jrsteensen/OpenHornet/release/OHM_Modifications/README.md

# Mods Folder

All parts inside the "mods" folder are modifications of the original OpenHornet parts. All parts inside this folder do not belong to the OpenHornet release baseline and are therefore not officially supported by the OpenHornet team.

## Documentation
All modifications made to the parts inside the "mods" folder are documented in the `README.md` file inside every folder.

### README.md Template
```
# <TITLE OF MODIFICATION>
- **Author:** <Name and discord username i.e. John Steensen (Noctum)>
- **Contributed on:** <date>
- **Derived from:** v<release number, i.e. 0.2.0)
- **Original Assembly:** <List OH part number of the original assembly.>

## Summary
<Describe the change and why>

### Parts List <This section is only required if there are changes to the parts list>
1. <List the new parts/hardware/components, and describe them well enough that they can be sourced. Links are good.>
2. ...
3. ...
```
