jrsteensen/OpenHornet/release/OHM_Modifications/DXF_files_v0.2.0/README.md

# DXF File Export of v0.2.0 release
- **Author:** Jose (5JsAs)
- **Contributed on:** Apr 10, 2024
- **Derived from:** v0.2.0
- **Original Assembly:** All SVG Structure Parts

## Summary
Contains the DXF files that correspond to the parts in SVG format of the different OH structures. The parts are compiled into 5 files according to the main structures of the project: UIP, LIP, Center Tub, LC, RC. For each structure there are two files in mm and inches.

The parts have been exported from the Fusion model in mm and compiled in AUTOCAD. The inch version is obtained after a units conversion in AUTOCAD.
