jrsteensen/OpenHornet/artwork/Left Console/OH4A1-9001 - DECAL, GROUND POWER.png

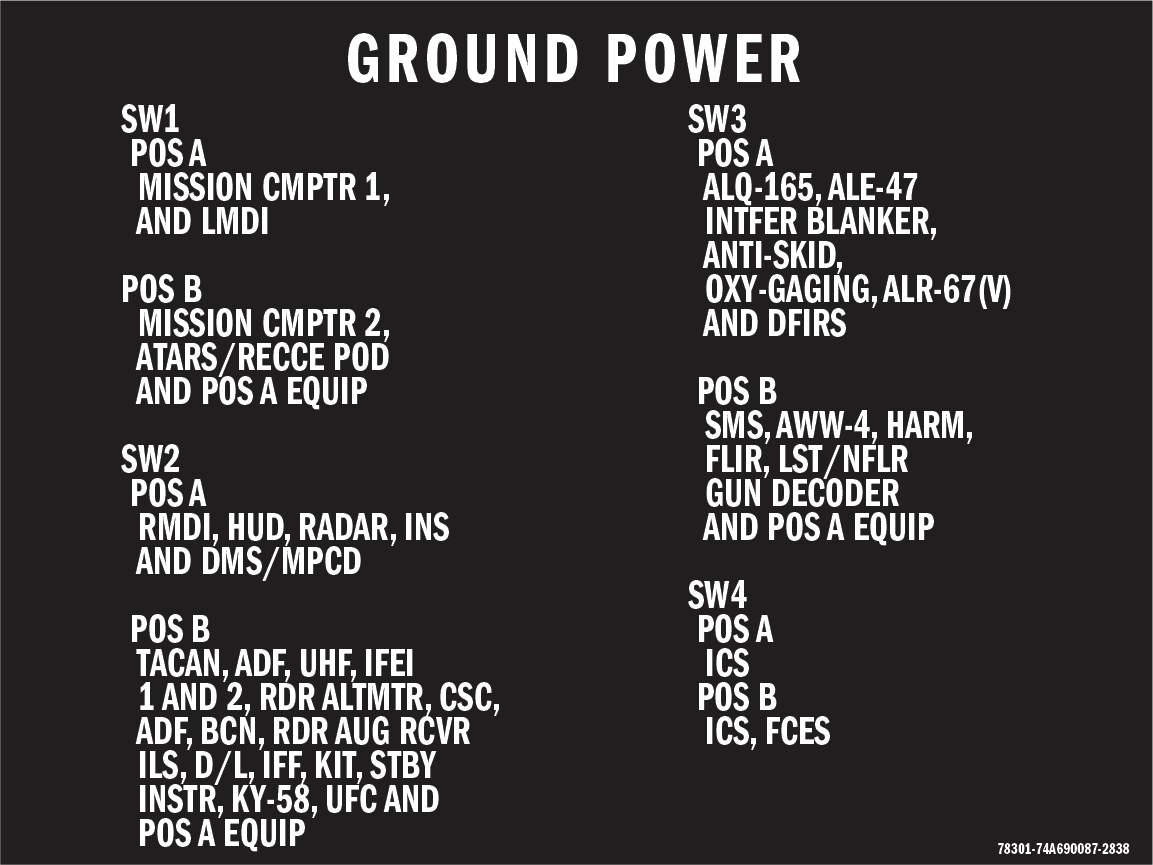
artwork/Left Console/OH4A1-9001 - DECAL, GROUND POWER.png
