jrsteensen/OpenHornet/artwork/Left Console/OH4A9-9001 - DECAL, RH GRIP ASSY.png

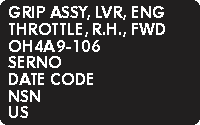
artwork/Left Console/OH4A9-9001 - DECAL, RH GRIP ASSY.png
