jrsteensen/OpenHornet/artwork/Right Console/OH5A1-9001 - DECAL, CANOPY.png

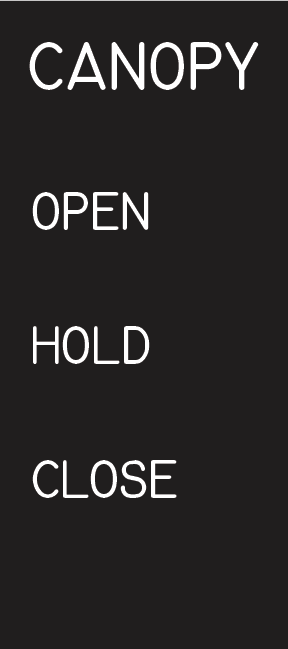
artwork/Right Console/OH5A1-9001 - DECAL, CANOPY.png
