jrsteensen/OpenHornet/artwork/seat/OH3A2A-9002 - DECAL, BRIDLE AND BOX.png

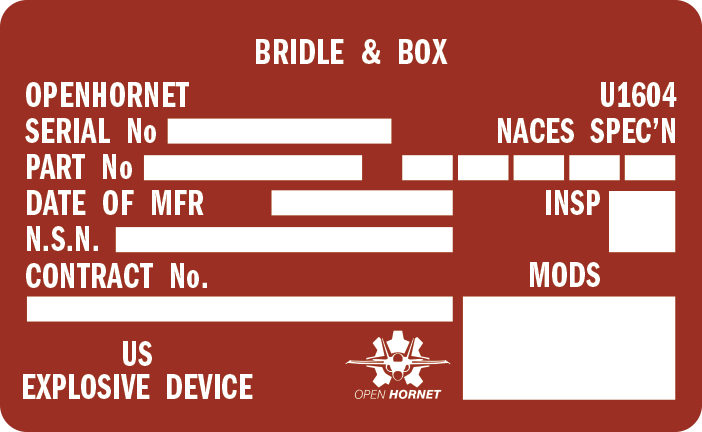
artwork/seat/OH3A2A-9002 - DECAL, BRIDLE AND BOX.png
