jrsteensen/OpenHornet/artwork/seat/OH3A2A-9004 - DECAL, DANGER DO NOT PULL.png

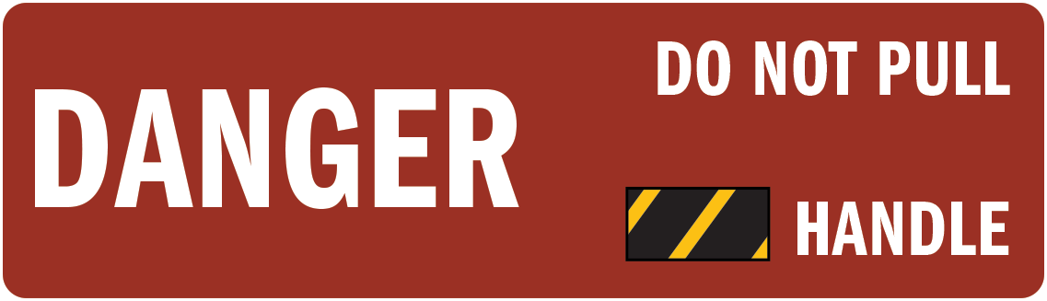
artwork/seat/OH3A2A-9004 - DECAL, DANGER DO NOT PULL.png
