jrsteensen/OpenHornet/artwork/seat/OH3A2A-9005 - DECAL, DO NOT HOLD.png

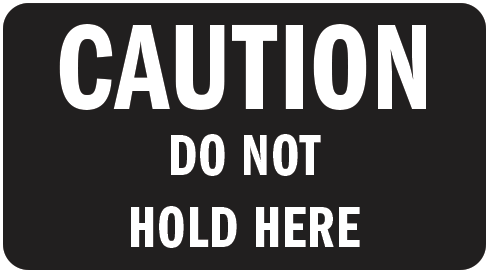
artwork/seat/OH3A2A-9005 - DECAL, DO NOT HOLD.png
