jrsteensen/OpenHornet/artwork/seat/OH3A2A-9006 - DECAL, NACES PFCL.png

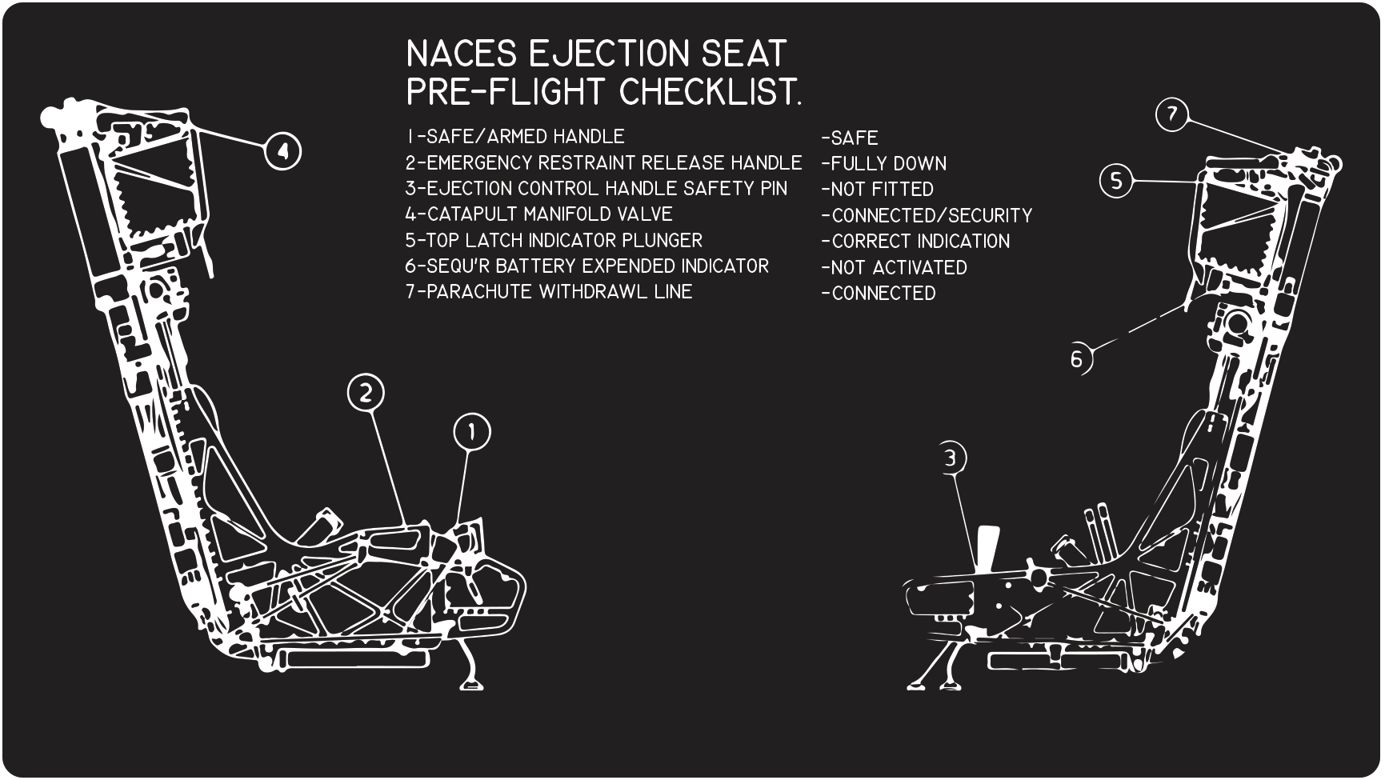
artwork/seat/OH3A2A-9006 - DECAL, NACES PFCL.png
