jrsteensen/OpenHornet/artwork/seat/OH3A2A-9008 - DECAL, SEAT BUCKET MECH.png

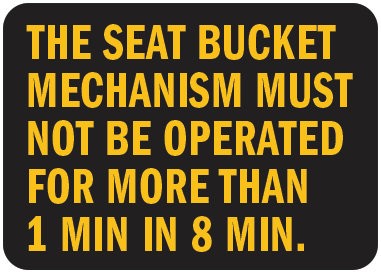
artwork/seat/OH3A2A-9008 - DECAL, SEAT BUCKET MECH.png
