jrsteensen/OpenHornet/artwork/seat/OH3A2A-9010 - DECAL, SEAT, AIRCRAFT EJECTION.png

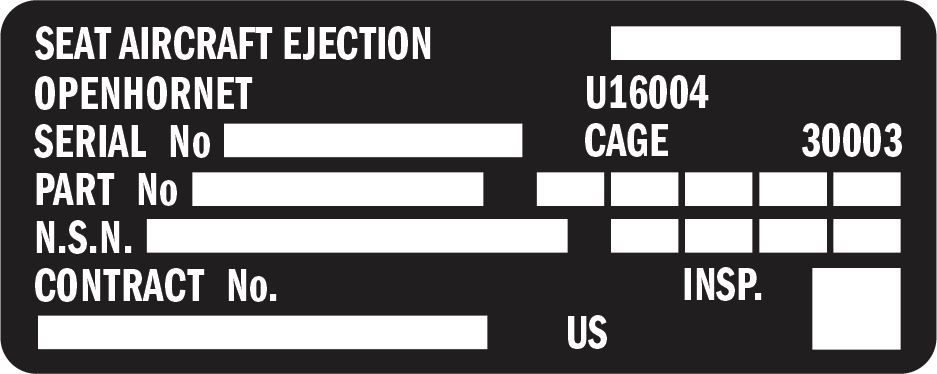
artwork/seat/OH3A2A-9010 - DECAL, SEAT, AIRCRAFT EJECTION.png
