jrsteensen/OpenHornet/artwork/seat/OH3A2A-9011 - DECAL, SEAT APPLICATION.png

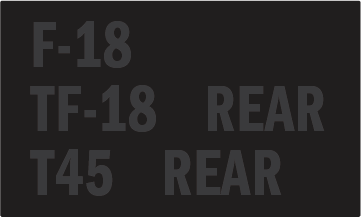
artwork/seat/OH3A2A-9011 - DECAL, SEAT APPLICATION.png
