jrsteensen/OpenHornet/artwork/seat/OH3A2A-9014 - DECAL, SURVIVAL KIT, OXYGEN, AIRCRAFT SEAT.png

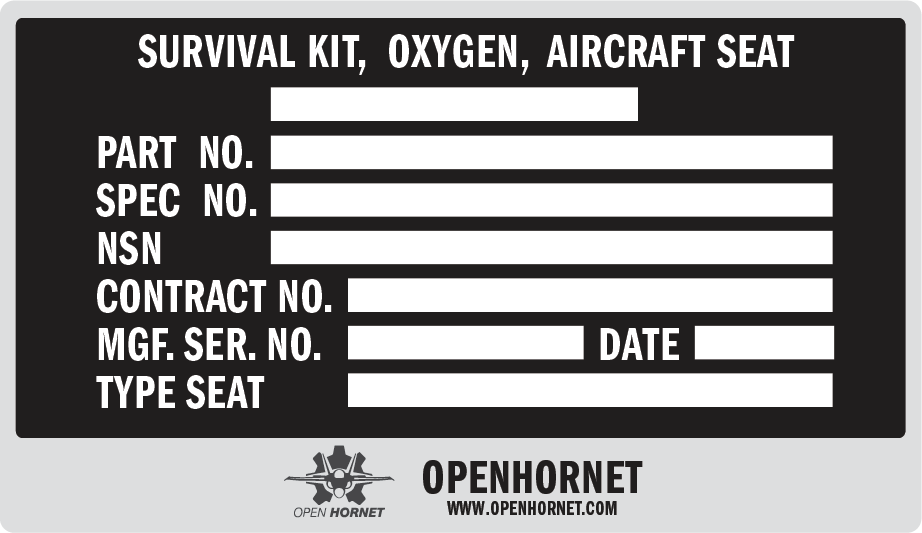
artwork/seat/OH3A2A-9014 - DECAL, SURVIVAL KIT, OXYGEN, AIRCRAFT SEAT.png
