jrsteensen/OpenHornet/artwork/seat/OH3A2A-9016 - DECAL, DROGUE ASSY.pdf.png

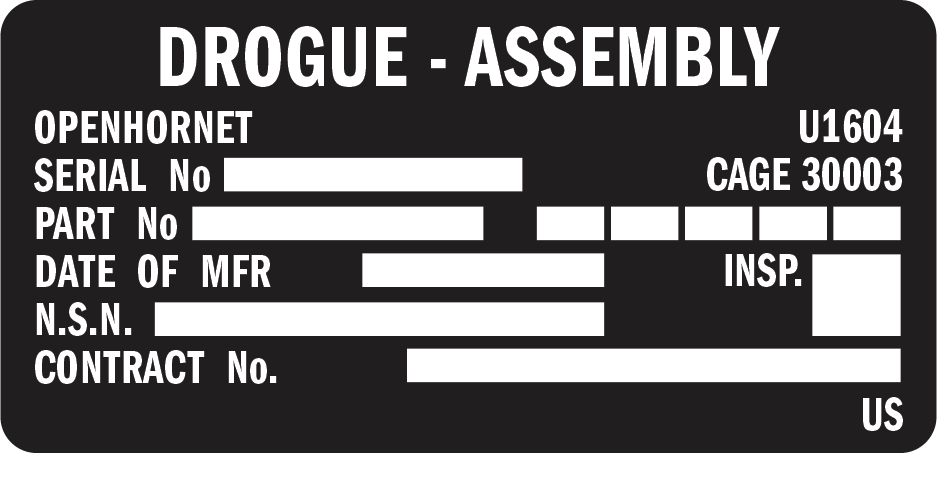
artwork/seat/OH3A2A-9016 - DECAL, DROGUE ASSY.pdf.png
