jrsteensen/OpenHornet/artwork/Stick/OH3A3-9001 - DECAL, GRIP ASSY.png

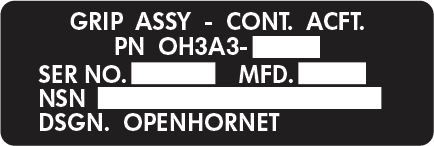
artwork/Stick/OH3A3-9001 - DECAL, GRIP ASSY.png
