jrsteensen/OpenHornet/artwork/Upper Instrument Panel/OH1A8-9001 - DECAL, TV LENS.png

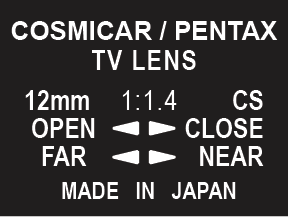
artwork/Upper Instrument Panel/OH1A8-9001 - DECAL, TV LENS.png
