jrsteensen/OpenHornet/ECAD/PCBs/ABSIS/ABSIS_ALE Relay Module/Assets/ABSIS_ALE Relay Module-BOT.png

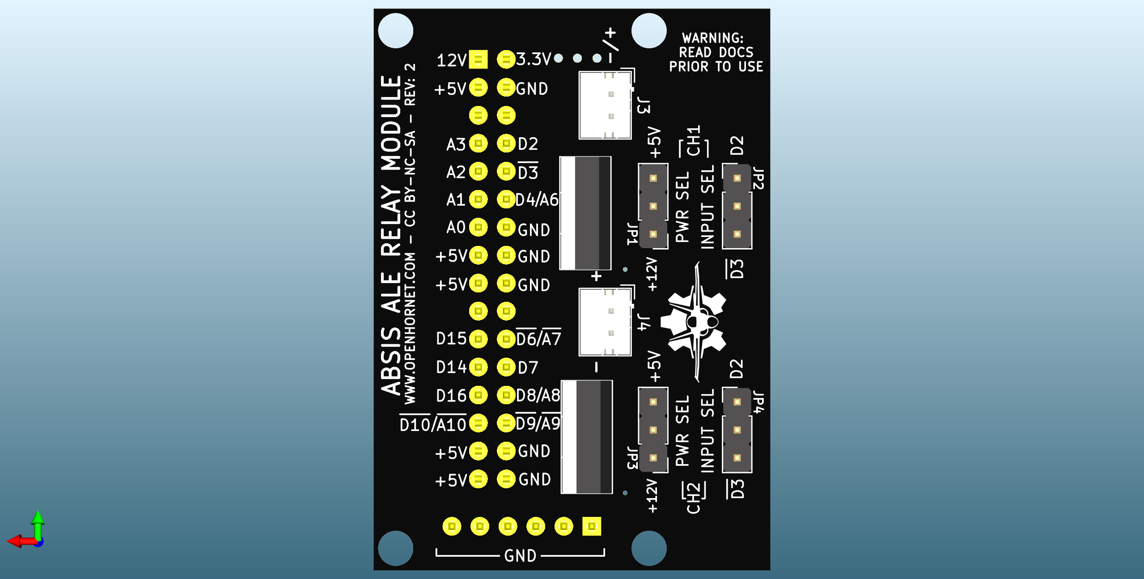
ECAD/PCBs/ABSIS/ABSIS_ALE Relay Module/Assets/ABSIS_ALE Relay Module-BOT.png
