jrsteensen/OpenHornet/ECAD/PCBs/ABSIS/ABSIS_ALE Relay Module/Assets/ABSIS_ALE Relay Module-TOP.png

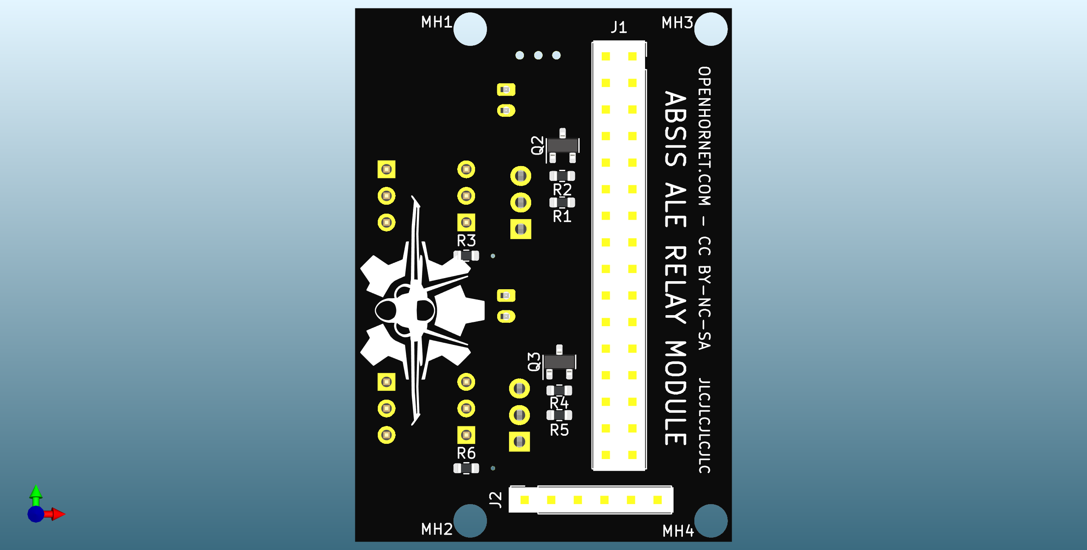
ECAD/PCBs/ABSIS/ABSIS_ALE Relay Module/Assets/ABSIS_ALE Relay Module-TOP.png
