jrsteensen/OpenHornet/ECAD/PCBs/ABSIS/ABSIS_ALE+/ASSETS/11.PNG

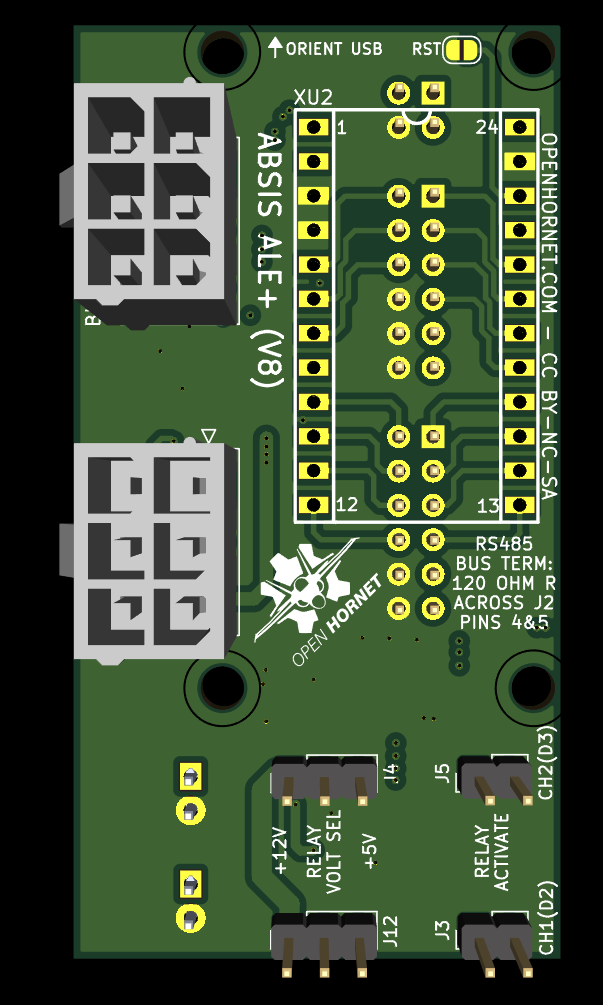
ECAD/PCBs/ABSIS/ABSIS_ALE+/ASSETS/11.PNG
