jrsteensen/OpenHornet/ECAD/PCBs/ABSIS/ABSIS_ALE+/ASSETS/12.PNG

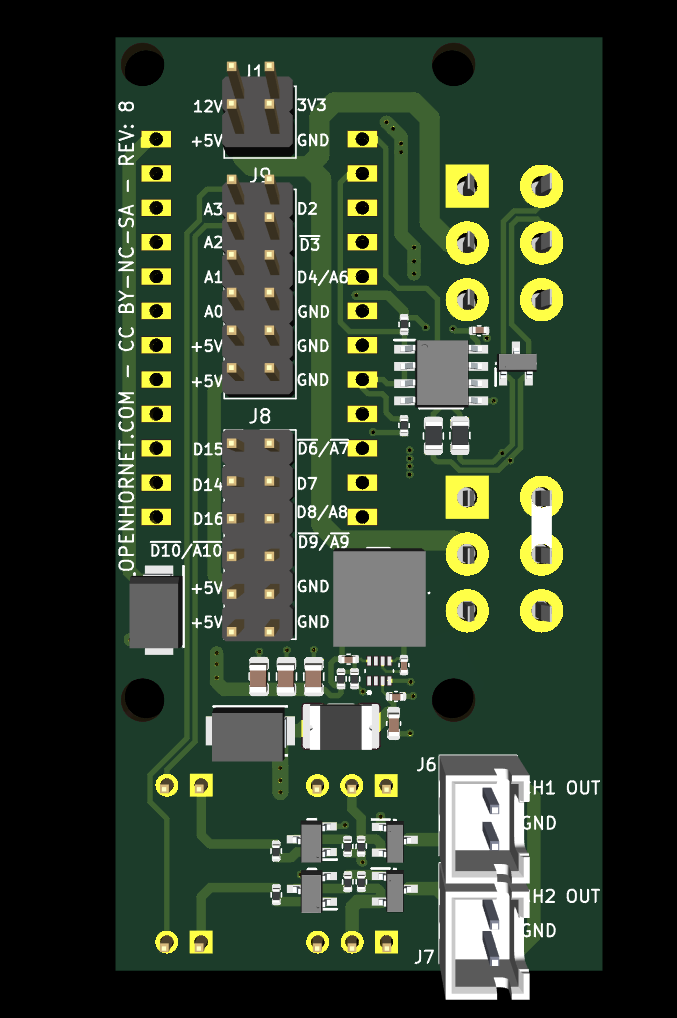
ECAD/PCBs/ABSIS/ABSIS_ALE+/ASSETS/12.PNG
