jrsteensen/OpenHornet/ECAD/PCBs/ABSIS/ABSIS_ALE+/ASSETS/13.PNG

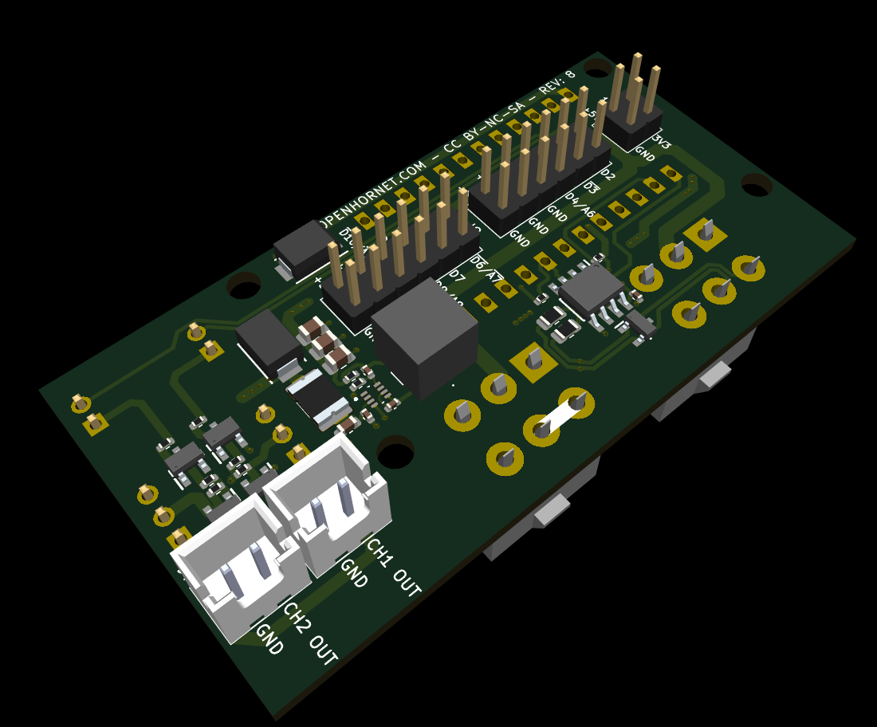
ECAD/PCBs/ABSIS/ABSIS_ALE+/ASSETS/13.PNG
