jrsteensen/OpenHornet/ECAD/PCBs/ABSIS/ABSIS_ALE+/ASSETS/14.PNG

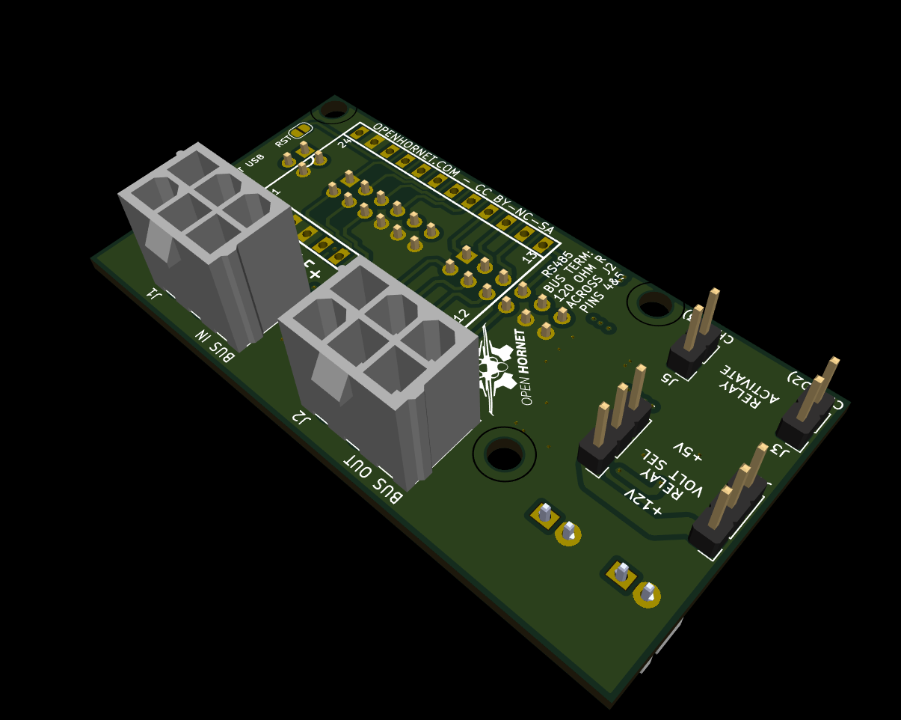
ECAD/PCBs/ABSIS/ABSIS_ALE+/ASSETS/14.PNG
