jrsteensen/OpenHornet/ECAD/PCBs/ABSIS/ABSIS_ALE+/ASSETS/15.PNG

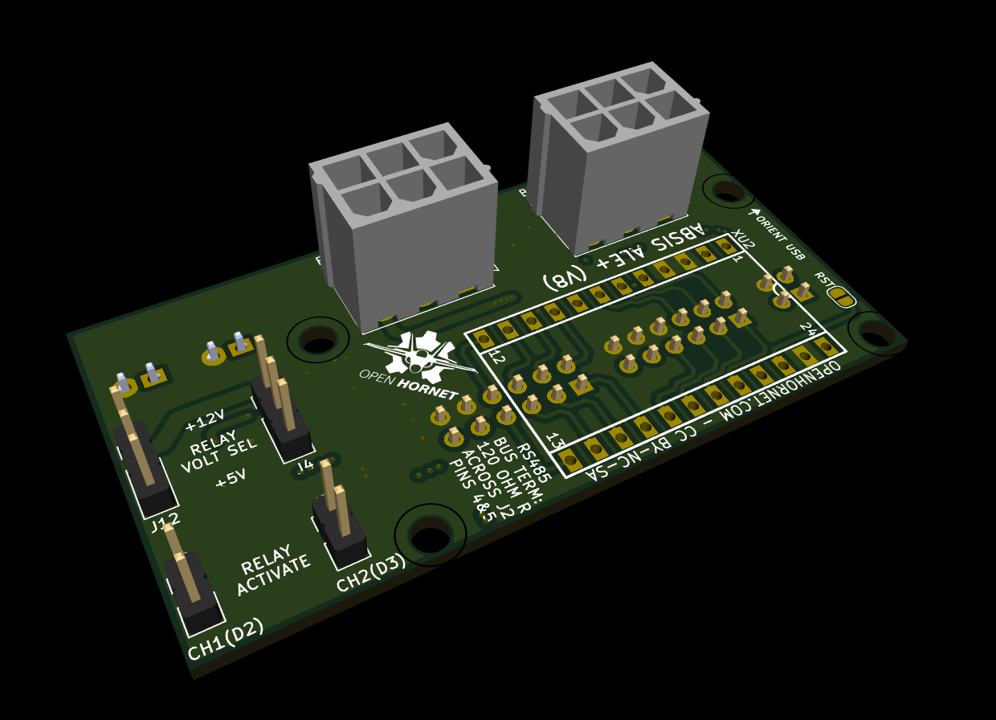
ECAD/PCBs/ABSIS/ABSIS_ALE+/ASSETS/15.PNG
