jrsteensen/OpenHornet/ECAD/PCBs/ABSIS/ABSIS_ALE+/ASSETS/16.PNG

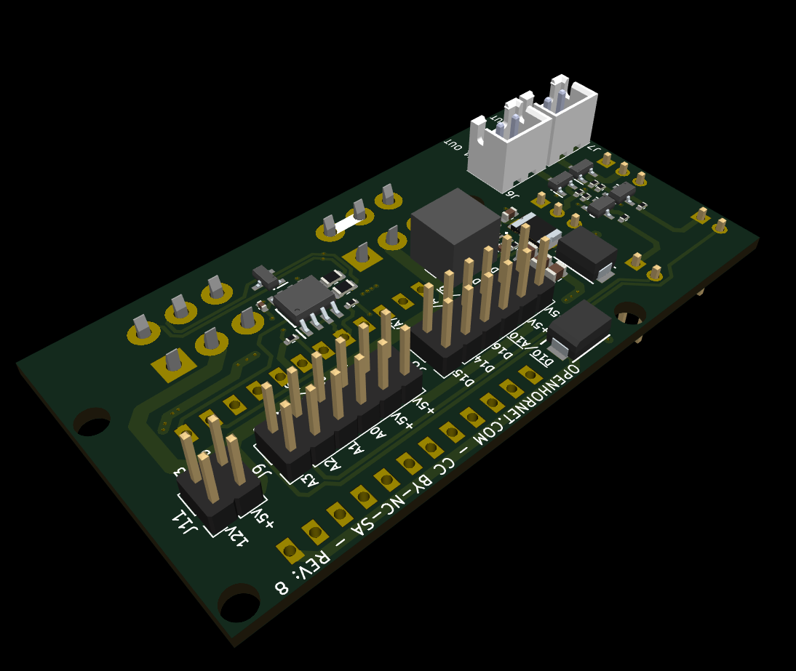
ECAD/PCBs/ABSIS/ABSIS_ALE+/ASSETS/16.PNG
