jrsteensen/OpenHornet/ECAD/PCBs/ABSIS/ABSIS_ALE/Assets/ABSIS_ALE-BOT_ISO.png

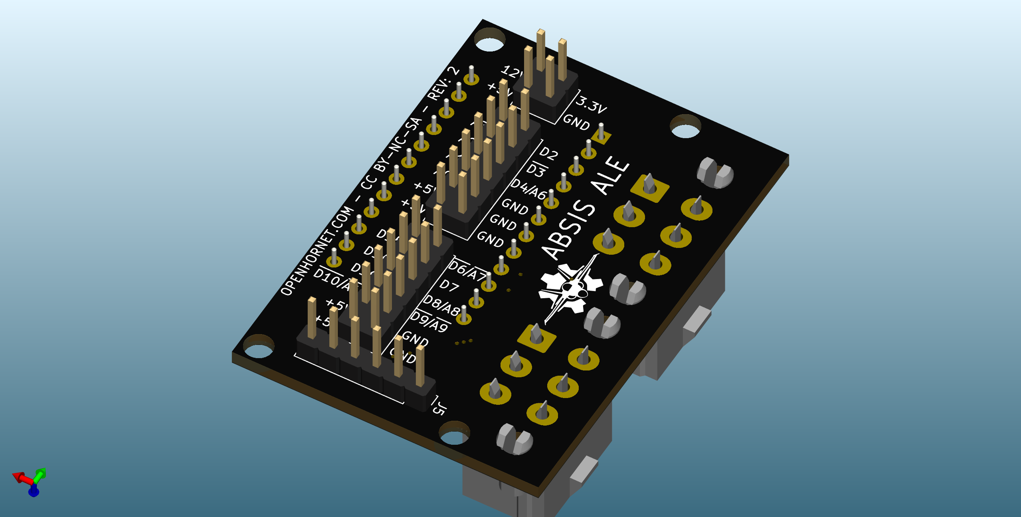
ECAD/PCBs/ABSIS/ABSIS_ALE/Assets/ABSIS_ALE-BOT_ISO.png
