jrsteensen/OpenHornet/ECAD/PCBs/ABSIS/ABSIS_ALE/Assets/ABSIS_ALE-TOP.png

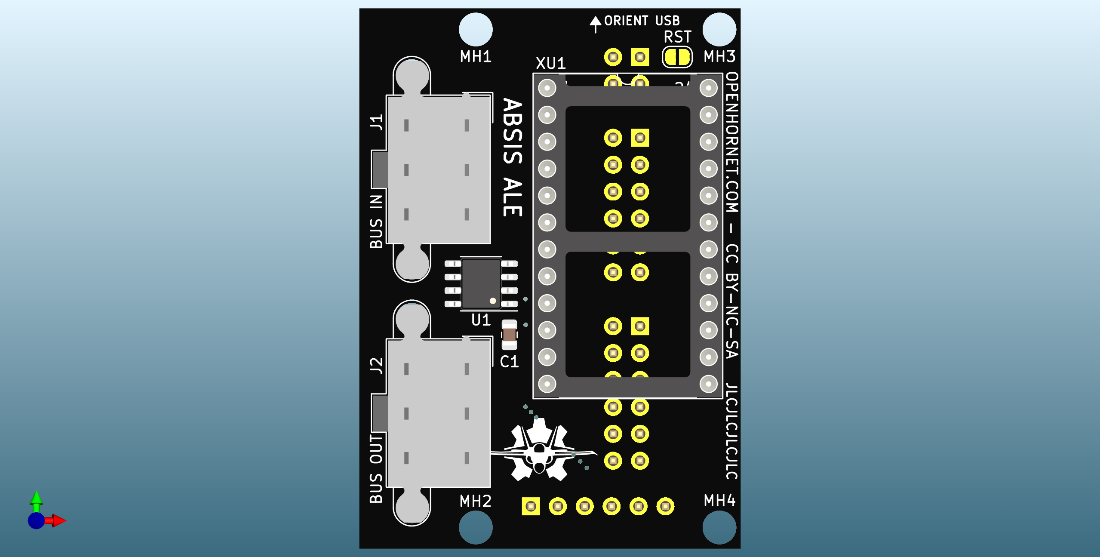
ECAD/PCBs/ABSIS/ABSIS_ALE/Assets/ABSIS_ALE-TOP.png
