jrsteensen/OpenHornet/ECAD/PCBs/ABSIS/ABSIS_ATX Power Supply Unit/Assets/ABSIS_ATX Power Supply Unit-BOT.png

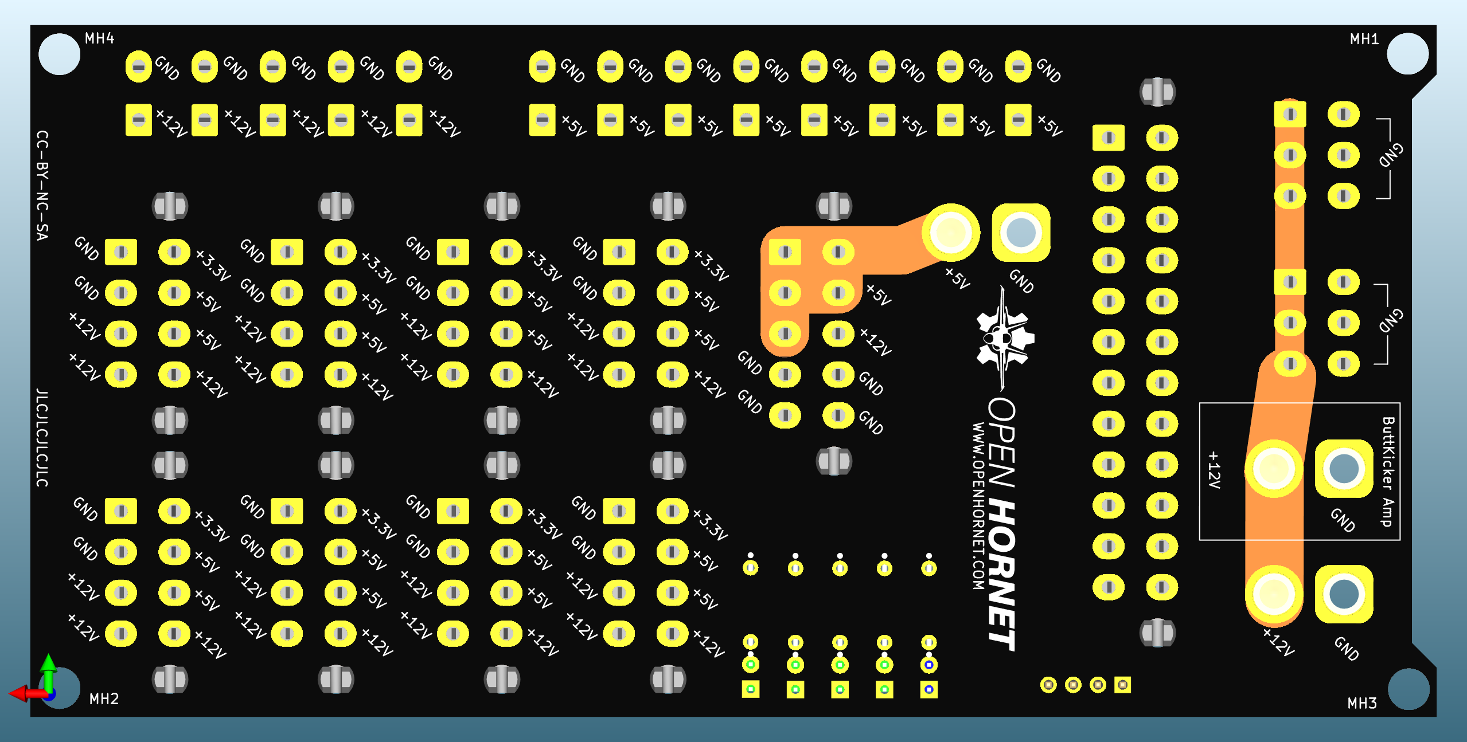
ECAD/PCBs/ABSIS/ABSIS_ATX Power Supply Unit/Assets/ABSIS_ATX Power Supply Unit-BOT.png
