jrsteensen/OpenHornet/ECAD/PCBs/ABSIS/ABSIS_ATX Power Supply Unit/Assets/ABSIS_ATX Power Supply Unit-TOP.png

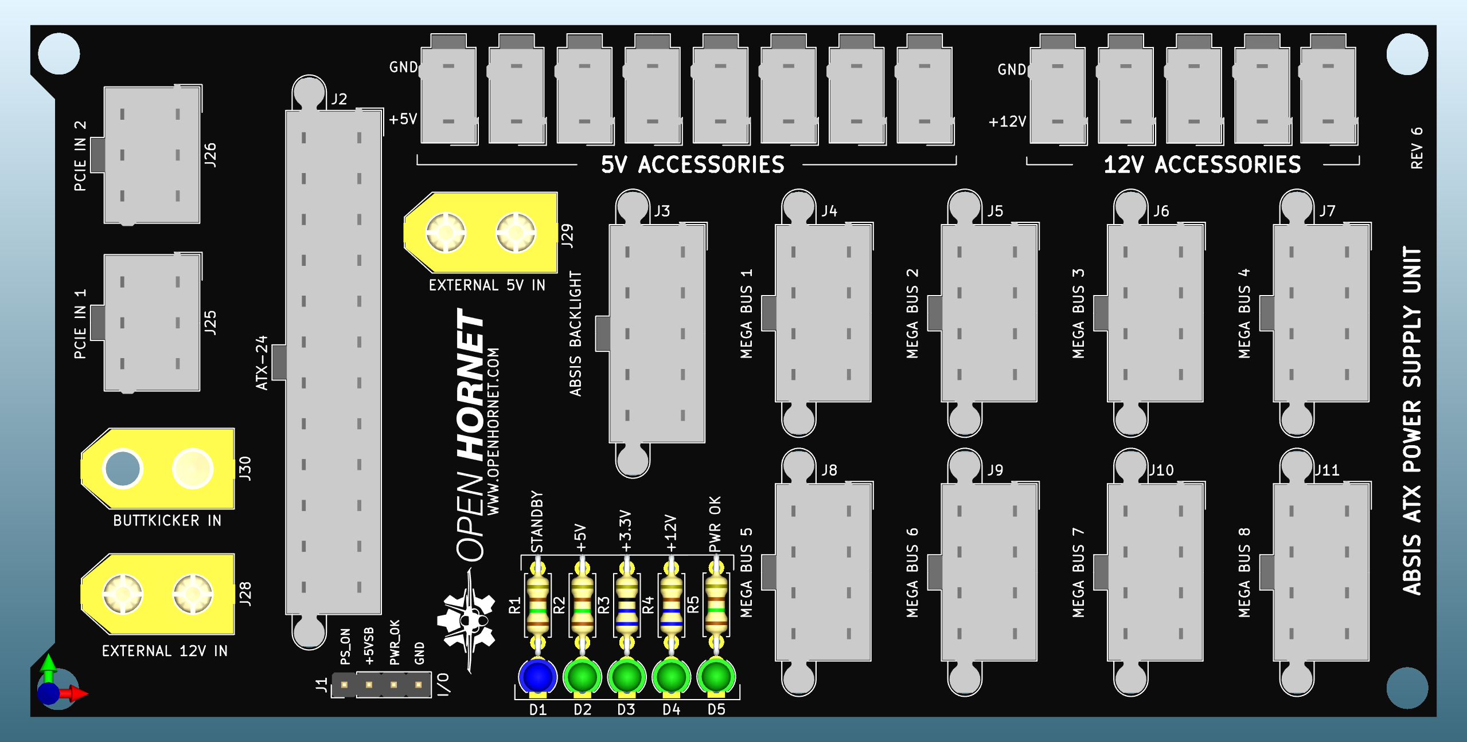
ECAD/PCBs/ABSIS/ABSIS_ATX Power Supply Unit/Assets/ABSIS_ATX Power Supply Unit-TOP.png
