jrsteensen/OpenHornet/ECAD/PCBs/ABSIS/ABSIS_ATX Power Supply Unit/Assets/ABSIS_ATX Power Supply Unit-TOP_ISO.png

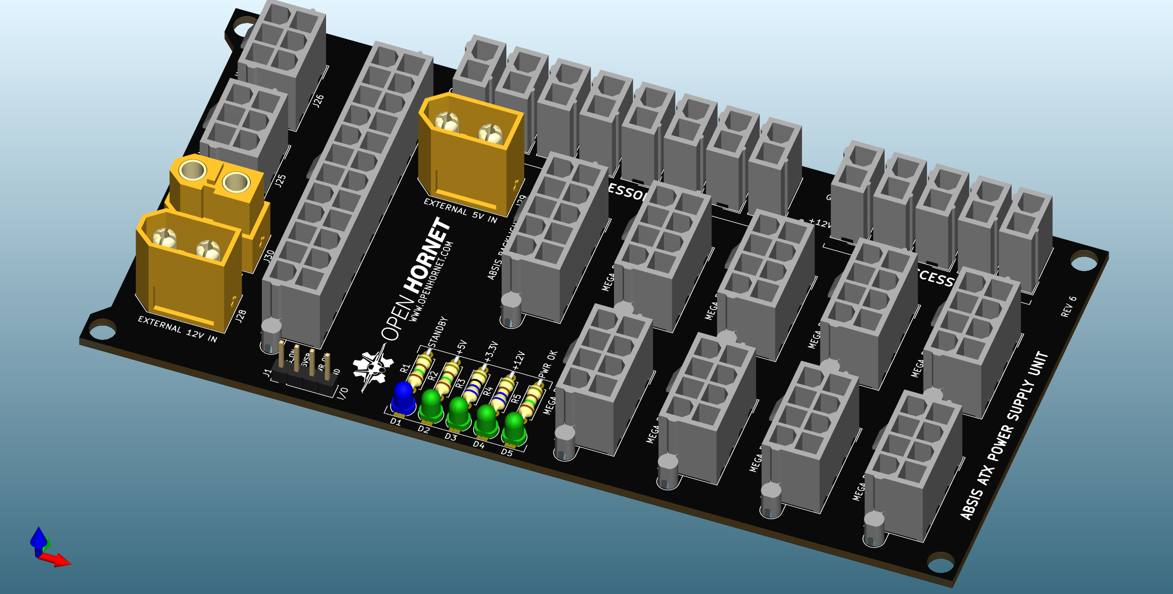
ECAD/PCBs/ABSIS/ABSIS_ATX Power Supply Unit/Assets/ABSIS_ATX Power Supply Unit-TOP_ISO.png
