jrsteensen/OpenHornet/ECAD/PCBs/ABSIS/ABSIS_Backlight Controller/Assets/ABSIS_Backlight Controller-BOT.png

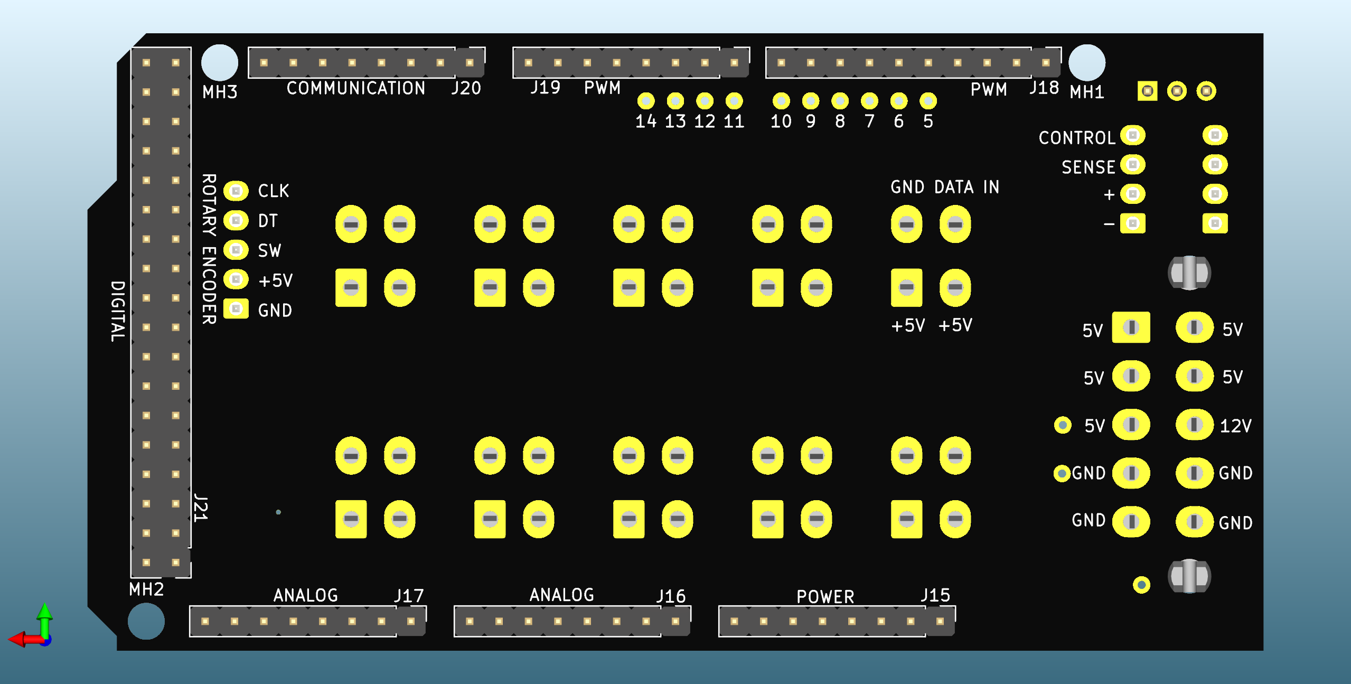
ECAD/PCBs/ABSIS/ABSIS_Backlight Controller/Assets/ABSIS_Backlight Controller-BOT.png
