jrsteensen/OpenHornet/ECAD/PCBs/ABSIS/ABSIS_Backlight Controller/Assets/ABSIS_Backlight Controller-TOP.png

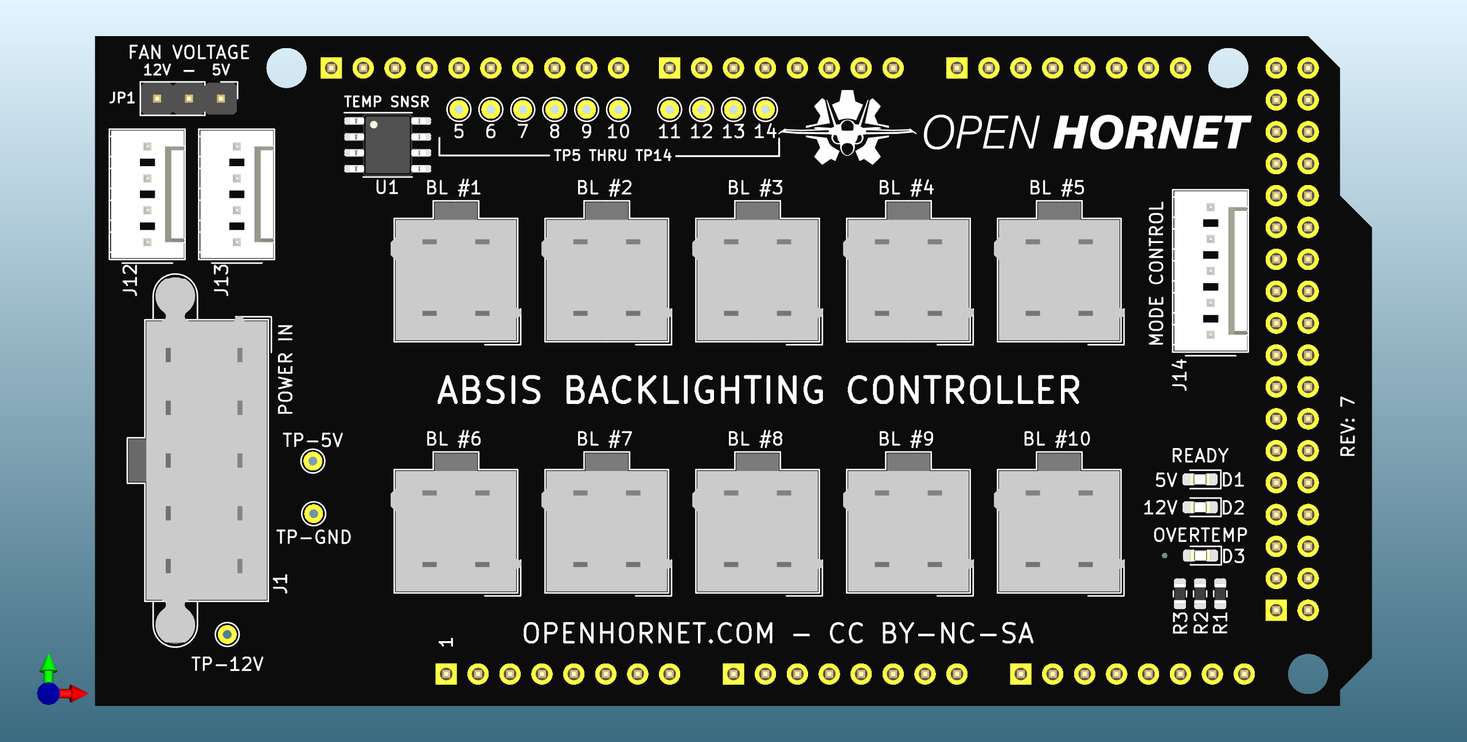
ECAD/PCBs/ABSIS/ABSIS_Backlight Controller/Assets/ABSIS_Backlight Controller-TOP.png
