jrsteensen/OpenHornet/ECAD/PCBs/ABSIS/ABSIS_Backlight Controller/Assets/ABSIS_Backlight Controller-TOP_ISO.png

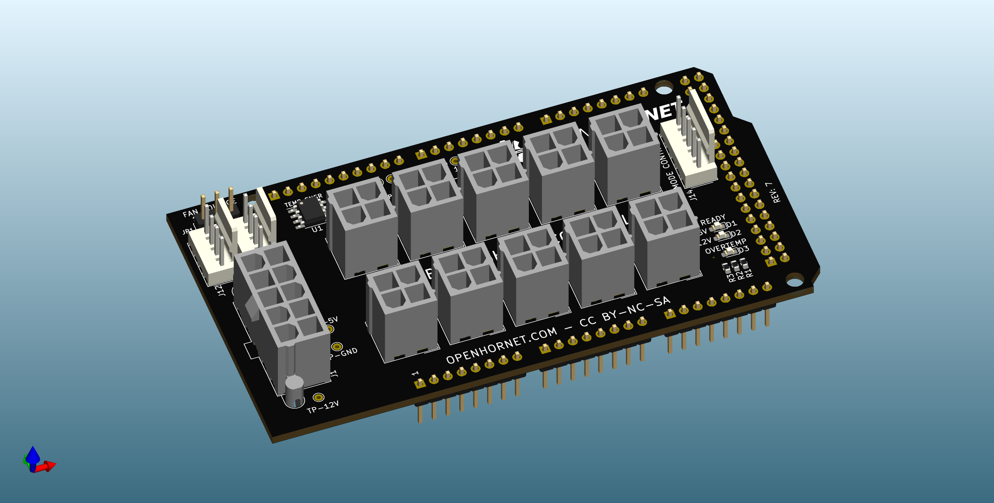
ECAD/PCBs/ABSIS/ABSIS_Backlight Controller/Assets/ABSIS_Backlight Controller-TOP_ISO.png
