jrsteensen/OpenHornet/ECAD/PCBs/ABSIS/ABSIS_Bus_Master/assets/11.PNG

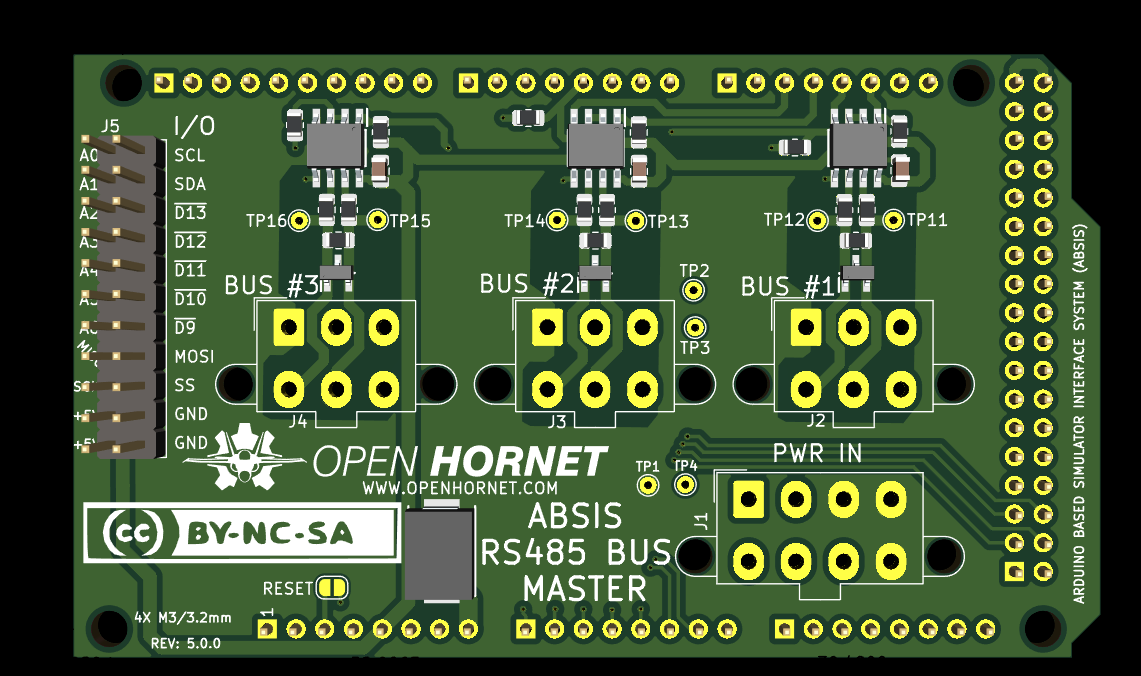
ECAD/PCBs/ABSIS/ABSIS_Bus_Master/assets/11.PNG
