jrsteensen/OpenHornet/ECAD/PCBs/ABSIS/ABSIS_Bus_Master/assets/12.PNG

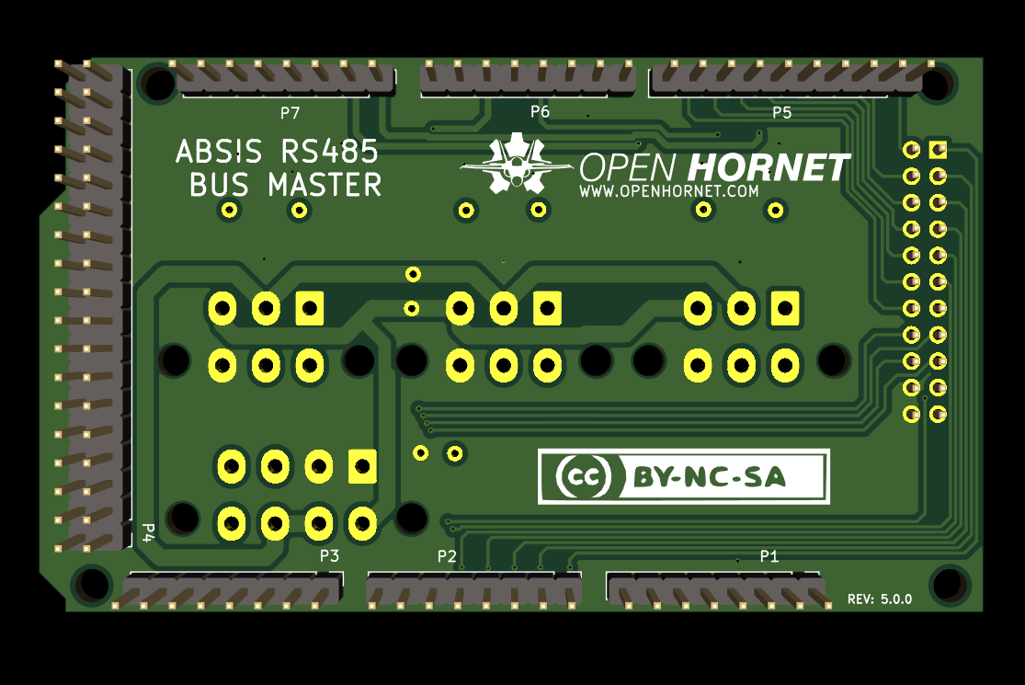
ECAD/PCBs/ABSIS/ABSIS_Bus_Master/assets/12.PNG
