jrsteensen/OpenHornet/ECAD/PCBs/ABSIS/ABSIS_Bus_Master/assets/13.PNG

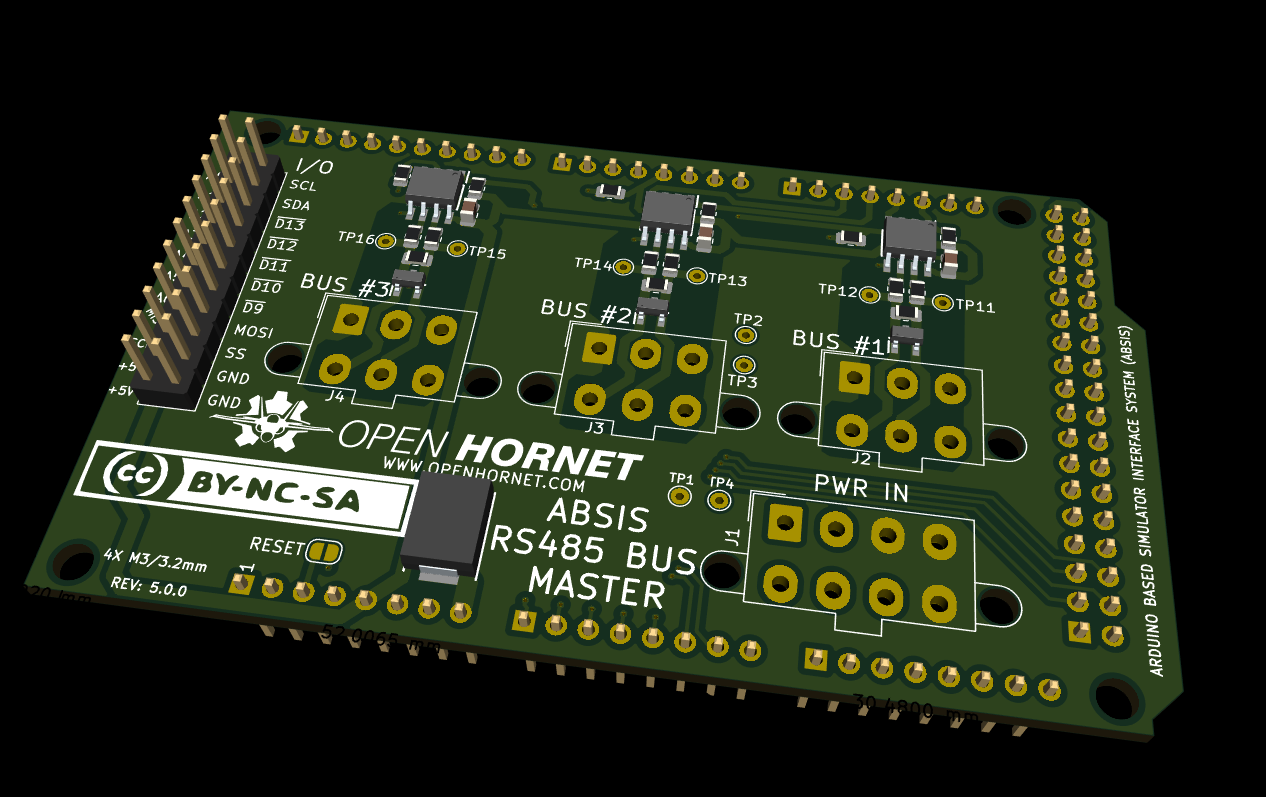
ECAD/PCBs/ABSIS/ABSIS_Bus_Master/assets/13.PNG
