jrsteensen/OpenHornet/ECAD/PCBs/ABSIS/ABSIS_Bus_Master/assets/14.PNG

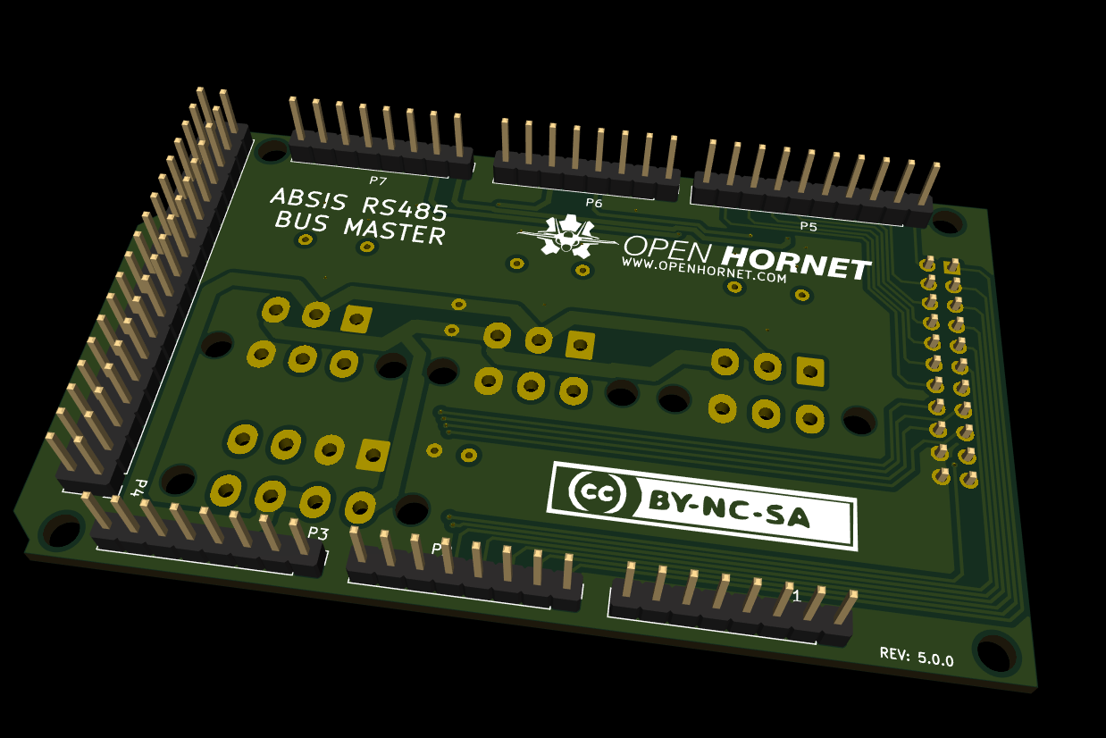
ECAD/PCBs/ABSIS/ABSIS_Bus_Master/assets/14.PNG
