jrsteensen/OpenHornet/ECAD/PCBs/ABSIS/ABSIS_Hall Sensor/Assets/ABSIS_Hall Sensor-BOT.png

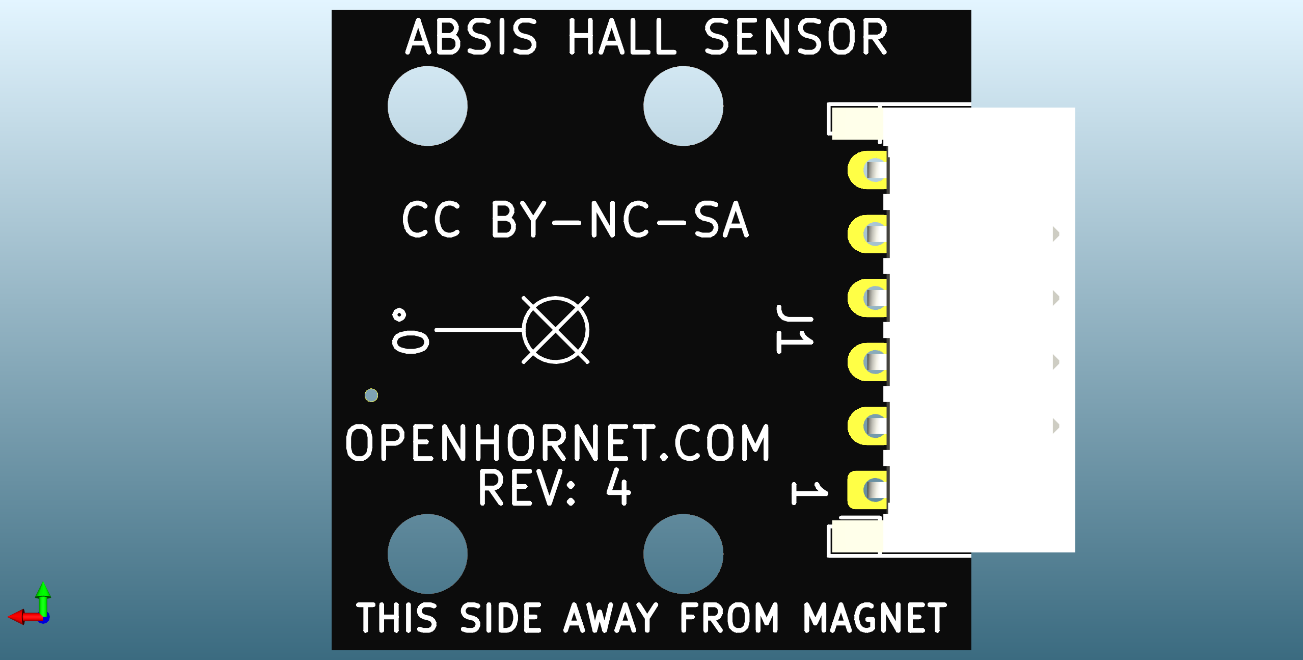
ECAD/PCBs/ABSIS/ABSIS_Hall Sensor/Assets/ABSIS_Hall Sensor-BOT.png
