jrsteensen/OpenHornet/ECAD/PCBs/ABSIS/ABSIS_Hall Sensor/Assets/ABSIS_Hall Sensor-BOT_ISO.png

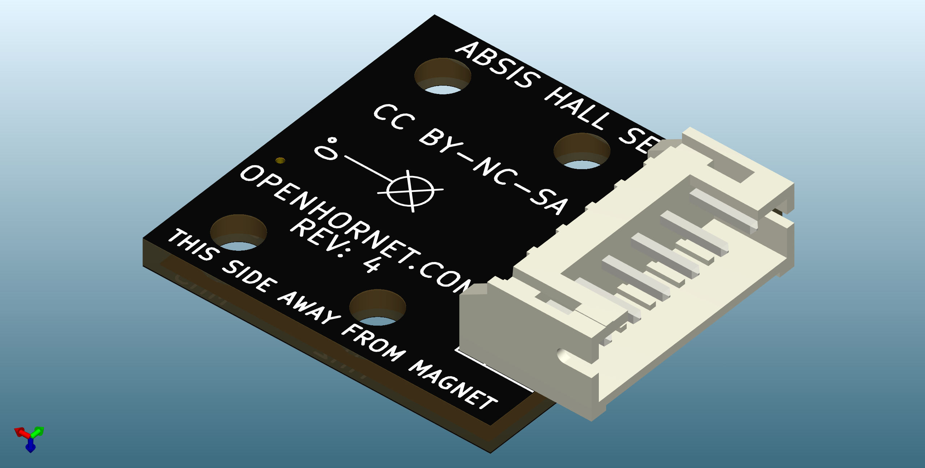
ECAD/PCBs/ABSIS/ABSIS_Hall Sensor/Assets/ABSIS_Hall Sensor-BOT_ISO.png
