jrsteensen/OpenHornet/ECAD/PCBs/ABSIS/ABSIS_Hall Sensor/Assets/ABSIS_Hall Sensor-TOP_ISO.png

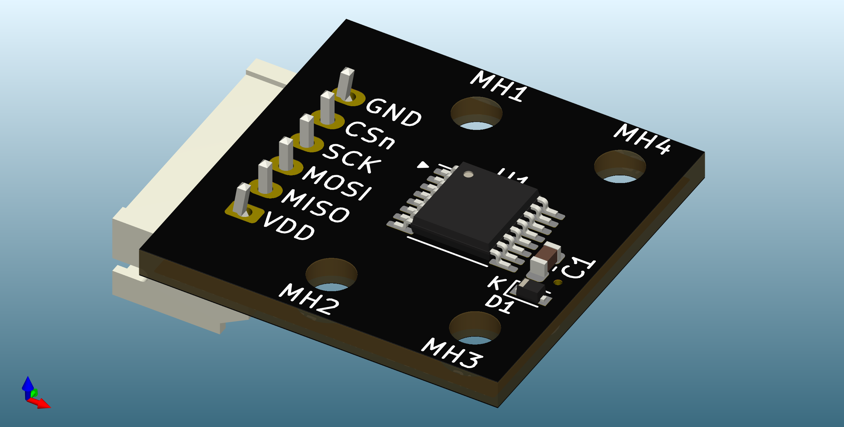
ECAD/PCBs/ABSIS/ABSIS_Hall Sensor/Assets/ABSIS_Hall Sensor-TOP_ISO.png
