jrsteensen/OpenHornet/ECAD/PCBs/ABSIS/ABSIS_HID Bus Master/Assets/ABSIS_HID Bus Master-BOT.png

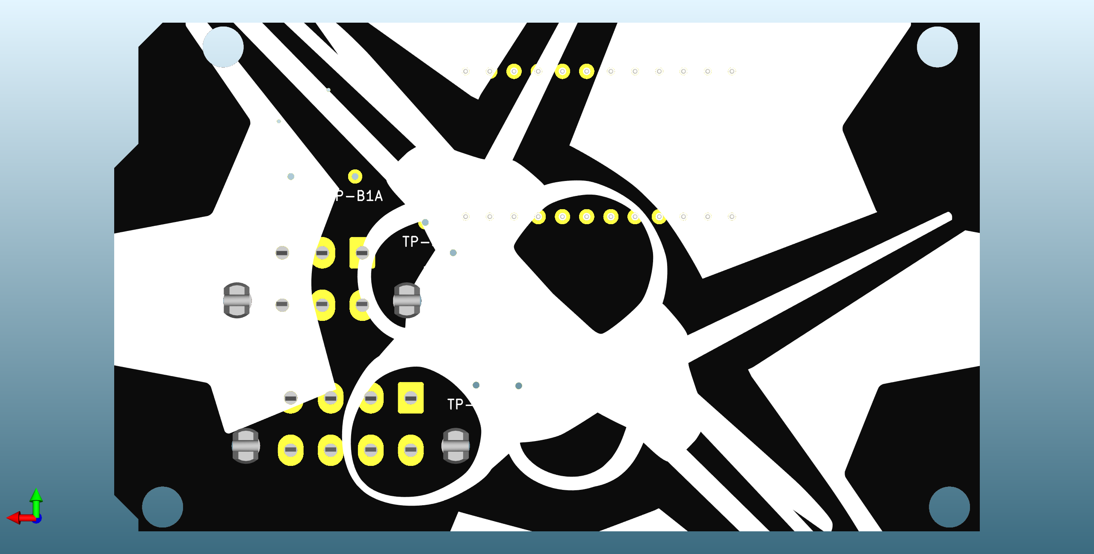
ECAD/PCBs/ABSIS/ABSIS_HID Bus Master/Assets/ABSIS_HID Bus Master-BOT.png
