jrsteensen/OpenHornet/ECAD/PCBs/ABSIS/ABSIS_HID Bus Master/Assets/ABSIS_HID Bus Master-TOP.png

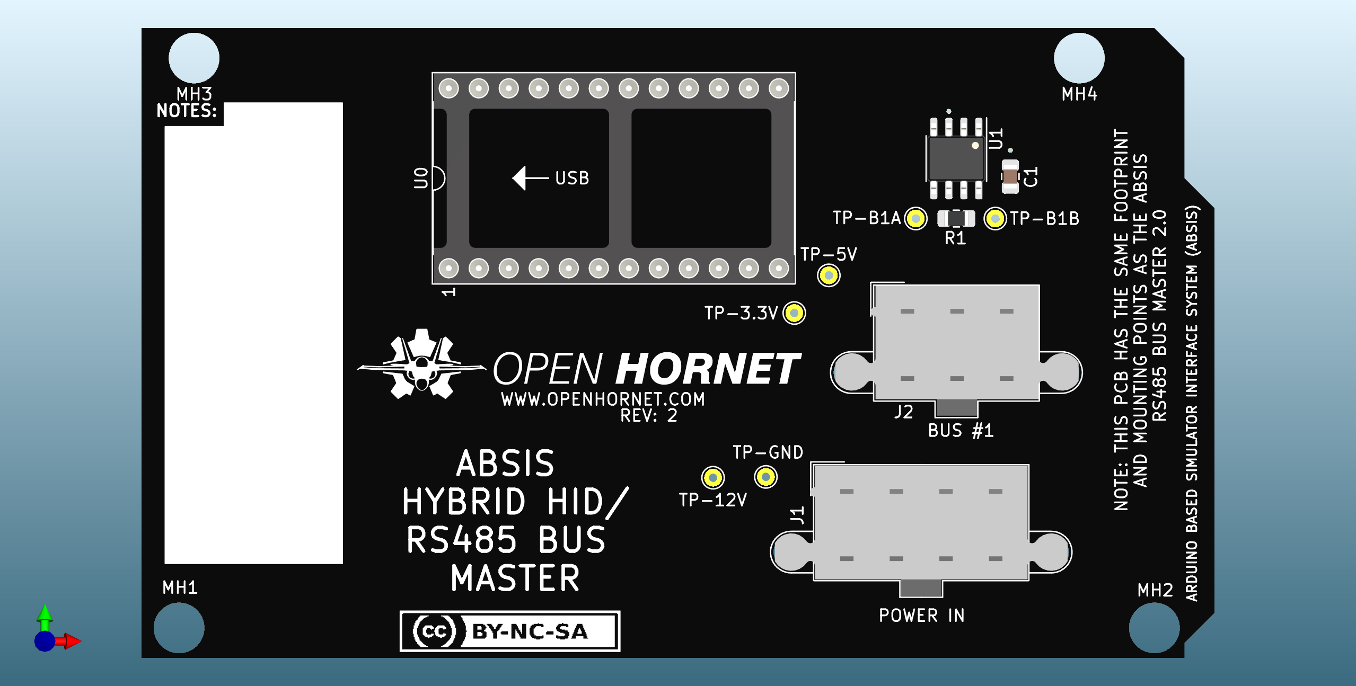
ECAD/PCBs/ABSIS/ABSIS_HID Bus Master/Assets/ABSIS_HID Bus Master-TOP.png
