jrsteensen/OpenHornet/ECAD/PCBs/ABSIS/ABSIS_HID Bus Master/Assets/ABSIS_HID Bus Master-TOP_ISO.png

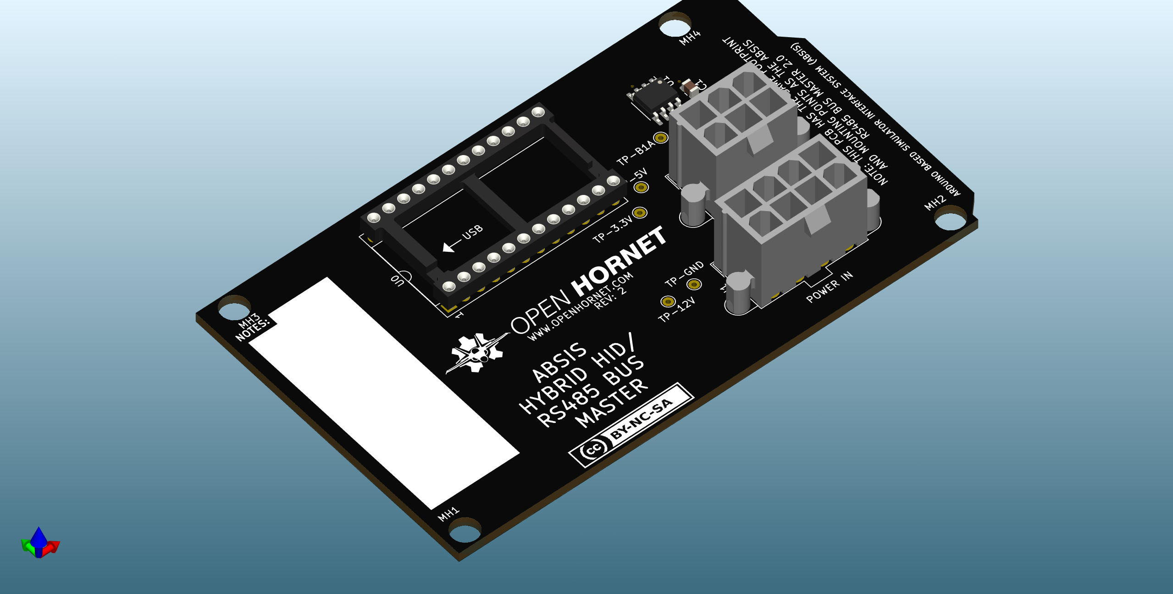
ECAD/PCBs/ABSIS/ABSIS_HID Bus Master/Assets/ABSIS_HID Bus Master-TOP_ISO.png
