jrsteensen/OpenHornet/ECAD/PCBs/ABSIS/ABSIS_Mega/assets/11.PNG

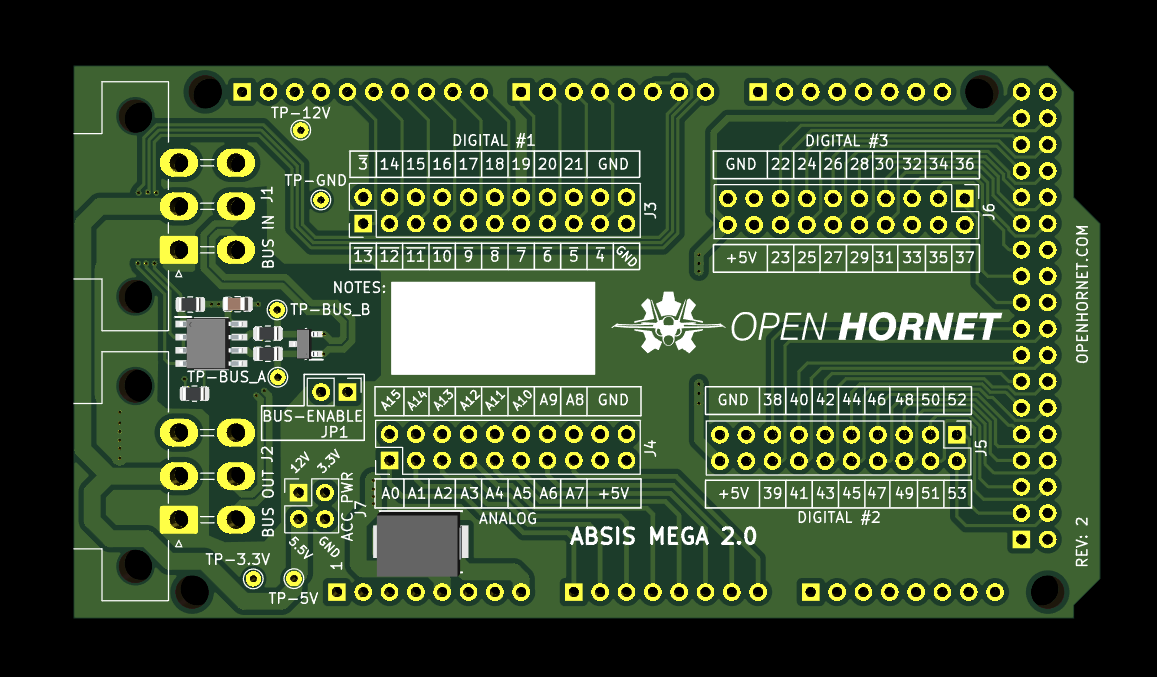
ECAD/PCBs/ABSIS/ABSIS_Mega/assets/11.PNG
