jrsteensen/OpenHornet/ECAD/PCBs/ABSIS/ABSIS_Mega/assets/12.PNG

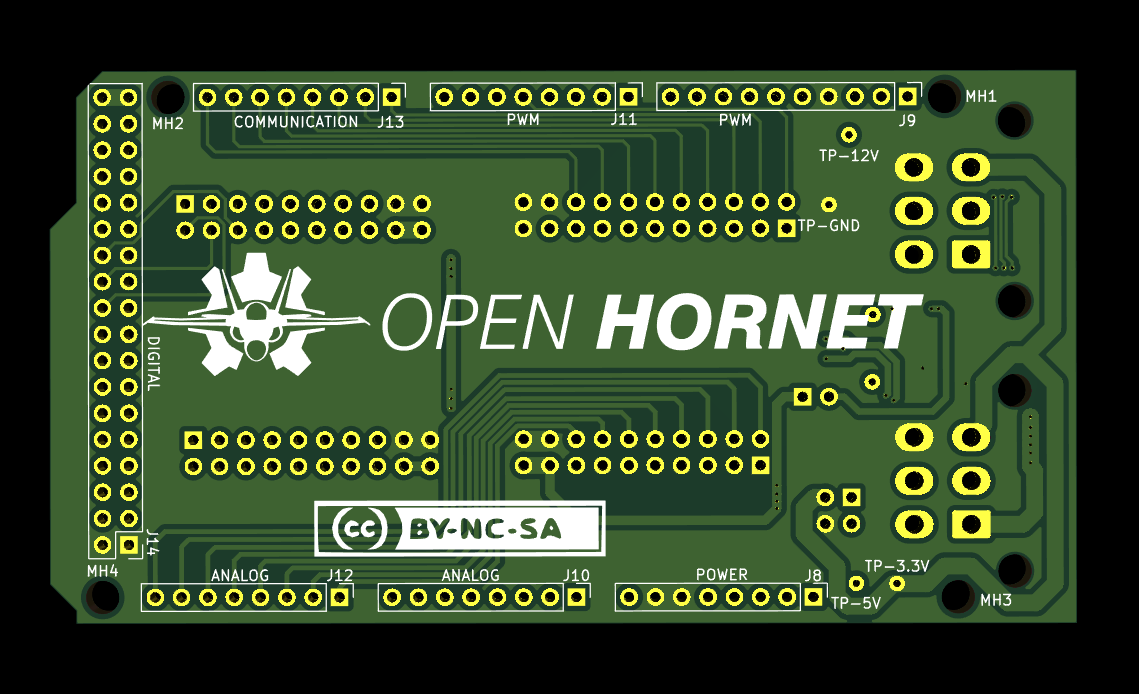
ECAD/PCBs/ABSIS/ABSIS_Mega/assets/12.PNG
