jrsteensen/OpenHornet/ECAD/PCBs/ABSIS/ABSIS_Mega/assets/13.PNG

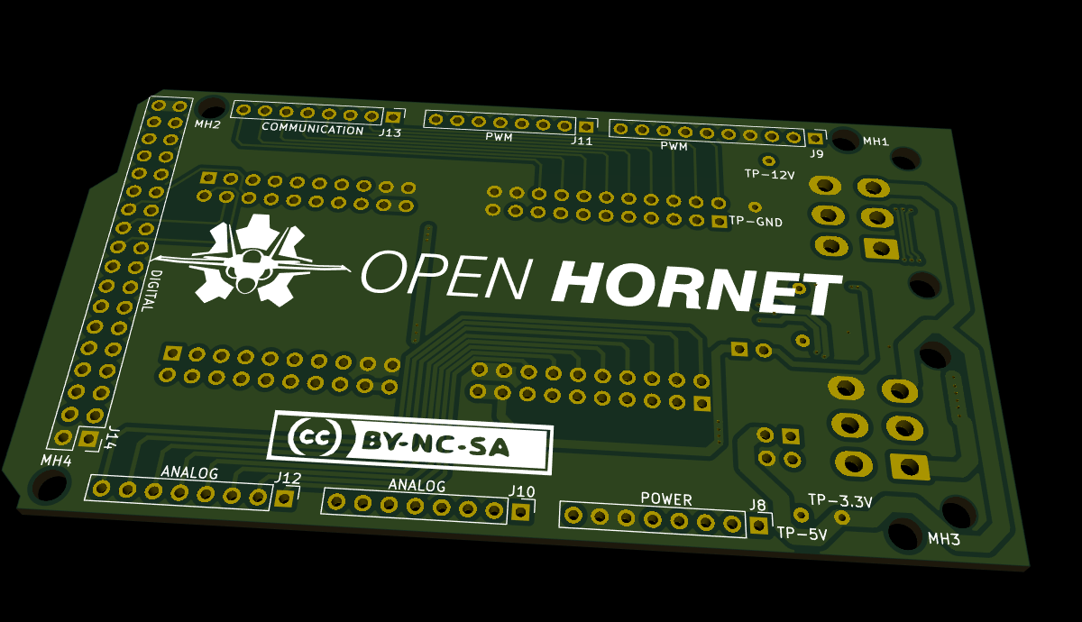
ECAD/PCBs/ABSIS/ABSIS_Mega/assets/13.PNG
