jrsteensen/OpenHornet/ECAD/PCBs/ABSIS/ABSIS_Mega/assets/14.PNG

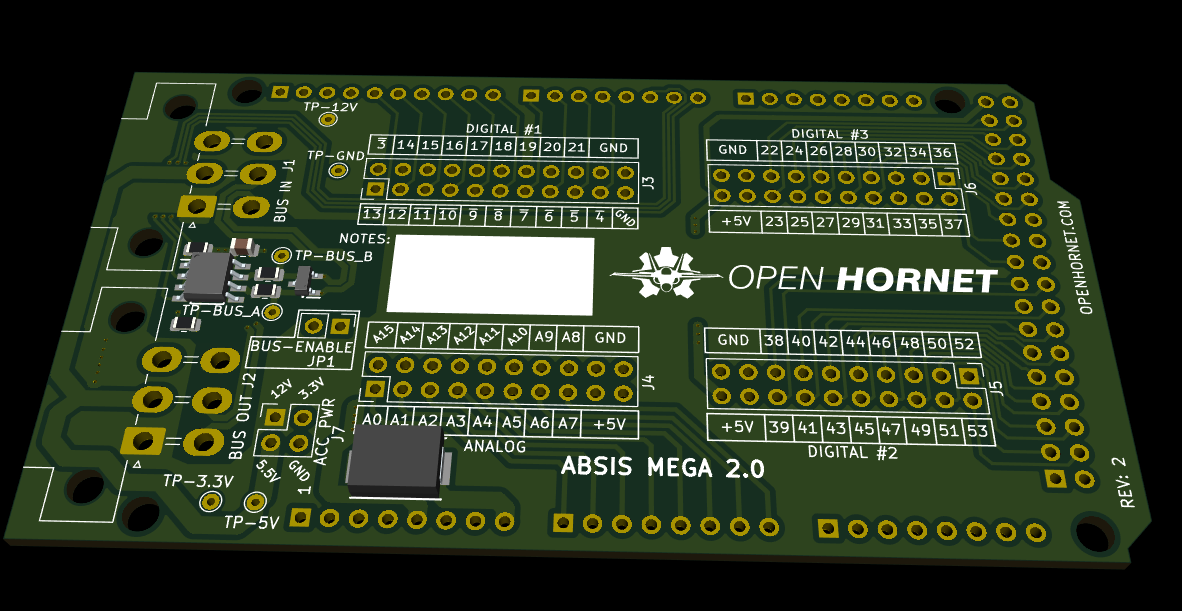
ECAD/PCBs/ABSIS/ABSIS_Mega/assets/14.PNG
