jrsteensen/OpenHornet/ECAD/PCBs/ABSIS/ABSIS_Mega/Assets/ABSIS_Mega-BOT.png

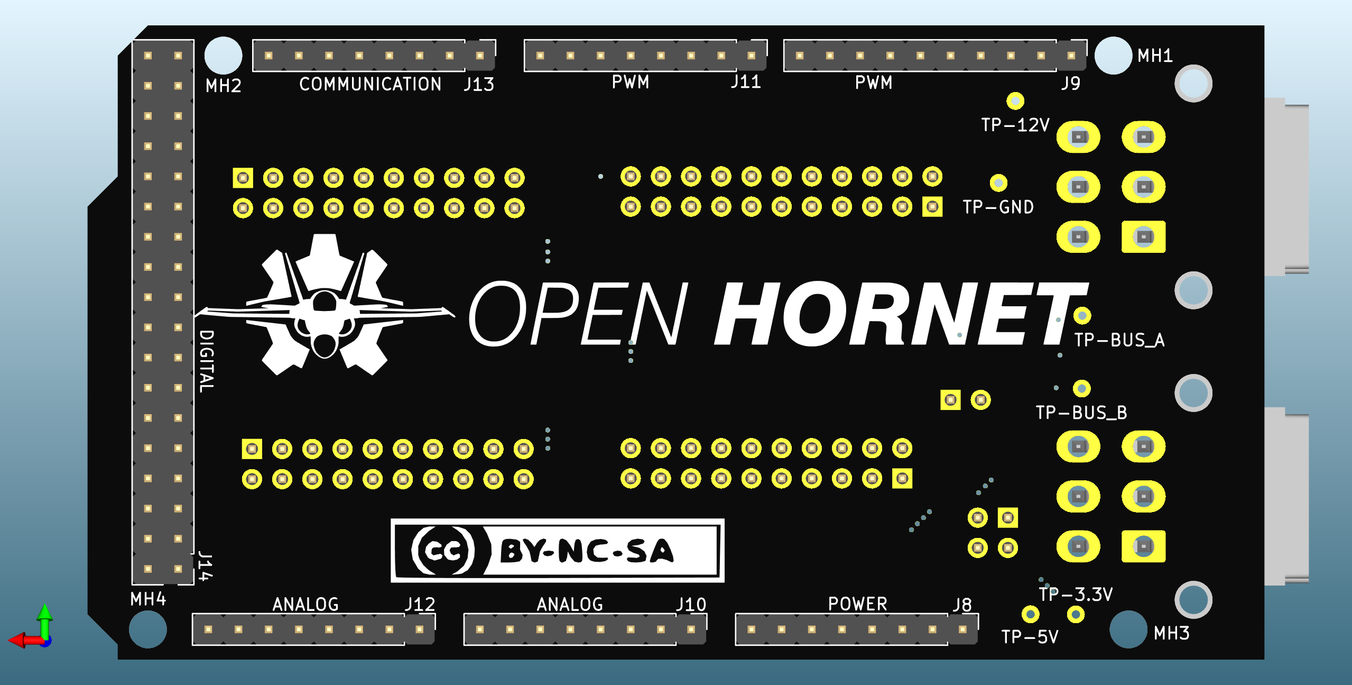
ECAD/PCBs/ABSIS/ABSIS_Mega/Assets/ABSIS_Mega-BOT.png
