jrsteensen/OpenHornet/ECAD/PCBs/ABSIS/ABSIS_Mega/Assets/ABSIS_Mega-BOT_ISO.png

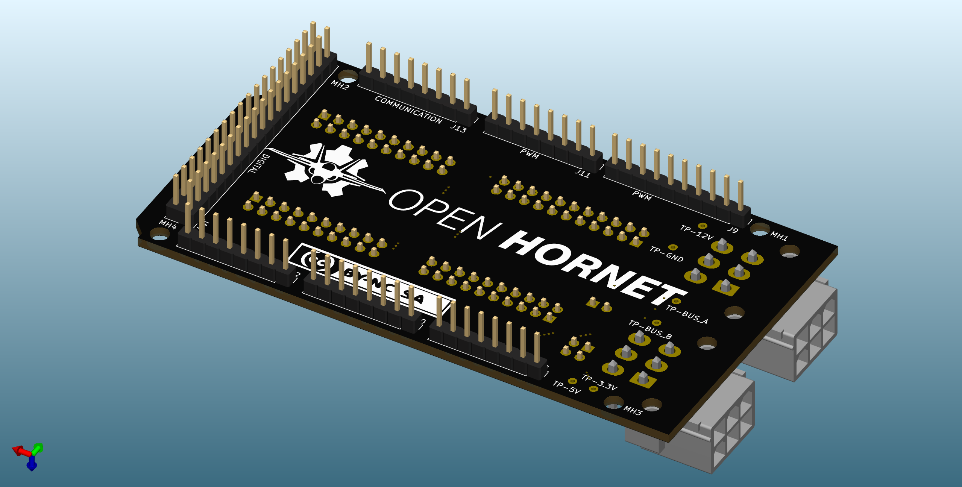
ECAD/PCBs/ABSIS/ABSIS_Mega/Assets/ABSIS_Mega-BOT_ISO.png
