jrsteensen/OpenHornet/ECAD/PCBs/ABSIS/ABSIS_Mega/Assets/ABSIS_Mega-TOP.png

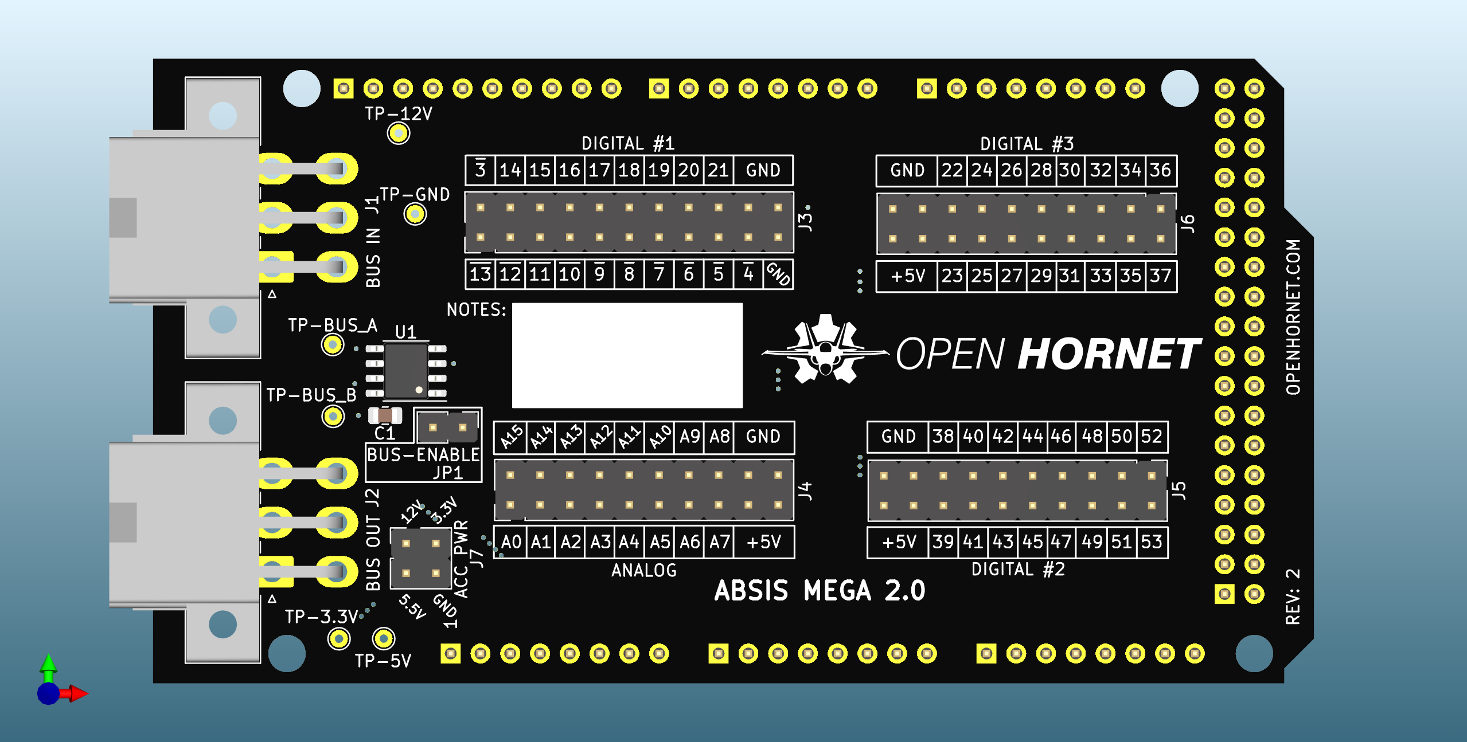
ECAD/PCBs/ABSIS/ABSIS_Mega/Assets/ABSIS_Mega-TOP.png
