jrsteensen/OpenHornet/ECAD/PCBs/ABSIS/xx_IN_DEV_ABSIS_Pro Micro/Assets/ABSIS_Pro_Micro_TOP_ISO.png

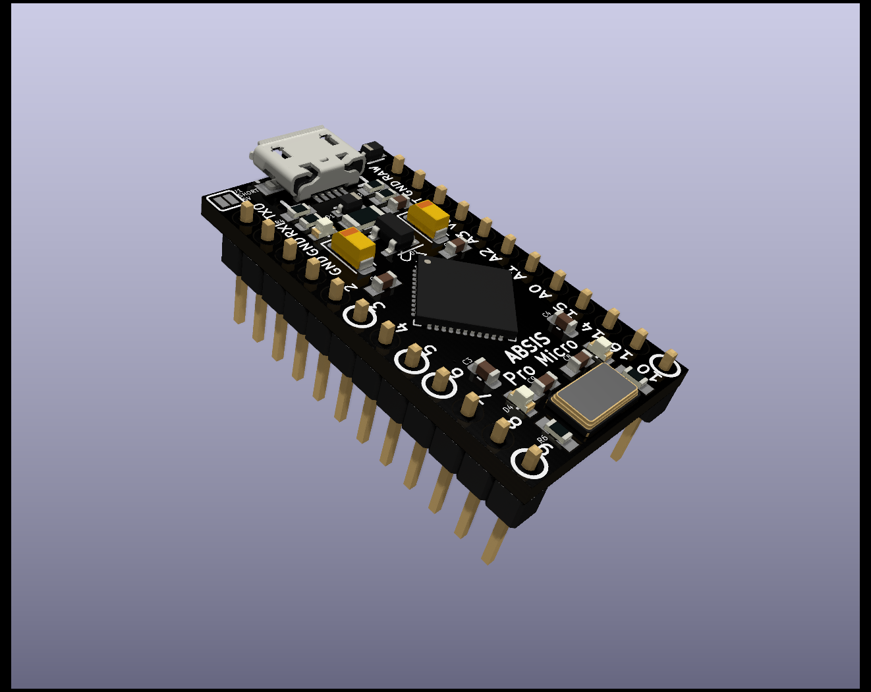
ECAD/PCBs/ABSIS/xx_IN_DEV_ABSIS_Pro Micro/Assets/ABSIS_Pro_Micro_TOP_ISO.png
