jrsteensen/OpenHornet/ECAD/PCBs/ABSIS/xx_IN_DEV_ABSIS_Pro Micro/Documentation/IMG_5492.jpg

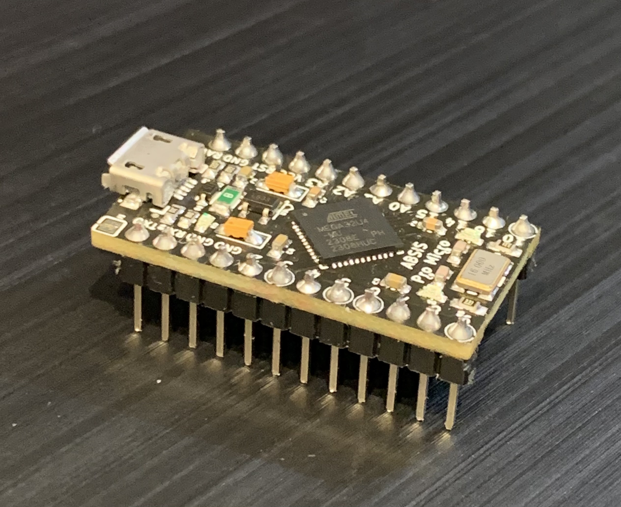
ECAD/PCBs/ABSIS/xx_IN_DEV_ABSIS_Pro Micro/Documentation/IMG_5492.jpg
