jrsteensen/OpenHornet/ECAD/PCBs/Backlight PCBs/Backlighting_Type A/ANT SEL PANEL/Assets/ANT SEL PANEL-BOT.png

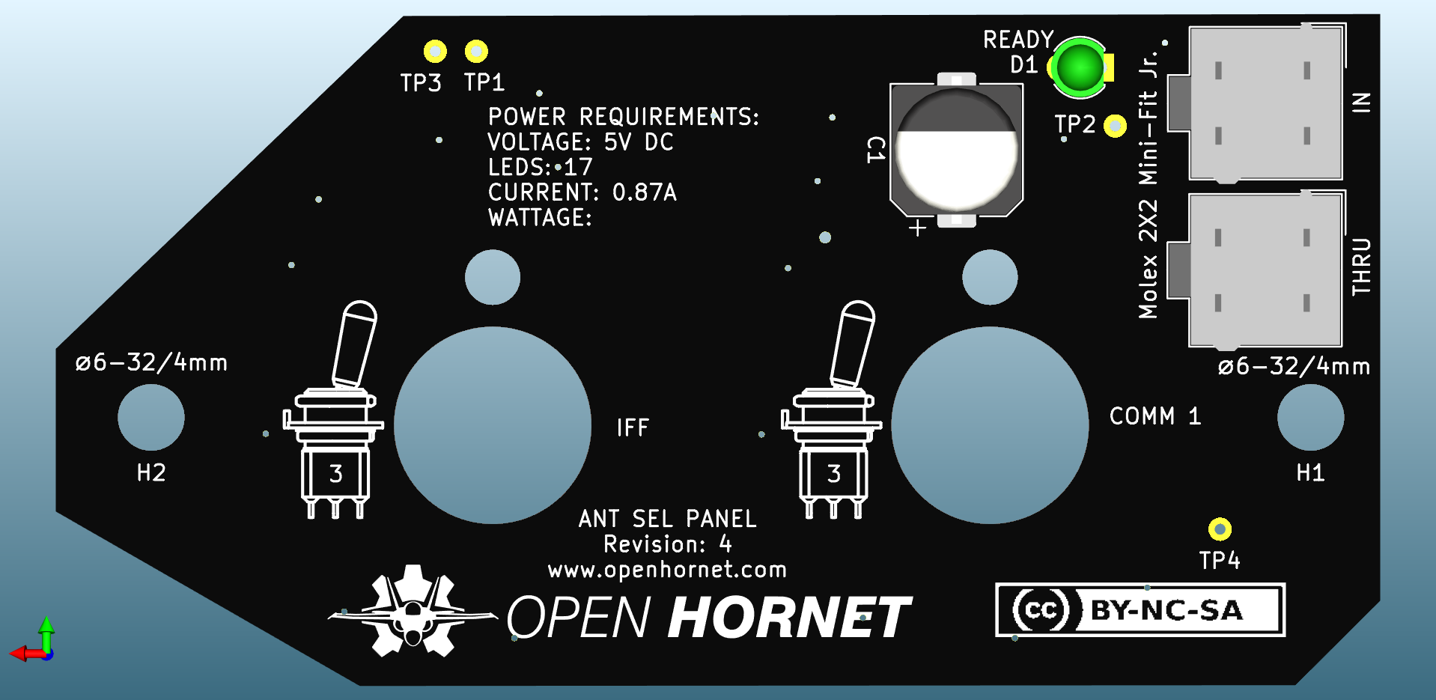
ECAD/PCBs/Backlight PCBs/Backlighting_Type A/ANT SEL PANEL/Assets/ANT SEL PANEL-BOT.png
