jrsteensen/OpenHornet/ECAD/PCBs/Backlight PCBs/Backlighting_Type A/APU ENG CRANK PANEL/Assets/APU ENG CRANK PANEL-BOT_ISO.png

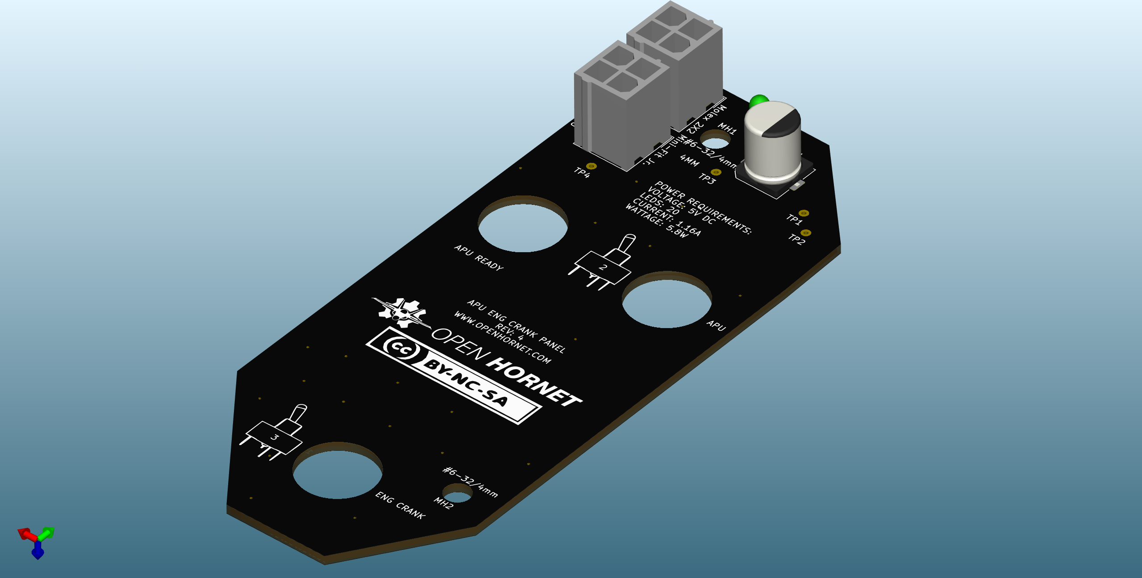
ECAD/PCBs/Backlight PCBs/Backlighting_Type A/APU ENG CRANK PANEL/Assets/APU ENG CRANK PANEL-BOT_ISO.png
