jrsteensen/OpenHornet/ECAD/PCBs/Backlight PCBs/Backlighting_Type A/AV COOL PANEL/Assets/AV COOL PANEL-BOT_ISO.png

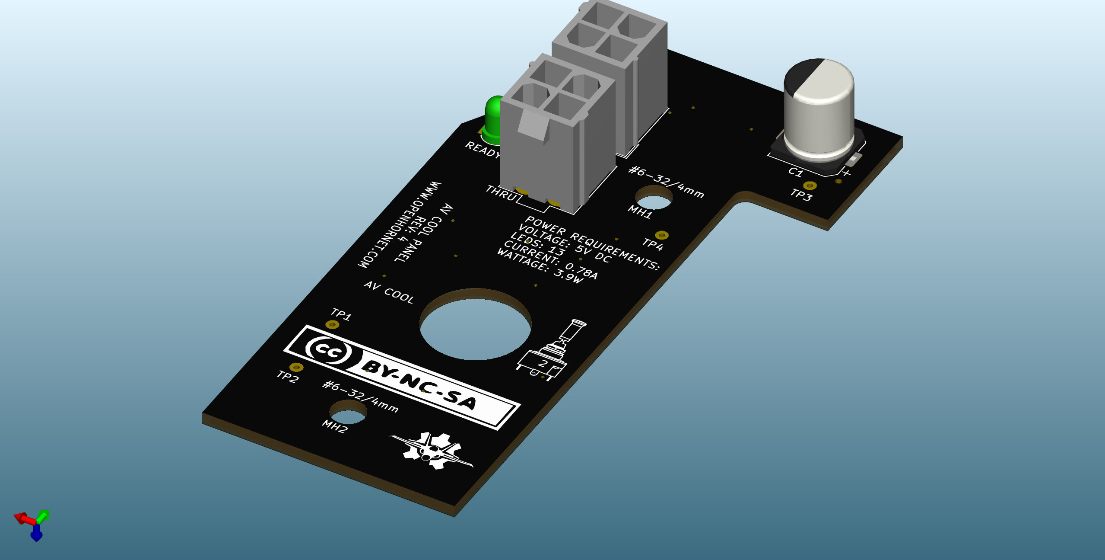
ECAD/PCBs/Backlight PCBs/Backlighting_Type A/AV COOL PANEL/Assets/AV COOL PANEL-BOT_ISO.png
