jrsteensen/OpenHornet/ECAD/PCBs/Backlight PCBs/Backlighting_Type A/AV COOL PANEL/Assets/AV COOL PANEL-TOP_ISO.png

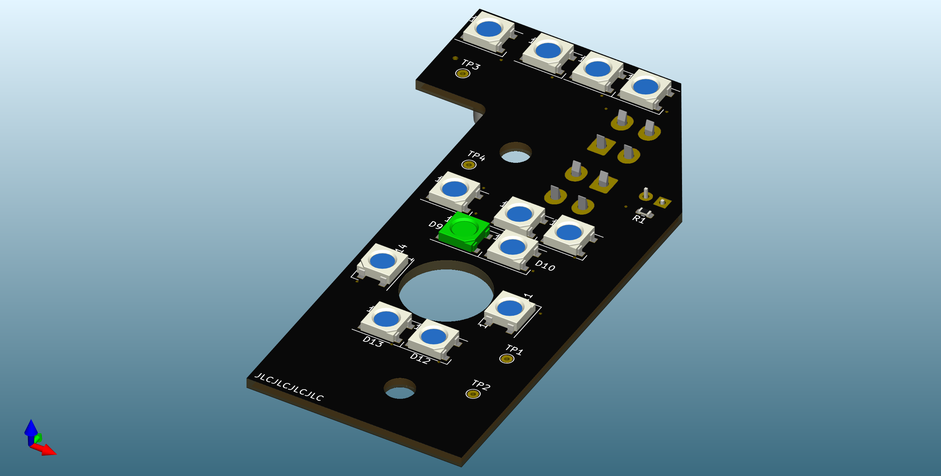
ECAD/PCBs/Backlight PCBs/Backlighting_Type A/AV COOL PANEL/Assets/AV COOL PANEL-TOP_ISO.png
