jrsteensen/OpenHornet/ECAD/PCBs/Backlight PCBs/Backlighting_Type A/CAUTION LIGHTS PANEL/Assets/CAUTION LIGHTS PANEL-BOT.png

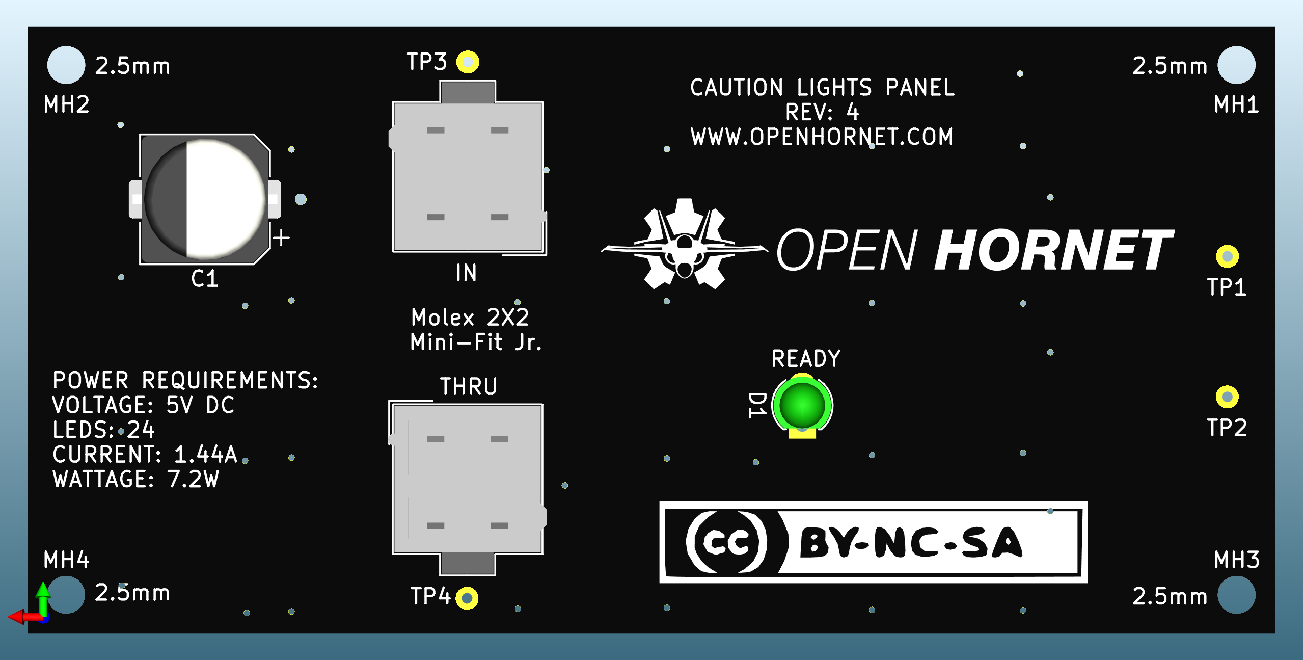
ECAD/PCBs/Backlight PCBs/Backlighting_Type A/CAUTION LIGHTS PANEL/Assets/CAUTION LIGHTS PANEL-BOT.png
