jrsteensen/OpenHornet/ECAD/PCBs/Backlight PCBs/Backlighting_Type A/DEFOG PANEL/Assets/DEFOG PANEL-BOT.png

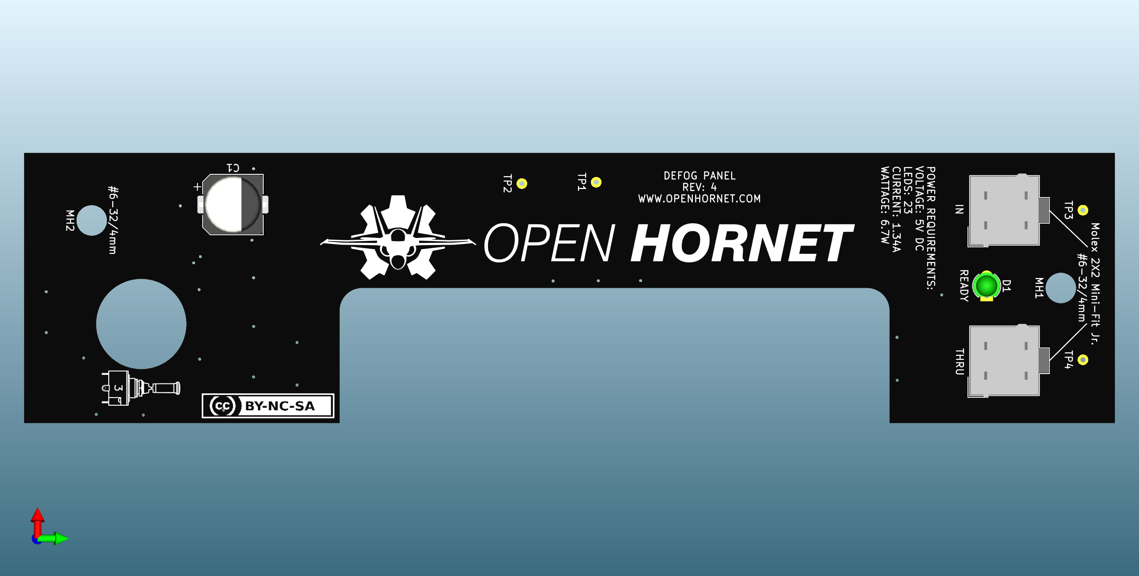
ECAD/PCBs/Backlight PCBs/Backlighting_Type A/DEFOG PANEL/Assets/DEFOG PANEL-BOT.png
