jrsteensen/OpenHornet/ECAD/PCBs/Backlight PCBs/Backlighting_Type A/ECM DISP PANEL/Assets/ECM DISP PANEL-BOT_ISO.png

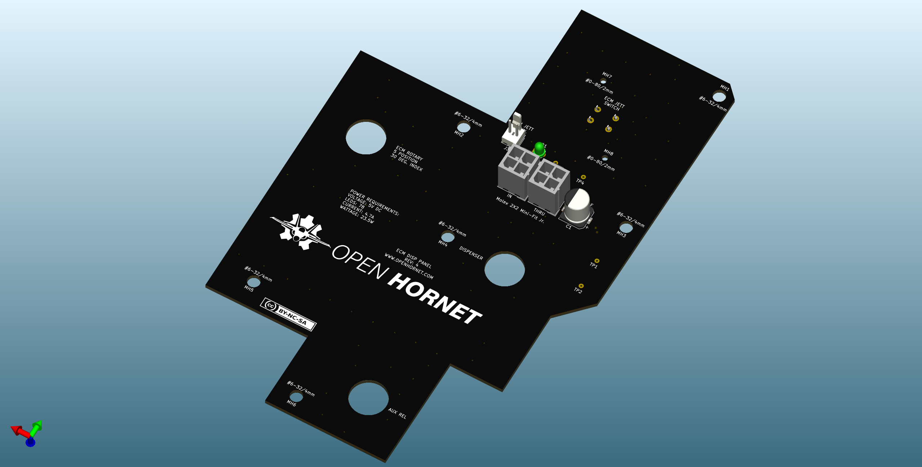
ECAD/PCBs/Backlight PCBs/Backlighting_Type A/ECM DISP PANEL/Assets/ECM DISP PANEL-BOT_ISO.png
