jrsteensen/OpenHornet/ECAD/PCBs/Backlight PCBs/Backlighting_Type A/ECS PANEL/Assets/ECS PANEL-BOT.png

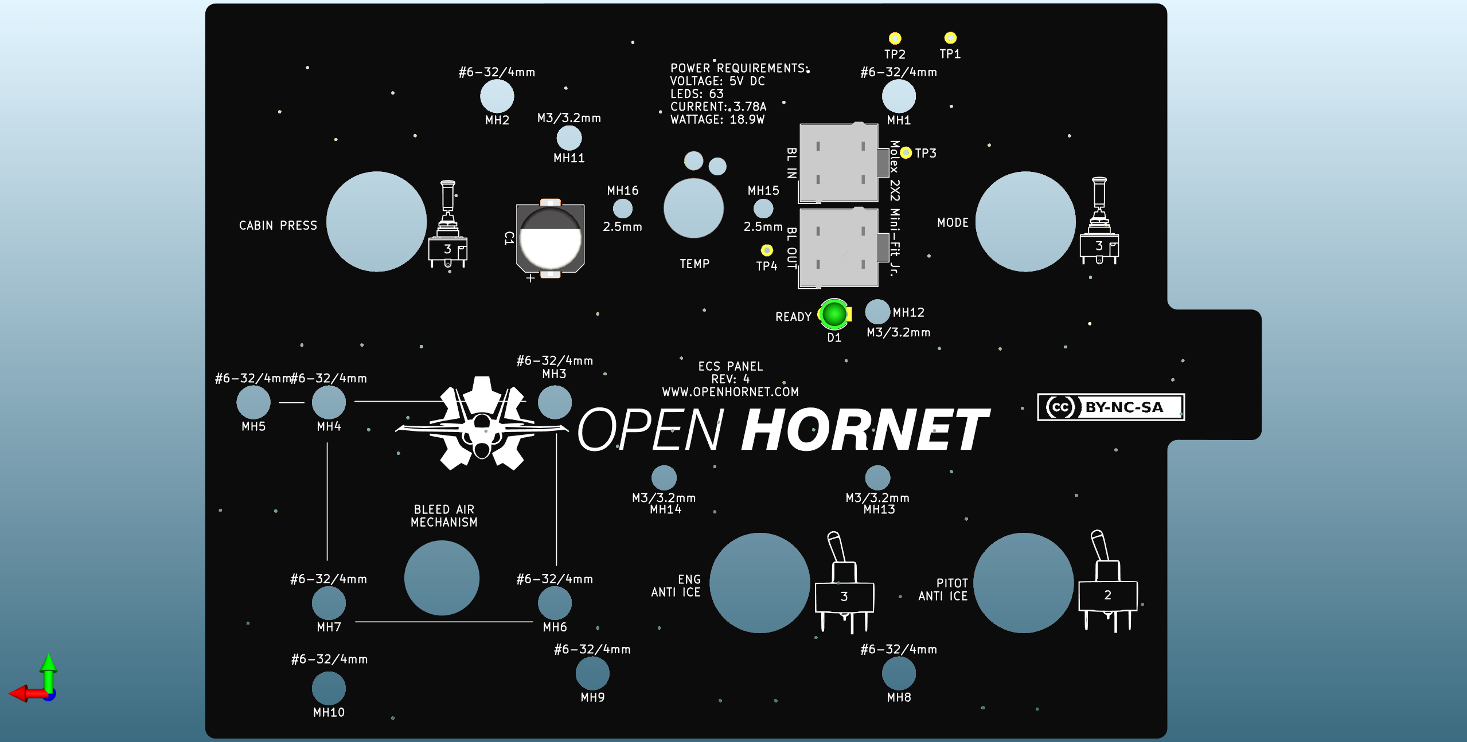
ECAD/PCBs/Backlight PCBs/Backlighting_Type A/ECS PANEL/Assets/ECS PANEL-BOT.png
