jrsteensen/OpenHornet/ECAD/PCBs/Backlight PCBs/Backlighting_Type A/ELEC PANEL/Assets/ELEC PANEL-BOT.png

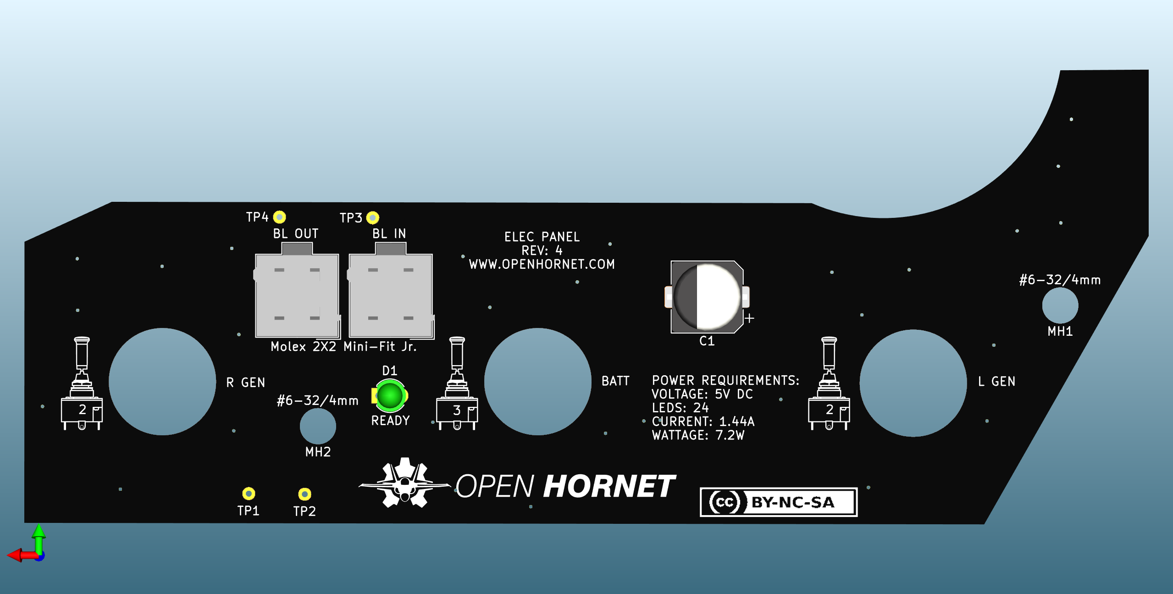
ECAD/PCBs/Backlight PCBs/Backlighting_Type A/ELEC PANEL/Assets/ELEC PANEL-BOT.png
