jrsteensen/OpenHornet/ECAD/PCBs/Backlight PCBs/Backlighting_Type A/EXT LT PANEL/Assets/EXT LT PANEL-BOT_ISO.png

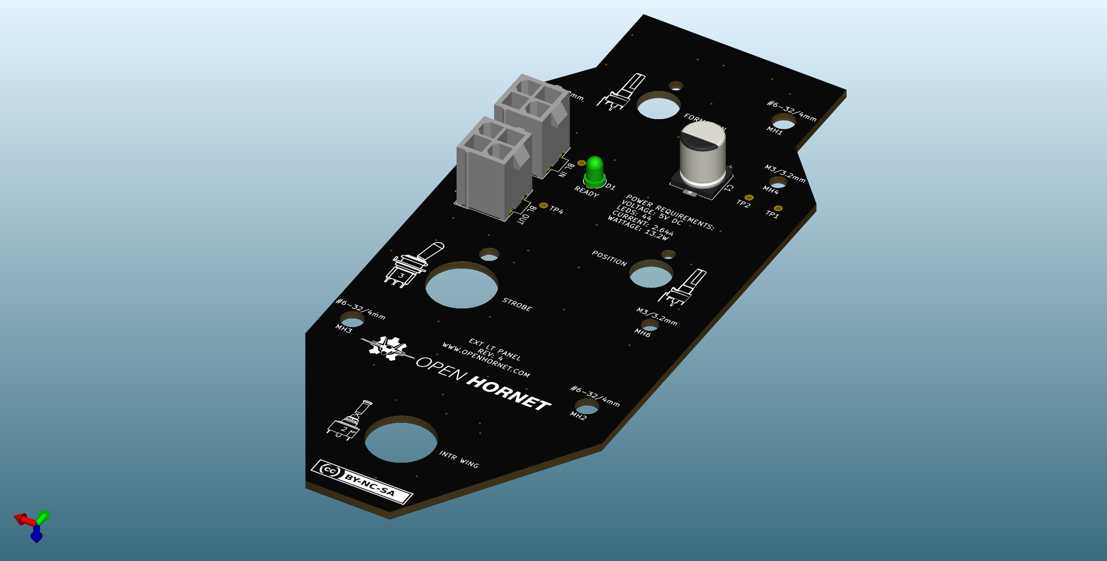
ECAD/PCBs/Backlight PCBs/Backlighting_Type A/EXT LT PANEL/Assets/EXT LT PANEL-BOT_ISO.png
