jrsteensen/OpenHornet/ECAD/PCBs/Backlight PCBs/Backlighting_Type A/FCS PANEL/Assets/FCS PANEL-BOT.png

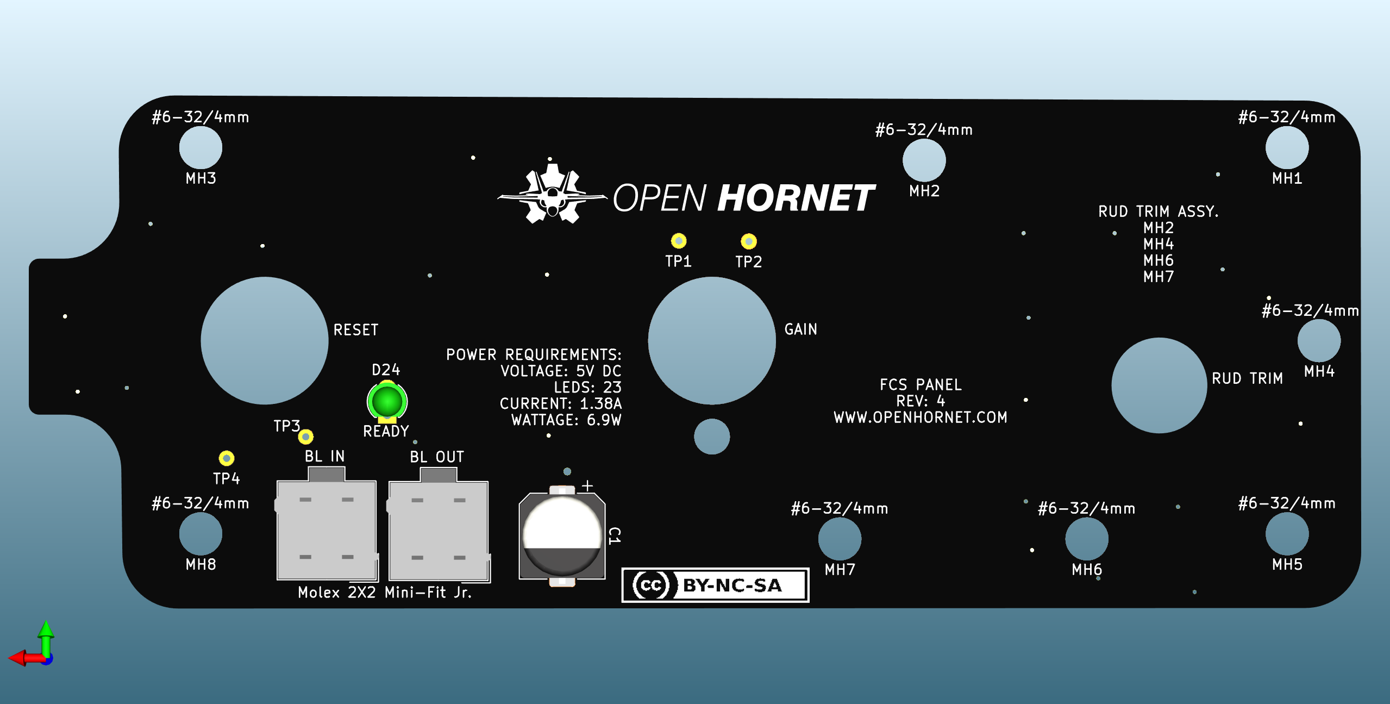
ECAD/PCBs/Backlight PCBs/Backlighting_Type A/FCS PANEL/Assets/FCS PANEL-BOT.png
