jrsteensen/OpenHornet/ECAD/PCBs/Backlight PCBs/Backlighting_Type A/FUEL PANEL/Assets/FUEL PANEL-BOT.png

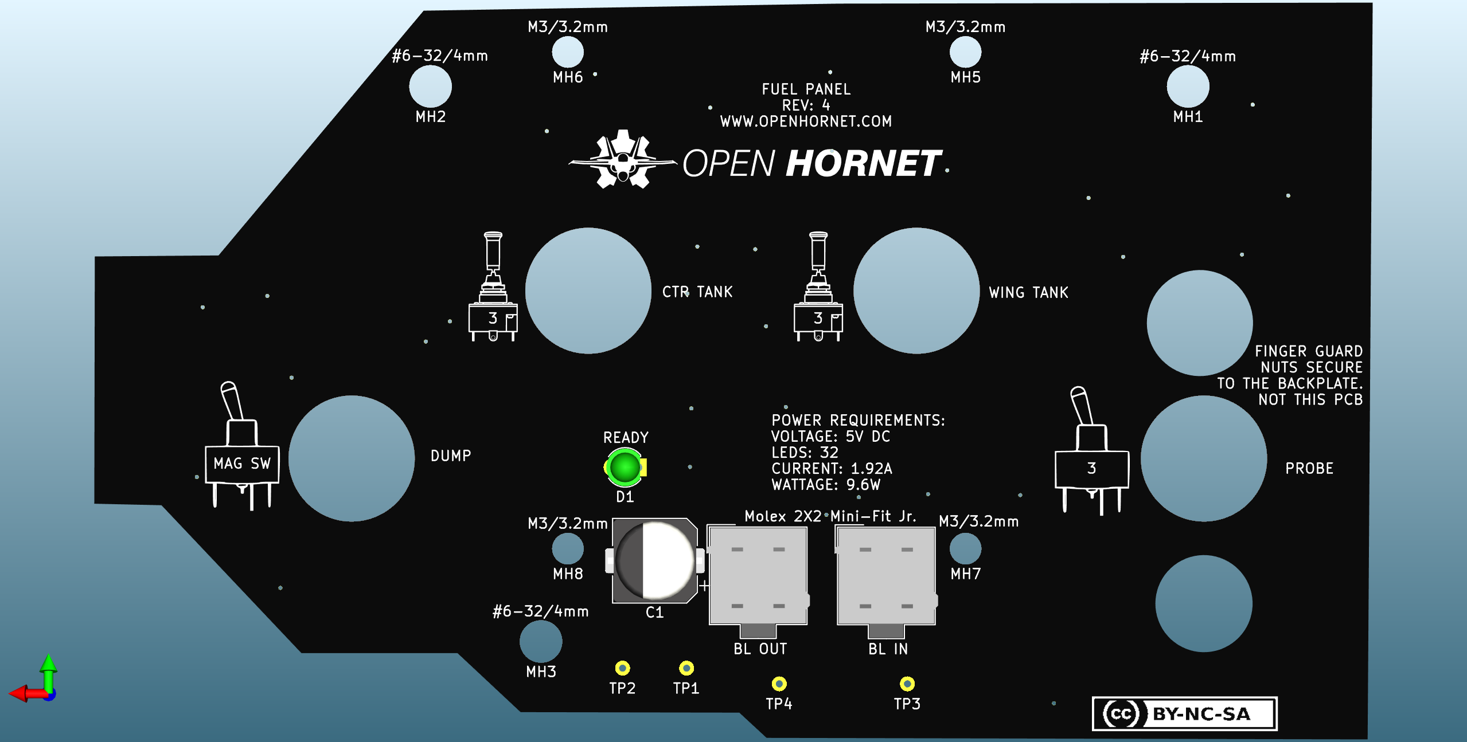
ECAD/PCBs/Backlight PCBs/Backlighting_Type A/FUEL PANEL/Assets/FUEL PANEL-BOT.png
