jrsteensen/OpenHornet/ECAD/PCBs/Backlight PCBs/Backlighting_Type A/GEN TIE PANEL/Assets/GEN TIE PANEL-BOT_ISO.png

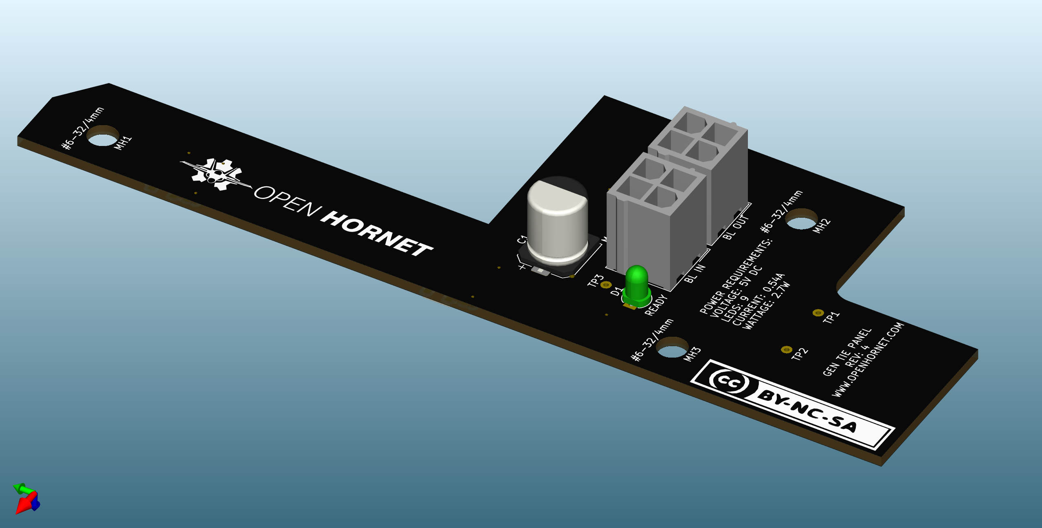
ECAD/PCBs/Backlight PCBs/Backlighting_Type A/GEN TIE PANEL/Assets/GEN TIE PANEL-BOT_ISO.png
