jrsteensen/OpenHornet/ECAD/PCBs/Backlight PCBs/Backlighting_Type A/HUD PANEL/Assets/HUD PANEL-BOT.png

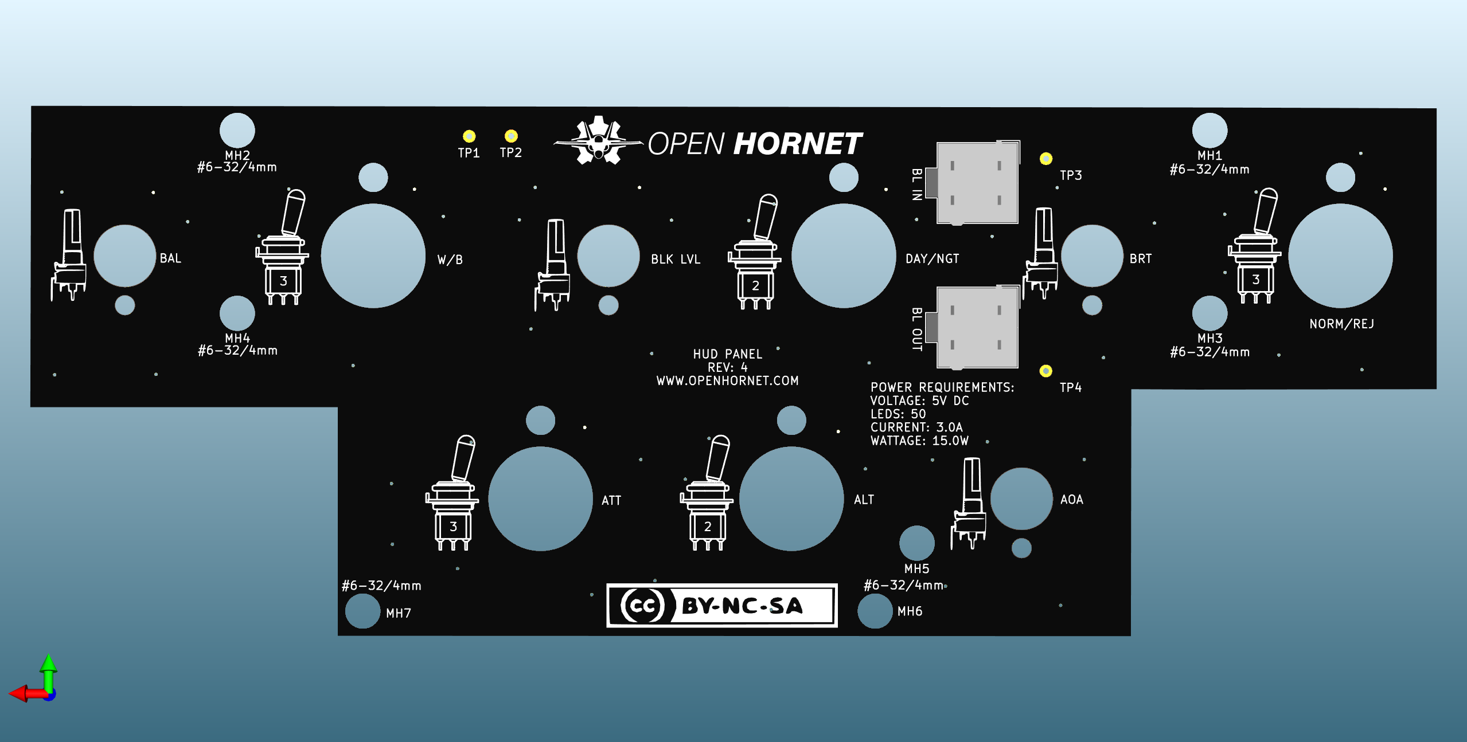
ECAD/PCBs/Backlight PCBs/Backlighting_Type A/HUD PANEL/Assets/HUD PANEL-BOT.png
