jrsteensen/OpenHornet/ECAD/PCBs/Backlight PCBs/Backlighting_Type A/HUD VID RCD PANEL/Assets/HUD VID RCD PANEL-BOT.png

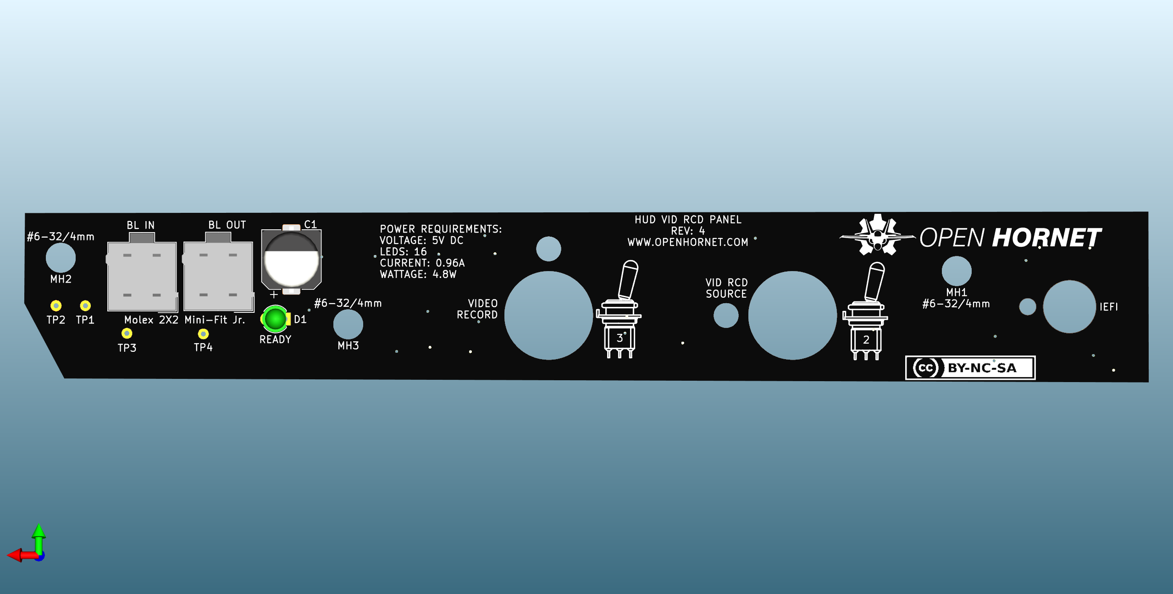
ECAD/PCBs/Backlight PCBs/Backlighting_Type A/HUD VID RCD PANEL/Assets/HUD VID RCD PANEL-BOT.png
