jrsteensen/OpenHornet/ECAD/PCBs/Backlight PCBs/Backlighting_Type A/HYD ISO PANEL/Assets/HYD ISO PANEL-BOT.png

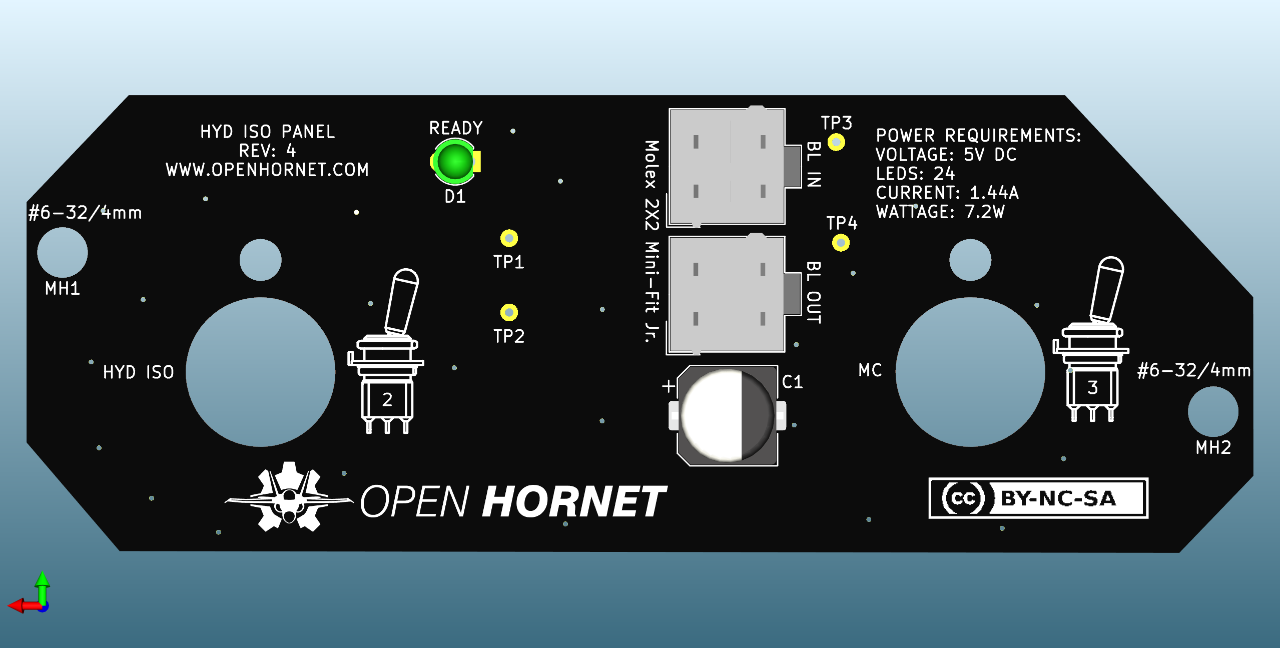
ECAD/PCBs/Backlight PCBs/Backlighting_Type A/HYD ISO PANEL/Assets/HYD ISO PANEL-BOT.png
