jrsteensen/OpenHornet/ECAD/PCBs/Backlight PCBs/Backlighting_Type A/INTR LT PANEL/Assets/INTR LT PANEL-BOT.png

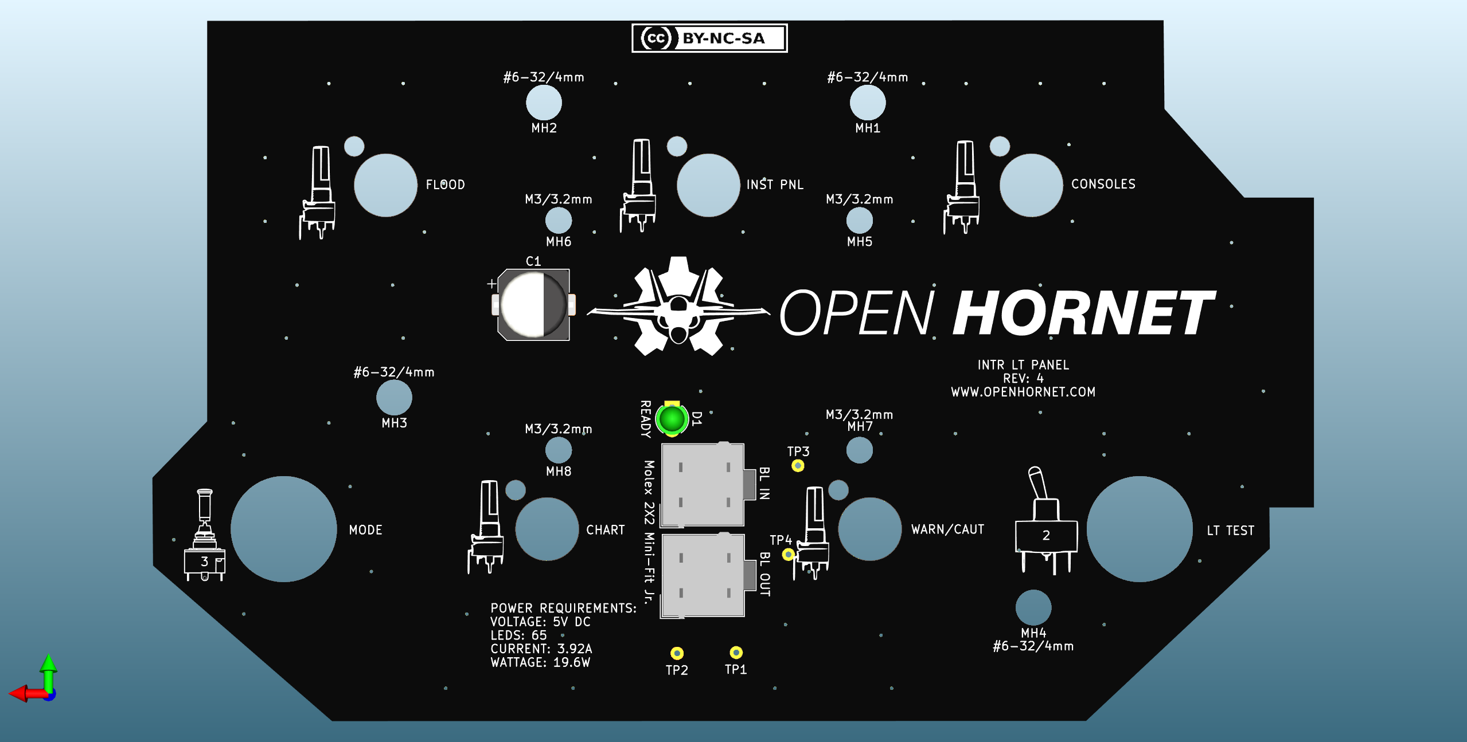
ECAD/PCBs/Backlight PCBs/Backlighting_Type A/INTR LT PANEL/Assets/INTR LT PANEL-BOT.png
