jrsteensen/OpenHornet/ECAD/PCBs/Backlight PCBs/Backlighting_Type A/JETT STATION SELECT PLACARD/Assets/JETT STATION SELECT PLACARD-BOT.png

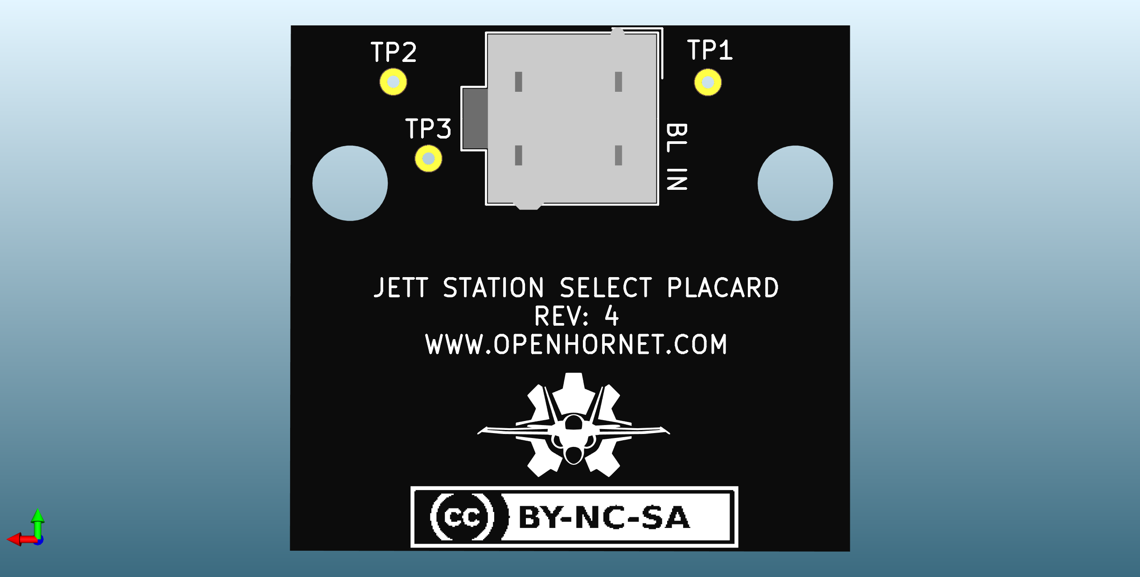
ECAD/PCBs/Backlight PCBs/Backlighting_Type A/JETT STATION SELECT PLACARD/Assets/JETT STATION SELECT PLACARD-BOT.png
