jrsteensen/OpenHornet/ECAD/PCBs/Backlight PCBs/Backlighting_Type A/KY-58 PANEL/Assets/KY-58 PANEL-BOT.png

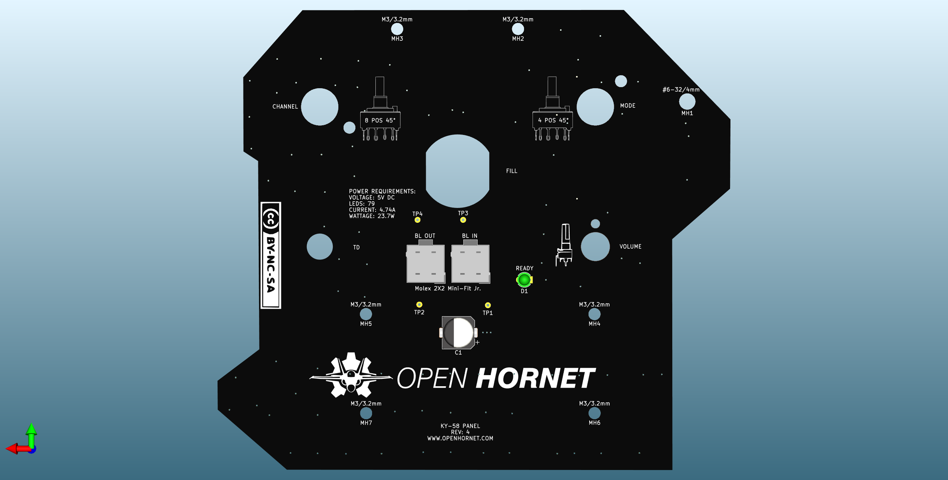
ECAD/PCBs/Backlight PCBs/Backlighting_Type A/KY-58 PANEL/Assets/KY-58 PANEL-BOT.png
