jrsteensen/OpenHornet/ECAD/PCBs/Backlight PCBs/Backlighting_Type A/LANDING GEAR PANEL/Assets/LANDING GEAR PANEL-BOT.png

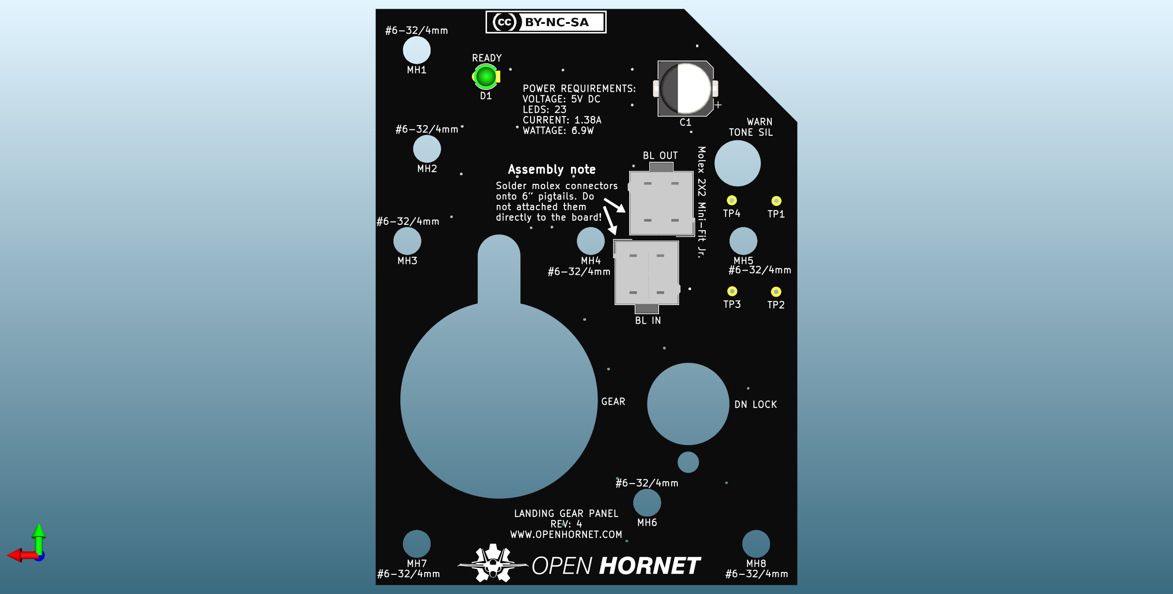
ECAD/PCBs/Backlight PCBs/Backlighting_Type A/LANDING GEAR PANEL/Assets/LANDING GEAR PANEL-BOT.png
