jrsteensen/OpenHornet/ECAD/PCBs/Backlight PCBs/Backlighting_Type A/LDG WING FOLD PLACARD/Assets/LDG WING FOLD PLACARD-BOT_ISO.png

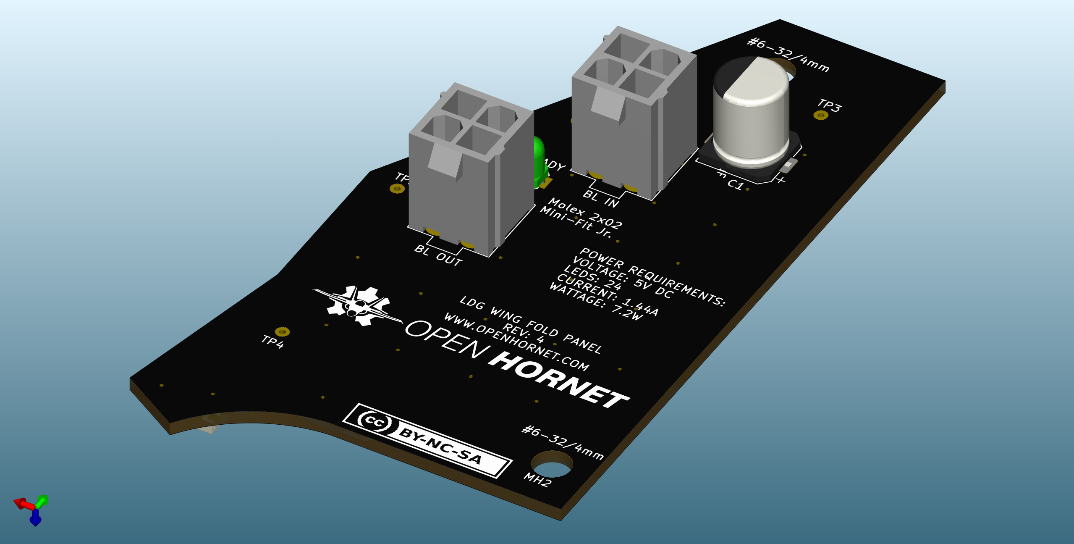
ECAD/PCBs/Backlight PCBs/Backlighting_Type A/LDG WING FOLD PLACARD/Assets/LDG WING FOLD PLACARD-BOT_ISO.png
