jrsteensen/OpenHornet/ECAD/PCBs/Backlight PCBs/Backlighting_Type A/LEFT CIRCUIT BREAKER/Assets/LEFT CIRCUIT BREAKER-BOT.png

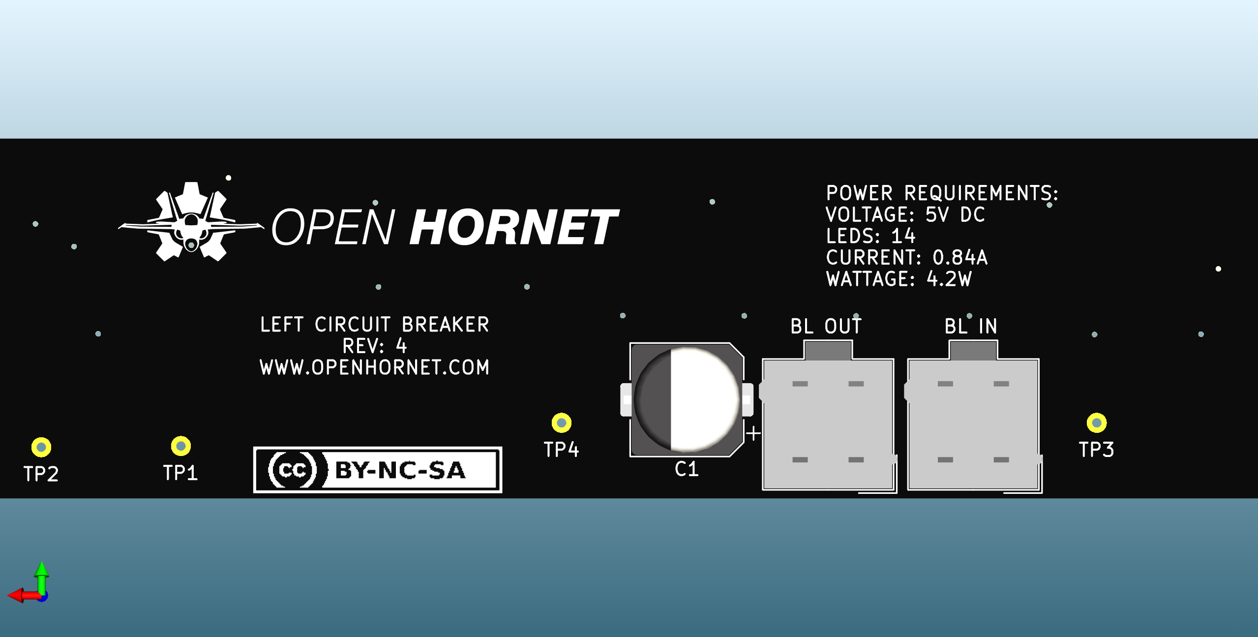
ECAD/PCBs/Backlight PCBs/Backlighting_Type A/LEFT CIRCUIT BREAKER/Assets/LEFT CIRCUIT BREAKER-BOT.png
