jrsteensen/OpenHornet/ECAD/PCBs/Backlight PCBs/Backlighting_Type A/MASTER ARM PANEL/Assets/MASTER ARM PANEL-TOP_ISO.png

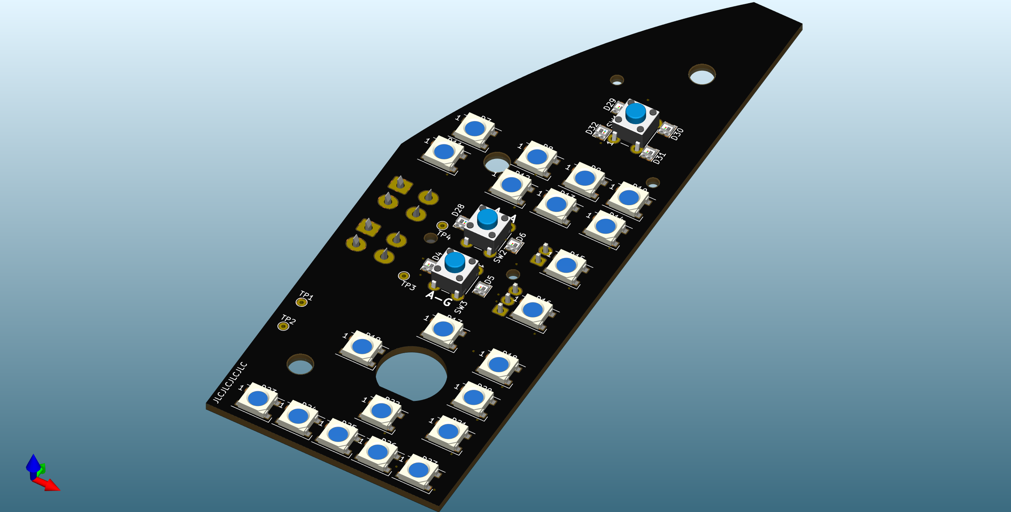
ECAD/PCBs/Backlight PCBs/Backlighting_Type A/MASTER ARM PANEL/Assets/MASTER ARM PANEL-TOP_ISO.png
