jrsteensen/OpenHornet/ECAD/PCBs/Backlight PCBs/Backlighting_Type A/OBOGS PANEL/Assets/OBOGS PANEL-BOT_ISO.png

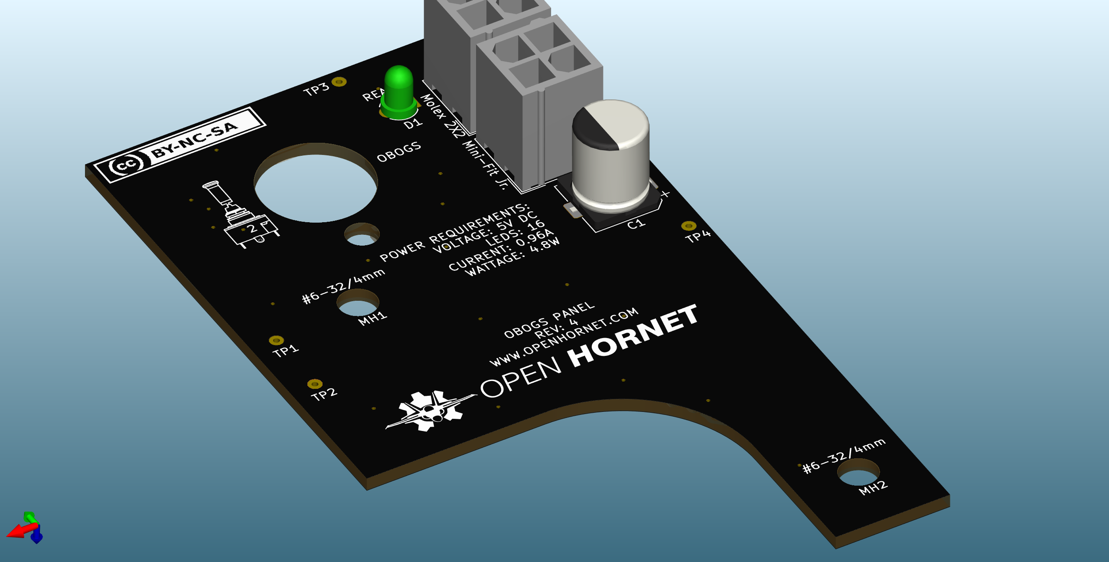
ECAD/PCBs/Backlight PCBs/Backlighting_Type A/OBOGS PANEL/Assets/OBOGS PANEL-BOT_ISO.png
