jrsteensen/OpenHornet/ECAD/PCBs/Backlight PCBs/Backlighting_Type A/SELECT JETT PANEL/Assets/SELECT JETT PANEL-BOT.png

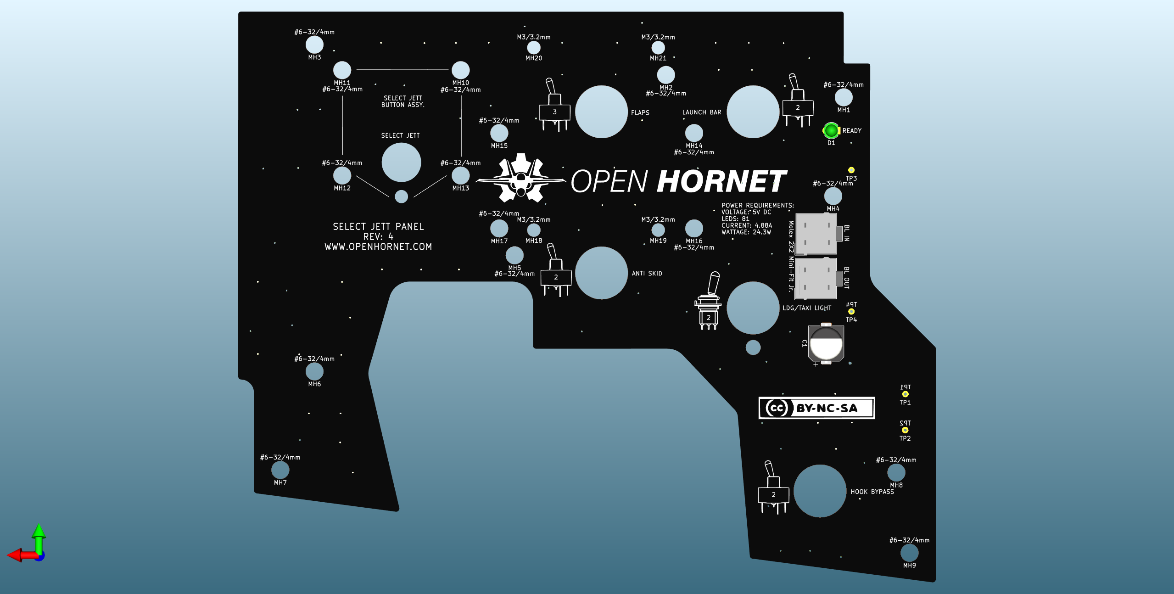
ECAD/PCBs/Backlight PCBs/Backlighting_Type A/SELECT JETT PANEL/Assets/SELECT JETT PANEL-BOT.png
