jrsteensen/OpenHornet/ECAD/PCBs/Backlight PCBs/Backlighting_Type A/SIM CONTROL PANEL/Assets/SIM CONTROL PANEL-BOT.png

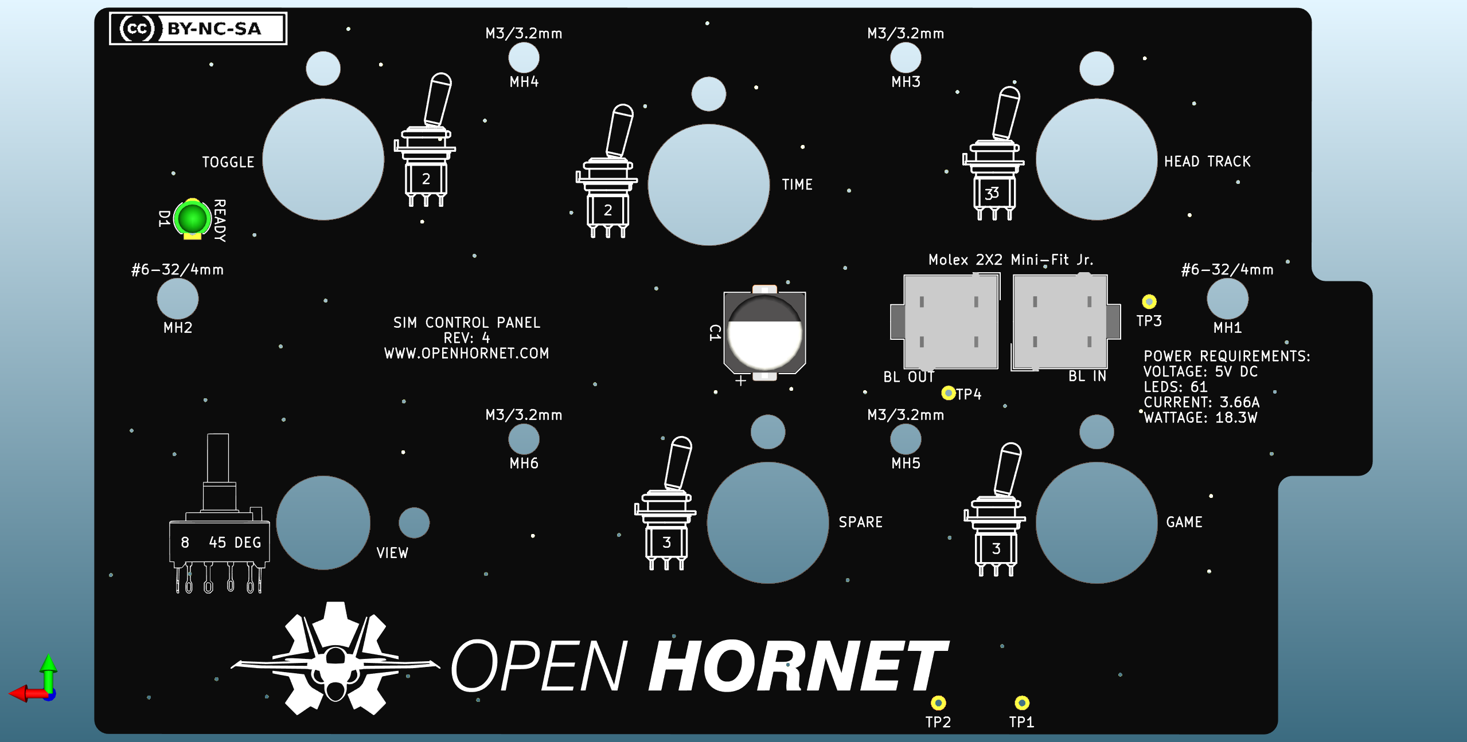
ECAD/PCBs/Backlight PCBs/Backlighting_Type A/SIM CONTROL PANEL/Assets/SIM CONTROL PANEL-BOT.png
