jrsteensen/OpenHornet/ECAD/PCBs/Backlight PCBs/Backlighting_Type A/SIM POWER PANEL/Assets/SIM POWER PANEL-BOT_ISO.png

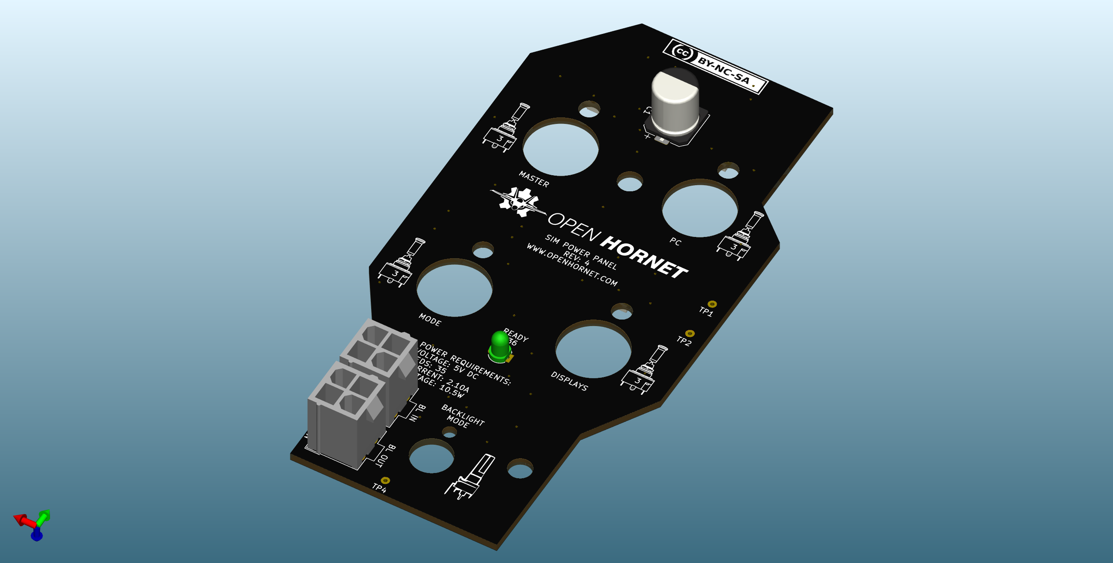
ECAD/PCBs/Backlight PCBs/Backlighting_Type A/SIM POWER PANEL/Assets/SIM POWER PANEL-BOT_ISO.png
