jrsteensen/OpenHornet/ECAD/PCBs/Backlight PCBs/Backlighting_Type A/SIM POWER PANEL/Assets/SIM POWER PANEL-TOP_ISO.png

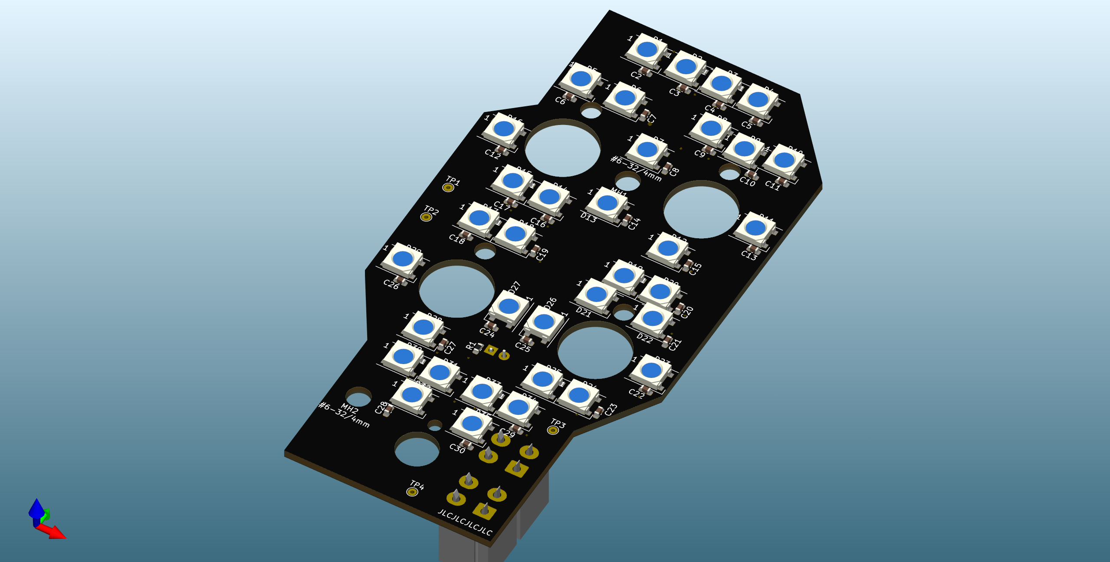
ECAD/PCBs/Backlight PCBs/Backlighting_Type A/SIM POWER PANEL/Assets/SIM POWER PANEL-TOP_ISO.png
