jrsteensen/OpenHornet/ECAD/PCBs/Backlight PCBs/Backlighting_Type A/SNSR PANEL/Assets/SNSR PANEL-BOT.png

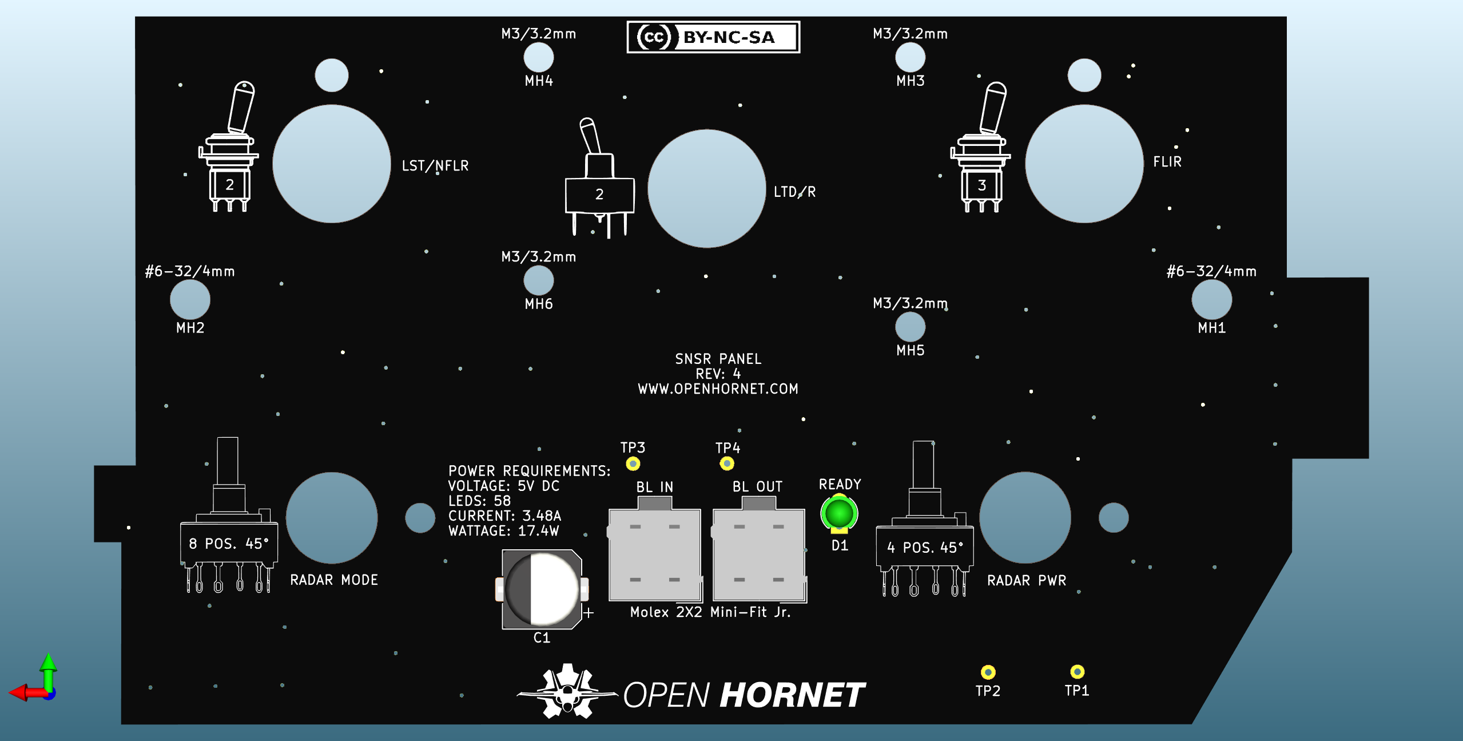
ECAD/PCBs/Backlight PCBs/Backlighting_Type A/SNSR PANEL/Assets/SNSR PANEL-BOT.png
