jrsteensen/OpenHornet/ECAD/PCBs/Backlight PCBs/Backlighting_Type A/SPIN RCV PANEL/Assets/SPIN RCV PANEL-BOT_ISO.png

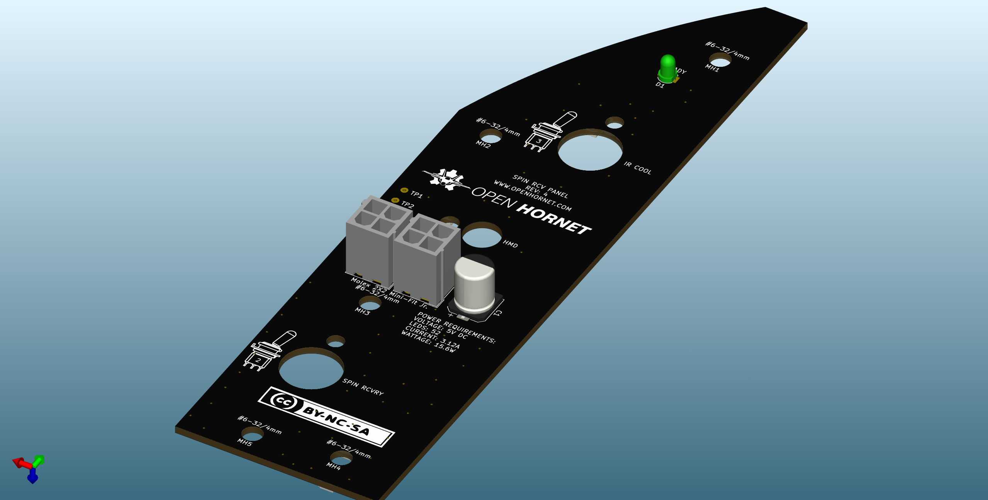
ECAD/PCBs/Backlight PCBs/Backlighting_Type A/SPIN RCV PANEL/Assets/SPIN RCV PANEL-BOT_ISO.png
