jrsteensen/OpenHornet/ECAD/PCBs/Functional PCBs/AMPCD/Assets/AMPCD-BOT.png

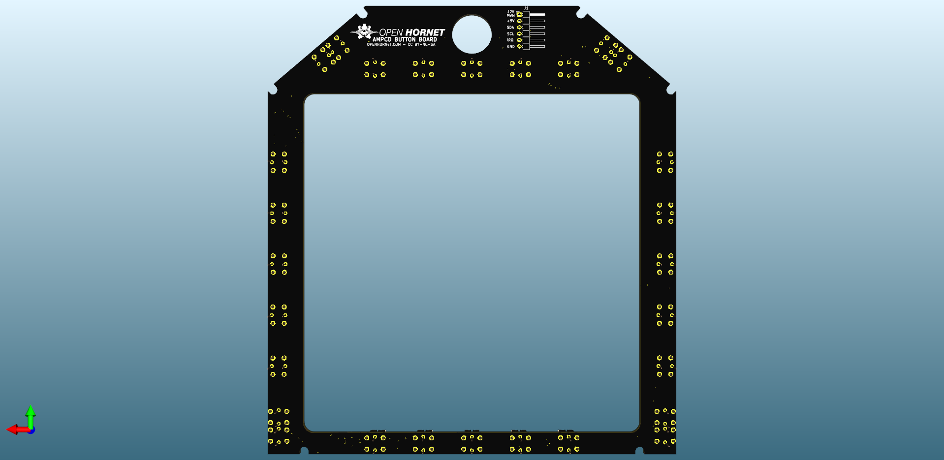
ECAD/PCBs/Functional PCBs/AMPCD/Assets/AMPCD-BOT.png
