jrsteensen/OpenHornet/ECAD/PCBs/Functional PCBs/AMPCD/Assets/AMPCD-BOT_ISO.png

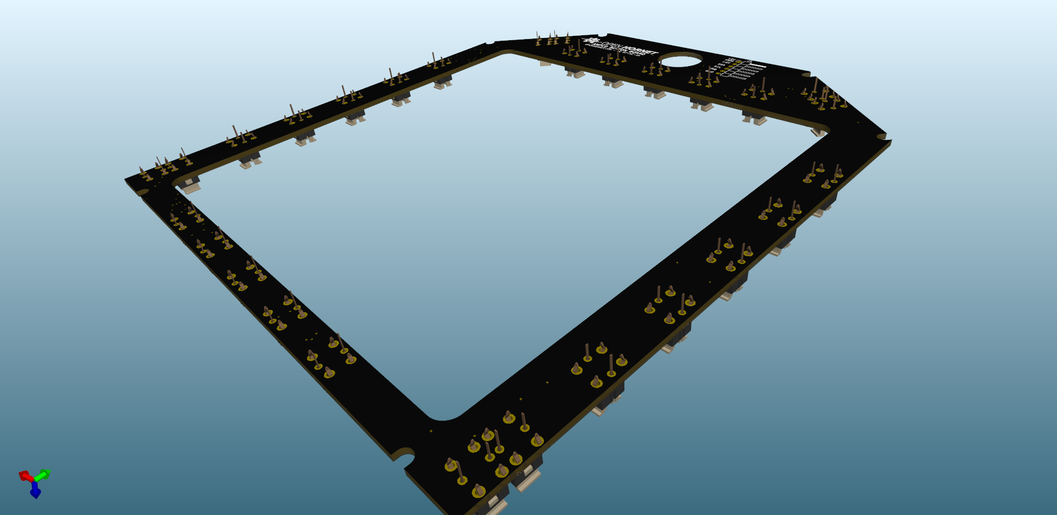
ECAD/PCBs/Functional PCBs/AMPCD/Assets/AMPCD-BOT_ISO.png
