jrsteensen/OpenHornet/ECAD/PCBs/Functional PCBs/AMPCD/Assets/AMPCD-TOP_ISO.png

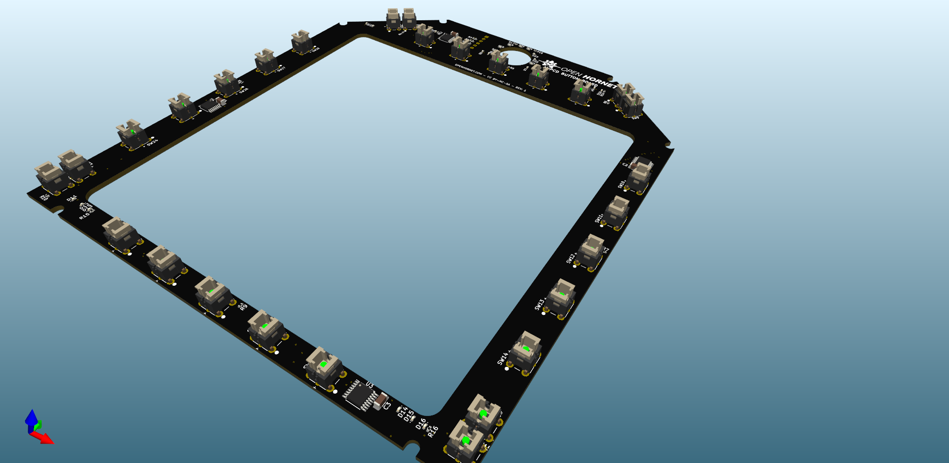
ECAD/PCBs/Functional PCBs/AMPCD/Assets/AMPCD-TOP_ISO.png
