jrsteensen/OpenHornet/ECAD/PCBs/Functional PCBs/CONTROLLER_AMPCD DDI/Assets/CONTROLLER_AMPCD DDI-BOT.png

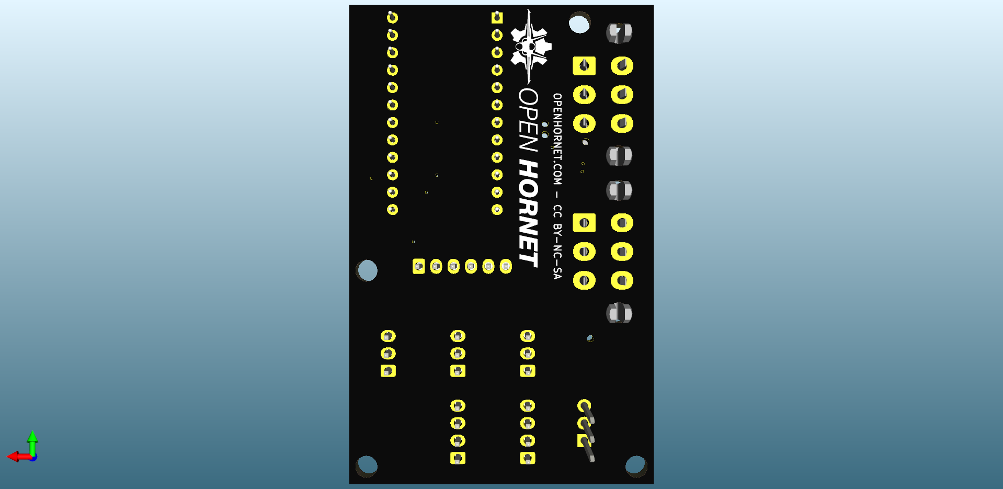
ECAD/PCBs/Functional PCBs/CONTROLLER_AMPCD DDI/Assets/CONTROLLER_AMPCD DDI-BOT.png
