jrsteensen/OpenHornet/ECAD/PCBs/Functional PCBs/CONTROLLER_Stick/Assets/CONTROLLER_Stick-BOT.png

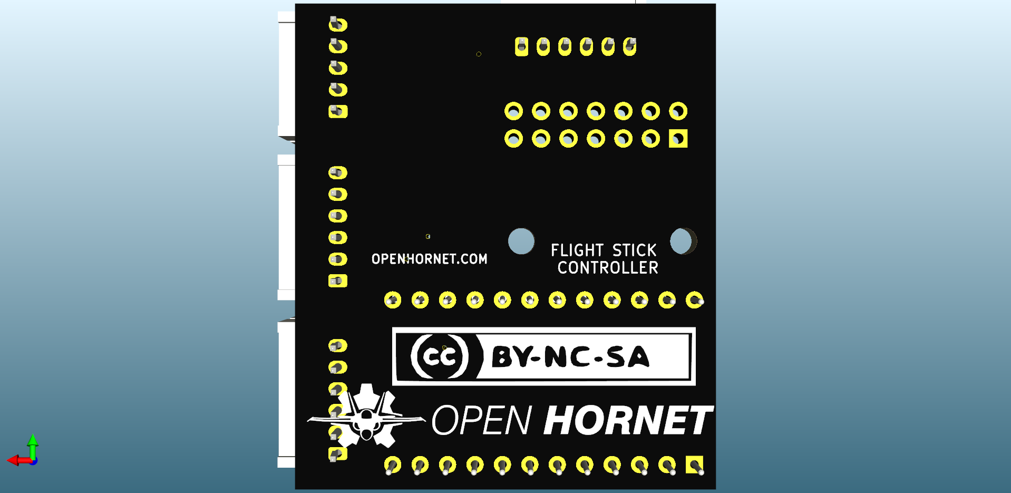
ECAD/PCBs/Functional PCBs/CONTROLLER_Stick/Assets/CONTROLLER_Stick-BOT.png
