jrsteensen/OpenHornet/ECAD/PCBs/Functional PCBs/CONTROLLER_Throttle/Assets/CONTROLLER_Throttle-BOT.png

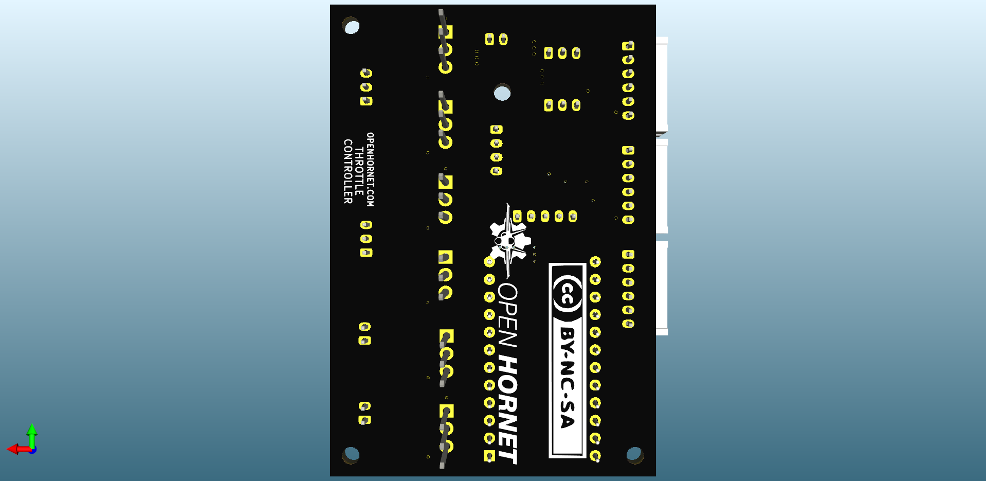
ECAD/PCBs/Functional PCBs/CONTROLLER_Throttle/Assets/CONTROLLER_Throttle-BOT.png
