jrsteensen/OpenHornet/ECAD/PCBs/Functional PCBs/DDI/Assets/DDI-BOT_ISO.png

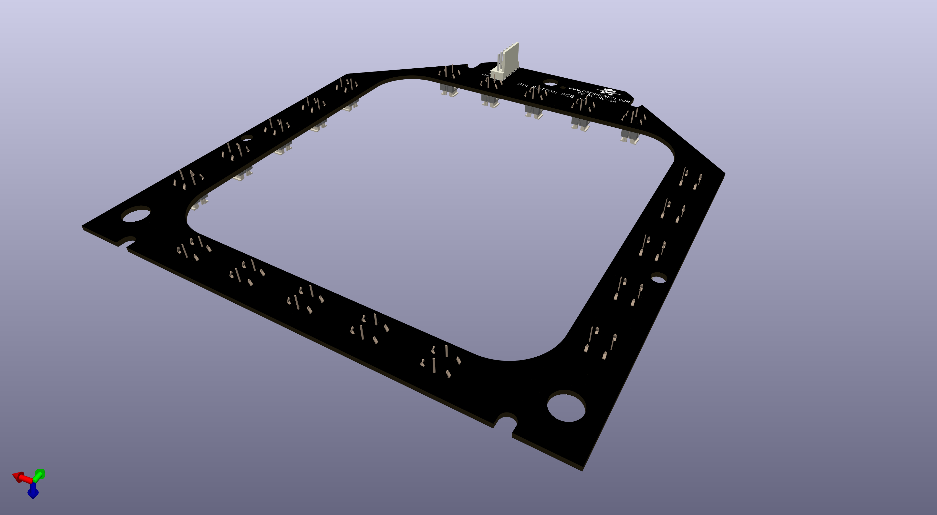
ECAD/PCBs/Functional PCBs/DDI/Assets/DDI-BOT_ISO.png
