jrsteensen/OpenHornet/ECAD/PCBs/Functional PCBs/DDI/Assets/DDI-TOP.png

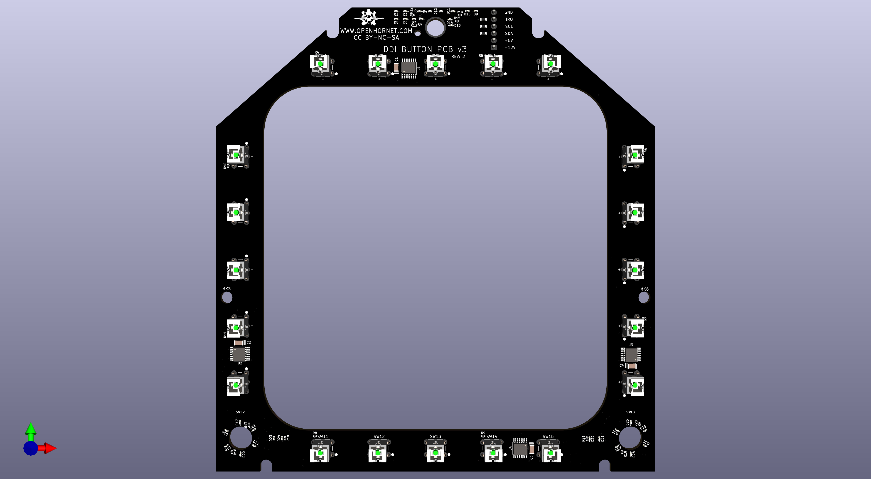
ECAD/PCBs/Functional PCBs/DDI/Assets/DDI-TOP.png
