jrsteensen/OpenHornet/ECAD/PCBs/Functional PCBs/DDI/Assets/DDI-TOP_ISO.png

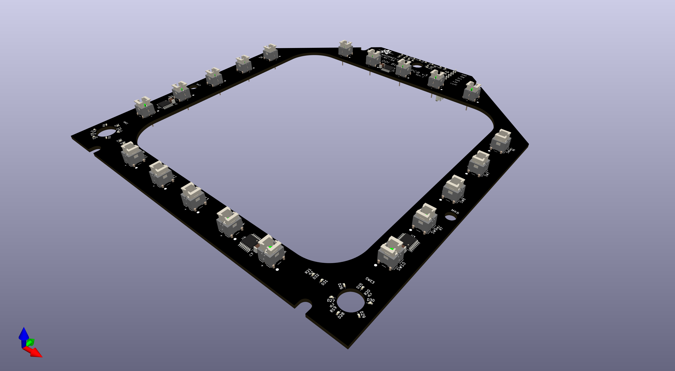
ECAD/PCBs/Functional PCBs/DDI/Assets/DDI-TOP_ISO.png
