jrsteensen/OpenHornet/ECAD/PCBs/Functional PCBs/EYEBROW WARNING INDICATOR_LEFT/Assets/EYEBROW WARNING INDICATOR_LEFT-BOT.png

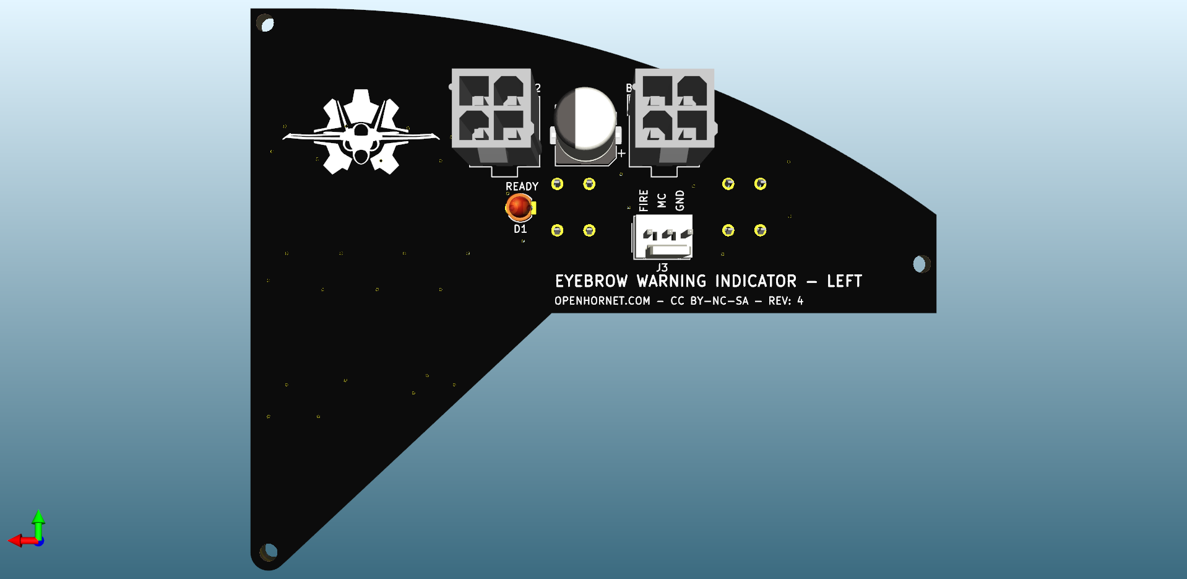
ECAD/PCBs/Functional PCBs/EYEBROW WARNING INDICATOR_LEFT/Assets/EYEBROW WARNING INDICATOR_LEFT-BOT.png
