jrsteensen/OpenHornet/ECAD/PCBs/Functional PCBs/EYEBROW WARNING INDICATOR_RIGHT/Assets/EYEBROW WARNING INDICATOR_RIGHT-BOT.png

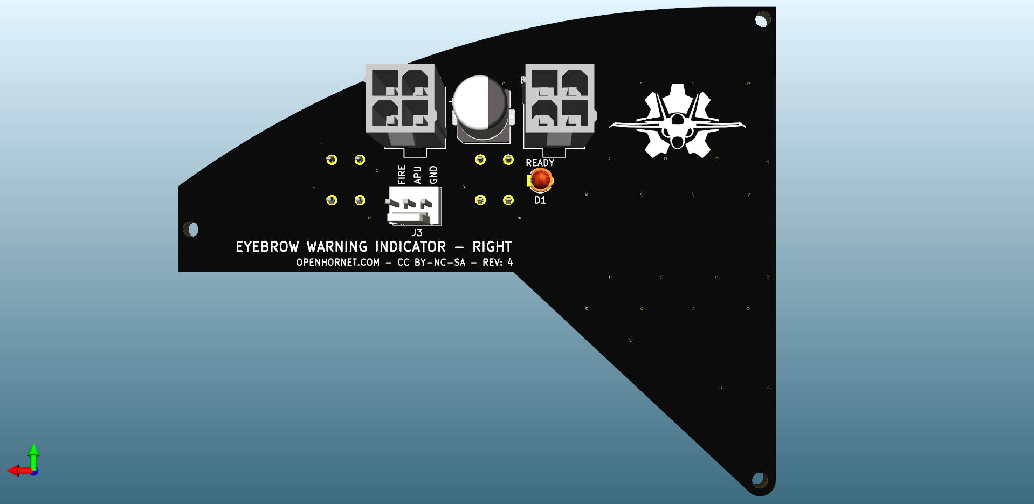
ECAD/PCBs/Functional PCBs/EYEBROW WARNING INDICATOR_RIGHT/Assets/EYEBROW WARNING INDICATOR_RIGHT-BOT.png
