jrsteensen/OpenHornet/ECAD/PCBs/Functional PCBs/GAUGE_Analog Instruments/Assets/GAUGE_Analog Instruments-TOP_ISO.png

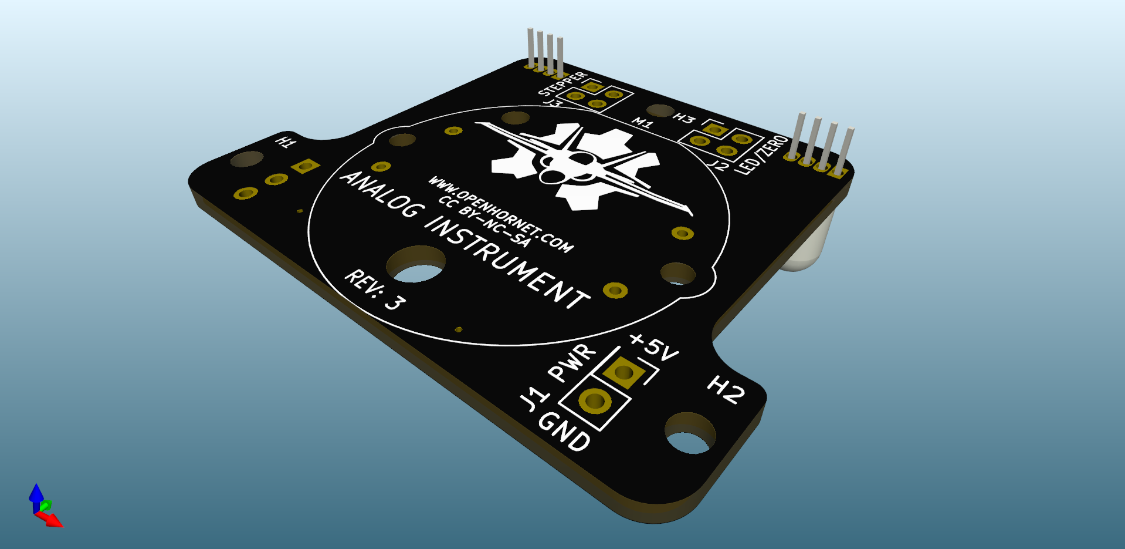
ECAD/PCBs/Functional PCBs/GAUGE_Analog Instruments/Assets/GAUGE_Analog Instruments-TOP_ISO.png
