jrsteensen/OpenHornet/ECAD/PCBs/Functional PCBs/IFEI/Assets/IFEI-BOT.png

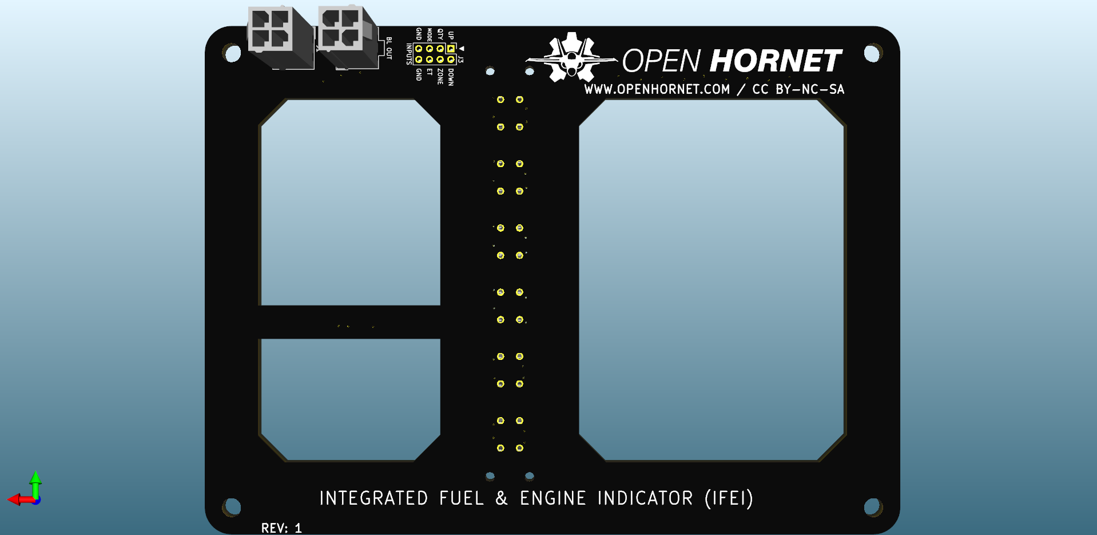
ECAD/PCBs/Functional PCBs/IFEI/Assets/IFEI-BOT.png
