jrsteensen/OpenHornet/ECAD/PCBs/Functional PCBs/IFEI/Assets/IFEI-BOT_ISO.png

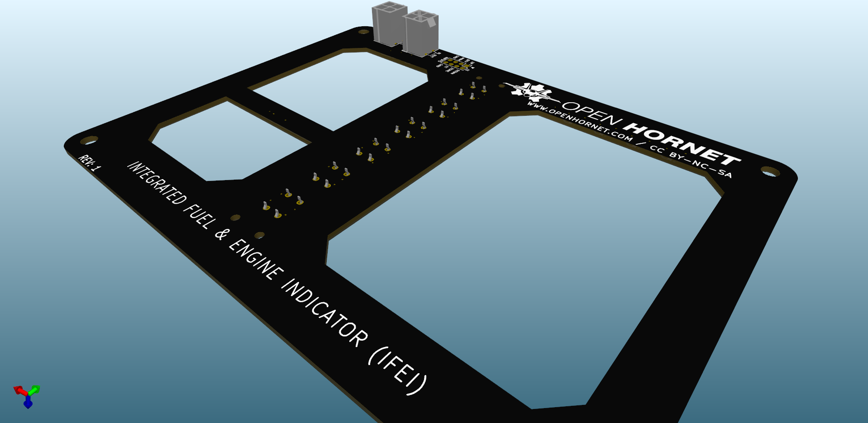
ECAD/PCBs/Functional PCBs/IFEI/Assets/IFEI-BOT_ISO.png
