jrsteensen/OpenHornet/ECAD/PCBs/Functional PCBs/IFEI/Assets/IFEI-TOP.png

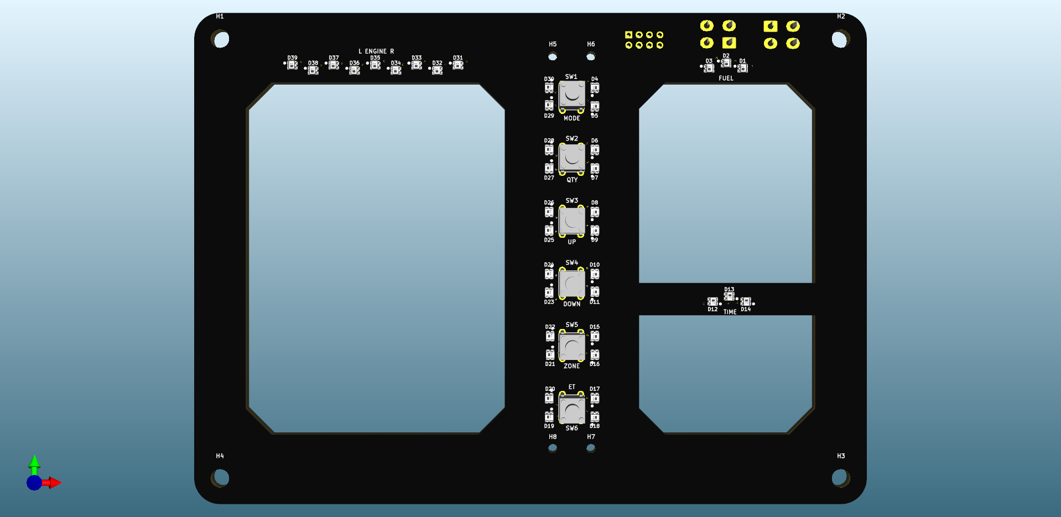
ECAD/PCBs/Functional PCBs/IFEI/Assets/IFEI-TOP.png
