jrsteensen/OpenHornet/ECAD/PCBs/Functional PCBs/IFEI/Assets/IFEI-TOP_ISO.png

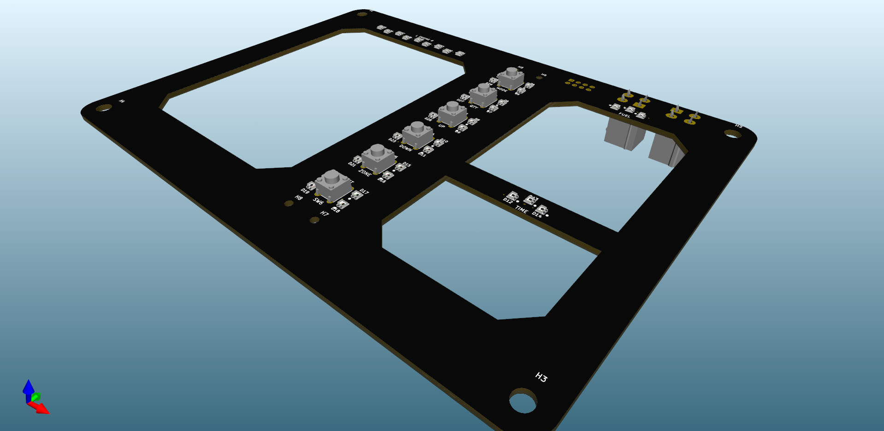
ECAD/PCBs/Functional PCBs/IFEI/Assets/IFEI-TOP_ISO.png
