jrsteensen/OpenHornet/ECAD/PCBs/Functional PCBs/JETT STATION SELECT/Assets/JETT STATION SELECT-BOT_ISO.png

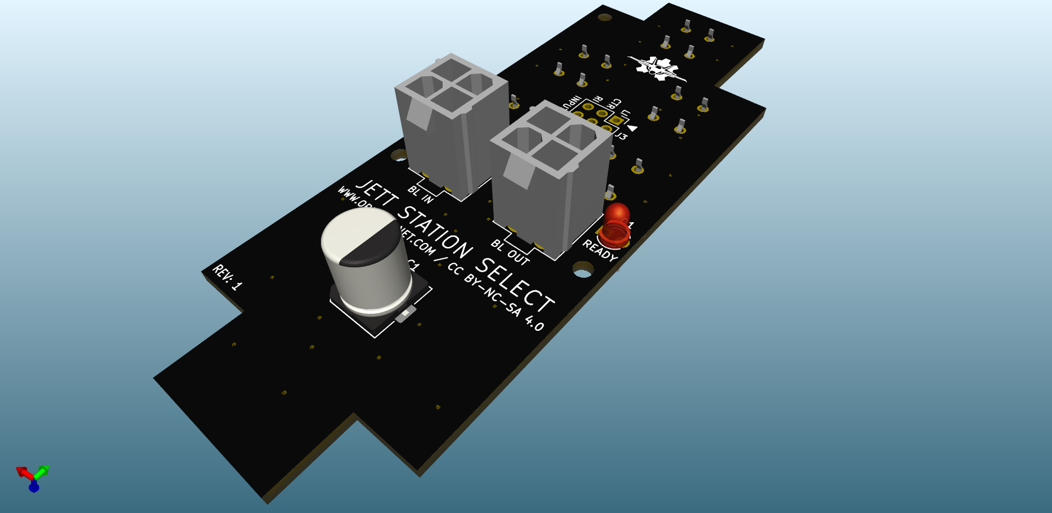
ECAD/PCBs/Functional PCBs/JETT STATION SELECT/Assets/JETT STATION SELECT-BOT_ISO.png
