jrsteensen/OpenHornet/ECAD/PCBs/Functional PCBs/JETT STATION SELECT/Assets/JETT STATION SELECT-TOP_ISO.png

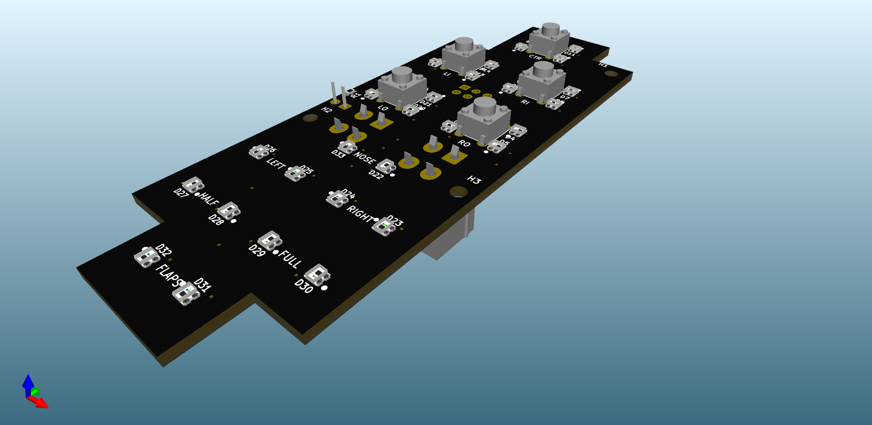
ECAD/PCBs/Functional PCBs/JETT STATION SELECT/Assets/JETT STATION SELECT-TOP_ISO.png
