jrsteensen/OpenHornet/ECAD/PCBs/Functional PCBs/RWR CONTROL PANEL/Assets/RWR CONTROL PANEL-BOT.png

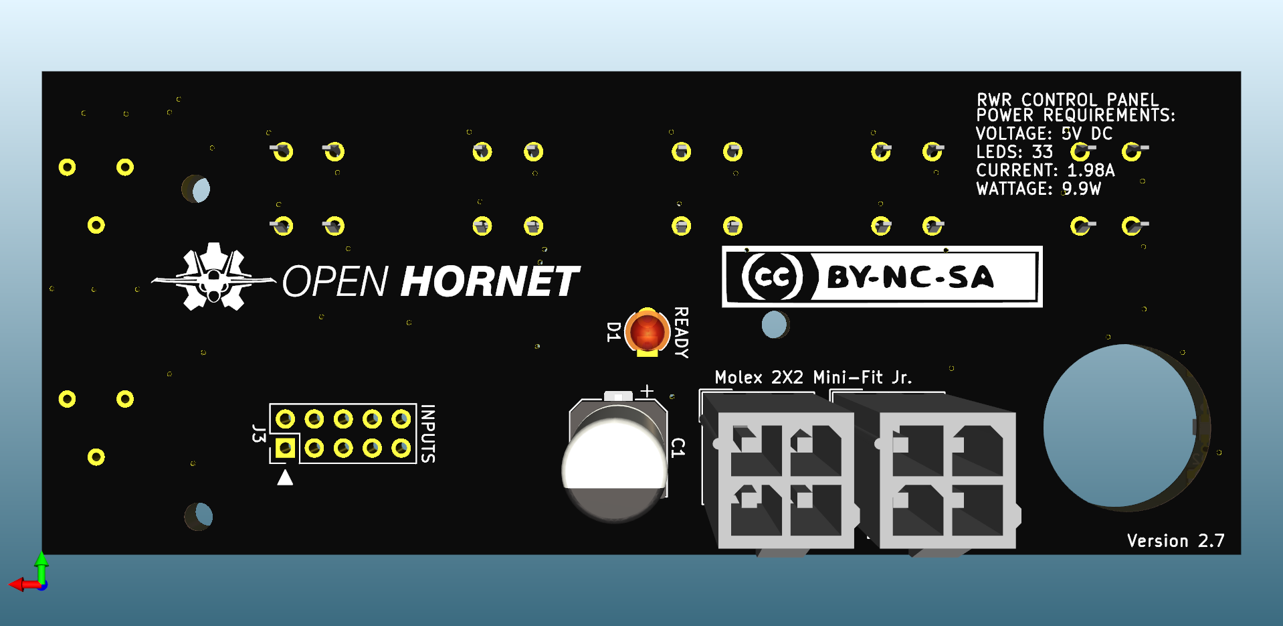
ECAD/PCBs/Functional PCBs/RWR CONTROL PANEL/Assets/RWR CONTROL PANEL-BOT.png
