jrsteensen/OpenHornet/ECAD/PCBs/OH_Specific/Backlighting/Landing_Gear_Panel_PCB_V2/Landing Gear Panel PCB V2-2 Back.png

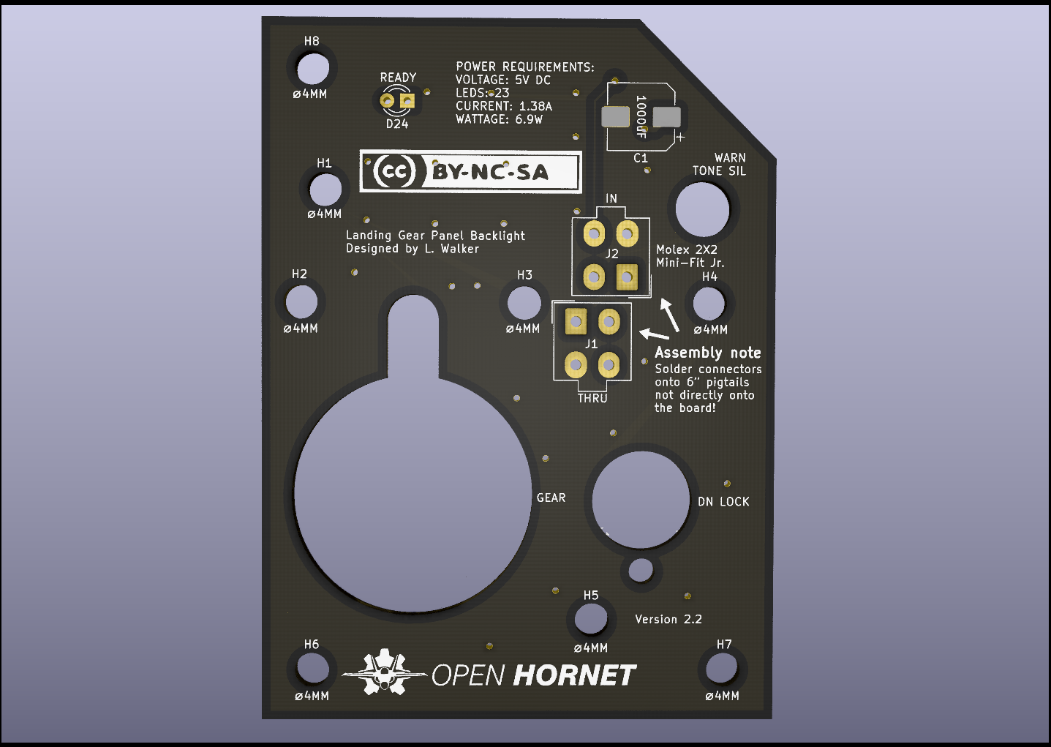
ECAD/PCBs/OH_Specific/Backlighting/Landing_Gear_Panel_PCB_V2/Landing Gear Panel PCB V2-2 Back.png
