jrsteensen/OpenHornet/ECAD/PCBs/OH_Specific/Functional/ewi_v3/ewi_v3 Left Front.png

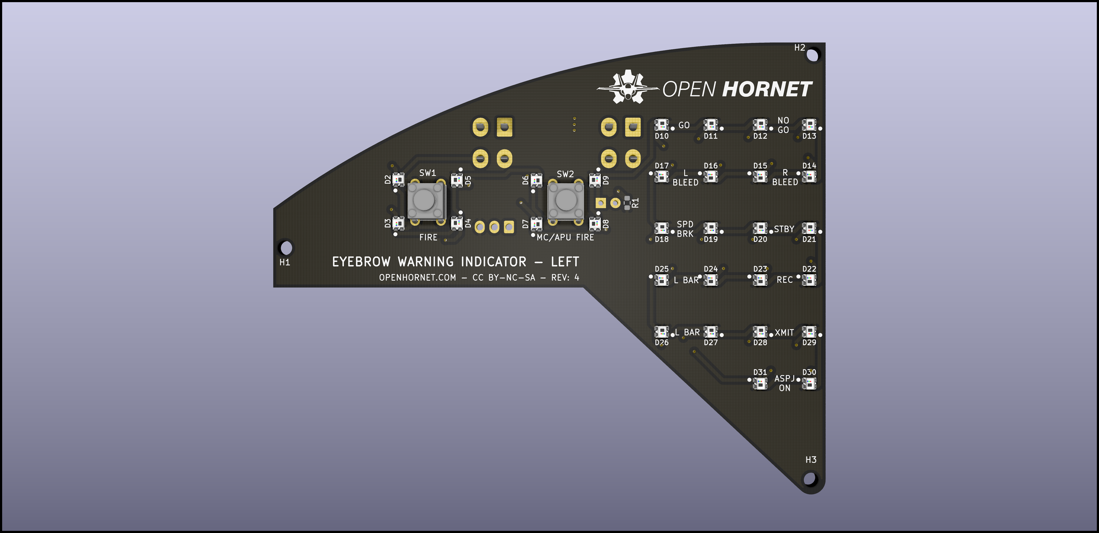
ECAD/PCBs/OH_Specific/Functional/ewi_v3/ewi_v3 Left Front.png
