jrsteensen/OpenHornet/ECAD/PCBs/Specialty/UFC3/ref/69504649-035c4d80-0ee2-11ea-87ad-109d5551093c.png

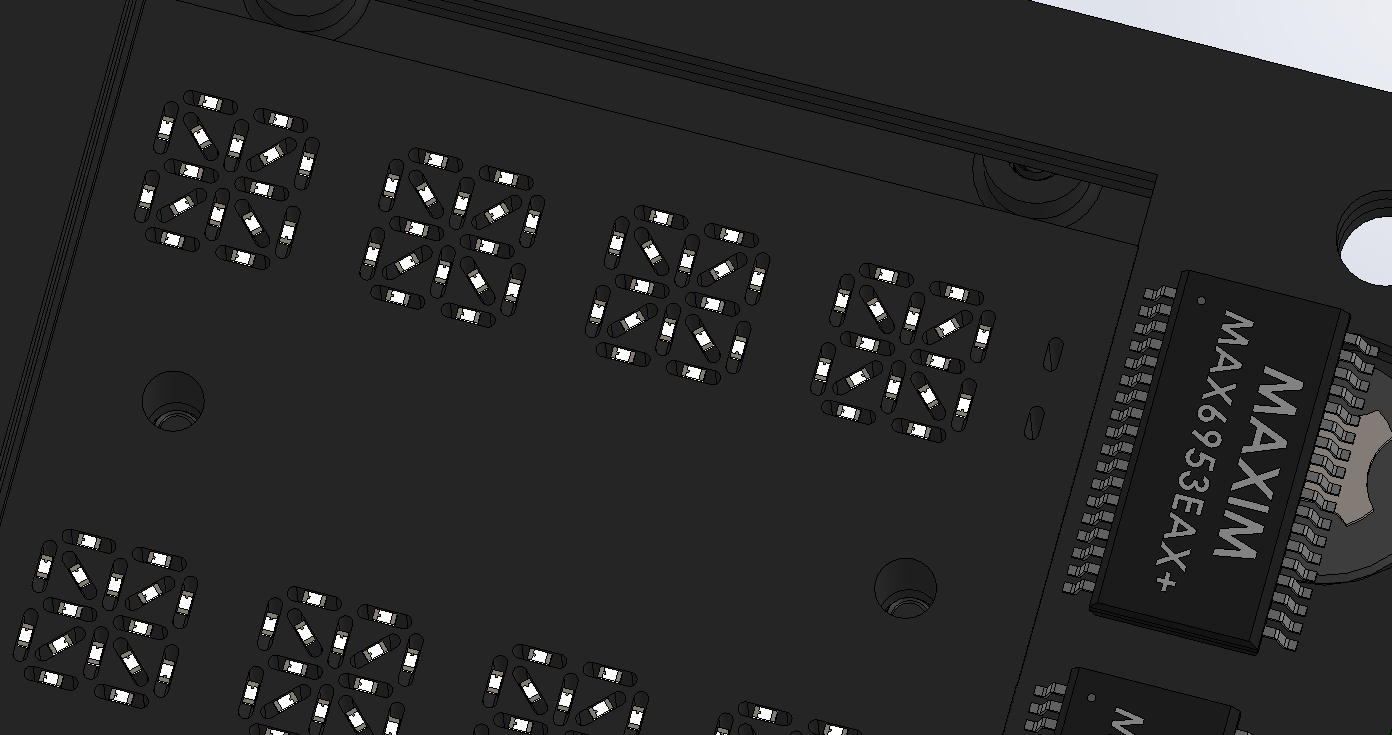
ECAD/PCBs/Specialty/UFC3/ref/69504649-035c4d80-0ee2-11ea-87ad-109d5551093c.png
