jrsteensen/OpenHornet/images/GerberDrillFilesGenerationSettings.png

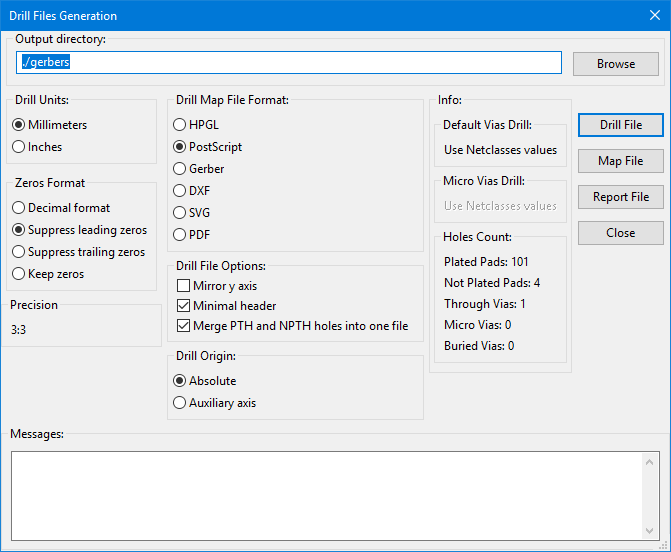
images/GerberDrillFilesGenerationSettings.png
