jrsteensen/OpenHornet/images/GerberPlotDialogSettings.png

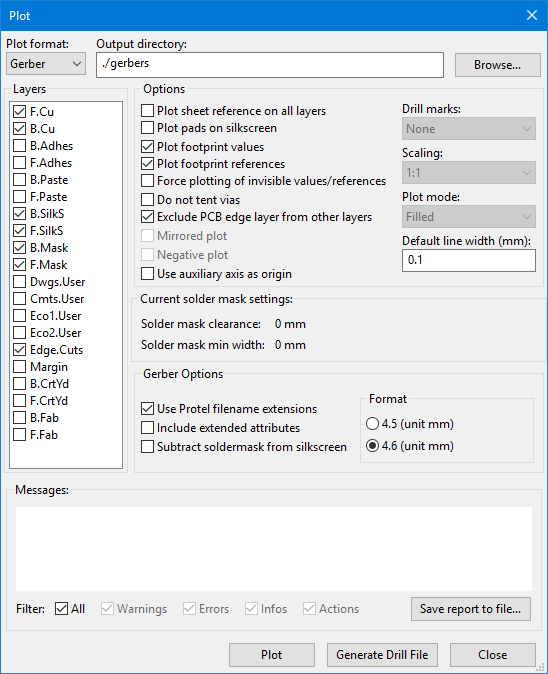
images/GerberPlotDialogSettings.png
