jrsteensen/OpenHornet/images/OHSysArch_SHT1.png

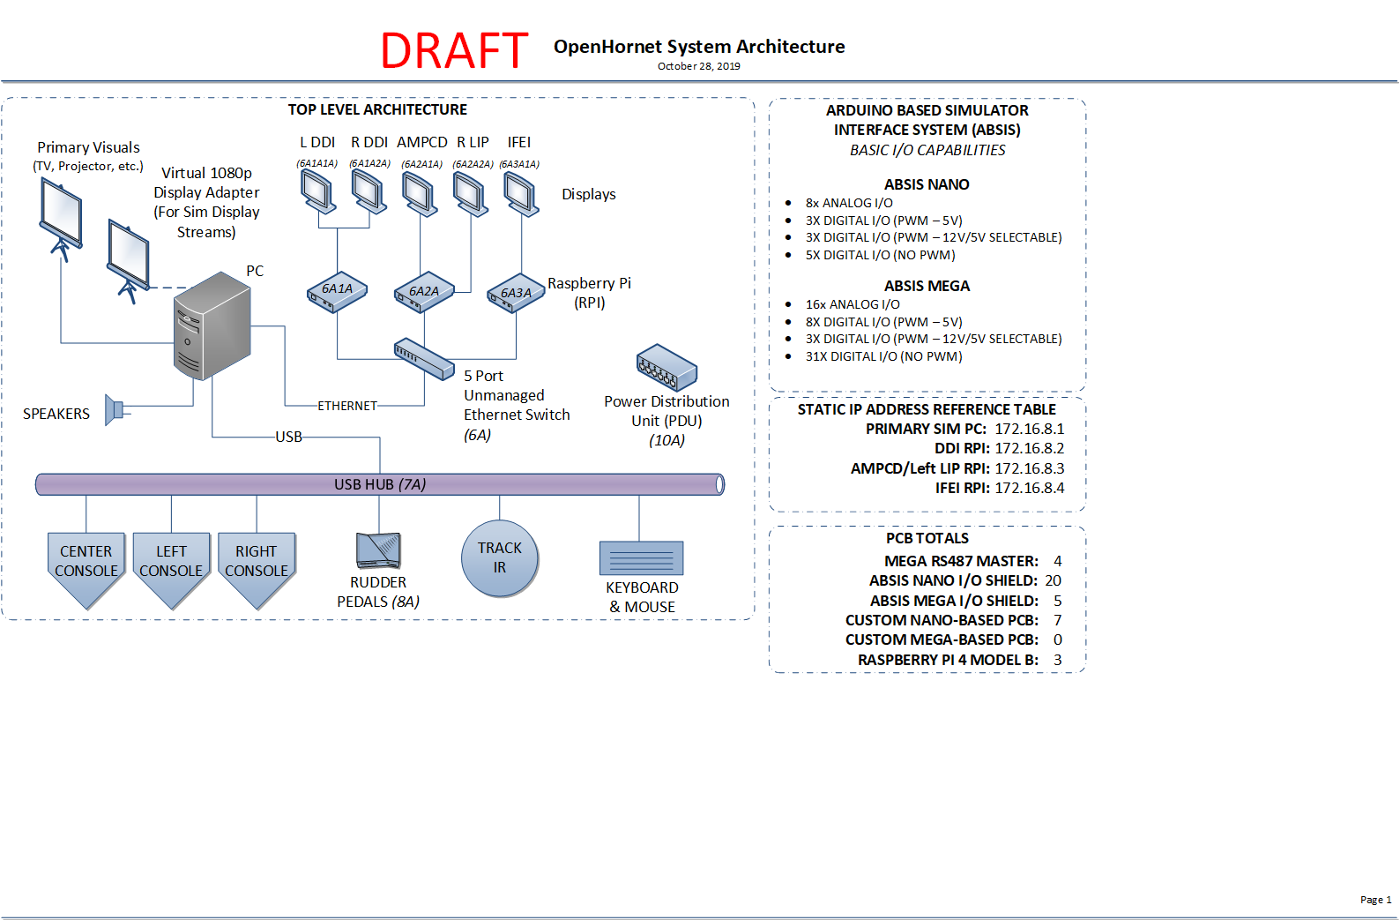
images/OHSysArch_SHT1.png
