jrsteensen/OpenHornet/images/OHSysArch_SHT2.png

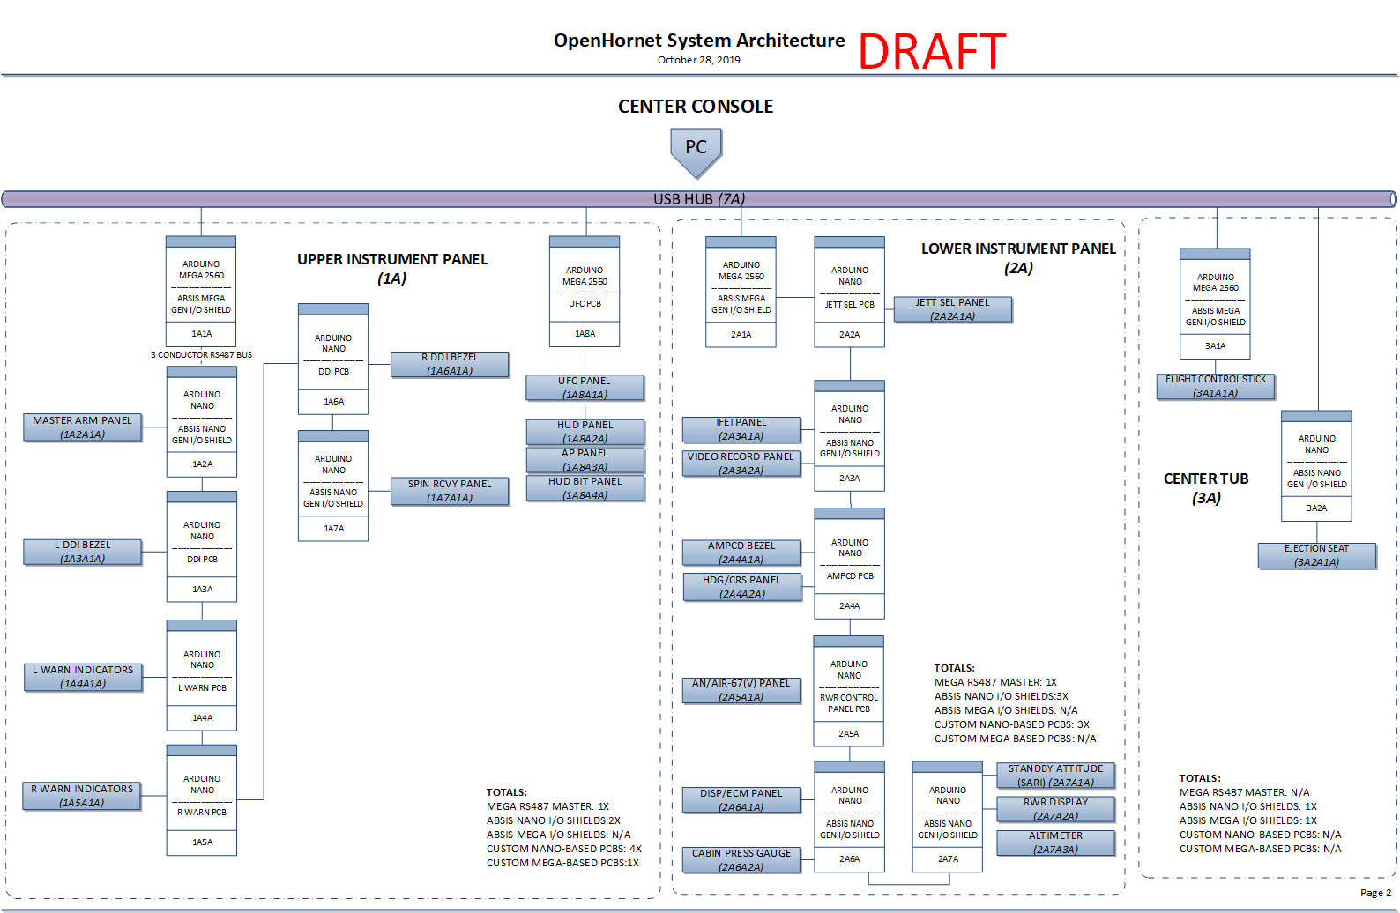
images/OHSysArch_SHT2.png
