jrsteensen/OpenHornet/images/OHSysArch_SHT3.png

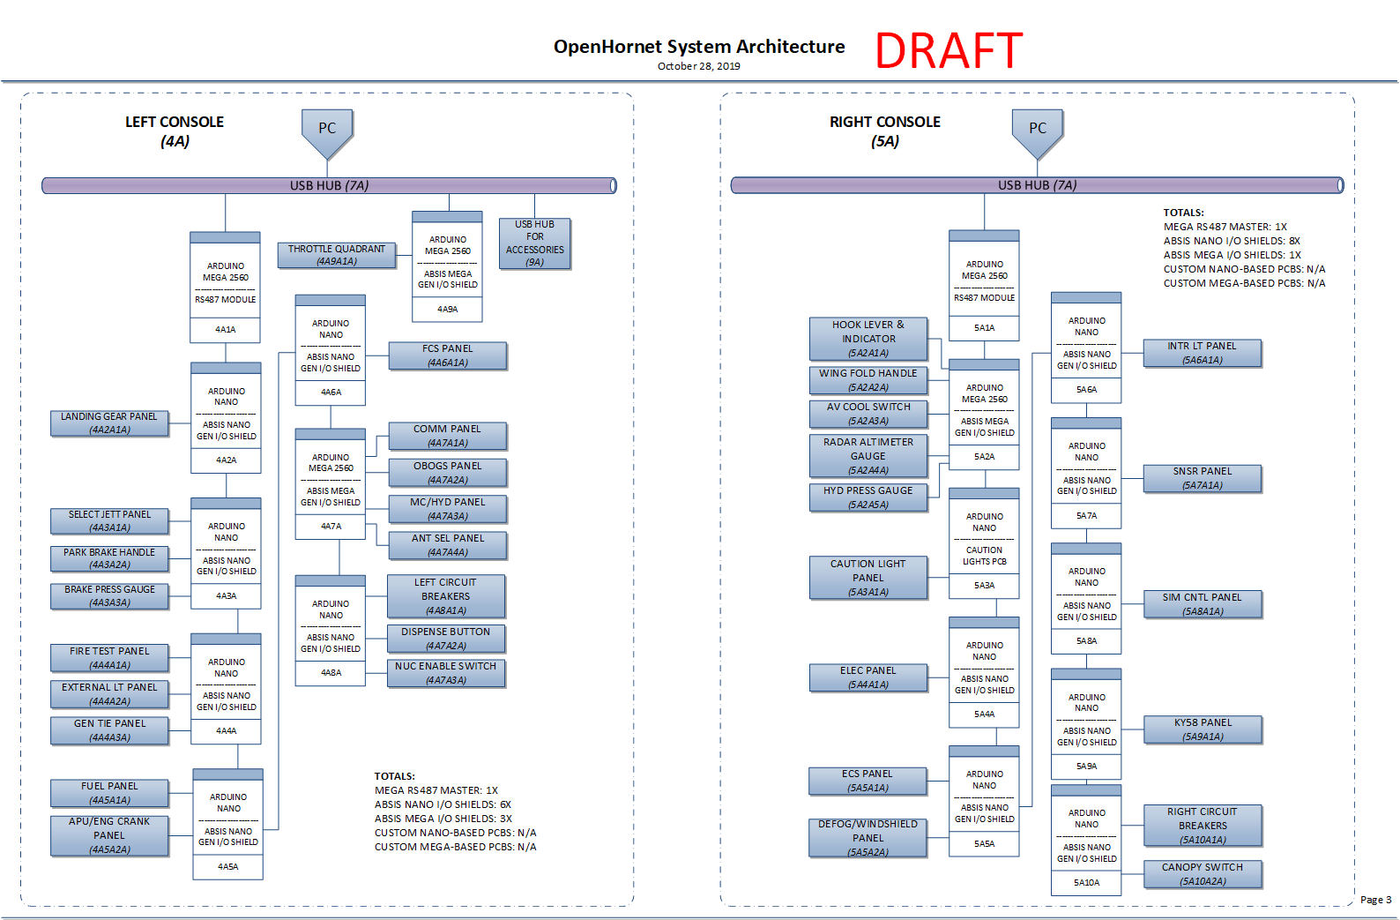
images/OHSysArch_SHT3.png
