jrsteensen/OpenHornet/utils/tools/MetricConversion/no_adaptation.png

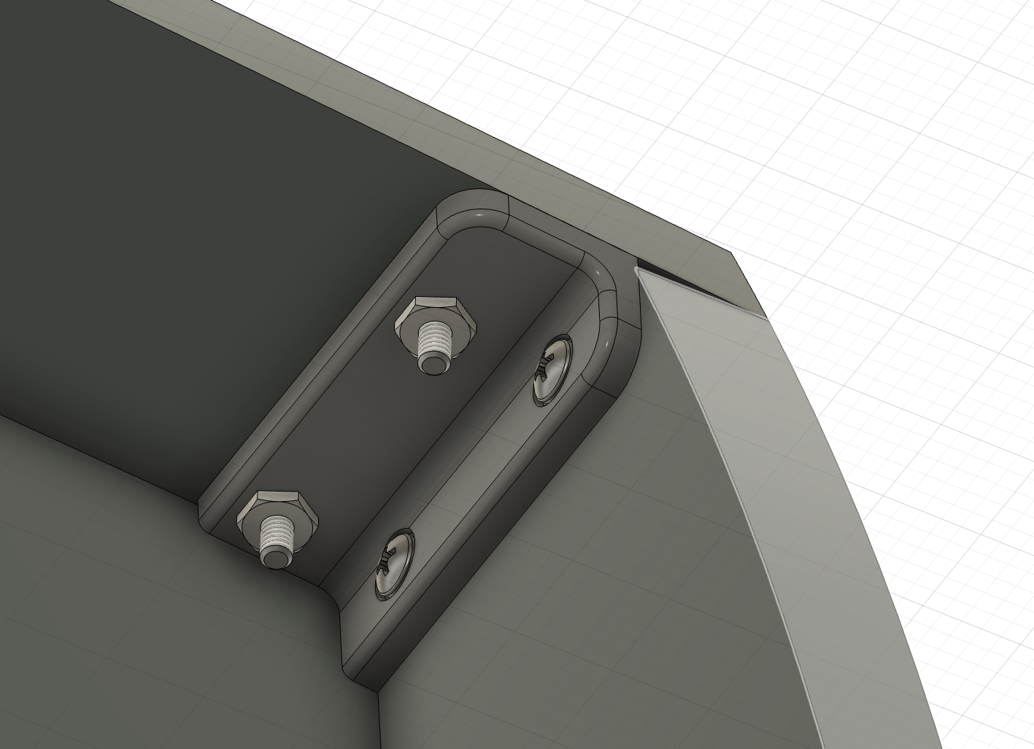
utils/tools/MetricConversion/no_adaptation.png
