jrsteensen/OpenHornet/ECAD/docs/requirements/ARCHITECTURE_INVENTORY.md

# Architecture evidence and findings

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

## Scope and method

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

No PCB, schematic, project, library, manufacturing output or workbook is changed by this PR.

## Pending successor supplement

The [ALE+ supplement](ALE_PLUS_SUPPLEMENT.md) reviews PR #1233 at its pinned head and records owner confirmation on 2026-09-11: ALE+ replaces ALE and the separate relay module; 7.5 V nominal / 7.3 V actual buck output; SS34 D2; planned 8.0.1 formatting/silkscreen revision. The master counts below remain a historical baseline, not a complete description of pending architecture.

## Issue-backed migration intent

[ABSIS_MIGRATION.md](ABSIS_MIGRATION.md) maps issue #1220 and related failure reports to affected boards. The older power/RS-485 circuits listed there are pending intentional migration, not equally preferred design alternatives. Master/Mega implementation has merged; ALE+ is pending; tracker checkboxes and qualification status are separate.

## Evidence map

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

| Evidence | Findings and relevance |
| --- | --- |
| [ECAD/README.md](../../README.md), [ECAD/MANUFACTURING.md](../../MANUFACTURING.md), [ECAD/REVIEW.md](../../REVIEW.md) | KiCad source, JLCPCB output structure and supplier preference, 1.6 mm default thickness, usually two layers/top SMD; board-specific exceptions; preview tooling has dependency limitations. KiCad 7.0.2 setup text is historical, not the intended new KiCad 10 baseline. |
| [PR template](../../../PULL_REQUEST_TEMPLATE.md) | Existing expectation of schematic requirements notes, review, version changes, constrained mechanics, BOM/Gerbers/MCAD and release copies. These support, but do not already implement, the new qualification gates. |
| [Cable specification A v2](../../../release/OH-SPEC_Specifications/OH-SPEC-002%20-%20ABSIS%20CABLES_A_v2.pdf) | Explicit 2025-11-02 revision changes Type A/E data conductors to 24–16 AWG twisted stranded pair; four power/return conductors remain 16 AWG. Exact cable/housing/contact families. Text and rendered sheet reviewed. |
| [Interconnect root](../../interconnects/OH_Interconnect.kicad_sch) and its five child sheets | Assembly/cable references, connector variants and mates, voltage/signal naming, subsystem topology and termination notes. Older generic-wire notes conflict with the later cable specification. |
| [Bus Master/Mega refresh PR #1228](https://github.com/jrsteensen/OpenHornet/pull/1228) | Explicit reliability/ESD rationale for THVD1410 refresh, master four-layer conversion, shield drain and power-path diodes. Current files show implementation differences from prose; see findings below. |
| [Custom Pro Micro PR #1213](https://github.com/jrsteensen/OpenHornet/pull/1213) | Explicitly an initial, unrouted and untested development design. Intended to address RAW/USB power coexistence using a priority mux. |
| [PowerDistribution.xlsx](../PowerDistribution.xlsx), [PDUPowerRequirements.xlsx](../PDUPowerRequirements.xlsx) | Incomplete older load estimates. `Summary` has mostly empty loads; PDU sheet has missing entries and Nano-era names. No complete approved current/drop/thermal budget inferred. |
| [OpenHornet IO Requirements.xlsx](../OpenHornet%20IO%20Requirements.xlsx), [ABSIS 2.0 Part Numbers.xlsx](../ABSIS%202.0%20Part%20Numbers.xlsx) | Useful functional intent; planning-era Nano assignments, proposed functions and old part-number mapping are not current interface authority. |
| [PCB Master BOM](../../PCBs/OpenHornet%20PCB%20Master%20BOM.xlsx), [ABSIS BOM](../../PCBs/ABSIS/ABSIS_BOM.xlsx), [UFC connections](../../PCBs/Functional%20PCBs/UFCconnections.xlsx) | Parts/MPN/supplier and interface evidence; not automatically synchronized with latest source. Master BOM, `MASTER`, `Top Components` and `Bottom Components` sheets retain historical metadata and must be reconciled with the latest source. |
| [Interconnect parts list](../../interconnects/reference/OH-PL-INTERCONNECT_A_v5.xlsx), [metadata quick reference](../../interconnects/reference/Interconnect%20Metadata%20Quick%20Ref.xlsx), [CSV combiner](../../interconnects/utilities/oh-interconnect-csv2bom.py) | Connector/housing/contact metadata and reference/quantity conventions. Combiner groups semicolon input by PN and sums Qty; it does not verify pinouts, missing metadata or mixed descriptions. |
| [Generation guide](../Generating_ECAD_Manufacturing_Files-V0.1.docx), [relative path guide](../relative_kicad_paths.docx), [2021 block diagram](../OpenHornet%20Block%20Diagram.pdf) | Refill/regenerate advice and portable library intent; older software steps and Nano topology require revision-specific interpretation. Block-diagram first page visually reviewed. |

## Architecture and generations

| Area | Recurring implementation | Classification |
| --- | --- | --- |
| Distributed power | ATX breakout supplies +12 V, +5 V, +3.3 V plus standby/control; Mini-Fit Jr. distribution, separate backlight feeds and auxiliary XT60 interfaces | Repeated intentional architecture; allowable rail currents/source combinations remain unresolved |
| ABSIS I/O | ALE and Mega modules with power + A/B on six-pin connectors; incoming/outgoing bus through nodes; local headers connect controls | Repeated interface mapping, not a guarantee that all named modules are compatible |
| Refreshed RS-485 | Master v6.0.0 and Mega v3.0.0: THVD1410DR, CDSOT23-SM712, two 10 Ω line resistors, 0.1 µF bypass, 10 kΩ logic pulls; master 120 Ω terminators | Intentional 2026 refresh. Candidate basis for new work; physical qualification and mixed-generation limits need records |
| ALE+ successor (pending) | Integrated I/O and two output channels; THVD1410/SM712 refresh; buck supply and four-layer PCB | Owner-confirmed replacement for ALE plus relay; see [ALE+ supplement](ALE_PLUS_SUPPLEMENT.md) for source and test-evidence scope |
| Older RS-485 | ALE, HID Master and several instrument controllers use MAX487EESA+T and a local 0.1 µF capacitor | Still present in current directories; not automatically the preferred new design |
| USB | Purchased Pro Micro/Mega modules and hubs; direct USB controllers alongside RS-485; UFC source selection; custom Pro Micro USB-C development | Multiple power generations and board-specific programming restrictions |
| Backlighting | WS2812B, WS2812B-Mini and WS2812B-2020; usually Mini-Fit Jr. DIN/DOUT chain with parallel +5 V/GND pass-through | Repeated architecture, package-specific electrical/optical behavior. Not RS-485 or analog PWM wiring merely because MCU pins are PWM-capable |
| DDI/AMPCD | Local I2C expander/button interface, shared IRQ, dedicated controller and separate lighting functions | Board-specific local bus. Legacy modular DDI text does not supersede current full boards |
| Instruments/HOTAS/UFC | Steppers/servos, optical zero sensors, magnetic SPI sensors, I2C muxes/ADCs/expanders, display controllers and keyboard scanning | Several distinct functional families; their ratings and local-bus rules are not global ABSIS specifications |
| Templates and placeholders | Nano and Mega shield templates, Type B ECS alternative, footprint-empty MPC PCB, partly placed custom Pro Micro | Historical/development candidates; active support and validation unknown |

Older `.sch/.pro` formats and KiCad 6/7-era modern files coexist with later 8/9/10-era formats. File-format recency and title-block dates do not alone establish architectural authority. In particular the refreshed Master PCB retains a 2024 title date while the schematic has a 2026 date. The update history and component topology are stronger evidence of intent.

## Interconnect hierarchy and topology evidence

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

## Connector and pinout conventions

See the exact observed bus maps in [INTERFACES.md](INTERFACES.md). Recurring families include Mini-Fit Jr. 4.20 mm power/bus connectors, 2.54 mm headers/sockets and Harwin M20 harness housings, JST PH local sensor/accessory connectors, JST SM panel-to-panel cable pairs, Molex KK-254 controls and USB/module connectors. XT60, Hirose, DIN and audio/load connectors appear in specific assemblies and are not generic replacements.

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

## Repeated parts, protection and power-integrity evidence

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

## Library, geometry and manufacturing evidence

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

## Findings requiring disposition

| Finding | Evidence | Interpretation / action |
| --- | --- | --- |
| F-01: ALE Relay layer conflict | Schematic note specifies four layers; PCB layer table and released Gerber ZIP have only top/bottom copper | Legacy maintenance/fabrication disposition only; ALE+ successor is four-layer. See Q-01 and [ALE+ supplement](ALE_PLUS_SUPPLEMENT.md) |
| F-02: Mega release instruction conflicts with CAD/CAM | `release/OHE_Electronics/ABSIS002-10 - PCB, ABSIS_MEGA/Important Manufacturing Instructions.txt` says four layers; current Mega PCB and released ZIP have two | Potential misplaced instruction; do not infer intent without owner disposition, Q-01 |
| F-03: Master manufacturing note absent | Refresh PR says note added; current Master production directory and release package have no such note. PCB and checked ZIP have four copper layers | Resolve exact manufacturing profile/document placement, Q-01 |
| F-04: Refresh incomplete across families | Master/Mega and pending ALE+ use THVD1410; master still contains older ALE/HID/selected MAX487 controllers | ALE+ is the intended ALE/relay successor; issue #1220 establishes migration scope for derivative controllers. See ABSIS_MIGRATION.md; tested limits and qualification remain Q-02/Q-09 |
| F-05: RS-485 note error and bias terminology | Master/Mega note gives low threshold as `.8VCC`; TI datasheet section 7.4 states 0.8 V. Logic pull networks differ from PR's external-bias description | Correct notes in a separately scoped hardware/docs follow-up; do not encode wrong threshold or presumed bias, Q-02 |
| F-06: Divergent USB restrictions | ALE/DDI controller module-fuse/jumper instructions, Standby Mega removal, Mega note mentions programming “Pro Micro,” UFC source-selection modes | Module-specific power analysis and corrected instructions needed, Q-04 |
| F-07: Cable text lags released specification | Interconnect Type A/E generic 16 AWG text versus OH-SPEC-002 A twisted pair | Newer explicit cable specification wins; synchronize later, Q-03 |
| F-08: Development design in current tree | Custom Pro Micro only partly placed, no routed tracks; PR explicitly untested. MPC PCB has no footprints | Do not treat as validated references, Q-09 |
| F-09: Case-split companions | `Functional PCBs/IFEI/IFEI.kicad_pro` and schematic versus `ifei/ifei.kicad_pcb`; same pattern for `UTIL_PHOTOSWITCH`/`util_photoswitch` | Exact-path/project pairing must be fixed or explicitly resolved before parity/export, Q-10 |
| F-10: Incomplete/stale requirements and parts metadata | Blank power budgets, Nano-era planning sheets, `1) XXXX` schematic notes, old BOM sensor naming and library paths | Do not derive approved ratings/parts from placeholders, Q-05/Q-09/Q-10 |
| F-11: Inconsistent constraints and exceptions | Varied copper-edge minima, existing exclusions and ignored rules, nonmatching Pro Micro custom-rule filename | No universal numeric fabrication rule or approved exception list inferred, Q-01/Q-10 |

Authoritative external checks: [TI THVD14xx datasheet revision E](https://www.ti.com/lit/gpn/THVD1410) for pin functions/thresholds; [Bourns CDSOT23-SM712 datasheet](https://www.bourns.com/docs/product-datasheets/cdsot23-sm712.pdf) for the protection-device/package reference; [KiCad IPC API](https://dev-docs.kicad.org/en/apis-and-binding/ipc-api/) and [KiCad 10 CLI](https://docs.kicad.org/10.0/en/cli/cli.html) for the proposed workflow. No full per-part qualification is claimed.

## Proposed policy versus discovered standards

Discovered standards worth preserving within scope are the recurring connector pin maps, released twisted-pair cable requirement, separate RS-485/backlight topology, explicit board-specific manufacturing instructions, and the intentional THVD1410 refresh direction. Newly proposed policy comprises semantic editing preference, stable requirement IDs, reproducible validation/evidence, exact part/pad verification, controlled deviations, source/CAM traceability and separate physical/release gates. Numerical budgets, environmental limits and unresolved architecture choices remain in [OPEN_QUESTIONS.md](OPEN_QUESTIONS.md).
