jrsteensen/OpenHornet/ECAD/docs/requirements/BOARD_INVENTORY.md

# Board and project inventory

**Informative baseline evidence, not requirements or validation results.** Snapshot: `c259a65a1759801a2affea817fd99f6a14f1e1fe`.

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

## Pending successor outside the master snapshot

**B69: ABSIS_ALE+** is an additional branch-specific PCB/project candidate in PR #1233, not part of the 68-file master count. See the [ALE+ supplement](ALE_PLUS_SUPPLEMENT.md) for pinned schematic/PCB/project paths, observed four-layer construction, parts and confirmed 7.5 V nominal / 7.3 V actual supply, SS34 selection and planned 8.0.1 revision. Its intended function replaces B01 and B02. Reported v8 prototype testing and the pending cosmetic revision are tracked separately from release qualification.

See [ABSIS_MIGRATION.md](ABSIS_MIGRATION.md) for the issue-backed power/RS-485 update scope and implementation status of affected boards. The baseline entries below retain historical observations; they do not override that migration direction.

## PCB sources

### B01: ABSIS_ALE

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

- Function: General Pro Micro I/O node with RS-485 in/out.
- Sources: [PCB](../../PCBs/ABSIS/ABSIS_ALE/ABSIS_ALE.kicad_pcb); [schematic](../../PCBs/ABSIS/ABSIS_ALE/ABSIS_ALE.kicad_sch); [project](../../PCBs/ABSIS/ABSIS_ALE/ABSIS_ALE.kicad_pro).
- Observed PCB revision: `3`; copper layers: F.Cu, B.Cu; thickness: 1.6; 17 embedded footprints.
- Repeated/functional parts: Mini-Fit Jr. 2x03 ×2; PinHeader_2x06 ×2; 0.1uF ×1; MAX487EESA+T ×1; ProMicro_5V/16Hz ×1; RST ×1; 1N5819WS ×1; PinHeader_1x06 ×1; PinHeader_2x02 ×1.
- Connector footprint families: Molex_Mini-Fit_Jr_5566-06A2_2x03_P4.20mm_Vertical ×2; PinHeader_2x06_P2.54mm_Vertical ×2; PinHeader_1x06_P2.54mm_Vertical ×1; PinHeader_2x02_P2.54mm_Vertical ×1.
- Selected rails: +5V, /+12V_SUPPLY, /+3.3V_SUPPLY, /+5V_SUPPLY, GND.
- Net classes (clearance/track/via diameter/drill): Default: 0.2/0.25/0.6/0.4.
- Project minima: min_clearance=0; min_track_width=0.2; min_copper_edge_clearance=0.05; min_through_hole_diameter=0.3; DRC exclusion records: 0.
- Actual routed widths: 0.3048, 0.4572, 0.635, 0.9144, 1.6256; via diameter/drill forms: 0.6/0.4.
- Mechanical footprint evidence: MountingHole_3.2mm_M3_DIN965 ×4.

### B02: ABSIS_ALE Relay Module

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

- Function: ALE accessory with two selectable-voltage MOSFET output channels.
- Sources: [PCB](../../PCBs/ABSIS/ABSIS_ALE%20Relay%20Module/ABSIS_ALE%20Relay%20Module.kicad_pcb); [schematic](../../PCBs/ABSIS/ABSIS_ALE%20Relay%20Module/ABSIS_ALE%20Relay%20Module.kicad_sch); [project](../../PCBs/ABSIS/ABSIS_ALE%20Relay%20Module/ABSIS_ALE%20Relay%20Module.kicad_pro).
- Observed PCB revision: `2`; copper layers: F.Cu, B.Cu; thickness: 1.6; 24 embedded footprints.
- Repeated/functional parts: 10k ×6; PinHeader_1x03 ×4; IRLML6402TRPBF ×2; JST_PH_01x02 ×2; IRFB3206PBF ×2; PinSocket_Long_1x06 ×1; PinSocket_Long_2x16 ×1.
- Connector footprint families: PinSocket_1x06_P2.54mm_Vertical ×1; PinSocket_2x16_P2.54mm_Vertical ×1; JST_PH_B2B-PH-K_1x02_P2.00mm_Vertical ×2; PinHeader_1x03_P2.54mm_Vertical ×4.
- Selected rails: /+12V_SUPPLY, /+3.3V_SUPPLY, /+5V_SUPPLY, GND.
- Net classes (clearance/track/via diameter/drill): Default: 0.2/0.25/0.6/0.4.
- Project minima: min_clearance=0; min_track_width=0.2; min_copper_edge_clearance=0.05; min_through_hole_diameter=0.3; DRC exclusion records: 1.
- Actual routed widths: 0.3048, 0.9144, 1.6256; via diameter/drill forms: 1.5/0.8; 0.6/0.4.
- Mechanical footprint evidence: MountingHole_3.2mm_M3_DIN965 ×4.

### B03: ABSIS_ATX Power Supply Unit

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

### B04: ABSIS_Backlight Controller

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

### B05: ABSIS_Bus_Master

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

### B06: ABSIS_Bus_Master (legacy)

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

### B07: ABSIS_HID Bus Master

- Function: Pro Micro USB/HID to one terminated RS-485 channel.
- Sources: [PCB](../../PCBs/ABSIS/ABSIS_HID%20Bus%20Master/ABSIS_HID%20Bus%20Master.kicad_pcb); [schematic](../../PCBs/ABSIS/ABSIS_HID%20Bus%20Master/ABSIS_HID%20Bus%20Master.kicad_sch); [project](../../PCBs/ABSIS/ABSIS_HID%20Bus%20Master/ABSIS_HID%20Bus%20Master.kicad_pro).
- Observed PCB revision: `4`; copper layers: F.Cu, B.Cu; thickness: 1.6; 20 embedded footprints.
- Repeated/functional parts: TestPoint ×6; MAX487EESA+T ×1; 120 ×1; 0.1uF ×1; Molex_Mini-Fit_Jr._2x04 ×1; Mini-Fit Jr. 2x03 ×1; ProMicro_5V/16Hz ×1; 1N5819WS ×1.
- Connector footprint families: Molex_Mini-Fit_Jr_5566-08A2_2x04_P4.20mm_Vertical ×1; Molex_Mini-Fit_Jr_5566-06A2_2x03_P4.20mm_Vertical ×1.
- Selected rails: +5V, /+12V_SUPPLY, /+3.3V_SUPPLY, /+5V_SUPPLY, GND.
- Net classes (clearance/track/via diameter/drill): Default: 0.2/0.25/0.6/0.4.
- Project minima: min_clearance=0; min_track_width=0.2; min_copper_edge_clearance=0.075; min_through_hole_diameter=0.3; DRC exclusion records: 0.
- Actual routed widths: 0.4572, 0.635, 0.9144, 1.2192, 1.6256; via diameter/drill forms: 0.6/0.4.
- Mechanical footprint evidence: MountingHole_3.2mm_M3_DIN965 ×4.

### B08: ABSIS_Hall Sensor

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

### B09: ABSIS_MPC

- Function: Incomplete project; intended function not established from empty PCB.
- Sources: [PCB](../../PCBs/ABSIS/ABSIS_MPC/ABSIS_MPC.kicad_pcb); [schematic](../../PCBs/ABSIS/ABSIS_MPC/ABSIS_MPC.kicad_sch); [project](../../PCBs/ABSIS/ABSIS_MPC/ABSIS_MPC.kicad_pro).
- Observed PCB revision: `not stated`; copper layers: F.Cu, B.Cu; thickness: 1.6; 0 embedded footprints.
- Repeated/functional parts: .
- Connector footprint families: none placed.
- Selected rails: none resolved from placed pads.
- Net classes (clearance/track/via diameter/drill): Default: 0.2/0.305/0.6/0.4; +5V: 0.2/0.457/0.6/0.4.
- Project minima: min_clearance=0.127; min_track_width=0.127; min_copper_edge_clearance=0.75; min_through_hole_diameter=0.3; DRC exclusion records: 0.
- Actual routed widths: none; via diameter/drill forms: none.
- Mechanical footprint evidence: inspect outline and assembly; no named mounting/keepout footprint.

### B10: ABSIS_Mega

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

### B11: ABSIS_Mega (legacy)

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

### B12: ABSIS_Pit Management System

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

### B13: ABSIS_Pro_Micro

- Function: Development ATmega32U4 replacement module with USB-C and RAW-priority power mux.
- Sources: [PCB](../../PCBs/ABSIS/ABSIS_Pro%20Micro/ABSIS_Pro_Micro.kicad_pcb); [schematic](../../PCBs/ABSIS/ABSIS_Pro%20Micro/ABSIS_Pro_Micro.kicad_sch); [project](../../PCBs/ABSIS/ABSIS_Pro%20Micro/ABSIS_Pro_Micro.kicad_pro).
- Observed PCB revision: `not stated`; copper layers: F.Cu, In1.Cu, In2.Cu, B.Cu; thickness: 1.6; 7 embedded footprints.
- Repeated/functional parts: FIDUCIALUFIDUCIAL ×2; M12PTH ×2; 2171790001 ×1; ~ ×1.
- Connector footprint families: PinHeader_1x06_P2.00mm_Vertical ×1; PinHeader_1x12_P2.54mm_Vertical ×2.
- Selected rails: +5V, /RAW, /vBUS, GND.
- Net classes (clearance/track/via diameter/drill): Default: 0.1778/0.25/0.8/0.4; +5v: 0.1778/0.25/0.8/0.4; 12V: 0.1778/0.25/0.8/0.4; AREF_4096: 0.1778/0.25/0.8/0.4; Diff: 0.1778/0.25/0.8/0.4; GND: 0.1778/0.25/0.8/0.4; vBUS: 0.1778/0.25/0.8/0.4; vIN1: 0.1778/0.25/0.8/0.4; vIN2: 0.1778/0.25/0.8/0.4.
- Project minima: min_clearance=0; min_track_width=0.2; min_copper_edge_clearance=0.1016; min_through_hole_diameter=0.254; DRC exclusion records: 0.
- Actual routed widths: none; via diameter/drill forms: none.
- Mechanical footprint evidence: inspect outline and assembly; no named mounting/keepout footprint.

### B14: ANT SEL PANEL

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

### B15: APU ENG CRANK PANEL

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

### B16: AV COOL PANEL

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

### B17: CAUTION LIGHTS PANEL

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

### B18: COMM PANEL

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

### B19: DEFOG PANEL

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

### B20: ECM DISP PANEL

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

### B21: ECS PANEL

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

### B22: ELEC PANEL

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

### B23: EXT LT PANEL

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

### B24: FCS PANEL

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

### B25: FIRE TEST PANEL

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

### B26: FUEL PANEL

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

### B27: GEN TIE PANEL

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

### B28: HUD PANEL

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

### B29: HUD VID RCD PANEL

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

### B30: HYD ISO PANEL

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

### B31: INTR LT PANEL

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

### B32: JETT STATION SELECT PLACARD

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

### B33: KY-58 PANEL

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

### B34: LANDING GEAR PANEL

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

### B35: LDG WING FOLD PLACARD

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

### B36: LEFT CIRCUIT BREAKER

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

### B37: MASTER ARM PANEL

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

### B38: OBOGS PANEL

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

### B39: SELECT JETT PANEL

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

### B40: SIM CONTROL PANEL

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

### B41: SIM PWR PCB V2 (legacy)

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

### B42: SIM POWER PANEL

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

### B43: SNSR PANEL

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

### B44: SPIN RCV PANEL

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

### B45: ECS PANEL

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

### B46: AMPCD

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

### B47: CONTROLLER_AMPCD DDI

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

### B48: CONTROLLER_Radar Altimeter

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

### B49: CONTROLLER_Standby Instrument

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

### B50: CONTROLLER_Stick

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

### B51: CONTROLLER_Throttle

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

### B52: DDI

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

### B53: EYEBROW WARNING INDICATOR_LEFT

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

### B54: EYEBROW WARNING INDICATOR_RIGHT

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

### B55: GAUGE_Analog Instruments

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

### B56: GAUGE_Dual Needle Instruments

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

### B57: GAUGE_Standby Altimeter

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

### B58: HOTAS_Analog Stick Breakout

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

### B59: HOTAS_Hat Switch Breakout

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

### B60: HOTAS_Throttle Inner Grip

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

### B61: JETT STATION SELECT

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

### B62: RWR CONTROL PANEL

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

### B63: UFC_Function Select

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

### B64: UFC_Main

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

### B65: ifei

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

### B66: util_photoswitch

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

### B67: ABSIS_Nano_2.0_Template (template)

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

### B68: Mega_shield_template (template)

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

## Modern projects without a corresponding PCB path

- [ewi_v3.kicad_pro](../../PCBs/Functional%20PCBs/EYEBROW%20WARNING%20INDICATOR_RIGHT/Legacy/ewi_v3.kicad_pro).
- [OH_Interconnect.kicad_pro](../../interconnects/OH_Interconnect.kicad_pro).

## Complete modern schematic index

This includes the six-sheet interconnect hierarchy, current board schematics and the two modern legacy snapshots.

| Schematic | Revision | Direct symbol instances / child sheets |
| --- | --- | --- |
| [PCBs/ABSIS/ABSIS_ALE/ABSIS_ALE.kicad_sch](../../PCBs/ABSIS/ABSIS_ALE/ABSIS_ALE.kicad_sch) | 3 | 40 / 0 |
| [PCBs/ABSIS/ABSIS_ALE Relay Module/ABSIS_ALE Relay Module.kicad_sch](../../PCBs/ABSIS/ABSIS_ALE%20Relay%20Module/ABSIS_ALE%20Relay%20Module.kicad_sch) | 2 | 38 / 0 |
| [PCBs/ABSIS/ABSIS_ATX Power Supply Unit/ABSIS_ATX Power Supply Unit.kicad_sch](../../PCBs/ABSIS/ABSIS_ATX%20Power%20Supply%20Unit/ABSIS_ATX%20Power%20Supply%20Unit.kicad_sch) | 6 | 86 / 0 |
| [PCBs/ABSIS/ABSIS_Backlight Controller/ABSIS_Backlight Controller.kicad_sch](../../PCBs/ABSIS/ABSIS_Backlight%20Controller/ABSIS_Backlight%20Controller.kicad_sch) | 7 | 82 / 0 |
| [PCBs/ABSIS/ABSIS_Bus_Master/ABSIS_Bus_Master.kicad_sch](../../PCBs/ABSIS/ABSIS_Bus_Master/ABSIS_Bus_Master.kicad_sch) | 6.0.0 | 96 / 0 |
| [PCBs/ABSIS/ABSIS_Bus_Master/legacy/ABSIS_Bus_Master.kicad_sch](../../PCBs/ABSIS/ABSIS_Bus_Master/legacy/ABSIS_Bus_Master.kicad_sch) | 5.0.0 | 72 / 0 |
| [PCBs/ABSIS/ABSIS_HID Bus Master/ABSIS_HID Bus Master.kicad_sch](../../PCBs/ABSIS/ABSIS_HID%20Bus%20Master/ABSIS_HID%20Bus%20Master.kicad_sch) | 4 | 38 / 0 |
| [PCBs/ABSIS/ABSIS_Hall Sensor/ABSIS_Hall Sensor.kicad_sch](../../PCBs/ABSIS/ABSIS_Hall%20Sensor/ABSIS_Hall%20Sensor.kicad_sch) | 4 | 18 / 0 |
| [PCBs/ABSIS/ABSIS_MPC/ABSIS_MPC.kicad_sch](../../PCBs/ABSIS/ABSIS_MPC/ABSIS_MPC.kicad_sch) | 1 | 321 / 0 |
| [PCBs/ABSIS/ABSIS_Mega/ABSIS_Mega.kicad_sch](../../PCBs/ABSIS/ABSIS_Mega/ABSIS_Mega.kicad_sch) | 3.0.0 | 68 / 0 |
| [PCBs/ABSIS/ABSIS_Mega/legacy/ABSIS_Mega.kicad_sch](../../PCBs/ABSIS/ABSIS_Mega/legacy/ABSIS_Mega.kicad_sch) | 2 | 59 / 0 |
| [PCBs/ABSIS/ABSIS_Pit Management System/ABSIS_Pit Management System.kicad_sch](../../PCBs/ABSIS/ABSIS_Pit%20Management%20System/ABSIS_Pit%20Management%20System.kicad_sch) | 1 | 32 / 0 |
| [PCBs/ABSIS/ABSIS_Pro Micro/ABSIS_Pro_Micro.kicad_sch](../../PCBs/ABSIS/ABSIS_Pro%20Micro/ABSIS_Pro_Micro.kicad_sch) | not stated | 68 / 0 |
| [PCBs/Backlight PCBs/Backlighting_Type A/ANT SEL PANEL/ANT SEL PANEL.kicad_sch](../../PCBs/Backlight%20PCBs/Backlighting_Type%20A/ANT%20SEL%20PANEL/ANT%20SEL%20PANEL.kicad_sch) | 4 | 61 / 0 |
| [PCBs/Backlight PCBs/Backlighting_Type A/APU ENG CRANK PANEL/APU ENG CRANK PANEL.kicad_sch](../../PCBs/Backlight%20PCBs/Backlighting_Type%20A/APU%20ENG%20CRANK%20PANEL/APU%20ENG%20CRANK%20PANEL.kicad_sch) | 4 | 68 / 0 |
| [PCBs/Backlight PCBs/Backlighting_Type A/AV COOL PANEL/AV COOL PANEL.kicad_sch](../../PCBs/Backlight%20PCBs/Backlighting_Type%20A/AV%20COOL%20PANEL/AV%20COOL%20PANEL.kicad_sch) | 4 | 45 / 0 |
| [PCBs/Backlight PCBs/Backlighting_Type A/CAUTION LIGHTS PANEL/CAUTION LIGHTS PANEL.kicad_sch](../../PCBs/Backlight%20PCBs/Backlighting_Type%20A/CAUTION%20LIGHTS%20PANEL/CAUTION%20LIGHTS%20PANEL.kicad_sch) | 4 | 85 / 0 |
| [PCBs/Backlight PCBs/Backlighting_Type A/COMM PANEL/COMM PANEL.kicad_sch](../../PCBs/Backlight%20PCBs/Backlighting_Type%20A/COMM%20PANEL/COMM%20PANEL.kicad_sch) | 4 | 287 / 0 |
| [PCBs/Backlight PCBs/Backlighting_Type A/DEFOG PANEL/DEFOG PANEL.kicad_sch](../../PCBs/Backlight%20PCBs/Backlighting_Type%20A/DEFOG%20PANEL/DEFOG%20PANEL.kicad_sch) | 4 | 58 / 0 |
| [PCBs/Backlight PCBs/Backlighting_Type A/ECM DISP PANEL/ECM DISP PANEL.kicad_sch](../../PCBs/Backlight%20PCBs/Backlighting_Type%20A/ECM%20DISP%20PANEL/ECM%20DISP%20PANEL.kicad_sch) | 4 | 131 / 0 |
| [PCBs/Backlight PCBs/Backlighting_Type A/ECS PANEL/ECS PANEL.kicad_sch](../../PCBs/Backlight%20PCBs/Backlighting_Type%20A/ECS%20PANEL/ECS%20PANEL.kicad_sch) | 4 | 184 / 0 |
| [PCBs/Backlight PCBs/Backlighting_Type A/ELEC PANEL/ELEC PANEL.kicad_sch](../../PCBs/Backlight%20PCBs/Backlighting_Type%20A/ELEC%20PANEL/ELEC%20PANEL.kicad_sch) | 4 | 86 / 0 |
| [PCBs/Backlight PCBs/Backlighting_Type A/EXT LT PANEL/EXT LT PANEL.kicad_sch](../../PCBs/Backlight%20PCBs/Backlighting_Type%20A/EXT%20LT%20PANEL/EXT%20LT%20PANEL.kicad_sch) | 4 | 109 / 0 |
| [PCBs/Backlight PCBs/Backlighting_Type A/FCS PANEL/FCS PANEL.kicad_sch](../../PCBs/Backlight%20PCBs/Backlighting_Type%20A/FCS%20PANEL/FCS%20PANEL.kicad_sch) | 4 | 81 / 0 |
| [PCBs/Backlight PCBs/Backlighting_Type A/FIRE TEST PANEL/FIRE TEST PANEL.kicad_sch](../../PCBs/Backlight%20PCBs/Backlighting_Type%20A/FIRE%20TEST%20PANEL/FIRE%20TEST%20PANEL.kicad_sch) | 4 | 49 / 0 |
| [PCBs/Backlight PCBs/Backlighting_Type A/FUEL PANEL/FUEL PANEL.kicad_sch](../../PCBs/Backlight%20PCBs/Backlighting_Type%20A/FUEL%20PANEL/FUEL%20PANEL.kicad_sch) | 4 | 93 / 0 |
| [PCBs/Backlight PCBs/Backlighting_Type A/GEN TIE PANEL/GEN TIE PANEL.kicad_sch](../../PCBs/Backlight%20PCBs/Backlighting_Type%20A/GEN%20TIE%20PANEL/GEN%20TIE%20PANEL.kicad_sch) | 4 | 50 / 0 |
| [PCBs/Backlight PCBs/Backlighting_Type A/HUD PANEL/HUD PANEL.kicad_sch](../../PCBs/Backlight%20PCBs/Backlighting_Type%20A/HUD%20PANEL/HUD%20PANEL.kicad_sch) | 4 | 94 / 0 |
| [PCBs/Backlight PCBs/Backlighting_Type A/HUD VID RCD PANEL/HUD VID RCD PANEL.kicad_sch](../../PCBs/Backlight%20PCBs/Backlighting_Type%20A/HUD%20VID%20RCD%20PANEL/HUD%20VID%20RCD%20PANEL.kicad_sch) | 4 | 51 / 0 |
| [PCBs/Backlight PCBs/Backlighting_Type A/HYD ISO PANEL/HYD ISO PANEL.kicad_sch](../../PCBs/Backlight%20PCBs/Backlighting_Type%20A/HYD%20ISO%20PANEL/HYD%20ISO%20PANEL.kicad_sch) | 4 | 74 / 0 |
| [PCBs/Backlight PCBs/Backlighting_Type A/INTR LT PANEL/INTR LT PANEL.kicad_sch](../../PCBs/Backlight%20PCBs/Backlighting_Type%20A/INTR%20LT%20PANEL/INTR%20LT%20PANEL.kicad_sch) | 4 | 115 / 0 |
| [PCBs/Backlight PCBs/Backlighting_Type A/JETT STATION SELECT PLACARD/JETT STATION SELECT PLACARD.kicad_sch](../../PCBs/Backlight%20PCBs/Backlighting_Type%20A/JETT%20STATION%20SELECT%20PLACARD/JETT%20STATION%20SELECT%20PLACARD.kicad_sch) | 4 | 24 / 0 |
| [PCBs/Backlight PCBs/Backlighting_Type A/KY-58 PANEL/KY-58 PANEL.kicad_sch](../../PCBs/Backlight%20PCBs/Backlighting_Type%20A/KY-58%20PANEL/KY-58%20PANEL.kicad_sch) | 4 | 162 / 0 |
| [PCBs/Backlight PCBs/Backlighting_Type A/LANDING GEAR PANEL/LANDING GEAR PANEL.kicad_sch](../../PCBs/Backlight%20PCBs/Backlighting_Type%20A/LANDING%20GEAR%20PANEL/LANDING%20GEAR%20PANEL.kicad_sch) | 4 | 84 / 0 |
| [PCBs/Backlight PCBs/Backlighting_Type A/LDG WING FOLD PLACARD/LDG WING FOLD PLACARD.kicad_sch](../../PCBs/Backlight%20PCBs/Backlighting_Type%20A/LDG%20WING%20FOLD%20PLACARD/LDG%20WING%20FOLD%20PLACARD.kicad_sch) | 4 | 67 / 0 |
| [PCBs/Backlight PCBs/Backlighting_Type A/LEFT CIRCUIT BREAKER/LEFT CIRCUIT BREAKER.kicad_sch](../../PCBs/Backlight%20PCBs/Backlighting_Type%20A/LEFT%20CIRCUIT%20BREAKER/LEFT%20CIRCUIT%20BREAKER.kicad_sch) | 4 | 55 / 0 |
| [PCBs/Backlight PCBs/Backlighting_Type A/MASTER ARM PANEL/MASTER ARM PANEL.kicad_sch](../../PCBs/Backlight%20PCBs/Backlighting_Type%20A/MASTER%20ARM%20PANEL/MASTER%20ARM%20PANEL.kicad_sch) | 4 | 76 / 0 |
| [PCBs/Backlight PCBs/Backlighting_Type A/OBOGS PANEL/OBOGS PANEL.kicad_sch](../../PCBs/Backlight%20PCBs/Backlighting_Type%20A/OBOGS%20PANEL/OBOGS%20PANEL.kicad_sch) | 4 | 61 / 0 |
| [PCBs/Backlight PCBs/Backlighting_Type A/SELECT JETT PANEL/SELECT JETT PANEL.kicad_sch](../../PCBs/Backlight%20PCBs/Backlighting_Type%20A/SELECT%20JETT%20PANEL/SELECT%20JETT%20PANEL.kicad_sch) | 4 | 183 / 0 |
| [PCBs/Backlight PCBs/Backlighting_Type A/SIM CONTROL PANEL/SIM CONTROL PANEL.kicad_sch](../../PCBs/Backlight%20PCBs/Backlighting_Type%20A/SIM%20CONTROL%20PANEL/SIM%20CONTROL%20PANEL.kicad_sch) | 4 | 145 / 0 |
| [PCBs/Backlight PCBs/Backlighting_Type A/SIM POWER PANEL/SIM POWER PANEL.kicad_sch](../../PCBs/Backlight%20PCBs/Backlighting_Type%20A/SIM%20POWER%20PANEL/SIM%20POWER%20PANEL.kicad_sch) | 4 | 104 / 0 |
| [PCBs/Backlight PCBs/Backlighting_Type A/SNSR PANEL/SNSR PANEL.kicad_sch](../../PCBs/Backlight%20PCBs/Backlighting_Type%20A/SNSR%20PANEL/SNSR%20PANEL.kicad_sch) | 4 | 158 / 0 |
| [PCBs/Backlight PCBs/Backlighting_Type A/SPIN RCV PANEL/SPIN RCV PANEL.kicad_sch](../../PCBs/Backlight%20PCBs/Backlighting_Type%20A/SPIN%20RCV%20PANEL/SPIN%20RCV%20PANEL.kicad_sch) | 4 | 96 / 0 |
| [PCBs/Backlight PCBs/Backlighting_Type B/ECS PANEL/ECS PANEL.kicad_sch](../../PCBs/Backlight%20PCBs/Backlighting_Type%20B/ECS%20PANEL/ECS%20PANEL.kicad_sch) | 1 | 15 / 0 |
| [PCBs/Functional PCBs/AMPCD/AMPCD.kicad_sch](../../PCBs/Functional%20PCBs/AMPCD/AMPCD.kicad_sch) | 1 | 147 / 0 |
| [PCBs/Functional PCBs/CONTROLLER_AMPCD DDI/CONTROLLER_AMPCD DDI.kicad_sch](../../PCBs/Functional%20PCBs/CONTROLLER_AMPCD%20DDI/CONTROLLER_AMPCD%20DDI.kicad_sch) | 4 | 56 / 0 |
| [PCBs/Functional PCBs/CONTROLLER_Radar Altimeter/CONTROLLER_Radar Altimeter.kicad_sch](../../PCBs/Functional%20PCBs/CONTROLLER_Radar%20Altimeter/CONTROLLER_Radar%20Altimeter.kicad_sch) | 3 | 50 / 0 |
| [PCBs/Functional PCBs/CONTROLLER_Standby Instrument/CONTROLLER_Standby Instrument.kicad_sch](../../PCBs/Functional%20PCBs/CONTROLLER_Standby%20Instrument/CONTROLLER_Standby%20Instrument.kicad_sch) | 1 | 63 / 0 |
| [PCBs/Functional PCBs/CONTROLLER_Stick/CONTROLLER_Stick.kicad_sch](../../PCBs/Functional%20PCBs/CONTROLLER_Stick/CONTROLLER_Stick.kicad_sch) | 1 | 37 / 0 |
| [PCBs/Functional PCBs/CONTROLLER_Throttle/CONTROLLER_Throttle.kicad_sch](../../PCBs/Functional%20PCBs/CONTROLLER_Throttle/CONTROLLER_Throttle.kicad_sch) | 2 | 84 / 0 |
| [PCBs/Functional PCBs/DDI/DDI.kicad_sch](../../PCBs/Functional%20PCBs/DDI/DDI.kicad_sch) | 1 | 144 / 0 |
| [PCBs/Functional PCBs/EYEBROW WARNING INDICATOR_LEFT/EYEBROW WARNING INDICATOR_LEFT.kicad_sch](../../PCBs/Functional%20PCBs/EYEBROW%20WARNING%20INDICATOR_LEFT/EYEBROW%20WARNING%20INDICATOR_LEFT.kicad_sch) | 4.0.1 | 72 / 0 |
| [PCBs/Functional PCBs/EYEBROW WARNING INDICATOR_RIGHT/EYEBROW WARNING INDICATOR_RIGHT.kicad_sch](../../PCBs/Functional%20PCBs/EYEBROW%20WARNING%20INDICATOR_RIGHT/EYEBROW%20WARNING%20INDICATOR_RIGHT.kicad_sch) | not stated | 72 / 0 |
| [PCBs/Functional PCBs/GAUGE_Analog Instruments/GAUGE_Analog Instruments.kicad_sch](../../PCBs/Functional%20PCBs/GAUGE_Analog%20Instruments/GAUGE_Analog%20Instruments.kicad_sch) | 2 | 20 / 0 |
| [PCBs/Functional PCBs/GAUGE_Dual Needle Instruments/GAUGE_Dual Needle Instruments.kicad_sch](../../PCBs/Functional%20PCBs/GAUGE_Dual%20Needle%20Instruments/GAUGE_Dual%20Needle%20Instruments.kicad_sch) | 1 | 51 / 0 |
| [PCBs/Functional PCBs/GAUGE_Standby Altimeter/GAUGE_Standby Altimeter.kicad_sch](../../PCBs/Functional%20PCBs/GAUGE_Standby%20Altimeter/GAUGE_Standby%20Altimeter.kicad_sch) | 2 | 39 / 0 |
| [PCBs/Functional PCBs/HOTAS_Analog Stick Breakout/HOTAS_Analog Stick Breakout.kicad_sch](../../PCBs/Functional%20PCBs/HOTAS_Analog%20Stick%20Breakout/HOTAS_Analog%20Stick%20Breakout.kicad_sch) | not stated | 20 / 0 |
| [PCBs/Functional PCBs/HOTAS_Hat Switch Breakout/HOTAS_Hat Switch Breakout.kicad_sch](../../PCBs/Functional%20PCBs/HOTAS_Hat%20Switch%20Breakout/HOTAS_Hat%20Switch%20Breakout.kicad_sch) | not stated | 10 / 0 |
| [PCBs/Functional PCBs/HOTAS_Throttle Inner Grip/HOTAS_Throttle Inner Grip.kicad_sch](../../PCBs/Functional%20PCBs/HOTAS_Throttle%20Inner%20Grip/HOTAS_Throttle%20Inner%20Grip.kicad_sch) | 1.1.0 | 30 / 0 |
| [PCBs/Functional PCBs/IFEI/IFEI.kicad_sch](../../PCBs/Functional%20PCBs/IFEI/IFEI.kicad_sch) | 1 | 71 / 0 |
| [PCBs/Functional PCBs/JETT STATION SELECT/JETT STATION SELECT.kicad_sch](../../PCBs/Functional%20PCBs/JETT%20STATION%20SELECT/JETT%20STATION%20SELECT.kicad_sch) | 1 | 61 / 0 |
| [PCBs/Functional PCBs/RWR CONTROL PANEL/RWR CONTROL PANEL.kicad_sch](../../PCBs/Functional%20PCBs/RWR%20CONTROL%20PANEL/RWR%20CONTROL%20PANEL.kicad_sch) | A | 70 / 0 |
| [PCBs/Functional PCBs/UFC_Function Select/UFC_Function Select.kicad_sch](../../PCBs/Functional%20PCBs/UFC_Function%20Select/UFC_Function%20Select.kicad_sch) | 3 | 72 / 0 |
| [PCBs/Functional PCBs/UFC_Main/UFC_Main.kicad_sch](../../PCBs/Functional%20PCBs/UFC_Main/UFC_Main.kicad_sch) | 6.3.1 | 382 / 0 |
| [PCBs/Functional PCBs/UTIL_PHOTOSWITCH/UTIL_PHOTOSWITCH.kicad_sch](../../PCBs/Functional%20PCBs/UTIL_PHOTOSWITCH/UTIL_PHOTOSWITCH.kicad_sch) | not stated | 10 / 0 |
| [interconnects/OH_Center_Tub.kicad_sch](../../interconnects/OH_Center_Tub.kicad_sch) | A | 46 / 0 |
| [interconnects/OH_Interconnect.kicad_sch](../../interconnects/OH_Interconnect.kicad_sch) | A | 25 / 5 |
| [interconnects/OH_Left_Console.kicad_sch](../../interconnects/OH_Left_Console.kicad_sch) | A | 359 / 0 |
| [interconnects/OH_Lower_Instrument_Panel.kicad_sch](../../interconnects/OH_Lower_Instrument_Panel.kicad_sch) | A | 353 / 0 |
| [interconnects/OH_Right_Console.kicad_sch](../../interconnects/OH_Right_Console.kicad_sch) | A | 255 / 0 |
| [interconnects/OH_Upper_Instrument_Panel.kicad_sch](../../interconnects/OH_Upper_Instrument_Panel.kicad_sch) | A | 194 / 0 |

## Legacy schematic index

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

| Source | Components | Title / revision |
| --- | --- | --- |
| [PCBs/ABSIS/ABSIS_ALE/Legacy/ABSIS_ALE.sch](../../PCBs/ABSIS/ABSIS_ALE/Legacy/ABSIS_ALE.sch) | 38 | Title "ABSIS ALE (ALmost Everything)"; Rev "1" |
| [PCBs/ABSIS/ABSIS_ALE Relay Module/Legacy/ABSIS_ALE Relay Module.sch](../../PCBs/ABSIS/ABSIS_ALE%20Relay%20Module/Legacy/ABSIS_ALE%20Relay%20Module.sch) | 36 | Title "ABSIS Nano 2.5 Relay Module"; Rev "1" |
| [PCBs/ABSIS/ABSIS_ATX Power Supply Unit/Legacy/ABSIS_ATX Power Supply Unit.sch](../../PCBs/ABSIS/ABSIS_ATX%20Power%20Supply%20Unit/Legacy/ABSIS_ATX%20Power%20Supply%20Unit.sch) | 84 | Title "ABSIS ATX Power Board"; Rev "2" |
| [PCBs/ABSIS/ABSIS_Backlight Controller/Legacy/ABSIS_Backlight Controller.sch](../../PCBs/ABSIS/ABSIS_Backlight%20Controller/Legacy/ABSIS_Backlight%20Controller.sch) | 81 | Title "ABSIS Backlighting Controller"; Rev "2" |
| [PCBs/ABSIS/ABSIS_HID Bus Master/Legacy/ABSIS_HID Bus Master.sch](../../PCBs/ABSIS/ABSIS_HID%20Bus%20Master/Legacy/ABSIS_HID%20Bus%20Master.sch) | 37 | Title "ABSIS RS485 Bus Master"; Rev "2" |
| [PCBs/ABSIS/ABSIS_Hall Sensor/Legacy/ABSIS_Hall Sensor.sch](../../PCBs/ABSIS/ABSIS_Hall%20Sensor/Legacy/ABSIS_Hall%20Sensor.sch) | 18 | Title "ABSIS HALL SENSOR"; Rev "2" |
| [PCBs/ABSIS/ABSIS_Pit Management System/Legacy/ABSIS_Pit Management System.sch](../../PCBs/ABSIS/ABSIS_Pit%20Management%20System/Legacy/ABSIS_Pit%20Management%20System.sch) | 32 | Title "ABSIS PIT MANAGEMENT SYSTEM"; Rev "1" |
| [PCBs/Backlight PCBs/Backlighting_Type A/ANT SEL PANEL/Legacy/ANT SEL PANEL.sch](../../PCBs/Backlight%20PCBs/Backlighting_Type%20A/ANT%20SEL%20PANEL/Legacy/ANT%20SEL%20PANEL.sch) | 23 | Title ""; Rev "" |
| [PCBs/Backlight PCBs/Backlighting_Type A/APU ENG CRANK PANEL/Legacy/APU ENG CRANK PANEL.sch](../../PCBs/Backlight%20PCBs/Backlighting_Type%20A/APU%20ENG%20CRANK%20PANEL/Legacy/APU%20ENG%20CRANK%20PANEL.sch) | 37 | Title ""; Rev "" |
| [PCBs/Backlight PCBs/Backlighting_Type A/AV COOL PANEL/Legacy/AV COOL PANEL.sch](../../PCBs/Backlight%20PCBs/Backlighting_Type%20A/AV%20COOL%20PANEL/Legacy/AV%20COOL%20PANEL.sch) | 26 | Title ""; Rev "" |
| [PCBs/Backlight PCBs/Backlighting_Type A/CAUTION LIGHTS PANEL/Legacy/CAUTION LIGHTS PANEL.sch](../../PCBs/Backlight%20PCBs/Backlighting_Type%20A/CAUTION%20LIGHTS%20PANEL/Legacy/CAUTION%20LIGHTS%20PANEL.sch) | 53 | Title ""; Rev "" |
| [PCBs/Backlight PCBs/Backlighting_Type A/COMM PANEL/Legacy/COMM PANEL.sch](../../PCBs/Backlight%20PCBs/Backlighting_Type%20A/COMM%20PANEL/Legacy/COMM%20PANEL.sch) | 224 | Title ""; Rev "" |
| [PCBs/Backlight PCBs/Backlighting_Type A/DEFOG PANEL/Legacy/DEFOG PANEL.sch](../../PCBs/Backlight%20PCBs/Backlighting_Type%20A/DEFOG%20PANEL/Legacy/DEFOG%20PANEL.sch) | 27 | Title ""; Rev "" |
| [PCBs/Backlight PCBs/Backlighting_Type A/ECM DISP PANEL/Legacy/ECM DISP PANEL.sch](../../PCBs/Backlight%20PCBs/Backlighting_Type%20A/ECM%20DISP%20PANEL/Legacy/ECM%20DISP%20PANEL.sch) | 89 | Title ""; Rev "" |
| [PCBs/Backlight PCBs/Backlighting_Type A/ECS PANEL/Legacy/ECS PANEL.sch](../../PCBs/Backlight%20PCBs/Backlighting_Type%20A/ECS%20PANEL/Legacy/ECS%20PANEL.sch) | 131 | Title ""; Rev "" |
| [PCBs/Backlight PCBs/Backlighting_Type A/ELEC PANEL/Legacy/ELEC PANEL.sch](../../PCBs/Backlight%20PCBs/Backlighting_Type%20A/ELEC%20PANEL/Legacy/ELEC%20PANEL.sch) | 53 | Title ""; Rev "" |
| [PCBs/Backlight PCBs/Backlighting_Type A/EXT LT PANEL/Legacy/EXT LT PANEL.sch](../../PCBs/Backlight%20PCBs/Backlighting_Type%20A/EXT%20LT%20PANEL/Legacy/EXT%20LT%20PANEL.sch) | 69 | Title ""; Rev "" |
| [PCBs/Backlight PCBs/Backlighting_Type A/FCS PANEL/Legacy/FCS PANEL.sch](../../PCBs/Backlight%20PCBs/Backlighting_Type%20A/FCS%20PANEL/Legacy/FCS%20PANEL.sch) | 44 | Title ""; Rev "" |
| [PCBs/Backlight PCBs/Backlighting_Type A/FIRE TEST PANEL/Legacy/FIRE TEST PANEL.sch](../../PCBs/Backlight%20PCBs/Backlighting_Type%20A/FIRE%20TEST%20PANEL/Legacy/FIRE%20TEST%20PANEL.sch) | 29 | Title ""; Rev "" |
| [PCBs/Backlight PCBs/Backlighting_Type A/FUEL PANEL/Legacy/FUEL PANEL.sch](../../PCBs/Backlight%20PCBs/Backlighting_Type%20A/FUEL%20PANEL/Legacy/FUEL%20PANEL.sch) | 52 | Title ""; Rev "" |
| [PCBs/Backlight PCBs/Backlighting_Type A/GEN TIE PANEL/Legacy/GEN TIE PANEL.sch](../../PCBs/Backlight%20PCBs/Backlighting_Type%20A/GEN%20TIE%20PANEL/Legacy/GEN%20TIE%20PANEL.sch) | 23 | Title ""; Rev "" |
| [PCBs/Backlight PCBs/Backlighting_Type A/HUD PANEL/Legacy/HUD PANEL.sch](../../PCBs/Backlight%20PCBs/Backlighting_Type%20A/HUD%20PANEL/Legacy/HUD%20PANEL.sch) | 64 | Title ""; Rev "" |
| [PCBs/Backlight PCBs/Backlighting_Type A/HUD VID RCD PANEL/Legacy/HUD VID RCD PANEL.sch](../../PCBs/Backlight%20PCBs/Backlighting_Type%20A/HUD%20VID%20RCD%20PANEL/Legacy/HUD%20VID%20RCD%20PANEL.sch) | 21 | Title ""; Rev "" |
| [PCBs/Backlight PCBs/Backlighting_Type A/HYD ISO PANEL/Legacy/HYD ISO PANEL.sch](../../PCBs/Backlight%20PCBs/Backlighting_Type%20A/HYD%20ISO%20PANEL/Legacy/HYD%20ISO%20PANEL.sch) | 42 | Title ""; Rev "" |
| [PCBs/Backlight PCBs/Backlighting_Type A/INTR LT PANEL/Legacy/INTR LT PANEL.sch](../../PCBs/Backlight%20PCBs/Backlighting_Type%20A/INTR%20LT%20PANEL/Legacy/INTR%20LT%20PANEL.sch) | 70 | Title ""; Rev "" |
| [PCBs/Backlight PCBs/Backlighting_Type A/JETT STATION SELECT PLACARD/Legacy/JETT STATION SELECT PLACARD.sch](../../PCBs/Backlight%20PCBs/Backlighting_Type%20A/JETT%20STATION%20SELECT%20PLACARD/Legacy/JETT%20STATION%20SELECT%20PLACARD.sch) | 9 | Title ""; Rev "" |
| [PCBs/Backlight PCBs/Backlighting_Type A/KY-58 PANEL/Legacy/KY-58 PANEL.sch](../../PCBs/Backlight%20PCBs/Backlighting_Type%20A/KY-58%20PANEL/Legacy/KY-58%20PANEL.sch) | 118 | Title ""; Rev "" |
| [PCBs/Backlight PCBs/Backlighting_Type A/LANDING GEAR PANEL/Legacy/LANDING GEAR PANEL.sch](../../PCBs/Backlight%20PCBs/Backlighting_Type%20A/LANDING%20GEAR%20PANEL/Legacy/LANDING%20GEAR%20PANEL.sch) | 48 | Title ""; Rev "" |
| [PCBs/Backlight PCBs/Backlighting_Type A/LDG WING FOLD PLACARD/Legacy/LDG WING FOLD PLACARD.sch](../../PCBs/Backlight%20PCBs/Backlighting_Type%20A/LDG%20WING%20FOLD%20PLACARD/Legacy/LDG%20WING%20FOLD%20PLACARD.sch) | 37 | Title ""; Rev "" |
| [PCBs/Backlight PCBs/Backlighting_Type A/LEFT CIRCUIT BREAKER/Legacy/LEFT CIRCUIT BREAKER.sch](../../PCBs/Backlight%20PCBs/Backlighting_Type%20A/LEFT%20CIRCUIT%20BREAKER/Legacy/LEFT%20CIRCUIT%20BREAKER.sch) | 31 | Title ""; Rev "" |
| [PCBs/Backlight PCBs/Backlighting_Type A/MASTER ARM PANEL/Legacy/MASTER ARM PANEL.sch](../../PCBs/Backlight%20PCBs/Backlighting_Type%20A/MASTER%20ARM%20PANEL/Legacy/MASTER%20ARM%20PANEL.sch) | 48 | Title ""; Rev "" |
| [PCBs/Backlight PCBs/Backlighting_Type A/OBOGS PANEL/Legacy/OBOGS PANEL.sch](../../PCBs/Backlight%20PCBs/Backlighting_Type%20A/OBOGS%20PANEL/Legacy/OBOGS%20PANEL.sch) | 38 | Title ""; Rev "" |
| [PCBs/Backlight PCBs/Backlighting_Type A/SELECT JETT PANEL/Legacy/SELECT JETT PANEL.sch](../../PCBs/Backlight%20PCBs/Backlighting_Type%20A/SELECT%20JETT%20PANEL/Legacy/SELECT%20JETT%20PANEL.sch) | 122 | Title ""; Rev "" |
| [PCBs/Backlight PCBs/Backlighting_Type A/SIM CONTROL PANEL/Legacy/SIM CONTROL PANEL.sch](../../PCBs/Backlight%20PCBs/Backlighting_Type%20A/SIM%20CONTROL%20PANEL/Legacy/SIM%20CONTROL%20PANEL.sch) | 102 | Title ""; Rev "" |
| [PCBs/Backlight PCBs/Backlighting_Type A/SIM POWER PANEL/Legacy/SIM POWER PANEL.sch](../../PCBs/Backlight%20PCBs/Backlighting_Type%20A/SIM%20POWER%20PANEL/Legacy/SIM%20POWER%20PANEL.sch) | 77 | Title ""; Rev "" |
| [PCBs/Backlight PCBs/Backlighting_Type A/SIM POWER PANEL/Legacy/SIM_PWR_PCB_V2/SIM PWR PCB V2.sch](../../PCBs/Backlight%20PCBs/Backlighting_Type%20A/SIM%20POWER%20PANEL/Legacy/SIM_PWR_PCB_V2/SIM%20PWR%20PCB%20V2.sch) | 54 | Title ""; Rev "" |
| [PCBs/Backlight PCBs/Backlighting_Type A/SNSR PANEL/Legacy/SNSR PANEL.sch](../../PCBs/Backlight%20PCBs/Backlighting_Type%20A/SNSR%20PANEL/Legacy/SNSR%20PANEL.sch) | 120 | Title ""; Rev "" |
| [PCBs/Backlight PCBs/Backlighting_Type A/SPIN RCV PANEL/Legacy/SPIN RCV PANEL.sch](../../PCBs/Backlight%20PCBs/Backlighting_Type%20A/SPIN%20RCV%20PANEL/Legacy/SPIN%20RCV%20PANEL.sch) | 86 | Title ""; Rev "" |
| [PCBs/Backlight PCBs/Backlighting_Type B/ECS PANEL/Legacy/ECS PANEL.sch](../../PCBs/Backlight%20PCBs/Backlighting_Type%20B/ECS%20PANEL/Legacy/ECS%20PANEL.sch) | 15 | Title ""; Rev "" |
| [PCBs/Functional PCBs/AMPCD/Legacy/AMPCD.sch](../../PCBs/Functional%20PCBs/AMPCD/Legacy/AMPCD.sch) | 147 | Title "AMPCD BUTTON BOARD"; Rev "1" |
| [PCBs/Functional PCBs/CONTROLLER_AMPCD DDI/Legacy/CONTROLLER_AMPCD DDI.sch](../../PCBs/Functional%20PCBs/CONTROLLER_AMPCD%20DDI/Legacy/CONTROLLER_AMPCD%20DDI.sch) | 55 | Title "DDI/AMPCD CONTROLLER"; Rev "2" |
| [PCBs/Functional PCBs/CONTROLLER_Radar Altimeter/Legacy/CONTROLLER_Radar Altimeter.sch](../../PCBs/Functional%20PCBs/CONTROLLER_Radar%20Altimeter/Legacy/CONTROLLER_Radar%20Altimeter.sch) | 44 | Title "Radar Altimeter Controller"; Rev "1" |
| [PCBs/Functional PCBs/CONTROLLER_Standby Instrument/Legacy/CONTROLLER_Standby Instrument.sch](../../PCBs/Functional%20PCBs/CONTROLLER_Standby%20Instrument/Legacy/CONTROLLER_Standby%20Instrument.sch) | 63 | Title "ABSIS MEGA 2.0"; Rev "1" |
| [PCBs/Functional PCBs/CONTROLLER_Stick/Legacy/CONTROLLER_Stick.sch](../../PCBs/Functional%20PCBs/CONTROLLER_Stick/Legacy/CONTROLLER_Stick.sch) | 37 | Title "OH Flight Stick Controller"; Rev "1" |
| [PCBs/Functional PCBs/CONTROLLER_Throttle/Legacy/CONTROLLER_Throttle.sch](../../PCBs/Functional%20PCBs/CONTROLLER_Throttle/Legacy/CONTROLLER_Throttle.sch) | 105 | Title "OH Flight Stick Controller"; Rev "1" |
| [PCBs/Functional PCBs/DDI/Legacy/DDI.sch](../../PCBs/Functional%20PCBs/DDI/Legacy/DDI.sch) | 144 | Title "DDI Button Board"; Rev "1" |
| [PCBs/Functional PCBs/EYEBROW WARNING INDICATOR_RIGHT/Legacy/ewi_v3.sch](../../PCBs/Functional%20PCBs/EYEBROW%20WARNING%20INDICATOR_RIGHT/Legacy/ewi_v3.sch) | 72 | Title ""; Rev "" |
| [PCBs/Functional PCBs/GAUGE_Analog Instruments/Legacy/GAUGE_Analog Instruments.sch](../../PCBs/Functional%20PCBs/GAUGE_Analog%20Instruments/Legacy/GAUGE_Analog%20Instruments.sch) | 20 | Title ""; Rev "2" |
| [PCBs/Functional PCBs/GAUGE_Dual Needle Instruments/Legacy/GAUGE_Dual Needle Instruments.sch](../../PCBs/Functional%20PCBs/GAUGE_Dual%20Needle%20Instruments/Legacy/GAUGE_Dual%20Needle%20Instruments.sch) | 51 | Title "DUAL NEEDLE GAUGE"; Rev "1" |
| [PCBs/Functional PCBs/GAUGE_Standby Altimeter/Legacy/GAUGE_Standby Altimeter.sch](../../PCBs/Functional%20PCBs/GAUGE_Standby%20Altimeter/Legacy/GAUGE_Standby%20Altimeter.sch) | 39 | Title ""; Rev "2" |
| [PCBs/Functional PCBs/HOTAS_Analog Stick Breakout/Legacy/HOTAS_Analog Stick Breakout.sch](../../PCBs/Functional%20PCBs/HOTAS_Analog%20Stick%20Breakout/Legacy/HOTAS_Analog%20Stick%20Breakout.sch) | 20 | Title ""; Rev "" |
| [PCBs/Functional PCBs/HOTAS_Hat Switch Breakout/Legacy/HOTAS_Hat Switch Breakout.sch](../../PCBs/Functional%20PCBs/HOTAS_Hat%20Switch%20Breakout/Legacy/HOTAS_Hat%20Switch%20Breakout.sch) | 10 | Title ""; Rev "" |
| [PCBs/Functional PCBs/HOTAS_Throttle Inner Grip/Legacy/HOTAS_Throttle Inner Grip.sch](../../PCBs/Functional%20PCBs/HOTAS_Throttle%20Inner%20Grip/Legacy/HOTAS_Throttle%20Inner%20Grip.sch) | 30 | Title ""; Rev "" |
| [PCBs/Functional PCBs/IFEI/Legacy/IFEI.sch](../../PCBs/Functional%20PCBs/IFEI/Legacy/IFEI.sch) | 71 | Title "Integrated Fuel & Engine Indicator (IFEI)"; Rev "1" |
| [PCBs/Functional PCBs/JETT STATION SELECT/Legacy/JETT STATION SELECT.sch](../../PCBs/Functional%20PCBs/JETT%20STATION%20SELECT/Legacy/JETT%20STATION%20SELECT.sch) | 61 | Title "JETT STATION SELECT"; Rev "1" |
| [PCBs/Functional PCBs/RWR CONTROL PANEL/Legacy/RWR CONTROL PANEL.sch](../../PCBs/Functional%20PCBs/RWR%20CONTROL%20PANEL/Legacy/RWR%20CONTROL%20PANEL.sch) | 70 | Title "RWR CONTROL PANEL"; Rev "A" |
| [PCBs/Functional PCBs/UFC_Function Select/Legacy/UFC_Function Select.sch](../../PCBs/Functional%20PCBs/UFC_Function%20Select/Legacy/UFC_Function%20Select.sch) | 35 | Title "Autopilot Button PCB"; Rev "2" |
| [PCBs/Functional PCBs/UTIL_PHOTOSWITCH/Legacy/UTIL_PHOTOSWITCH.sch](../../PCBs/Functional%20PCBs/UTIL_PHOTOSWITCH/Legacy/UTIL_PHOTOSWITCH.sch) | 10 | Title ""; Rev "" |
| [lib/OH_Templates/ABSIS_Nano_2.0_Template/ABSIS_Nano_2.0_Template.sch](../../lib/OH_Templates/ABSIS_Nano_2.0_Template/ABSIS_Nano_2.0_Template.sch) | 34 | Title "ABSIS Nano 2.0"; Rev "1" |
| [lib/OH_Templates/Mega_shield_template/Mega_shield_template.sch](../../lib/OH_Templates/Mega_shield_template/Mega_shield_template.sch) | 35 | Title ""; Rev "1" |
