jrsteensen/OpenHornet/release/OHC_Common_Parts/OHC0001 - ASSY, SWITCH, LOCKING TOGGLES/OHC0001 - ASSY, SWITCH, LOCKING TOGGLES_-_v5.pdf

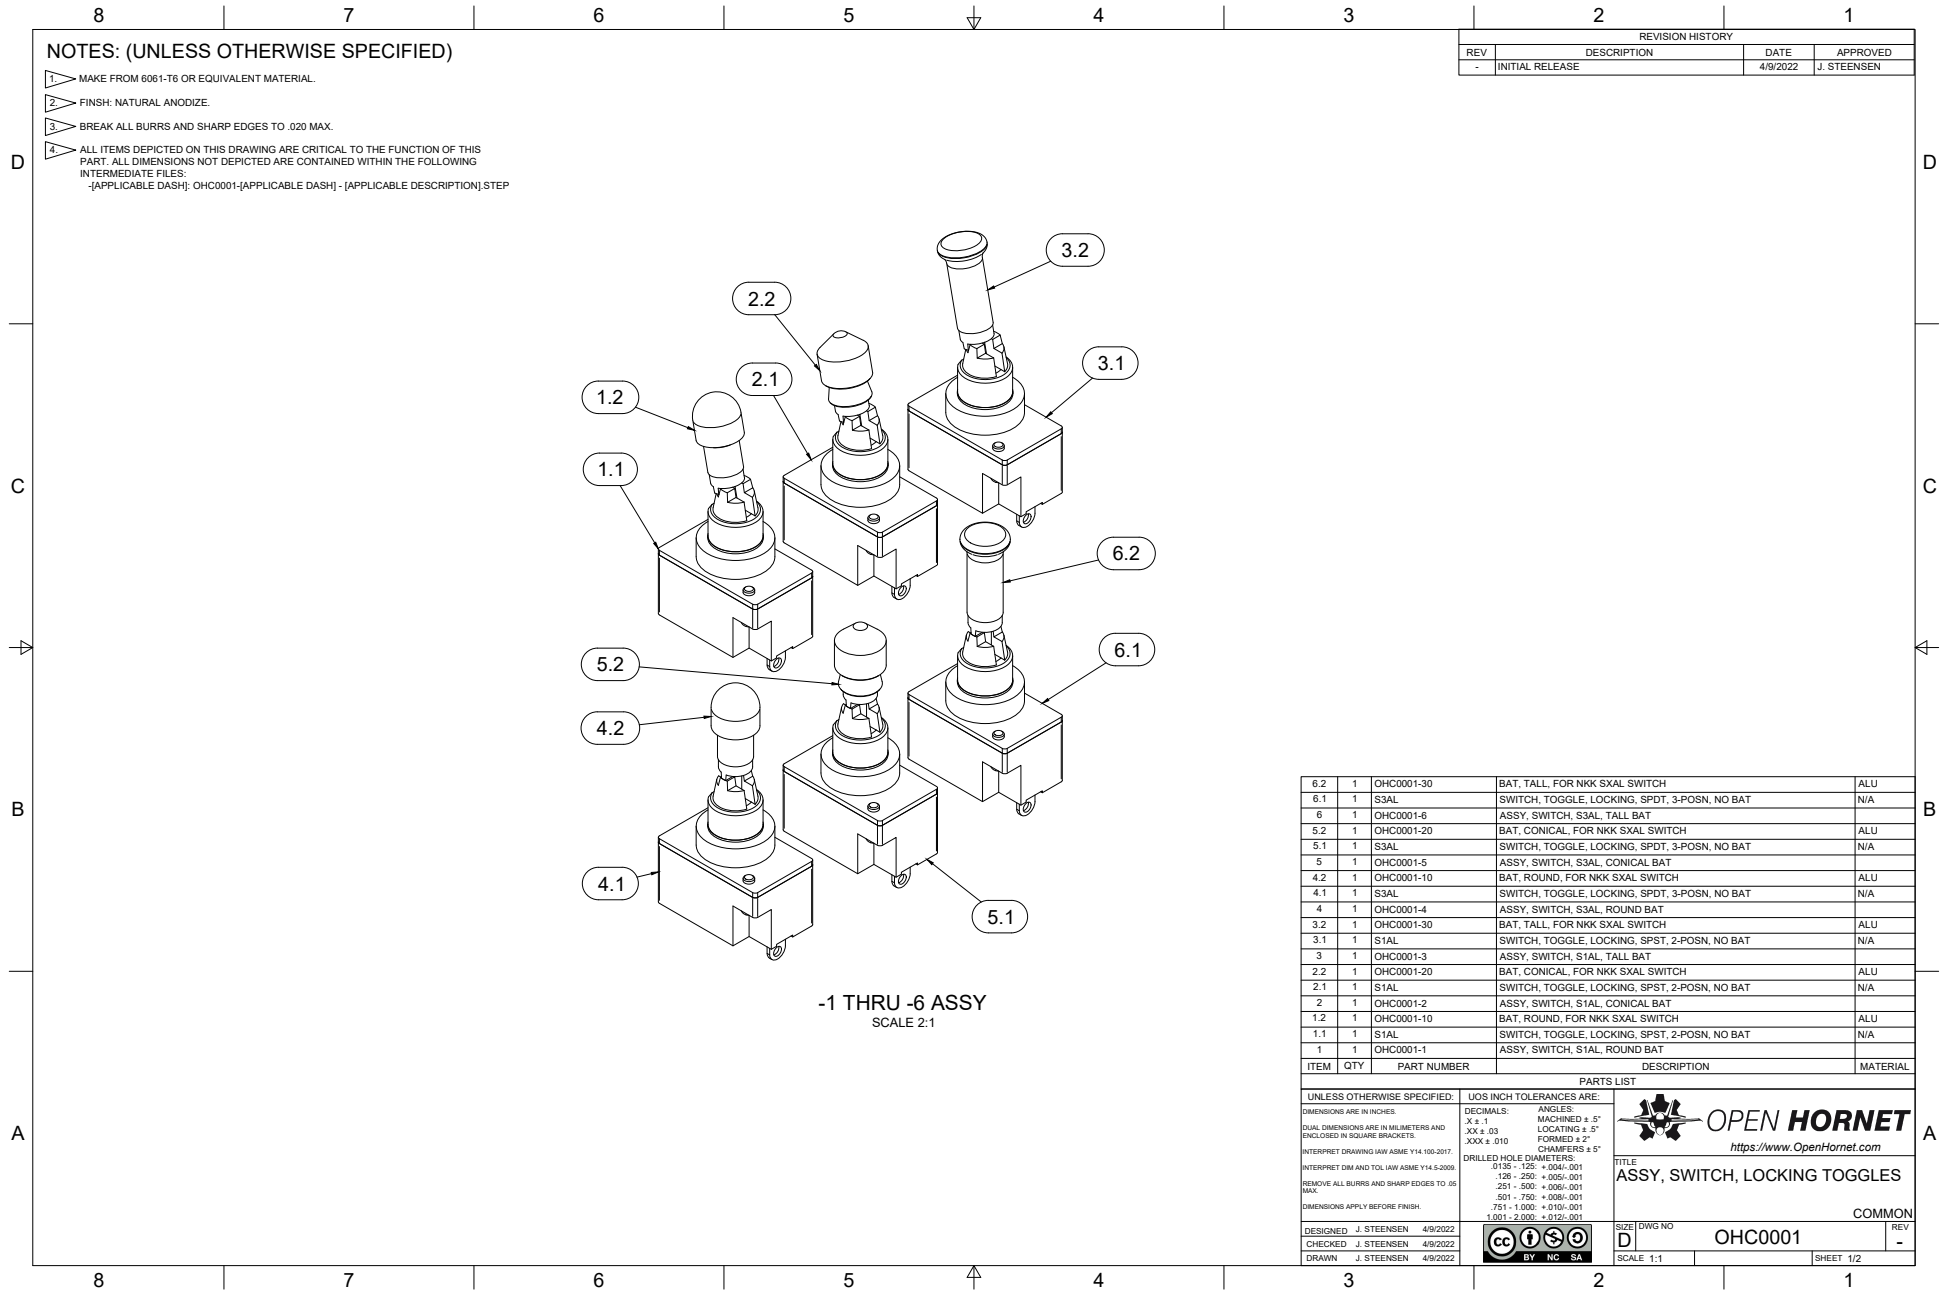
[picture p324: page 1]
SIZE; DWG NO; REV; J. STEENSEN; OHC0001; PARTS LIST; REVISION HISTORY; -1 THRU -6 ASSY; SCALE 2:1

NOTES: (UNLESS OTHERWISE SPECIFIED)

REV | DESCRIPTION | DATE | APPROVED
- | INITIAL RELEASE | 4/9/2022 | J. STEENSEN

1. MAKE FROM 6061-T6 OR EQUIVALENT MATERIAL.

2. FINSH: NATURAL ANODIZE.

3. BREAK ALL BURRS AND SHARP EDGES TO .020 MAX.

4. ALL ITEMS DEPICTED ON THIS DRAWING ARE CRITICAL TO THE FUNCTION OF THIS

PART. ALL DIMENSIONS NOT DEPICTED ARE CONTAINED WITHIN THE FOLLOWING
INTERMEDIATE FILES:
-[APPLICABLE DASH]: OHC0001-[APPLICABLE DASH] - [APPLICABLE DESCRIPTION].STEP

6.2 | 1 | OHC0001-30 | BAT, TALL, FOR NKK SXAL SWITCH | ALU
6.1 | 1 | S3AL | SWITCH, TOGGLE, LOCKING, SPDT, 3-POSN, NO BAT | N/A
6 | 1 | OHC0001-6 | ASSY, SWITCH, S3AL, TALL BAT
5.2 | 1 | OHC0001-20 | BAT, CONICAL, FOR NKK SXAL SWITCH | ALU
5.1 | 1 | S3AL | SWITCH, TOGGLE, LOCKING, SPDT, 3-POSN, NO BAT | N/A
5 | 1 | OHC0001-5 | ASSY, SWITCH, S3AL, CONICAL BAT
4.2 | 1 | OHC0001-10 | BAT, ROUND, FOR NKK SXAL SWITCH | ALU
4.1 | 1 | S3AL | SWITCH, TOGGLE, LOCKING, SPDT, 3-POSN, NO BAT | N/A
4 | 1 | OHC0001-4 | ASSY, SWITCH, S3AL, ROUND BAT
3.2 | 1 | OHC0001-30 | BAT, TALL, FOR NKK SXAL SWITCH | ALU
3.1 | 1 | S1AL | SWITCH, TOGGLE, LOCKING, SPST, 2-POSN, NO BAT | N/A
3 | 1 | OHC0001-3 | ASSY, SWITCH, S1AL, TALL BAT
2.2 | 1 | OHC0001-20 | BAT, CONICAL, FOR NKK SXAL SWITCH | ALU
2.1 | 1 | S1AL | SWITCH, TOGGLE, LOCKING, SPST, 2-POSN, NO BAT | N/A
2 | 1 | OHC0001-2 | ASSY, SWITCH, S1AL, CONICAL BAT
1.2 | 1 | OHC0001-10 | BAT, ROUND, FOR NKK SXAL SWITCH | ALU
1.1 | 1 | S1AL | SWITCH, TOGGLE, LOCKING, SPST, 2-POSN, NO BAT | N/A
1 | 1 | OHC0001-1 | ASSY, SWITCH, S1AL, ROUND BAT
ITEM | QTY | PART NUMBER | DESCRIPTION | MATERIAL

UNLESS OTHERWISE SPECIFIED: | UOS INCH TOLERANCES ARE: | https://www.OpenHornet.com
DIMENSIONS ARE IN INCHES. DUAL DIMENSIONS ARE IN MILIMETERS AND ENCLOSED IN SQUARE BRACKETS. INTERPRET DRAWING IAW ASME Y14.100-2017. INTERPRET DIM AND TOL IAW ASME Y14.5-2009. REMOVE ALL BURRS AND SHARP EDGES TO .05 MAX. DIMENSIONS APPLY BEFORE FINISH. | ANGLES: DECIMALS: MACHINED ± .5° .X ± .1 LOCATING ± .5° .XX ± .03 FORMED ± 2° .XXX ± .010 CHAMFERS ± 5° DRILLED HOLE DIAMETERS: .0135 - .125: +.004/-.001 .126 - .250: +.005/-.001 .251 - .500: +.006/-.001 .501 - .750: +.008/-.001 .751 - 1.000: +.010/-.001 1.001 - 2.000: +.012/-.001

TITLE
ASSY, SWITCH, LOCKING TOGGLES

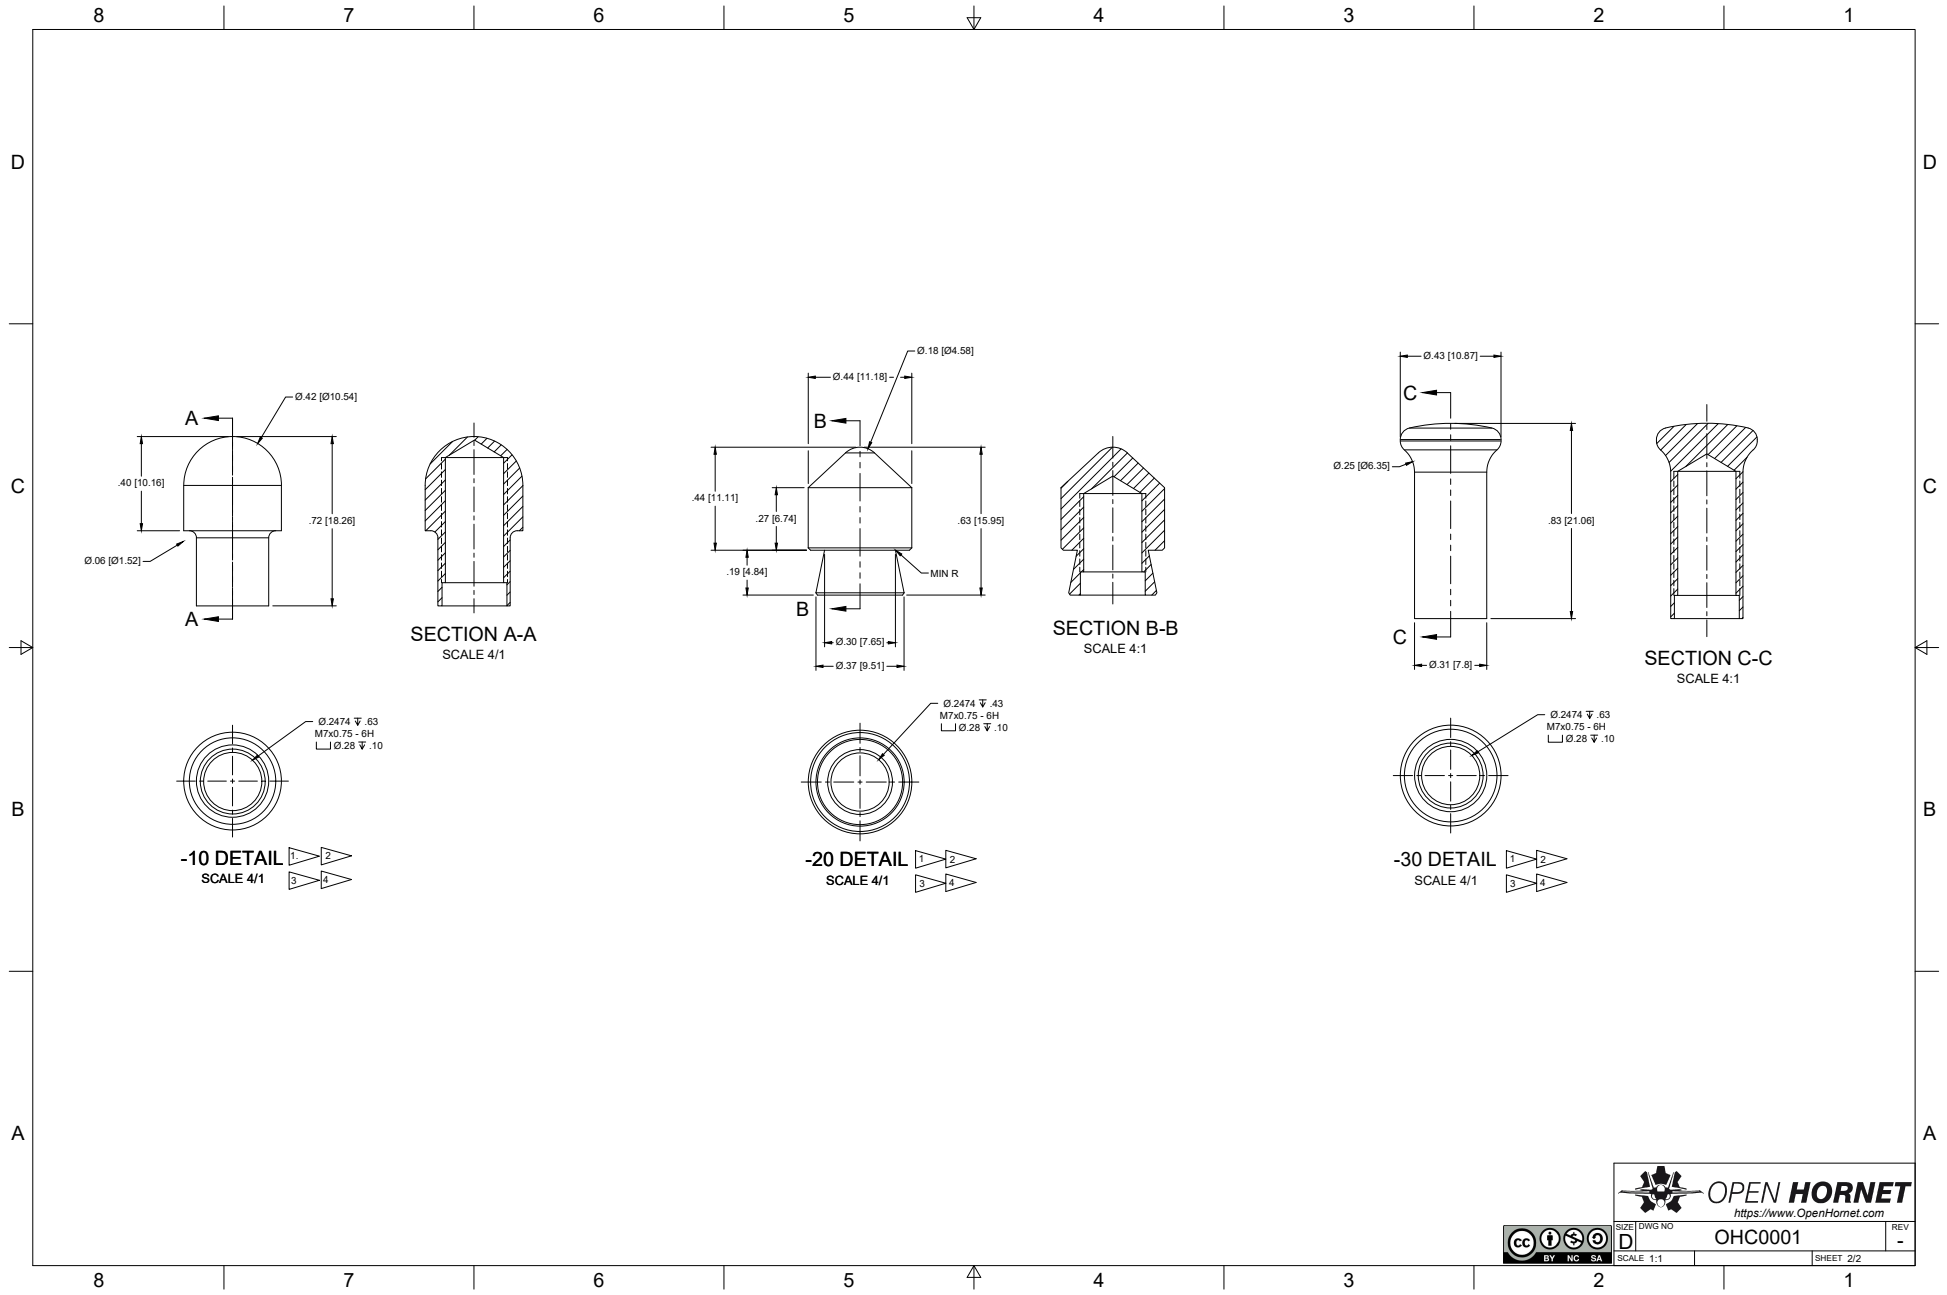
[picture p325: page 2]
-10 DETAIL; SCALE 4/1; SECTION A-A; -20 DETAIL; SECTION B-B; SCALE 4:1; MIN R; SECTION C-C; -30 DETAIL

https://www.OpenHornet.com

SIZE D | DWG NO OHC0001 | REV -

1:1 SCALE | | 2/2 SHEET
