jrsteensen/OpenHornet/release/OHC_Common_Parts/OHC0007 - INSTRUMENT COMPONENTS/OHC0007 - INSTRUMENT COMPONENTS_-_v5.pdf

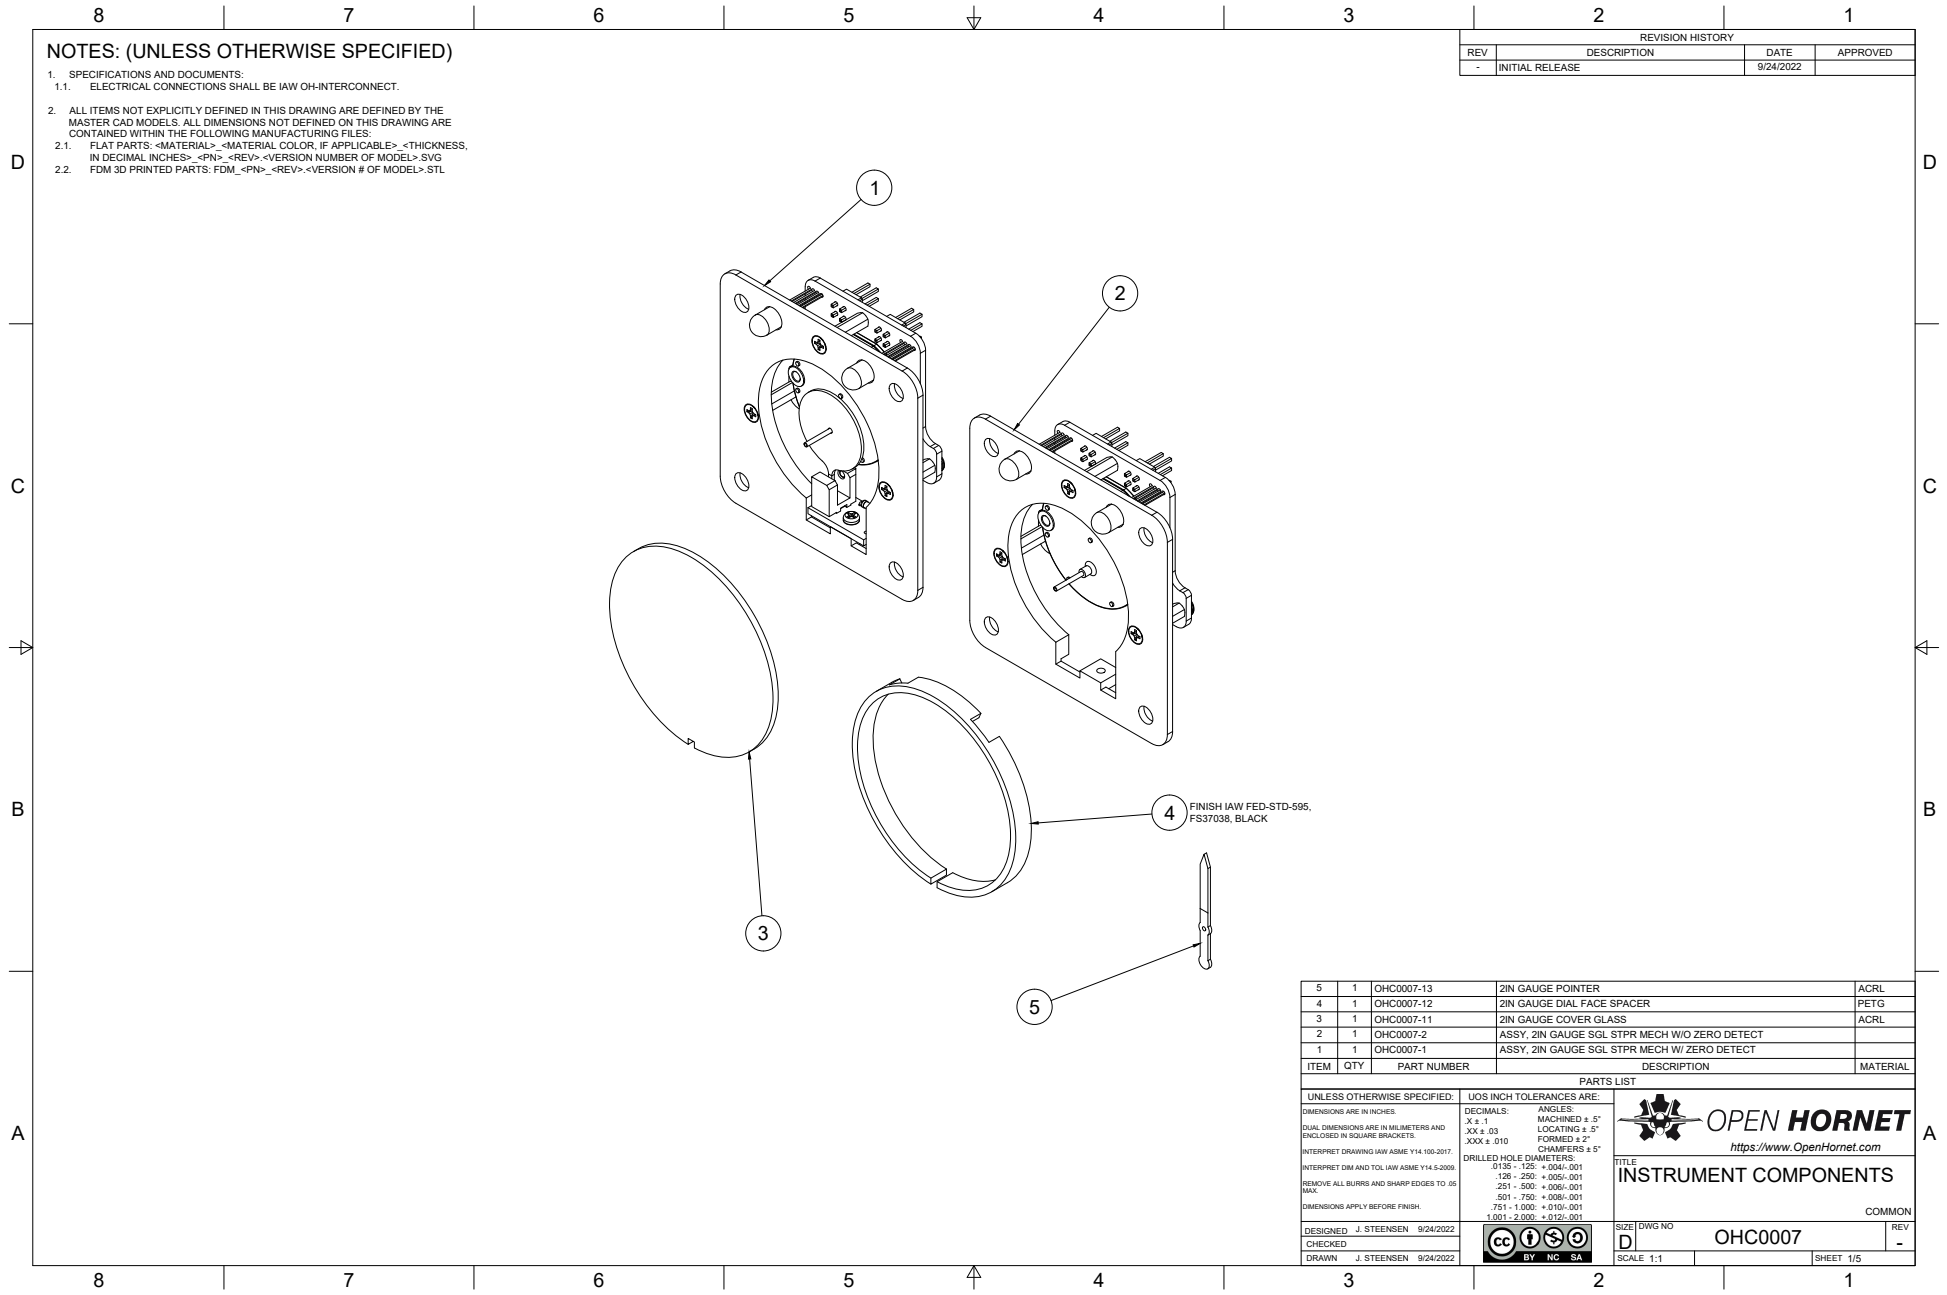
[picture p331: page 1]
J. STEENSEN; INSTRUMENT COMPONENTS; PARTS LIST; REVISION HISTORY

NOTES: (UNLESS OTHERWISE SPECIFIED)

REV | DESCRIPTION | DATE | APPROVED
- | INITIAL RELEASE | 9/24/2022

1. SPECIFICATIONS AND DOCUMENTS:
1.1. ELECTRICAL CONNECTIONS SHALL BE IAW OH-INTERCONNECT.

2. ALL ITEMS NOT EXPLICITLY DEFINED IN THIS DRAWING ARE DEFINED BY THE
MASTER CAD MODELS. ALL DIMENSIONS NOT DEFINED ON THIS DRAWING ARE
CONTAINED WITHIN THE FOLLOWING MANUFACTURING FILES:
2.1. FLAT PARTS: <MATERIAL>_<MATERIAL COLOR, IF APPLICABLE>_<THICKNESS,

IN DECIMAL INCHES>_<PN>_<REV>.<VERSION NUMBER OF MODEL>.SVG

2.2. FDM 3D PRINTED PARTS: FDM_<PN>_<REV>.<VERSION # OF MODEL>.STL

FINISH IAW FED-STD-595,
FS37038, BLACK

5 | 1 | OHC0007-13 | 2IN GAUGE POINTER | ACRL
4 | 1 | OHC0007-12 | 2IN GAUGE DIAL FACE SPACER | PETG
3 | 1 | OHC0007-11 | 2IN GAUGE COVER GLASS | ACRL
2 | 1 | OHC0007-2 | ASSY, 2IN GAUGE SGL STPR MECH W/O ZERO DETECT
1 | 1 | OHC0007-1 | ASSY, 2IN GAUGE SGL STPR MECH W/ ZERO DETECT
ITEM | QTY | PART NUMBER | DESCRIPTION | MATERIAL

UNLESS OTHERWISE SPECIFIED: | UOS INCH TOLERANCES ARE: | https://www.OpenHornet.com
DIMENSIONS ARE IN INCHES. DUAL DIMENSIONS ARE IN MILIMETERS AND ENCLOSED IN SQUARE BRACKETS. INTERPRET DRAWING IAW ASME Y14.100-2017. INTERPRET DIM AND TOL IAW ASME Y14.5-2009. REMOVE ALL BURRS AND SHARP EDGES TO .05 MAX. DIMENSIONS APPLY BEFORE FINISH. | ANGLES: DECIMALS: MACHINED ± .5° .X ± .1 LOCATING ± .5° .XX ± .03 FORMED ± 2° .XXX ± .010 CHAMFERS ± 5° DRILLED HOLE DIAMETERS: .0135 - .125: +.004/-.001 .126 - .250: +.005/-.001 .251 - .500: +.006/-.001 .501 - .750: +.008/-.001 .751 - 1.000: +.010/-.001 1.001 - 2.000: +.012/-.001

J. STEENSEN 9/24/2022 DESIGNED | | SIZE D | DWG NO OHC0007 | REV -

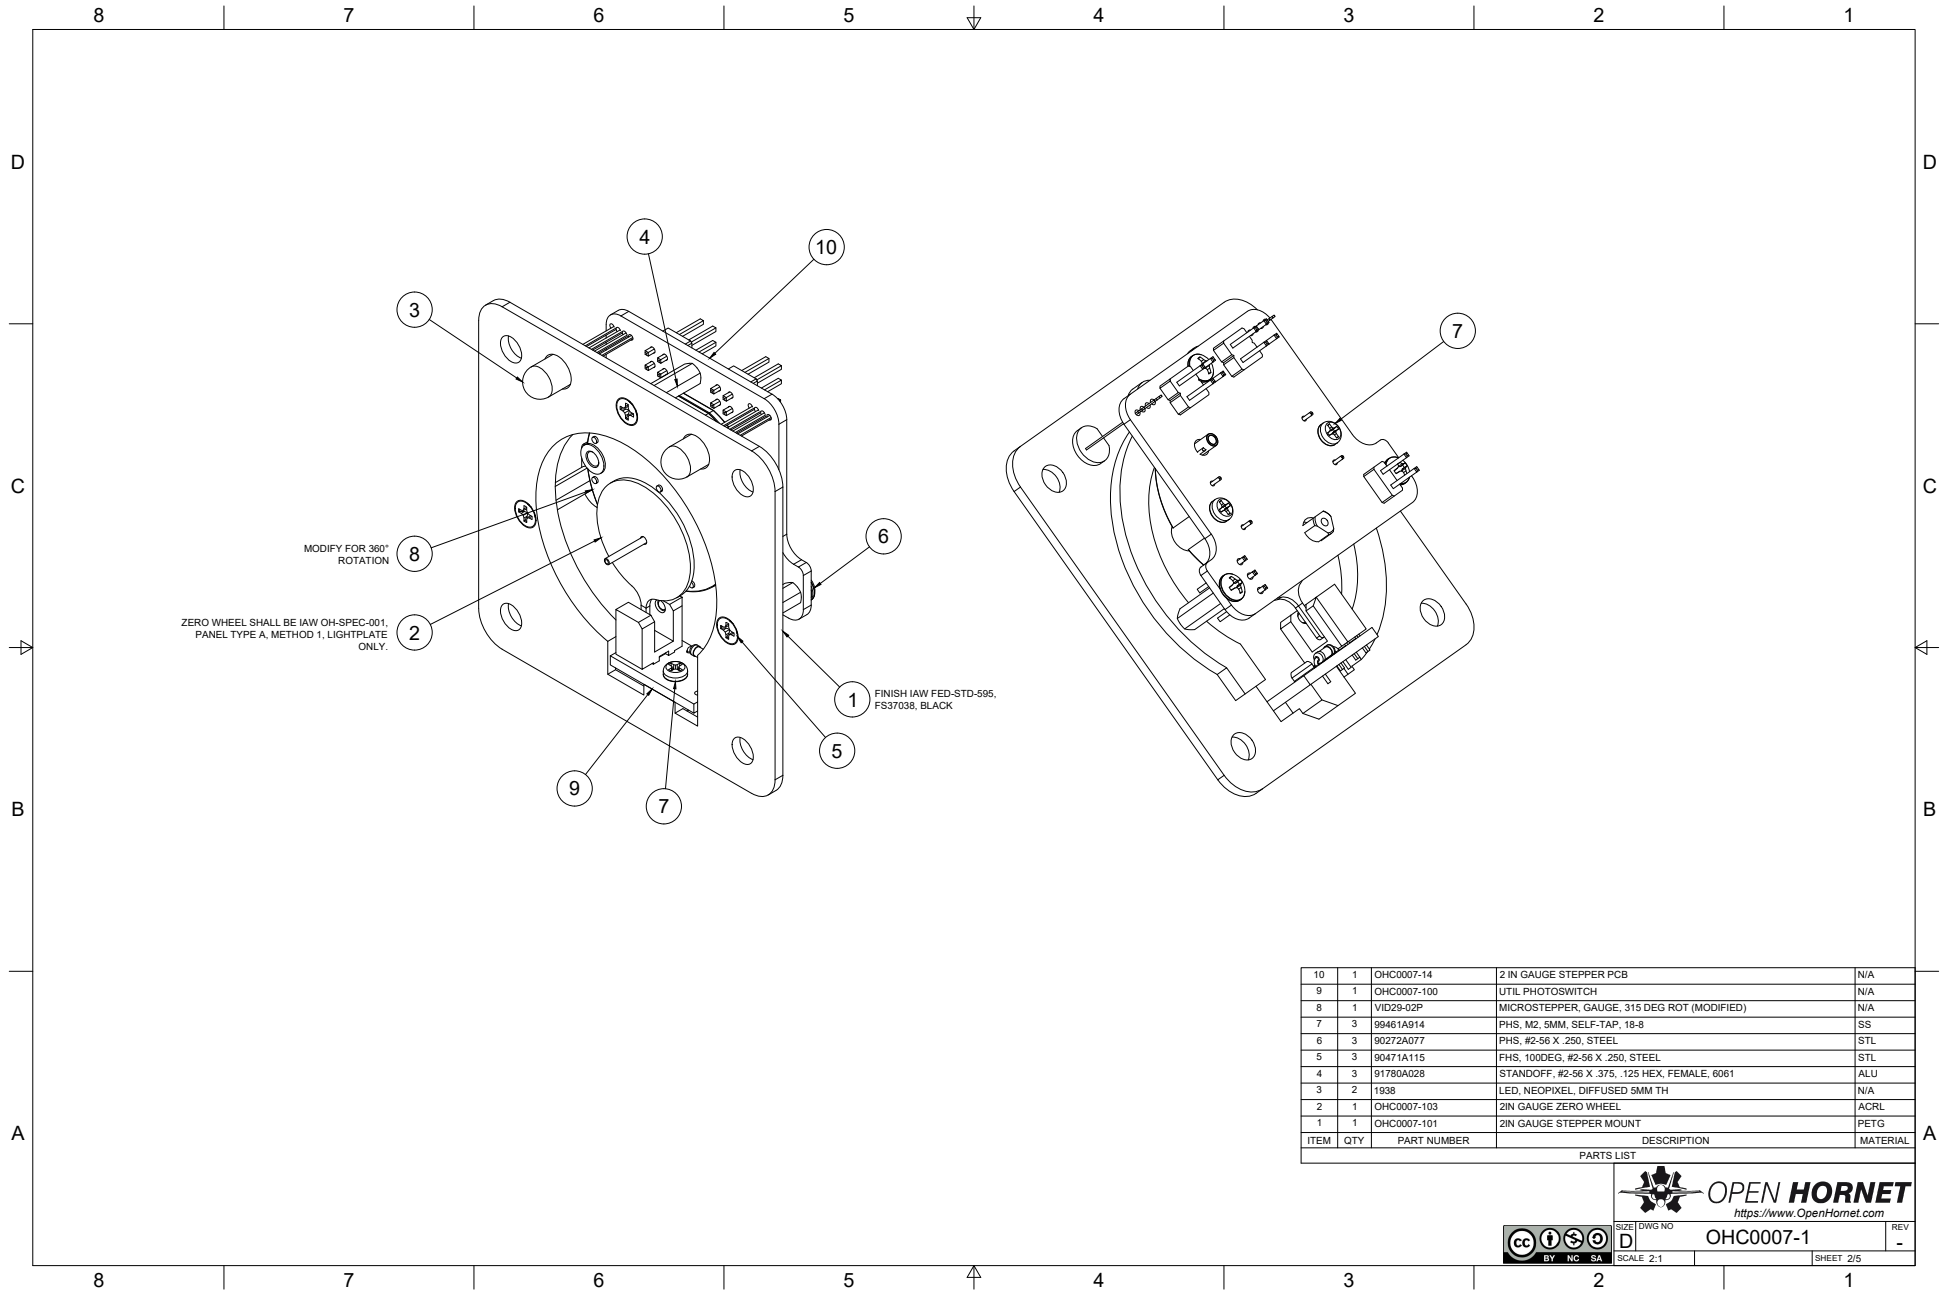
[picture p332: page 2]
PARTS LIST; MODIFY FOR 360°

ZERO WHEEL SHALL BE IAW OH-SPEC-001,
PANEL TYPE A, METHOD 1, LIGHTPLATE

FINISH IAW FED-STD-595,
FS37038, BLACK

10 | 1 | OHC0007-14 | 2 IN GAUGE STEPPER PCB | N/A
9 | 1 | OHC0007-100 | UTIL PHOTOSWITCH | N/A
8 | 1 | VID29-02P | MICROSTEPPER, GAUGE, 315 DEG ROT (MODIFIED) | N/A
7 | 3 | 99461A914 | PHS, M2, 5MM, SELF-TAP, 18-8 | SS
6 | 3 | 90272A077 | PHS, #2-56 X .250, STEEL | STL
5 | 3 | 90471A115 | FHS, 100DEG, #2-56 X .250, STEEL | STL
4 | 3 | 91780A028 | STANDOFF, #2-56 X .375, .125 HEX, FEMALE, 6061 | ALU
3 | 2 | 1938 | LED, NEOPIXEL, DIFFUSED 5MM TH | N/A
2 | 1 | OHC0007-103 | 2IN GAUGE ZERO WHEEL | ACRL
1 | 1 | OHC0007-101 | 2IN GAUGE STEPPER MOUNT | PETG
ITEM | QTY | PART NUMBER | DESCRIPTION | MATERIAL

https://www.OpenHornet.com

D | OHC0007-1 | -

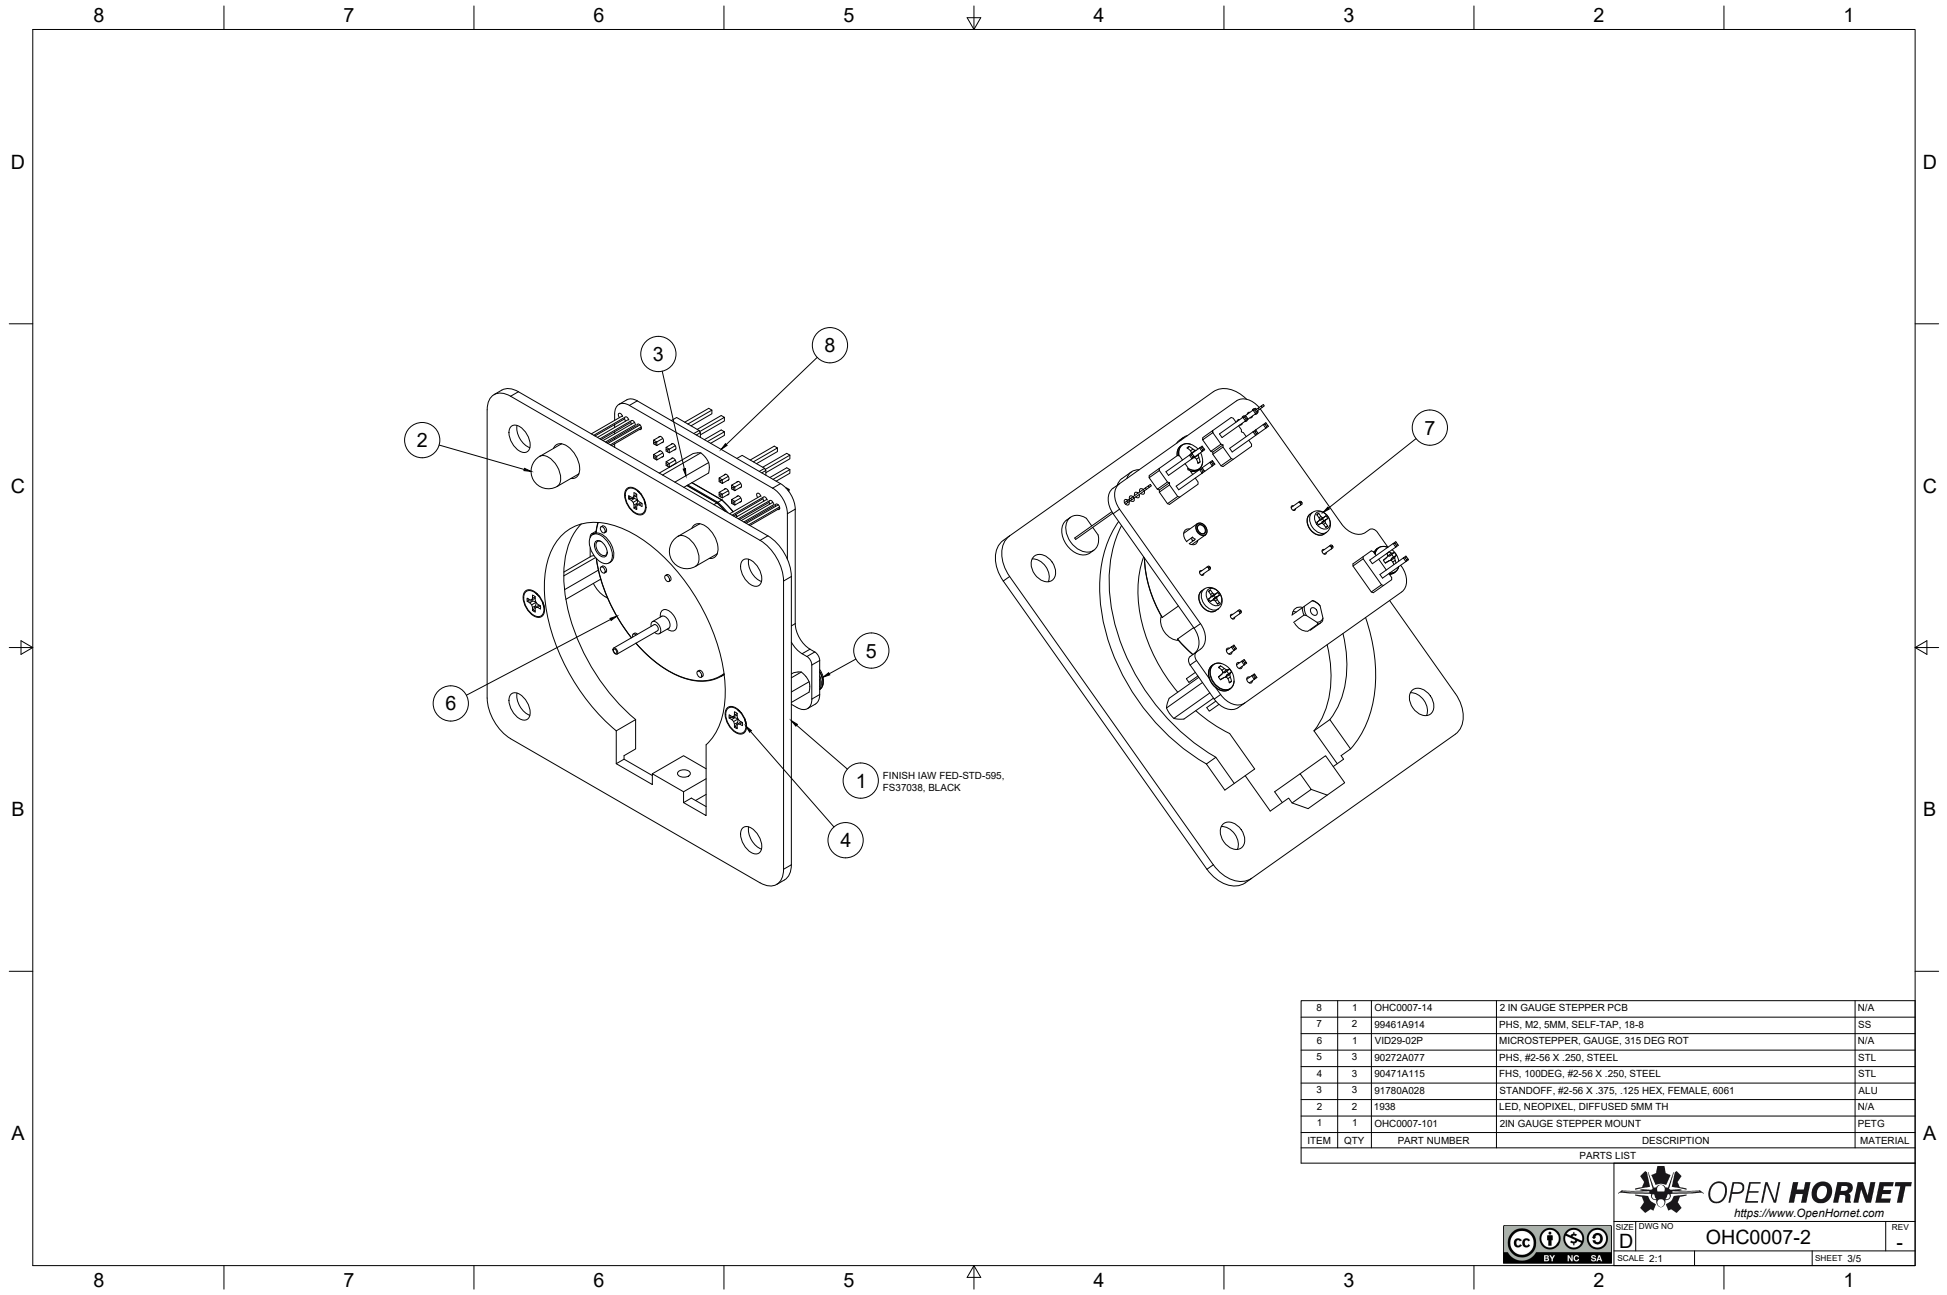
[picture p333: page 3]
PARTS LIST

FINISH IAW FED-STD-595,
FS37038, BLACK

8 | 1 | OHC0007-14 | 2 IN GAUGE STEPPER PCB | N/A
7 | 2 | 99461A914 | PHS, M2, 5MM, SELF-TAP, 18-8 | SS
6 | 1 | VID29-02P | MICROSTEPPER, GAUGE, 315 DEG ROT | N/A
5 | 3 | 90272A077 | PHS, #2-56 X .250, STEEL | STL
4 | 3 | 90471A115 | FHS, 100DEG, #2-56 X .250, STEEL | STL
3 | 3 | 91780A028 | STANDOFF, #2-56 X .375, .125 HEX, FEMALE, 6061 | ALU
2 | 2 | 1938 | LED, NEOPIXEL, DIFFUSED 5MM TH | N/A
1 | 1 | OHC0007-101 | 2IN GAUGE STEPPER MOUNT | PETG
ITEM | QTY | PART NUMBER | DESCRIPTION | MATERIAL

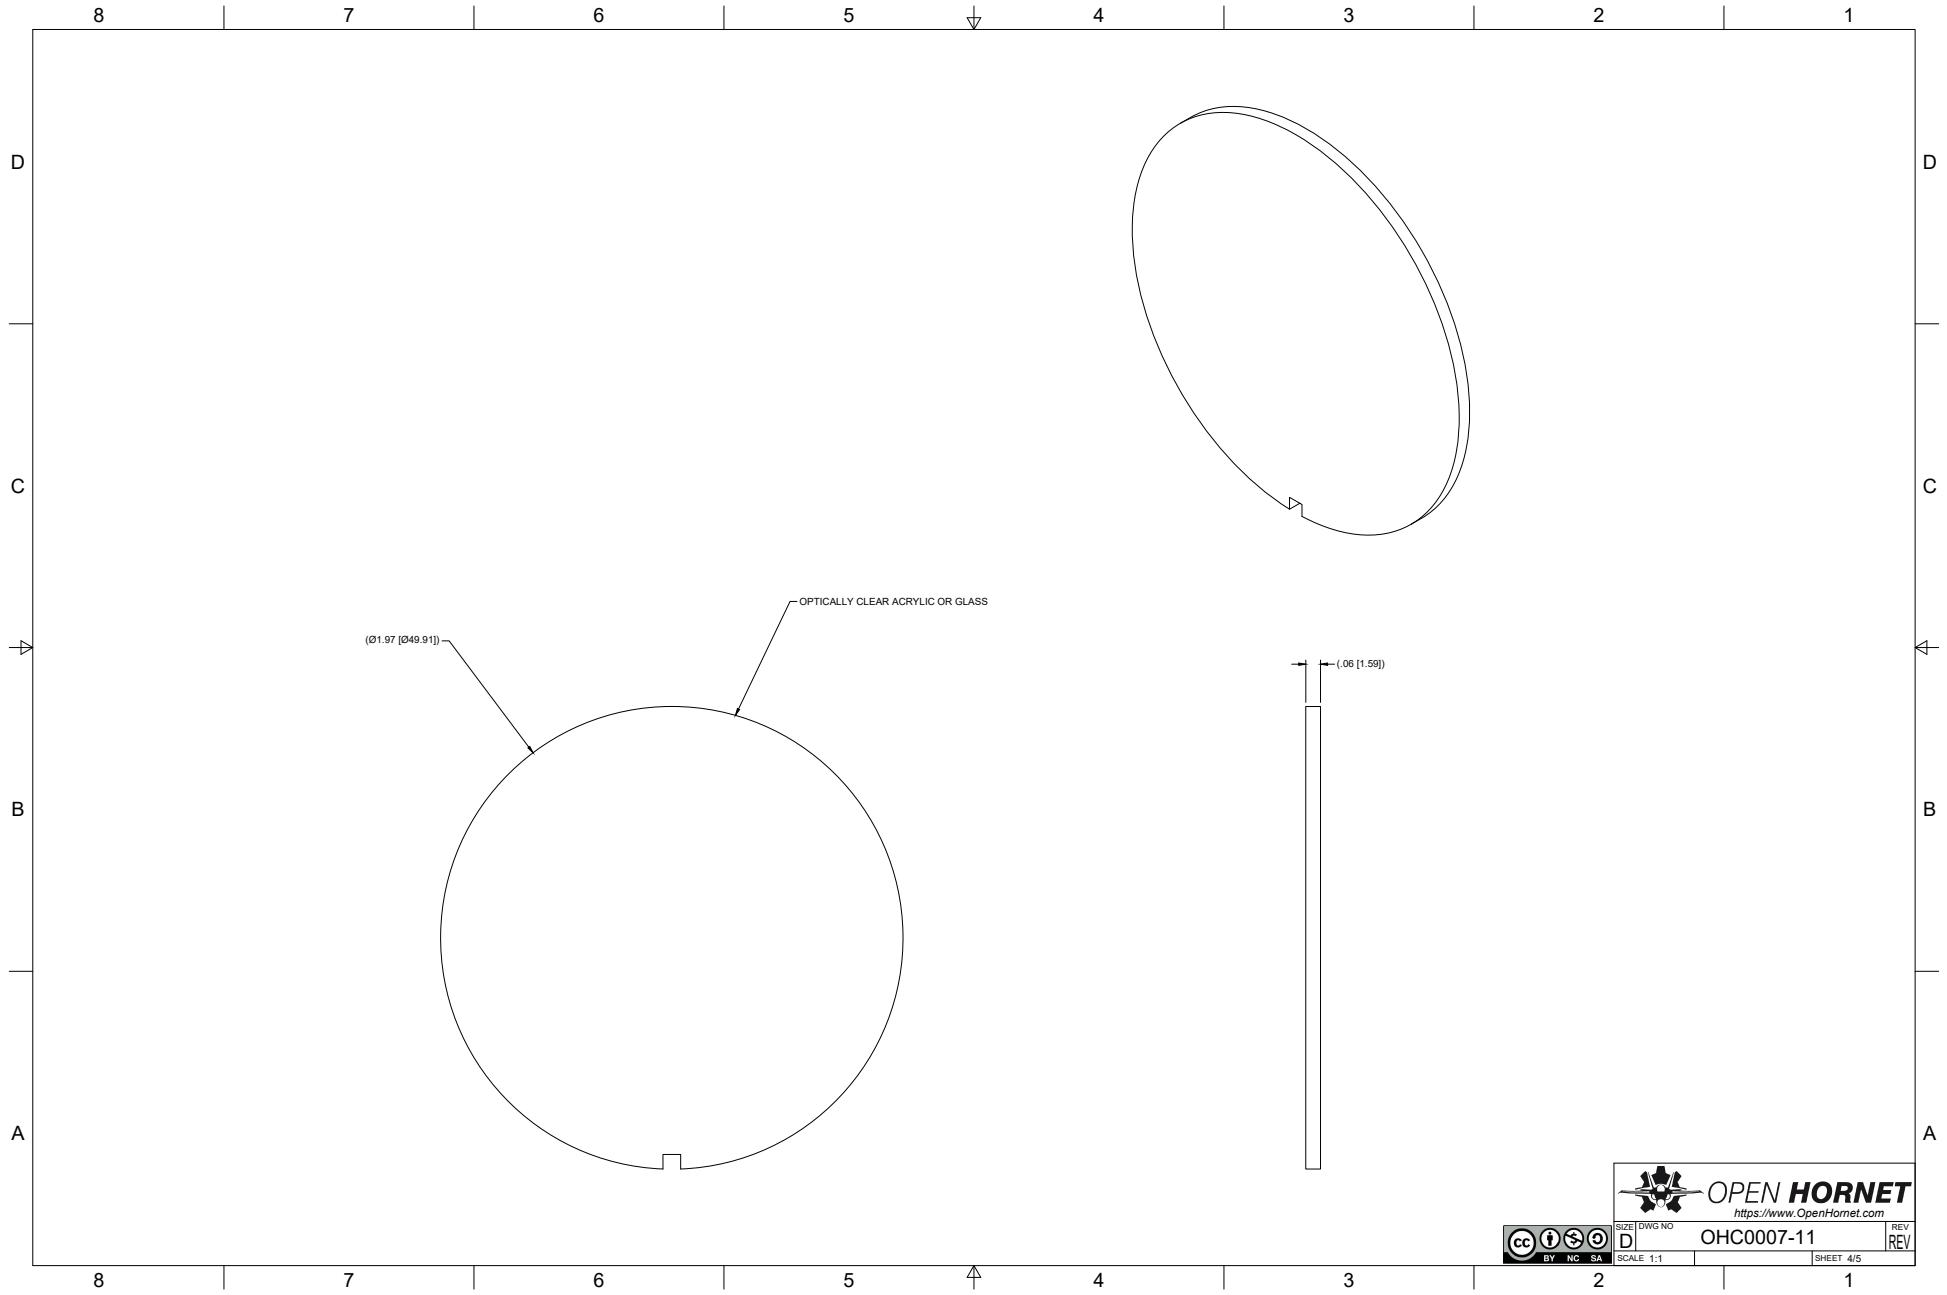
[picture p334: page 4]

OPTICALLY CLEAR ACRYLIC OR GLASS

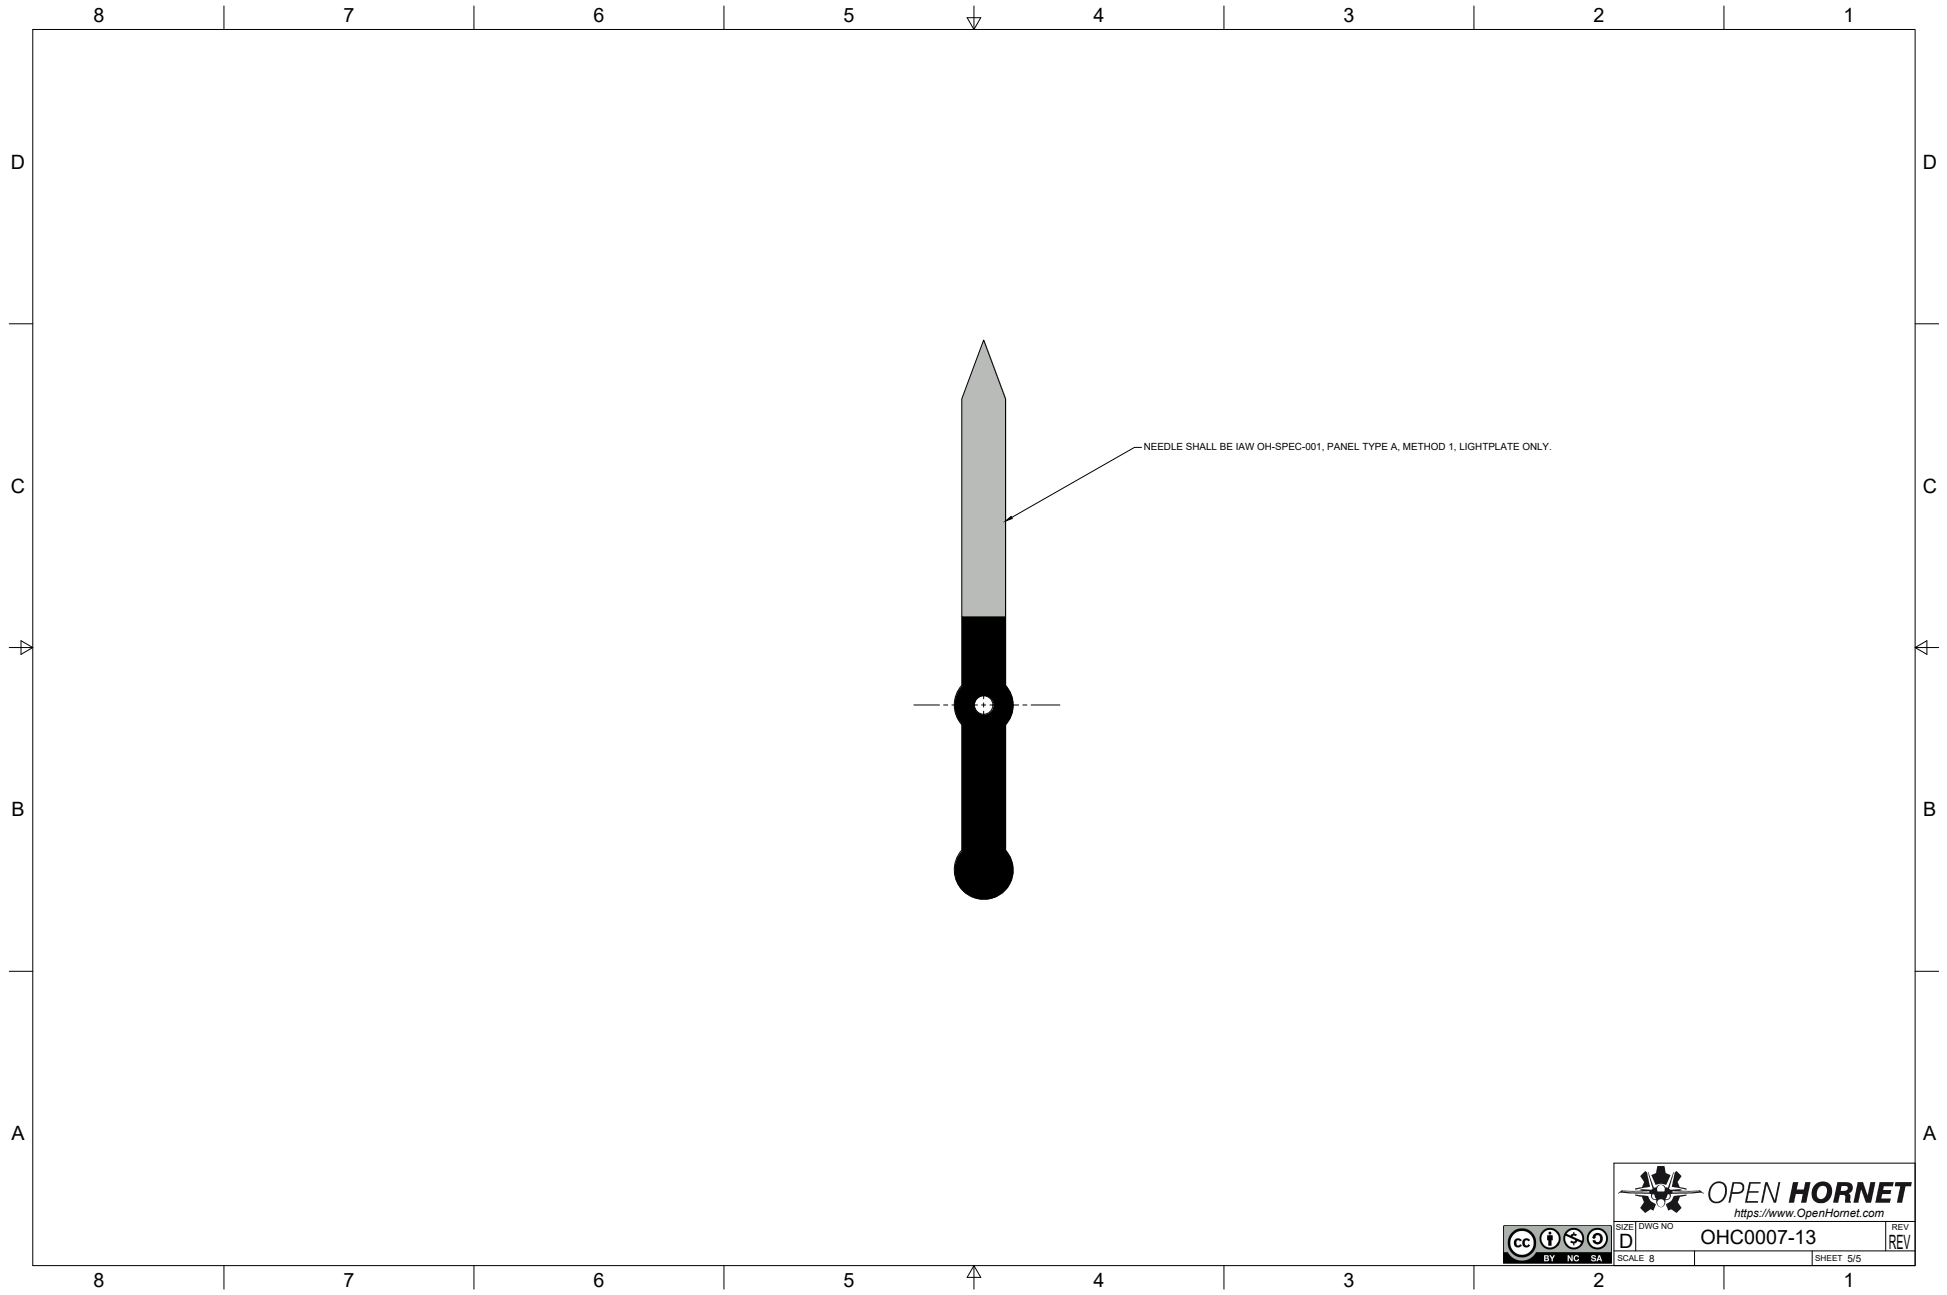
[picture p335: page 5]

NEEDLE SHALL BE IAW OH-SPEC-001, PANEL TYPE A, METHOD 1, LIGHTPLATE ONLY.

D | OHC0007-13 | REV
