jrsteensen/OpenHornet/release/OHC_Common_Parts/OHC0013 - BULKHEAD INTERCONNECT PANELS/OHC0013 - BULKHEAD INTERCONNECT PANELS_-_v4.pdf

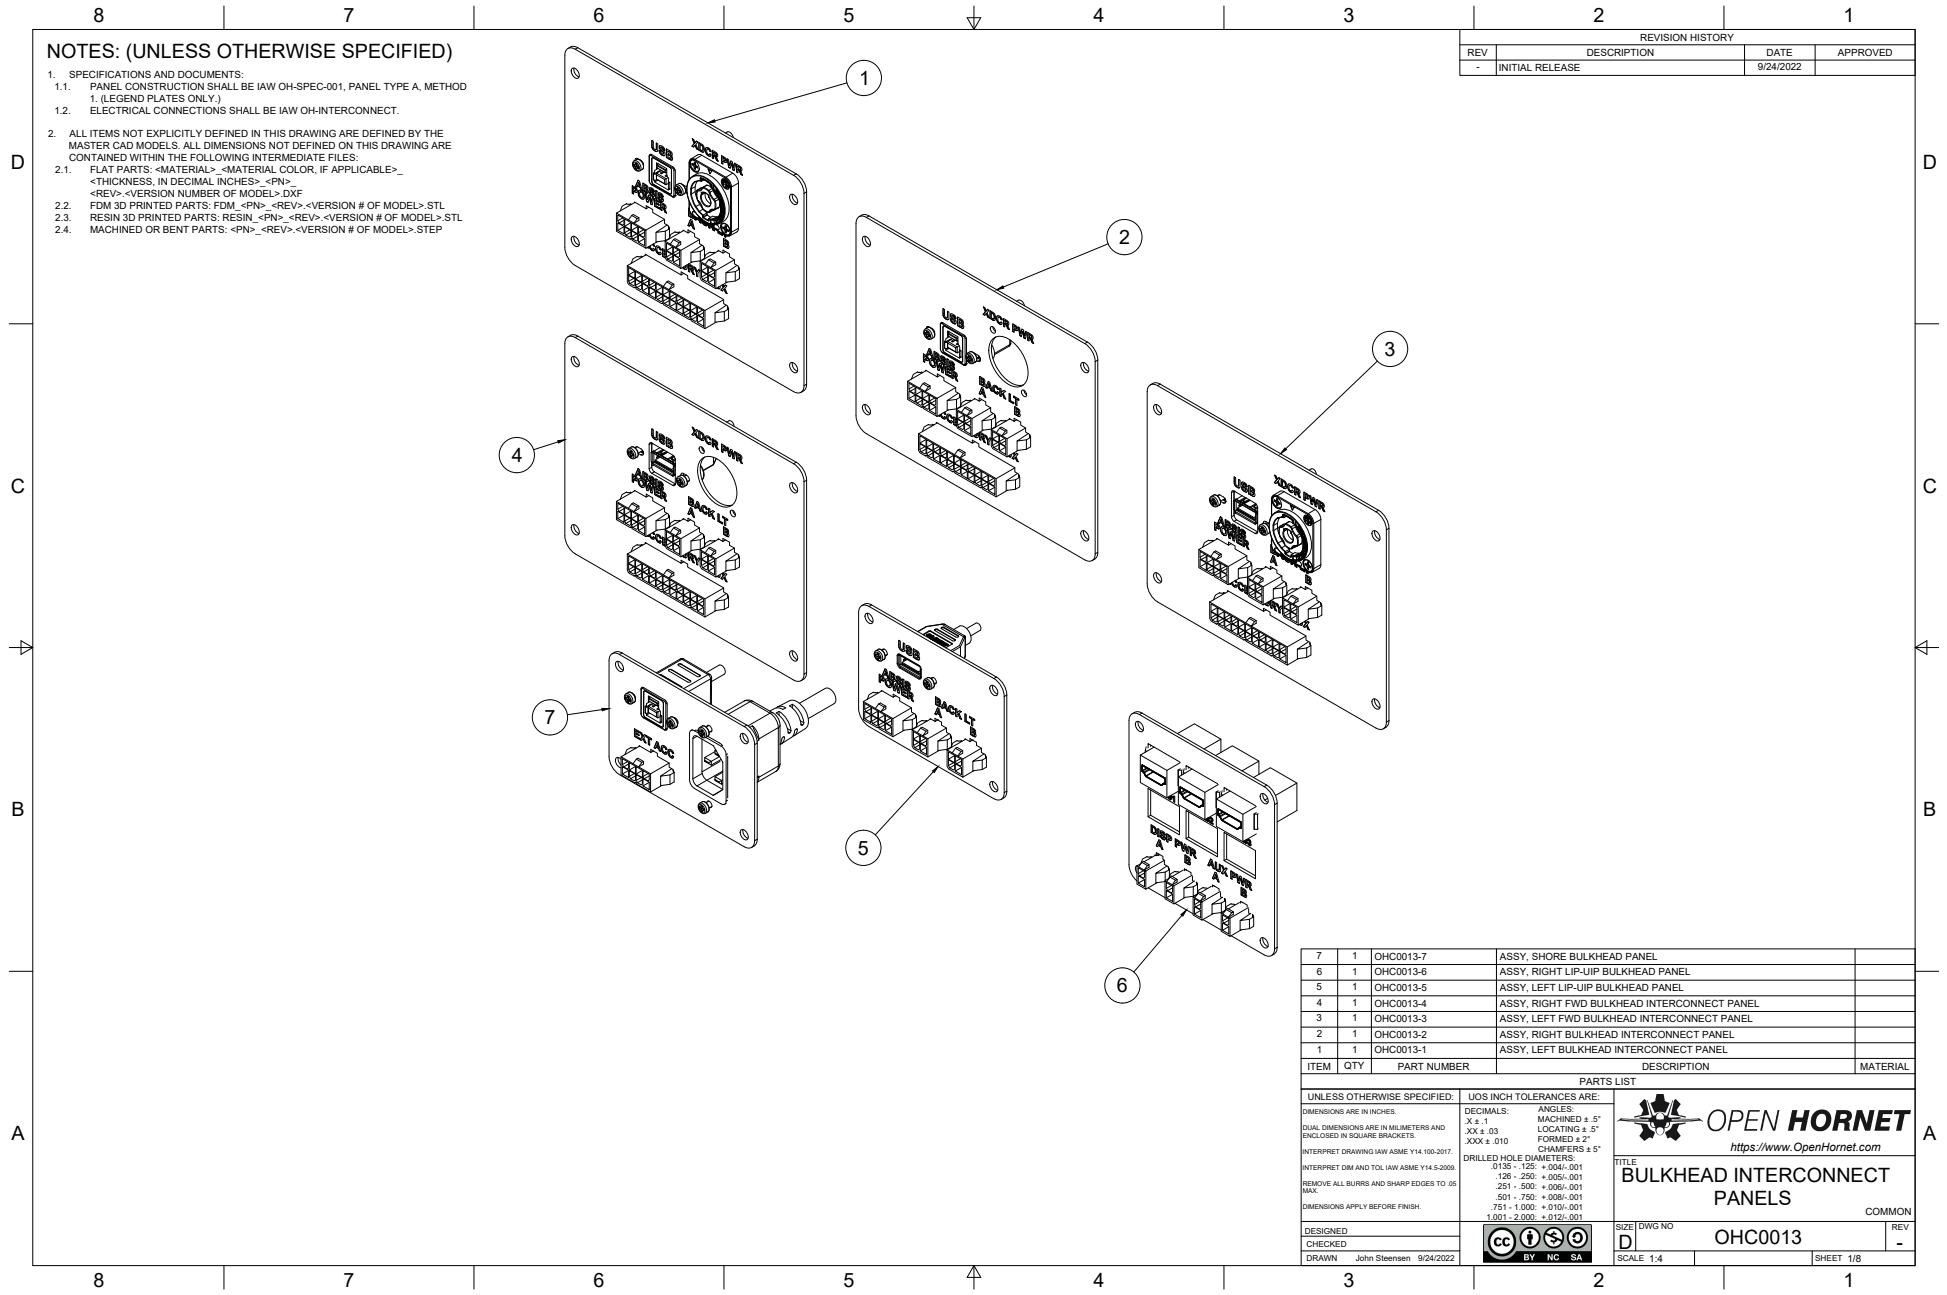
[picture p336: page 1]
SIZE DWG NO; REV; .X ± .1 .XX ± .03 .XXX ± .010; MACHINED ± .5° LOCATING ± .5° FORMED ± 2° CHAMFERS ± 5°; UNLESS OTHERWISE SPECIFIED:; UOS INCH TOLERANCES ARE:; John Steensen 9/24/2022; OHC0013; - COMMON; BULKHEAD INTERCONNECT; PARTS LIST; ITEM; QTY; PART NUMBER; DESCRIPTION; MATERIAL; OHC0013-1; ASSY, LEFT BULKHEAD INTERCONNECT PANEL; OHC0013-2; ASSY, RIGHT BULKHEAD INTERCONNECT PANEL; OHC0013-3; ASSY, LEFT FWD BULKHEAD INTERCONNECT PANEL; OHC0013-4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

NOTES: (UNLESS OTHERWISE SPECIFIED)

1. SPECIFICATIONS AND DOCUMENTS:
1.1. PANEL CONSTRUCTION SHALL BE IAW OH-SPEC-001, PANEL TYPE A, METHOD

1. (LEGEND PLATES ONLY.)

1.2. ELECTRICAL CONNECTIONS SHALL BE IAW OH-INTERCONNECT.

2. ALL ITEMS NOT EXPLICITLY DEFINED IN THIS DRAWING ARE DEFINED BY THE
MASTER CAD MODELS. ALL DIMENSIONS NOT DEFINED ON THIS DRAWING ARE
CONTAINED WITHIN THE FOLLOWING INTERMEDIATE FILES:
2.1. FLAT PARTS: <MATERIAL>_<MATERIAL COLOR, IF APPLICABLE>_

<THICKNESS, IN DECIMAL INCHES>_<PN>_
<REV>.<VERSION NUMBER OF MODEL>.DXF

2.2. FDM 3D PRINTED PARTS: FDM_<PN>_<REV>.<VERSION # OF MODEL>.STL
2.3. RESIN 3D PRINTED PARTS: RESIN_<PN>_<REV>.<VERSION # OF MODEL>.STL
2.4. MACHINED OR BENT PARTS: <PN>_<REV>.<VERSION # OF MODEL>.STEP

DIMENSIONS ARE IN INCHES.

DUAL DIMENSIONS ARE IN MILIMETERS AND
ENCLOSED IN SQUARE BRACKETS.

https://www.OpenHornet.com

INTERPRET DRAWING IAW ASME Y14.100-2017.

DRILLED HOLE DIAMETERS:

INTERPRET DIM AND TOL IAW ASME Y14.5-2009.

REMOVE ALL BURRS AND SHARP EDGES TO .05
MAX.

DIMENSIONS APPLY BEFORE FINISH.

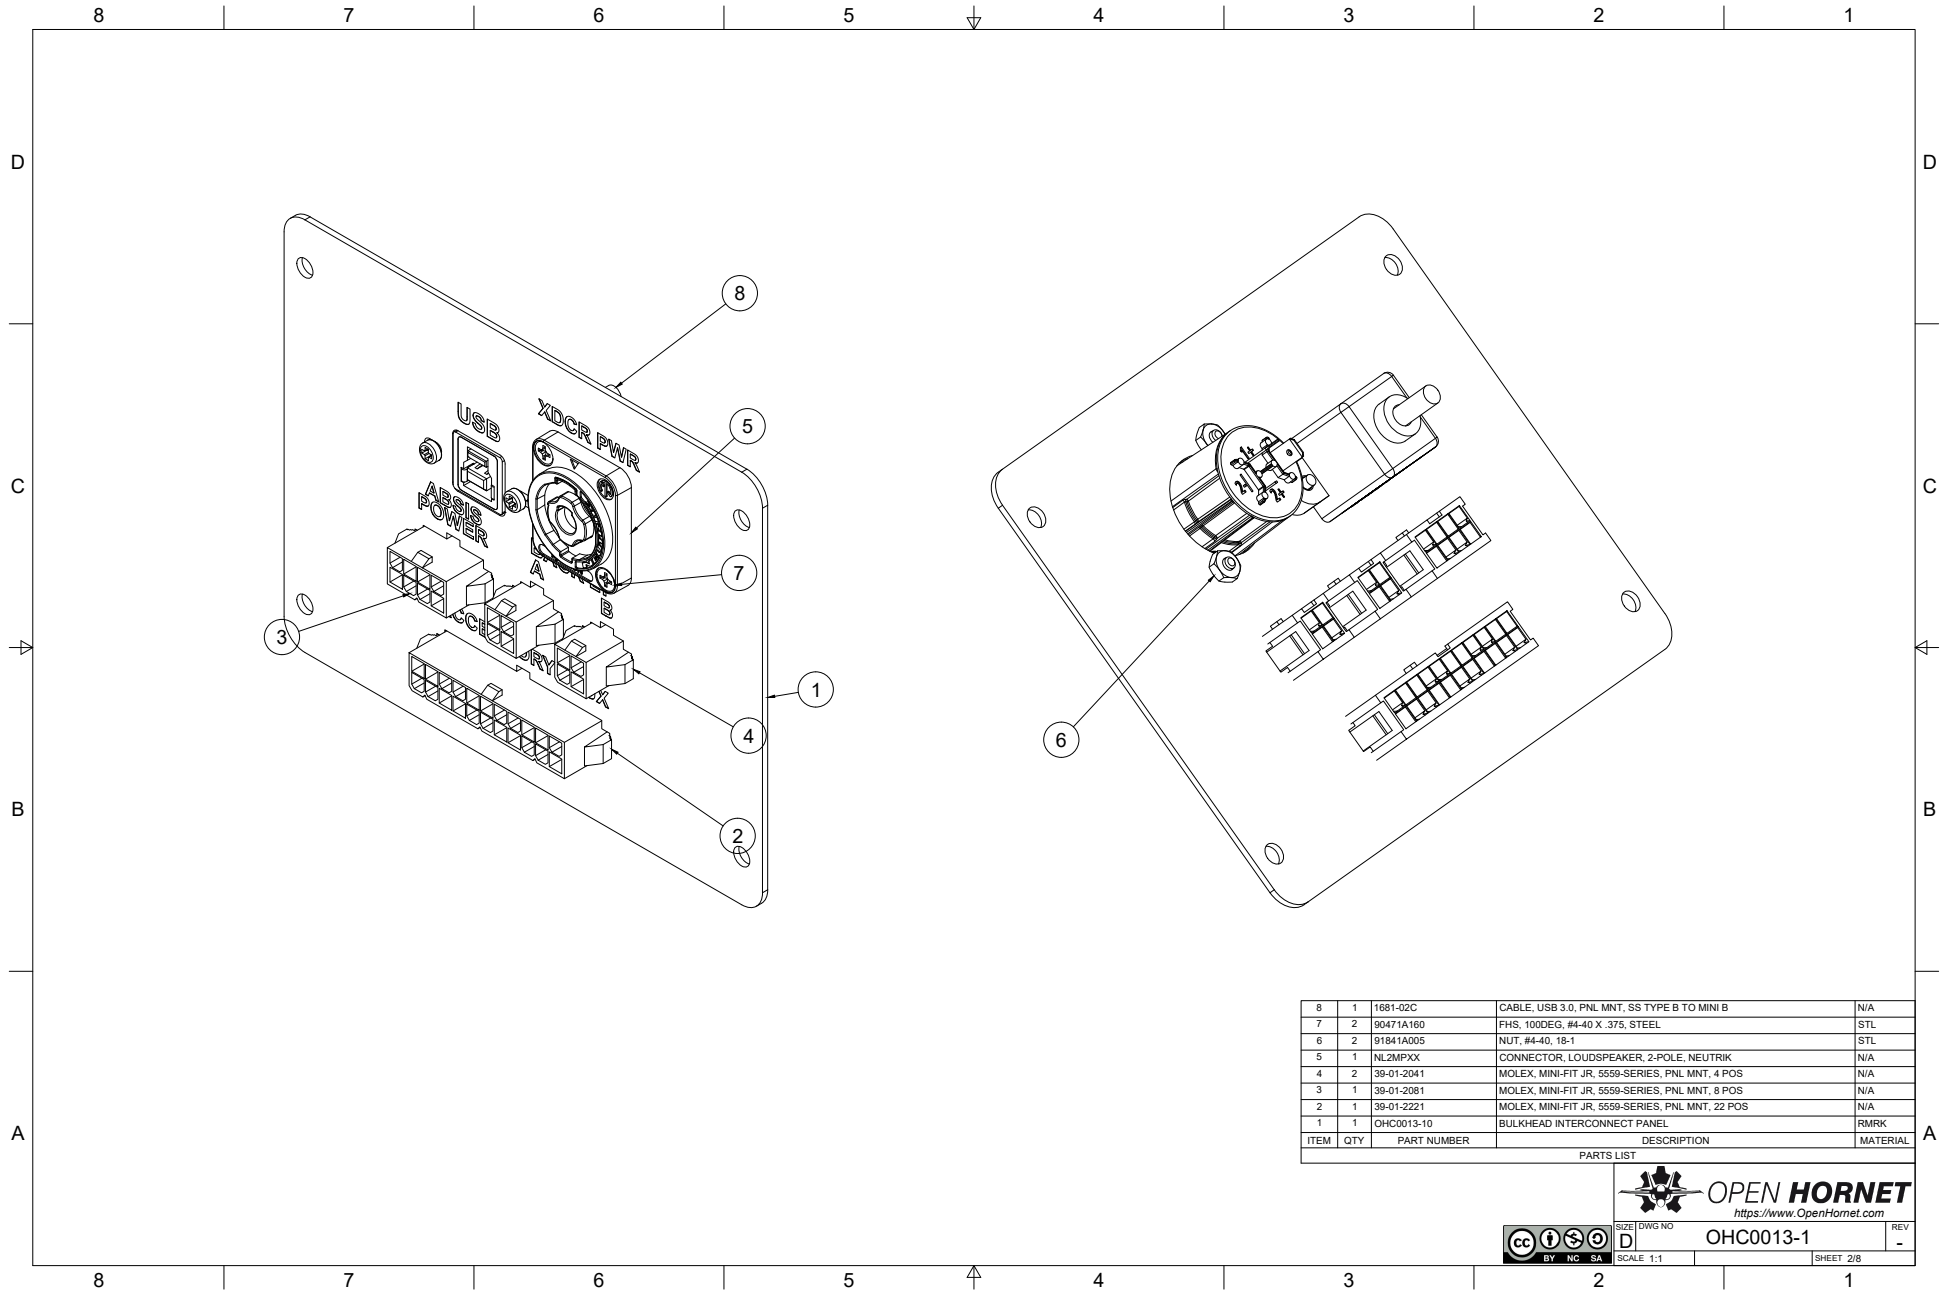
[picture p337: page 2]
PARTS LIST

8 | 1 | 1681-02C | CABLE, USB 3.0, PNL MNT, SS TYPE B TO MINI B | N/A
7 | 2 | 90471A160 | FHS, 100DEG, #4-40 X .375, STEEL | STL
6 | 2 | 91841A005 | NUT, #4-40, 18-1 | STL
5 | 1 | NL2MPXX | CONNECTOR, LOUDSPEAKER, 2-POLE, NEUTRIK | N/A
4 | 2 | 39-01-2041 | MOLEX, MINI-FIT JR, 5559-SERIES, PNL MNT, 4 POS | N/A
3 | 1 | 39-01-2081 | MOLEX, MINI-FIT JR, 5559-SERIES, PNL MNT, 8 POS | N/A
2 | 1 | 39-01-2221 | MOLEX, MINI-FIT JR, 5559-SERIES, PNL MNT, 22 POS | N/A
1 | 1 | OHC0013-10 | BULKHEAD INTERCONNECT PANEL | RMRK
ITEM | QTY | PART NUMBER | DESCRIPTION | MATERIAL

https://www.OpenHornet.com

D | OHC0013-1 | -

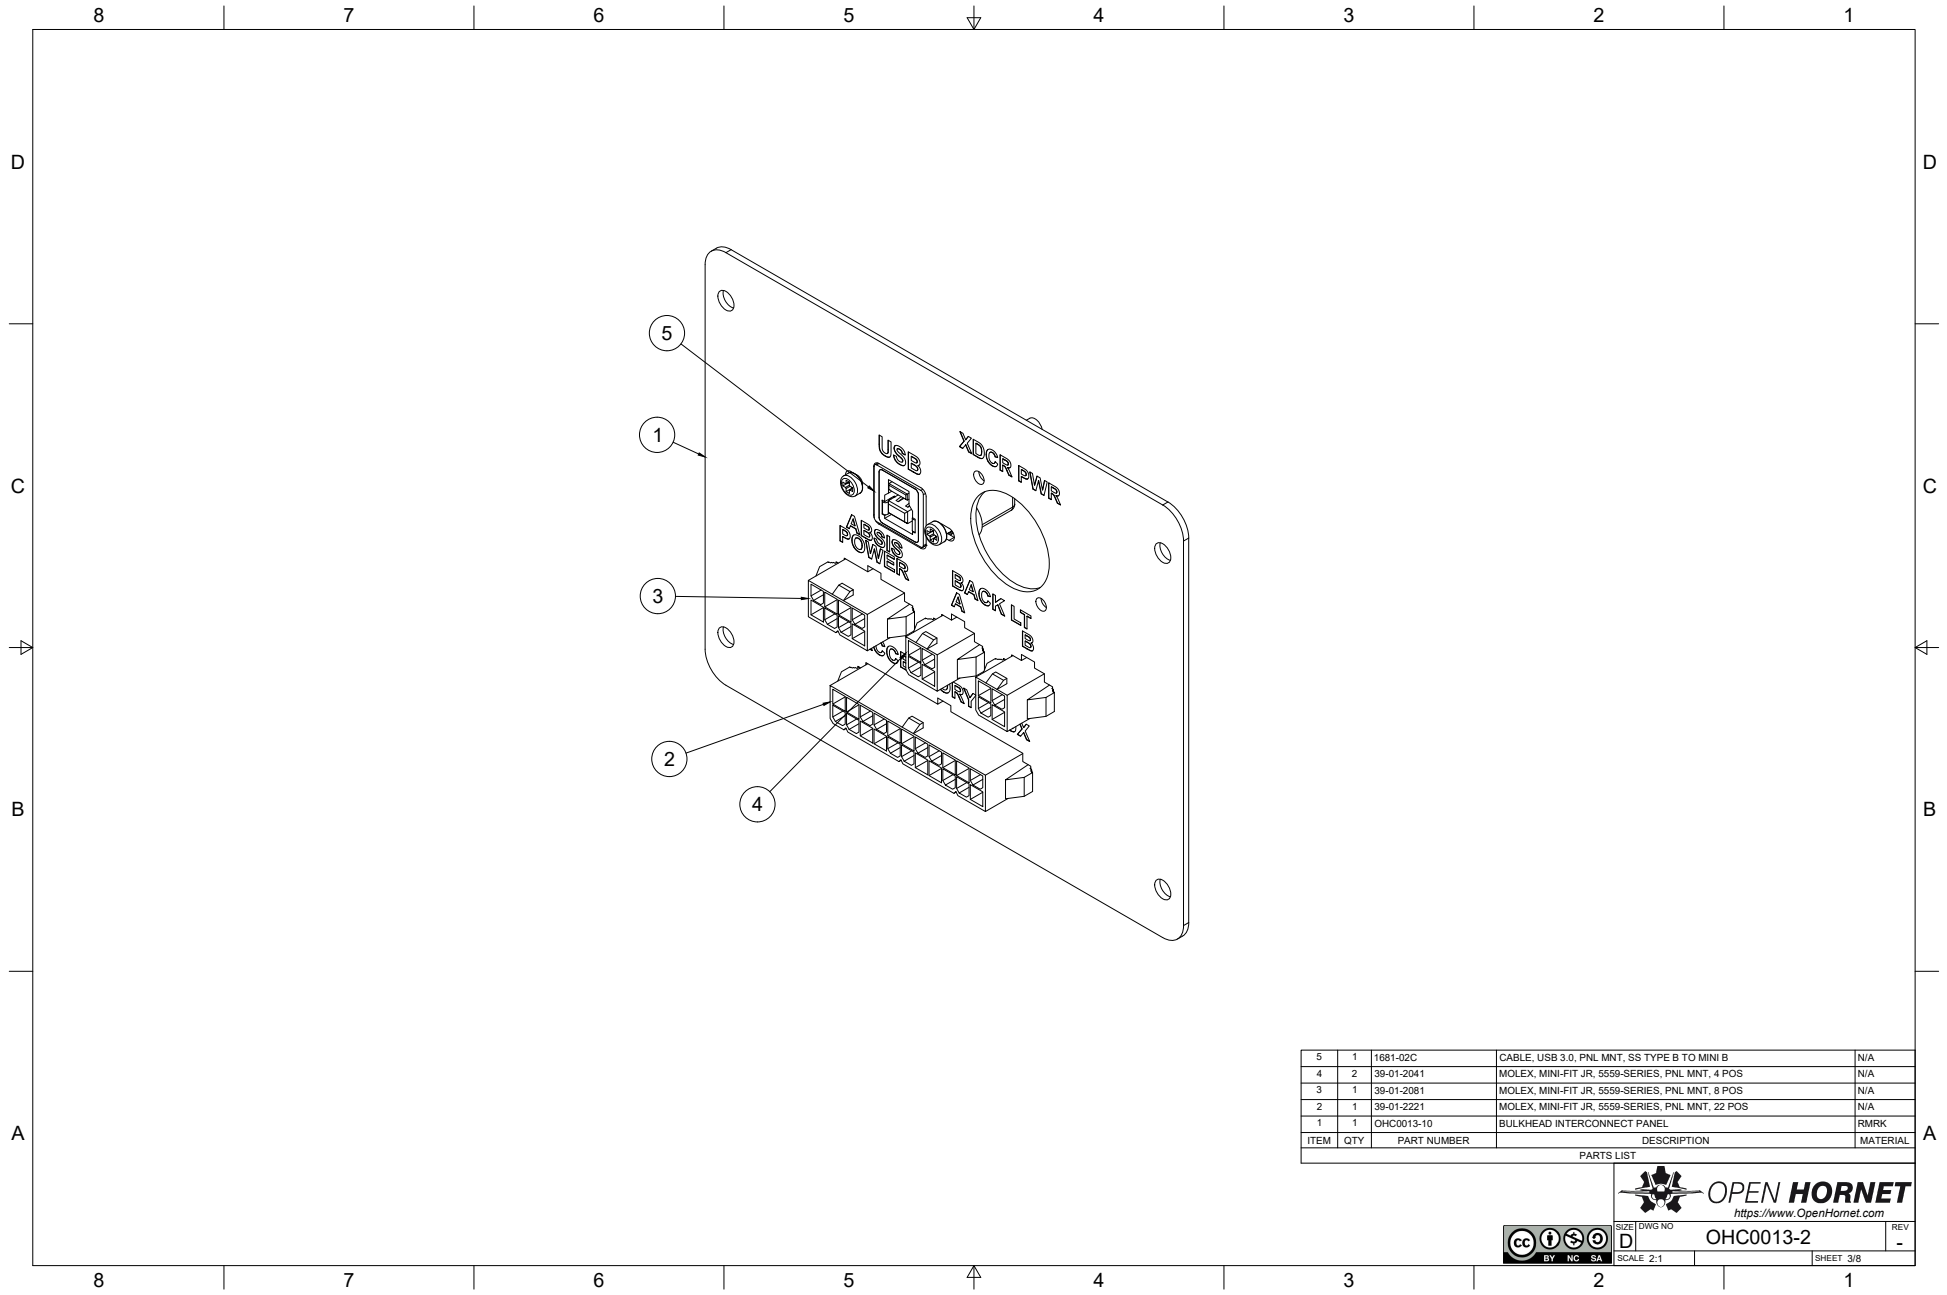
[picture p338: page 3]
PARTS LIST

5 | 1 | 1681-02C | CABLE, USB 3.0, PNL MNT, SS TYPE B TO MINI B | N/A
4 | 2 | 39-01-2041 | MOLEX, MINI-FIT JR, 5559-SERIES, PNL MNT, 4 POS | N/A
3 | 1 | 39-01-2081 | MOLEX, MINI-FIT JR, 5559-SERIES, PNL MNT, 8 POS | N/A
2 | 1 | 39-01-2221 | MOLEX, MINI-FIT JR, 5559-SERIES, PNL MNT, 22 POS | N/A
1 | 1 | OHC0013-10 | BULKHEAD INTERCONNECT PANEL | RMRK
ITEM | QTY | PART NUMBER | DESCRIPTION | MATERIAL

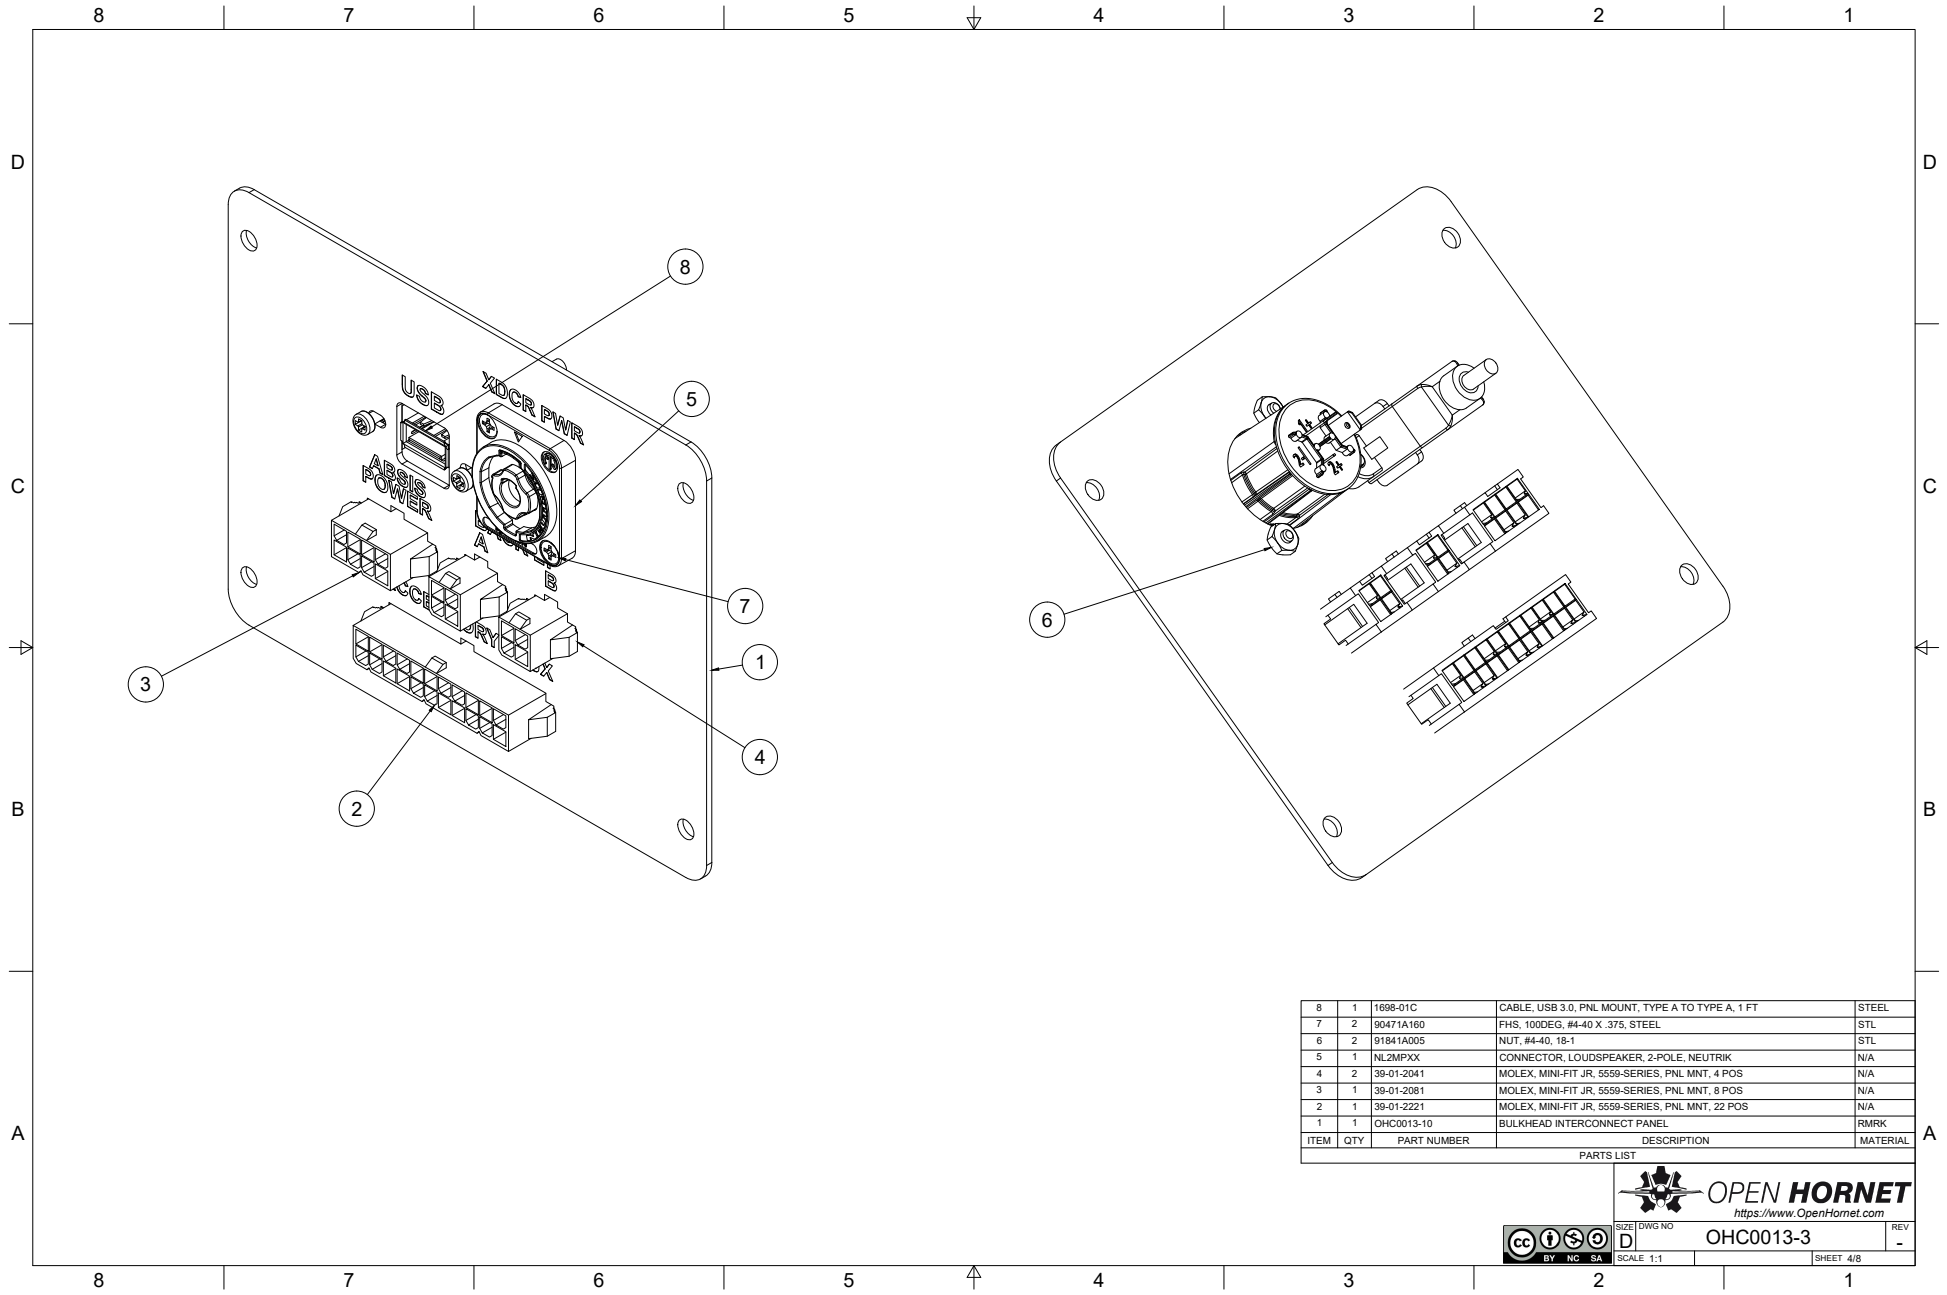
[picture p339: page 4]
PARTS LIST

8 | 1 | 1698-01C | CABLE, USB 3.0, PNL MOUNT, TYPE A TO TYPE A, 1 FT | STEEL
7 | 2 | 90471A160 | FHS, 100DEG, #4-40 X .375, STEEL | STL
6 | 2 | 91841A005 | NUT, #4-40, 18-1 | STL
5 | 1 | NL2MPXX | CONNECTOR, LOUDSPEAKER, 2-POLE, NEUTRIK | N/A
4 | 2 | 39-01-2041 | MOLEX, MINI-FIT JR, 5559-SERIES, PNL MNT, 4 POS | N/A
3 | 1 | 39-01-2081 | MOLEX, MINI-FIT JR, 5559-SERIES, PNL MNT, 8 POS | N/A
2 | 1 | 39-01-2221 | MOLEX, MINI-FIT JR, 5559-SERIES, PNL MNT, 22 POS | N/A
1 | 1 | OHC0013-10 | BULKHEAD INTERCONNECT PANEL | RMRK
ITEM | QTY | PART NUMBER | DESCRIPTION | MATERIAL

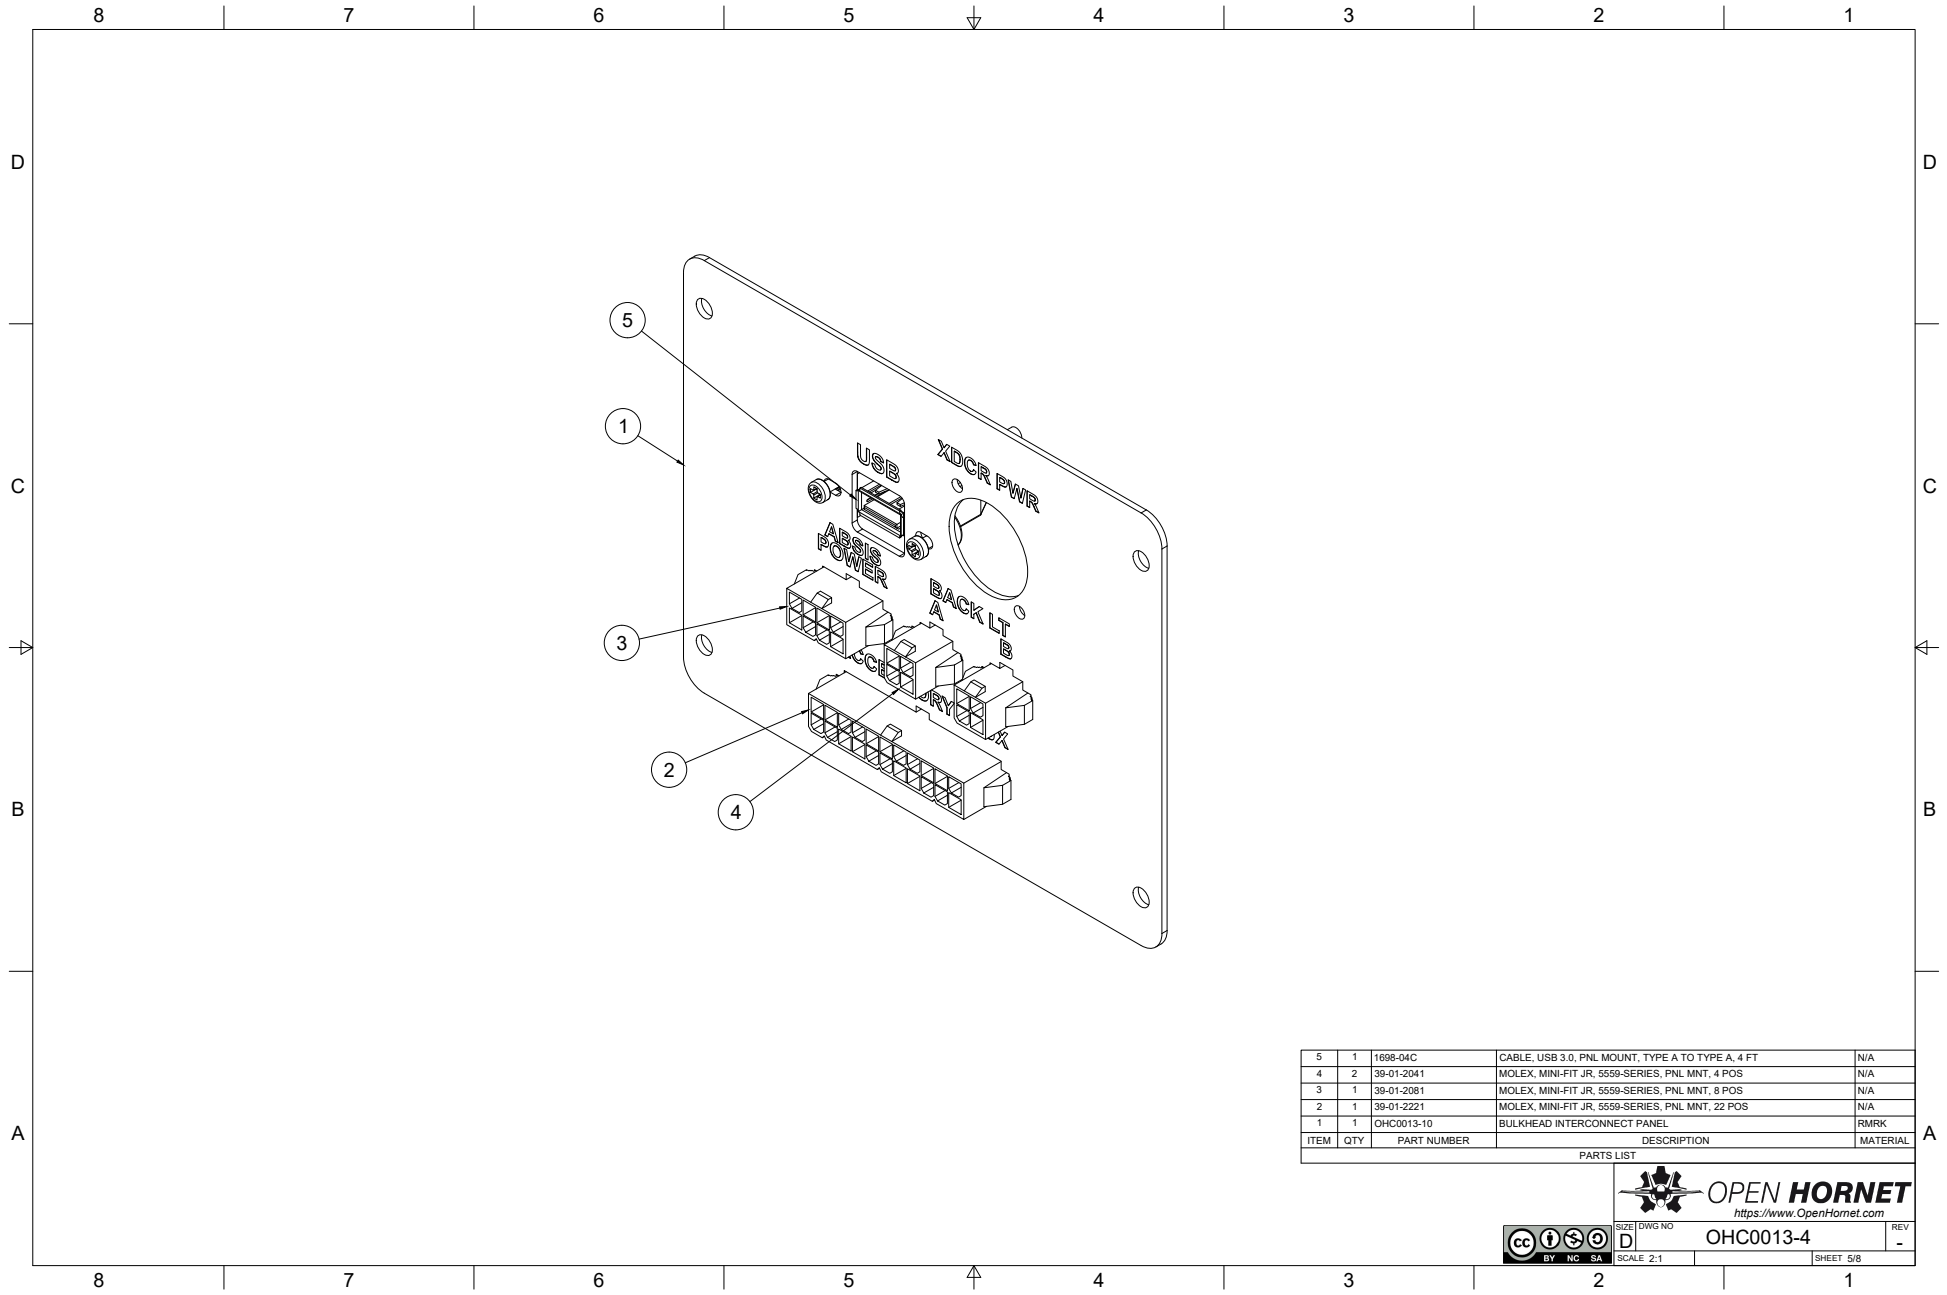
[picture p340: page 5]
PARTS LIST

5 | 1 | 1698-04C | CABLE, USB 3.0, PNL MOUNT, TYPE A TO TYPE A, 4 FT | N/A
4 | 2 | 39-01-2041 | MOLEX, MINI-FIT JR, 5559-SERIES, PNL MNT, 4 POS | N/A
3 | 1 | 39-01-2081 | MOLEX, MINI-FIT JR, 5559-SERIES, PNL MNT, 8 POS | N/A
2 | 1 | 39-01-2221 | MOLEX, MINI-FIT JR, 5559-SERIES, PNL MNT, 22 POS | N/A
1 | 1 | OHC0013-10 | BULKHEAD INTERCONNECT PANEL | RMRK
ITEM | QTY | PART NUMBER | DESCRIPTION | MATERIAL

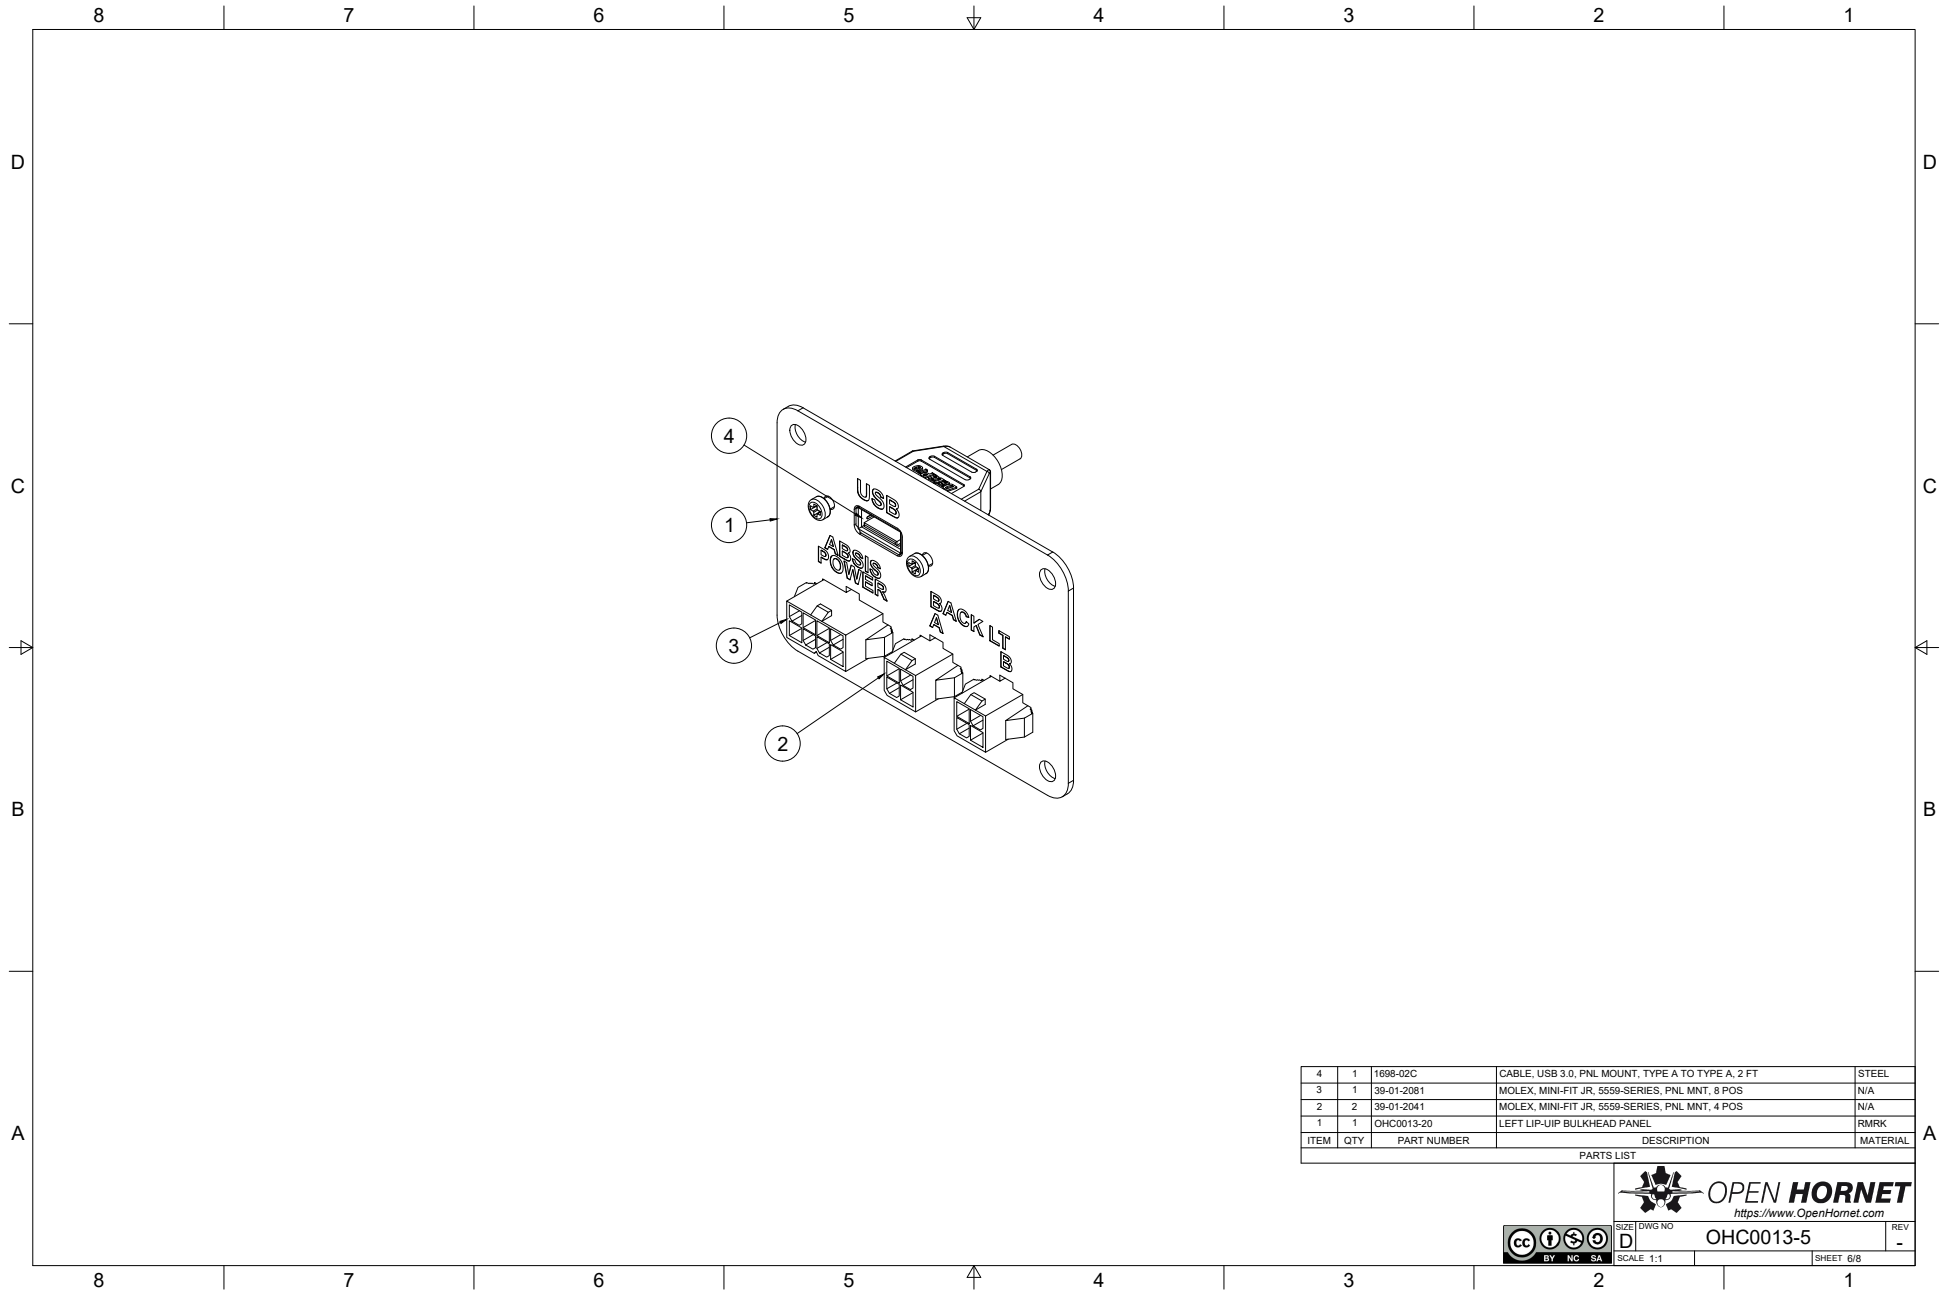
[picture p341: page 6]
PARTS LIST

4 | 1 | 1698-02C | CABLE, USB 3.0, PNL MOUNT, TYPE A TO TYPE A, 2 FT | STEEL
3 | 1 | 39-01-2081 | MOLEX, MINI-FIT JR, 5559-SERIES, PNL MNT, 8 POS | N/A
2 | 2 | 39-01-2041 | MOLEX, MINI-FIT JR, 5559-SERIES, PNL MNT, 4 POS | N/A
1 | 1 | OHC0013-20 | LEFT LIP-UIP BULKHEAD PANEL | RMRK
ITEM | QTY | PART NUMBER | DESCRIPTION | MATERIAL

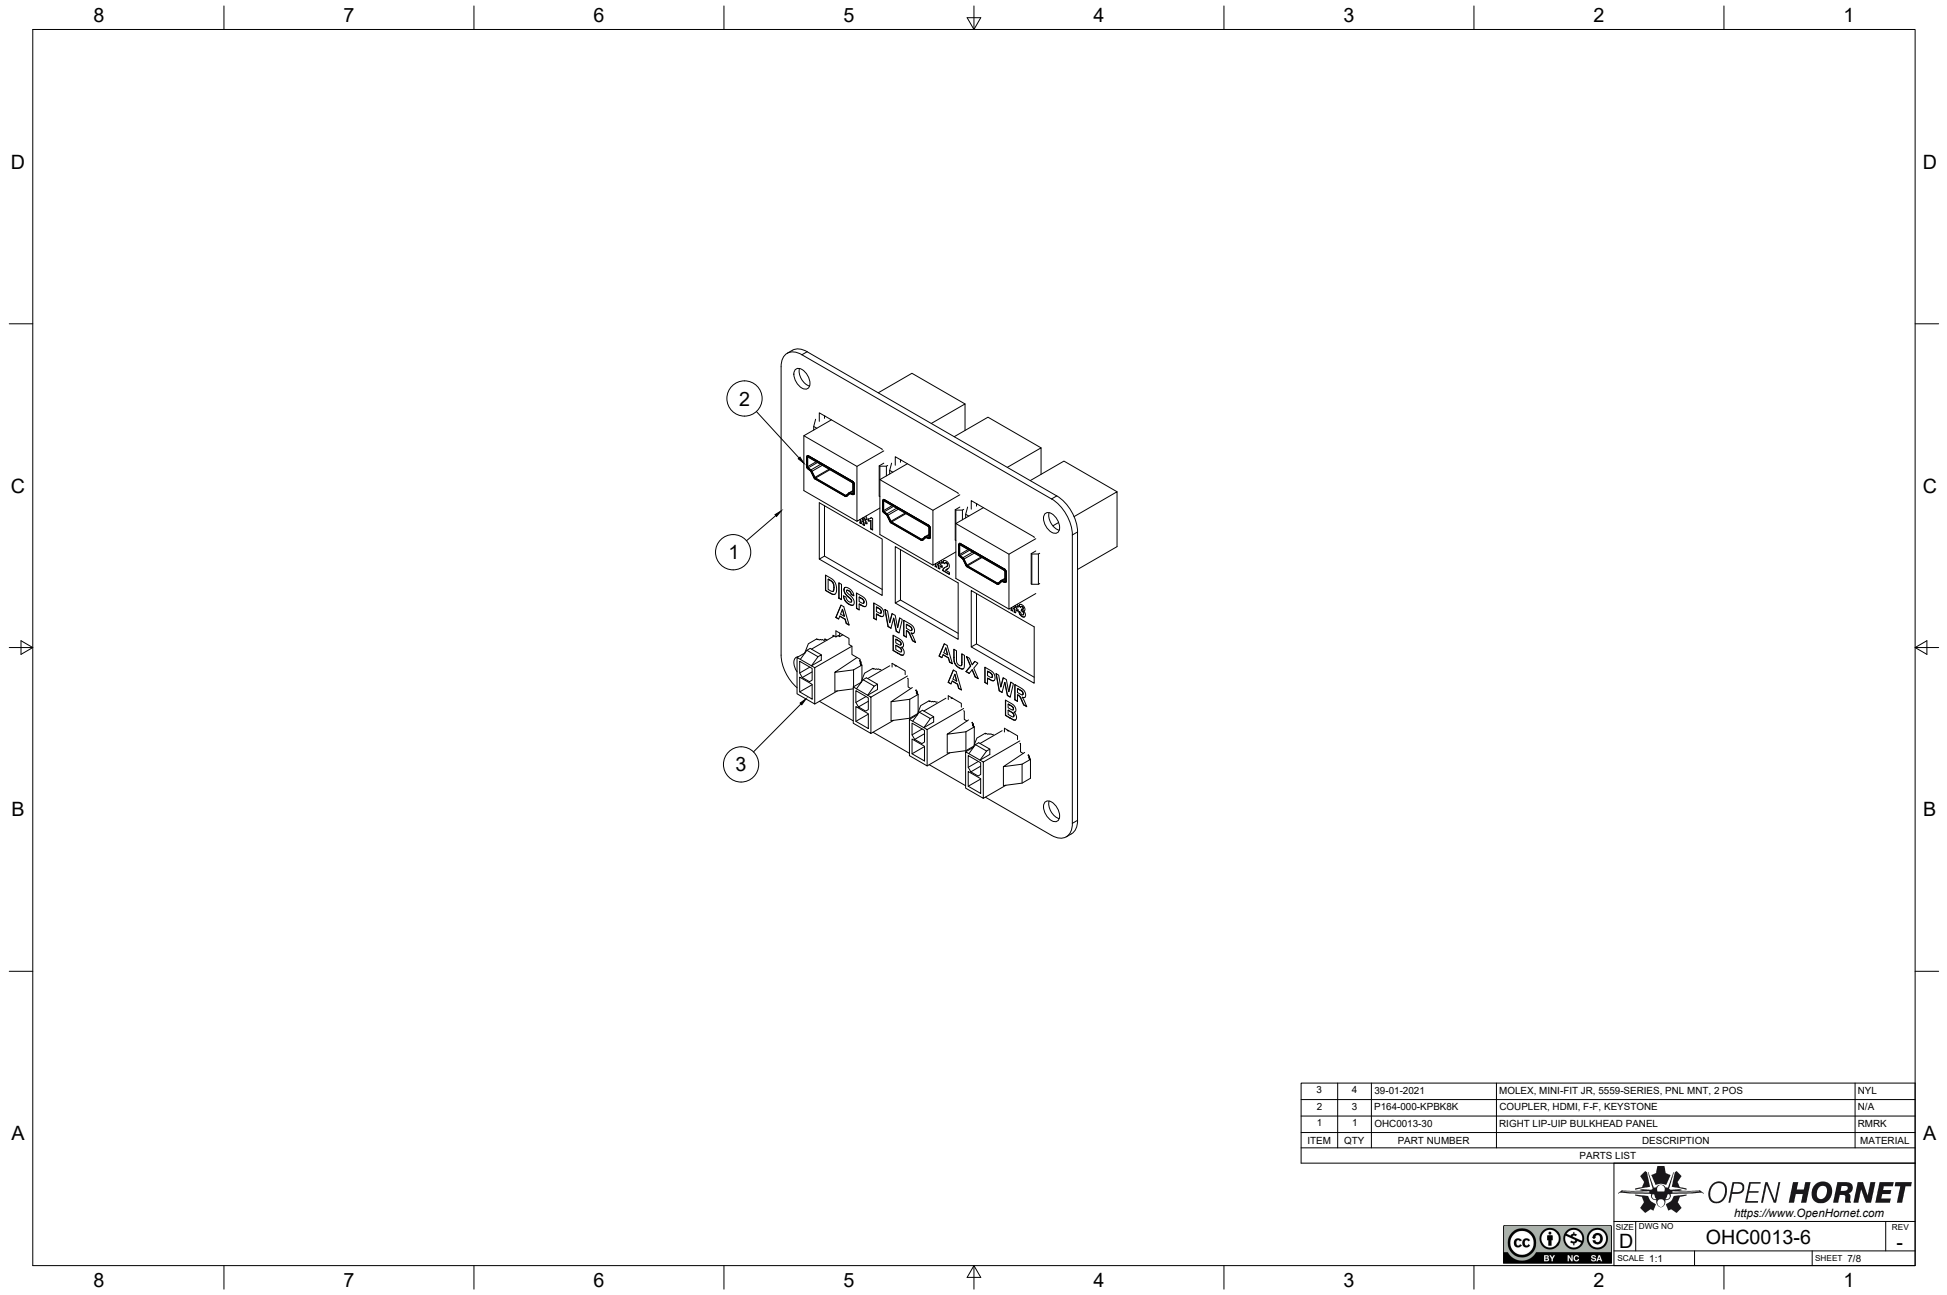
[picture p342: page 7]
PARTS LIST

3 | 4 | 39-01-2021 | MOLEX, MINI-FIT JR, 5559-SERIES, PNL MNT, 2 POS | NYL
2 | 3 | P164-000-KPBK8K | COUPLER, HDMI, F-F, KEYSTONE | N/A
1 | 1 | OHC0013-30 | RIGHT LIP-UIP BULKHEAD PANEL | RMRK
ITEM | QTY | PART NUMBER | DESCRIPTION | MATERIAL

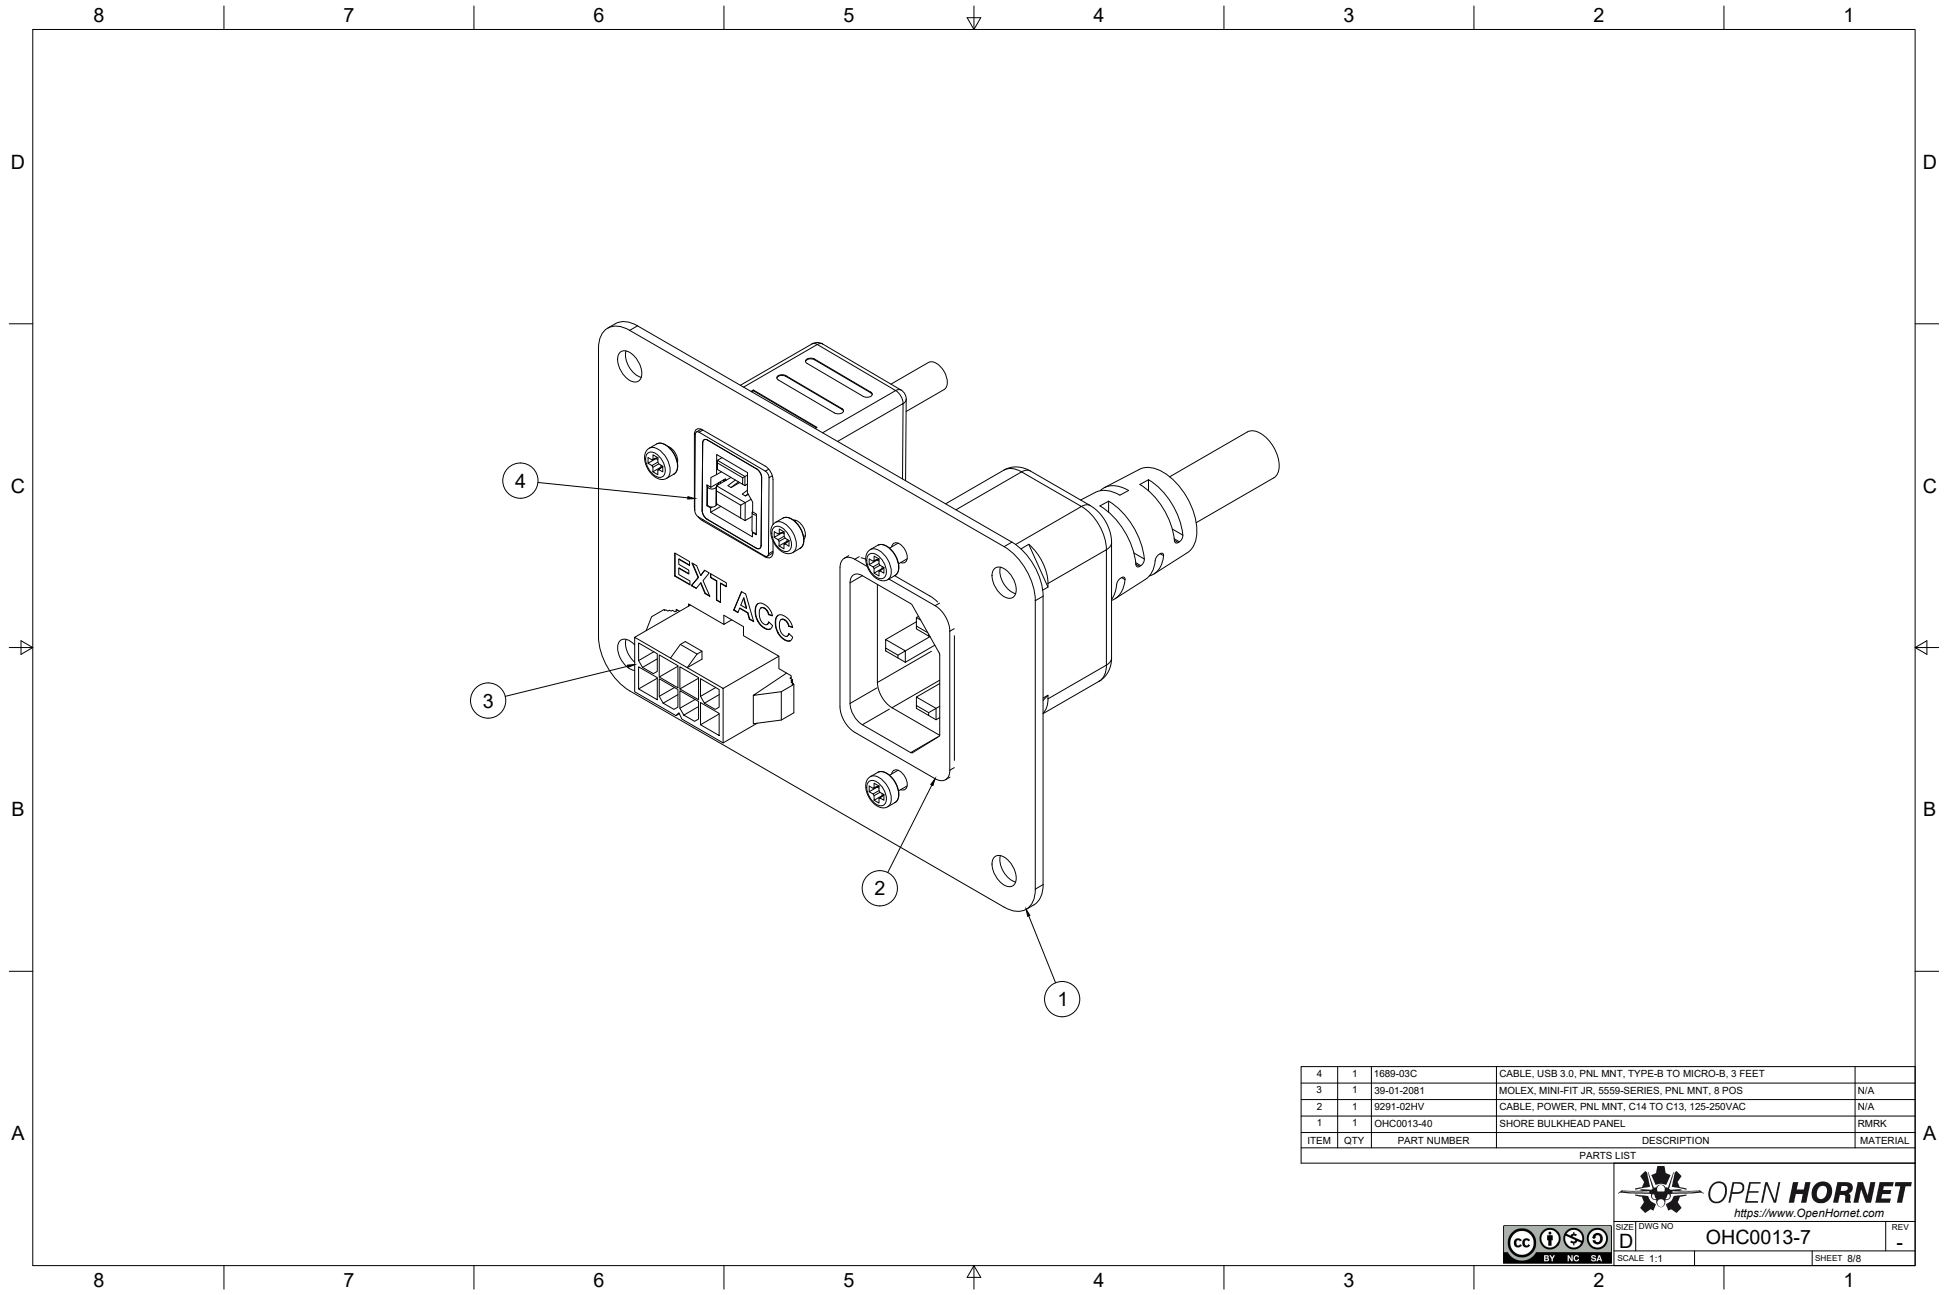
[picture p343: page 8]
PARTS LIST

4 | 1 | 1689-03C | CABLE, USB 3.0, PNL MNT, TYPE-B TO MICRO-B, 3 FEET
3 | 1 | 39-01-2081 | MOLEX, MINI-FIT JR, 5559-SERIES, PNL MNT, 8 POS | N/A
2 | 1 | 9291-02HV | CABLE, POWER, PNL MNT, C14 TO C13, 125-250VAC | N/A
1 | 1 | OHC0013-40 | SHORE BULKHEAD PANEL | RMRK
ITEM | QTY | PART NUMBER | DESCRIPTION | MATERIAL
