jrsteensen/OpenHornet/release/OH-MPL - MASTER PARTS LIST, OPENHORNET (FOR REFERENCE ONLY)_B_v19.xlsx

Sheet: Master Parts List
Part Type | (All) | SEE SHEET 1 FOR ADMIN INFORMATION AND LICENSING MARKING.
Part Name | (All)
MATERIAL | (All)
COTS Category | (All)
COTS Subcategory | (All)
Sum of QTY
Console | OH ASSY PN | SUB ASSEMBLIES | PART NUMBER | DESCRIPTION | Total
CENTER | OH3A1-1 - ASSY, CENTER TUB | (blank) | 90126A029 | WASHER, .25 X .625, STEEL, ZINC | 13
 |  |  | 91309A542 | HHCS, .25-20 X 1.00, STEEL, ZINC | 13
 |  |  | OH3A1-1 | ASSY, CENTER TUB | 1
 | OH3A1A1 - ASSY, MAIN CENTER TUB | (blank) | 3225T24 | VIBRATION-DAMPING LOOP CLAMP | 2
 |  |  | 90252A115 | FHWS, 82DEG, #8 X 1.50, STEEL, BLK, FOR MDF | 26
 |  |  | 90252A118 | FHWS, 82DEG, #8 X 2.00, STEEL, BLK, FOR MDF | 26
 |  |  | 90471A435 | FHS, 100DEG, #8-32 X .625, STEEL | 16
 |  |  | 90471A436 | FHS, 100DEG, #8-32 X 1.25, STEEL | 8
 |  |  | 91249A197 | PHS, #8-32 X .750, 18-8, BLK | 2
 |  |  | 92105A660 | INSERT, 8-32, SELF TAPPING, FOR SOFTWOOD | 28
 |  |  | 92105A675 | INSERT, .25-20, SELF TAPPING, FOR SOFTWOOD | 13
 |  |  | 98023A113 | WASHER, #8, STEEL, ZINC | 2
 |  |  | J15BF.1.15N | DRAG CHAIN, 15 X 15MM, ABS | 1
 |  |  | OH3A1-101 | CENTER TUB FLOOR | 1
 |  |  | OH3A1-102 | CENTER TUB KEYSTONE | 1
 |  |  | OH3A1-103 | CENTER TUB AFT BULKHEAD | 1
 |  |  | OH3A1-104 | CENTER TUB LEFT WALL | 1
 |  |  | OH3A1-105 | CENTER TUB RIGHT WALL | 1
 |  |  | OH3A1-106 | CENTER TUB FWD BULKHEAD | 1
 |  |  | OH3A1-107 | REAR HUMP OUTBOARD INTERNAL SUPPORT | 2
 |  |  | OH3A1-108 | REAR HUMP LATERAL STRINGER | 3
 |  |  | OH3A1-109 | SEAT MOUNT ANGLE A, .125 X 2.0 X 2.0, 6063-T52 | 2
 |  |  | OH3A1-110 | STRIP A, .50 X 2.0, 60A DUROMETER, RUBBER, ADHESIVE BACKED | 2
 |  |  | OH3A1-111 | SEAT MOUNT ANGLE B, .125 X 2.0 X 2.0, 6063-T52 | 2
 |  |  | OH3A1-112 | STRIP B, .50 X 2.0, 60A DUROMETER, RUBBER, ADHESIVE BACKED | 2
 |  |  | OH3A1A1 | ASSY, MAIN CENTER TUB | 1
 | OH3A2-1 - ASSY, EJECTION SEAT, SJU-17 | ASSY, BRIDLE CONTAINER COVER | 90252A115 | FHWS, 82DEG, #8 X 1.50, STEEL, BLK, FOR MDF | 4
 |  |  | OH3A2-20 | DROGUE BRIDLE CONTAINER | 2
 |  |  | OH3A2-23 | AFT RAIL CAP | 1
 |  |  | OH3A2-400 | ASSY, BRIDLE CONTAINER COVER | 1
 |  | ASSY, PARACHUTE CONTAINER, SJU-17 | 4280-BLACK | BRACKET, SLOTTED, INSIDE CORNER | 2
 |  |  | 60645K131 | ROD END, BALL JOINT, .3125-24 X 1.25 SHANK X .875 OAW, STEEL | 2
 |  |  | 90252A112 | FHWS, 82DEG, #8 X 1.00, STEEL, BLK, FOR MDF | 19
 |  |  | 90252A115 | FHWS, 82DEG, #8 X 1.50, STEEL, BLK, FOR MDF | 3
 |  |  | 90272A201 | PHS, #8-32 X 1.250, STEEL | 4
 |  |  | 90275A196 | FHS, 82DEG, #8-32 X .625, STEEL | 14
 |  |  | 90471A435 | FHS, 100DEG, #8-32 X .625, STEEL | 4
 |  |  | 91249A197 | PHS, #8-32 X .750, 18-8, BLK | 20
 |  |  | 91309A587 | HHCS, .3125-18 X 1.5, STEEL | 4
 |  |  | 91654A144 | SCREW NAIL, DOMED, .14 X .25 SHANK X .25 HD DIA, 18-8 | 30
 |  |  | 91841A009 | NUT, #8-32, 18-8 | 22
 |  |  | 92105A660 | INSERT, 8-32, SELF TAPPING, FOR SOFTWOOD | 6
 |  |  | 92673A119 | NUT, .3125-18, 18-8 | 4
 |  |  | 93365A140 | INSERT, 8-32, BRASS, FOR PLASTICS | 22
 |  |  | 96765A145 | WASHER, .3125 X .750 X .05 THK, 18-8, BLK | 4
 |  |  | 98023A113 | WASHER, #8, STEEL, ZINC | 28
 |  |  | OH3A2A-200 | ASSY, PARACHUTE CONTAINER, SJU-17 | 1
 |  |  | OH3A2A-201 | LOWER PARACHUTE CONTAINER BASE | 1
 |  |  | OH3A2A-202 | FWD PARACHUTE CONTAINER SUPPORT | 1
 |  |  | OH3A2A-203 | TOP PARACHUTE CONTAINER BASE | 1
 |  |  | OH3A2A-204 | LEFT SIDE PARACHUTE CONTAINER SUPPORT | 1
 |  |  | OH3A2A-205 | AFT PARACHUTE CONTAINER SUPPORT | 1
 |  |  | OH3A2A-206 | RIGHT SIDE PARACHUTE CONTAINER SUPPORT | 1
 |  |  | OH3A2A-207 | LH CANOPY BREAKER | 1
 |  |  | OH3A2A-208 | RH CANOPY BREAKER | 1
 |  |  | OH3A2A-209 | LH PARACHUTE CONTAINER LID | 1
 |  |  | 146 | RH PARACHUTE CONTAINER LID | 1
 |  |  | OH3A2A-211 | SJU-17 HEADREST A | 1
 |  |  | OH3A2A-212 | SJU-17 HEADREST D | 1
 |  |  | OH3A2A-213 | SJU-17 HEADREST C | 1
 |  |  | OH3A2A-214 | SJU-17 HEADREST B | 1
 |  |  | OH3A2A-215 | OUTSIDE PARACHUTE CONTAINER SKIN | 1
 |  |  | OH3A2A-216 | LOWER PARACHUTE CONTAINER SKIN TRIM | 1
 |  |  | OH3A2A-217 | RIGHT OUTSIDE PARACHUTE CONTAINER SKIN | 1
 |  |  | OH3A2A-218 | RIGHT LOWER PARACHUTE CONTAINER SKIN TRIM | 1
 |  |  | OH3A2A-221 | PCM PARACHUTE CONTAINER INTERFACE PLATE | 1
 |  |  | OH3A2A-222 | PCM UPPER RAIL INTERFACE PLATE | 1
 |  |  | OH3A2A-223 | PCM SUPPORT | 1
 |  | ASSY, SEAT BASE & RAILS | 90252A112 | FHWS, 82DEG, #8 X 1.00, STEEL, BLK, FOR MDF | 2
 |  |  | 90252A115 | FHWS, 82DEG, #8 X 1.50, STEEL, BLK, FOR MDF | 66
 |  |  | 90252A118 | FHWS, 82DEG, #8 X 2.00, STEEL, BLK, FOR MDF | 4
 |  |  | 90272A201 | PHS, #8-32 X 1.250, STEEL | 24
 |  |  | 90272A203 | PHS, #8-32 X 1.50, STEEL | 1
 |  |  | 90471A435 | FHS, 100DEG, #8-32 X .625, STEEL | 6
 |  |  | 91249A197 | PHS, #8-32 X .750, 18-8, BLK | 14
 |  |  | 91841A009 | NUT, #8-32, 18-8 | 1
 |  |  | 92105A660 | INSERT, 8-32, SELF TAPPING, FOR SOFTWOOD | 12
 |  |  | 92105A675 | INSERT, .25-20, SELF TAPPING, FOR SOFTWOOD | 4
 |  |  | 93365A140 | INSERT, 8-32, BRASS, FOR PLASTICS | 32
 |  |  | 96765A120 | WASHER, #8 X .375 OD, 18-8, BLACK | 6
 |  |  | 98023A113 | WASHER, #8, STEEL, ZINC | 33
 |  |  | 98381A474 | PIN, DOWEL, .125 OD X .875L, ALLOY STEEL | 2
 |  |  | 9994T91 | CASTER, FIXED, EDGE-MOUNT, 2.0 OD RBR WHEEL | 2
 |  |  | OH3A2-10 | FWD SEAT MOUNT CROSSMEMBER | 1
 |  |  | OH3A2-11 | SEAT CATAPULT | 1
 |  |  | OH3A2-12 | SEAT CATAPULT MOUNT | 1
 |  |  | OH3A2-13 | SEAT CATAPULT DETAIL RING | 2
 |  |  | OH3A2-14 | BUTTKICKER MOUNTING PLATE | 1
 |  |  | OH3A2-15 | OUTBOARD SEAT MOUNT | 1
 |  |  | OH3A2-16 | INBOARD SEAT MOUNT | 1
 |  |  | OH3A2-17 | VERTICAL MOUNTING RAIL | 1
 |  |  | OH3A2-18 | VERTICAL MOUNTING RAIL, OUTER | 1
 |  |  | OH3A2-19 | UPPER HORIZONTAL MOUNTING RAIL | 1
 |  |  | OH3A2-21 | LOWER HORIZONTAL MOUNTING RAIL | 1
 |  |  | OH3A2-22 | UPPER RAIL CAP | 1
 |  |  | OH3A2-24 | SEAT CATAPULT HORIZONTAL SUPPORT | 1
 |  |  | OH3A2-25 | SEAT REAR RAIL PLATE | 1
 |  |  | OH3A2-26 | DROGUE DEPLOYMENT MOUNT A | 2
 |  |  | OH3A2-28 | LOWER PARACHUTE DEPLOYMENT ROCKET MOUNT | 1
 |  |  | OH3A2-29 | RH OUTBOARD SEAT MOUNT | 1
 |  |  | OH3A2-30 | RH VERTICAL MOUNTING RAIL INNER | 1
 |  |  | OH3A2-300 | ASSY, SEAT BASE & RAILS | 1
 |  |  | OH3A2-31 | RH VERTICAL MOUNTING RAIL OUTER | 1
 |  |  | OH3A2-32 | RH INBOARD SEAT MOUNT | 1
 |  |  | OH3A2-35 | LH IGNITION BLOCK | 1
 |  |  | OH3A2-36 | RH IGNITION BLOCK | 1
 |  |  | OH3A2-37 | LOWER HEADREST BLOCK B | 1
 |  |  | OH3A2-38 | LOWER HEADREST BLOCK D | 1
 |  |  | OH3A2-39 | LOWER HEADREST BLOCK A | 1
 |  |  | OH3A2-40 | LOWER HEADREST BLOCK A (1) | 1
 |  |  | OH3A2-41 | SEAT HARNESS REEL | 1
 |  |  | OH3A2-42 | SEAT SEAWARS PROBE | 1
 |  |  | OH3A2-43 | LOWER HEADREST SKIN | 1
 |  | ASSY, SEAT BUCKET, SJU-17 | 91249A148 | PHS, #6-32 X .50, 18-8, BLK | 4
 |  |  | 91249A197 | PHS, #8-32 X .750, 18-8, BLK | 13
 |  |  | 96765A115 | WASHER, #6 X .375 OD, 18-8, BLACK-OXIDE | 4
 |  |  | 96765A120 | WASHER, #8 X .375 OD, 18-8, BLACK | 13
 |  |  | OH3A2A-100 | ASSY, SEAT BUCKET, SJU-17 | 1
 |  | ASSY, SEAT BUCKET, SJU-17 -> ASSY, CENTER SEAT BUCKET | 4280-BLACK | BRACKET, SLOTTED, INSIDE CORNER | 4
 |  |  | 90252A115 | FHWS, 82DEG, #8 X 1.50, STEEL, BLK, FOR MDF | 29
 |  |  | 90252A118 | FHWS, 82DEG, #8 X 2.00, STEEL, BLK, FOR MDF | 22
 |  |  | 90377A165 | WASHER, .3125 X 1.50 OD, 18-8, BLK | 4
 |  |  | 91249A060 | PHS, #2-56 X .625, 18-8, BLK | 4
 |  |  | 91249A197 | PHS, #8-32 X .750, 18-8, BLK | 8
 |  |  | 91780A035 | STANDOFF, #2-56 X 1.50, .1875 HEX, FEMALE, 6061 | 4
 |  |  | 92105A660 | INSERT, 8-32, SELF TAPPING, FOR SOFTWOOD | 17
 |  |  | 92198A692 | HHCS, .3125-18 X 2.25, PART THD, 18-8 | 4
 |  |  | 92673A119 | NUT, .3125-18, 18-8 | 4
 |  |  | 93365A130 | INSERT, 6-32, BRASS, FOR PLASTIC | 4
 |  |  | 93365A140 | INSERT, 8-32, BRASS, FOR PLASTICS | 4
 |  |  | 94070A076 | PHS, #2-56 X .1875, BRASS | 4
 |  |  | 96765A145 | WASHER, .3125 X .750 X .05 THK, 18-8, BLK | 4
 |  |  | 98023A113 | WASHER, #8, STEEL, ZINC | 8
 |  |  | OH3A2A-1000 | ASSY, CENTER SEAT BUCKET | 1
 |  |  | OH3A2A-101 | SEAT BASE | 1
 |  |  | OH3A2A-102 | UPPER SEAT BASE | 1
 |  |  | OH3A2A-103 | RIGHT OUTBOARD UPPER SEAT PAN LONGERON | 1
 |  |  | OH3A2A-105 | UPPER SEAT PAN DETAIL B | 1
 |  |  | OH3A2A-106 | UPPER SEAT PAN DETAIL C | 1
 |  |  | OH3A2A-107 | LEFT INBOARD UPPER SEAT PAN LONGERON | 1
 |  |  |  | RIGHT INBOARD UPPER SEAT PAN LONGERON | 1
 |  |  | OH3A2A-108 | LEFT THIGH SUPPORT | 1
 |  |  |  | RIGHT THIGH SUPPORT | 1
 |  |  | OH3A2A-109 | FWD UPPER SEAT PAN TRIM | 1
 |  |  | OH3A2A-110 | LEFT OUTBOARD UPPER SEAT PAN LONGERON | 1
 |  |  | OH3A2A-112 | UPPER SEAT PAN DETAIL E | 1
 |  |  | OH3A2A-115 | REAR UPPER SEAT PAN SUPPORT | 1
 |  |  | OH3A2A-116 | FWD SEAT PAN TOP SUPPORT | 1
 |  |  | OH3A2A-117 | SEAT PAN TOP | 1
 |  |  | OH3A2A-119 | SEAT BACK BASE | 1
 |  |  | OH3A2A-120 | SEAT BACK RIB A | 2
 |  |  | OH3A2A-121 | SEAT BACK RIB B | 2
 |  |  | OH3A2A-122 | RIGHT SEAT BACK DOUBLER PLATE | 1
 |  |  | OH3A2A-123 | LEFT SEAT BACK DOUBLER PLATE | 1
 |  |  | OH3A2A-124 | SEAT BACK SKIN | 1
 |  |  | OH3A2A-138 | ACCESS PANEL, SEAT PAN | 1
 |  |  | OH3A2A-140 | RIGHT KNEE GUARD SUPPORT | 1
 |  |  | OH3A2A-141 | KNEE GUARD SUPPORT BRACKET | 2
 |  |  | OH3A2A-147 | LEFT KNEE GUARD SUPPORT | 1
 |  | ASSY, SEAT BUCKET, SJU-17 -> ASSY, CENTER SEAT BUCKET -> ASSY, ABSIS ALE | ABSIS001 | ASSY, ABSIS ALE | 1
 |  |  | ABSIS001-10 | PCB, ABSIS ALE | 1
 |  |  | DEV-12640 | ARDUINO PRO MICRO, 5V, 16 MHZ, SPARKFUN | 1
 |  | ASSY, SEAT BUCKET, SJU-17 -> ASSY, EJECTION HANDLE | 3914T5 | STOP, WIRE ROPE, .1875 WIRE DIA | 4
 |  |  | 5648K33 | TUBING, .500OD X .3281 ID, 95A DUROMETER, POLYURETHANE, YELLOW | 1
 |  |  | 7658K17 | SWITCH, LIMIT, SUBMINIATURE, SNAP-ACTING, SPST | 1
 |  |  | 7856K18 | HEAT-SHRINK, .75ID SHRINK TO .375ID, POLYOLEFIN, YELLOW | 2
 |  |  | 8912T54 | ROPE, WIRE, COATED, .1875 ROPE DIA, .3125 COATING DIAMETER, BLACK | 1
 |  |  | 90126A029 | WASHER, .25 X .625, STEEL, ZINC | 6
 |  |  | 90272A079 | PHS, #2-56 X .375, STEEL | 2
 |  |  | 90272A203 | PHS, #8-32 X 1.50, STEEL | 2
 |  |  | 91078A029 | NUT, THIN, .25-20, STEEL | 2
 |  |  | 93365A110 | INSERT, 2-56, BRASS, FOR PLASTIC | 2
 |  |  | 93365A140 | INSERT, 8-32, BRASS, FOR PLASTICS | 2
 |  |  | 93365A160 | INSERT, .25-20, BRASS, FOR PLASTICS | 4
 |  |  | 95412A560 | ROD, .25-20 X 4.500, 18-8 | 2
 |  |  | 9657K332 | SPRING, COMPRESSION, 0.296 ID X 0.36 OD X 1.25 OAL X 0.27 CL, STEEL, 6.7 LBF MAX | 2
 |  |  | 98023A113 | WASHER, #8, STEEL, ZINC | 2
 |  |  | OH3A2A-1300 | ASSY, EJECTION HANDLE | 1
 |  |  | OH3A2A-142 | EJECTION HANDLE CAP SUPPORT | 1
 |  |  | OH3A2A-143 | EJECTION HANDLE CAP | 1
 |  |  | OH3A2A-144 | EJECTION HANDLE SWITCH ACTUATOR | 1
 |  |  | OH3A2A-145 | LOWER EJECTION HANDLE BASE | 1
 |  |  | OH3A2A-146 | UPPER EJECTION HANDLE BASE | 1
 |  |  | PTN0.50SS | SLEEVING, BRAIDED, SAFETY STRIPE (YELLOW-BLACK), .500 DIA, PET | 1
 |  | ASSY, SEAT BUCKET, SJU-17 -> ASSY, LEFT SEAT BUCKET | 100SP4T8B13M1QEH | SWITCH, TOGGLE, (ON)-OFF-(ON), SPDT, 18MM BAT | 1
 |  |  | 5901A122 | SPRING PLUNGER, BALL-NOSE, 8-32 HEX DRIVE | 1
 |  |  | 7658K17 | SWITCH, LIMIT, SUBMINIATURE, SNAP-ACTING, SPST | 2
 |  |  | 90471A436 | FHS, 100DEG, #8-32 X 1.25, STEEL | 7
 |  |  | 91654A144 | SCREW NAIL, DOMED, .14 X .25 SHANK X .25 HD DIA, 18-8 | 42
 |  |  | 91772A064 | PHS, #0-80 X 0.4375, 18-8 | 4
 |  |  | 91841A009 | NUT, #8-32, 18-8 | 1
 |  |  | 93365A102 | INSERT, 0-80, BRASS, FOR PLASTICS | 4
 |  |  | 93365A140 | INSERT, 8-32, BRASS, FOR PLASTICS | 8
 |  |  | HDW12 | LOCK WASHER FOR SWITCH, B13 | 1
 |  |  | HDW17 | LOCKING RING FOR SWITCH, B13 | 1
 |  |  | HDW4 | HEX NUT FOR SWITCH, 15/32-32NS | 2
 |  |  | OH3A2A-1200 | ASSY, LEFT SEAT BUCKET | 1
 |  |  | OH3A2A-126 | LEFT SEAT BUCKET SKIN | 1
 |  |  | OH3A2A-127 | SEAT HEIGHT ACTUATOR SWITCH HOUSING | 1
 |  |  | OH3A2A-128 | OUTER SHOULDER HARNESS CONTROL LEVER HOUSING | 1
 |  |  | OH3A2A-129 | INNER SHOULDER HARNESS CONTROL LEVER HOUSING | 1
 |  |  | OH3A2A-130 | SHOULDER HARNESS CONTROL LEVER | 1
 |  |  | OH3A2A-131 | SHOULDER HARNESS CONTROL LEVER HANDLE | 1
 |  | ASSY, SEAT BUCKET, SJU-17 -> ASSY, RIGHT SEAT BUCKET | 1394A230 | BRACKET, FLAT, 1.5 X 0.5 X .06, 2X #5 HOLE, STEEL | 1
 |  |  | 60645K111 (LH) | ROD END, BALL JOINT, 10-32 X .750 X .3125 ID, STEEL | 1
 |  |  | 60645K111 (RH) | ROD END, BALL JOINT, 10-32 X .750 X .3125 ID, RH, STEEL | 1
 |  |  | 60645K311 | ROD END, BALL JOINT, 10-32 FEMALE X .3125 ID, STEEL, ZINC | 2
 |  |  | 6294K432 | BEARING, SLEEVE, .3125 OD X .25 L X .375 FLANGE, NYLON | 2
 |  |  | 6516K120 | ROD, CONNECTING, 10-32 X 1.1875, 12 OAL, STEEL | 1
 |  |  | 6627K412 | BEARING, SLEEVE, .4698 OD X .25 L X .6875 FLANGE OD X .375 SHFT, PEEK | 1
 |  |  | 7658K17 | SWITCH, LIMIT, SUBMINIATURE, SNAP-ACTING, SPST | 2
 |  |  | 84835A23 | SPRING PLUNGER, BALL-NOSE, PRESS-FIT, 0.25 IN DIA, 6-13 LB FORCE | 2
 |  |  | 90272A832 | PHS, #10-32 X .875, STEEL | 1
 |  |  | 90322A639 | ROD, THREADED, 10-32 X 1.0, STEEL | 1
 |  |  | 90480A195 | NUT, #10-32, THIN, STEEL | 2
 |  |  | 90618A200 | WASHER, #4 X .250, 18-8, BLACK OXIDE, MS15795-803B | 6
 |  |  | 90969A310 | SCREW, ULTRA LOW PROFILE SHOULDER, .375 X .50 L X .3125-18 X .50 | 1
 |  |  | 91249A111 | PHS, #4-40 X .50, 18-8, BLK | 6
 |  |  | 91654A144 | SCREW NAIL, DOMED, .14 X .25 SHANK X .25 HD DIA, 18-8 | 40
 |  |  | 91771A140 | FHS, 82DEG, #2-56 X 1.00, 18-8 | 2
 |  |  | 91772A060 | PHS, #0-80 X 0.625, 18-8 | 2
 |  |  | 91772A064 | PHS, #0-80 X 0.4375, 18-8 | 2
 |  |  | 92141A011 | WASHER, #10 X .438 OD, 18-8 | 4
 |  |  | 92671A115 | NUT, #0-80, BRASS | 2
 |  |  | 92673A119 | NUT, .3125-18, 18-8 | 1
 |  |  | 92735A605 | GROOVED CLEVIS PIN, .3125 OD X .625 UL X .75 OAL, STEEL | 4
 |  |  | 92735A610 | GROOVED CLEVIS PIN, .3125 OD X .875 UL X 1.0 OAL, STEEL | 1
 |  |  | 93330A554 | STANDOFF, #10-32 X 3.50, .25 OD, FEMALE, ALUMINUM | 1
 |  |  | 93330A564 | STANDOFF, #10-32 X 4.00, .25 OD, FEMALE, ALUMINUM | 1
 |  |  | 93365A102 | INSERT, 0-80, BRASS, FOR PLASTICS | 2
 |  |  | 93365A110 | INSERT, 2-56, BRASS, FOR PLASTIC | 2
 |  |  | 93365A120 | INSERT, 4-40, BRASS, FOR PLASTICS | 6
 |  |  | 9657K328 | SPRING, COMPRESSION, .198 ID X .25 OD X 1.25OAL X .32 CL, STEEL, 5.7LBS-IN FORCE | 1
 |  |  | OH3A2A-1100 | ASSY, RIGHT SEAT BUCKET | 1
 |  |  | OH3A2A-125 | RIGHT SEAT BUCKET SKIN | 1
 |  |  | OH3A2A-132 | MANUAL OVERRIDE HANDLE | 1
 |  |  | OH3A2A-133 | SEAT ARMING LEVER | 1
 |  |  | OH3A2A-134 | MANUAL OVERRIDE HANDLE SWITCH MOUNT | 1
 |  |  | OH3A2A-135 | MANUAL OVERRIDE HANDLE MECHANISM GUARD | 1
 |  |  | OH3A2A-137 | CRANK ARM, SEAT ARMING LEVER | 1
 |  | DROGUE DEPLOYMENT CATAPULT | OH3A2-100 | DROGUE DEPLOYMENT CATAPULT | 1
 |  |  | OH3A2-101 | DROGUE DEPLOYMENT CATAPULT UPPER CAP | 1
 |  |  | OH3A2-102 | DROGUE DEPLOYMENT CATAPULT LOWER CAP | 1
 |  |  | OH3A2-103 | DROGUE DEPLOYMENT CATAPULT BODY | 1
 |  |  | OH3A2-104 | DROGUE DEPLOYMENT CATAPULT MOUNT | 2
 |  |  | OH3A2-105 | DROGUE DEPLOYMENT CASTLE NUT | 1
 |  | PARACHUTE DEPLOYMENT ROCKET | OH3A2-200 | PARACHUTE DEPLOYMENT ROCKET | 1
 |  |  | OH3A2-201 | PARACHUTE DEPLOYMENT ROCKET BODY | 1
 |  |  | OH3A2-202 | PARACHUTE DEPLOYMENT ROCKET LOWER BODY | 1
 |  |  | OH3A2-203 | PARACHUTE DEPLOYMENT ROCKET UPPER CAP | 1
 |  | (blank) | 57715K26 | KNOB, THREE-ARM, .3125-18, THRU-HOLE, PLASTIC | 4
 |  |  | 90126A029 | WASHER, .25 X .625, STEEL, ZINC | 4
 |  |  | 90377A165 | WASHER, .3125 X 1.50 OD, 18-8, BLK | 8
 |  |  | 91309A542 | HHCS, .25-20 X 1.00, STEEL, ZINC | 4
 |  |  | 91841A009 | NUT, #8-32, 18-8 | 2
 |  |  | 92198A692 | HHCS, .3125-18 X 2.25, PART THD, 18-8 | 9
 |  |  | 92673A119 | NUT, .3125-18, 18-8 | 9
 |  |  | 93085A854 | FHS, 100DEG, #8-32 X 2.00, 18-8 | 2
 |  |  | 96765A120 | WASHER, #8 X .375 OD, 18-8, BLACK | 2
 |  |  | 96765A145 | WASHER, .3125 X .750 X .05 THK, 18-8, BLK | 12
 |  |  | 98060A580 | BOLT, CARRIAGE, KNURLED-NECK, .3125-18 X 1.75L, GR5 | 4
 |  |  | BK4-4 | XDCR, BUTTKICKER ADVANCE | 1
 |  |  | OH3A2-1 | ASSY, EJECTION SEAT, SJU-17 | 1
 |  |  | OH3A2-27 | UPPER PARACHUTE DEPLOYMENT ROCKET ARM | 2
 |  |  | OH3A2-33 | SEAT PAN CUSHION | 1
 |  |  | OH3A2-34 | SEAT BACK CUSHION | 1
 |  |  | OH3A2A-9002 | DECAL, BRIDLE AND BOX | 1
 |  |  | OH3A2A-9003 | DECAL, BUCKET-SEAT ASSY | 1
 |  |  | OH3A2A-9004 | DECAL, DANGER DO NOT PULL | 1
 |  |  | OH3A2A-9005 | DECAL, DO NOT HOLD | 1
 |  |  | OH3A2A-9006 | DECAL, NACES PFCL | 1
 |  |  | OH3A2A-9007 | DECAL, PARACHUTE ASSY | 1
 |  |  | OH3A2A-9008 | DECAL, SEAT BUCKET MECH | 1
 |  |  | OH3A2A-9010 | DECAL, SEAT, AIRCRAFT EJECTION | 1
 |  |  | OH3A2A-9011 | DECAL, SEAT APPLICATION | 2
 |  |  | OH3A2A-9014 | DECAL, SURVIVAL KIT, OXYGEN, AIRCRAFT SEAT | 1
 |  |  | OH3A2A-9016 | DECAL, DROGUE ASSY | 1
 | OH3A3-1 - ASSY, FLIGHT CONTROL STICK | ASSY, SSDCT | 57445K24 | 8MM CLAMPING SHAFT COLLAR | 3
 |  |  | 90131A103 | WASHER, CUSHIONING, 0.375 ID, ABRASION-RESISTANT | 3
 |  |  | 9657K438 | 3 IN COMPRESSION SPRING | 1
 |  |  | OH3A3-20 | ASSY, SSDCT | 2
 |  | ASSY, SSDCT -> ASSY, FIXED END, SSDCT | 59935K73 | M8 8MM BALL JOINT ROD END | 1
 |  |  | 91116A160 | OVERSIZED FLAT WASHER, M8, 8.4MM ID 24MM OD | 1
 |  |  | 91828A410 | HEX NUT, M8 X 1.25 | 1
 |  |  | 92125A141 | FHCS, M3 X 0.5 MM, 35 MM LONG | 10
 |  |  | 93475A270 | 93475A270 - FLAT WASHER, M8 | 1
 |  |  | 93625A100 | NYLOC HEX NUT, M3 X 0.5 MM | 10
 |  |  | 93625A300 | NYLOC HEX NUT, M8 X 1.25MM | 1
 |  |  | 93650A155 | Cushioning Washer, 0.3125", Moisture-Resistant | 2
 |  |  | OH3A3-203 | FIXED END BASE A | 1
 |  |  | OH3A3-204 | FIXED END BASE B | 1
 |  |  | OH3A3-22 | ASSY, FIXED END, SSDCT | 1
 |  | ASSY, SSDCT -> ASSY, FIXED END, SSDCT -> ASSY, GUIDE ROD | 57485K67 | 8MM SET SCREW SHAFT COLLAR | 1
 |  |  | OH3A3-205 | ASSY, GUIDE ROD | 2
 |  |  | OH3A3-206 | ROD, 8MM X 180MM, ALU | 1
 |  | ASSY, SSDCT -> ASSY, FIXED END, SSDCT -> ASSY, THREADED STUD | 91116A160 | OVERSIZED FLAT WASHER, M8, 8.4MM ID 24MM OD | 1
 |  |  | 91828A410 | HEX NUT, M8 X 1.25 | 2
 |  |  | OH3A3-207 | ASSY, THREADED STUD | 1
 |  |  | OH3A3-208 | ROD, M8 X 75MM | 1
 |  | ASSY, SSDCT -> ASSY, PUSHROD, SMOOTH, SSDCT | 57445K24 | 8MM CLAMPING SHAFT COLLAR | 1
 |  |  | 90131A103 | WASHER, CUSHIONING, 0.375 ID, ABRASION-RESISTANT | 1
 |  |  | OH3A3-209 | ROD, 8MM X 140MM | 1
 |  |  | OH3A3-23 | ASSY, PUSHROD, SMOOTH, SSDCT | 1
 |  | ASSY, SSDCT -> ASSY, PUSHROD, THREADED, SSDCT | 5395T211 | 8MM SET SCREW SHAFT COUPLING | 1
 |  |  | 59935K73 | M8 8MM BALL JOINT ROD END | 1
 |  |  | 91828A410 | HEX NUT, M8 X 1.25 | 2
 |  |  | 93475A270 | 93475A270 - FLAT WASHER, M8 | 2
 |  |  | OH3A3-210 | ROD, M8 X 1.25 X 117.5MM, FLATTED END | 1
 |  |  | OH3A3-24 | ASSY, PUSHROD, THREADED, SSDCT | 1
 |  | ASSY, SSDCT -> ASSY, SPRING END, SSDCT | 6659K677 | 8MM OIL-EMBEDDED FLANGED SLEEVE BEARING | 1
 |  |  | 92125A132 | FHCS, M3 X 0.5 MM, 12 MM LONG | 4
 |  |  | 94180A333 | HEAT-SET INSERT, M3 X 0.50 MM | 4
 |  |  | LM8SUU | LINEAR BEARING 8MM | 2
 |  |  | OH3A3-201 | SPRING END BASE | 1
 |  |  | OH3A3-202 | SPRING END PLATE | 1
 |  |  | OH3A3-21 | ASSY, SPRING END, SSDCT | 2
 |  | ASSY, STATIC SSDCT ANCHOR | 92125A216 | FHCS, M5 X 0.8 MM, 25 MM LONG | 10
 |  |  | 93475A240 | FLAT WASHER, M5 | 10
 |  |  | 93625A200 | NYLOC HEX NUT, M5 X 0.8 MM | 10
 |  |  | OH3A3-30 | ASSY, STATIC SSDCT ANCHOR | 1
 |  |  | OH3A3-31 | BASE PLATE, SSA | 1
 |  |  | OH3A3-32 | RISER, SSA | 2
 |  |  | OH3A3-33 | TOP PLATE, SSA | 1
 |  | ASSY, STICK EXTENSION | 2960812 | F/A-18C HORNET™ HOTAS ADD-ON GRIP | 1
 |  |  | 90471A210 | FHS, 100DEG, #6-32 X .3125, STEEL | 4
 |  |  | 92095A194 | BHCS, M4 X 0.70 MM THREAD, 16 MM LONG | 2
 |  |  | 93365A130 | INSERT, 6-32, BRASS, FOR PLASTIC | 4
 |  |  | 93475A230 | FLAT WASHER, M4 | 2
 |  |  | 93625A150 | NYLOC HEX NUT, M4 X 0.7 MM | 2
 |  |  | HR10A-7P-5P | CONNECTOR, PLUG, MALE, 5P | 1
 |  |  | HR10A-7R-5S | CONNECTOR, RECEPTACLE, FEMALE, 5P | 1
 |  |  | MD-50PL100 | CONNECTOR, 5P MINI DIN RCPT, PNL MNT, 10CM LEADS | 1
 |  |  | OH3A3-40 | ASSY, STICK EXTENSION | 1
 |  |  | OH3A3-41 | STICK RISER | 1
 |  |  | OH3A3-42 | PADDLE BOX | 1
 |  |  | OH3A3-43 | PADDLE BOX COVER | 1
 |  |  | OH3A3-44 | RECEPTACLE MOUNTING CUP | 1
 |  |  | OH3A3-45 | RISER CUP MOUNT | 1
 |  | ASSY, STICK PITCH AXIS | 5862K205 | MAGNET, .50 OD X .125 THK, NEODYMIUM | 1
 |  |  | 91287A155 | HHS, M8 X 1.25 MM, 35 MM LONG | 2
 |  |  | 92095A454 | BHCS, M2 X 0.4MM, 8 MM LONG | 6
 |  |  | 92125A216 | FHCS, M5 X 0.8 MM, 25 MM LONG | 16
 |  |  | 92125A222 | FHCS, M5 X 0.8 MM, 35 MM LONG | 6
 |  |  | 92125A250 | FHCS, M6 X 1 MM, 45 MM LONG | 12
 |  |  | 93187A110 | HEX NUT, M2 X 0.4 MM, BRASS | 4
 |  |  | 93475A240 | FLAT WASHER, M5 | 10
 |  |  | 93475A250 | FLAT WASHER, M6 | 12
 |  |  | 93475A280 | FLAT WASHER, M10 | 4
 |  |  | 93625A200 | NYLOC HEX NUT, M5 X 0.8 MM | 10
 |  |  | 93625A250 | NYLOC HEX NUT, M6 X 1 MM | 12
 |  |  | 93625A300 | NYLOC HEX NUT, M8 X 1.25MM | 2
 |  |  | 95130A105 | NUT, #2-56, NARROW, BRASS | 2
 |  |  | ABSIS004-1 | PCB, HALL SENSOR, ABSIS | 1
 |  |  | KP000-10MM | 10MM PILLOW BLOCK RADIAL BALL BEARING | 2
 |  |  | OH3A3-10 | ASSY, STICK PITCH AXIS | 1
 |  |  | OH3A3-13 | BASE PLATE, SPA | 1
 |  |  | OH3A3-14 | PITCH BEARING RISER BLOCK, SPA | 2
 |  |  | OH3A3-142 | PITCH SENSOR MAGNET SPACER | 1
 |  |  | OH3A3-143 | STICK CONTROLLER MOUNT | 1
 |  | ASSY, STICK PITCH AXIS -> ASSY, LEFT PITCH DAMPER | 92095A238 | BHCS, M6 X 1MM, 16MM LONG | 1
 |  |  | 93475A270 | 93475A270 - FLAT WASHER, M8 | 6
 |  |  | KX-ZNQ-024 | MOTORCYCLE STEERING DAMPER | 1
 |  |  | KX-ZNQ-024 (PO) | DAMPER CLAMP | 1
 |  |  | OH3A3-19L | ASSY, LEFT PITCH DAMPER | 1
 |  | ASSY, STICK PITCH AXIS -> ASSY, LEFT PITCH DAMPER ANCHOR, SPA | 93475A270 | 93475A270 - FLAT WASHER, M8 | 1
 |  |  | 93625A200 | NYLOC HEX NUT, M5 X 0.8 MM | 3
 |  |  | 93625A300 | NYLOC HEX NUT, M8 X 1.25MM | 1
 |  |  | OH3A3-11 | ASSY, LEFT PITCH DAMPER ANCHOR, SPA | 1
 |  |  | OH3A3-136 | BLOCK, LEFT PITCH DAMPER ANCHOR | 1
 |  | ASSY, STICK PITCH AXIS -> ASSY, RIGHT PITCH DAMPER | 92095A238 | BHCS, M6 X 1MM, 16MM LONG | 1
 |  |  | KX-ZNQ-024 | MOTORCYCLE STEERING DAMPER | 1
 |  |  | KX-ZNQ-024 (PO) | DAMPER CLAMP | 1
 |  |  | OH3A3-19R | ASSY, RIGHT PITCH DAMPER | 1
 |  | ASSY, STICK PITCH AXIS -> ASSY, RIGHT PITCH DAMPER ANCHOR, SPA | 93475A270 | 93475A270 - FLAT WASHER, M8 | 1
 |  |  | 93625A200 | NYLOC HEX NUT, M5 X 0.8 MM | 3
 |  |  | 93625A300 | NYLOC HEX NUT, M8 X 1.25MM | 1
 |  |  | OH3A3-12 | ASSY, RIGHT PITCH DAMPER ANCHOR, SPA | 1
 |  |  | OH3A3-137 | BLOCK, RIGHT PITCH DAMPER ANCHOR | 1
 |  | ASSY, STICK PITCH AXIS -> ASSY, STICK CONTROLLER PCB | DEV-12640 | ARDUINO PRO MICRO, 5V, 16 MHZ, SPARKFUN | 1
 |  |  | OH3A3A1-1 | ASSY, STICK CONTROLLER PCB | 1
 |  |  | OH3A3A1-10 | PCB, STICK CONTROLLER | 1
 |  | ASSY, STICK PITCH AXIS -> ASSY, STICK YOKE | 6658K734 | 8MM ID, 12MM OD, 6MM LG, OIL-EMBEDDED BRONZE SLEEVE BEARING | 2
 |  |  | 91287A254 | HHS, M6 X 1 MM, 80 MM LONG | 1
 |  |  | 91292A318 | SHCS, M4 X 0.7 MM, 75 MM LONG | 14
 |  |  | 92125A130 | FHCS, M3 X 0.5 MM, 10 MM LONG | 2
 |  |  | 92125A203 | FHCS - M4 X 0.7 MM THREAD, 30 MM LONG | 6
 |  |  | 92125A373 | FHCS, M4 X 0.7 MM THREAD, 55 MM LONG | 2
 |  |  | 92981A230 | SHOULDER SCREW, M6 X 1MM, 8MM SHOULDER DIA, 80MM SHOULDER LEN | 1
 |  |  | 93475A230 | FLAT WASHER, M4 | 28
 |  |  | 93475A250 | FLAT WASHER, M6 | 2
 |  |  | 93475A270 | 93475A270 - FLAT WASHER, M8 | 2
 |  |  | 93625A150 | NYLOC HEX NUT, M4 X 0.7 MM | 14
 |  |  | 93625A250 | NYLOC HEX NUT, M6 X 1 MM | 2
 |  |  | OH3A3-100 | ASSY, STICK YOKE | 1
 |  |  | OH3A3-124 | SCISSOR STOP | 1
 |  | ASSY, STICK PITCH AXIS -> ASSY, STICK YOKE -> ASSY, AFT MAIN PLATE | 92095A194 | BHCS, M4 X 0.70 MM THREAD, 16 MM LONG | 2
 |  |  | 93475A230 | FLAT WASHER, M4 | 2
 |  |  | 93625A150 | NYLOC HEX NUT, M4 X 0.7 MM | 2
 |  |  | FRT-D2-152 | ROTARY DAMPER | 1
 |  |  | FRT-D2-152-G1 | ROTARY DAMPER WITH 12-TOOTH M1 GEAR | 1
 |  |  | OH3A3-122 | ASSY, AFT MAIN PLATE | 1
 |  | ASSY, STICK PITCH AXIS -> ASSY, STICK YOKE -> ASSY, AFT MAIN PLATE -> ASSY, FWD MAIN PLATE | 608-2RS | 8X22X7 SEALED RADIAL BALL BEARING | 1
 |  |  | 92125A192 | FHCS, M4 X 0.7 MM, 12 MM LONG | 3
 |  |  | OH3A3-119 | ASSY, FWD MAIN PLATE | 1
 |  |  | OH3A3-120 | MAIN PLATE | 1
 |  |  | OH3A3-121 | BEARING PLATE | 1
 |  | ASSY, STICK PITCH AXIS -> ASSY, STICK YOKE -> ASSY, FWD PLATE | 5862K205 | MAGNET, .50 OD X .125 THK, NEODYMIUM | 1
 |  |  | 92095A194 | BHCS, M4 X 0.70 MM THREAD, 16 MM LONG | 2
 |  |  | FRT-D2-152 | ROTARY DAMPER | 1
 |  |  | FRT-D2-152-G1 | ROTARY DAMPER WITH 12-TOOTH M1 GEAR | 1
 |  |  | OH3A3-118 | ASSY, FWD PLATE | 1
 |  |  | OH3A3-152 | ROLL AXIS DAMPER EXTENDED GEAR | 1
 |  |  | OH3A3-153 | ROLL AXIS MAGNET CUP | 1
 |  | ASSY, STICK PITCH AXIS -> ASSY, STICK YOKE -> ASSY, FWD PLATE -> ASSY, FWD MAIN PLATE | 608-2RS | 8X22X7 SEALED RADIAL BALL BEARING | 1
 |  |  | 92125A192 | FHCS, M4 X 0.7 MM, 12 MM LONG | 3
 |  |  | OH3A3-119 | ASSY, FWD MAIN PLATE | 1
 |  |  | OH3A3-120 | MAIN PLATE | 1
 |  |  | OH3A3-121 | BEARING PLATE | 1
 |  | ASSY, STICK PITCH AXIS -> ASSY, STICK YOKE -> ASSY, FWD PLATE -> ASSY, ROLL SENSOR | 92095A454 | BHCS, M2 X 0.4MM, 8 MM LONG | 4
 |  |  | 93187A110 | HEX NUT, M2 X 0.4 MM, BRASS | 4
 |  |  | 94180A351 | SCREW-TO-EXPAND INSERT, M2 X 0.4MM | 2
 |  |  | ABSIS004-1 | PCB, HALL SENSOR, ABSIS | 1
 |  |  | OH3A3-123 | ASSY, ROLL SENSOR | 1
 |  |  | OH3A3-150 | ROLL SENSOR MOUNT | 1
 |  | ASSY, STICK PITCH AXIS -> ASSY, STICK YOKE -> ASSY, MAIN CASING | 57485K68 | 10 MM CARBON STEEL SET SCREW SHAFT COLLAR | 3
 |  |  | 92015A121 | SET SCREW, M5 X 0.8 MM, 10 MM LONG | 3
 |  |  | 92125A205 | FHCS, M4 X 0.7 MM THREAD, 40 MM LONG | 2
 |  |  | OH3A3-101 | ASSY, MAIN CASING | 1
 |  |  | OH3A3-106 | ROD, PITCH AXIS | 1
 |  | ASSY, STICK PITCH AXIS -> ASSY, STICK YOKE -> ASSY, MAIN CASING -> ASSY, MAIN CASING A | 93625A150 | NYLOC HEX NUT, M4 X 0.7 MM | 2
 |  |  | OH3A3-102 | ASSY, MAIN CASING A | 1
 |  |  | OH3A3-103 | MAIN CASING A | 1
 |  | ASSY, STICK PITCH AXIS -> ASSY, STICK YOKE -> ASSY, MAIN CASING -> ASSY, MAIN CASING B | 93625A150 | NYLOC HEX NUT, M4 X 0.7 MM | 4
 |  |  | OH3A3-104 | ASSY, MAIN CASING B | 1
 |  |  | OH3A3-105 | MAIN CASING B | 1
 |  | ASSY, STICK PITCH AXIS -> ASSY, STICK YOKE -> ASSY, MAIN CASING -> STUD, SPRING DAMPER | 91116A160 | OVERSIZED FLAT WASHER, M8, 8.4MM ID 24MM OD | 1
 |  |  | 91287A307 | HHS, M8 X 1.25 MM THREAD, 45 MM LONG | 1
 |  |  | OH3A3-107 | STUD, SPRING DAMPER | 4
 |  | ASSY, STICK PITCH AXIS -> ASSY, STICK YOKE -> ASSY, PIVOTING STICK RISER MOUNT | 6658K736 | 8MM ID, 12MM OD, 16MM LG, OIL-EMBEDDED SAE 841 BRONZE SLEEVE BEARING | 1
 |  |  | 92125A130 | FHCS, M3 X 0.5 MM, 10 MM LONG | 4
 |  |  | 92125A204 | FHCS, M4 X 0.7 MM THREAD, 35 MM LONG | 2
 |  |  | OH3A3-108 | ASSY, PIVOTING STICK RISER MOUNT | 1
 |  |  | OH3A3-109 | MID PLATE | 1
 |  |  | OH3A3-114 | PIVOT TOP PLATE | 1
 |  | ASSY, STICK PITCH AXIS -> ASSY, STICK YOKE -> ASSY, PIVOTING STICK RISER MOUNT -> ASSY, PIVOT BLOCK A | 93625A150 | NYLOC HEX NUT, M4 X 0.7 MM | 1
 |  |  | 94180A331 | HEAT-SET INSERT, M3 X 0.50 MM | 2
 |  |  | 94180A351 | SCREW-TO-EXPAND INSERT, M2 X 0.4MM | 1
 |  |  | OH3A3-110 | ASSY, PIVOT BLOCK A | 1
 |  |  | OH3A3-111 | PIVOT BLOCK A | 1
 |  | ASSY, STICK PITCH AXIS -> ASSY, STICK YOKE -> ASSY, PIVOTING STICK RISER MOUNT -> ASSY, PIVOT BLOCK B | 93625A150 | NYLOC HEX NUT, M4 X 0.7 MM | 3
 |  |  | 94180A331 | HEAT-SET INSERT, M3 X 0.50 MM | 2
 |  |  | 94180A351 | SCREW-TO-EXPAND INSERT, M2 X 0.4MM | 1
 |  |  | OH3A3-112 | ASSY, PIVOT BLOCK B | 1
 |  |  | OH3A3-113 | PIVOT BLOCK B | 1
 |  | ASSY, STICK PITCH AXIS -> ASSY, STICK YOKE -> ASSY, ROLL DAMPER ARM A | 94180A331 | HEAT-SET INSERT, M3 X 0.50 MM | 1
 |  |  | OH3A3-115 | ASSY, ROLL DAMPER ARM A | 1
 |  |  | OH3A3-116 | ROLL DAMPER ARM A | 1
 |  | ASSY, STICK PITCH AXIS -> ASSY, STICK YOKE -> ASSY, ROLL DAMPER ARM B | 94180A331 | HEAT-SET INSERT, M3 X 0.50 MM | 1
 |  |  | OH3A3-117 | ASSY, ROLL DAMPER B | 1
 |  |  | OH3A3-118 | ROLL DAMPER ARM B | 1
 |  | ASSY, STICK PITCH AXIS -> ASSY, STICK YOKE -> ASSY, SCISSORS | 92095A223 | BHCS M5 X 0.80 MM THREAD, 45 MM LONG | 2
 |  |  | 93475A240 | FLAT WASHER, M5 | 6
 |  |  | 93625A200 | NYLOC HEX NUT, M5 X 0.8 MM | 2
 |  |  | 9654K421 | 1.75" Long, 0.5" OD, 0.055" WD Steel Extension Spring with Loop Ends | 3
 |  |  | OH3A3-125 | ASSY, SCISSORS | 1
 |  |  | OH3A3-135 | SCISSOR SPRING SPACER | 4
 |  | ASSY, STICK PITCH AXIS -> ASSY, STICK YOKE -> ASSY, SCISSORS -> ASSY, SCISSOR ARM A | 6659K115 | 8MM ID, 12MM OD, 6MM LG, OIL-EMBEDDED FLANGED SLEEVE BEARING | 2
 |  |  | 92095A205 | BHCS, M4 X 0.7 MM THREAD, 45MM LONG | 2
 |  |  | 93475A230 | FLAT WASHER, M4 | 6
 |  |  | 93625A150 | NYLOC HEX NUT, M4 X 0.7 MM | 2
 |  |  | OH3A3-131 | SCISSOR CUSHION (1374N12) | 1
 |  |  | OH3A3-132 | ASSY, SCISSOR ARM A | 1
 |  |  | OH3A3-133 | SCISSOR ARM A LINK | 2
 |  |  | OH3A3-134 | SCISSOR ARM A BLOCK | 1
 |  | ASSY, STICK PITCH AXIS -> ASSY, STICK YOKE -> ASSY, SCISSORS -> ASSY, SCISSOR ARM B | 6659K115 | 8MM ID, 12MM OD, 6MM LG, OIL-EMBEDDED FLANGED SLEEVE BEARING | 2
 |  |  | 92095A205 | BHCS, M4 X 0.7 MM THREAD, 45MM LONG | 2
 |  |  | 93475A230 | FLAT WASHER, M4 | 6
 |  |  | 93625A150 | NYLOC HEX NUT, M4 X 0.7 MM | 2
 |  |  | OH3A3-126 | ASSY, SCISSOR ARM B | 1
 |  |  | OH3A3-127 | SCISSOR ARM B LINK UPPER | 2
 |  |  | OH3A3-128 | SCISSOR ARM B LINK SPACER | 2
 |  |  | OH3A3-129 | SCISSOR ARM B LINK LOWER | 2
 |  |  | OH3A3-130 | SCISSOR ARM B BLOCK | 1
 |  |  | OH3A3-131 | SCISSOR CUSHION (1374N12) | 1
 |  | ASSY, STICK PITCH AXIS -> ASSY, TRAVEL STOP, AFT LEFT | 91292A129 | SHCS, M5X0.8, 25MM, 18-8 | 1
 |  |  | 91828A241 | HEX NUT, M5 X 0.8 MM | 2
 |  |  | 93625A200 | NYLOC HEX NUT, M5 X 0.8 MM | 1
 |  |  | 9540K922 | UNTHREADED BUMPER M5 | 1
 |  |  | OH3A3-138 | TRAVEL STOP, AFT LEFT | 1
 |  |  | OH3A3-15 | ASSY, TRAVEL STOP, AFT LEFT | 1
 |  | ASSY, STICK PITCH AXIS -> ASSY, TRAVEL STOP, AFT RIGHT | 91292A129 | SHCS, M5X0.8, 25MM, 18-8 | 1
 |  |  | 91828A241 | HEX NUT, M5 X 0.8 MM | 2
 |  |  | 93625A200 | NYLOC HEX NUT, M5 X 0.8 MM | 1
 |  |  | 9540K922 | UNTHREADED BUMPER M5 | 1
 |  |  | OH3A3-139 | TRAVEL STOP, AFT RIGHT | 1
 |  |  | OH3A3-16 | ASSY, TRAVEL STOP, AFT RIGHT | 1
 |  | ASSY, STICK PITCH AXIS -> ASSY, TRAVEL STOP, FWD LEFT | 91292A126 | SHCS, M5X0.8, 16MM, 18-8 | 1
 |  |  | 91828A241 | HEX NUT, M5 X 0.8 MM | 1
 |  |  | 93625A200 | NYLOC HEX NUT, M5 X 0.8 MM | 1
 |  |  | 9540K922 | UNTHREADED BUMPER M5 | 1
 |  |  | OH3A3-140 | TRAVEL STOP, FWD LEFT | 1
 |  |  | OH3A3-17 | ASSY, TRAVEL STOP, FWD LEFT | 1
 |  | ASSY, STICK PITCH AXIS -> ASSY, TRAVEL STOP, FWD RIGHT | 91292A126 | SHCS, M5X0.8, 16MM, 18-8 | 1
 |  |  | 91828A241 | HEX NUT, M5 X 0.8 MM | 1
 |  |  | 93625A200 | NYLOC HEX NUT, M5 X 0.8 MM | 1
 |  |  | 9540K922 | UNTHREADED BUMPER M5 | 1
 |  |  | OH3A3-141 | TRAVEL STOP, FWD RIGHT | 1
 |  |  | OH3A3-18 | ASSY, TRAVEL STOP, FWD RIGHT | 1
 |  | (blank) | 91287A307 | HHS, M8 X 1.25 MM THREAD, 45 MM LONG | 2
 |  |  | 92095A205 | BHCS, M4 X 0.7 MM THREAD, 45MM LONG | 2
 |  |  | 93475A230 | FLAT WASHER, M4 | 4
 |  |  | 93475A270 | 93475A270 - FLAT WASHER, M8 | 10
 |  |  | 93625A150 | NYLOC HEX NUT, M4 X 0.7 MM | 2
 |  |  | 93625A300 | NYLOC HEX NUT, M8 X 1.25MM | 4
 |  |  | OH3A3-1 | ASSY, FLIGHT CONTROL STICK | 1
 |  |  | OH3A3-9001 | DECAL, GRIP ASSY | 1
CENTER Total |  |  |  |  | 1700
LEFT | OH10A1A1-1 - ASSY, SIM PWR PANEL | ASSY, SWITCH, S1AL, ROUND BAT | OHC0001-1 | ASSY, SWITCH, S1AL, ROUND BAT | 1
 |  |  | OHC0001-10 | BAT, ROUND, FOR NKK SXAL SWITCH | 1
 |  |  | S1AL | SWITCH, TOGGLE, LOCKING, SPST, 2-POSN, NO BAT | 1
 |  | ASSY, SWITCH, S3AL, CONICAL BAT | OHC0001-20 | BAT, CONICAL, FOR NKK SXAL SWITCH | 1
 |  |  | OHC0001-5 | ASSY, SWITCH, S3AL, CONICAL BAT | 1
 |  |  | S3AL | SWITCH, TOGGLE, LOCKING, SPDT, 3-POSN, NO BAT | 1
 |  | ASSY, SWITCH, S3AL, TALL BAT | OHC0001-30 | BAT, TALL, FOR NKK SXAL SWITCH | 1
 |  |  | OHC0001-6 | ASSY, SWITCH, S3AL, TALL BAT | 1
 |  |  | S3AL | SWITCH, TOGGLE, LOCKING, SPDT, 3-POSN, NO BAT | 1
 |  | OHC0003-A-18FLGN4 - ASSY, KNOB, GREY, .25 D-SHAFT | 92311A188 | SET SCREW, 8-32 X .1875, CUP POINT, 18-8 | 2
 |  |  | OHC0003-18FLGN4 | KNOB, GREY, .25 D-SHAFT | 1
 |  |  | OHC0003-A-18FLGN4 | ASSY, KNOB, GREY, .25 D-SHAFT | 1
 |  | S1AL - SWITCH, TOGGLE, LOCKING, SPST, 2-POSN, STD BAT | S1AL | SWITCH, TOGGLE, LOCKING, SPST, 2-POSN, NO BAT | 1
 |  |  |  | SWITCH, TOGGLE, LOCKING, SPST, 2-POSN, STD BAT | 1
 |  |  | SXAL-BAT | STANDARD BAT FOR S-SERIES LOCKING SWITCHES | 1
 |  | (blank) | 90760A007 | NUT, JAM, #6-32, STEEL | 2
 |  |  | 91249A151 | PHS, #6-32 X .625, 18-8, BLK | 2
 |  |  | AT503M | HEX NUT FOR SWITCH, M12-1 | 4
 |  |  | AT508 | LOCK WASHER FOR SWITCH, M12 | 4
 |  |  | AT537 | O-RING FOR SWITCH, 12 MM ID | 4
 |  |  | EN11-HSM1BF20 | ROTARY ENCODER | 1
 |  |  | OH10A1A1-1 | ASSY, SIM PWR PANEL | 1
 |  |  | OH10A1A1-10 | SIM PWR PCB V | 1
 |  |  | OH10A1A1-11 | SIM PWR BACKPLATE | 1
 |  |  | OH10A1A1-12 | SIM PWR LIGHTPLATE | 1
 |  |  | OH10A1A1-13 | SIM PWR LEGEND PLATE | 1
 |  |  | PEC11R NUT | HEX NUT FOR SWITCH, M7 X .75 | 1
 | OH4A1-1 - ASSY, LEFT CONSOLE | ASSY, ABSIS ALE | ABSIS001 | ASSY, ABSIS ALE | 1
 |  |  | ABSIS001-10 | PCB, ABSIS ALE | 1
 |  |  | DEV-12640 | ARDUINO PRO MICRO, 5V, 16 MHZ, SPARKFUN | 1
 |  | ASSY, ABSIS HID BUS MASTER | (GENERIC) | HEADER, PIN, .1 SPACING | 2
 |  |  | DEV-12640 | ARDUINO PRO MICRO, 5V, 16 MHZ, SPARKFUN | 1
 |  | ASSY, LC TO CT BULKHEAD INTERCONNECT PANEL | 1589-01C | CABLE, USB 2.0, PNL MNT, TYPE B FEMALE TO TYPE A MALE, 1 FT | 1
 |  |  | 39-01-2061 | MOLEX, MINI-FIT JR, 5559-SERIES, PNL MNT, 6 POS | 2
 |  |  | 90471A160 | FHS, 100DEG, #4-40 X .375, STEEL | 2
 |  |  | 91841A005 | NUT, #4-40, 18-1 | 2
 |  |  | NL2MPXX | CONNECTOR, LOUDSPEAKER, 2-POLE, NEUTRIK | 1
 |  |  | OH4A14A1-1 | ASSY, LC TO CT BULKHEAD INTERCONNECT PANEL | 1
 |  |  | OH4A14A1-10 | LC TO CT BULKHEAD INTERCONNECT PANEL | 1
 |  | ASSY, LEFT BULKHEAD INTERCONNECT PANEL | 1681-02C | CABLE, USB 3.0, PNL MNT, SS TYPE B TO MINI B | 1
 |  |  | 39-01-2041 | MOLEX, MINI-FIT JR, 5559-SERIES, PNL MNT, 4 POS | 2
 |  |  | 39-01-2081 | MOLEX, MINI-FIT JR, 5559-SERIES, PNL MNT, 8 POS | 1
 |  |  | 39-01-2221 | MOLEX, MINI-FIT JR, 5559-SERIES, PNL MNT, 22 POS | 1
 |  |  | 90471A160 | FHS, 100DEG, #4-40 X .375, STEEL | 2
 |  |  | 91841A005 | NUT, #4-40, 18-1 | 2
 |  |  | NL2MPXX | CONNECTOR, LOUDSPEAKER, 2-POLE, NEUTRIK | 1
 |  |  | OHC0013-1 | ASSY, LEFT BULKHEAD INTERCONNECT PANEL | 1
 |  |  | OHC0013-10 | BULKHEAD INTERCONNECT PANEL | 1
 |  | ASSY, TRANSDUCER GAIN REMOTE | OH4A10-1 | ASSY, TRANSDUCER GAIN REMOTE | 1
 |  |  | OH4A10-10 | TRANSDUCER GAIN REMOTE PLATE | 1
 |  |  | P0915N-FC20BR10K | POTENTIOMETER, 9MM ROTARY, PANEL MOUNT | 1
 |  |  | P09X NUT | HEX NUT FOR POTENTIOMETER, M7X0.75 | 1
 |  |  | P09X WASHER | WASHER FOR POTENTIOMETER, M7 | 1
 |  | ASSY, TRANSDUCER GAIN REMOTE -> OHC0003-A-18FLGN4 - ASSY, KNOB, GREY, .25 D-SHAFT | 92311A188 | SET SCREW, 8-32 X .1875, CUP POINT, 18-8 | 2
 |  |  | OHC0003-18FLGN4 | KNOB, GREY, .25 D-SHAFT | 1
 |  |  | OHC0003-A-18FLGN4 | ASSY, KNOB, GREY, .25 D-SHAFT | 1
 |  | OHC0009-1 - FAUX DZUS STUD | 90275A196 | FHS, 82DEG, #8-32 X .625, STEEL | 1
 |  |  | OHC0009-1 | FAUX DZUS STUD | 43
 |  |  | OHC0009-10 | FAUX DZUS STUD HEAD | 1
 |  | THROTTLE QUADRANT COVER PLATE | 7900T707 | STRIP BRUSH, EASY-CUT, .125 WIDTH X .0975 THICK, NYLON | 3
 |  |  | 90618A200 | WASHER, #4 X .250, 18-8, BLACK OXIDE, MS15795-803B | 6
 |  |  | 91249A111 | PHS, #4-40 X .50, 18-8, BLK | 6
 |  |  | 93365A120 | INSERT, 4-40, BRASS, FOR PLASTICS | 6
 |  |  | OH4A1-11 | USB COVER PLATE | 1
 |  |  | OH4A9A4-1 | THROTTLE QUADRANT COVER PLATE | 1
 |  |  | OH4A9A4-10 | INBOARD THROTTLE QUADRANT CONSOLE COVER PLATE | 1
 |  |  | OH4A9A4-11 | OUTBOARD THROTTLE QUADRANT LEGEND PLATE | 1
 |  |  | OH4A9A4-12 | OUTBOARD THROTTLE QUADRANT BRUSH HOLDER | 1
 |  |  | OH4A9A4-13 | INBOARD THROTTLE QUADRANT LEGEND PLATE | 1
 |  |  | OH4A9A4-14 | AFT OUTBOARD THROTTLE QUADRANT RAIL SUPPORT | 1
 |  |  | OH4A9A4-15 | FWD OUTBOARD THROTTLE QUADRANT RAIL SUPPORT | 1
 |  | (blank) | 4PMINIH | 4 PORT USB 3.0 HUB | 1
 |  |  | 90272A079 | PHS, #2-56 X .375, STEEL | 4
 |  |  | 90272A106 | PHS, #4-40 X .250, STEEL | 4
 |  |  | 90272A201 | PHS, #8-32 X 1.250, STEEL | 12
 |  |  | 90272A203 | PHS, #8-32 X 1.50, STEEL | 4
 |  |  | 90471A220 | FHS, 100DEG, #6-32 X .500, STEEL | 2
 |  |  | 90471A435 | FHS, 100DEG, #8-32 X .625, STEEL | 4
 |  |  | 90618A200 | WASHER, #4 X .250, 18-8, BLACK OXIDE, MS15795-803B | 4
 |  |  | 90760A007 | NUT, JAM, #6-32, STEEL | 2
 |  |  | 91249A066 | PHS, #2-56 X 1.0, 18-8, BLK | 2
 |  |  | 91249A111 | PHS, #4-40 X .50, 18-8, BLK | 2
 |  |  | 91249A120 | PHS, #4-40 X .875, 18-8, BLK | 2
 |  |  | 91249A146 | PHS, #6-32 X .375, 18-8, BLK | 1
 |  |  | 91249A148 | PHS, #6-32 X .50, 18-8, BLK | 11
 |  |  | 91249A161 | PHS, #6-32 X 1.50, 18-8, BLK | 2
 |  |  | 91249A192 | PHS, #8-32 X .375, 18-8, BLK | 6
 |  |  | 91780A105 | STANDOFF, #2-56 X .375, .1875 HEX, FEMALE, ALUMINUM | 4
 |  |  | 91841A005 | NUT, #4-40, 18-1 | 4
 |  |  | 91841A007 | NUT, #6-32, 18-8 | 2
 |  |  | 91841A009 | NUT, #8-32, 18-8 | 8
 |  |  | 92105A660 | INSERT, 8-32, SELF TAPPING, FOR SOFTWOOD | 2
 |  |  | 93505A456 | STANDOFF, #8-32 X 1.00, .250 HEX, MALE-FEMALE, ALUMINUM | 4
 |  |  | 94070A076 | PHS, #2-56 X .1875, BRASS | 4
 |  |  | 94639A187 | SPACER, #2 X 0.25 OD X 0.125 L, NYLON | 4
 |  |  | 95130A105 | NUT, #2-56, NARROW, BRASS | 2
 |  |  | 98023A113 | WASHER, #8, STEEL, ZINC | 6
 |  |  | ABSIS001A1 | PCB, ABSIS ALE RELAY MODULE | 1
 |  |  | B09V6WY1SD | HUB, USB 3.0, 7-PORT, 5VDC | 3
 |  |  | OH4A1-1 | ASSY, LEFT CONSOLE | 1
 |  |  | OH4A1-10 | LEFT CONSOLE EXT SKIN | 1
 |  |  | OH4A1-12 | APU ABSIS ADAPTER PLATE | 1
 |  | ASSY, ABSIS BUS MASTER | ABSIS011 | ASSY, ABSIS BUS MASTER | 1
 |  |  | ABSIS011-10 | PCB, ABSIS BUS MASTER | 1
 | OH4A1A1-1 - ASSY, LEFT CONSOLE STRUCTURE | (blank) | 3225T24 | VIBRATION-DAMPING LOOP CLAMP | 1
 |  |  | 90252A115 | FHWS, 82DEG, #8 X 1.50, STEEL, BLK, FOR MDF | 75
 |  |  | 90272A190 | PHS, #8-32 X 0.250, STEEL | 1
 |  |  | 90272A203 | PHS, #8-32 X 1.50, STEEL | 48
 |  |  | 90471A435 | FHS, 100DEG, #8-32 X .625, STEEL | 29
 |  |  | 90471A436 | FHS, 100DEG, #8-32 X 1.25, STEEL | 32
 |  |  | 91249A151 | PHS, #6-32 X .625, 18-8, BLK | 3
 |  |  | 91249A192 | PHS, #8-32 X .375, 18-8, BLK | 5
 |  |  | 91841A009 | NUT, #8-32, 18-8 | 79
 |  |  | 92105A660 | INSERT, 8-32, SELF TAPPING, FOR SOFTWOOD | 36
 |  |  | 93365A120 | INSERT, 4-40, BRASS, FOR PLASTICS | 4
 |  |  | 93365A130 | INSERT, 6-32, BRASS, FOR PLASTIC | 13
 |  |  | 93365A140 | INSERT, 8-32, BRASS, FOR PLASTICS | 66
 |  |  | 98023A113 | WASHER, #8, STEEL, ZINC | 70
 |  |  | OH4A1A1-1 | ASSY, LEFT CONSOLE STRUCTURE | 1
 |  |  | OH4A1A1-10 | PRIMARY RIB E | 1
 |  |  | OH4A1A1-11 | PRIMARY RIB A | 1
 |  |  | OH4A1A1-12 | PRIMARY RIB B | 1
 |  |  | OH4A1A1-13 | PRIMARY RIB C | 1
 |  |  | OH4A1A1-14 | PRIMARY RIB D | 1
 |  |  | OH4A1A1-15 | D-C LEFT INBOARD SPACER | 1
 |  |  | OH4A1A1-16 | E-D LEFT INBOARD SPACER | 1
 |  |  | OH4A1A1-17 | E-AFT LEFT INBOARD SPACER | 1
 |  |  | OH4A1A1-18 | LEFT CONSOLE - LEFT AUX SPACER | 1
 |  |  | OH4A1A1-19 | A-B LEFT OUTBOARD SPACER | 1
 |  |  | OH4A1A1-20 | LEFT SUB-CONSOLE RAIL | 1
 |  |  | OH4A1A1-21 | B-C LEFT OUTBOARD SPACER | 1
 |  |  | OH4A1A1-22 | C-D LEFT OUTBOARD SPACER | 1
 |  |  | OH4A1A1-23 | D-E LEFT OUTBOARD SPACER | 1
 |  |  | OH4A1A1-24 | E-AFT LEFT OUTBOARD SPACER | 1
 |  |  | OH4A1A1-25 | FWD LEFT CONSOLE CANOPY RAIL BRACKET | 1
 |  |  | OH4A1A1-26 | CANOPY RAIL TRIM | 1
 |  |  | OH4A1A1-27 | AFT LEFT CONSOLE CANOPY RAIL BRACKET | 1
 |  |  | OH4A1A1-28 | CANOPY RAIL | 1
 |  |  | OH4A1A1-29 | CONSOLE SILL BRACKET A-L | 4
 |  |  | OH4A1A1-30 | CONSOLE SILL BRACKET B-L | 3
 |  |  | OH4A1A1-31 | AFT LEFT UPPER BULKHEAD BRACKET | 1
 |  |  | OH4A1A1-32 | INBOARD LEFT CONSOLE WALL | 1
 |  |  | OH4A1A1-33 | LEFT CONSOLE FLOOR | 1
 |  |  | OH4A1A1-34 | LEFT AFT INTERNAL BULKHEAD | 1
 |  |  | OH4A1A1-35 | LEFT AFT BULKHEAD | 1
 |  |  | OH4A1A1-36 | LEFT CONSOLE INBOARD WALL | 1
 |  |  | OH4A1A1-37 | INBOARD WALL SUPPORT | 1
 |  |  | OH4A1A1-38 | A-B LOWER STRINGER | 1
 |  |  | OH4A1A1-39 | B-C LOWER STRINGER | 1
 |  |  | OH4A1A1-40 | C-D LOWER STRINGER | 2
 |  |  | OH4A1A1-41 | E-F LOWER STRINGER | 2
 |  |  | OH4A1A1-42 | AFT BULKHEAD STRINGER | 2
 |  |  | OH4A1A1-43 | INBOARD FWD LEFT CONSOLE TRIM | 1
 |  |  | OH4A1A1-44 | LEFT AUX VENT PLUG | 1
 |  |  | OH4A1A1-45 | LEFT AUX PANEL | 1
 |  |  | OH4A1A1-46 | LEFT AUX UPPER BRACKET | 1
 |  |  | OH4A1A1-47 | LEFT AUX SUPPORT BRACKET, FWD, OUTBOARD | 1
 |  |  | OH4A1A1-48 | LEFT AUX SUPPORT BRACKET, LOWER, OUTBOARD | 1
 |  |  | OH4A1A1-49 | LEFT AUX SUPPORT BRACKET, LOWER, INBOARD | 1
 | OH4A2A1-1 - ASSY, LANDING GEAR LEVER PANEL | ASSY, ABSIS ALE | ABSIS001 | ASSY, ABSIS ALE | 1
 |  |  | ABSIS001-10 | PCB, ABSIS ALE | 1
 |  |  | DEV-12640 | ARDUINO PRO MICRO, 5V, 16 MHZ, SPARKFUN | 1
 |  | ASSY, LDG GEAR HANDLE | 92671A115 | NUT, #0-80, BRASS | 1
 |  |  | OH4A2A1-100 | OH4A2A1-100 - ASSY, LDG GEAR HANDLE | 1
 |  |  | OH4A2A1-101 | LDG GEAR HANDLE LOLLIPOP | 1
 |  |  | OH4A2A1-102 | LDG GEAR HANDLE LOLLIPOP COVER | 1
 |  | ASSY, LDG GEAR LVR MECH | 7658K16 | SWITCH, LIMIT, SUBMINIATURE, ROLLER LEVER, SPDT | 2
 |  |  | 84835A14 | SPRING PLUNGER, BALL-NOSE, PRESS-FIT, 0.5 IN DIA | 1
 |  |  | 90272A079 | PHS, #2-56 X .375, STEEL | 2
 |  |  | 90618A200 | WASHER, #4 X .250, 18-8, BLACK OXIDE, MS15795-803B | 4
 |  |  | 91249A058 | PHS, #2-56 X .500, 18-8, BLK | 2
 |  |  | 91249A115 | PHS, #4-40 X .625, 18-8, BLK | 4
 |  |  | 92141A003 | WASHER, #2 X .250 OD, 18-8 | 6
 |  |  | 93085A851 | FHS, 100DEG, #4-40 X 1.25, 18-8 | 4
 |  |  | 95649A232 | WASHER, .25 X .50 OD, .031 THK, PLASTIC UHMW | 2
 |  |  | DSTL-0418-12 | SOLENOID, CLOSED FRAME, PULL, TUBULAR | 1
 |  |  | OH4A2A1-200 | ASSY, LDG GEAR LVR MECH | 1
 |  | ASSY, LDG GEAR LVR MECH -> ASSY, LDG GEAR ELEC STANDOFF BRACKET | 91249A050 | PHS, #2-56 X .25, 18-8, BLK | 2
 |  |  | 93365A110 | INSERT, 2-56, BRASS, FOR PLASTIC | 2
 |  |  | OH4A2A1-219 | ASSY, LDG GEAR ELEC STANDOFF BRACKET | 1
 |  |  | OH4A2A1-219A | LDG GEAR ELEC STANDOFF BRACKET | 1
 |  | ASSY, LDG GEAR LVR MECH -> ASSY, LDG GEAR LEVEL MOUNT SHELL B | 6338K411 | SLEEVE BEARING FOR .250 SHAFT X .375 ID X .250 | 1
 |  |  | 93365A110 | INSERT, 2-56, BRASS, FOR PLASTIC | 2
 |  |  | 93365A120 | INSERT, 4-40, BRASS, FOR PLASTICS | 3
 |  |  | 93365A130 | INSERT, 6-32, BRASS, FOR PLASTIC | 1
 |  |  | OH4A2A1-217 | ASSY, LDG GEAR LEVEL MOUNT SHELL B | 1
 |  |  | OH4A2A1-217A | LDG GEAR LEVEL MOUNT SHELL B | 1
 |  | ASSY, LDG GEAR LVR MECH -> ASSY, LDG GEAR LEVER MOUNT A | 6338K411 | SLEEVE BEARING FOR .250 SHAFT X .375 ID X .250 | 1
 |  |  | 91831A005 | NUT, NYLOC, #4-40, 18-8 | 4
 |  |  | 93365A110 | INSERT, 2-56, BRASS, FOR PLASTIC | 6
 |  |  | 93365A120 | INSERT, 4-40, BRASS, FOR PLASTICS | 7
 |  |  | OH4A2A1-216 | ASSY, LDG GEAR LEVER MOUNT A | 1
 |  |  | OH4A2A1-216A | LDG GEAR LEVER MOUNT A | 1
 |  | ASSY, LDG GEAR LVR MECH -> ASSY, LDG GEAR LVR | 6338K312 | BEARING, SLEEVE, FLANGED, .375 ID X .50 OD, 0.50 LG | 1
 |  |  | 7658K15 | SWITCH, LIMIT, SUBMINIATURE, LEVER, SPDT | 1
 |  |  | 84835A23 | SPRING PLUNGER, BALL-NOSE, PRESS-FIT, 0.25 IN DIA, 6-13 LB FORCE | 1
 |  |  | 91249A063 | PHS, #2-56 X .750, 18-8, BLK | 2
 |  |  | 91841A003 | NUT, #2-56, 18-1 | 2
 |  |  | 92141A003 | WASHER, #2 X .250 OD, 18-8 | 4
 |  |  | 93085A116 | FHS, 100DEG, #4-40 X .875, 18-8 | 7
 |  |  | OH4A2A1-210 | ASSY, LDG GEAR LVR | 1
 |  |  | OH4A2A1-211 | LDG GEAR LVR PIVOT PIN 0.25 IN | 2
 |  |  | OH4A2A1-214 | LDG GEAR LVR DETENTS | 1
 |  | ASSY, LDG GEAR LVR MECH -> ASSY, LDG GEAR LVR -> ASSY, LDG GEAR LVR LOLLIPOP SHAFT | 92196A108 | SHCS, #4-40 X .375, 18-8 | 1
 |  |  | OH4A2A1-216 | ASSY, LDG GEAR LVR LOLLIPOP SHAFT | 1
 |  |  | OH4A2A1-216A | LDG GEAR LVR LOLLIPOP SHAFT | 1
 |  | ASSY, LDG GEAR LVR MECH -> ASSY, LDG GEAR LVR -> PRE-ASSY, LDG GEAR LVR SHELL A | 93365A120 | INSERT, 4-40, BRASS, FOR PLASTICS | 7
 |  |  | OH4A2A1-212 | PRE-ASSY, LDG GEAR LVR SHELL A | 1
 |  |  | OH4A2A1-212A | LDG GEAR LVR SHELL A | 1
 |  | ASSY, LDG GEAR LVR MECH -> ASSY, LDG GEAR LVR -> PRE-ASSY, LDG GEAR LVR SHELL B | 93365A110 | INSERT, 2-56, BRASS, FOR PLASTIC | 2
 |  |  | OH4A2A1-215 | PRE-ASSY, LDG GEAR LVR SHELL B | 1
 |  |  | OH4A2A1-215A | LDG GEAR LVR SHELL B | 1
 |  | ASSY, LDG GEAR LVR MECH -> ASSY, LDG GEAR LVR -> PRE-ASSY, LDG GEAR LVR UPPER TUBE | 6338K312 | BEARING, SLEEVE, FLANGED, .375 ID X .50 OD, 0.50 LG | 1
 |  |  | OH4A2A1-213 | PRE-ASSY, LDG GEAR LVR UPPER TUBE | 1
 |  |  | OH4A2A1-213A | LDG GEAR LVR UPPER TUBE | 1
 |  | ASSY, LDG GEAR LVR MECH -> ASSY, LDG GEAR SOLENOID CLAMP | 91251A115 | SHCS, #4-40 X 1.00, STEEL, BLK | 1
 |  |  | 91831A005 | NUT, NYLOC, #4-40, 18-8 | 1
 |  |  | OH4A2A1-218 | ASSY, LDG GEAR SOLENOID CLAMP | 1
 |  |  | OH4A2A1-218A | SOLENOID CLAMP LINER | 1
 |  |  | OH4A2A1-218B | LDG GEAR SOLENOID CLAMP | 1
 |  | ASSY, LDG GEAR LWR OUTBD MOUNTING BRACKET | 93365A130 | INSERT, 6-32, BRASS, FOR PLASTIC | 1
 |  |  | OH4A2A1-20 | ASSY, LDG GEAR LWR OUTBD MOUNTING BRACKET | 1
 |  |  | OH4A2A1-20A | LDG GEAR LWR OUTBD MOUNTING BRACKET | 1
 |  | (blank) | 462071004 | MOLEX MINI-FIT JR HEADER, 4-CIRCUITS DUAL-ROW | 2
 |  |  | 90272A079 | PHS, #2-56 X .375, STEEL | 1
 |  |  | 90471A160 | FHS, 100DEG, #4-40 X .375, STEEL | 2
 |  |  | 91249A151 | PHS, #6-32 X .625, 18-8, BLK | 2
 |  |  | 91771A071 | FHS, 82DEG, #0-80 X .75, 18-8 | 1
 |  |  | 93505A217 | STANDOFF, #2-56 X 1.00, .1875 HEX, MALE-FEMALE, ALUMINUM | 8
 |  |  | 94070A076 | PHS, #2-56 X .1875, BRASS | 4
 |  |  | 96640A295 | FHS, 100DEG, #2-56 X .250, 18-8, BLK | 1
 |  |  | ABSIS001A1 | PCB, ABSIS ALE RELAY MODULE | 1
 |  |  | AT513M | HEX NUT FOR SWITCH, M6 X .75 | 1
 |  |  | C90 | CAP, PUSHBUTTON, BLACK, .354 OD | 1
 |  |  | KM1101RR02QE | PUSHBUTTON, SPST, SUBMINIATURE, PANEL MOUNT | 1
 |  |  | MPG206R | SWITCH, PUSHBUTTON, MOMENTARY, NO CAP | 1
 |  |  | OH4A2A1-1 | ASSY, LANDING GEAR LEVER PANEL | 1
 |  |  | OH4A2A1-10 | LANDING GEAR PANEL PCB V2 | 1
 |  |  | OH4A2A1-11 | LANDING GEAR PANEL BACKPLATE | 1
 |  |  | OH4A2A1-12 | LANDING GEAR PANEL LIGHTPLATE | 1
 |  |  | OH4A2A1-13 | LANDING GEAR PANEL LEGEND PLATE | 1
 |  |  | OH4A2A1-16 | WARN TONE SILENCE SWITCH CAP | 1
 |  |  | OH4A2A1-21 | LANDING GEAR HANDLE LED MOUNT | 1
 |  |  | HLMP-1321 | 3MM BACKLIGHTING LED, RED | 1
 | OH4A3A1-1 - ASSY, SELECT JETT PANEL | ASSY, SELECT JETT BUTTON | 92311A144 | SET SCREW, #6-32 X 0.25, CUP POINT, 18-8 | 1
 |  |  | 9414T3 | SHAFT COLLAR, .125 ID X 0.375 OD X .25 THK | 1
 |  |  | OH4A3A1-19 | SELECT JETT BUTTON | 1
 |  |  | OH4A3A1-19A | ASSY, SELECT JETT BUTTON | 1
 |  | ASSY, SELECT JETT ELECTRONICS TRAY | 94070A076 | PHS, #2-56 X .1875, BRASS | 16
 |  |  | ABSIS001A1 | PCB, ABSIS ALE RELAY MODULE | 1
 |  |  | OH4A3A1-20 | SELECT JETT ABSIS ADAPTER PLATE | 1
 |  |  | OH4A3A1-200 | ASSY, SELECT JETT ELECTRONICS TRAY | 1
 |  |  | 91780A115 | STANDOFF, #2-56 X .875, .1875 HEX, FEMALE, ALUMINUM | 8
 |  | ASSY, SELECT JETT ELECTRONICS TRAY -> ASSY, ABSIS ALE | ABSIS001 | ASSY, ABSIS ALE | 2
 |  |  | ABSIS001-10 | PCB, ABSIS ALE | 1
 |  |  | DEV-12640 | ARDUINO PRO MICRO, 5V, 16 MHZ, SPARKFUN | 1
 |  | ASSY, SELECT JETT KNOB | 92311A425 | SET SCREW, 10-32 X .250, CUP POINT, 18-8 | 1
 |  |  | 9414T6 | COLLAR, SHAFT, .25 ID X .50 OD X .2813 T, STEEL, BLK | 1
 |  |  | OH4A3A1-18 | SELECT JETT KNOB | 1
 |  |  | OH4A3A1-18A | ASSY, SELECT JETT KNOB | 1
 |  | ASSY, SELECT JETT SWITCH MECH | 2303-0250-0024 | GEAR, PINION, .250 BORE, 24T, MOD 0.8, STL, SERVOCITY | 2
 |  |  | 50K NUT | HEX NUT FOR SWITCH, .375-32 UNEF | 1
 |  |  | 50KS45-01-1-05N | SWITCH, ROTARY, 45 DEG, 5 POS, .25 FLAT SHAFT | 1
 |  |  | 7779K61 | SWITCH, LIMIT, MINIATURE, SNAP-ACTION | 1
 |  |  | 90471A210 | FHS, 100DEG, #6-32 X .3125, STEEL | 2
 |  |  | 90471A220 | FHS, 100DEG, #6-32 X .500, STEEL | 2
 |  |  | 90618A200 | WASHER, #4 X .250, 18-8, BLACK OXIDE, MS15795-803B | 4
 |  |  | 91249A120 | PHS, #4-40 X .875, 18-8, BLK | 2
 |  |  | 91831A005 | NUT, NYLOC, #4-40, 18-8 | 2
 |  |  | 92141A011 | WASHER, #10 X .438 OD, 18-8 | 2
 |  |  | 92311A144 | SET SCREW, #6-32 X 0.25, CUP POINT, 18-8 | 1
 |  |  | 9414T3 | SHAFT COLLAR, .125 ID X 0.375 OD X .25 THK | 1
 |  |  | 9657K247 | SPRING, COMPRESSION, 0.30 OD X 0.440 L | 1
 |  |  | 96640A298 | FHS, 100DEG, #2-56 X .4375, 18-8, BLK | 4
 |  |  | OH4A3A1-100 | ASSY, SELECT JETT SWITCH MECH | 1
 |  |  | OH4A3A1-105 | ROTATING SHAFT, 0.25 OD, 0.15 ID | 1
 |  |  | OH4A3A1-106 | PUSH SHAFT, 0.125 OD | 1
 |  |  | OH4A3A1-107 | ALIGNING SHAFT, 0.25 OD, 0.375 LG | 1
 |  |  | OH4A3A1-108 | SPRING CENTERING SLEEVE | 1
 |  | ASSY, SELECT JETT SWITCH MECH -> PRE-ASSY, SELECT JETT LOWER MOUNT PLATE | 6338K561 | BEARING, SLEEVE, FLANGED, .125 ID X .25OD, .25 LG, BRONZE | 1
 |  |  | 6389K231 | BEARING, SLEEVED, FLANGED, .375 OD X .25 ID X .3125 H, .50 X .0625 FLANGE, NYLON | 1
 |  |  | OH4A3A1-102 | SELECT JETT LOWER MOUNT PLATE 3DP | 1
 |  |  | OH4A3A1-102A | PRE-ASSY, SELECT JETT LOWER MOUNT PLATE | 1
 |  | ASSY, SELECT JETT SWITCH MECH -> PRE-ASSY, SELECT JETT SWITCH BRACKET | 93365A110 | INSERT, 2-56, BRASS, FOR PLASTIC | 4
 |  |  | OH4A3A1-103 | SELECT JETT SWITCH BRACKET | 1
 |  |  | OH4A3A1-103A | PRE-ASSY, SELECT JETT SWITCH BRACKET | 1
 |  | ASSY, SELECT JETT SWITCH MECH -> PRE-ASSY, SELECT JETT UPPER BRACKET | 6389K231 | BEARING, SLEEVED, FLANGED, .375 OD X .25 ID X .3125 H, .50 X .0625 FLANGE, NYLON | 1
 |  |  | 93365A130 | INSERT, 6-32, BRASS, FOR PLASTIC | 8
 |  |  | OH4A3A1-101 | SELECT JETT UPPER BRACKET 3DP | 1
 |  |  | OH4A3A1-101A | PRE-ASSY, SELECT JETT UPPER BRACKET | 1
 |  | ASSY, SWITCH, MAGNETICALLY HELD, (ON)-ON | 645H/2 MOD | SWITCH, TOGGLE, MOM-ON, STD BAT (MODIFIED) | 1
 |  |  | 91100A120 | WASHER, M3 X 9 OD, STL, ZINC | 1
 |  |  | 91920A579 | STANDOFF, M3 X 0.5 - 6.4 X 4.5 HEX X 50L, STL | 1
 |  |  | 92095A179 | BHCS, M3 X 0.5-6, 18-8 | 1
 |  |  | OHC0005-1 | ASSY, SWITCH, MAGNETICALLY HELD, (ON)-ON | 2
 |  |  | OHC0005-10 | BRACKET, MAG SWITCH | 1
 |  |  | P20/15 | ELECTROMAGNET, Ø20 X 15, 12V DC, 25N | 1
 |  | ASSY, SWITCH, S1AL, ROUND BAT | OHC0001-1 | ASSY, SWITCH, S1AL, ROUND BAT | 1
 |  |  | OHC0001-10 | BAT, ROUND, FOR NKK SXAL SWITCH | 1
 |  |  | S1AL | SWITCH, TOGGLE, LOCKING, SPST, 2-POSN, NO BAT | 1
 |  | (blank) | 100SP1T8B13M1QEH | SWITCH, TOGGLE, ON-ON, SPDT, 2-POSN, 18MM BAT | 1
 |  |  | 639H/2 | SWITCH, TOGGLE, ON-OFF-ON, STD BAT | 1
 |  |  | 90272A106 | PHS, #4-40 X .250, STEEL | 1
 |  |  | 90272A144 | PHS, #6-32 X 0.250, STEEL | 2
 |  |  | 90471A150 | FHS, 100DEG, #4-40 X .1875, STEEL | 1
 |  |  | 90471A220 | FHS, 100DEG, #6-32 X .500, STEEL | 4
 |  |  | 90760A007 | NUT, JAM, #6-32, STEEL | 3
 |  |  | 91249A151 | PHS, #6-32 X .625, 18-8, BLK | 5
 |  |  | 91251A108 | SHCS, #4-40 X .375, STEEL, BLK | 1
 |  |  | 91780A045 | STANDOFF, #4-40 X 2.50, HEX, FEMALE, ALU | 1
 |  |  | 91780A337 | STANDOFF, #6-32 X 1.50, .25 HEX, FEMALE, ALUMINUM | 2
 |  |  | 93505A107 | STANDOFF, #4-40 X 1.00, HEX, MALE-FEMALE, ALUMINUM | 1
 |  |  | 93505A446 | STANDOFF, #6-32 X 1.00, .25 HEX, MALE-FEMALE, ALUMINUM | 4
 |  |  | AT503M | HEX NUT FOR SWITCH, M12-1 | 1
 |  |  | AT508 | LOCK WASHER FOR SWITCH, M12 | 1
 |  |  | AT537 | O-RING FOR SWITCH, 12 MM ID | 1
 |  |  | HDW12 | LOCK WASHER FOR SWITCH, B13 | 2
 |  |  | HDW17 | LOCKING RING FOR SWITCH, B13 | 1
 |  |  | HDW4 | HEX NUT FOR SWITCH, 15/32-32NS | 5
 |  |  | OH4A3A1-1 | ASSY, SELECT JETT PANEL | 1
 |  |  | OH4A3A1-10 | PCB, SELECT JETT PANEL REV 4 | 1
 |  |  | OH4A3A1-11 | SELECT JETT BACKPLATE | 1
 |  |  | OH4A3A1-12 | SELECT JETT LIGHTPLATE | 1
 |  |  | OH4A3A1-13 | SELECT JETT LEGEND PLATE | 1
 |  |  | OH4A3A1-15 | LAUNCH BAR SWITCH CAP | 1
 |  |  | OH4A3A1-16 | LANDING GEAR SWITCH CAP | 1
 |  |  | OH4A3A1-17 | FLAPS SWITCH CAP | 1
 | OH4A3A2-1 - ASSY, PARK BRAKE HANDLE | (blank) | 5901A142 | SPRING PLUNGER, BALL-NOSE, 0.25-20 HEX DRIVE | 3
 |  |  | 6338K411 | SLEEVE BEARING FOR .250 SHAFT X .375 ID X .250 | 2
 |  |  | 7658K15 | SWITCH, LIMIT, SUBMINIATURE, LEVER, SPDT | 3
 |  |  | 90176A102 | SPACER, #4 X .188 OD X .125 L, NYLON, BLK | 1
 |  |  | 91249A060 | PHS, #2-56 X .625, 18-8, BLK | 6
 |  |  | 91251A106 | SHCS, #4-40 X .250, STEEL, BLK | 2
 |  |  | 91841A003 | NUT, #2-56, 18-1 | 6
 |  |  | 92141A034 | WASHER, 0.578 X 1.062 OD, 18-8 | 1
 |  |  | 93365A112 | INSERT, 2-56, BRASS, FOR PLASTICS | 8
 |  |  | 93365A160 | INSERT, .25-20, BRASS, FOR PLASTICS | 3
 |  |  | 96640A025 | FHS, 82DEG, #2-56 X .375, 18-8, BLK | 1
 |  |  | 96640A027 | FHS, 82DEG, #2-56 X .50, 18-8, BLK | 8
 |  |  | OH4A3A2-1 | ASSY, PARK BRAKE HANDLE | 1
 |  |  | OH4A3A2-10 | PARKING BRAKE MECHANISM BODY | 1
 |  |  | OH4A3A2-11 | WING FOLD MECHANISM UPPER CAP | 1
 |  |  | OH4A3A2-12 | WING FOLD HANDLE RETAINING NUT | 1
 |  |  | OH4A3A2-13 | PARKING BRAKE MECHANISM END CAP | 1
 |  |  | OH4A3A2-14 | PARKING BRAKE HANDLE | 1
 |  |  | OH4A3A2-15 | PARKING BRAKE MECHANISM SHAFT | 1
 | OH4A3A3-1 - ASSY, BRAKE PRESSURE INDICATOR | (blank) | 1938 | LED, NEOPIXEL, DIFFUSED 5MM TH | 1
 |  |  | 91772A064 | PHS, #0-80 X 0.4375, 18-8 | 2
 |  |  | 93365A102 | INSERT, 0-80, BRASS, FOR PLASTICS | 2
 |  |  | 93365A130 | INSERT, 6-32, BRASS, FOR PLASTIC | 2
 |  |  | OH4A3A3-1 | ASSY, BRAKE PRESSURE INDICATOR | 1
 |  |  | OH4A3A3-10 | 1.5 IN CASE | 1
 |  |  | OH4A3A3-11 | 1.5 INDICATOR GLASS | 1
 |  |  | OH4A3A3-12 | BRAKE PRESSURE INDICATOR SHROUD | 1
 |  |  | OH4A3A3-13 | BRAKE PRESSURE INDICATOR SPACER | 1
 |  |  | OH4A3A3-14 | BRAKE PRESSURE INDICATOR NEEDLE | 1
 |  |  | OH4A3A3-15 | BRAKE PRESSURE INDICATOR BEZEL FACE | 1
 |  |  | OH4A3A3-16 | BRAKE PRESSURE INDICATOR REAR BEZEL SPACER | 1
 |  |  | VID29-02P | MICROSTEPPER, GAUGE, 315 DEG ROT | 1
 | OH4A4A1-1 - ASSY, FIRE TEST PANEL | (blank) | 100SP4T8B13M1QEH | SWITCH, TOGGLE, (ON)-OFF-(ON), SPDT, 18MM BAT | 1
 |  |  | 90760A007 | NUT, JAM, #6-32, STEEL | 2
 |  |  | 91249A151 | PHS, #6-32 X .625, 18-8, BLK | 2
 |  |  | HDW12 | LOCK WASHER FOR SWITCH, B13 | 1
 |  |  | HDW17 | LOCKING RING FOR SWITCH, B13 | 1
 |  |  | HDW4 | HEX NUT FOR SWITCH, 15/32-32NS | 2
 |  |  | OH4A4A1-1 | ASSY, FIRE TEST PANEL | 1
 |  |  | OH4A4A1-10 | FIRE TEST PANEL PCB V2 | 1
 |  |  | OH4A4A1-11 | FIRE TEST PANEL BACKPLATE | 1
 |  |  | OH4A4A1-12 | FIRE TEST PANEL LIGHTPLATE | 1
 |  |  | OH4A4A1-13 | FIRE TEST PANEL LEGEND PLATE | 1
 | OH4A4A2-1 - ASSY, EXTERNAL LT PANEL | ASSY, ABSIS ALE | ABSIS001 | ASSY, ABSIS ALE | 1
 |  |  | ABSIS001-10 | PCB, ABSIS ALE | 1
 |  |  | DEV-12640 | ARDUINO PRO MICRO, 5V, 16 MHZ, SPARKFUN | 1
 |  | ASSY, SWITCH, S1AL, TALL BAT | OHC0001-3 | ASSY, SWITCH, S1AL, TALL BAT | 1
 |  |  | OHC0001-30 | BAT, TALL, FOR NKK SXAL SWITCH | 1
 |  |  | S1AL | SWITCH, TOGGLE, LOCKING, SPST, 2-POSN, NO BAT | 1
 |  | OHC0003-A-385CGB4 - ASSY, KNOB, GREY, .25 D-SHAFT | 92311A188 | SET SCREW, 8-32 X .1875, CUP POINT, 18-8 | 1
 |  |  | 92311A189 | SET SCREW, 8-32 X .1875, CUP POINT, 18-8 | 1
 |  |  | OHC0003-385CGB4 | KNOB, GREY, .25 D-SHAFT | 1
 |  |  | OHC0003-A-385CGB4 | ASSY, KNOB, GREY, .25 D-SHAFT | 2
 |  | (blank) | H-37-5 | LOCKWASHER FOR POTENTIOMETER, 1/4 ID | 2
 |  |  | 100SP3T8B13M1QEH | SWITCH, TOGGLE, ON-OFF-ON, SPDT, 18MM BAT | 1
 |  |  | 90272A144 | PHS, #6-32 X 0.250, STEEL | 3
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
