jrsteensen/OpenHornet/MCAD/UFC Panel_v3.SLDASM

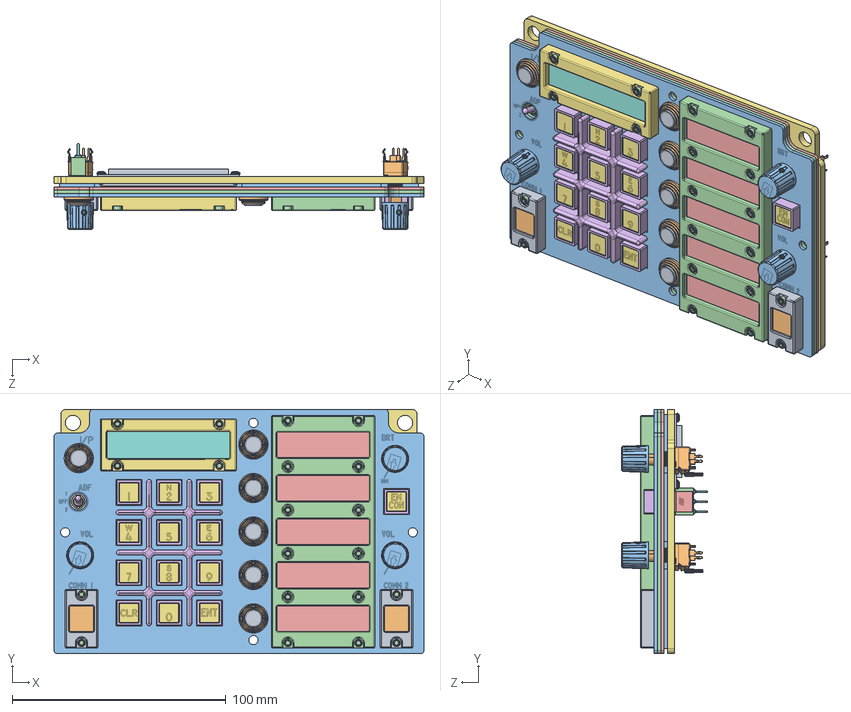
[picture p358: CAD file, 2019-12-26]
MCAD/UFC Panel_v3.SLDASM
173.0 x 114.3 x 40.1 mm
UFC COMM Bezel x 2
UFC COMM Bezel Diffuser x 2
UFC COMM Bezel Guard x 2
UFC OPT Bezel
UFC OPT Bezel Diffuser x 5
UFC OPT Bezel Guard x 5
UFC Scratchpad Bezel
UFC Scratchpad Bezel Diffuser
UFC Scratchpad Bezel Guard
UFC OPT LED Spacer Plate
UFC OPT Matrixing Plate
UFC COMM Matrixing Plate x 2
UFC COMM LED Spacer Plate x 2
UFC Square Button x 13
UFC Square Button Legend x 13
UFC Round Button x 6
UFC Round Button Legend x 6
UFC Round Button Guard x 6
UFC Legend Plate
UFC Inner Spacer Plate
UFC Outer Spacer Plate
UFC Finger Guard
UFC Backplate
16-219A-SLASH-T2D-AR2T1QY-SLASH-3T - LED, SMD, 0403, 2.95V, 10mA, White, 135 DEG VIEW ANGLE x 362
ER-OLEDM023-1W
GX06400 - SWITCH, DOME, SNAPTRON, 6.3mm DIA, 400gf x 19
UFC PCB
100 SP Housing
100 SP Top Bracket
100 T2
100 B3 Bushing
100 SP M2 Terminal
Nut^100SP3T2B3M2RE - TOGGLE, MICRO, 3 POS, .250 THD BUSHING, SHORT BAT
P0915N-FC20BR10K x 3
UFC MS21382-0XNX x 3
96006A231 - SHCS, 2-56 X .125, 18-8, BLACK OXIDE x 20
99461A505 - PHS, 0-42 X .125, SELF TAPPING, 18-8 x 19
93365A110_BRASS HEAT-SET INSERT FOR PLASTICS_2-56 x 4
94070A076 - PHS, 2-56 X .1875, BRASS x 4
92311A105 - SCREW, SET, 4-40 X .1875, CUP POINT, HEX DRIVE, 18-8 x 3
