jrsteensen/OpenHornet/MCAD/FWD UFC Assembly.sldasm

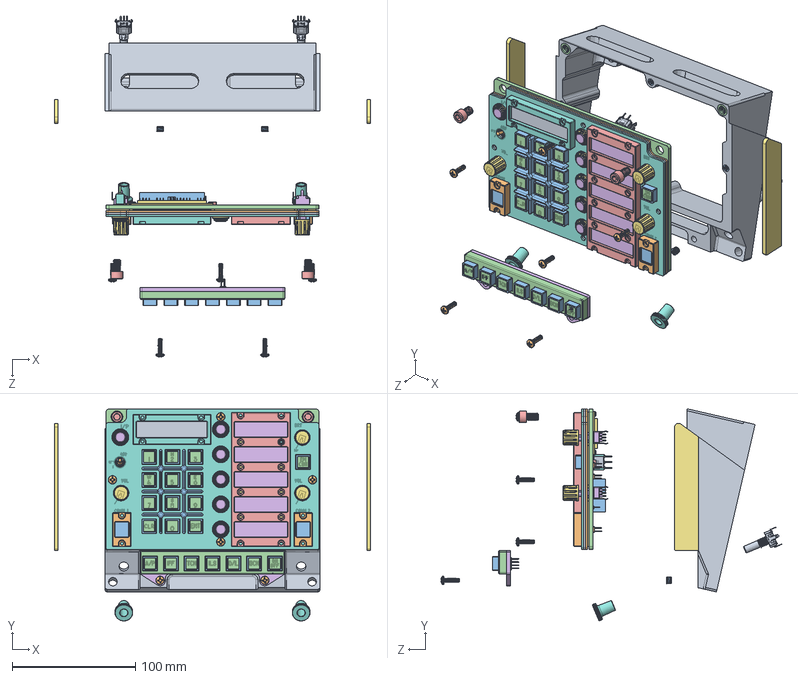
[picture p359: CAD file, 2019-11-24]
MCAD/FWD UFC Assembly.sldasm
257.2 x 172.2 x 277.1 mm
UFC Panel Support Structure
UFC COMM Bezel x 2
UFC COMM Bezel Diffuser x 2
UFC COMM Bezel Guard x 2
UFC OPT Bezel
UFC OPT Bezel Diffuser x 5
UFC OPT Bezel Guard x 5
UFC Scratchpad Bezel
UFC Scratchpad Bezel Diffuser
UFC Scratchpad Bezel Guard
UFC Square Button x 20
UFC Square Button Legend x 20
UFC Round Button x 6
UFC Round Button Legend x 6
UFC Round Button Guard x 6
UFC Legend Plate
UFC Inner Spacer Plate
UFC Outer Spacer Plate
UFC Finger Guard
UFC Backplate
LTP-305G - LED, 5x7 Matrix, Green, .300 Char Height, Common Cathode Row, Common Anode Column x 22
LTST-C150KGKT - LED, GREEN, SMD, 1206, 3.2x1.6mm x 10
ER-OLEDM023-1W
header SMD 2,54mm x 25
Single pin x 44
Single plastic support x 22
71349-2016 - Header, 2.54mm pitch, 2x18 (36), shrouded x 2
MAX5953EAX+ x 6
EEE-0JA221WP - CAP, 220uF, 6.3V, Polarized, SMD
GX06400 - SWITCH, DOME, SNAPTRON, 6.3mm DIA, 400gf x 26
UFC PCB
100 SP Housing
100 SP Top Bracket
100 T2
100 B3 Bushing
100 SP M2 Terminal
Nut^100SP3T2B3M2RE - TOGGLE, MICRO, 3 POS, .250 THD BUSHING, SHORT BAT
EVU-F2MFL3B14 - Pot, 10k Linear, PTH, M9 x 0.75 bushing, No Switch x 3
UFC MS21382-0XNX x 3
96006A231 - SHCS, 2-56 X .125, 18-8, BLACK OXIDE
99461A505 - PHS, 0-42 X .125, SELF TAPPING, 18-8 x 26
93365A110_BRASS HEAT-SET INSERT FOR PLASTICS_2-56 x 4
94070A076 - PHS, 2-56 X .1875, BRASS x 4
AP Module FWD Body
AP Module PCB
AP Module Mounting Plate
FWD UFC Guard x 2
UFC COMM Knob x 2
PEC11R-4220F-S0012 - ENCODER, INC, QUAD, DETENT, SWITCH, 12PPR, 6mm DIA X 20mm FLAT SHAFT x 2
91249A148 - PHS, 6-32 X .500, 18-8, BLACK-OXIDE x 6
93365A130 - INSERT, 6-32, BRASS, FOR PLASTICS x 6
93365A160 - INSERT, .25-20, BRASS, FOR PLASTICS x 2
91251A535 - SHCS, .25-20 X .375, STEEL, BLACK OXIDE x 2
