jrsteensen/OpenHornet/MCAD/DDIv2.SLDASM

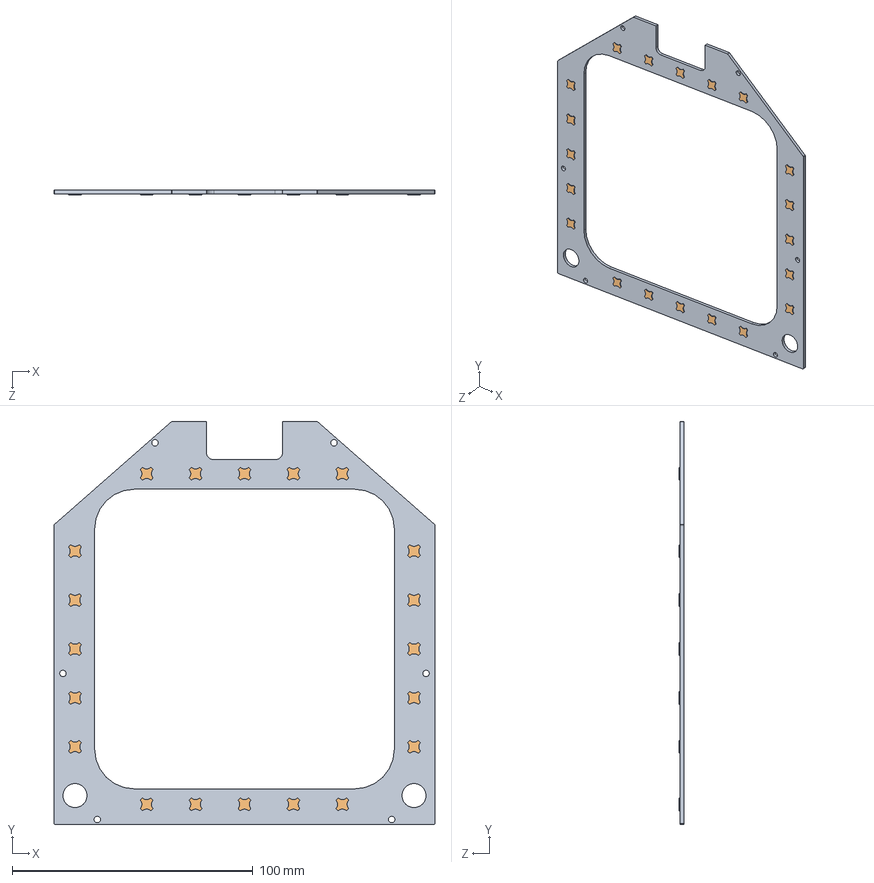
[picture p360: CAD file, 2019-11-24]
MCAD/DDIv2.SLDASM
158.2 x 167.4 x 1.96 mm
DDI PCB Mockup
GX06400 - SWITCH, DOME, SNAPTRON, 6.3mm DIA, 400gf x 20
