jrsteensen/OpenHornet/release/OH3_Center_Tub/OH3A3 - ASSY, FLIGHT CONTROL STICK/Manufacturing/OH3A3-120_MAIN PLATE_-_V50.step

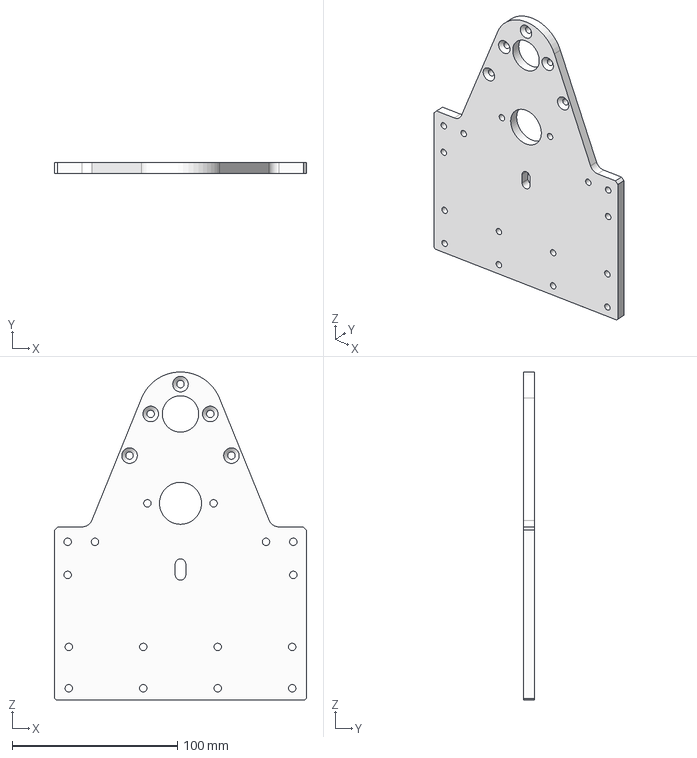
[picture p361: CAD file, 2024-02-26]
release/OH3_Center_Tub/OH3A3 - ASSY, FLIGHT CONTROL STICK/Manufacturing/OH3A3-120_MAIN PLATE_-_V50.step
152.4 x 6.35 x 198.2 mm
