jrsteensen/OpenHornet/MCAD/Spin Panel.sldasm

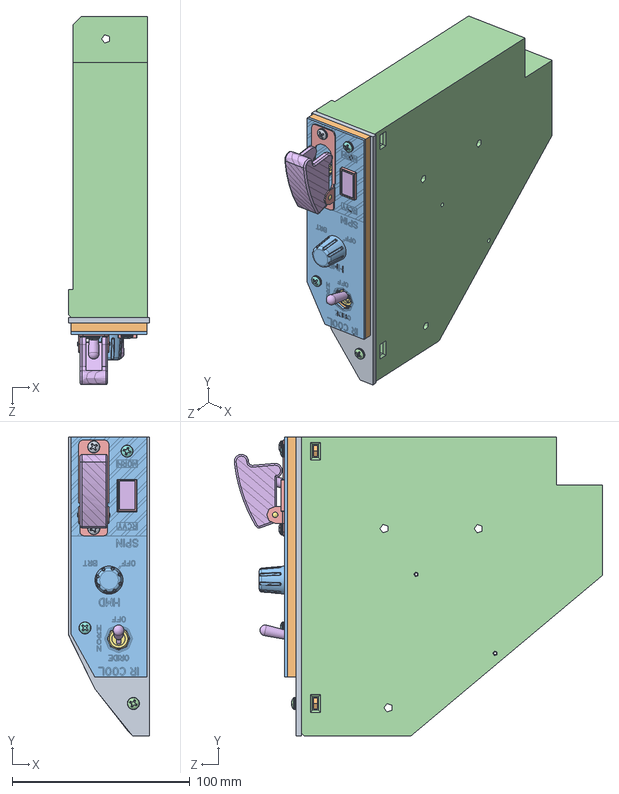
[picture p362: CAD file, 2019-10-30]
MCAD/Spin Panel.sldasm
45.7 x 168.3 x 207.3 mm
Spin Panel Backplate
Spin Panel Lightplate
Spin Panel Legend Plate
Spin Panel Module Bracket
SPN Indicator Body
SPN Indicator Cover
SPN Indicator Legend
SPN Indicator Diffuser
C-104 x 2
R-104 x 2
LTW-420D7 x 2
100-300SPXBODY x 2
100SPXBRACKET_1 x 2
100T8 x 2
100B13BUSHING x 2
100-300SPXM1 x 2
HDW17 - LOCKING RING, B13 x 2
HDW12 - LOCK WASHER, B13 x 2
HDW4 - NUT, B13 x 4
P170S-FC20BR10K - Pot, 10K, Panel Mount, Side Adjust, Lugs, ON-OFF Switch
MS25224-2 Base
MS25224_Guard
MS25224_PIN
91249A156 - PHS, 6-32 X .8750, 18-8, BLACK-OXIDE x 2
91772A162 - PHS, 6-32 X .5625, 18-8 x 2
90760A007 - NUT, 6-32, JAM, STEEL, ZINC-PLATED x 5
Korry RD239-A1G2 v4
91249A148 - PHS, 6-32 X .500, 18-8, BLACK-OXIDE
93365A110_BRASS HEAT-SET INSERT FOR PLASTICS_2-56 x 2
