jrsteensen/OpenHornet/MCAD/HUD Bit Box Assembly.sldasm

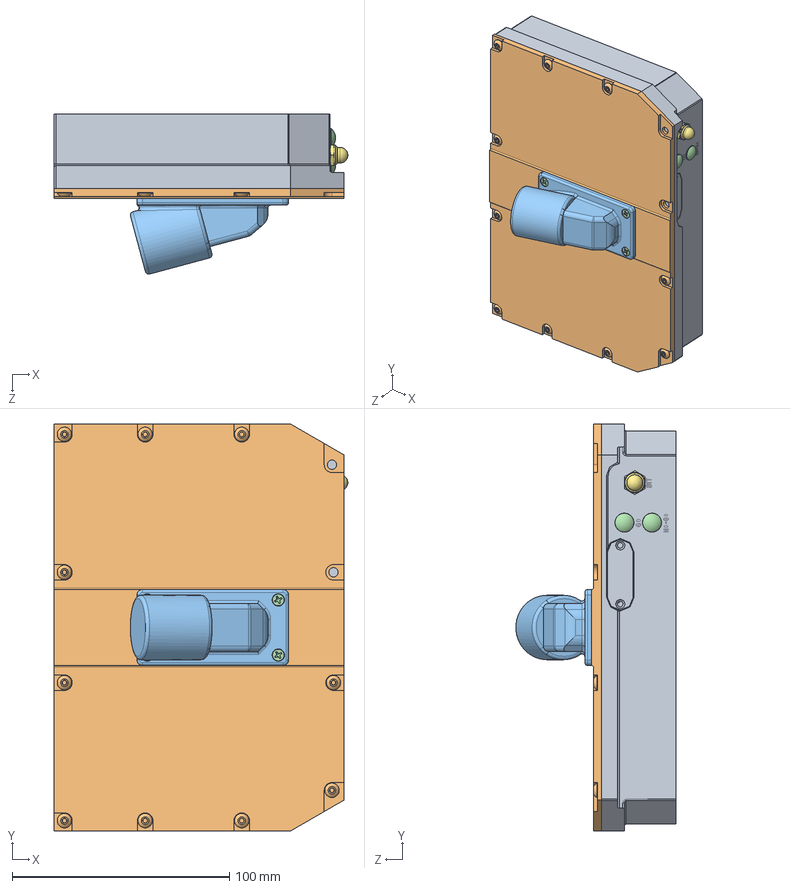
[picture p363: CAD file, 2019-10-30]
MCAD/HUD Bit Box Assembly.sldasm
135.2 x 187.3 x 73.8 mm
HUD BIT Box
HUD BIT Box Lid
HUD Camera
CMC 441 XTP x 2
334-15_SLASH_X1C5-1QSA - LED, 5mm (T1.75), WHITE, 3.2V, 20mA, PTH x 2
CF18JT68R0 - RESISTOR, 68Ohms, .125W, PTH, NO LEADS x 2
N5040G 2 - DUST BOOT, GREY, .25-32, M5423-SLASH-10-01
30-3UL
93365A130 - INSERT, 6-32, BRASS, FOR PLASTICS x 10
97763A141 - BHCS, 6-32 X .250, 18-8, BLACK-OXIDE x 10
91841A005 - NUT, 4-40, 18-8 x 4
90471A427 - FHS, 100DEG, 4-40 X .625, 18-8 x 4
