jrsteensen/OpenHornet/release/OH3_Center_Tub/OH3A3 - ASSY, FLIGHT CONTROL STICK/Manufacturing/FDM_OH3A3-105_MAIN CASING B_-_V50.3mf

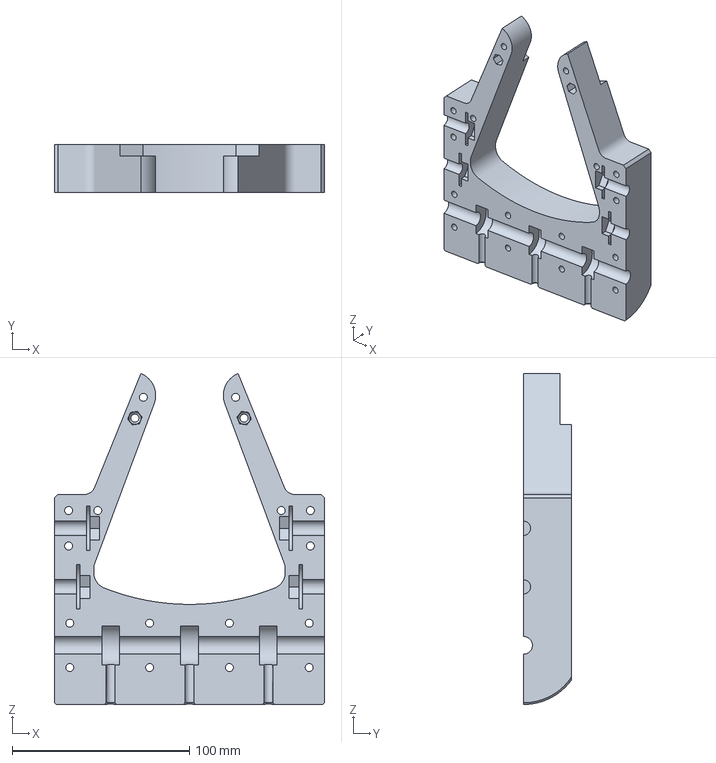
[picture p364: CAD file, 2024-02-26]
release/OH3_Center_Tub/OH3A3 - ASSY, FLIGHT CONTROL STICK/Manufacturing/FDM_OH3A3-105_MAIN CASING B_-_V50.3mf
152.4 x 27.0 x 186.7 mm
