jrsteensen/OpenHornet/ECAD/PCBs for Sim/.55 SQ Indicator/docs/.55 SQ Indicator PCB.DXF

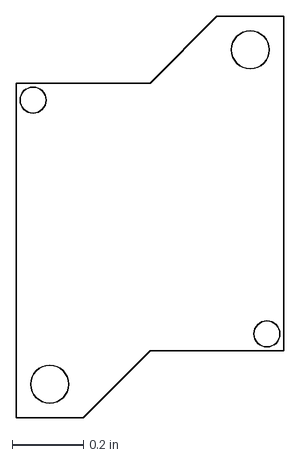
[picture p365: CAD file, 2019-10-15]
ECAD/PCBs for Sim/.55 SQ Indicator/docs/.55 SQ Indicator PCB.DXF
0.75 x 1.12 in
