jrsteensen/OpenHornet/ECAD/PCBs/ABSIS/ABSIS_ALE Relay Module/MCAD/ABSIS_ALE Relay Module.step

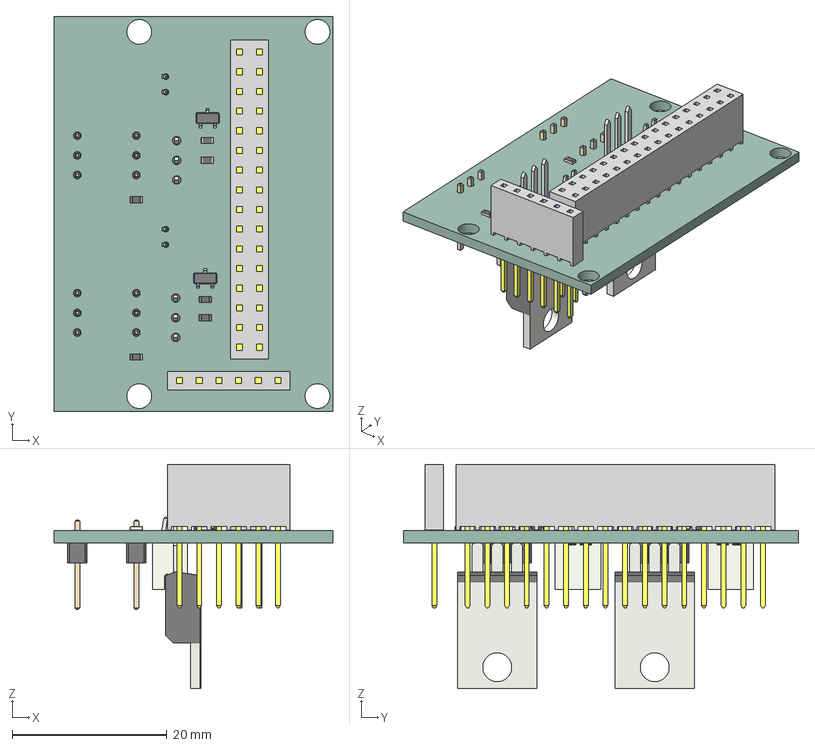
[picture p366: CAD file, 2024-02-26]
ECAD/PCBs/ABSIS/ABSIS_ALE Relay Module/MCAD/ABSIS_ALE Relay Module.step
36.0 x 51.0 x 29.0 mm
ABSIS_ALE Relay Module PCB
