jrsteensen/OpenHornet/ECAD/PCBs/ABSIS/ABSIS_ALE+/MCAD/ABSIS_ALE+.step

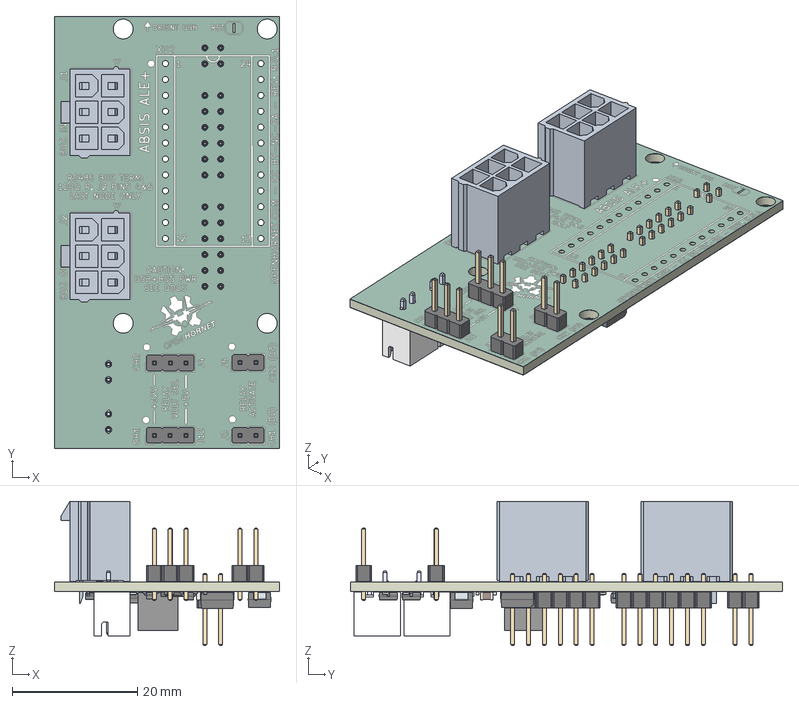
[picture p367: CAD file, 2026-09-13]
ECAD/PCBs/ABSIS/ABSIS_ALE+/MCAD/ABSIS_ALE+.step
36.0 x 69.0 x 23.0 mm
PinHeader_1x02_P254mm_Vertical x 2
PinHeader_1x03_P254mm_Vertical x 2
PinsArrayL x 5
FilletPinR x 5
R_0402_1005Metric x 10
C_0805_2012Metric x 3
PinHeader_2x02_P254mm_Vertical
PinHeader_2x06_P254mm_Vertical x 2
C_0603_1608Metric
FilletPin1 x 2
FilletPin2 x 2
Pins
R_0805_2012Metric x 2
PinsArrayLR
C_0402_1005Metric x 4
BxB-XH-A_02 x 2
Rect6
Rect7
solidBody
Terminal
ABSIS ALE+_silkscreen x 2
ABSIS ALE+_soldermask x 2
ABSIS ALE+_PCB
