jrsteensen/OpenHornet/ECAD/PCBs/ABSIS/ABSIS_Bus_Master/MCAD/ABSIS_Bus_Master.step

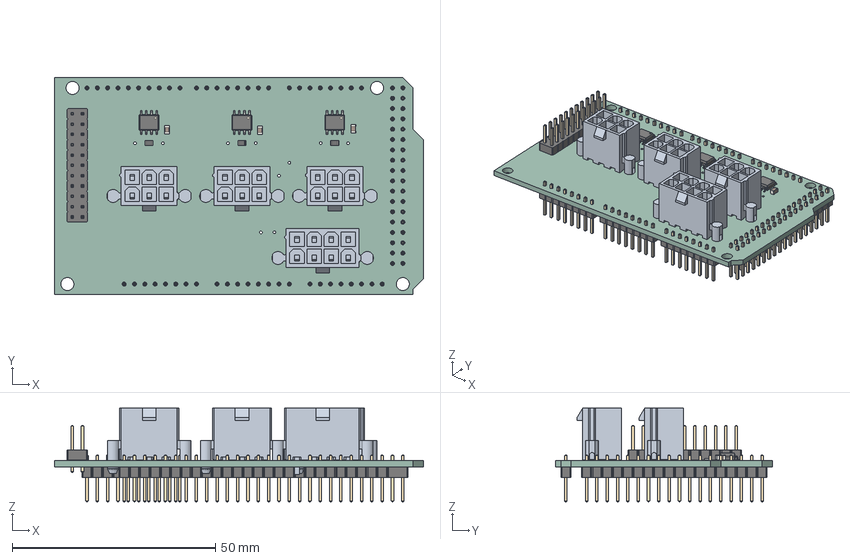
[picture p368: CAD file, 2026-04-08]
ECAD/PCBs/ABSIS/ABSIS_Bus_Master/MCAD/ABSIS_Bus_Master.step
90.8 x 53.3 x 23.0 mm
SOIC_8_39x49mm_P127mm x 3
R_0805_2012Metric x 3
C_0805_2012Metric x 3
PinHeader_2x11_P254mm_Vertical
PinHeader_2x18_P254mm_Vertical
PinHeader_1x08_P254mm_Vertical x 5
PinHeader_1x10_P254mm_Vertical
_autosave-ABSIS_Bus_Master_PCB
