jrsteensen/OpenHornet/ECAD/PCBs/ABSIS/ABSIS_Hall Sensor/MCAD/ABSIS_Hall Sensor.step

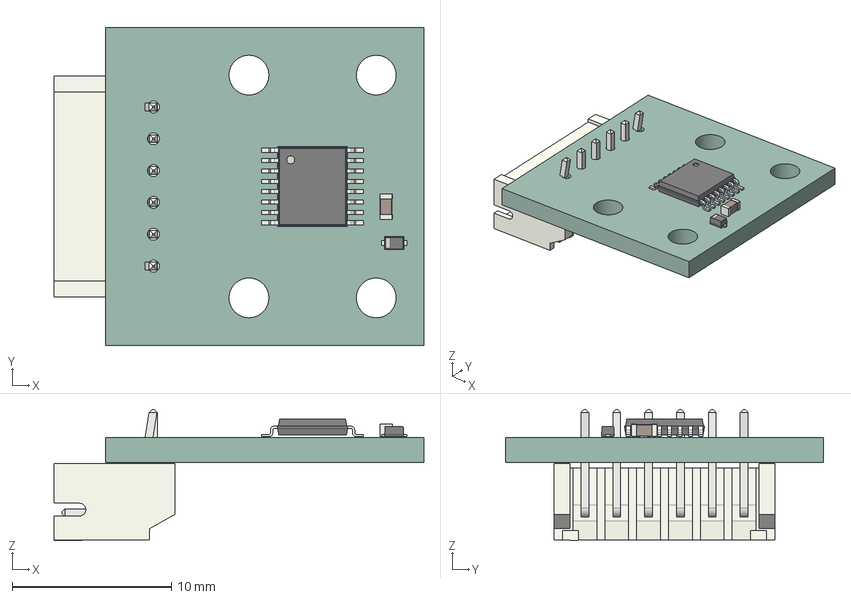
[picture p369: CAD file, 2024-02-26]
ECAD/PCBs/ABSIS/ABSIS_Hall Sensor/MCAD/ABSIS_Hall Sensor.step
23.2 x 20.0 x 8.25 mm
PCB
