jrsteensen/OpenHornet/ECAD/PCBs/ABSIS/ABSIS_Pit Management System/MCAD/ABSIS_Pit Management System.step

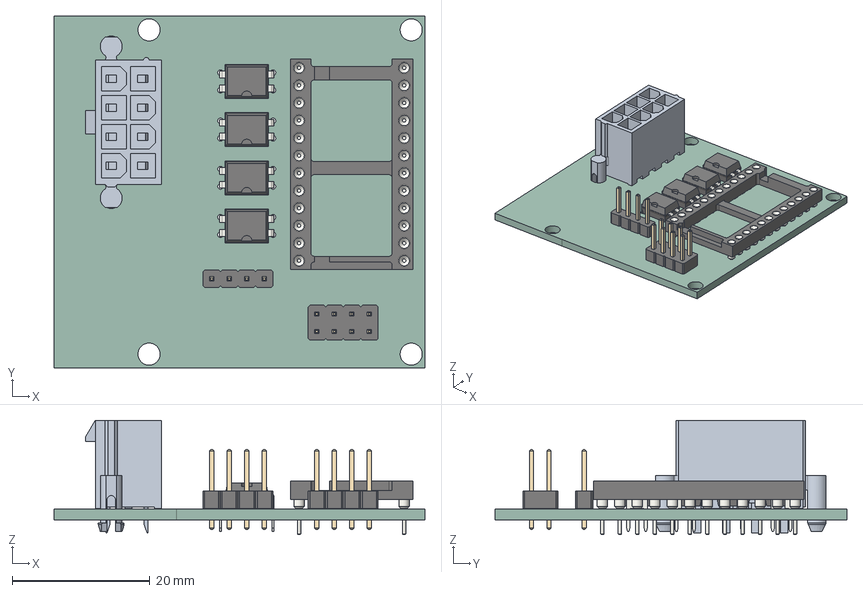
[picture p370: CAD file, 2024-02-26]
ECAD/PCBs/ABSIS/ABSIS_Pit Management System/MCAD/ABSIS_Pit Management System.step
53.8 x 51.0 x 16.6 mm
ABSIS_Pit Management System PCB
