jrsteensen/OpenHornet/ECAD/PCBs/ABSIS/NANO_IO/NANO_IO.step

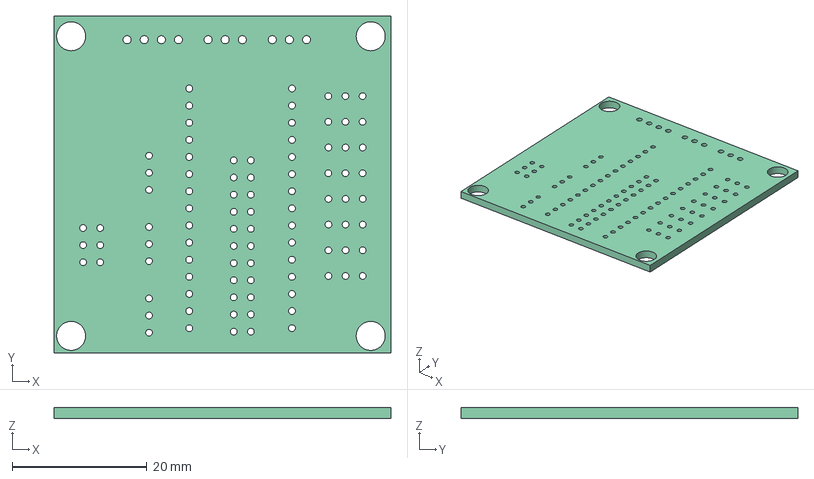
[picture p371: CAD file, 2019-11-14]
ECAD/PCBs/ABSIS/NANO_IO/NANO_IO.step
50.0 x 50.0 x 1.60 mm
Local_CS
Pcb
Step_Models
