jrsteensen/OpenHornet/ECAD/PCBs/ABSIS/NANO_IO/shapes3D/nano_io.wrl.sldprt

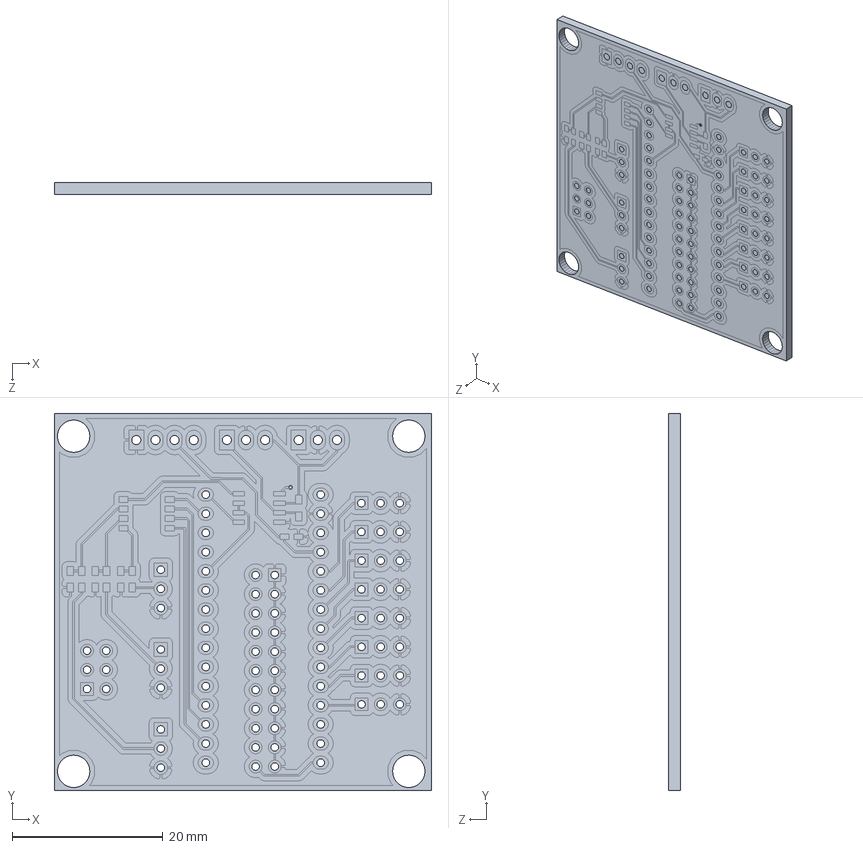
[picture p372: CAD file, 2019-10-15]
ECAD/PCBs/ABSIS/NANO_IO/shapes3D/nano_io.wrl.sldprt
50.0 x 50.0 x 1.61 mm
