jrsteensen/OpenHornet/ECAD/PCBs/ABSIS/NANO_IO_LITE/NANO_IO.step

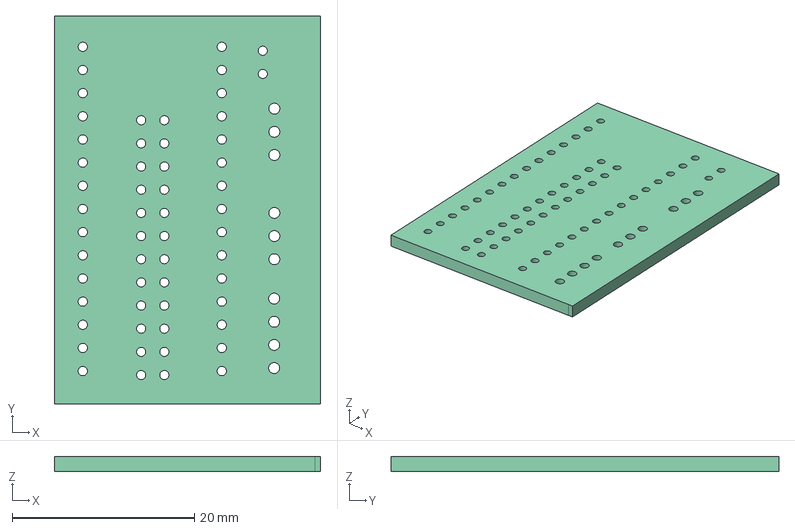
[picture p373: CAD file, 2019-11-14]
ECAD/PCBs/ABSIS/NANO_IO_LITE/NANO_IO.step
29.2 x 42.5 x 1.60 mm
Local_CS
Pcb
Step_Models
