jrsteensen/OpenHornet/ECAD/PCBs/ABSIS/xx_IN_DEV_ABSIS_Pro Micro/MCAD/ABSIS_Pro_Micro.step

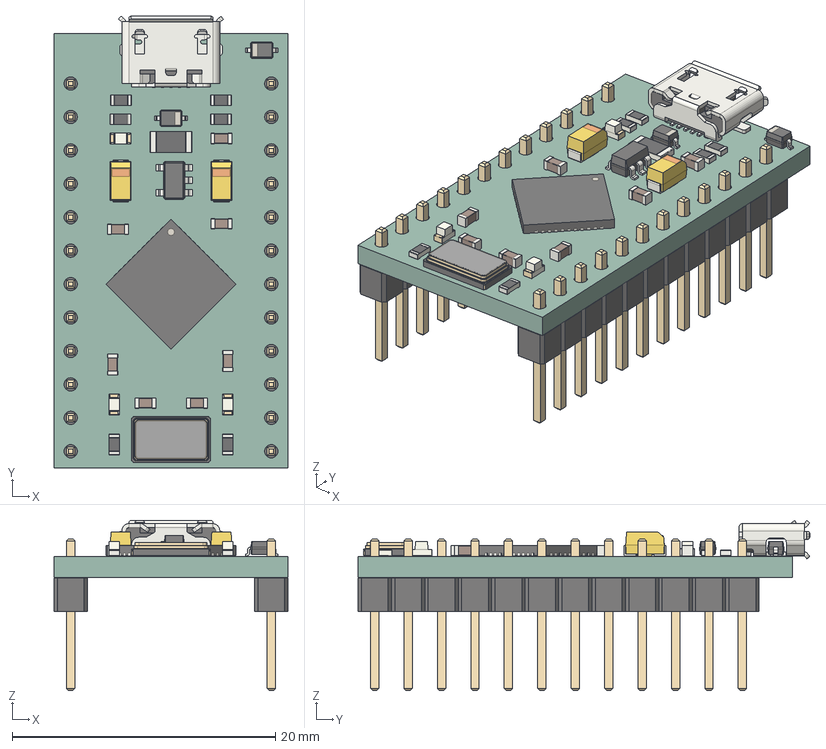
[picture p374: CAD file, 2026-05-03]
ECAD/PCBs/ABSIS/xx_IN_DEV_ABSIS_Pro Micro/MCAD/ABSIS_Pro_Micro.step
17.8 x 34.3 x 12.9 mm
C_0603_1608Metric x 7
CP_EIA_3216_18_Kemet_A x 2
R_0603_1608Metric x 6
LED_0603_1608Metric x 3
SOT_23_5
QFN-44-1EP_7x7mm_Pitch0.5mm
SMD_0603_4Pin
USB_Micro-B_Molex_47346-0001
Fuse_1206_3216Metric
D_SOD_323 x 2
PinHeader_1x12_P254mm_Vertical x 2
_autosave-ABSIS_Pro_Micro_PCB
