jrsteensen/OpenHornet/ECAD/PCBs/Backlight PCBs/Backlighting_Type A/ANT SEL PANEL/MCAD/ANT SEL PANEL.step

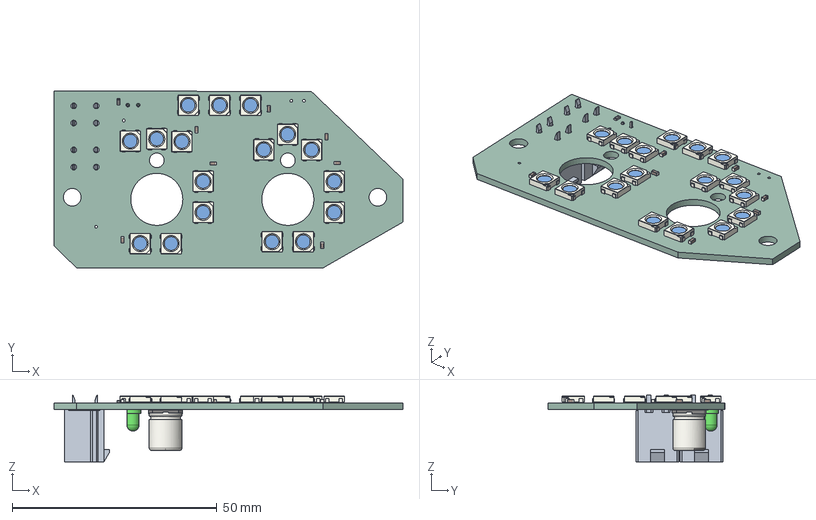
[picture p375: CAD file, 2024-02-26]
ECAD/PCBs/Backlight PCBs/Backlighting_Type A/ANT SEL PANEL/MCAD/ANT SEL PANEL.step
85.2 x 43.2 x 16.3 mm
ANT SEL PANEL PCB
