jrsteensen/OpenHornet/ECAD/PCBs/Backlight PCBs/Backlighting_Type A/APU ENG CRANK PANEL/MCAD/APU ENG CRANK PANEL.step

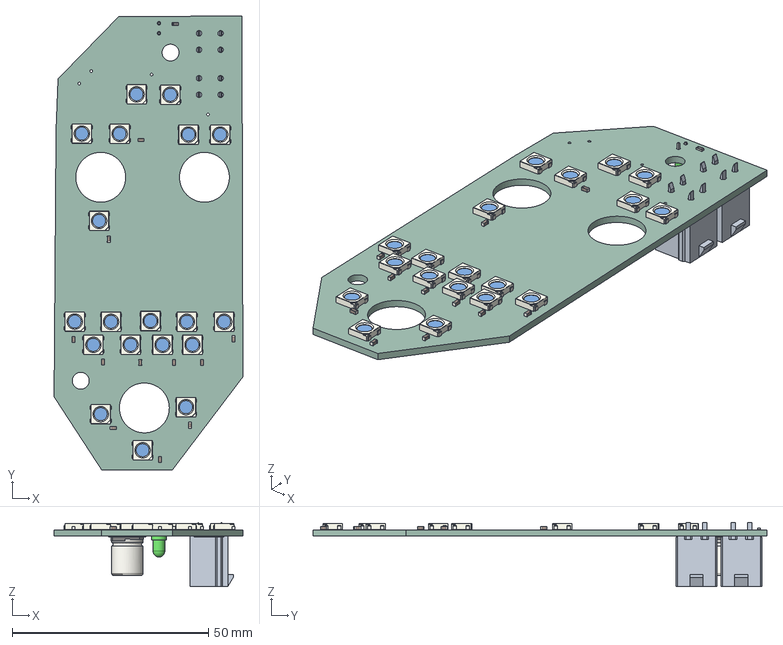
[picture p376: CAD file, 2024-02-26]
ECAD/PCBs/Backlight PCBs/Backlighting_Type A/APU ENG CRANK PANEL/MCAD/APU ENG CRANK PANEL.step
48.1 x 115.6 x 16.3 mm
_autosave-APU ENG CRANK PANEL PCB
