jrsteensen/OpenHornet/ECAD/PCBs/Backlight PCBs/Backlighting_Type A/AV COOL PANEL/MCAD/AV COOL PANEL.step

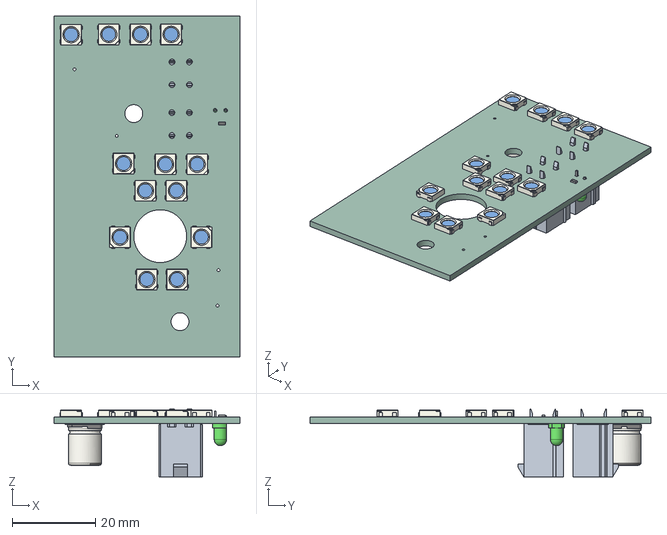
[picture p377: CAD file, 2024-02-26]
ECAD/PCBs/Backlight PCBs/Backlighting_Type A/AV COOL PANEL/MCAD/AV COOL PANEL.step
44.7 x 82.0 x 16.3 mm
AV COOL PANEL PCB
