jrsteensen/OpenHornet/ECAD/PCBs/Backlight PCBs/Backlighting_Type A/CAUTION LIGHTS PANEL/MCAD/CAUTION LIGHTS PANEL.step

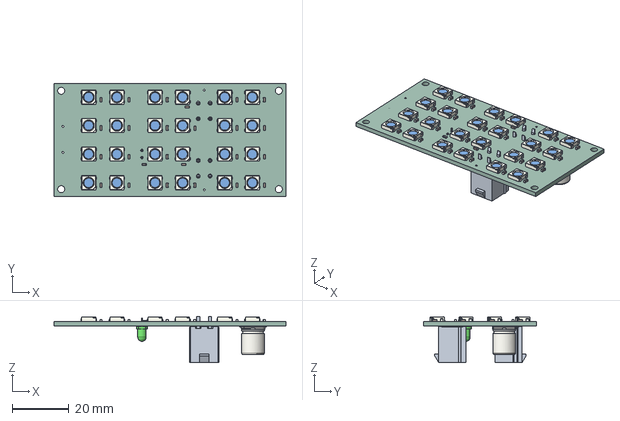
[picture p378: CAD file, 2024-02-26]
ECAD/PCBs/Backlight PCBs/Backlighting_Type A/CAUTION LIGHTS PANEL/MCAD/CAUTION LIGHTS PANEL.step
81.9 x 39.8 x 16.3 mm
CAUTION LIGHTS PANEL PCB
