jrsteensen/OpenHornet/ECAD/PCBs/Backlight PCBs/Backlighting_Type A/COMM PANEL/MCAD/COMM PANEL.step

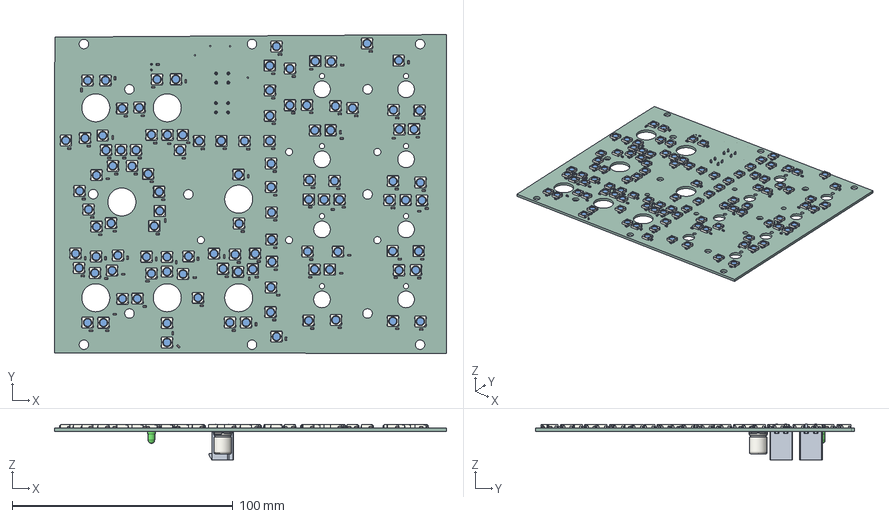
[picture p379: CAD file, 2024-02-26]
ECAD/PCBs/Backlight PCBs/Backlighting_Type A/COMM PANEL/MCAD/COMM PANEL.step
177.7 x 144.5 x 16.3 mm
COMM PANEL PCB
