jrsteensen/OpenHornet/ECAD/PCBs/Backlight PCBs/Backlighting_Type A/DEFOG PANEL/MCAD/DEFOG PANEL.step

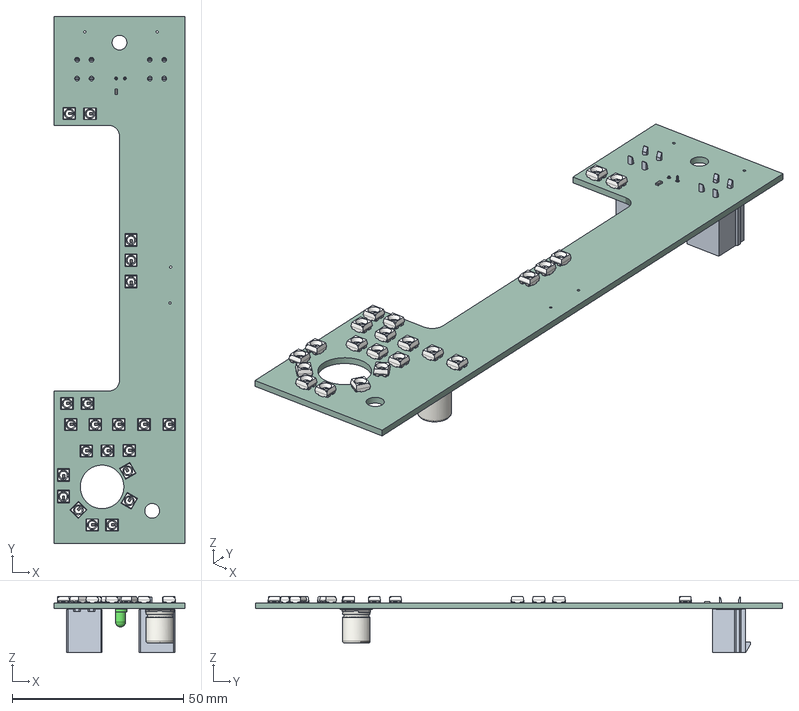
[picture p380: CAD file, 2024-02-26]
ECAD/PCBs/Backlight PCBs/Backlighting_Type A/DEFOG PANEL/MCAD/DEFOG PANEL.step
38.1 x 153.7 x 16.4 mm
DEFOG PANEL PCB
