jrsteensen/OpenHornet/ECAD/PCBs/Backlight PCBs/Backlighting_Type A/ECM DISP PANEL/MCAD/ECM DISP PANEL.step

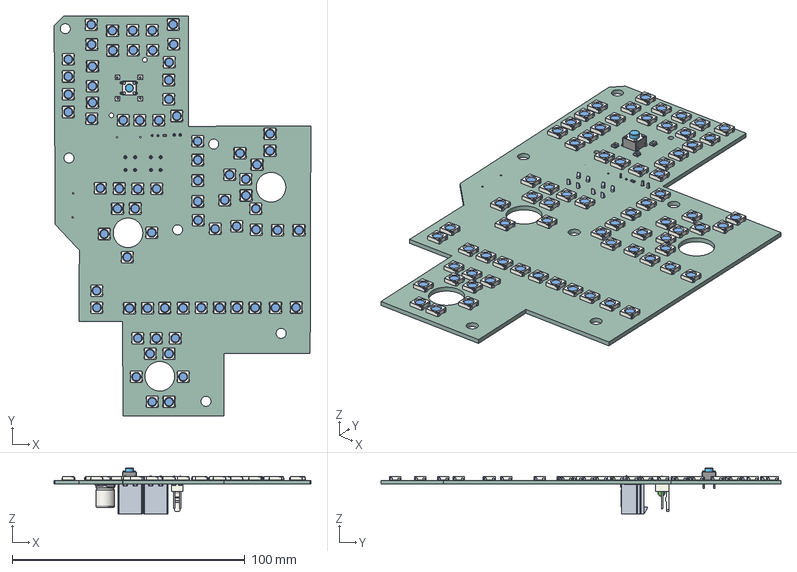
[picture p381: CAD file, 2024-02-26]
ECAD/PCBs/Backlight PCBs/Backlighting_Type A/ECM DISP PANEL/MCAD/ECM DISP PANEL.step
110.3 x 171.8 x 19.7 mm
ECM DISP PANEL PCB
