jrsteensen/OpenHornet/ECAD/PCBs/Backlight PCBs/Backlighting_Type A/ECS PANEL/MCAD/ECS PANEL.step

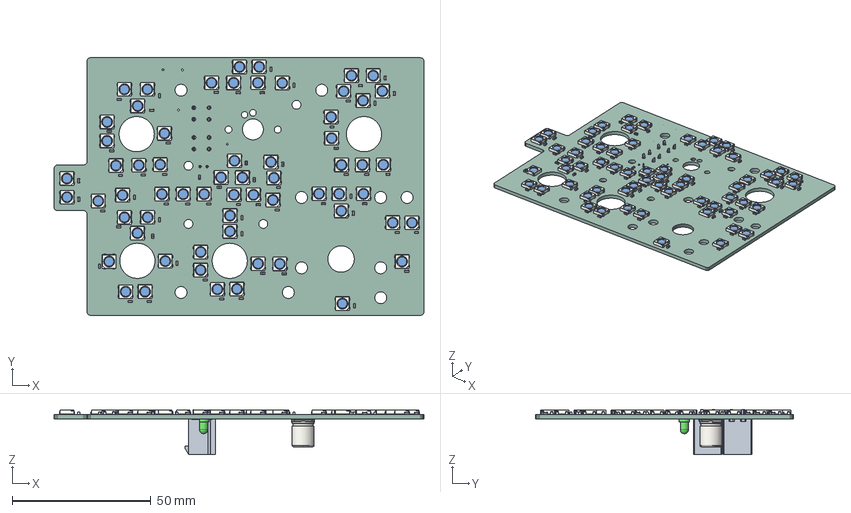
[picture p382: CAD file, 2024-02-26]
ECAD/PCBs/Backlight PCBs/Backlighting_Type A/ECS PANEL/MCAD/ECS PANEL.step
133.6 x 93.0 x 16.3 mm
ECS PANEL PCB
