jrsteensen/OpenHornet/ECAD/PCBs/Backlight PCBs/Backlighting_Type A/ELEC PANEL/MCAD/ELEC PANEL.step

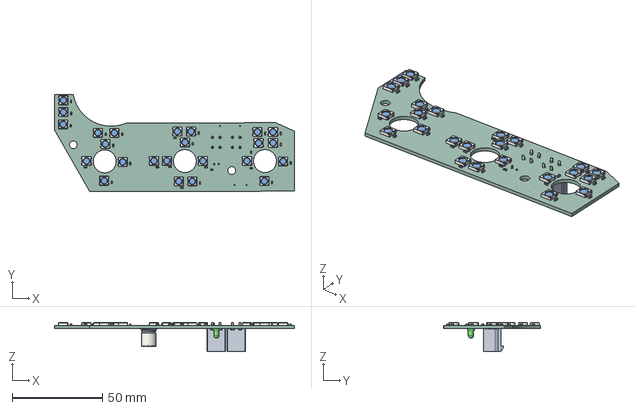
[picture p383: CAD file, 2024-02-26]
ECAD/PCBs/Backlight PCBs/Backlighting_Type A/ELEC PANEL/MCAD/ELEC PANEL.step
133.1 x 53.8 x 16.3 mm
ELEC PANEL PCB
