jrsteensen/OpenHornet/ECAD/PCBs/Backlight PCBs/Backlighting_Type A/EXT LT PANEL/MCAD/EXT LT PANEL.step

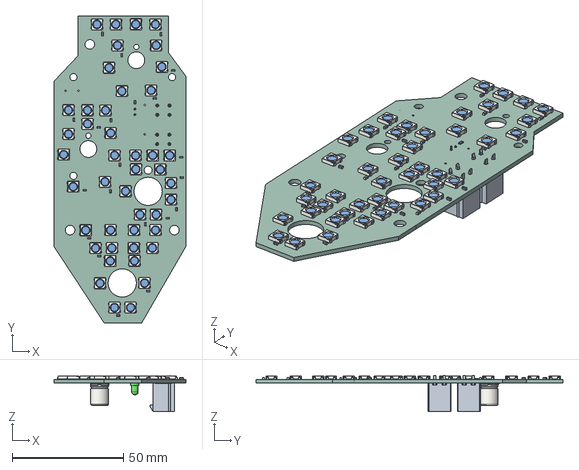
[picture p384: CAD file, 2024-02-26]
ECAD/PCBs/Backlight PCBs/Backlighting_Type A/EXT LT PANEL/MCAD/EXT LT PANEL.step
59.4 x 138.3 x 16.3 mm
EXT LT PANEL PCB
