jrsteensen/OpenHornet/ECAD/PCBs/Backlight PCBs/Backlighting_Type A/FCS PANEL/MCAD/FCS PANEL.step

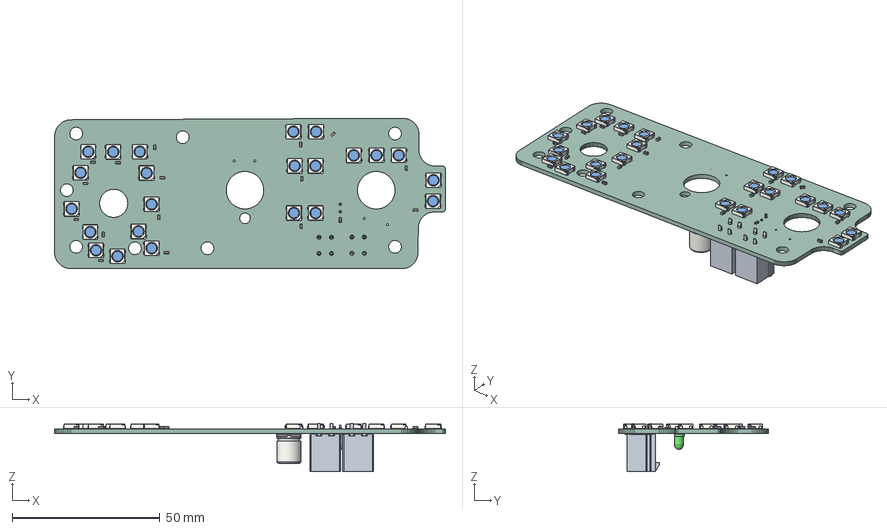
[picture p385: CAD file, 2024-02-26]
ECAD/PCBs/Backlight PCBs/Backlighting_Type A/FCS PANEL/MCAD/FCS PANEL.step
132.4 x 51.0 x 16.3 mm
FCS PANEL PCB
