jrsteensen/OpenHornet/ECAD/PCBs/Backlight PCBs/Backlighting_Type A/FIRE TEST PANEL/MCAD/FIRE TEST PANEL.step

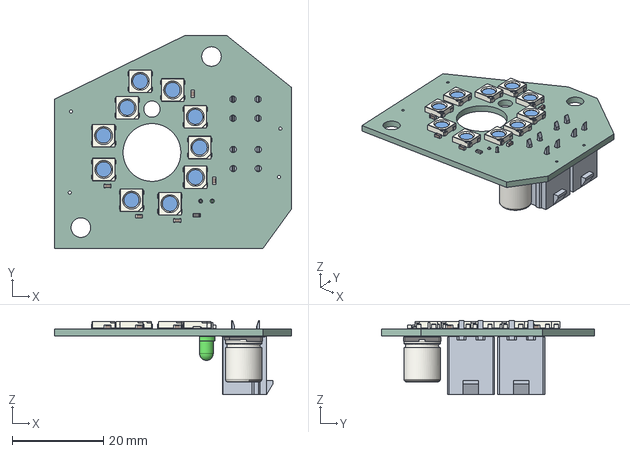
[picture p386: CAD file, 2024-02-26]
ECAD/PCBs/Backlight PCBs/Backlighting_Type A/FIRE TEST PANEL/MCAD/FIRE TEST PANEL.step
52.1 x 46.8 x 16.3 mm
FIRE TEST PANEL PCB
