jrsteensen/OpenHornet/ECAD/PCBs/Backlight PCBs/Backlighting_Type A/FUEL PANEL/MCAD/FUEL PANEL.step

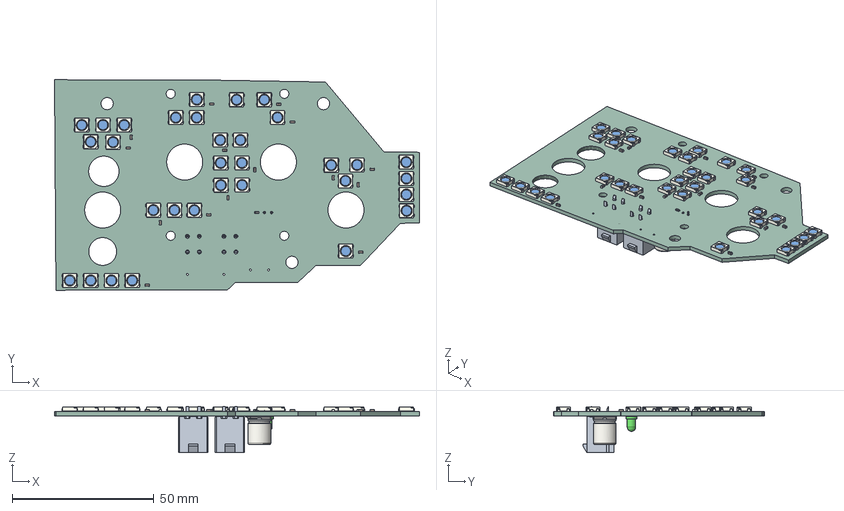
[picture p387: CAD file, 2024-02-26]
ECAD/PCBs/Backlight PCBs/Backlighting_Type A/FUEL PANEL/MCAD/FUEL PANEL.step
128.6 x 74.2 x 16.3 mm
FUEL PANEL PCB
