jrsteensen/OpenHornet/ECAD/PCBs/Backlight PCBs/Backlighting_Type A/GEN TIE PANEL/MCAD/GEN TIE PANEL.step

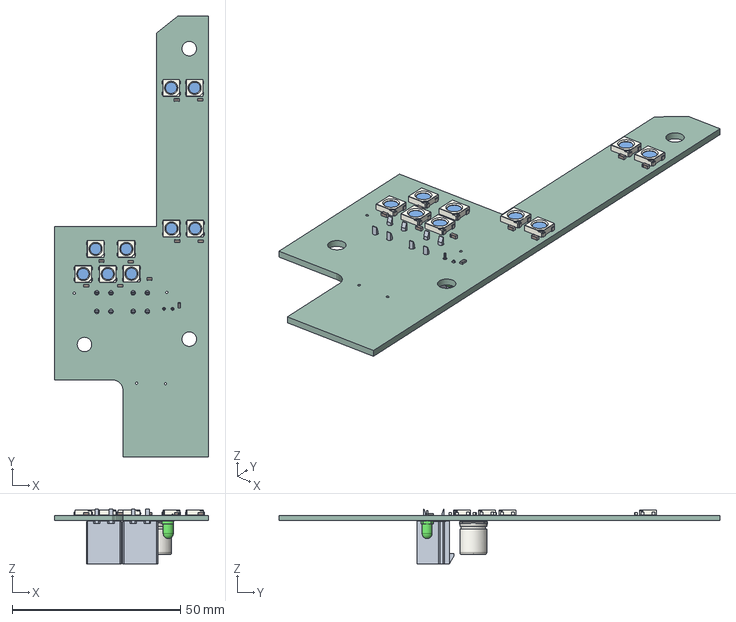
[picture p388: CAD file, 2024-02-26]
ECAD/PCBs/Backlight PCBs/Backlighting_Type A/GEN TIE PANEL/MCAD/GEN TIE PANEL.step
45.7 x 130.8 x 16.3 mm
GEN TIE PANEL PCB
