jrsteensen/OpenHornet/ECAD/PCBs/Backlight PCBs/Backlighting_Type A/HUD PANEL/MCAD/HUD PANEL.step

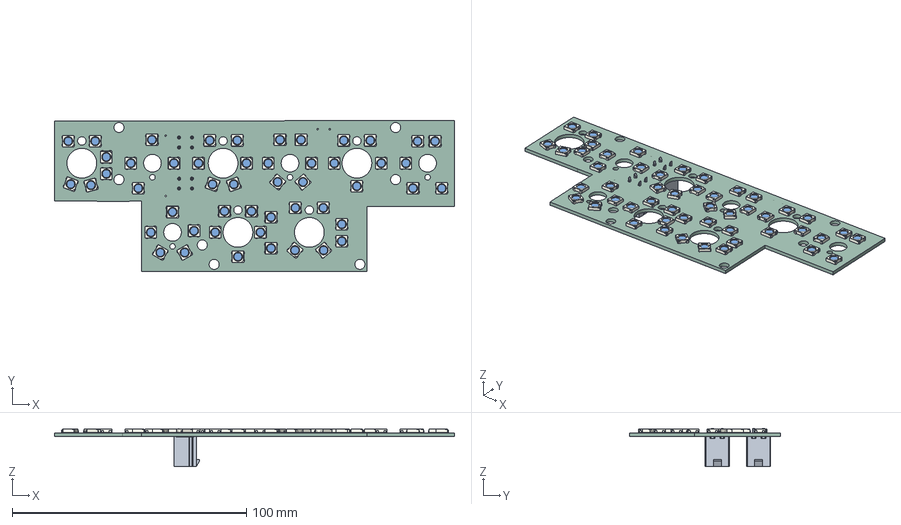
[picture p389: CAD file, 2024-02-26]
ECAD/PCBs/Backlight PCBs/Backlighting_Type A/HUD PANEL/MCAD/HUD PANEL.step
170.8 x 64.5 x 16.3 mm
_autosave-HUD PANEL PCB
