jrsteensen/OpenHornet/ECAD/PCBs/Backlight PCBs/Backlighting_Type A/HUD VID RCD PANEL/MCAD/HUD VID RCD PANEL.step

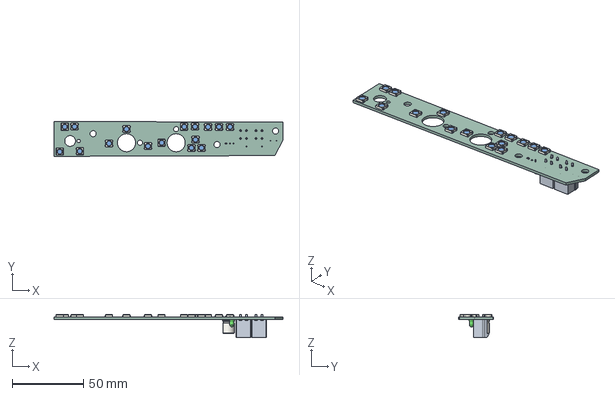
[picture p390: CAD file, 2024-02-26]
ECAD/PCBs/Backlight PCBs/Backlighting_Type A/HUD VID RCD PANEL/MCAD/HUD VID RCD PANEL.step
161.0 x 24.4 x 16.3 mm
_autosave-HUD VID RCD PANEL PCB
