jrsteensen/OpenHornet/ECAD/PCBs/Backlight PCBs/Backlighting_Type A/HYD ISO PANEL/MCAD/HYD ISO PANEL.step

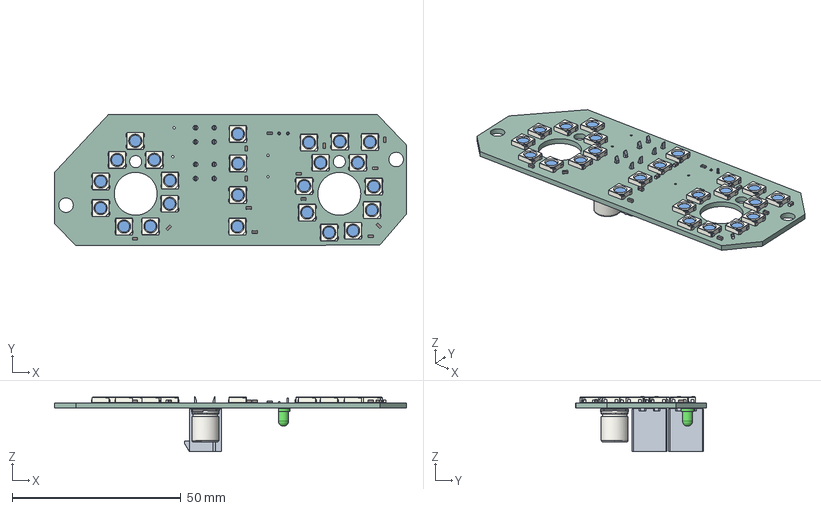
[picture p391: CAD file, 2024-02-26]
ECAD/PCBs/Backlight PCBs/Backlighting_Type A/HYD ISO PANEL/MCAD/HYD ISO PANEL.step
104.3 x 38.9 x 16.3 mm
_autosave-HYD ISO PANEL PCB
