jrsteensen/OpenHornet/ECAD/PCBs/Backlight PCBs/Backlighting_Type A/INTR LT PANEL/MCAD/INTR LT PANEL.step

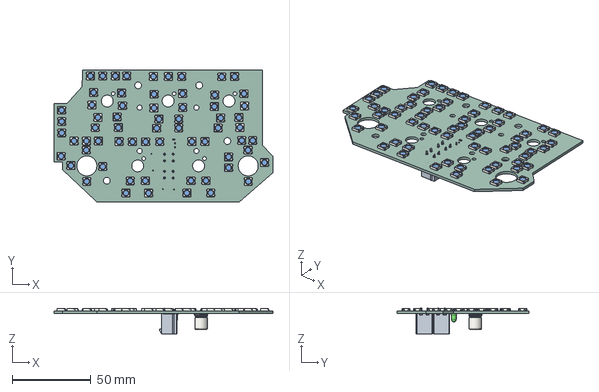
[picture p392: CAD file, 2024-02-26]
ECAD/PCBs/Backlight PCBs/Backlighting_Type A/INTR LT PANEL/MCAD/INTR LT PANEL.step
138.9 x 83.9 x 16.3 mm
INTR LT PANEL PCB
