jrsteensen/OpenHornet/ECAD/PCBs/Backlight PCBs/Backlighting_Type A/JETT STATION SELECT PLACARD/MCAD/JETT STATION SELECT PLACARD.step

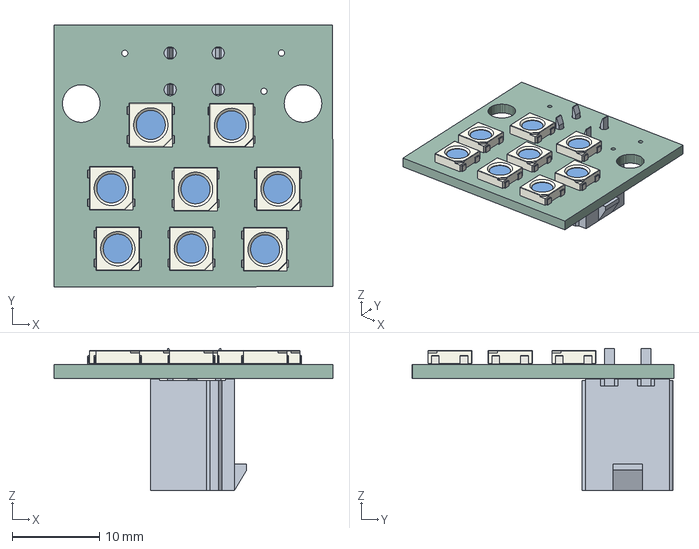
[picture p393: CAD file, 2024-02-26]
ECAD/PCBs/Backlight PCBs/Backlighting_Type A/JETT STATION SELECT PLACARD/MCAD/JETT STATION SELECT PLACARD.step
32.0 x 30.0 x 16.3 mm
_autosave-JETT STATION SELECT PLACARD PCB
