jrsteensen/OpenHornet/ECAD/PCBs/Backlight PCBs/Backlighting_Type A/KY-58 PANEL/MCAD/KY-58 PANEL.step

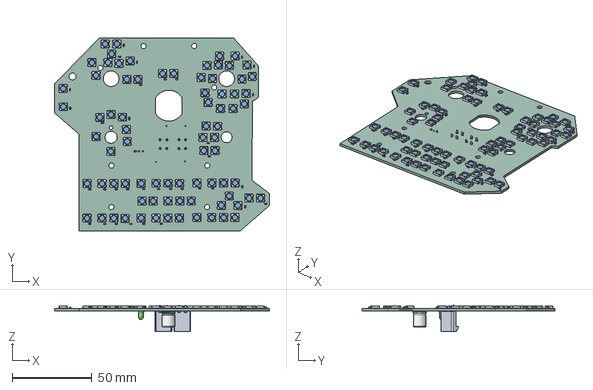
[picture p394: CAD file, 2024-02-26]
ECAD/PCBs/Backlight PCBs/Backlighting_Type A/KY-58 PANEL/MCAD/KY-58 PANEL.step
134.7 x 120.8 x 16.3 mm
KY-58 PANEL PCB
