jrsteensen/OpenHornet/ECAD/PCBs/Backlight PCBs/Backlighting_Type A/LDG WING FOLD PLACARD/MCAD/LDG WING FOLD PLACARD.step

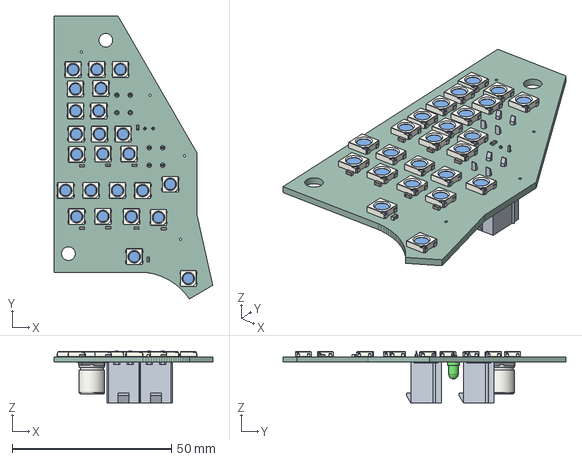
[picture p396: CAD file, 2024-02-26]
ECAD/PCBs/Backlight PCBs/Backlighting_Type A/LDG WING FOLD PLACARD/MCAD/LDG WING FOLD PLACARD.step
49.8 x 88.9 x 16.3 mm
LDG WING FOLD PLACARD PCB
