jrsteensen/OpenHornet/ECAD/PCBs/Backlight PCBs/Backlighting_Type A/LEFT CIRCUIT BREAKER/MCAD/LEFT CIRCUIT BREAKER.step

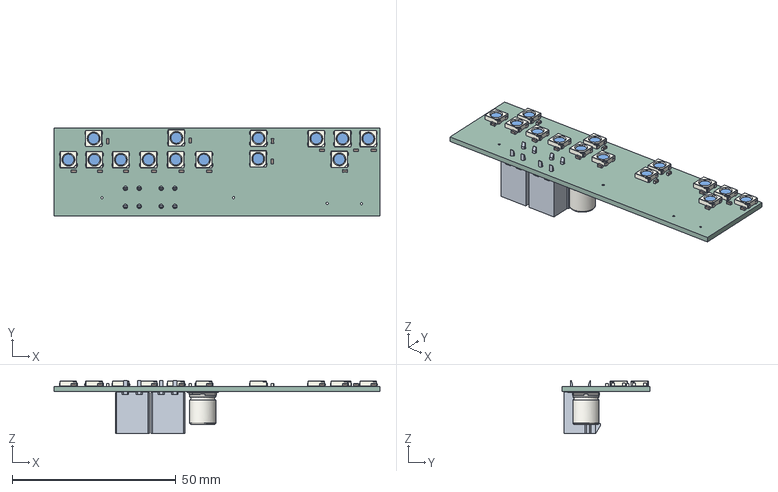
[picture p397: CAD file, 2024-02-26]
ECAD/PCBs/Backlight PCBs/Backlighting_Type A/LEFT CIRCUIT BREAKER/MCAD/LEFT CIRCUIT BREAKER.step
99.5 x 27.0 x 16.3 mm
LEFT CIRCUIT BREAKER PCB
