jrsteensen/OpenHornet/ECAD/PCBs/Backlight PCBs/Backlighting_Type A/MASTER ARM PANEL/MCAD/MASTER ARM PANEL.step

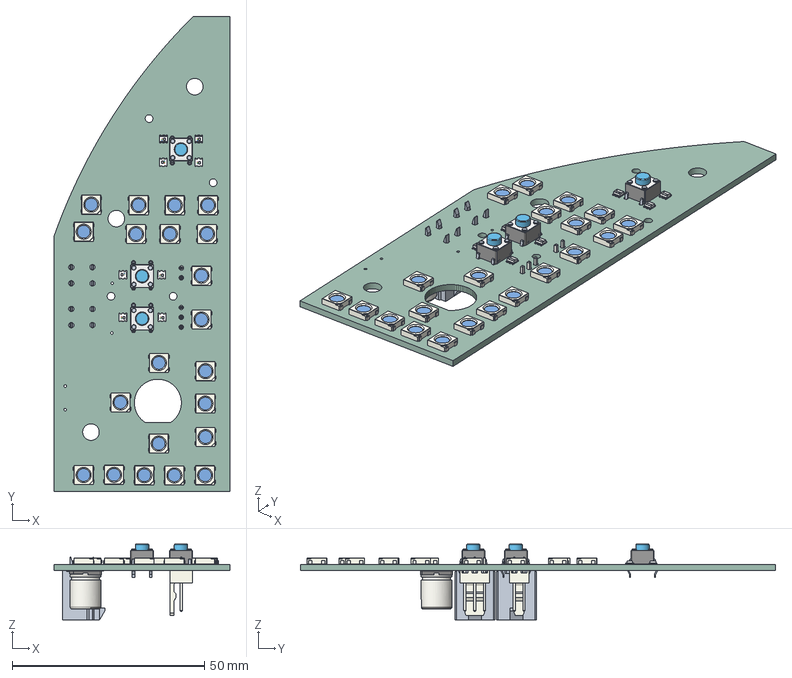
[picture p398: CAD file, 2024-02-26]
ECAD/PCBs/Backlight PCBs/Backlighting_Type A/MASTER ARM PANEL/MCAD/MASTER ARM PANEL.step
45.7 x 123.5 x 19.7 mm
MASTER ARM PANEL PCB
