jrsteensen/OpenHornet/ECAD/PCBs/Backlight PCBs/Backlighting_Type A/OBOGS PANEL/MCAD/OBOGS PANEL.step

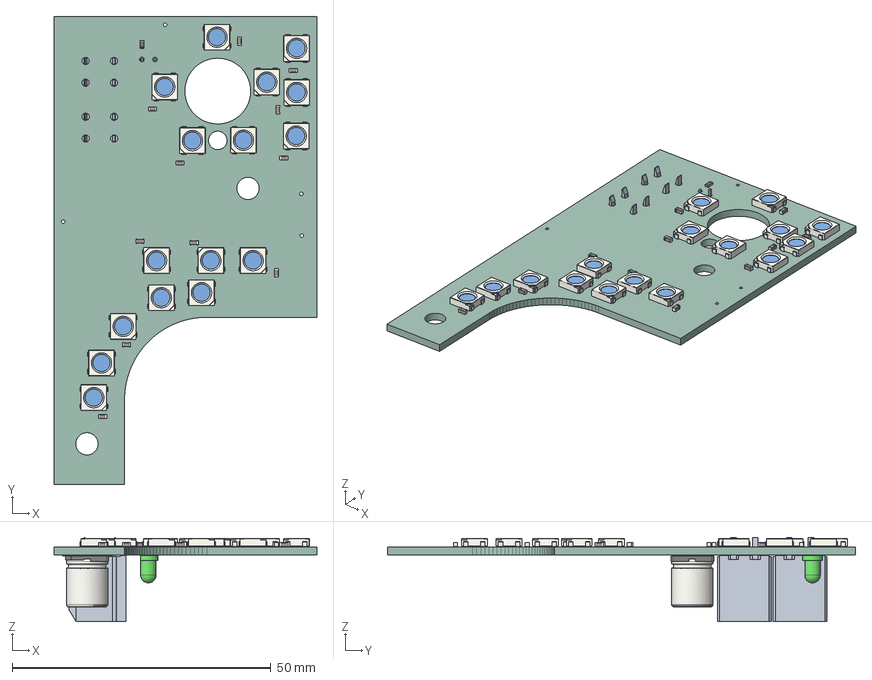
[picture p399: CAD file, 2024-02-26]
ECAD/PCBs/Backlight PCBs/Backlighting_Type A/OBOGS PANEL/MCAD/OBOGS PANEL.step
50.8 x 90.4 x 16.3 mm
OBOGS PANEL PCB
