jrsteensen/OpenHornet/ECAD/PCBs/Backlight PCBs/Backlighting_Type A/SELECT JETT PANEL/MCAD/SELECT JETT PANEL.step

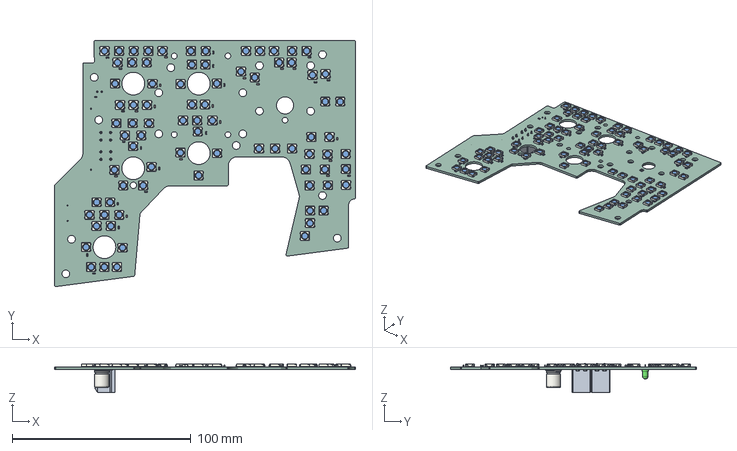
[picture p400: CAD file, 2024-02-26]
ECAD/PCBs/Backlight PCBs/Backlighting_Type A/SELECT JETT PANEL/MCAD/SELECT JETT PANEL.step
168.3 x 137.6 x 16.3 mm
PCB
