jrsteensen/OpenHornet/ECAD/PCBs/Backlight PCBs/Backlighting_Type A/SIM CONTROL PANEL/MCAD/SIM CONTROL PANEL.step

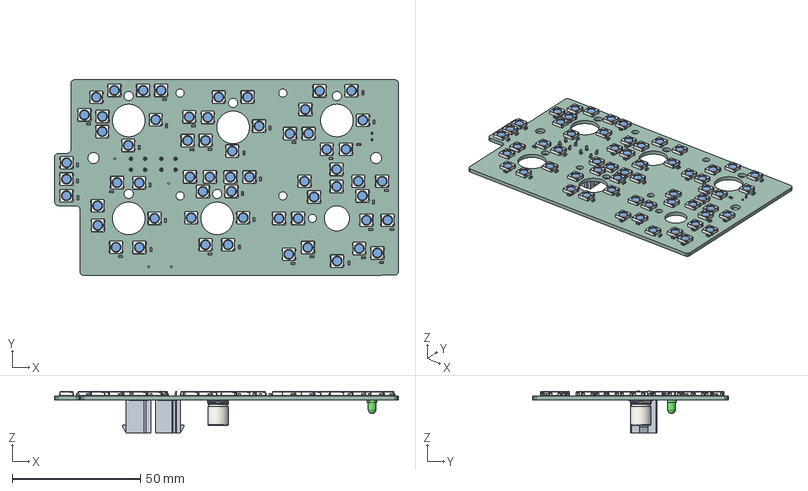
[picture p401: CAD file, 2024-02-26]
ECAD/PCBs/Backlight PCBs/Backlighting_Type A/SIM CONTROL PANEL/MCAD/SIM CONTROL PANEL.step
133.9 x 76.2 x 16.3 mm
SIM CONTROL PANEL PCB
