jrsteensen/OpenHornet/ECAD/PCBs/Backlight PCBs/Backlighting_Type A/SIM POWER PANEL/MCAD/SIM POWER PANEL.step

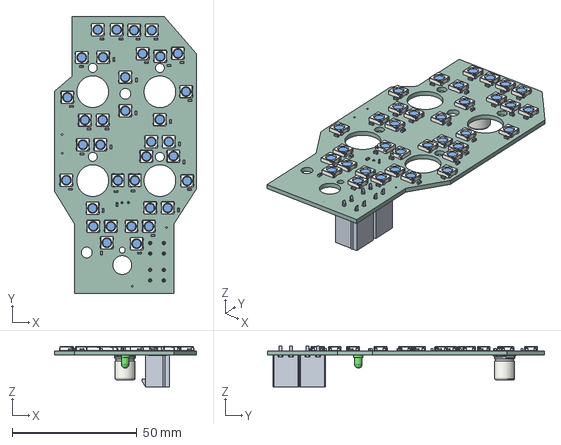
[picture p402: CAD file, 2024-02-26]
ECAD/PCBs/Backlight PCBs/Backlighting_Type A/SIM POWER PANEL/MCAD/SIM POWER PANEL.step
57.0 x 111.0 x 16.3 mm
SIM POWER PANEL PCB
