jrsteensen/OpenHornet/ECAD/PCBs/Backlight PCBs/Backlighting_Type A/SNSR PANEL/MCAD/SNSR PANEL.step

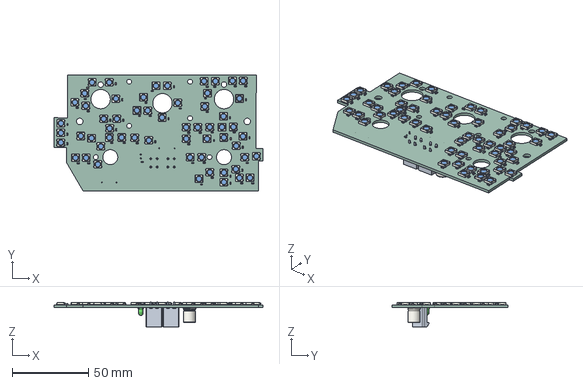
[picture p403: CAD file, 2024-02-26]
ECAD/PCBs/Backlight PCBs/Backlighting_Type A/SNSR PANEL/MCAD/SNSR PANEL.step
137.2 x 76.2 x 16.3 mm
SNSR PANEL PCB
