jrsteensen/OpenHornet/ECAD/PCBs/Backlight PCBs/Backlighting_Type A/SPIN RCV PANEL/MCAD/SPIN RCV PANEL.step

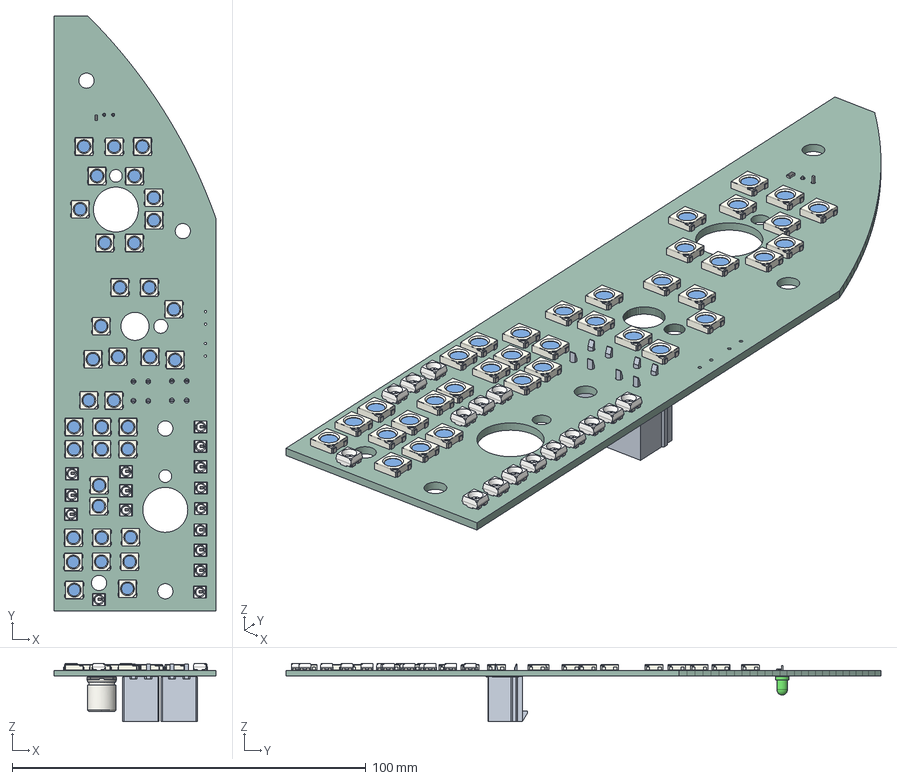
[picture p404: CAD file, 2024-02-26]
ECAD/PCBs/Backlight PCBs/Backlighting_Type A/SPIN RCV PANEL/MCAD/SPIN RCV PANEL.step
45.7 x 168.3 x 16.4 mm
_autosave-SPIN RCV PANEL PCB
