jrsteensen/OpenHornet/ECAD/PCBs/Backlight PCBs/Backlighting_Type B/ECS PANEL/Assets/ECS Panel Legend Plate.DXF

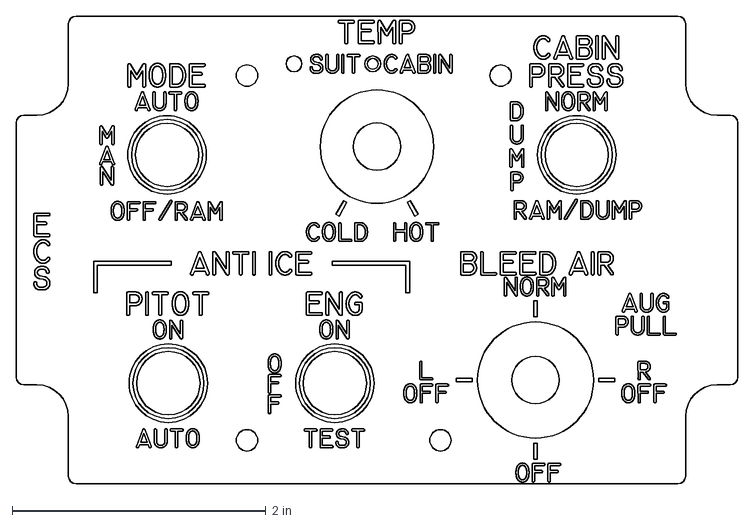
[picture p405: CAD file, 2022-09-23]
ECAD/PCBs/Backlight PCBs/Backlighting_Type B/ECS PANEL/Assets/ECS Panel Legend Plate.DXF
5.69 x 3.69 in
