jrsteensen/OpenHornet/ECAD/PCBs/Functional PCBs/AMPCD/MCAD/AMPCD.step

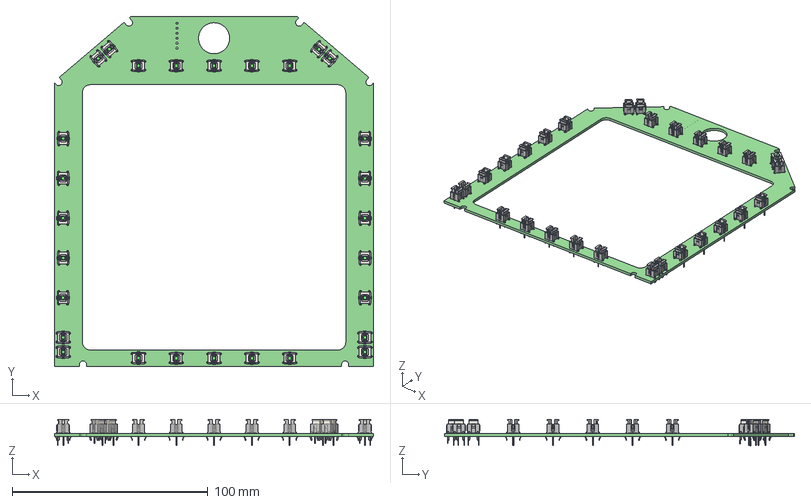
[picture p406: CAD file, 2024-02-26]
ECAD/PCBs/Functional PCBs/AMPCD/MCAD/AMPCD.step
162.9 x 178.9 x 13.4 mm
AMPCD PCB
