jrsteensen/OpenHornet/ECAD/PCBs/Functional PCBs/CONTROLLER_AMPCD DDI/MCAD/CONTROLLER_AMPCD DDI.step

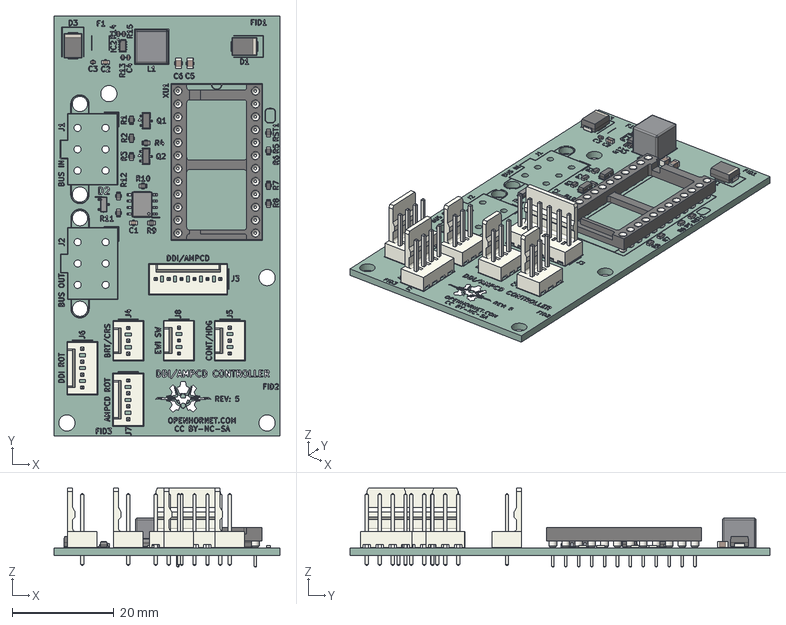
[picture p407: CAD file, 2026-10-04]
ECAD/PCBs/Functional PCBs/CONTROLLER_AMPCD DDI/MCAD/CONTROLLER_AMPCD DDI.step
44.5 x 82.5 x 15.5 mm
Molex_KK-254_AE-6410-06A_1x06_P2.54mm_Vertical
Molex_KK-254_AE-6410-03A_1x03_P2.54mm_Vertical x 3
Molex_KK-254_AE-6410-04A_1x04_P2.54mm_Vertical x 2
SOT-23 x 2
R_0603_1608Metric x 12
DIP-24_W15.24mm_Socket
SOT-583-8
C_0402_1005Metric x 2
PinsArrayLR
L_Bourns_SRP6060FA
C_0805_2012Metric x 2
PinsArrayL
FilletPinR
C_0603_1608Metric x 2
D_SMB x 2
R_0402_1005Metric x 3
CONTROLLER_AMPCD DDI_silkscreen x 2
CONTROLLER_AMPCD DDI_PCB
