jrsteensen/OpenHornet/ECAD/PCBs/Functional PCBs/CONTROLLER_Radar Altimeter/MCAD/CONTROLLER_Radar Altimeter.step

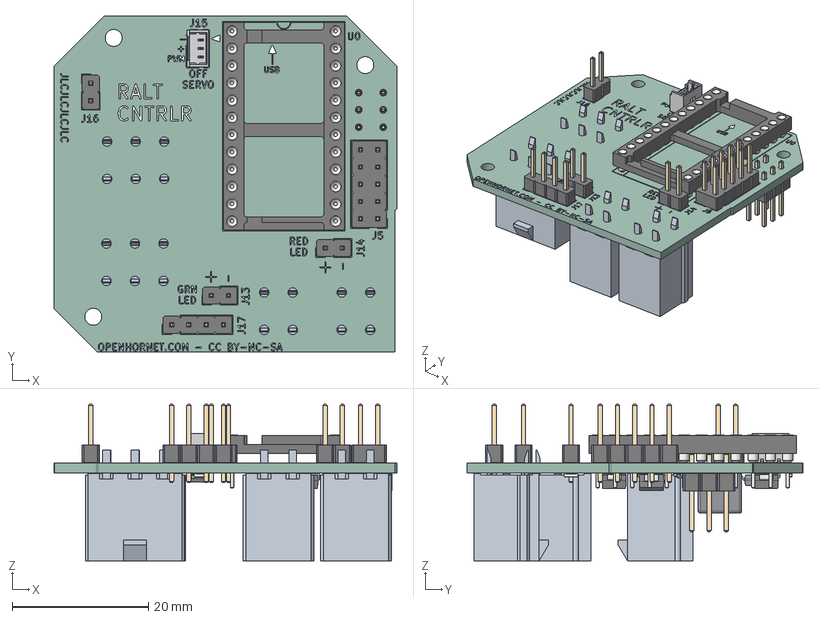
[picture p408: CAD file, 2026-10-04]
ECAD/PCBs/Functional PCBs/CONTROLLER_Radar Altimeter/MCAD/CONTROLLER_Radar Altimeter.step
50.4 x 49.4 x 23.0 mm
PinHeader_1x02_P2.54mm_Vertical x 3
125SH-B-03-TS
DIP-24_W15.24mm_Socket
PinHeader_1x04_P2.54mm_Vertical
PinHeader_2x05_P2.54mm_Vertical
R_0805_2012Metric x 2
C_0402_1005Metric x 2
Molex_Mini-Fit_Jr_5566-04A_2x02_P4.20mm_Vertical x 2
PinsArrayLR
R_0603_1608Metric x 6
C_0603_1608Metric x 2
R_0402_1005Metric x 3
SOT-583-8
C_0805_2012Metric x 2
D_SMB x 2
PinHeader_1x03_P2.54mm_Vertical x 2
SOT-23
FilletPin1
FilletPin2
PinsArrayL
FilletPinR
L_Bourns_SRP6060FA
CONTROLLER_Radar Altimeter_silkscreen x 2
CONTROLLER_Radar Altimeter_PCB
