jrsteensen/OpenHornet/ECAD/PCBs/Functional PCBs/CONTROLLER_Standby Instrument/MCAD/CONTROLLER_Standby Instrument.step

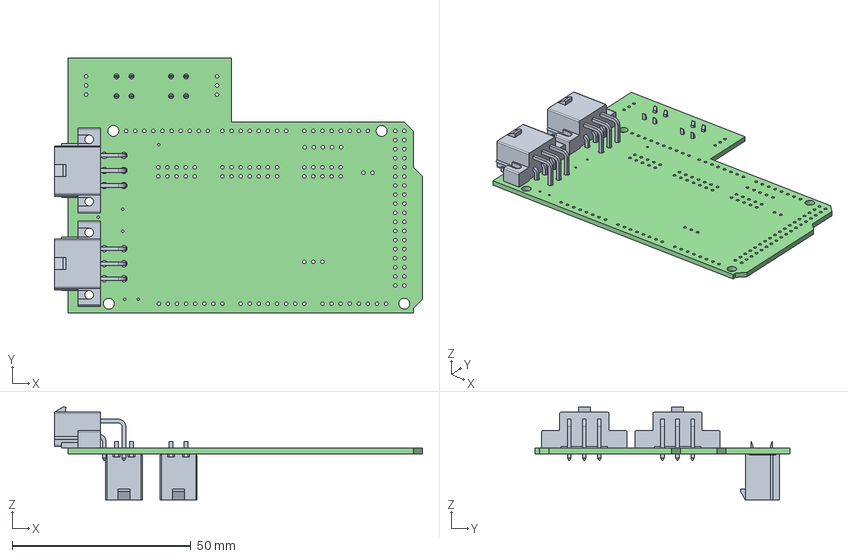
[picture p409: CAD file, 2024-02-26]
ECAD/PCBs/Functional PCBs/CONTROLLER_Standby Instrument/MCAD/CONTROLLER_Standby Instrument.step
102.8 x 71.1 x 25.9 mm
CONTROLLER_Standby Instrument PCB
