jrsteensen/OpenHornet/ECAD/PCBs/Functional PCBs/CONTROLLER_Stick/MCAD/CONTROLLER_Stick.step

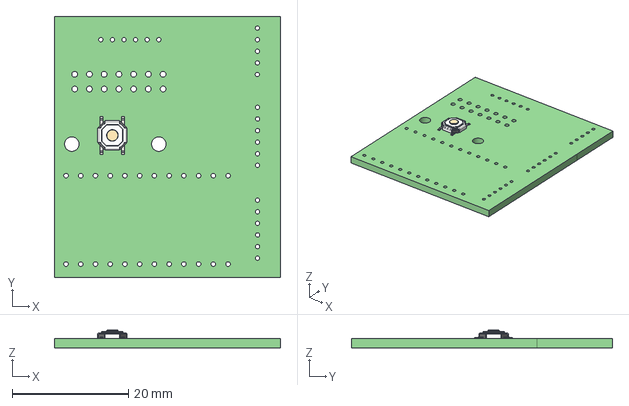
[picture p410: CAD file, 2024-02-26]
ECAD/PCBs/Functional PCBs/CONTROLLER_Stick/MCAD/CONTROLLER_Stick.step
39.0 x 45.0 x 3.05 mm
CONTROLLER_Stick PCB
