jrsteensen/OpenHornet/ECAD/PCBs/Functional PCBs/DDI/MCAD/DDI.step

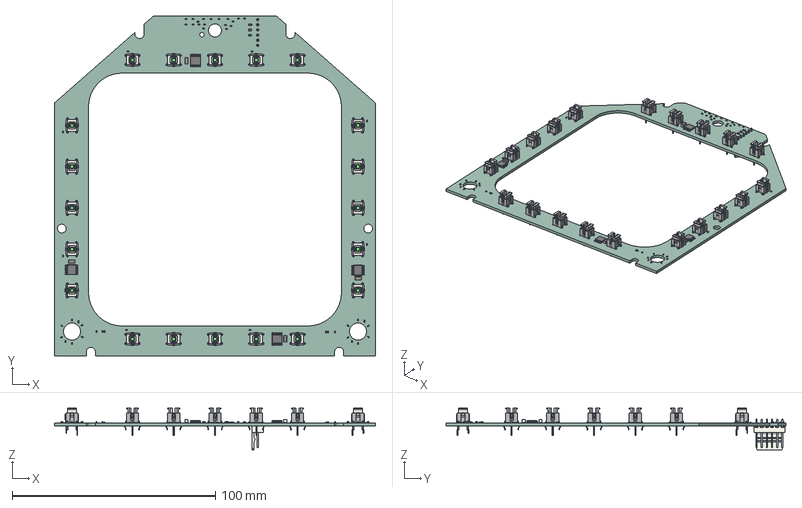
[picture p411: CAD file, 2026-04-08]
ECAD/PCBs/Functional PCBs/DDI/MCAD/DDI.step
158.2 x 167.4 x 20.6 mm
C_1206_3216Metric x 4
LED_0402_1005Metric x 30
R_0603_1608Metric x 3
R_0402_1005Metric x 18
TSSOP_16_44x5mm_P065mm x 4
TL1240GQ x 20
Molex_AE_6410_06A x 2
_autosave-DDI_PCB
