jrsteensen/OpenHornet/ECAD/PCBs/Functional PCBs/EYEBROW WARNING INDICATOR_LEFT/MCAD/EYEBROW WARNING INDICATOR_LEFT.step

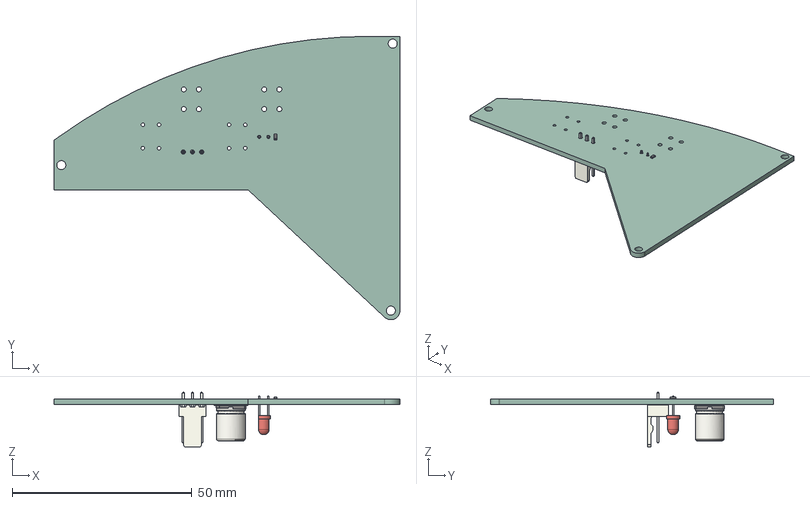
[picture p412: CAD file, 2026-04-12]
ECAD/PCBs/Functional PCBs/EYEBROW WARNING INDICATOR_LEFT/MCAD/EYEBROW WARNING INDICATOR_LEFT.step
96.1 x 78.8 x 15.3 mm
R_0603_1608Metric
CP_Elec_8x10
LED_D3.0mm
Molex_AE_6410_03A
_autosave-EYEBROW WARNING INDICATOR_LEFT_PCB
