jrsteensen/OpenHornet/ECAD/PCBs/Functional PCBs/EYEBROW WARNING INDICATOR_RIGHT/MCAD/EYEBROW WARNING INDICATOR_RIGHT.step

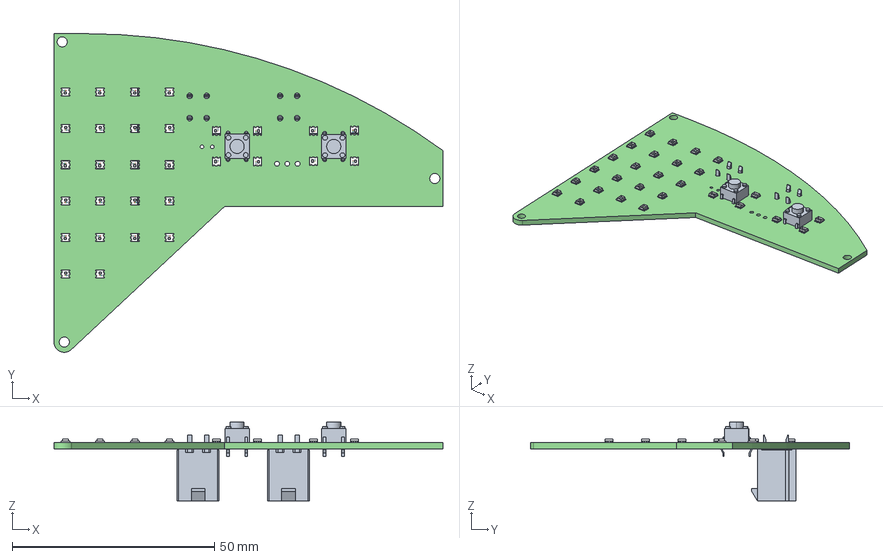
[picture p413: CAD file, 2024-02-26]
ECAD/PCBs/Functional PCBs/EYEBROW WARNING INDICATOR_RIGHT/MCAD/EYEBROW WARNING INDICATOR_RIGHT.step
96.1 x 78.8 x 19.5 mm
_autosave-EYEBROW WARNING INDICATOR_RIGHT PCB
