jrsteensen/OpenHornet/ECAD/PCBs/Functional PCBs/GAUGE_Analog Instruments/MCAD/GAUGE_Analog Instruments.step

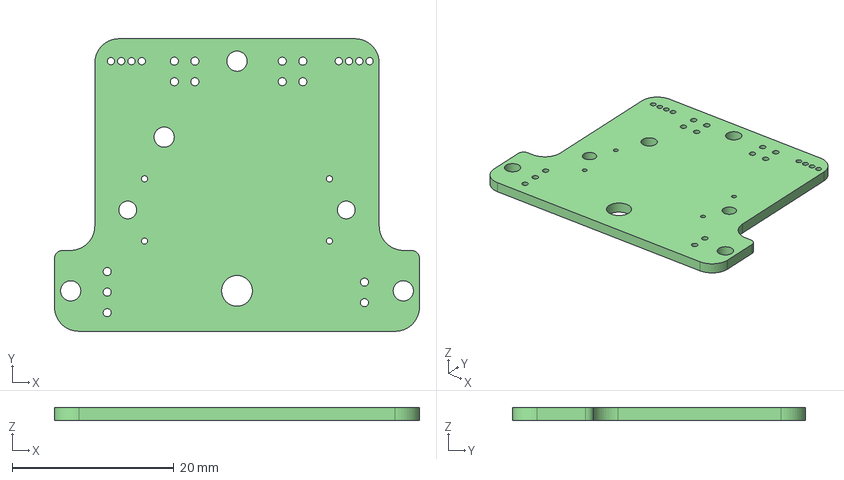
[picture p414: CAD file, 2024-02-26]
ECAD/PCBs/Functional PCBs/GAUGE_Analog Instruments/MCAD/GAUGE_Analog Instruments.step
45.1 x 36.2 x 1.60 mm
