jrsteensen/OpenHornet/ECAD/PCBs/Functional PCBs/GAUGE_Dual Needle Instruments/MCAD/GAUGE_Dual Needle Instruments.step

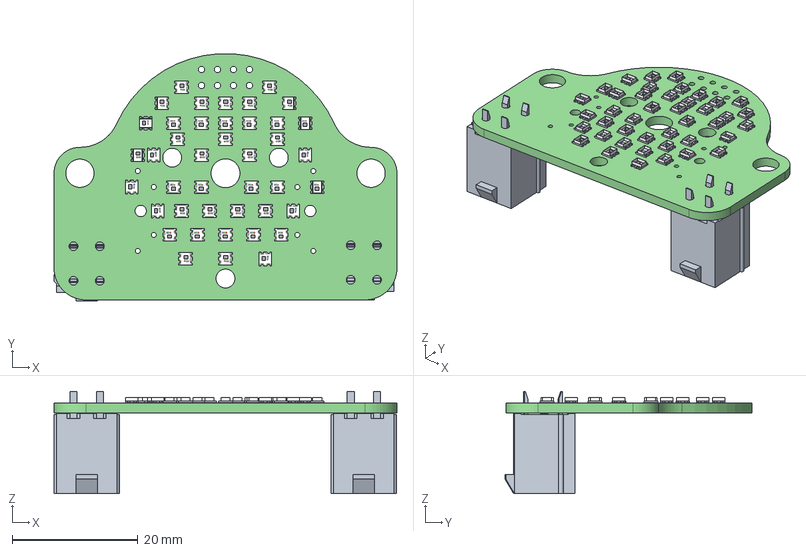
[picture p415: CAD file, 2024-02-26]
ECAD/PCBs/Functional PCBs/GAUGE_Dual Needle Instruments/MCAD/GAUGE_Dual Needle Instruments.step
54.6 x 39.4 x 16.3 mm
_autosave-GAUGE_Dual Needle Instruments PCB
