jrsteensen/OpenHornet/ECAD/PCBs/Functional PCBs/GAUGE_Standby Altimeter/MCAD/GAUGE_Standby Altimeter.step

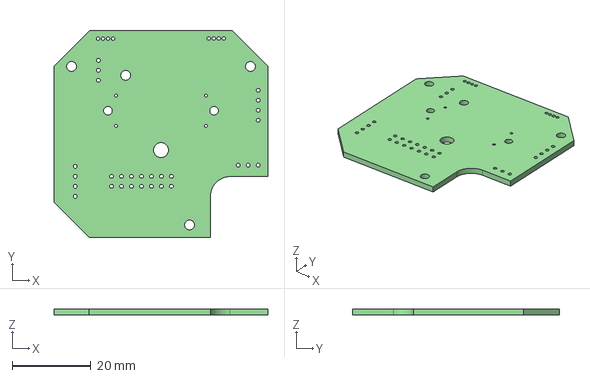
[picture p416: CAD file, 2024-02-26]
ECAD/PCBs/Functional PCBs/GAUGE_Standby Altimeter/MCAD/GAUGE_Standby Altimeter.step
54.4 x 52.6 x 1.60 mm
