jrsteensen/OpenHornet/ECAD/PCBs/Functional PCBs/HOTAS_Hat Switch Breakout/MCAD/HOTAS_Hat Switch Breakout.step

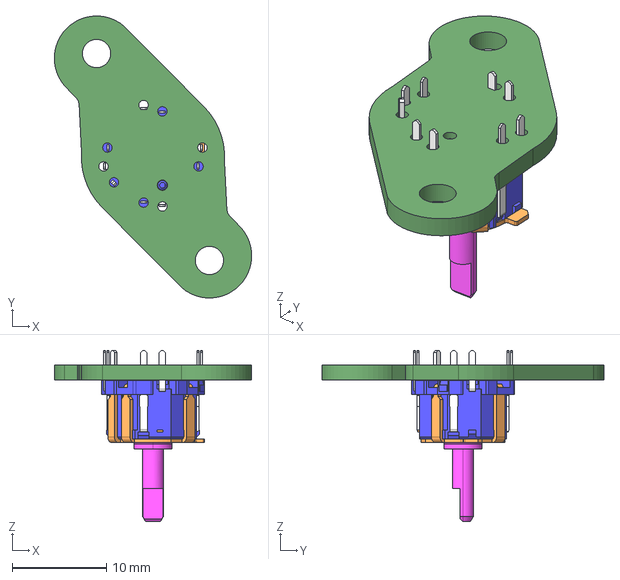
[picture p417: CAD file, 2022-09-23]
ECAD/PCBs/Functional PCBs/HOTAS_Hat Switch Breakout/MCAD/HOTAS_Hat Switch Breakout.step
21.0 x 30.0 x 18.2 mm
