jrsteensen/OpenHornet/ECAD/PCBs/Functional PCBs/IFEI/MCAD/IFEI.step

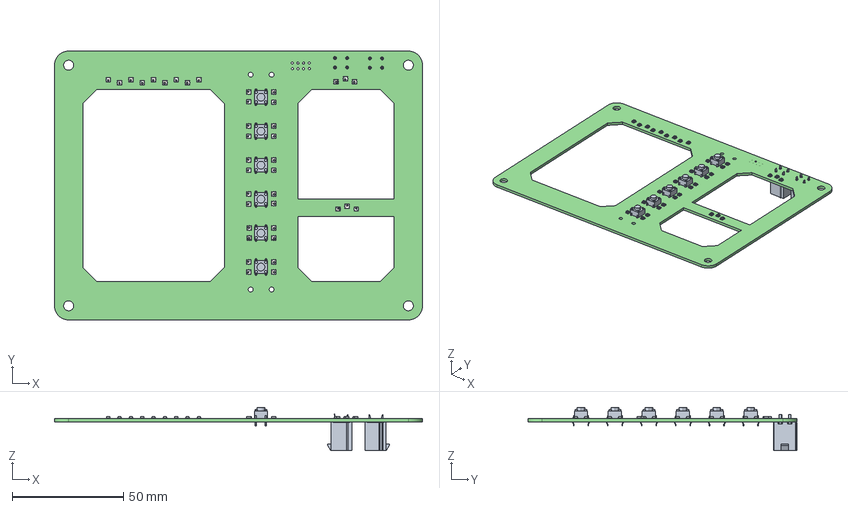
[picture p418: CAD file, 2024-02-26]
ECAD/PCBs/Functional PCBs/IFEI/MCAD/IFEI.step
165.1 x 120.7 x 19.5 mm
_autosave-IFEI PCB
