jrsteensen/OpenHornet/ECAD/PCBs/Functional PCBs/JETT STATION SELECT/MCAD/JETT STATION SELECT.step

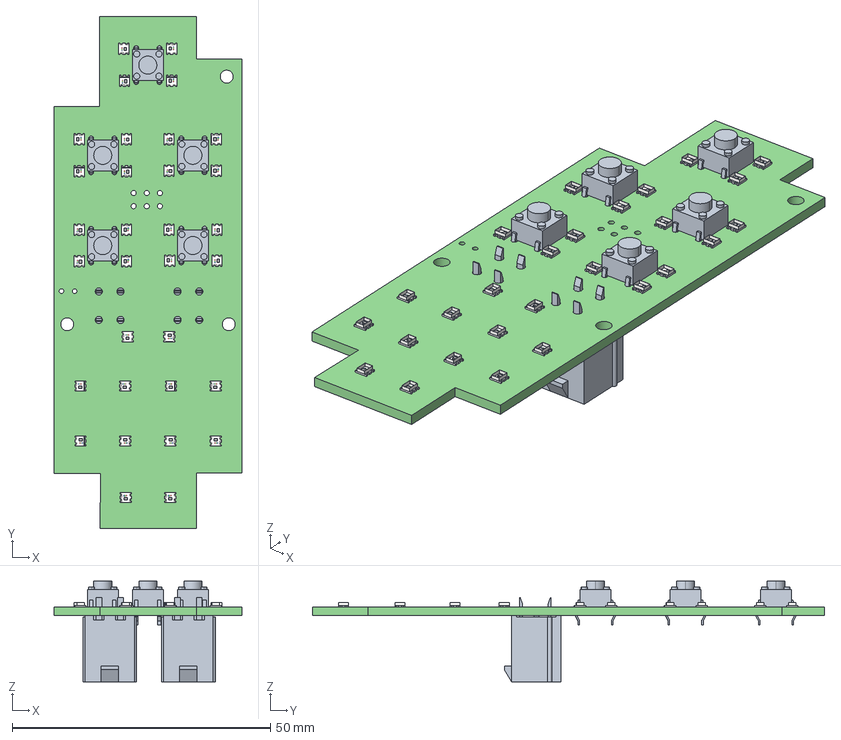
[picture p419: CAD file, 2024-02-26]
ECAD/PCBs/Functional PCBs/JETT STATION SELECT/MCAD/JETT STATION SELECT.step
36.3 x 99.1 x 19.5 mm
_autosave-JETT STATION SELECT PCB
