jrsteensen/OpenHornet/ECAD/PCBs/Functional PCBs/RWR CONTROL PANEL/MCAD/RWR CONTROL PANEL.step

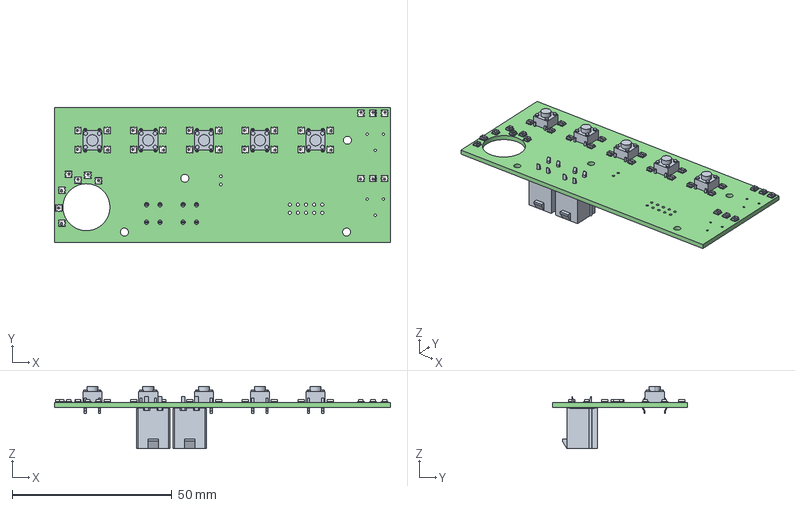
[picture p420: CAD file, 2024-02-26]
ECAD/PCBs/Functional PCBs/RWR CONTROL PANEL/MCAD/RWR CONTROL PANEL.step
105.2 x 42.4 x 19.5 mm
_autosave-RWR CONTROL PANEL PCB
