jrsteensen/OpenHornet/ECAD/PCBs/Functional PCBs/UFC_Function Select/MCAD/PCB, UFC_Function Select.step

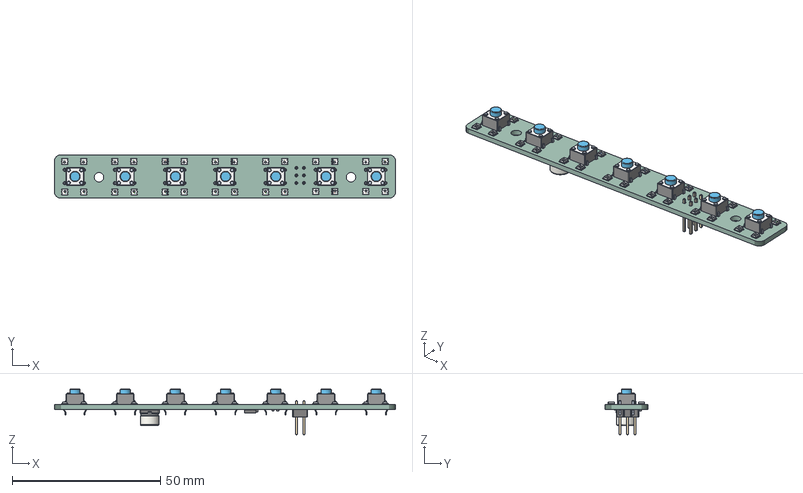
[picture p421: CAD file, 2024-02-26]
ECAD/PCBs/Functional PCBs/UFC_Function Select/MCAD/PCB, UFC_Function Select.step
115.0 x 14.5 x 15.4 mm
PCB
