jrsteensen/OpenHornet/ECAD/PCBs/Functional PCBs/UTIL_PHOTOSWITCH/MCAD/UTIL_PHOTOSWITCH.step

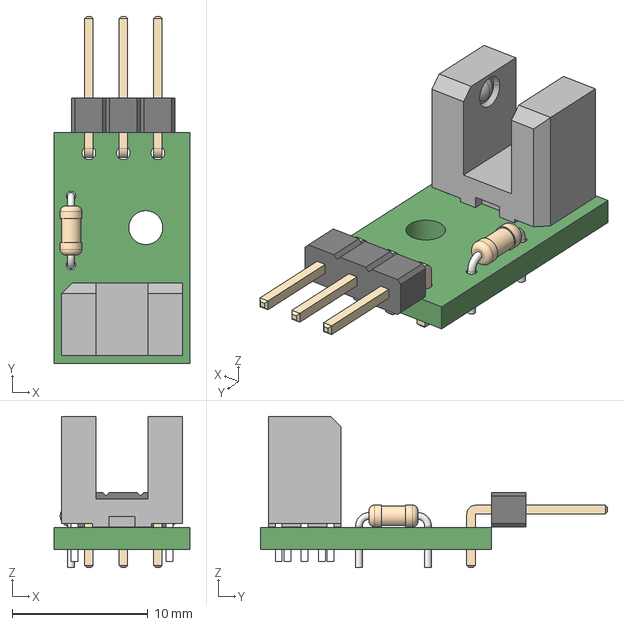
[picture p422: CAD file, 2022-09-23]
ECAD/PCBs/Functional PCBs/UTIL_PHOTOSWITCH/MCAD/UTIL_PHOTOSWITCH.step
10.0 x 25.5 x 11.1 mm
