jrsteensen/OpenHornet/ECAD/PCBs/OH_Specific/Backlighting/JETT_Station_Select_Placard_PCB_V1/JETT Station Select Placard.DXF

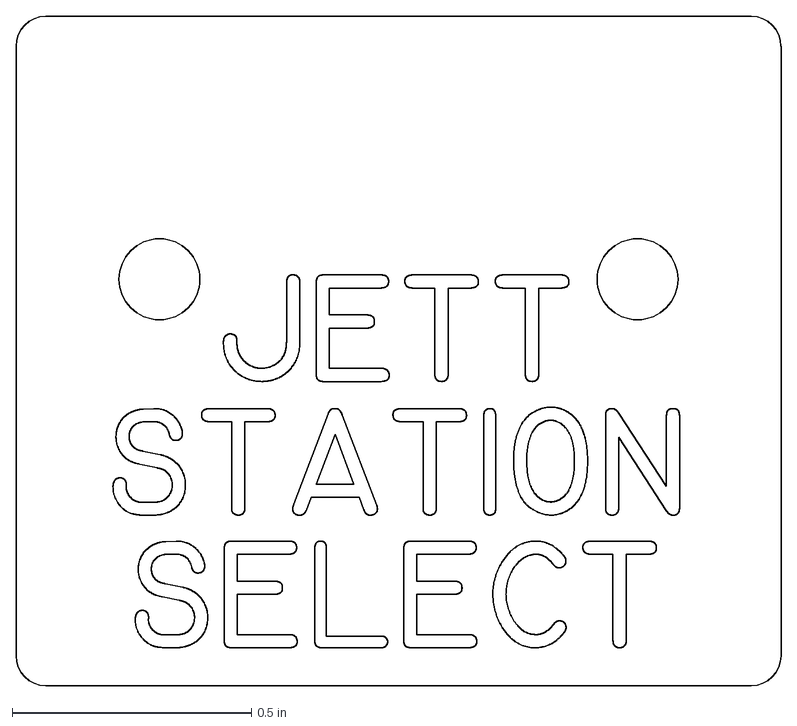
[picture p423: CAD file, 2022-09-23]
ECAD/PCBs/OH_Specific/Backlighting/JETT_Station_Select_Placard_PCB_V1/JETT Station Select Placard.DXF
1.60 x 1.40 in
