jrsteensen/OpenHornet/ECAD/PCBs/OH_Specific/Backlighting/Landing_Gear_Panel_PCB_V2/Landing Gear Panel Backplate.DXF

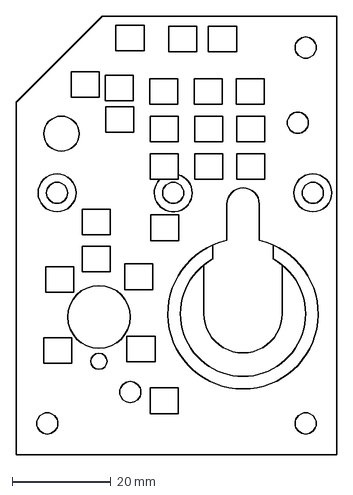
[picture p424: CAD file, 2021-02-01]
ECAD/PCBs/OH_Specific/Backlighting/Landing_Gear_Panel_PCB_V2/Landing Gear Panel Backplate.DXF
65.1 x 88.9 mm
