jrsteensen/OpenHornet/ECAD/PCBs/OH_Specific/Backlighting/LDG_Wing_Fold_PCB_V2/LDG Wing Fold PCB V2/LDG Wing Fold PCB V2_Point_1.SLDPRT

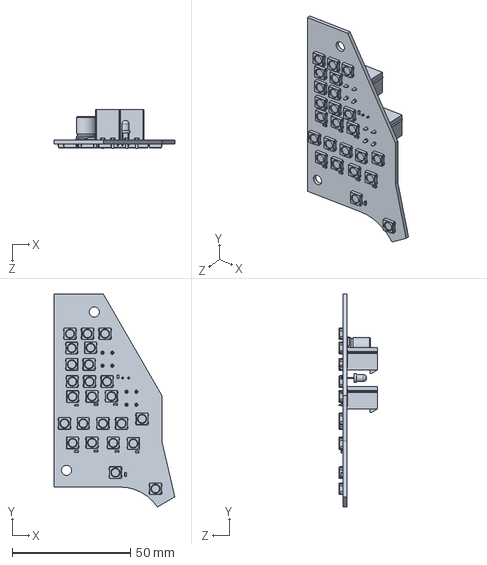
[picture p425: CAD file, 2022-09-23]
ECAD/PCBs/OH_Specific/Backlighting/LDG_Wing_Fold_PCB_V2/LDG Wing Fold PCB V2/LDG Wing Fold PCB V2_Point_1.SLDPRT
51.1 x 90.1 x 16.3 mm
