jrsteensen/OpenHornet/ECAD/PCBs/OH_Specific/Backlighting/Left_Circuit_Breaker_PCB_V1/Circuit Breaker Placard Legend Plate.DXF

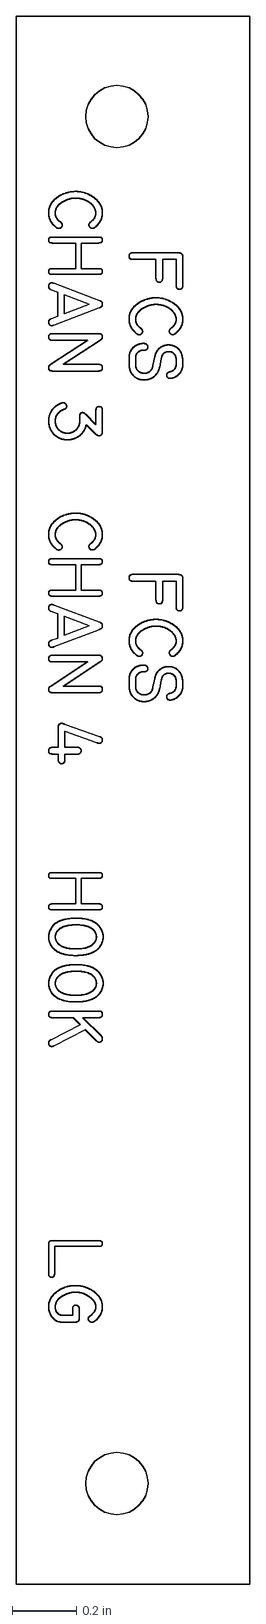
[picture p426: CAD file, 2022-09-23]
ECAD/PCBs/OH_Specific/Backlighting/Left_Circuit_Breaker_PCB_V1/Circuit Breaker Placard Legend Plate.DXF
0.725 x 4.88 in
