jrsteensen/OpenHornet/ECAD/PCBs/OH_Specific/Backlighting/Master_Arm_Panel_PCB_V2/ref/Master Arm Backplate.DXF

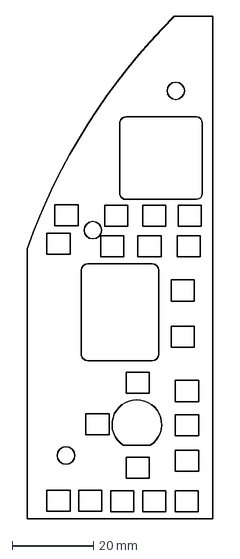
[picture p427: CAD file, 2022-09-23]
ECAD/PCBs/OH_Specific/Backlighting/Master_Arm_Panel_PCB_V2/ref/Master Arm Backplate.DXF
45.7 x 123.5 mm
