jrsteensen/OpenHornet/ECAD/PCBs/OH_Specific/Backlighting/PCB Switch Icons/Original Switch SW Export/631H_SLASH_2 - SWITCH, TOGGLE, ON-OFF, STD BAT.DXF

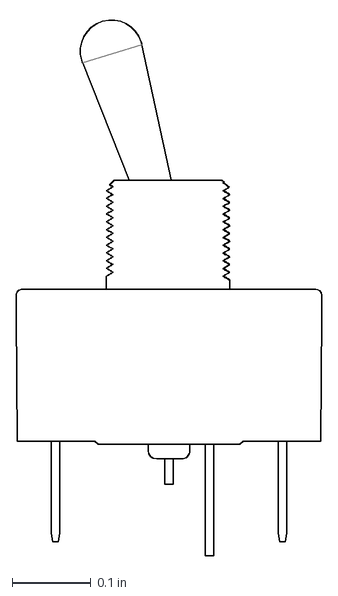
[picture p428: CAD file, 2022-09-23]
ECAD/PCBs/OH_Specific/Backlighting/PCB Switch Icons/Original Switch SW Export/631H_SLASH_2 - SWITCH, TOGGLE, ON-OFF, STD BAT.DXF
0.387 x 0.683 in
