jrsteensen/OpenHornet/ECAD/PCBs/OH_Specific/Backlighting/Select_JETT_Panel_PCB_V2/Select JETT Backplate.DXF

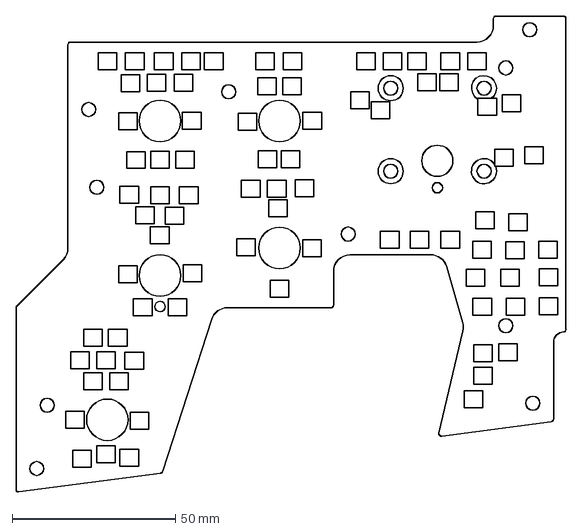
[picture p429: CAD file, 2021-02-01]
ECAD/PCBs/OH_Specific/Backlighting/Select_JETT_Panel_PCB_V2/Select JETT Backplate.DXF
168.3 x 145.6 mm
