jrsteensen/OpenHornet/ECAD/PCBs/OH_Specific/Backlighting/SIM_CNTL_Panel_PCB_V2/SIM CNTL Panel Backplate.DXF

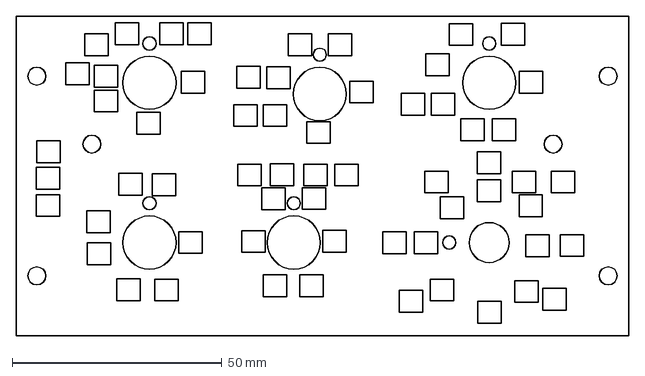
[picture p430: CAD file, 2022-09-23]
ECAD/PCBs/OH_Specific/Backlighting/SIM_CNTL_Panel_PCB_V2/SIM CNTL Panel Backplate.DXF
146.1 x 76.2 mm
