jrsteensen/OpenHornet/ECAD/PCBs/OH_Specific/Backlighting/SPIN_RCV_Panel_PCB_V2/Spin Panel Backplate.DXF

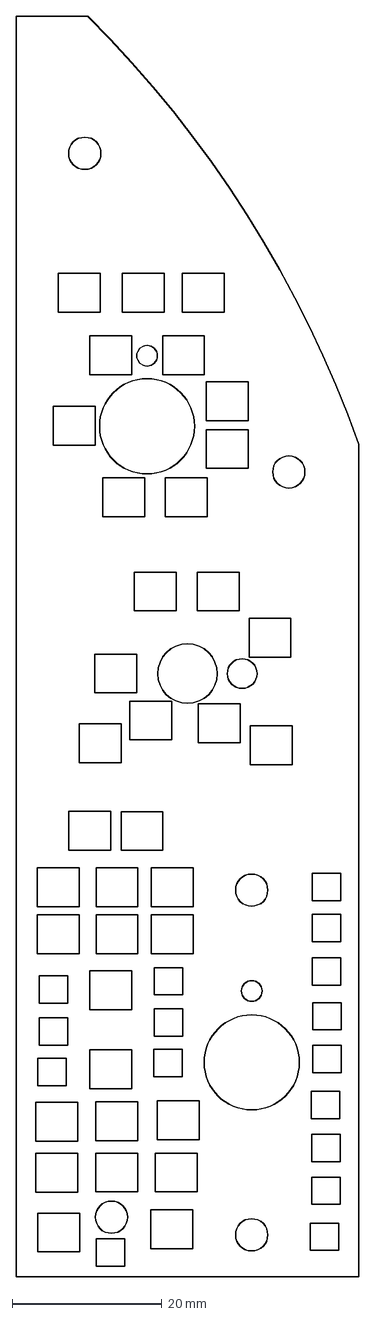
[picture p431: CAD file, 2022-09-23]
ECAD/PCBs/OH_Specific/Backlighting/SPIN_RCV_Panel_PCB_V2/Spin Panel Backplate.DXF
45.7 x 168.3 mm
