jrsteensen/OpenHornet/ECAD/PCBs/OH_Specific/Functional/ampcd_button_board/ref/AMPCD PCB2.DXF

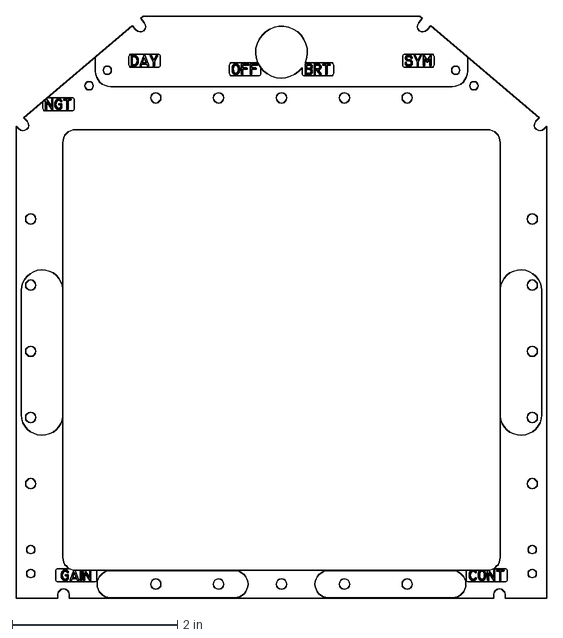
[picture p432: CAD file, 2022-09-23]
ECAD/PCBs/OH_Specific/Functional/ampcd_button_board/ref/AMPCD PCB2.DXF
6.41 x 7.04 in
