jrsteensen/OpenHornet/ECAD/PCBs/OH_Specific/Functional/ddi_button_board/docs/DDI_PCB.DXF

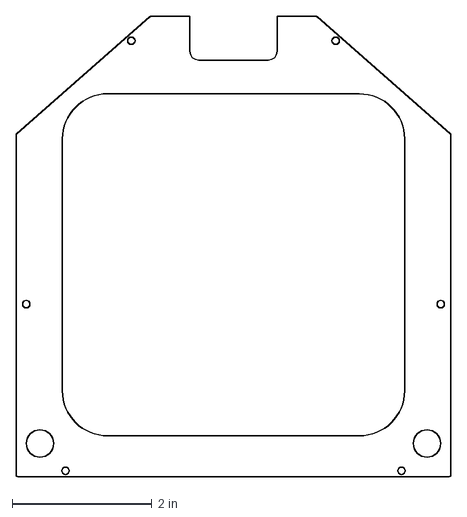
[picture p433: CAD file, 2019-10-15]
ECAD/PCBs/OH_Specific/Functional/ddi_button_board/docs/DDI_PCB.DXF
6.23 x 6.59 in
