jrsteensen/OpenHornet/ECAD/PCBs/OH_Specific/Functional/dual_needle_gauge/dual_needle_gauge.step

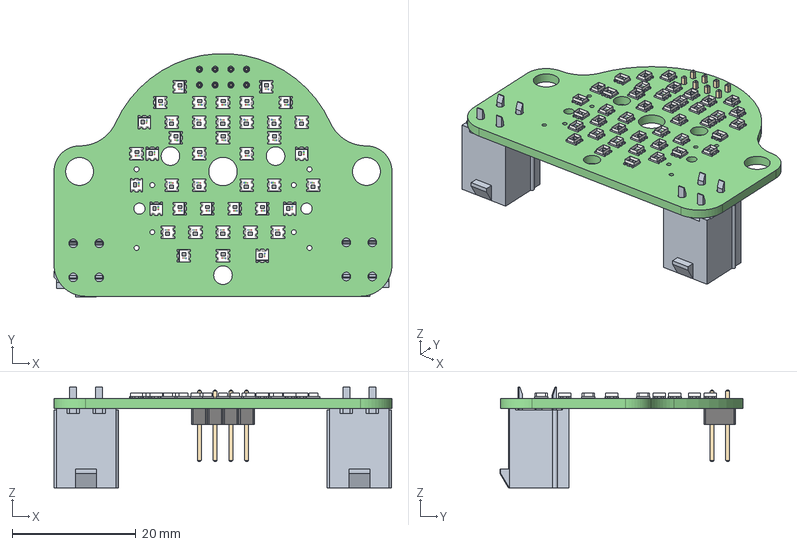
[picture p434: CAD file, 2022-09-23]
ECAD/PCBs/OH_Specific/Functional/dual_needle_gauge/dual_needle_gauge.step
54.6 x 39.3 x 16.3 mm
_autosave-dual_needle_gauge PCB
