jrsteensen/OpenHornet/ECAD/PCBs/OH_Specific/Functional/dual_needle_gauge/ref/x40_8798.DXF

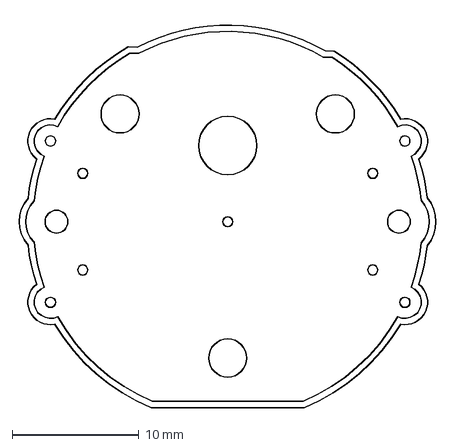
[picture p435: CAD file, 2022-09-23]
ECAD/PCBs/OH_Specific/Functional/dual_needle_gauge/ref/x40_8798.DXF
33.3 x 30.8 mm
