jrsteensen/OpenHornet/ECAD/PCBs/OH_Specific/Functional/ewi_v3/mcad/ewi_v3_right.step

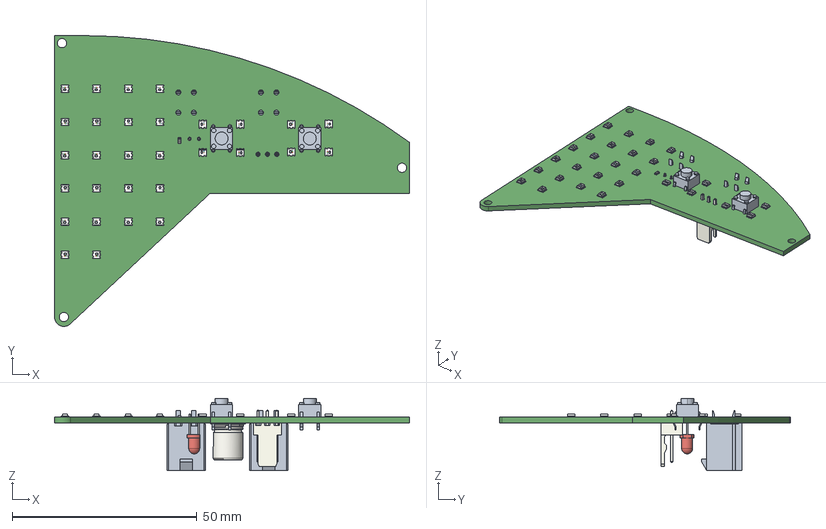
[picture p436: CAD file, 2022-09-23]
ECAD/PCBs/OH_Specific/Functional/ewi_v3/mcad/ewi_v3_right.step
96.1 x 78.8 x 19.5 mm
