jrsteensen/OpenHornet/ECAD/PCBs/OH_Specific/Functional/ewi_v3/ref/EWI PCB - Left.DXF

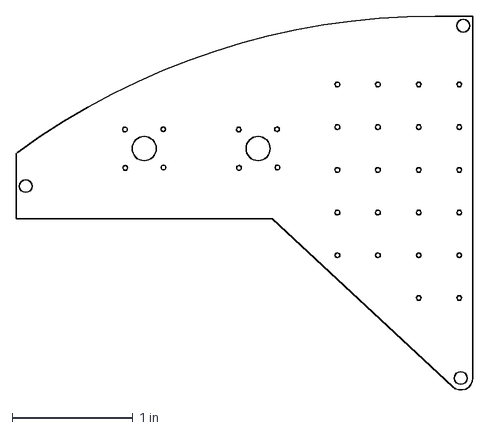
[picture p437: CAD file, 2022-09-23]
ECAD/PCBs/OH_Specific/Functional/ewi_v3/ref/EWI PCB - Left.DXF
3.79 x 3.11 in
