jrsteensen/OpenHornet/ECAD/PCBs/OH_Specific/Functional/ifei/mcad/ifei.step

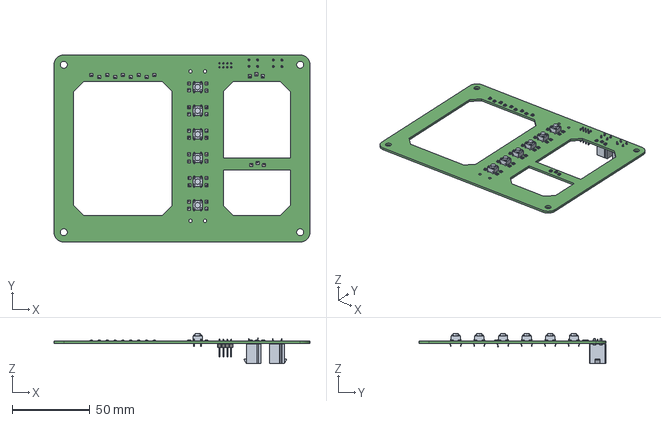
[picture p438: CAD file, 2022-09-23]
ECAD/PCBs/OH_Specific/Functional/ifei/mcad/ifei.step
165.1 x 120.6 x 19.5 mm
