jrsteensen/OpenHornet/ECAD/PCBs/OH_Specific/Functional/ifei/ref/IFEI.DXF

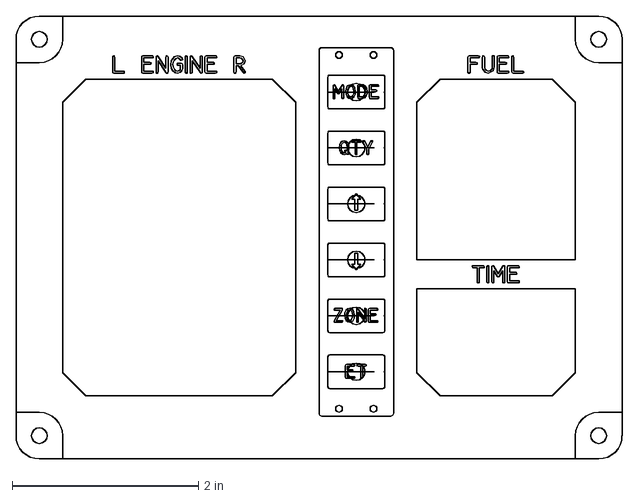
[picture p439: CAD file, 2022-09-23]
ECAD/PCBs/OH_Specific/Functional/ifei/ref/IFEI.DXF
6.50 x 4.75 in
