jrsteensen/OpenHornet/ECAD/PCBs/OH_Specific/Functional/jett_station_select/ref/JETT Select PCB.DXF

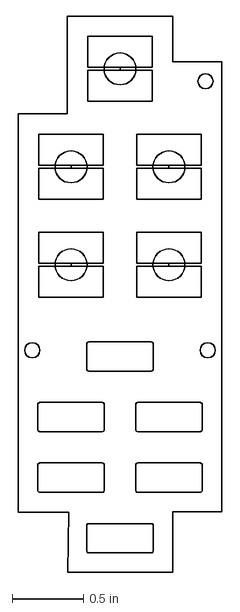
[picture p440: CAD file, 2022-09-23]
ECAD/PCBs/OH_Specific/Functional/jett_station_select/ref/JETT Select PCB.DXF
1.43 x 3.90 in
