jrsteensen/OpenHornet/ECAD/PCBs/OH_Specific/Functional/ralt_controller/Radar Altimeter Case.DXF

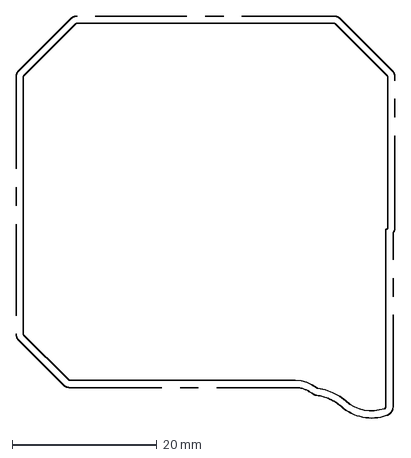
[picture p441: CAD file, 2022-09-23]
ECAD/PCBs/OH_Specific/Functional/ralt_controller/Radar Altimeter Case.DXF
52.4 x 55.6 mm
