jrsteensen/OpenHornet/ECAD/PCBs/OH_Specific/Functional/RWR_Panel_PCB_V2/mcad/RWR_Control_Panel V2.5.step

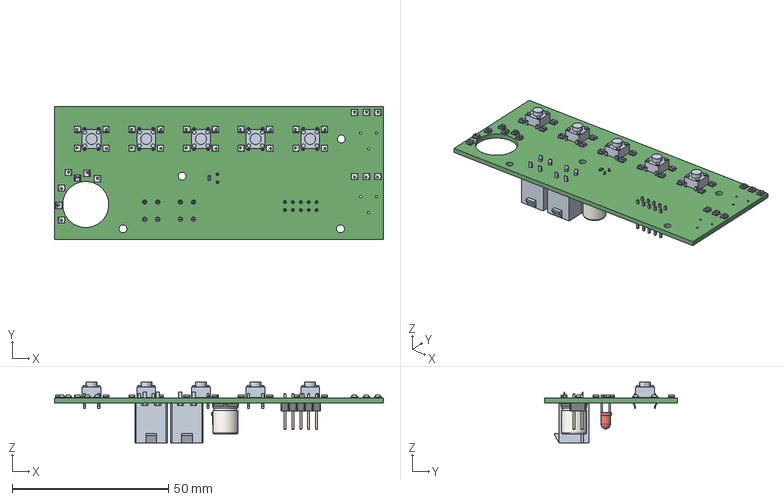
[picture p442: CAD file, 2022-09-23]
ECAD/PCBs/OH_Specific/Functional/RWR_Panel_PCB_V2/mcad/RWR_Control_Panel V2.5.step
105.2 x 42.4 x 19.5 mm
