jrsteensen/OpenHornet/ECAD/PCBs/OH_Specific/Functional/RWR_Panel_PCB_V2/ref/Part9^RWR Control Panel.DXF

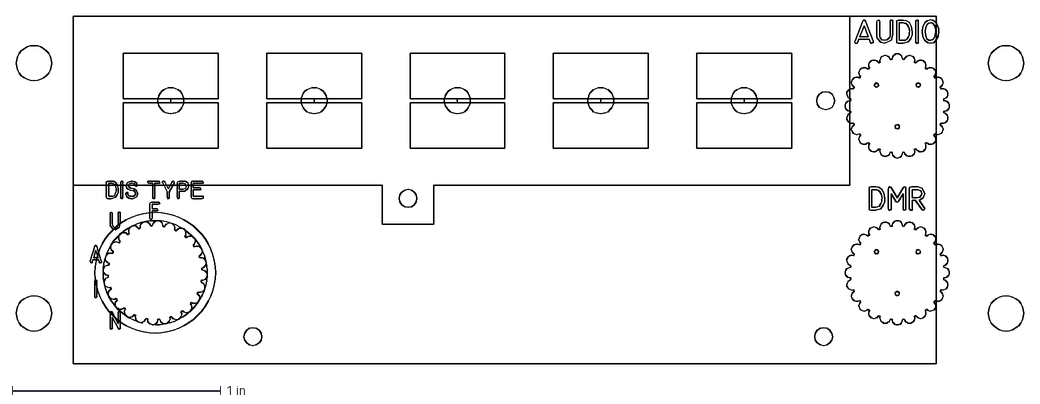
[picture p443: CAD file, 2022-09-23]
ECAD/PCBs/OH_Specific/Functional/RWR_Panel_PCB_V2/ref/Part9^RWR Control Panel.DXF
4.83 x 1.67 in
