jrsteensen/OpenHornet/ECAD/PCBs/OH_Specific/Functional/standby_airspeed_vvi/mcad/standby_airspeed_vvi.step

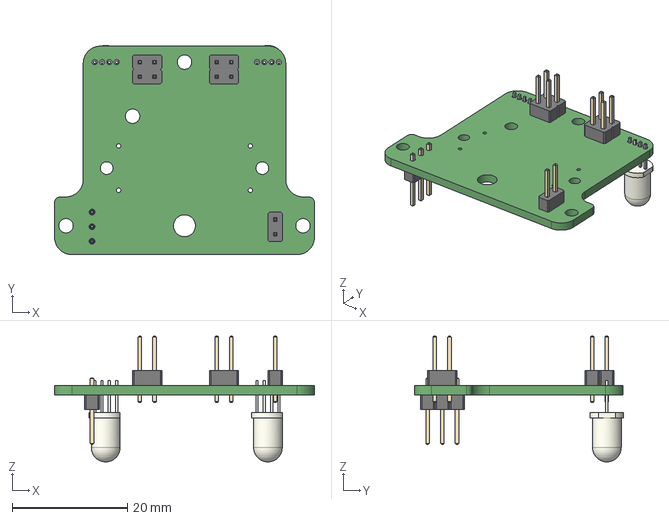
[picture p444: CAD file, 2022-09-23]
ECAD/PCBs/OH_Specific/Functional/standby_airspeed_vvi/mcad/standby_airspeed_vvi.step
45.1 x 36.3 x 21.8 mm
