jrsteensen/OpenHornet/ECAD/PCBs/OH_Specific/Functional/standby_airspeed_vvi/ref/standby_airspeed_vvi.DXF

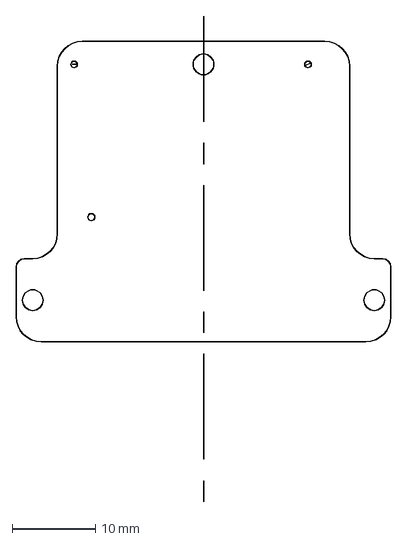
[picture p445: CAD file, 2022-09-23]
ECAD/PCBs/OH_Specific/Functional/standby_airspeed_vvi/ref/standby_airspeed_vvi.DXF
45.1 x 58.4 mm
