jrsteensen/OpenHornet/ECAD/PCBs/OH_Specific/Functional/standby_altimeter/mcad/standby_altimeter.step

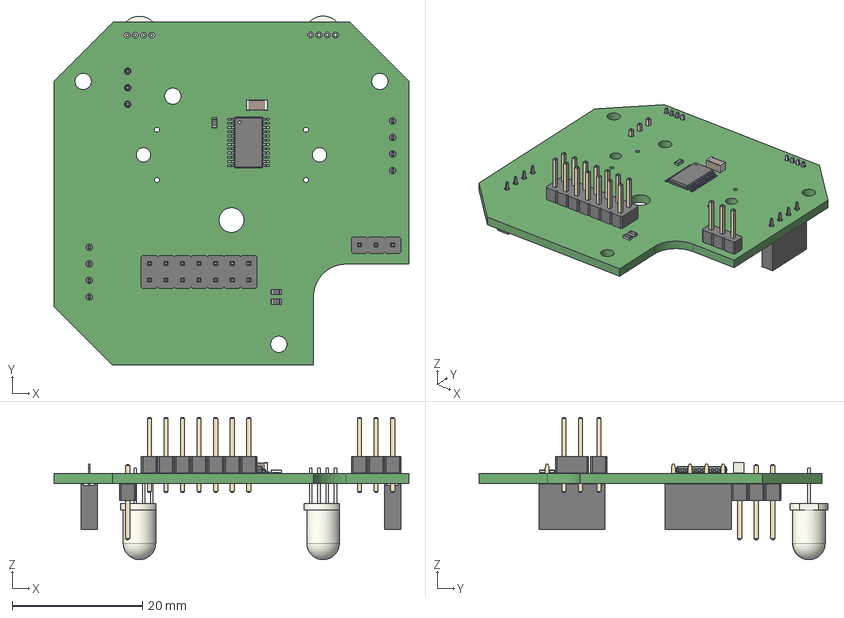
[picture p446: CAD file, 2022-09-23]
ECAD/PCBs/OH_Specific/Functional/standby_altimeter/mcad/standby_altimeter.step
54.4 x 53.5 x 21.8 mm
