jrsteensen/OpenHornet/ECAD/PCBs/OH_Specific/Functional/standby_altimeter/ref/standby_altimeter.DXF

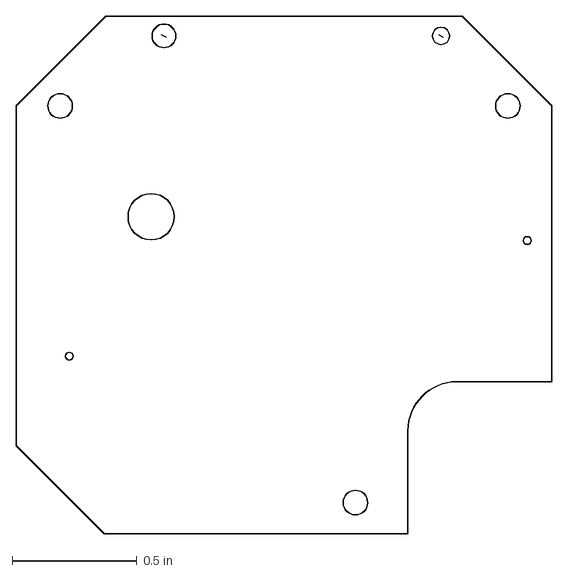
[picture p447: CAD file, 2022-09-23]
ECAD/PCBs/OH_Specific/Functional/standby_altimeter/ref/standby_altimeter.DXF
2.14 x 2.07 in
