jrsteensen/OpenHornet/ECAD/PCBs/OH_Specific/Functional/ufc_v5_ap/ref/AP Switch Module.dxf

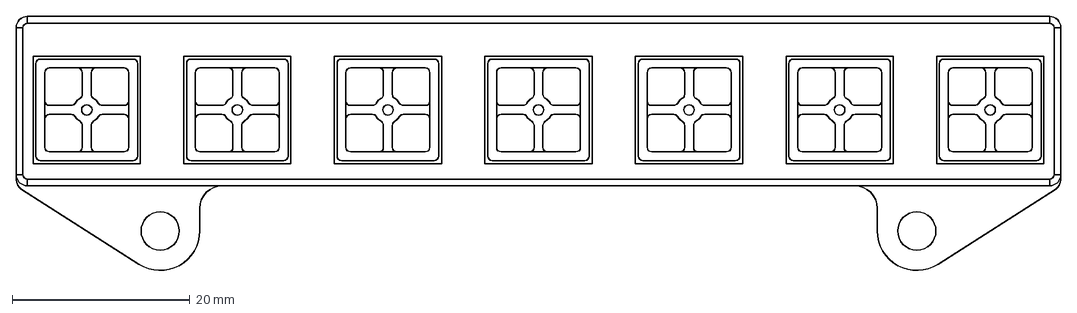
[picture p448: CAD file, 2021-02-01]
ECAD/PCBs/OH_Specific/Functional/ufc_v5_ap/ref/AP Switch Module.dxf
117.5 x 28.8 mm
