jrsteensen/OpenHornet/ECAD/PCBs/OH_Specific/Functional/ufc_v5_main/ref/UFC Panel_v4.dxf

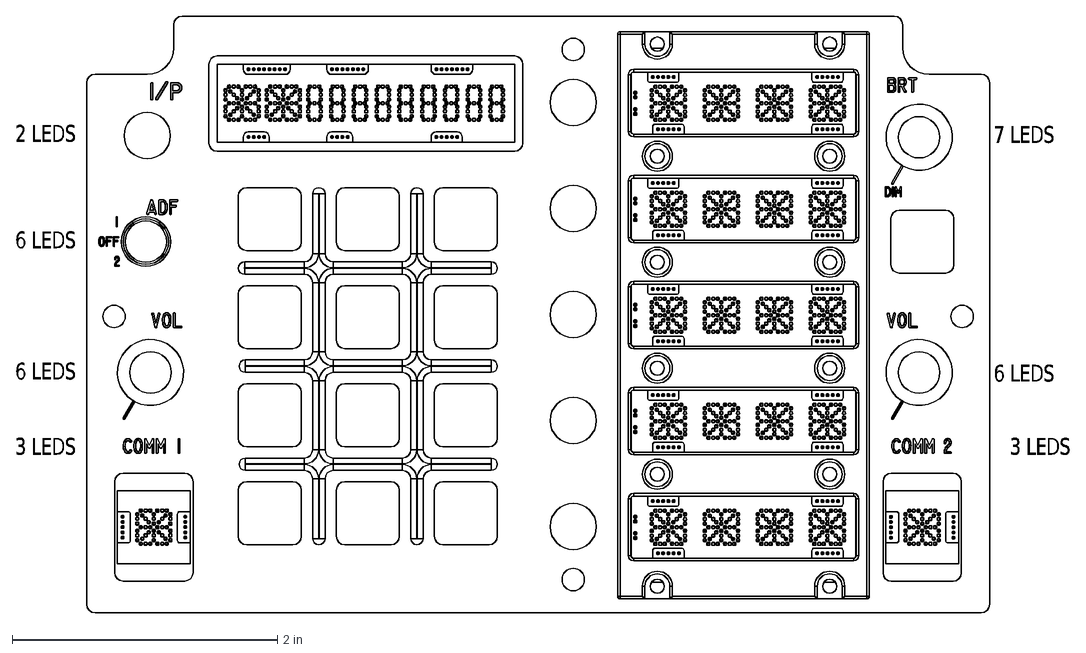
[picture p449: CAD file, 2021-02-01]
ECAD/PCBs/OH_Specific/Functional/ufc_v5_main/ref/UFC Panel_v4.dxf
7 LEDS
6 LEDS
2 LEDS
3 LEDS
