jrsteensen/OpenHornet/ECAD/PCBs/OH_Specific/Functional/util_photoswitch/opb61x.DXF

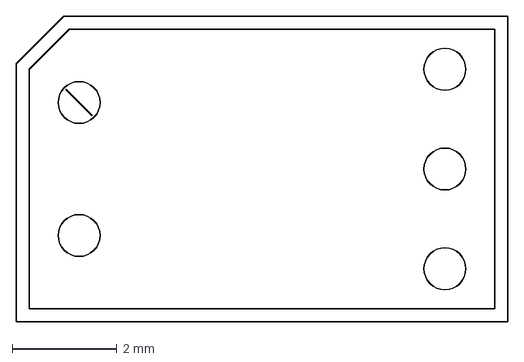
[picture p450: CAD file, 2022-09-23]
ECAD/PCBs/OH_Specific/Functional/util_photoswitch/opb61x.DXF
9.39 x 5.83 mm
