jrsteensen/OpenHornet/ECAD/PCBs/Specialty/55_SQ_Indicator/sq_indicator.step

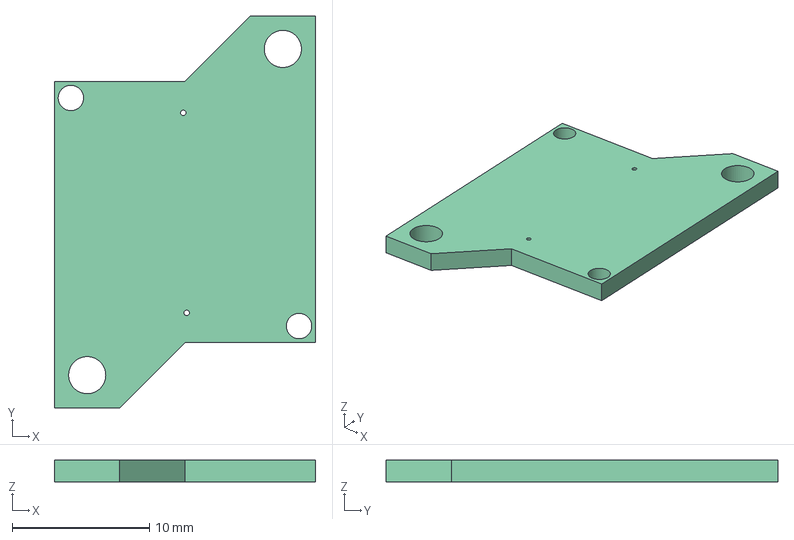
[picture p451: CAD file, 2019-11-06]
ECAD/PCBs/Specialty/55_SQ_Indicator/sq_indicator.step
19.1 x 28.6 x 1.60 mm
Local_CS
Step_Models
