jrsteensen/OpenHornet/ECAD/PCBs/Specialty/AP/AP.step

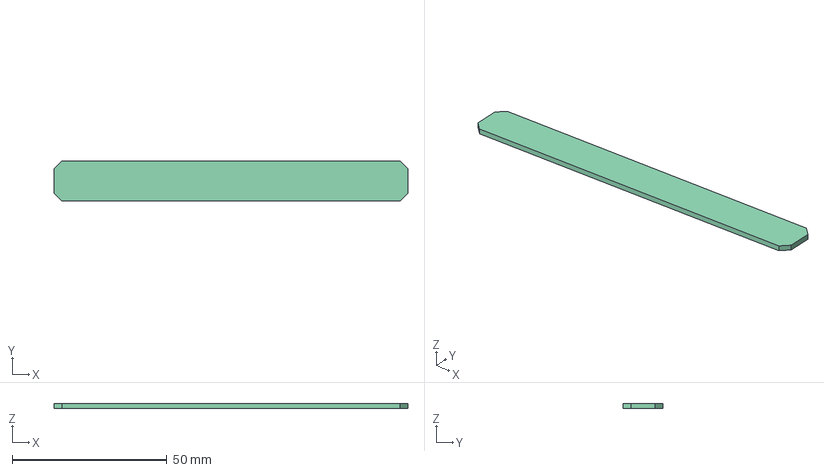
[picture p452: CAD file, 2019-11-05]
ECAD/PCBs/Specialty/AP/AP.step
114.6 x 13.0 x 1.60 mm
Local_CS
Pcb
Step_Models
