jrsteensen/OpenHornet/ECAD/PCBs/Specialty/AP/docs/AP_PCB.DXF

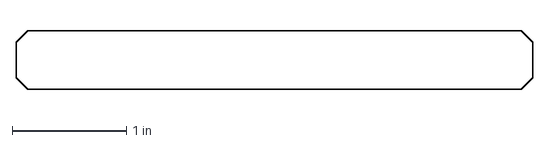
[picture p453: CAD file, 2019-10-15]
ECAD/PCBs/Specialty/AP/docs/AP_PCB.DXF
4.51 x 0.51 in
