jrsteensen/OpenHornet/ECAD/PCBs/Specialty/Caution_lights_panel/Caution_Light_Panel.step

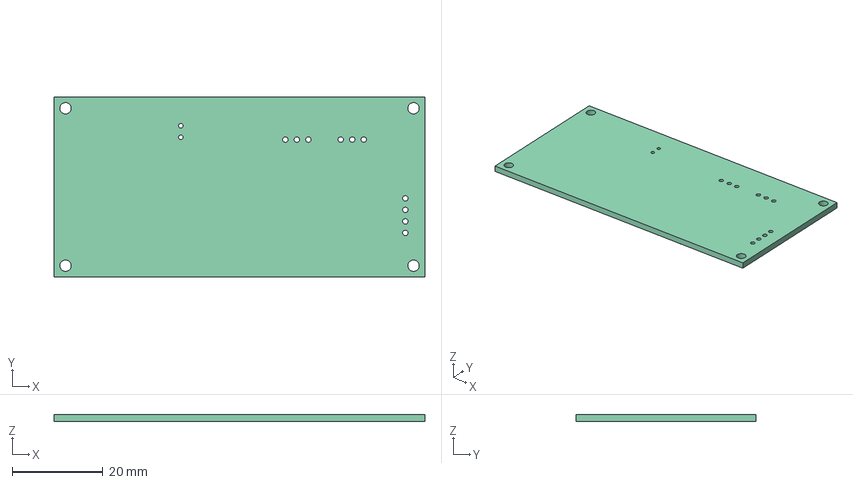
[picture p454: CAD file, 2019-11-08]
ECAD/PCBs/Specialty/Caution_lights_panel/Caution_Light_Panel.step
81.9 x 39.8 x 1.60 mm
Local_CS
Step_Models
