jrsteensen/OpenHornet/ECAD/PCBs/Specialty/DDI/AMPCD_button_board/DDI_shield.step

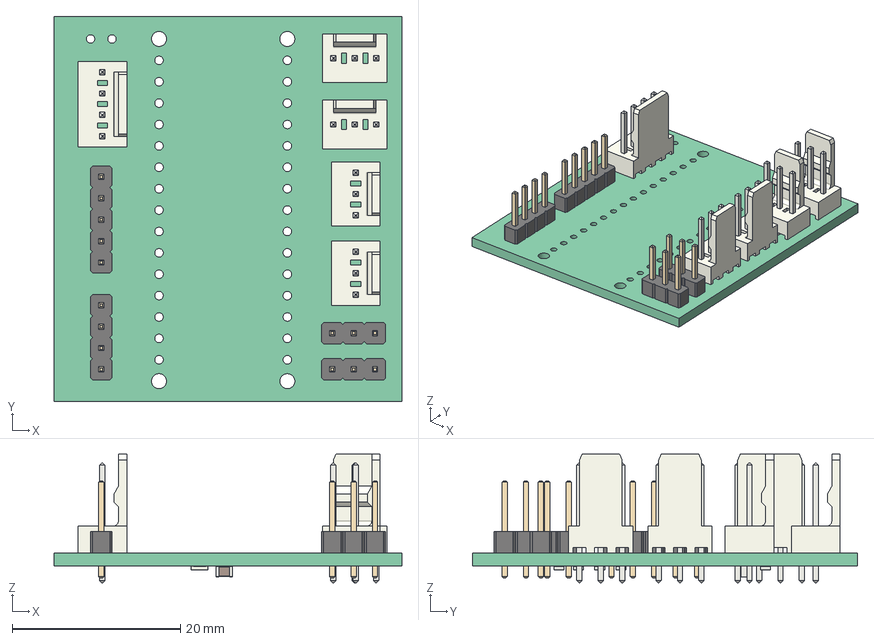
[picture p455: CAD file, 2019-10-29]
ECAD/PCBs/Specialty/DDI/AMPCD_button_board/DDI_shield.step
41.3 x 45.7 x 15.3 mm
Local_CS
J8_PinHeader_1x04_P254mm_Vertical_5DB0FFF6
J6_PinHeader_1x05_P254mm_Vertical_5BDEC227
J1_Molex_AE_6410_04A_5BDEC7D9
J2_Molex_AE_6410_03A_5BDEC804
J3_Molex_AE_6410_03A_5BDED261
J5_Molex_AE_6410_03A_5BDED08A
J7_Molex_AE_6410_03A_5BDED015
J9_PinHeader_1x03_P254mm_Vertical_5DB10023
J10_PinHeader_1x03_P254mm_Vertical_5DB102A2
R2_R_0805_2012Metric_5BDEC2A7
R3_R_0805_2012Metric_5BDEC2B8
R4_R_0805_2012Metric_5BDEC2C9
R5_R_0805_2012Metric_5BDEC2DA
C1_C_0805_2012Metric_5BDED3C8
R1_R_0805_2012Metric_5BDEC8C7
