jrsteensen/OpenHornet/ECAD/PCBs/Specialty/DDI/AMPCD_button_board/docs/AMPCD_PCB.DXF

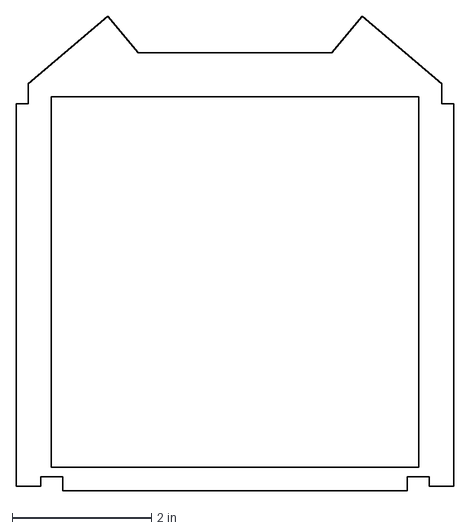
[picture p456: CAD file, 2019-10-15]
ECAD/PCBs/Specialty/DDI/AMPCD_button_board/docs/AMPCD_PCB.DXF
6.29 x 6.82 in
