jrsteensen/OpenHornet/ECAD/PCBs/Specialty/Eyebrow_warning_indicators/docs/EWI_PCB_-_Right.DXF

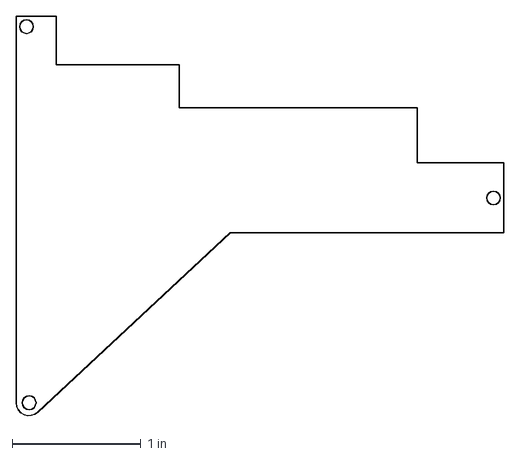
[picture p457: CAD file, 2019-10-15]
ECAD/PCBs/Specialty/Eyebrow_warning_indicators/docs/EWI_PCB_-_Right.DXF
3.79 x 3.11 in
