jrsteensen/OpenHornet/ECAD/PCBs/Specialty/Eyebrow_warning_indicators/Left/EWI_Left.step

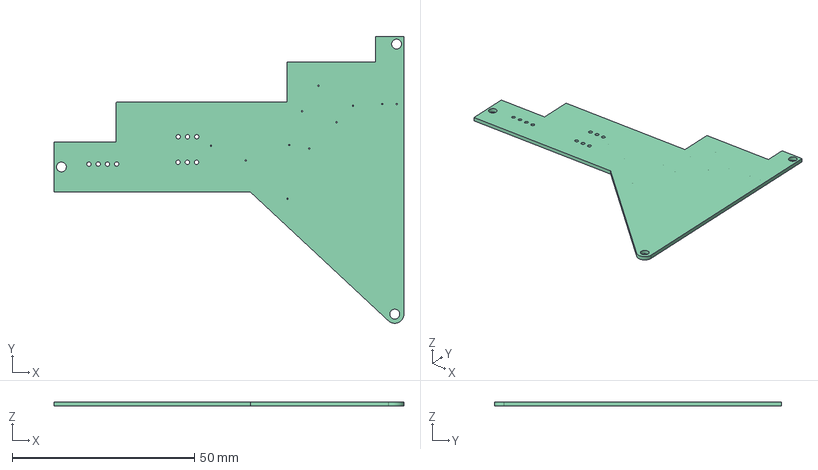
[picture p458: CAD file, 2019-11-01]
ECAD/PCBs/Specialty/Eyebrow_warning_indicators/Left/EWI_Left.step
96.1 x 78.8 x 1.20 mm
Local_CS
Step_Models
