jrsteensen/OpenHornet/ECAD/PCBs/Specialty/IFEI/docs/IFEI_PCB.DXF

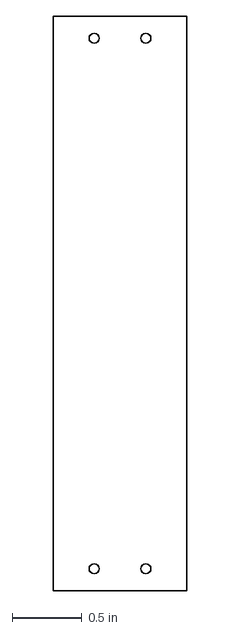
[picture p459: CAD file, 2019-10-15]
ECAD/PCBs/Specialty/IFEI/docs/IFEI_PCB.DXF
0.957 x 4.11 in
