jrsteensen/OpenHornet/ECAD/PCBs/Specialty/IFEI/IFEI.step

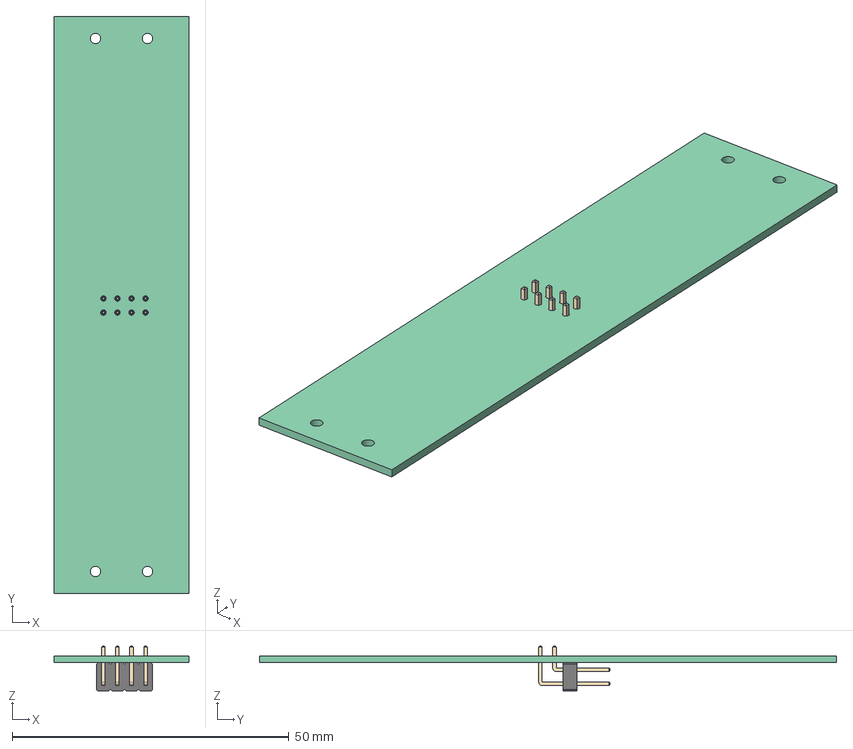
[picture p460: CAD file, 2019-11-07]
ECAD/PCBs/Specialty/IFEI/IFEI.step
24.3 x 104.3 x 8.08 mm
Local_CS
J1_PinHeader_2x04_P254mm_Horizontal_5DBCFCC3
