jrsteensen/OpenHornet/ECAD/PCBs/Specialty/JETT_SELECT_Panel/docs/JETT_Select_PCB.DXF

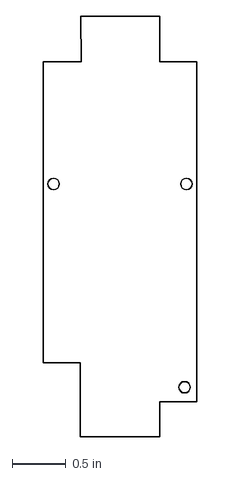
[picture p461: CAD file, 2019-10-15]
ECAD/PCBs/Specialty/JETT_SELECT_Panel/docs/JETT_Select_PCB.DXF
1.43 x 3.90 in
