jrsteensen/OpenHornet/ECAD/PCBs/Specialty/Master_Mode_Pushbutton/docs/Master_Mode_Pushbutton_PCB.DXF

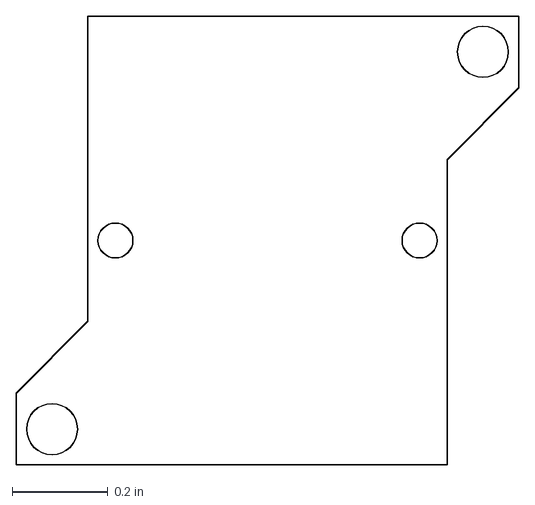
[picture p462: CAD file, 2019-10-15]
ECAD/PCBs/Specialty/Master_Mode_Pushbutton/docs/Master_Mode_Pushbutton_PCB.DXF
1.05 x 0.938 in
