jrsteensen/OpenHornet/ECAD/PCBs/Specialty/Master_Mode_Pushbutton/MasterModePushbutton.step

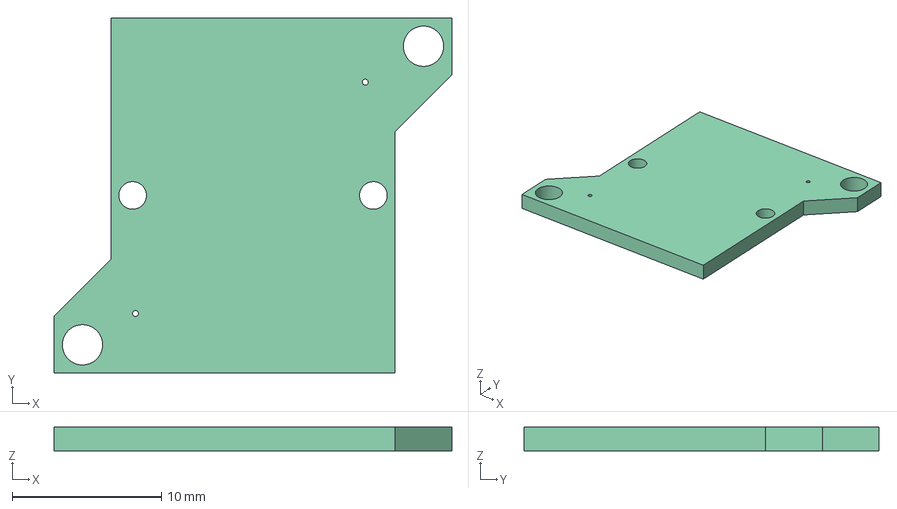
[picture p463: CAD file, 2019-11-01]
ECAD/PCBs/Specialty/Master_Mode_Pushbutton/MasterModePushbutton.step
26.7 x 23.8 x 1.60 mm
Local_CS
Step_Models
