jrsteensen/OpenHornet/ECAD/PCBs/Specialty/RWR_Control_Panel/docs/RWR_Control_Panel_PCB.DXF

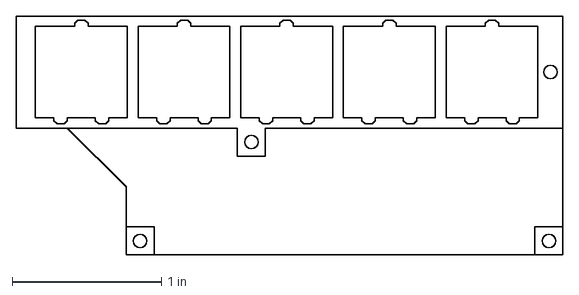
[picture p464: CAD file, 2019-10-15]
ECAD/PCBs/Specialty/RWR_Control_Panel/docs/RWR_Control_Panel_PCB.DXF
3.66 x 1.60 in
