jrsteensen/OpenHornet/ECAD/PCBs/Specialty/RWR_Control_Panel/RWR_Control_Panel.step

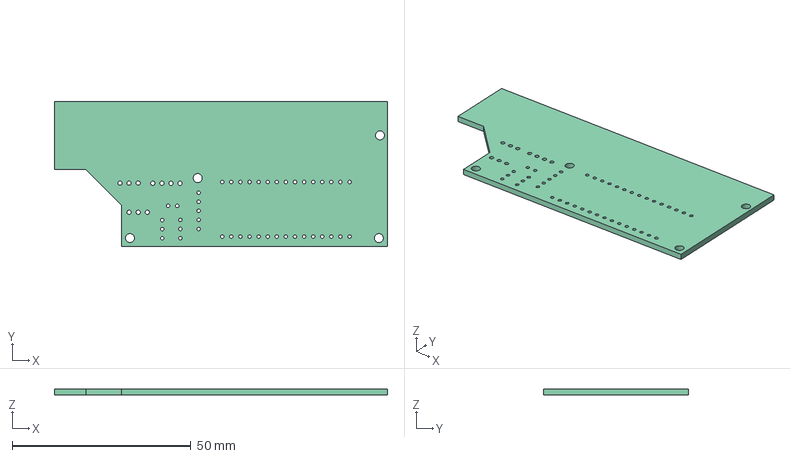
[picture p465: CAD file, 2019-11-16]
ECAD/PCBs/Specialty/RWR_Control_Panel/RWR_Control_Panel.step
93.0 x 40.6 x 1.60 mm
Local_CS
Pcb
Step_Models
