jrsteensen/OpenHornet/ECAD/PCBs/Specialty/UFC_Mega_Shield/UFC_Controller_Interface.step

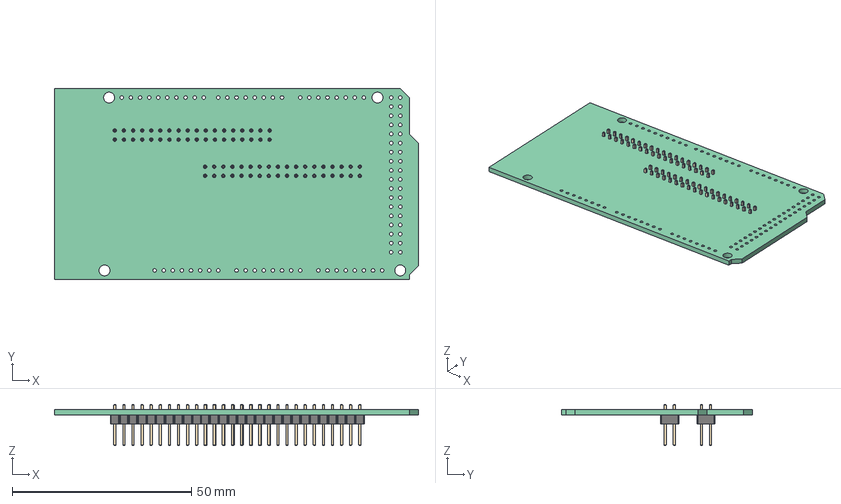
[picture p466: CAD file, 2019-11-06]
ECAD/PCBs/Specialty/UFC_Mega_Shield/UFC_Controller_Interface.step
101.6 x 53.3 x 11.5 mm
Local_CS
P14_PinHeader_2x18_P254mm_Vertical_5DBBCDBC
P15_PinHeader_2x18_P254mm_Vertical_5DBBD61E
