jrsteensen/OpenHornet/reference/hornet_stick_grip_basemesh.obj

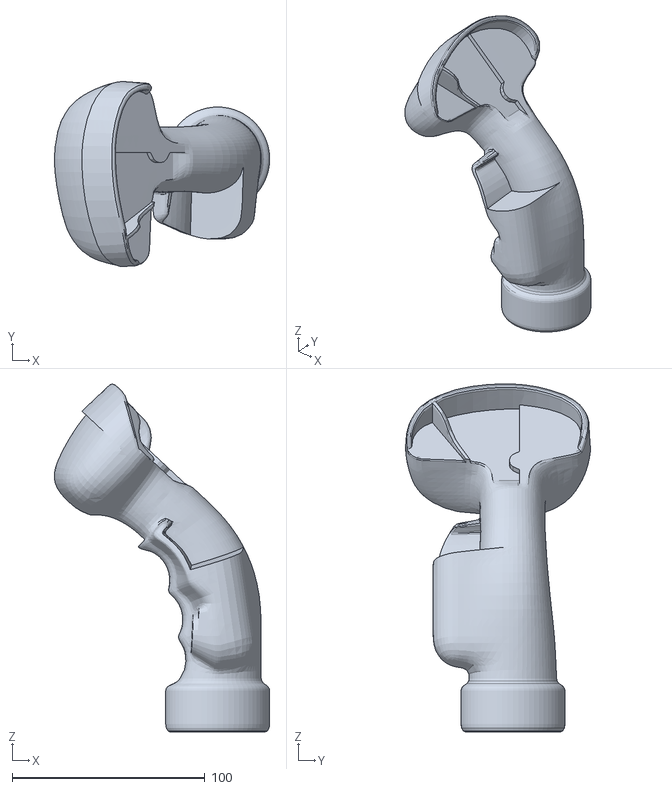
[picture p467: CAD file, 2020-04-17]
reference/hornet_stick_grip_basemesh.obj
111.8 x 96.1 x 180.7
