jrsteensen/OpenHornet/release/OH1_Upper_Instrument_Panel/Manufacturing/FDM_OH1A1-18_UPPER UIP FACE MOUNT, LEFT_-_V105.3mf

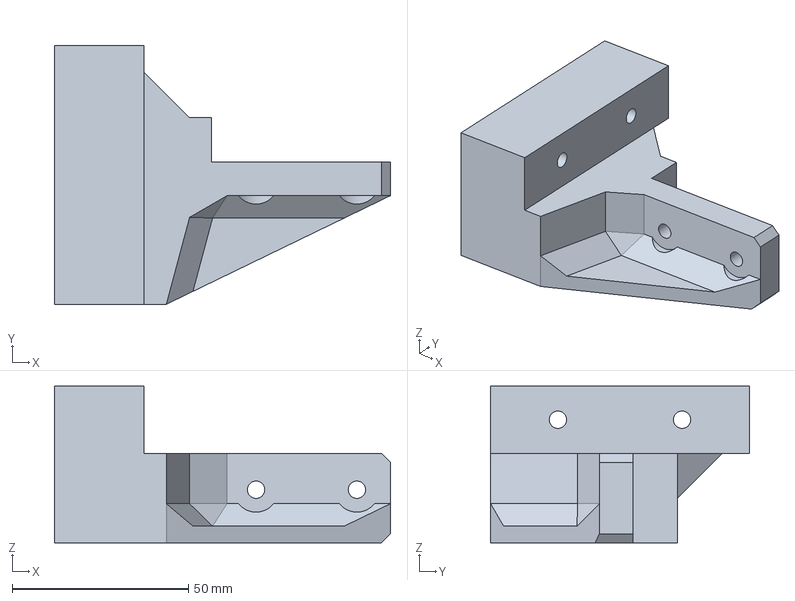
[picture p468: CAD file, 2024-02-26]
release/OH1_Upper_Instrument_Panel/Manufacturing/FDM_OH1A1-18_UPPER UIP FACE MOUNT, LEFT_-_V105.3mf
95.2 x 73.3 x 44.4 mm
