jrsteensen/OpenHornet/release/OH1_Upper_Instrument_Panel/OH1A2 - ASSY, PANEL, MASTER ARM/Manufacturing/FDM_OH1A2-15_EMERG JETT BRKT_A_V18.3mf

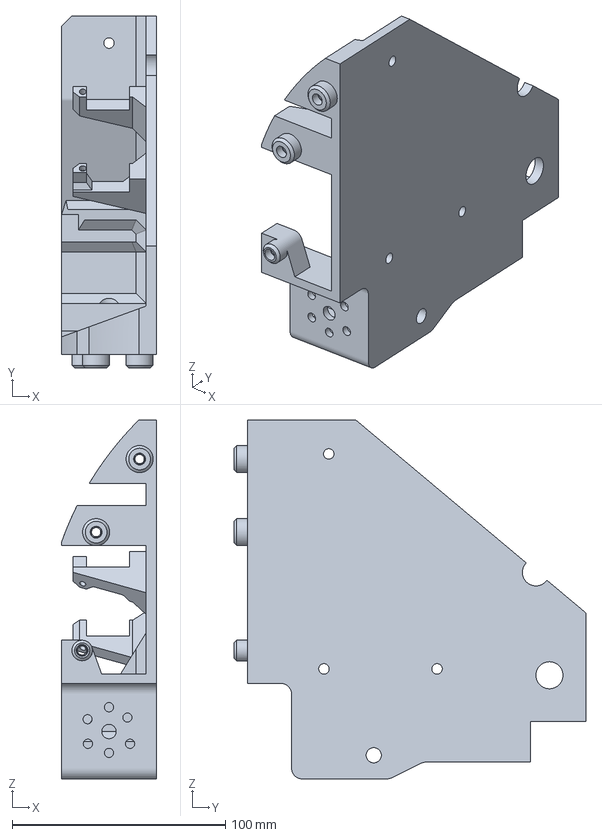
[picture p469: CAD file, 2026-09-23]
release/OH1_Upper_Instrument_Panel/OH1A2 - ASSY, PANEL, MASTER ARM/Manufacturing/FDM_OH1A2-15_EMERG JETT BRKT_A_V18.3mf
44.4 x 165.1 x 168.4 mm
