jrsteensen/OpenHornet/release/OH1_Upper_Instrument_Panel/OH1A3 - ASSY, DDIv2/Manufacturing/RESN_OH1A3-11_DDI BUTTON_-_V8.3mf

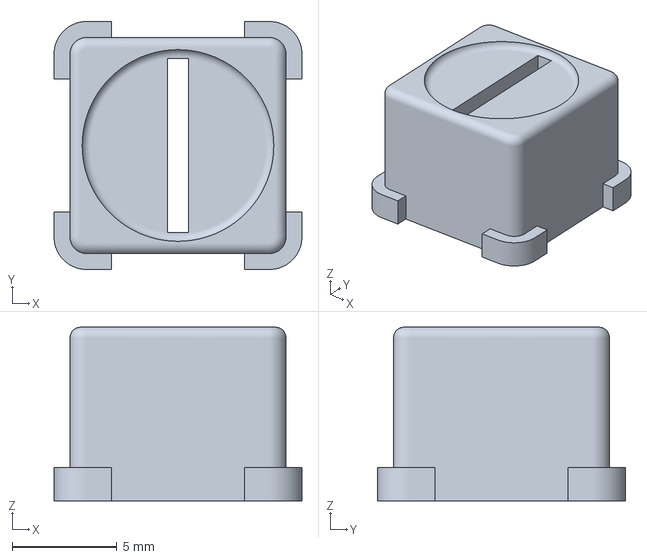
[picture p470: CAD file, 2024-02-26]
release/OH1_Upper_Instrument_Panel/OH1A3 - ASSY, DDIv2/Manufacturing/RESN_OH1A3-11_DDI BUTTON_-_V8.3mf
11.8 x 11.8 x 8.29 mm
