jrsteensen/OpenHornet/release/OH1_Upper_Instrument_Panel/OH1A4 - ASSY, EYEBROW WARNING MODULE, LEFT/Manufacturing/FDM_OH1A4-32_MIRROREWI CHASSIS - RIGHT_-_V5.3mf

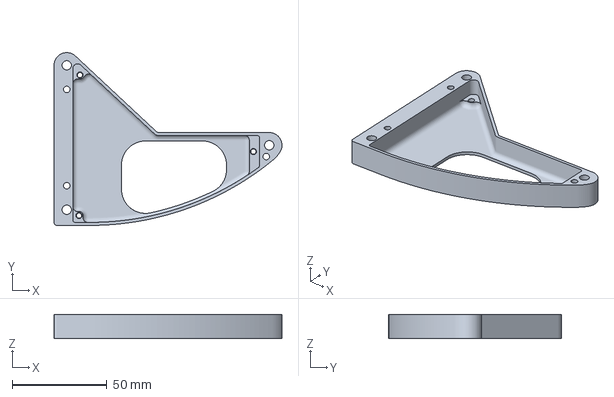
[picture p471: CAD file, 2024-02-26]
release/OH1_Upper_Instrument_Panel/OH1A4 - ASSY, EYEBROW WARNING MODULE, LEFT/Manufacturing/FDM_OH1A4-32_MIRROREWI CHASSIS - RIGHT_-_V5.3mf
120.4 x 91.3 x 12.7 mm
