jrsteensen/OpenHornet/release/OHE_Electronics/OHC0015-10 - PCB, DDI_AMPCD_CONTROLLER/Important Manufacturing Instructions.txt

1:  This PCB only has Top Layer components and will only have a "BOM_TOP-CONTROLLER_AMPCD DDI.csv"
