jrsteensen/OpenHornet/ECAD/PCBs/ABSIS/ABSIS_HID Bus Master/JLCPCB/production_files/Important Manufacturing Instructions.txt

1:  This PCB only has Top Layer components.
