jrsteensen/OpenHornet/release/OH4_Left_Console/Manufacturing/OH4A1-9001 - DECAL, GROUND POWER.pdf

# GROUND POWER

SW1
POS A
MISSION CMPTR 1,
AND LMDI
POS B
MISSION CMPTR 2,
ATARS/RECCE POD
AND POS A EQUIP
SW2
POS A
RMDI, HUD, RADAR, INS
AND DMS/MPCD
POS B
TACAN, ADF, UHF, IFEI
1 AND 2, RDR ALTMTR, CSC,
ADF, BCN, RDR AUG RCVR
ILS, D/L, IFF, KIT, STBY
INSTR, KY-58, UFC AND
POS A EQUIP

SW3
POS A
ALQ-165, ALE-47
INTFER BLANKER,
ANTI-SKID,
OXY-GAGING, ALR-67(V)
AND DFIRS
POS B
SMS, AWW-4, HARM,
FLIR, LST/NFLR
GUN DECODER
AND POS A EQUIP
SW4
POS A
ICS
POS B
ICS, FCES

78301-74A690087-2838
