jrsteensen/OpenHornet/release/OH4_Left_Console/Manufacturing/OH4A9-9001 - DECAL, RH GRIP ASSY.pdf

GRIP ASSY, LVR, ENG
THROTTLE, R.H., FWD
OH4A9-106
SERNO
DATE CODE
NSN
US
