jrsteensen/OpenHornet/release/OH4_Left_Console/Manufacturing/OH4A9-9002 - DECAL, LH GRIP ASSY.pdf

GRIP ASSY, LVR, ENG
THROTTLE, L.H., FWD
OH4A9-205
SERNO
DATE CODE
NSN
US
