jrsteensen/OpenHornet/release/OH1_Upper_Instrument_Panel/OH1A8 - ASSY, UPFRONT CONTROL PANEL/Manufacturing/OH1A8-9001 - DECAL, TV LENS_-_V2.pdf

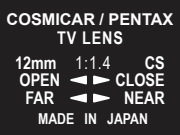
[picture p500: figure]
COSMICAR / PENTAX; 12mm OPEN FAR; CS CLOSE NEAR MADE IN JAPAN; TV LENS
