jrsteensen/OpenHornet/ECAD/PCBs/Backlight PCBs/Backlighting_Type A/FIRE TEST PANEL/Assets/FIRE TEST PANEL-BOT.png

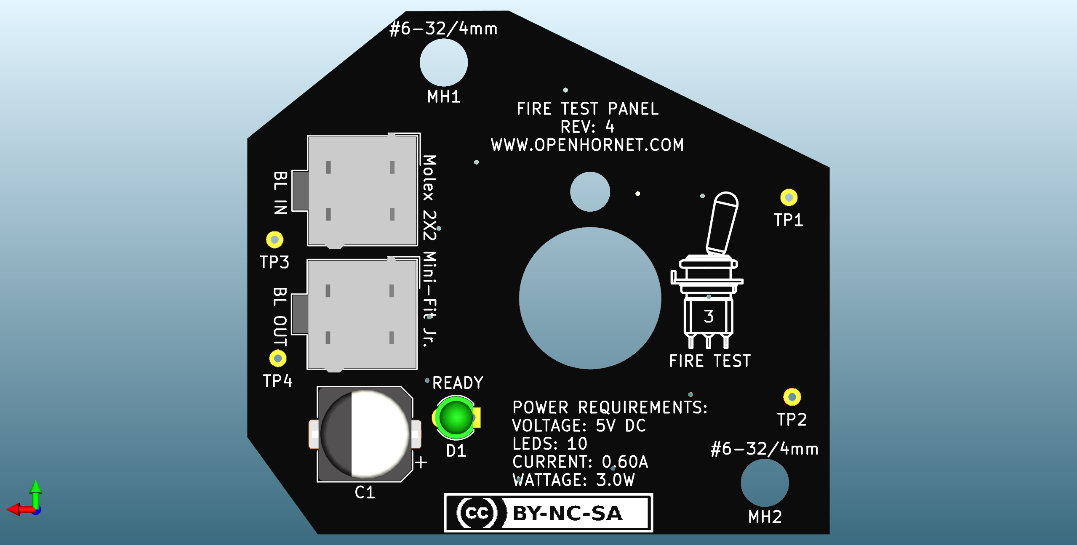
ECAD/PCBs/Backlight PCBs/Backlighting_Type A/FIRE TEST PANEL/Assets/FIRE TEST PANEL-BOT.png
