jrsteensen/OpenHornet/ECAD/PCBs/Backlight PCBs/Backlighting_Type A/FIRE TEST PANEL/Assets/FIRE TEST PANEL-BOT_ISO.png

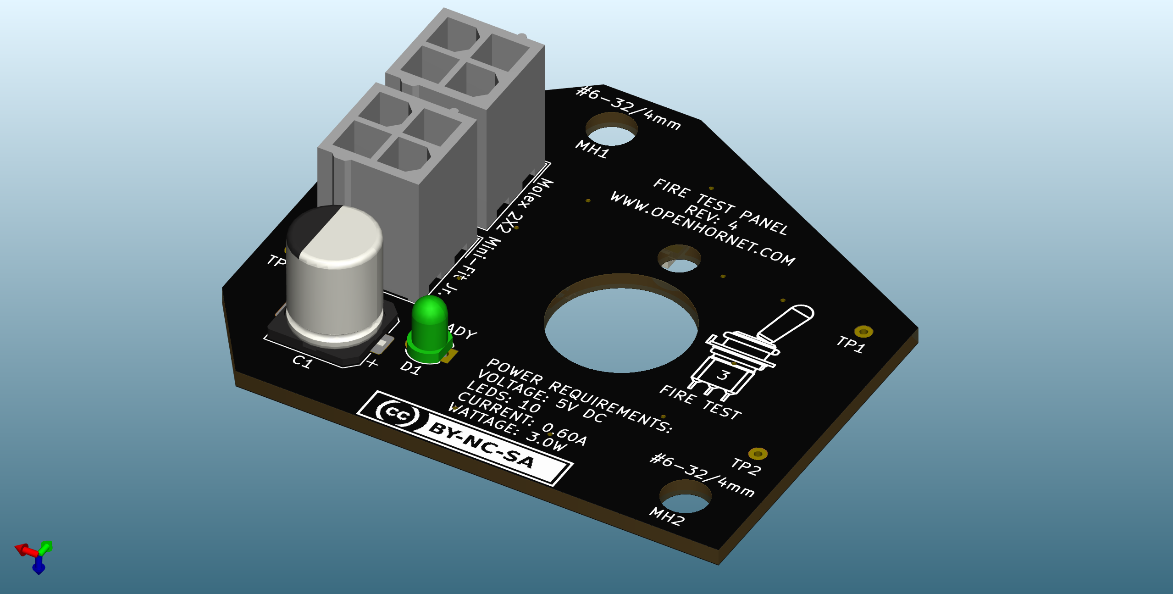
ECAD/PCBs/Backlight PCBs/Backlighting_Type A/FIRE TEST PANEL/Assets/FIRE TEST PANEL-BOT_ISO.png
