jrsteensen/OpenHornet/ECAD/PCBs/Backlight PCBs/Backlighting_Type A/FIRE TEST PANEL/Assets/FIRE TEST PANEL-TOP_ISO.png

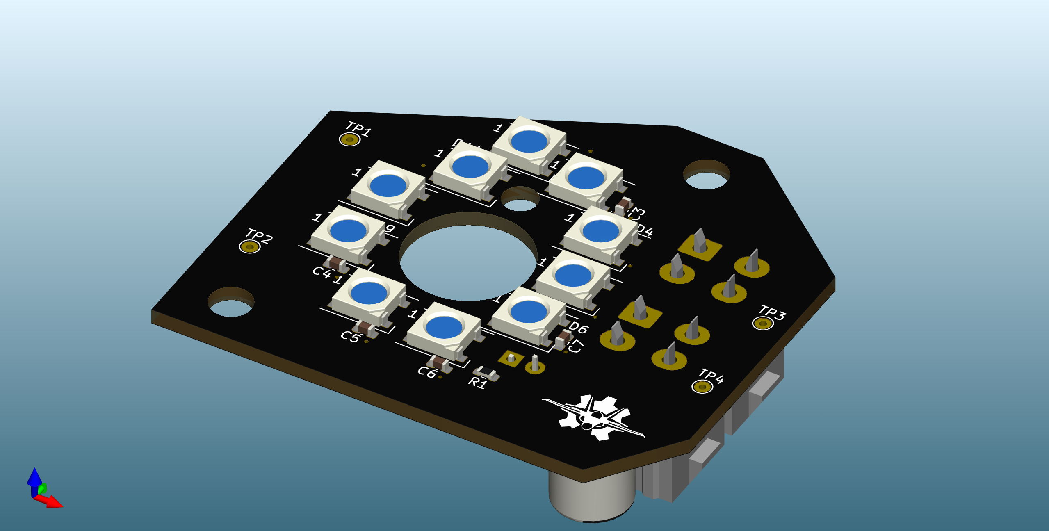
ECAD/PCBs/Backlight PCBs/Backlighting_Type A/FIRE TEST PANEL/Assets/FIRE TEST PANEL-TOP_ISO.png
