jrsteensen/OpenHornet/release/OHE_Electronics/OH2A7A1-11 - STANDBY_CONTROLLER/CONTROLLER_Standby Instrument.pdf

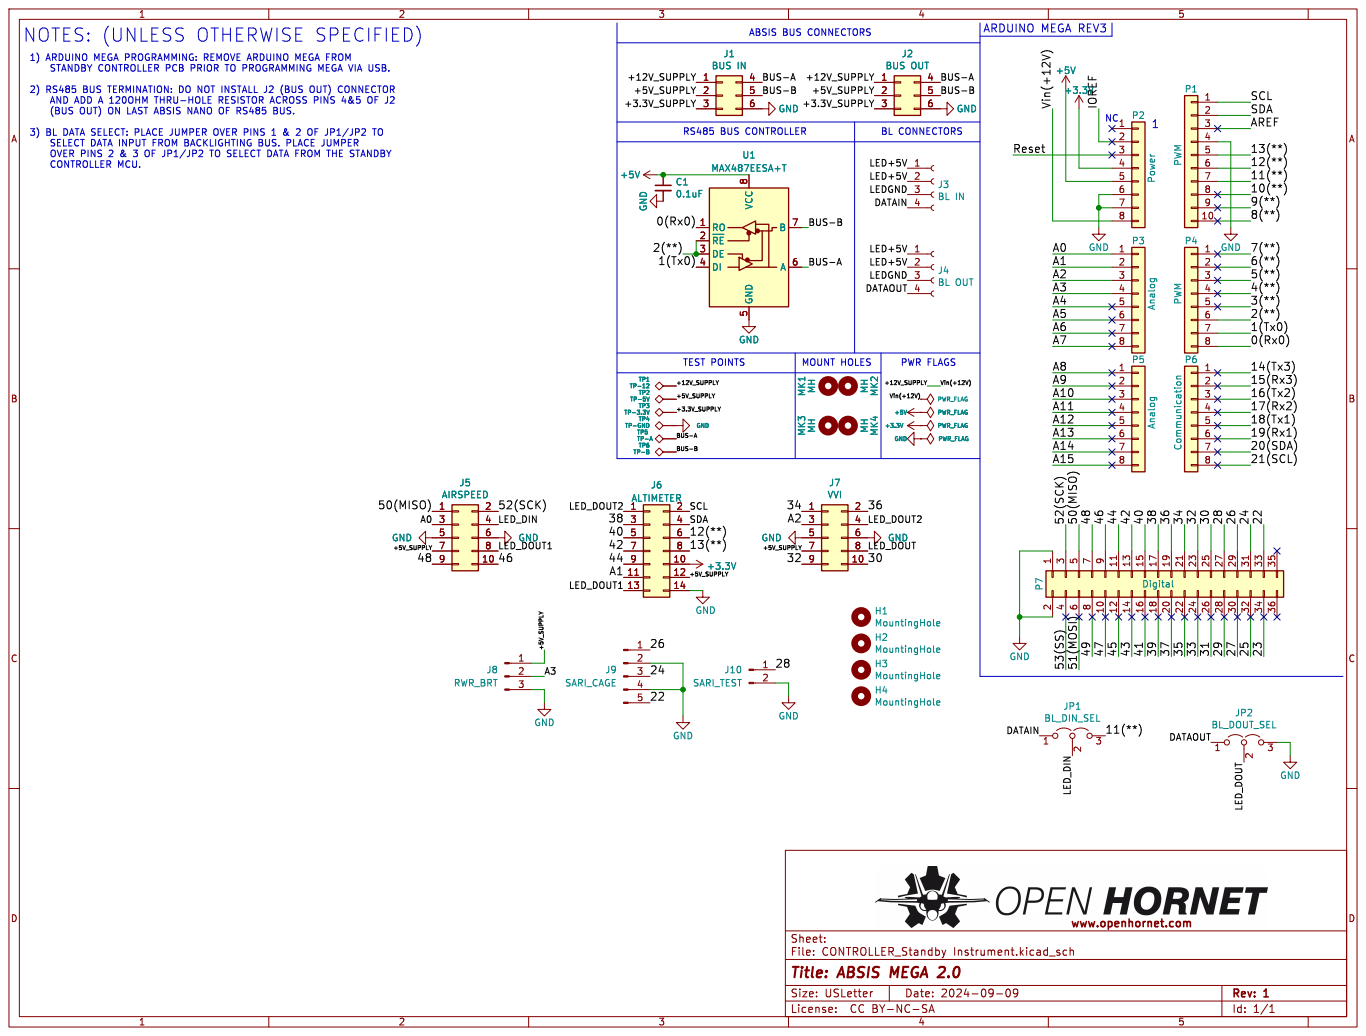
[picture p519: page 1]

1) ARDUINO MEGA PROGRAMMING: REMOVE ARDUINO MEGA FROM
STANDBY CONTROLLER PCB PRIOR TO PROGRAMMING MEGA VIA USB. 2) RS485 BUS TERMINATION: DO NOT INSTALL J2 (BUS OUT) CONNECTOR

AND ADD A 120OHM THRU-HOLE RESISTOR ACROSS PINS 4&5 OF J2

H1 MountingHole H2 MountingHole H3 MountingHole H4 MountingHole

Id: 1/1 Title: ABSIS MEGA 2.0

Size: USLetter | | Rev: | 1
License: CC | BY-NC-SA
