jrsteensen/OpenHornet/release/OHC_Common_Parts/OHC0009 - FAUX DZUS STUD/OHC0009-1 - FAUX DZUS STUD_-_v2.pdf

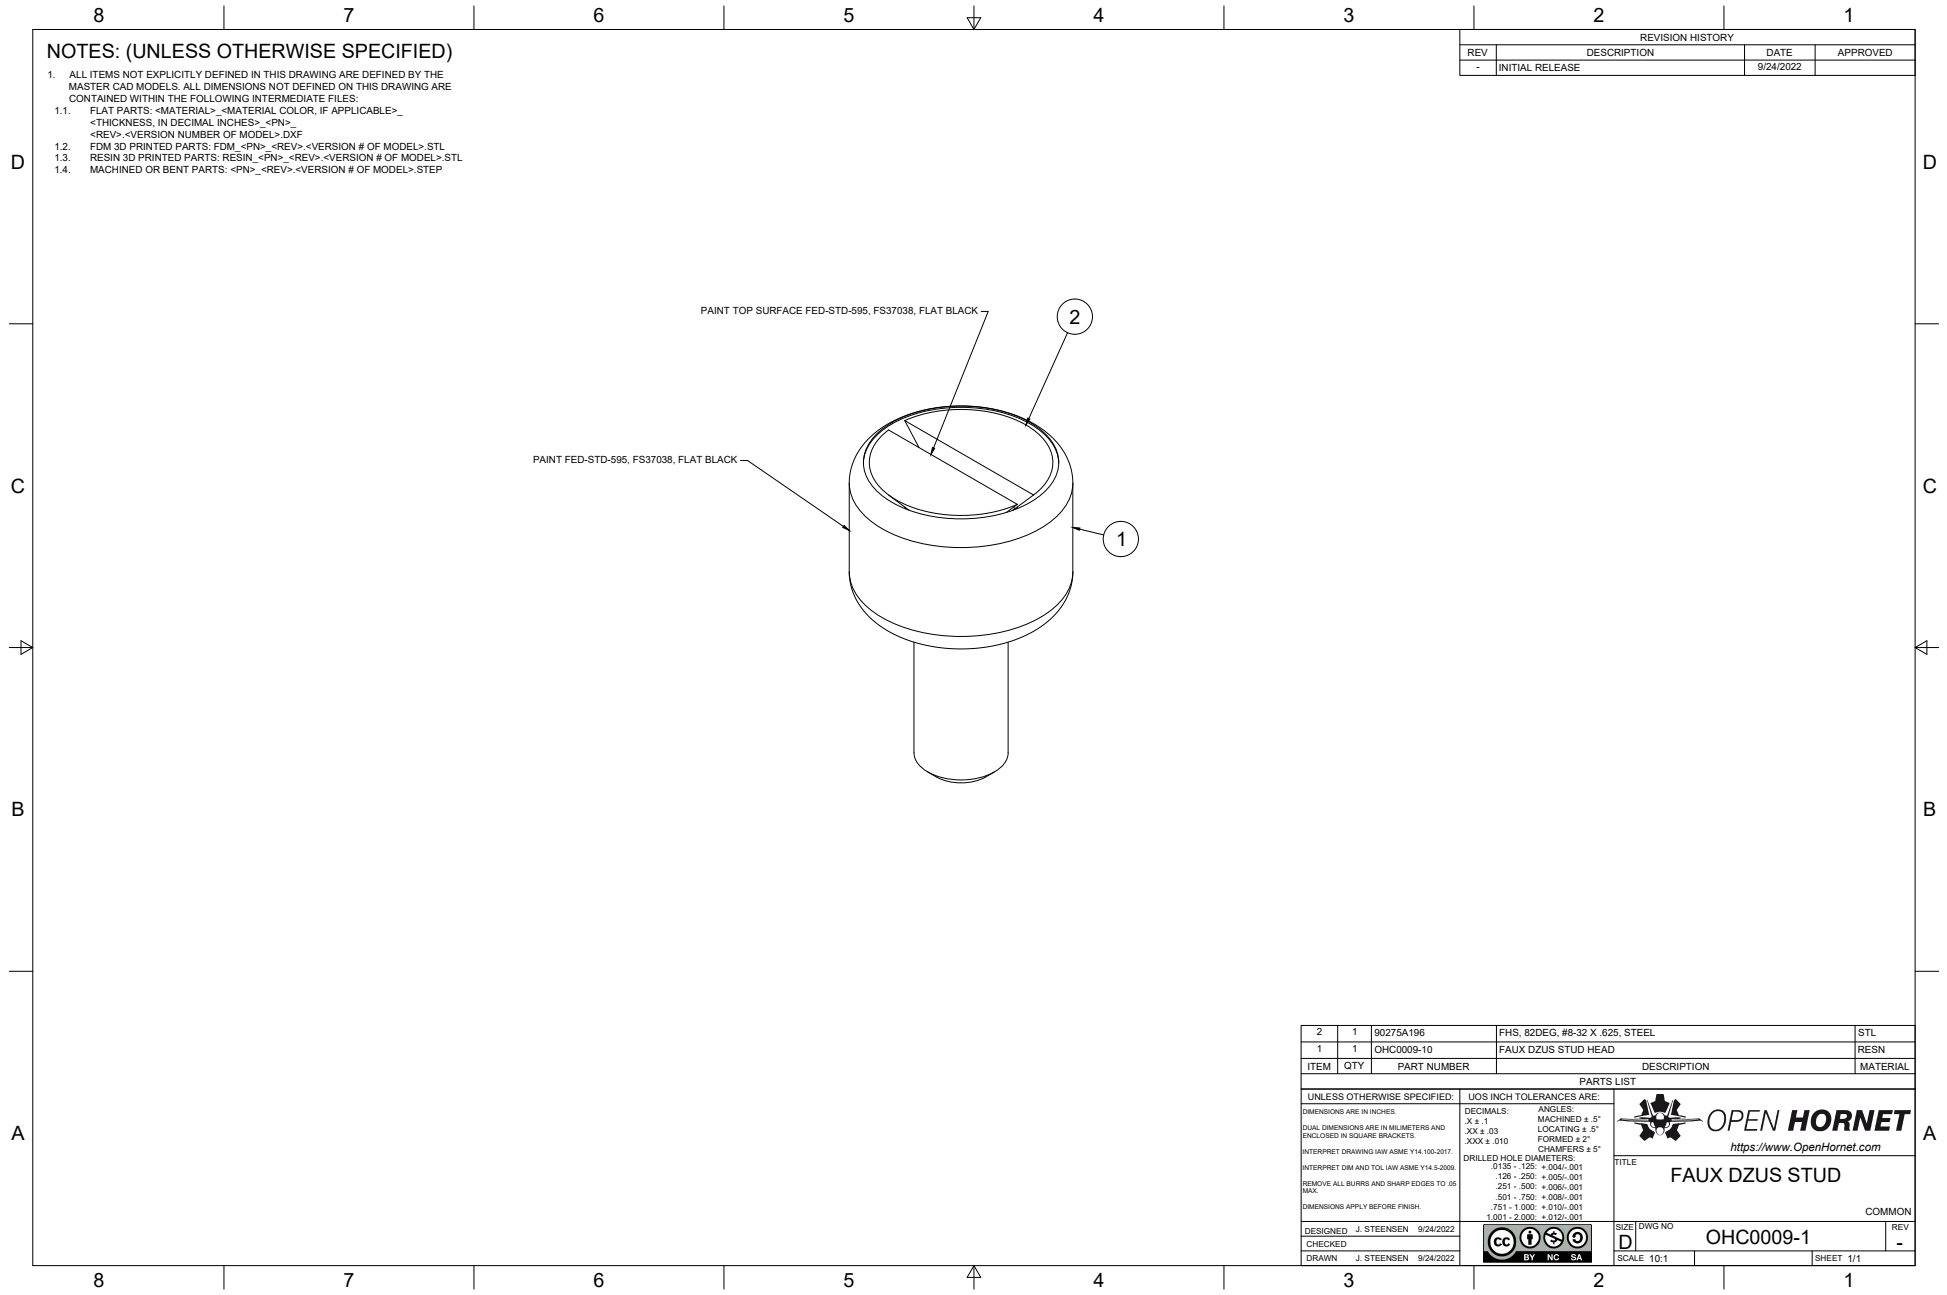
[picture p520: page 1]
J. STEENSEN; PARTS LIST; REVISION HISTORY

NOTES: (UNLESS OTHERWISE SPECIFIED)

REV | DESCRIPTION | DATE | APPROVED
- | INITIAL RELEASE | 9/24/2022

1. ALL ITEMS NOT EXPLICITLY DEFINED IN THIS DRAWING ARE DEFINED BY THE
MASTER CAD MODELS. ALL DIMENSIONS NOT DEFINED ON THIS DRAWING ARE
CONTAINED WITHIN THE FOLLOWING INTERMEDIATE FILES:
1.1. FLAT PARTS: <MATERIAL>_<MATERIAL COLOR, IF APPLICABLE>_

<THICKNESS, IN DECIMAL INCHES>_<PN>_
<REV>.<VERSION NUMBER OF MODEL>.DXF

1.2. FDM 3D PRINTED PARTS: FDM_<PN>_<REV>.<VERSION # OF MODEL>.STL
1.3. RESIN 3D PRINTED PARTS: RESIN_<PN>_<REV>.<VERSION # OF MODEL>.STL

1.4. MACHINED OR BENT PARTS: <PN>_<REV>.<VERSION # OF MODEL>.STEP

PAINT TOP SURFACE FED-STD-595, FS37038, FLAT BLACK

PAINT FED-STD-595, FS37038, FLAT BLACK

2 | 1 | 90275A196 | FHS, 82DEG, #8-32 X .625, STEEL | STL
1 | 1 | OHC0009-10 | FAUX DZUS STUD HEAD | RESN
ITEM | QTY | PART NUMBER | DESCRIPTION | MATERIAL

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

FAUX DZUS STUD

J. STEENSEN 9/24/2022 DESIGNED | | SIZE D | DWG NO OHC0009-1 | REV -
