jrsteensen/OpenHornet/release/OHE_Electronics/ABSIS001A1 - PCB, ABSIS_ALE RELAY MODULE/ABSIS_ALE Relay Module.pdf

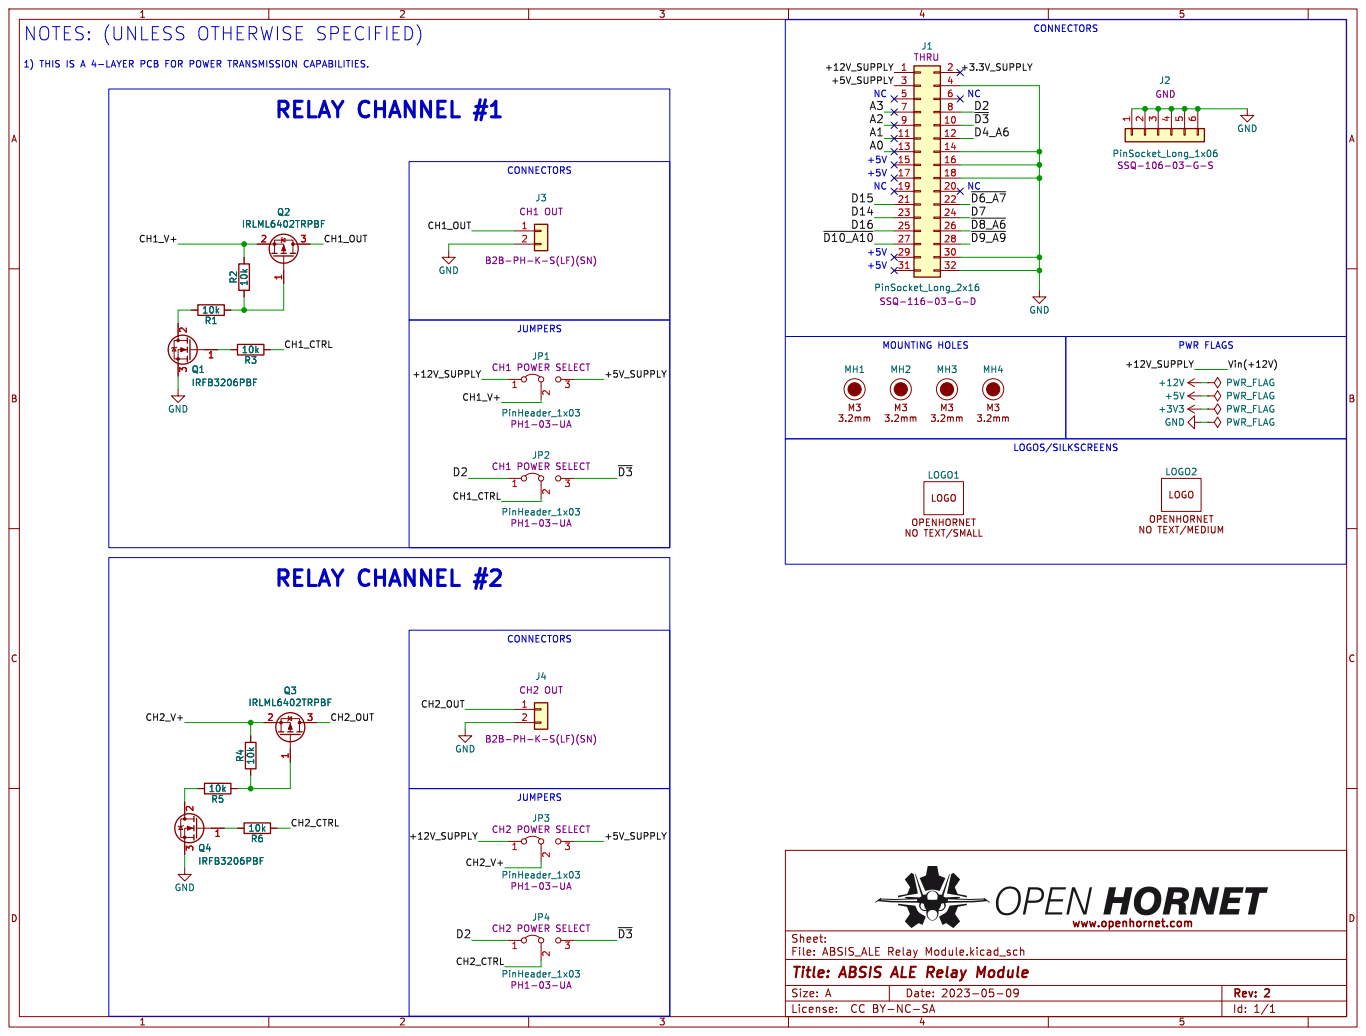
[picture p521: page 1]

J3 B2B-PH-K-S(LF)(SN) CH1 OUT GND

J4 B2B-PH-K-S(LF)(SN) CH2 OUT R4 10k
IRLML6402TRPBF

Id: 1/1 Title: ABSIS ALE Relay Module

Size: A | | Rev: 2
License: CC | BY-NC-SA
