jrsteensen/OpenHornet/release/OHE_Electronics/ABSIS004 - PCB, ABSIS_HALL SENSOR/ABSIS_Hall Sensor.pdf

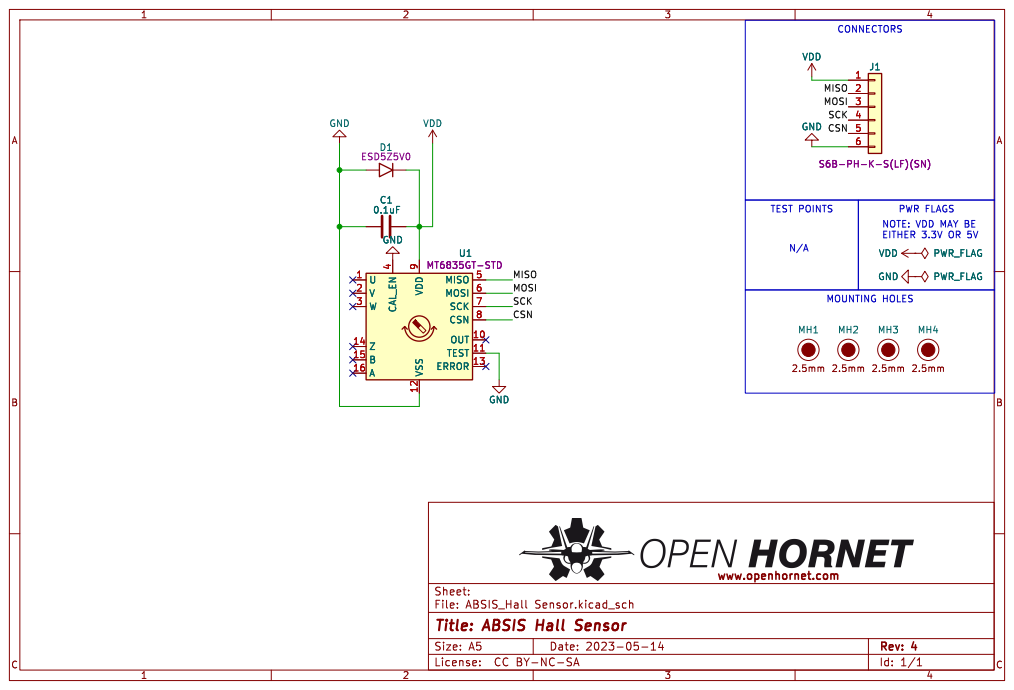
[picture p522: page 1]

PWR FLAGS CONNECTORS MOUNTING HOLES

Size: A5 | | Rev: 4
License: CC | BY-NC-SA
