jrsteensen/OpenHornet/release/OHE_Electronics/ABSIS005-10 - PCB, ABSIS_BACKLIGHT CONTROLLER/ABSIS_Backlight Controller.pdf

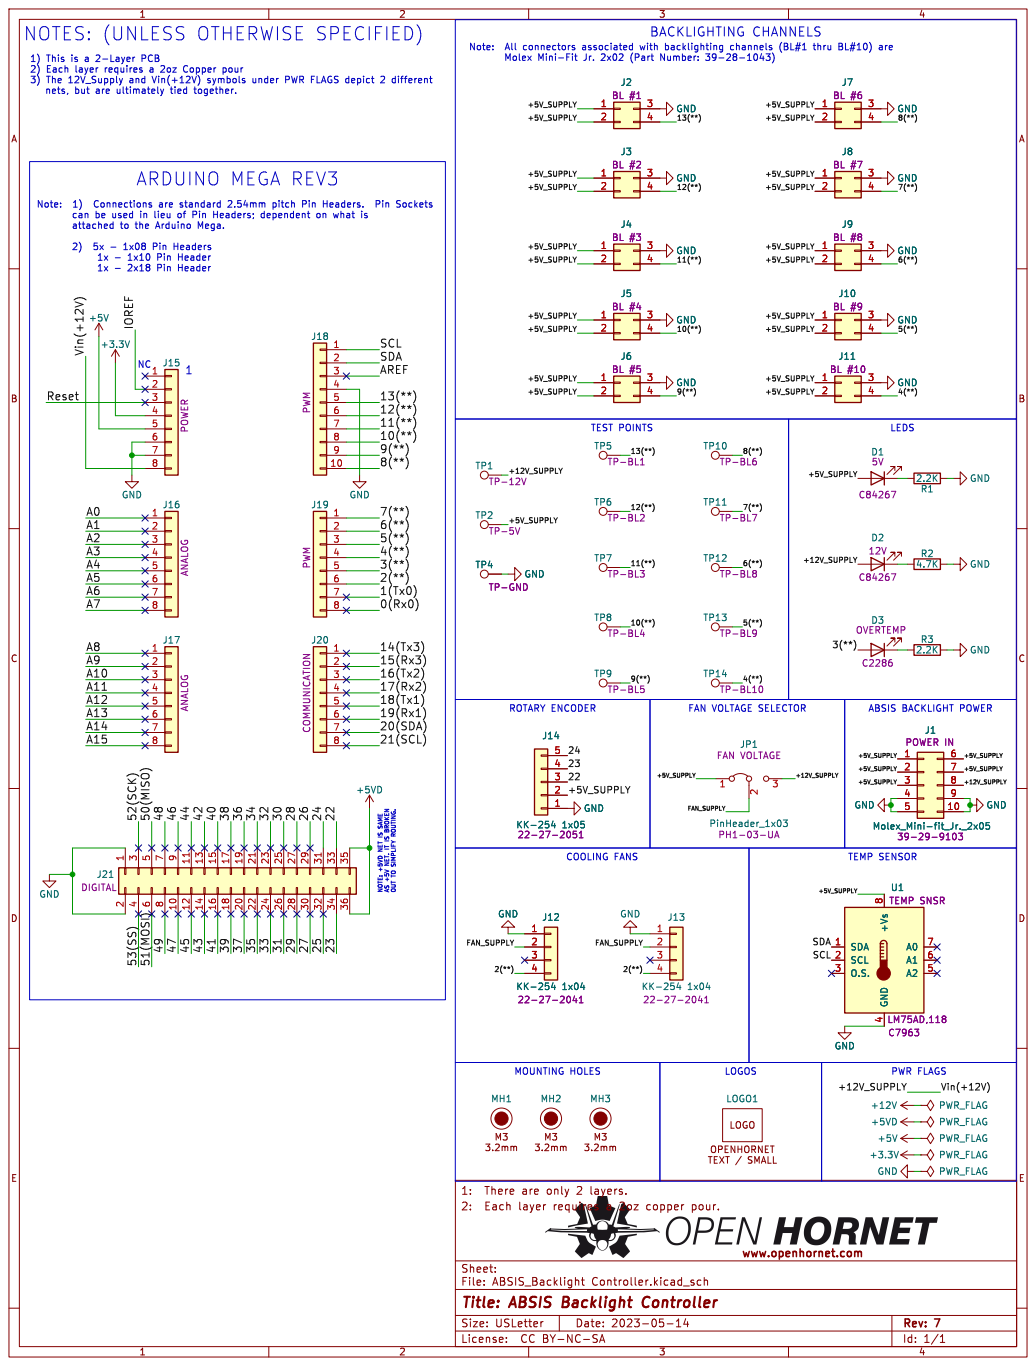
[picture p523: page 1]

COOLING FANS ARDUINO MEGA REV3

2) 5x - 1x08 Pin Headers 1x - 1x10 Pin Header 1x - 2x18 Pin Header

Size: USLetter | | Rev: 7
License: CC | BY-NC-SA
