jrsteensen/OpenHornet/release/OHE_Electronics/ABSIS006 - PCB, ABSIS_ATX PSU BREAKOUT/ABSIS_ATX Power Supply Unit.pdf

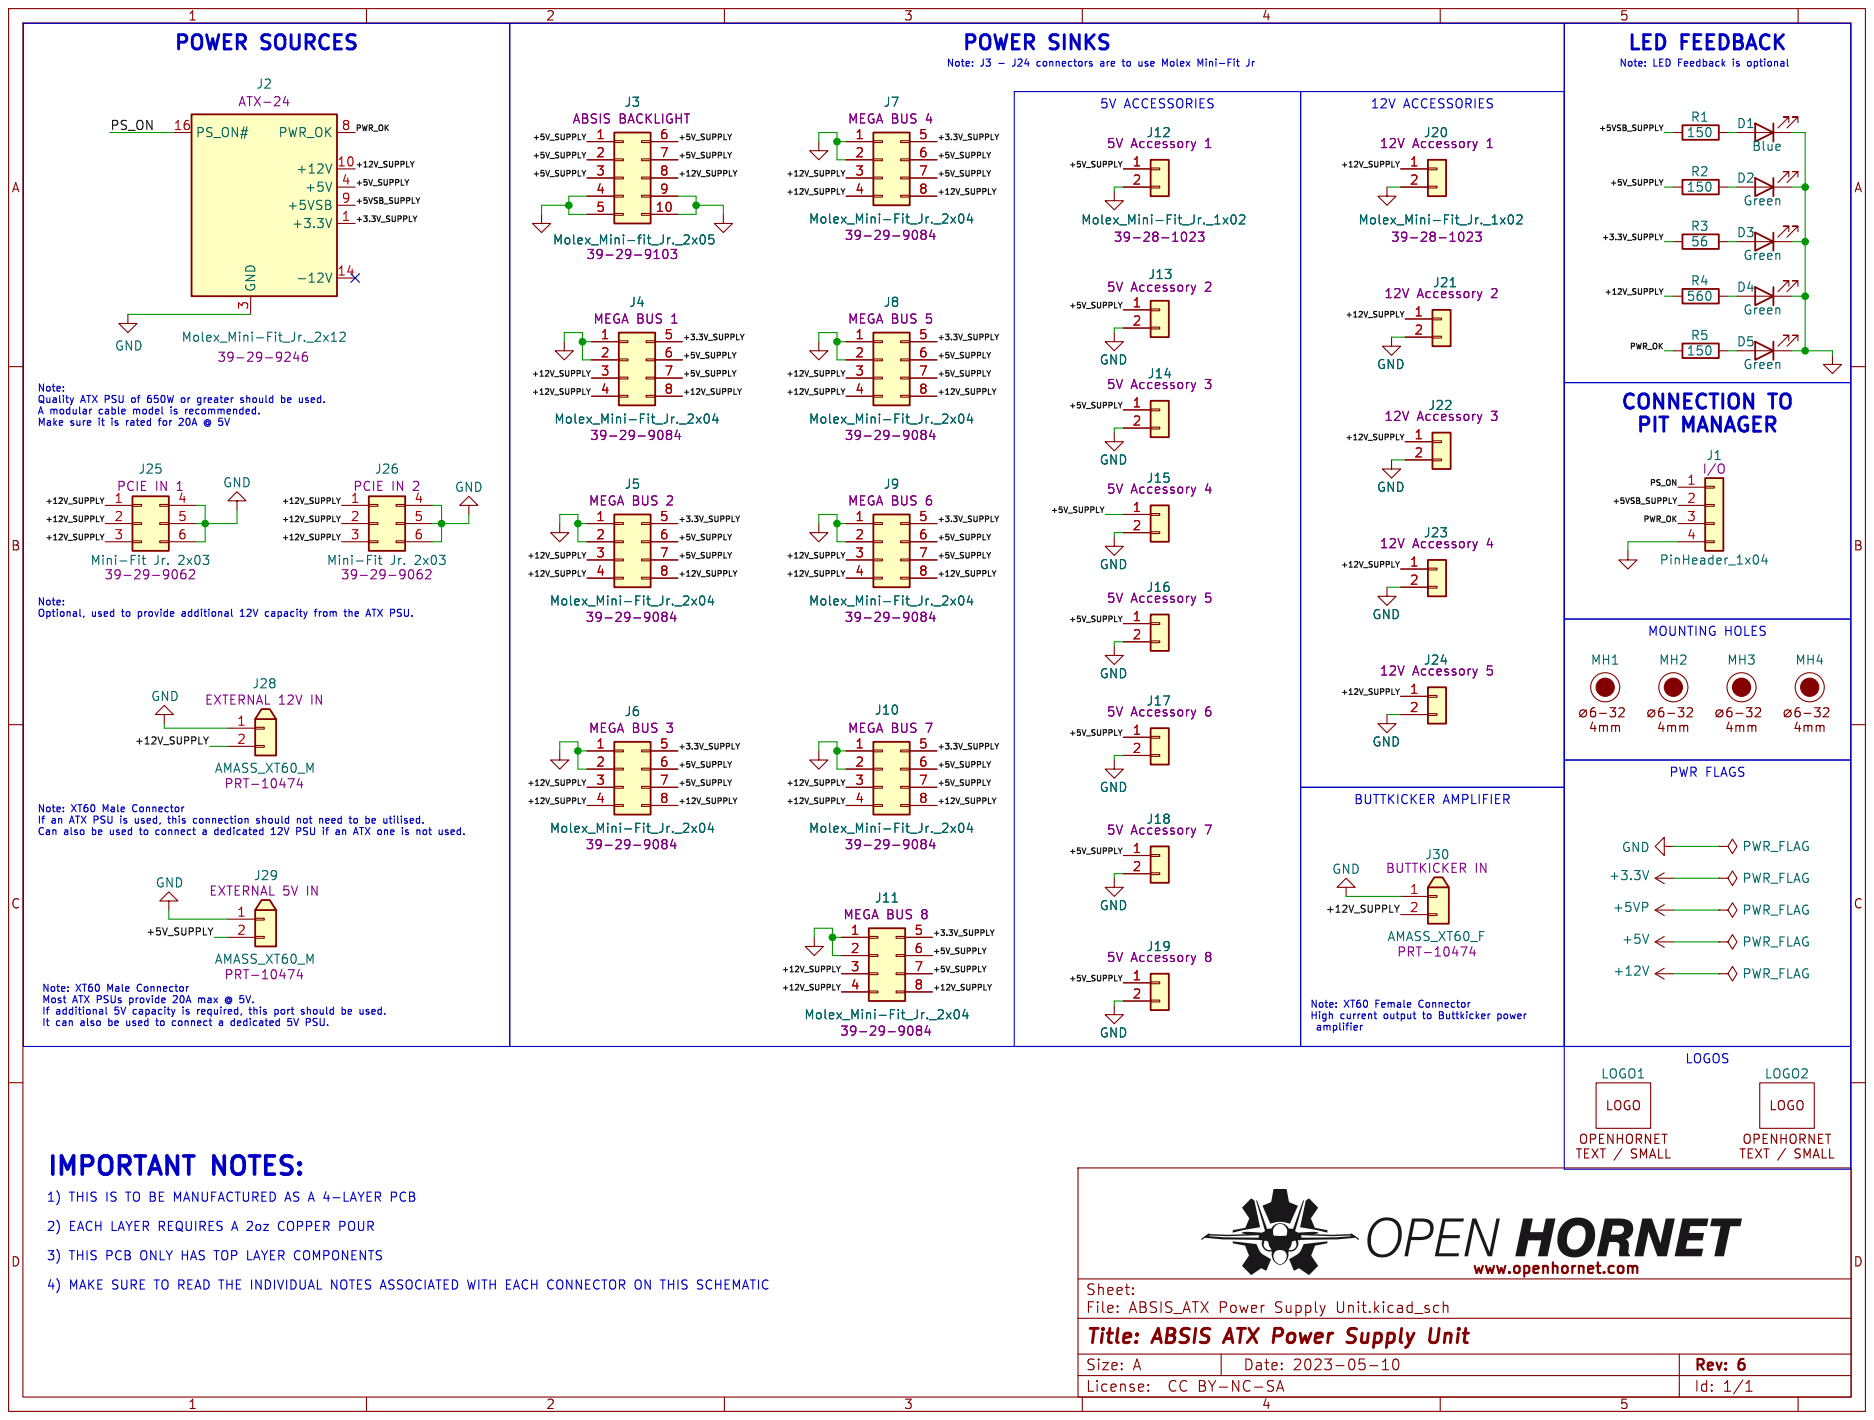
[picture p524: page 1]

Note: LED Feedback is optional

39-29-9062 PCIE IN 2 GND
PRT-10474 EXTERNAL 12V IN GND
+12V_SUPPLY Note: XT60 Male Connector

PRT-10474 EXTERNAL 5V IN GND

1) THIS IS TO BE MANUFACTURED AS A 4-LAYER PCB

2) EACH LAYER REQUIRES A 2oz COPPER POUR

3) THIS PCB ONLY HAS TOP LAYER COMPONENTS
4) MAKE SURE TO READ THE INDIVIDUAL NOTES ASSOCIATED WITH EACH CONNECTOR ON THIS SCHEMATIC

Size: A | | Rev: 6
License: CC | BY-NC-SA
