jrsteensen/OpenHornet/release/OHE_Electronics/ABSIS007-10 - PCB, ABSIS_PIT MANAGEMENT SYSTEM/ABSIS_Pit Management System.pdf

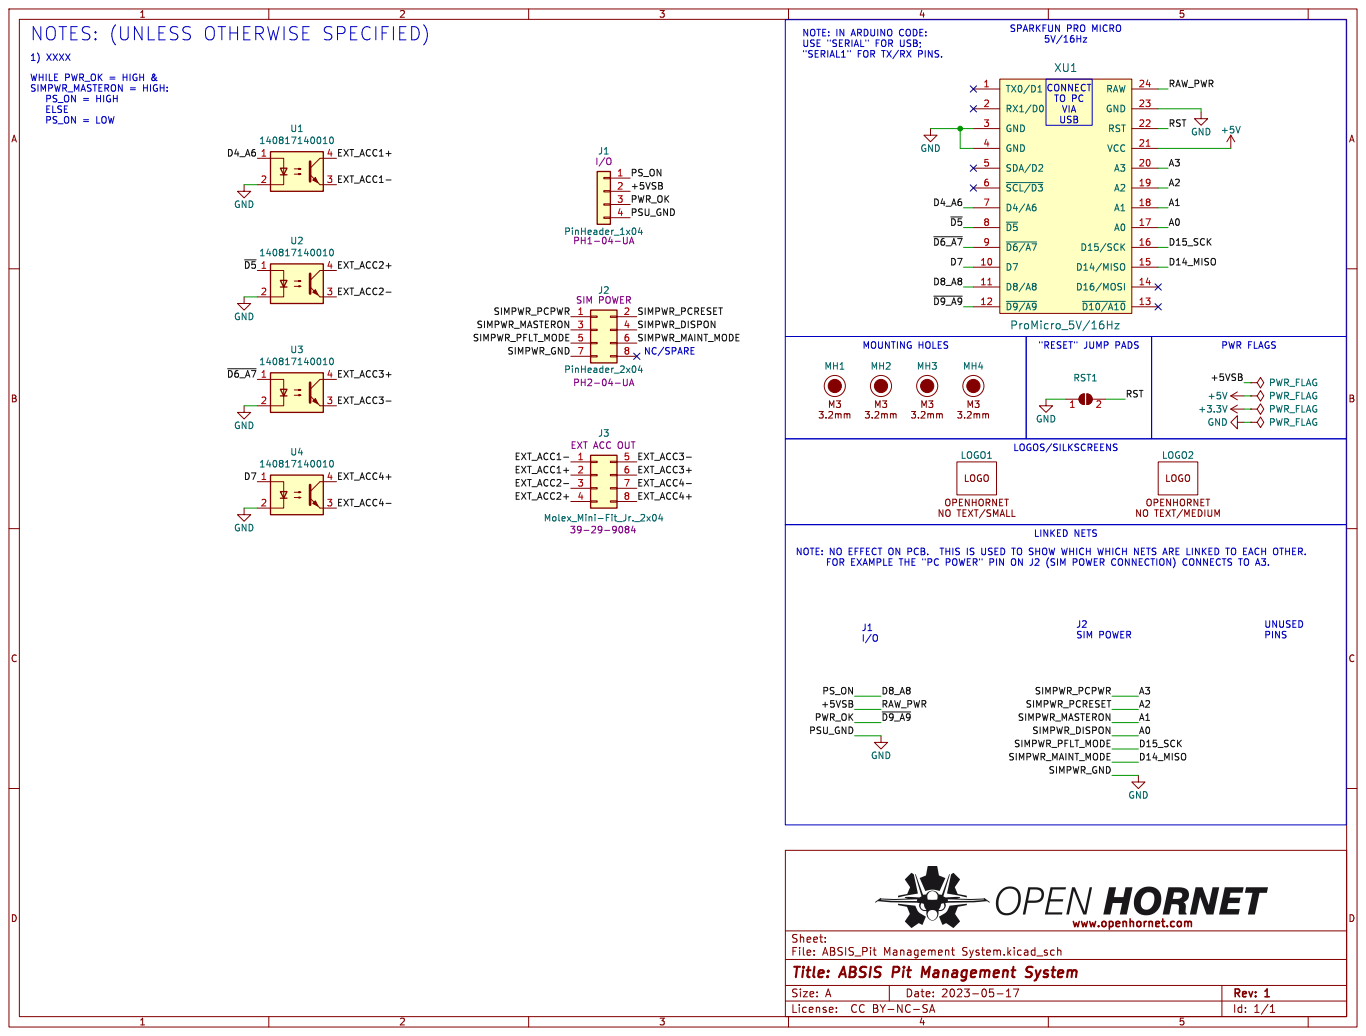
[picture p525: page 1]

PINS NOTES: (UNLESS OTHERWISE SPECIFIED)

NOTE: IN ARDUINO CODE: USE "SERIAL" FOR USB; "SERIAL1" FOR TX/RX PINS.

Id: 1/1 Title: ABSIS Pit Management System

Size: A | | Rev: 1
License: CC | BY-NC-SA
