jrsteensen/OpenHornet/release/OHE_Electronics/OH10A1A1-10 - PCB, SIM POWER PANEL/SIM POWER PANEL.pdf

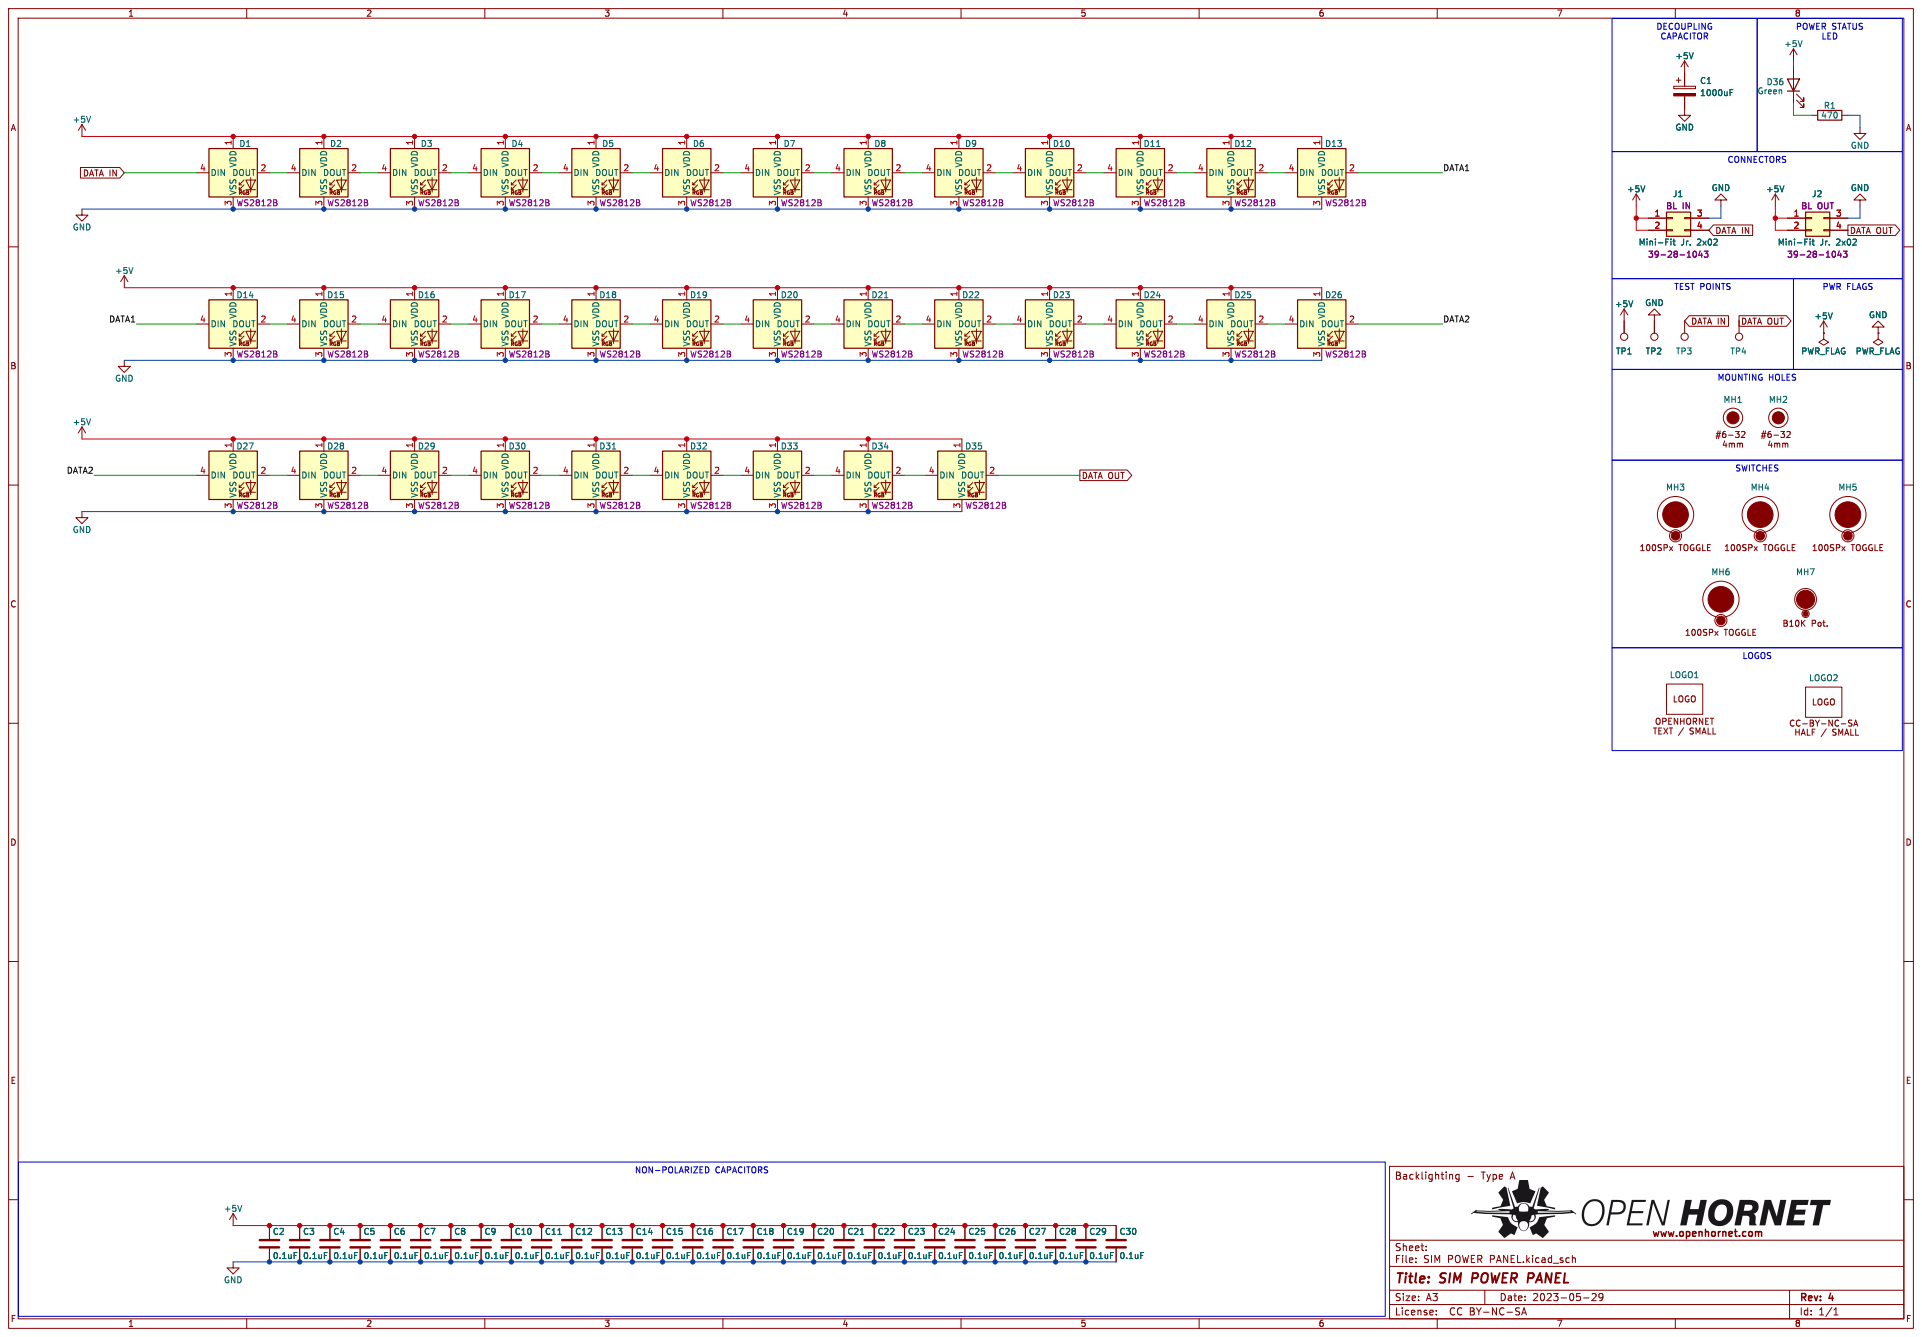
[picture p526: page 1]

3 DIN 4 D28 WS2812B DATA OUT DATA IN DATA OUT DATA IN DATA OUT DATA IN DATA1 DATA1 DATA2 DATA2

Id: 1/1 Title: SIM POWER PANEL

Size: A3 | | Rev: 4 | F Date: 2023-05-29
License: CC | BY-NC-SA
