jrsteensen/OpenHornet/release/OHE_Electronics/OH1A2-11 - PCB, MASTER ARM PANEL/MASTER ARM PANEL.pdf

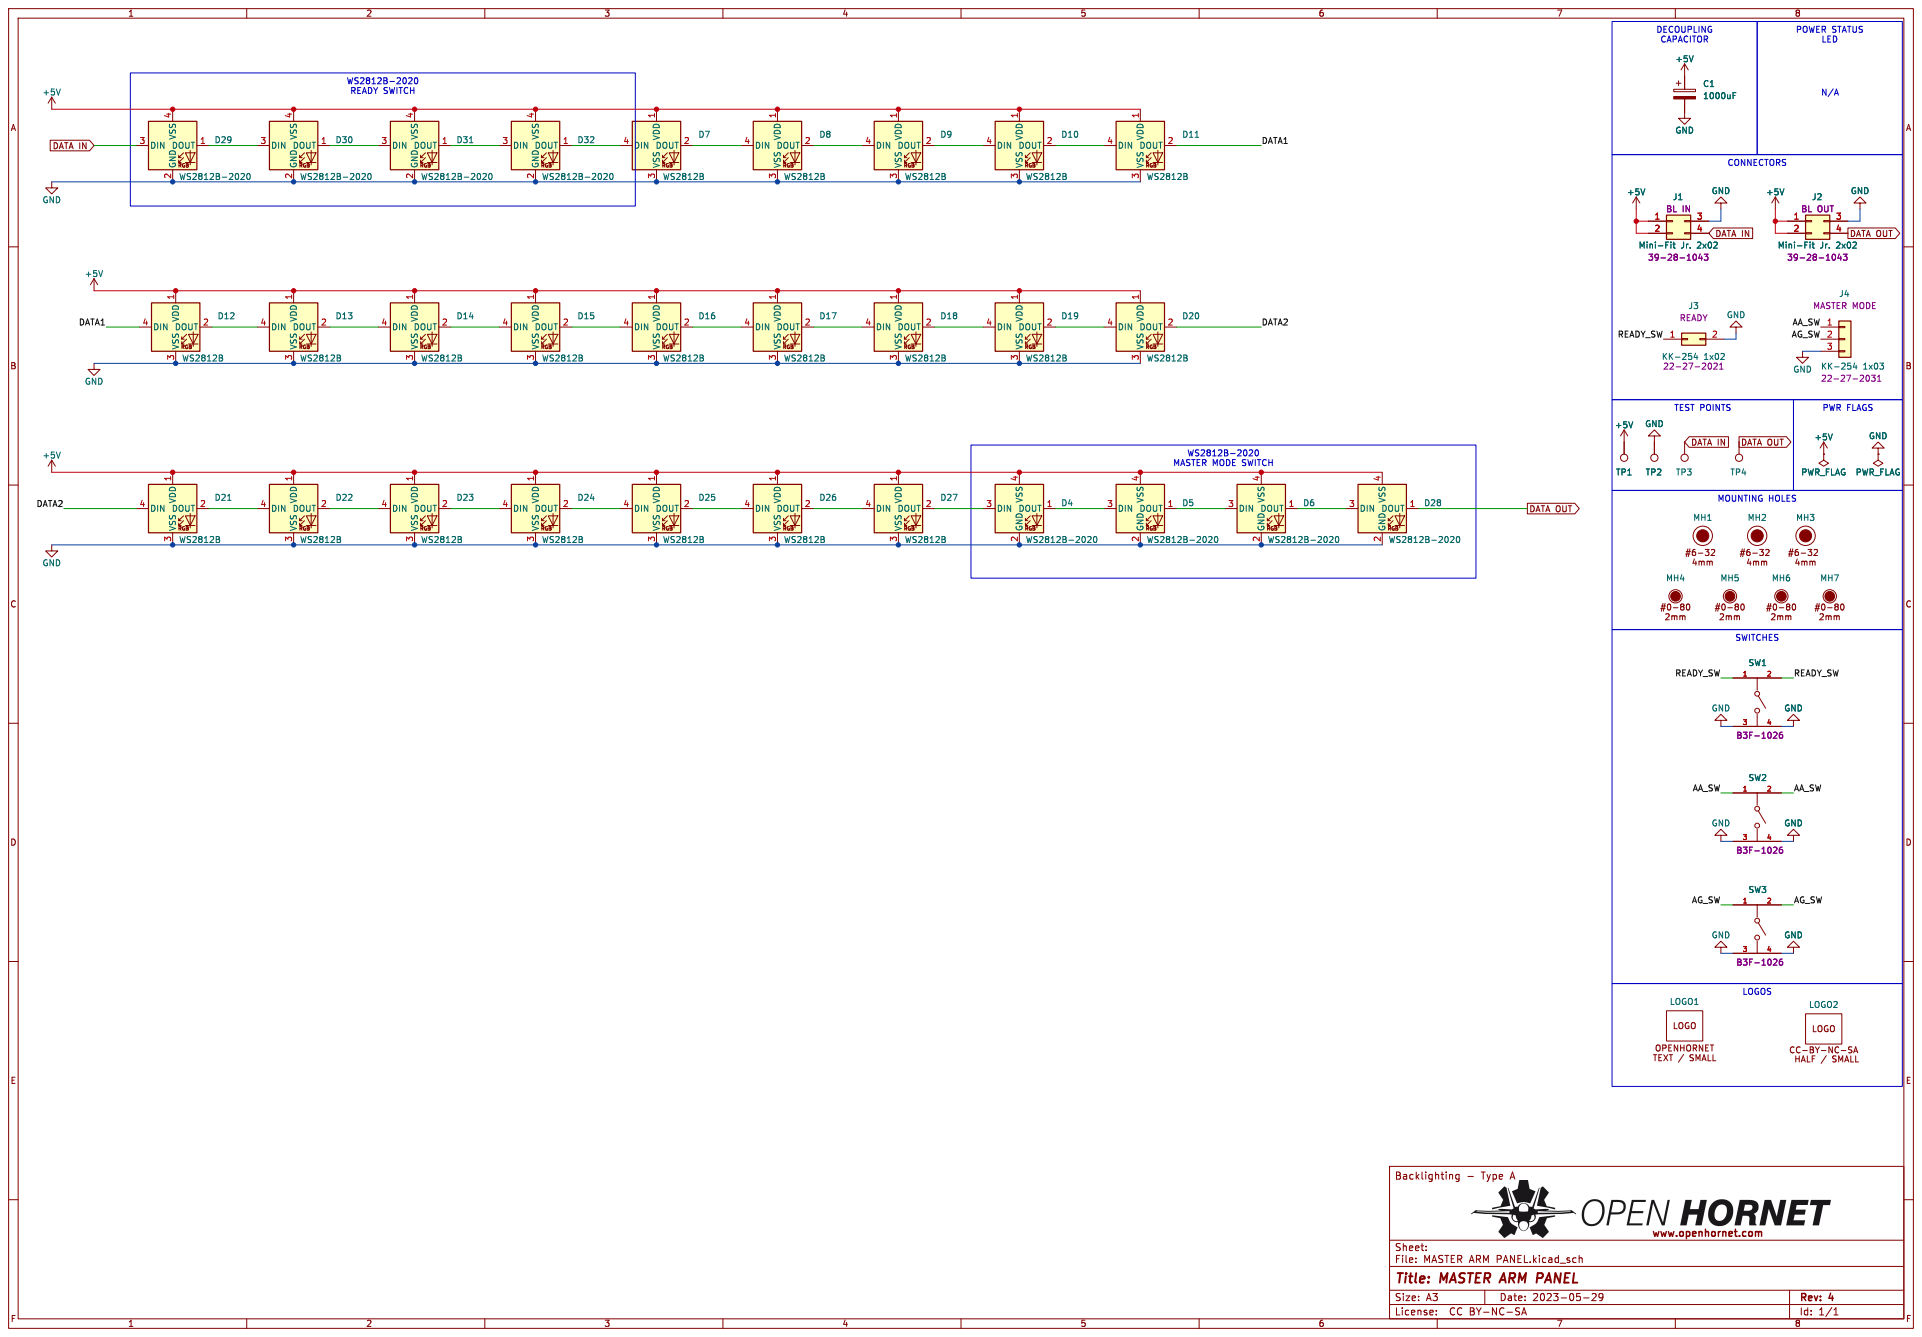
[picture p527: page 1]

CONNECTORS
22-27-2031 MASTER MODE GND GND

Id: 1/1 Title: MASTER ARM PANEL

Size: A3 | | Rev: 4 | F Date: 2023-05-29
License: CC | BY-NC-SA
