jrsteensen/OpenHornet/release/OHE_Electronics/OH1A6-13 - PCB, SPIN RCV PANEL/SPIN RCV PANEL.pdf

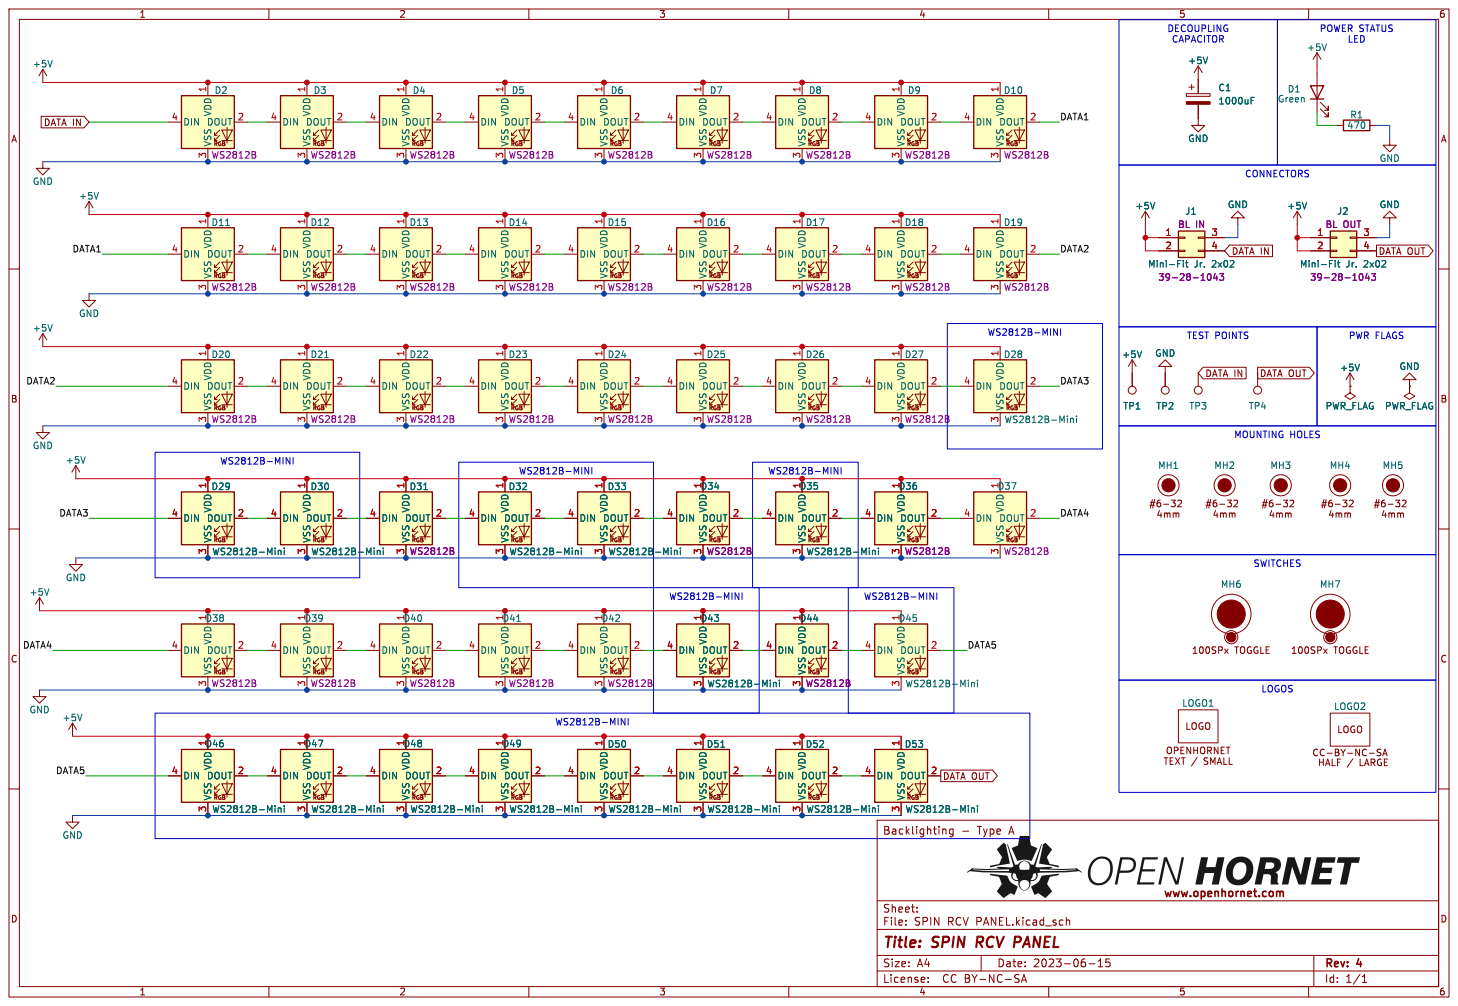
[picture p528: page 1]

LED MOUNTING HOLES WS2812B-MINI WS2812B-MINI

3 DIN 4 D35WS2812B-Mini DATA IN

3 DIN 4 D28 WS2812B-Mini GND GND

3 DIN 4 D30 WS2812B-Mini RGB VDD

3 DIN 4 D33 WS2812B-Mini RGB VDD

3 DIN 4 D46WS2812B-Mini RGB VDD

3 DIN 4 D49WS2812B-Mini RGB VDD

3 DIN 4 D45WS2812B-Mini RGB VDD

3 DIN 4 D51 WS2812B-Mini RGB VDD

3 DIN 4 D52 WS2812B-Mini RGB VDD

3 DIN 4 D50 WS2812B-Mini RGB VDD
RGB VDD

3 DIN 4 D53 WS2812B-Mini RGB VDD

Id: 1/1 Title: SPIN RCV PANEL

Size: A4 | | Rev: 4
License: CC | BY-NC-SA
