jrsteensen/OpenHornet/release/OHE_Electronics/OH2A2A1-104 - PCB, JETT STATION SELECT PLACARD/JETT STATION SELECT PLACARD.pdf

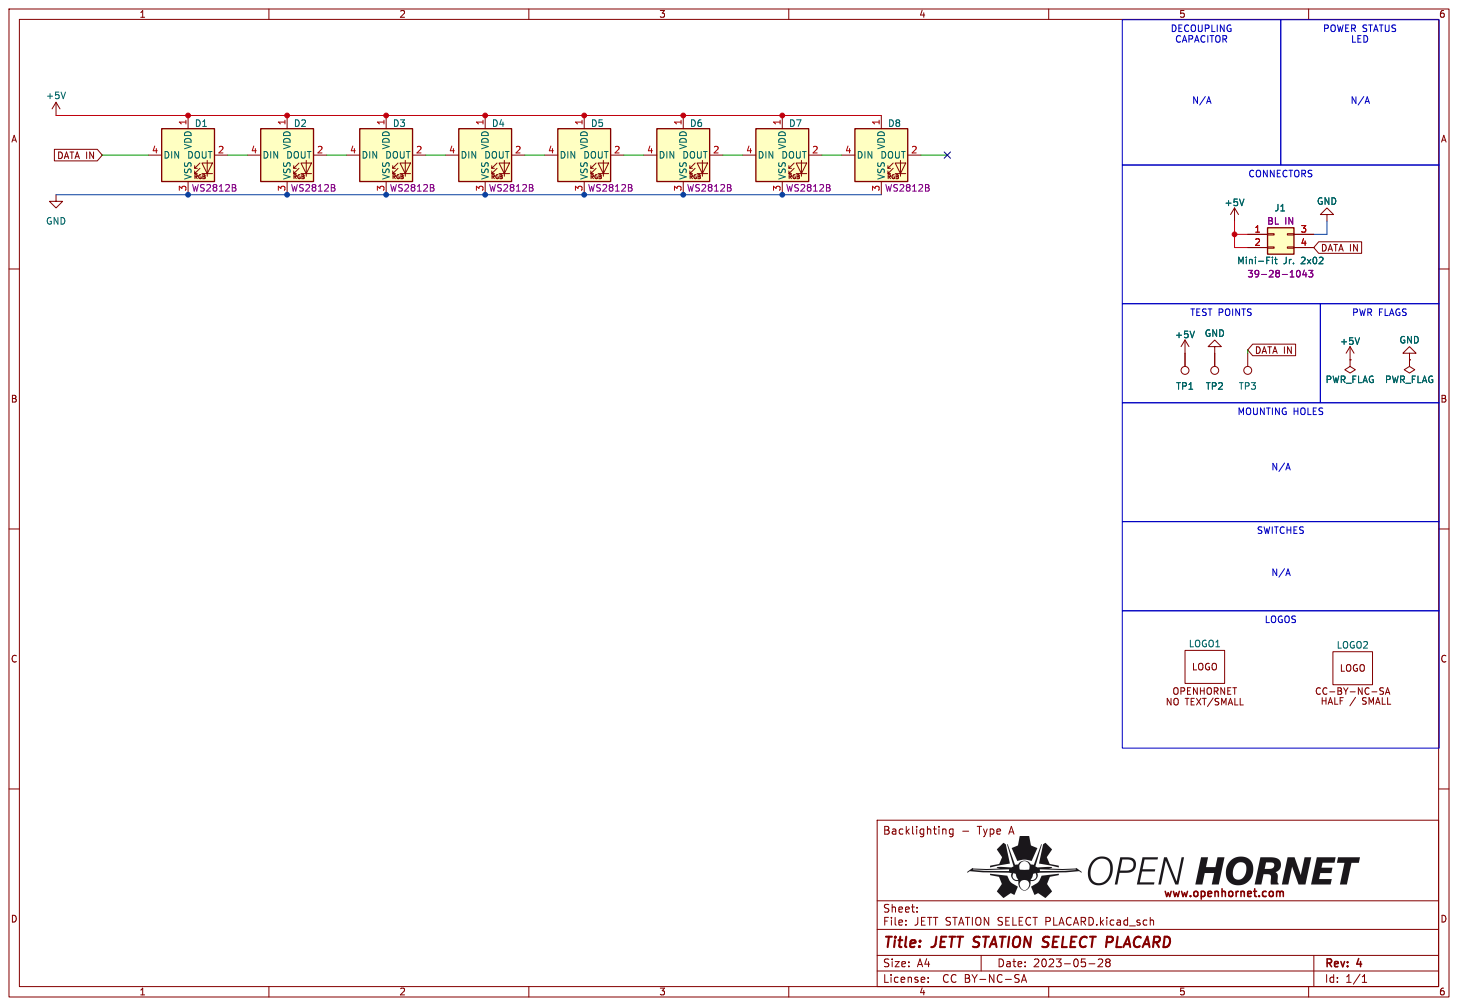
[picture p529: page 1]

TP3 +5V 39-28-1043 BL IN GND | | N/A MOUNTING HOLES GND

3 DIN 4 D3 WS2812B CC-BY-NC-SA HALF / SMALL
RGB VDD

TP1 | TP2 | +5V +5V +5V PWR_FLAG PWR_FLAG PWR_FLAG PWR_FLAG

Id: 1/1 Title: JETT STATION SELECT PLACARD

Size: A4 | | Rev: 4
License: CC | BY-NC-SA
