jrsteensen/OpenHornet/release/OHE_Electronics/OH2A5A1-13 - PCB, ECM DISP PANEL/ECM DISP PANEL.pdf

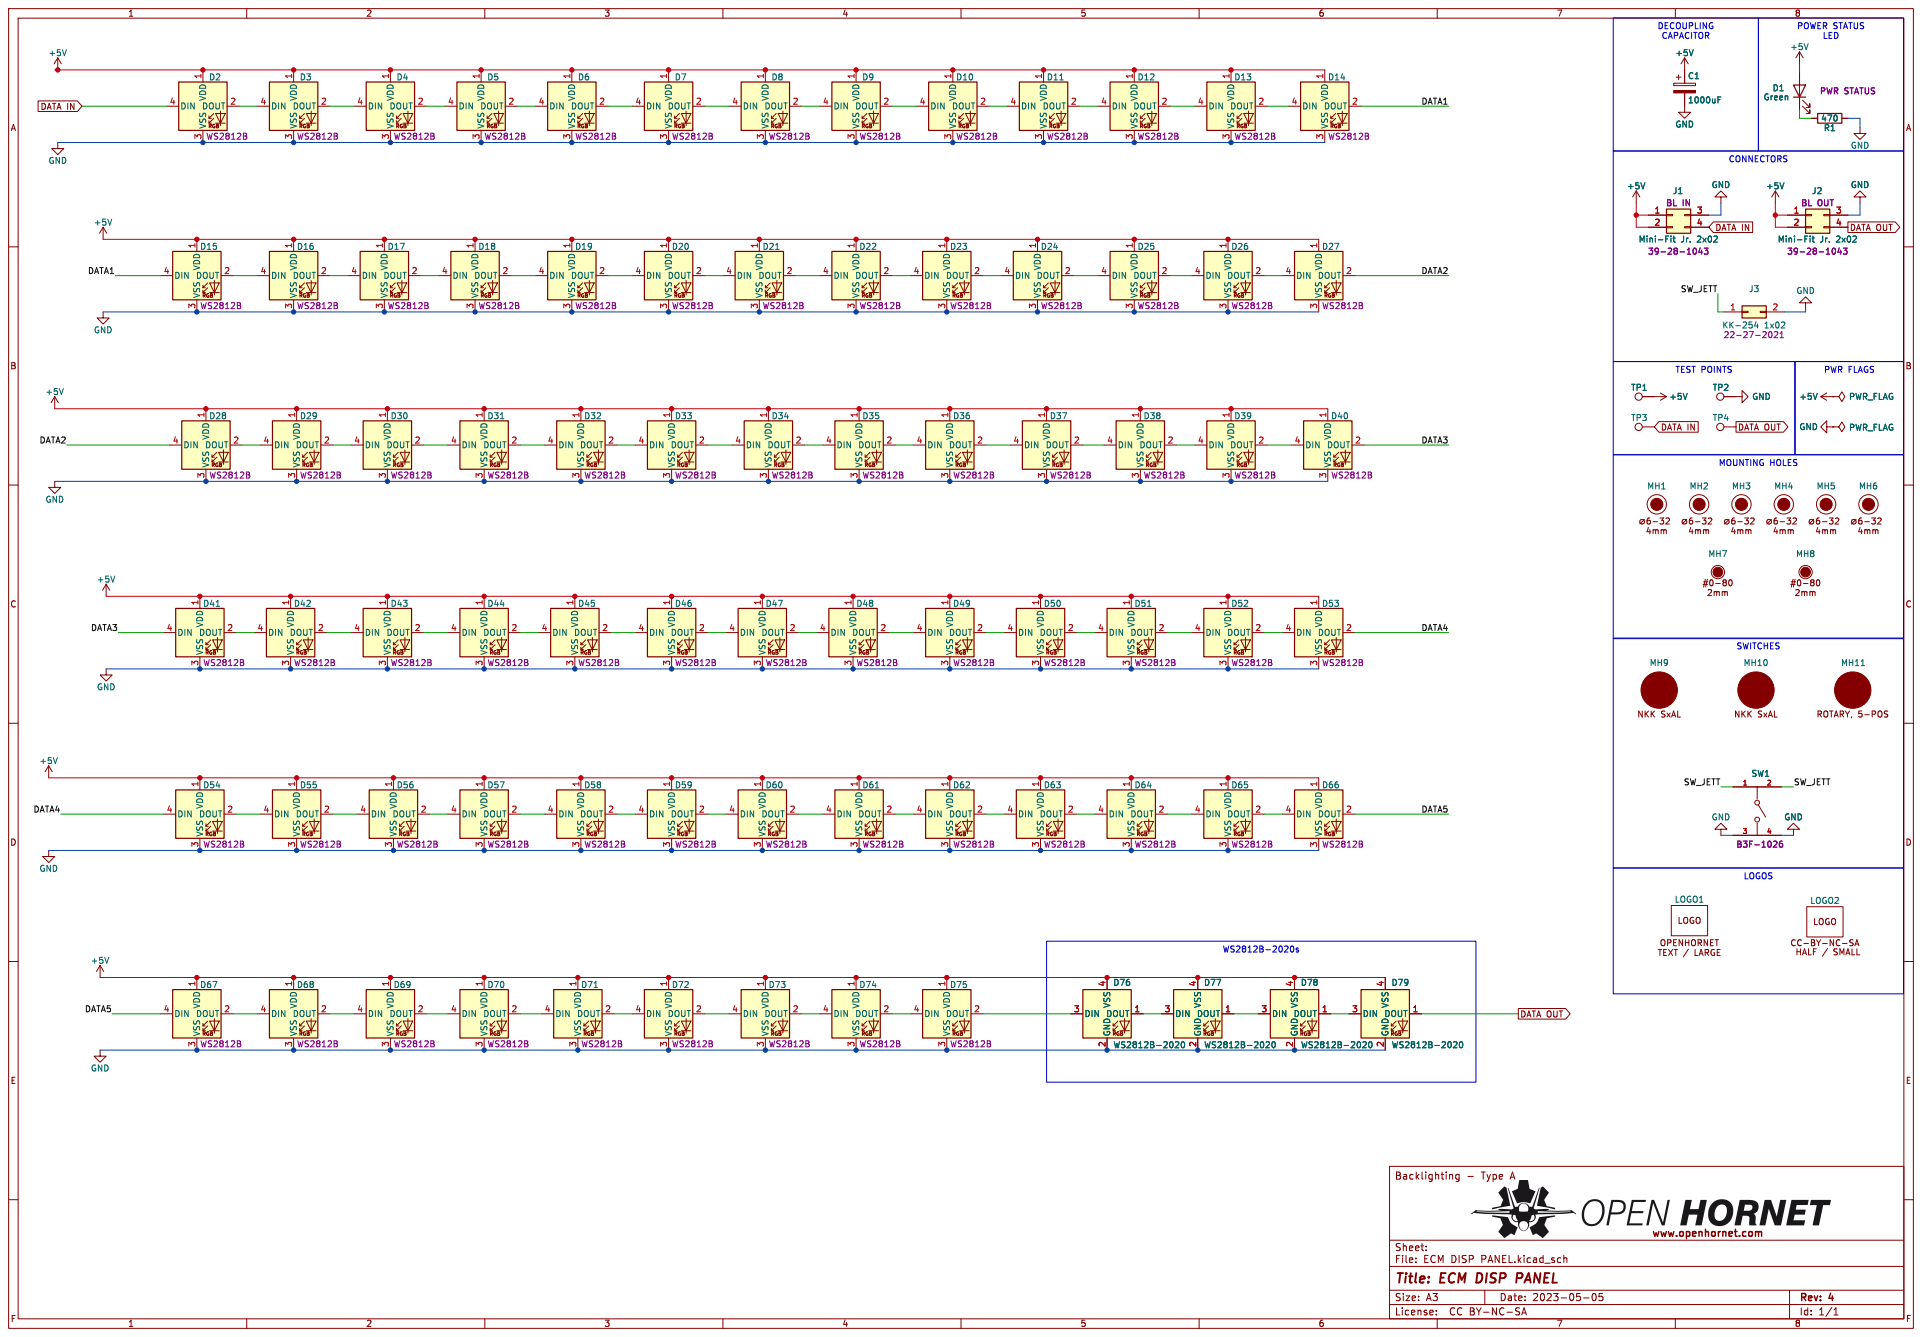
[picture p530: page 1]

3 DIN 4 D22 WS2812B DATA OUT DATA IN DATA OUT DATA IN
RGB VDD

CC-BY-NC-SA HALF / SMALL

2 DIN 3 VSS D76 4 WS2812B-2020 DOUT 1 GND

Id: 1/1 Title: ECM DISP PANEL

Size: A3 | | Rev: 4 | F Date: 2023-05-05
License: CC | BY-NC-SA
