jrsteensen/OpenHornet/release/OHE_Electronics/OH4A2A1-10 - PCB, LANDING GEAR PANEL/LANDING GEAR PANEL.pdf

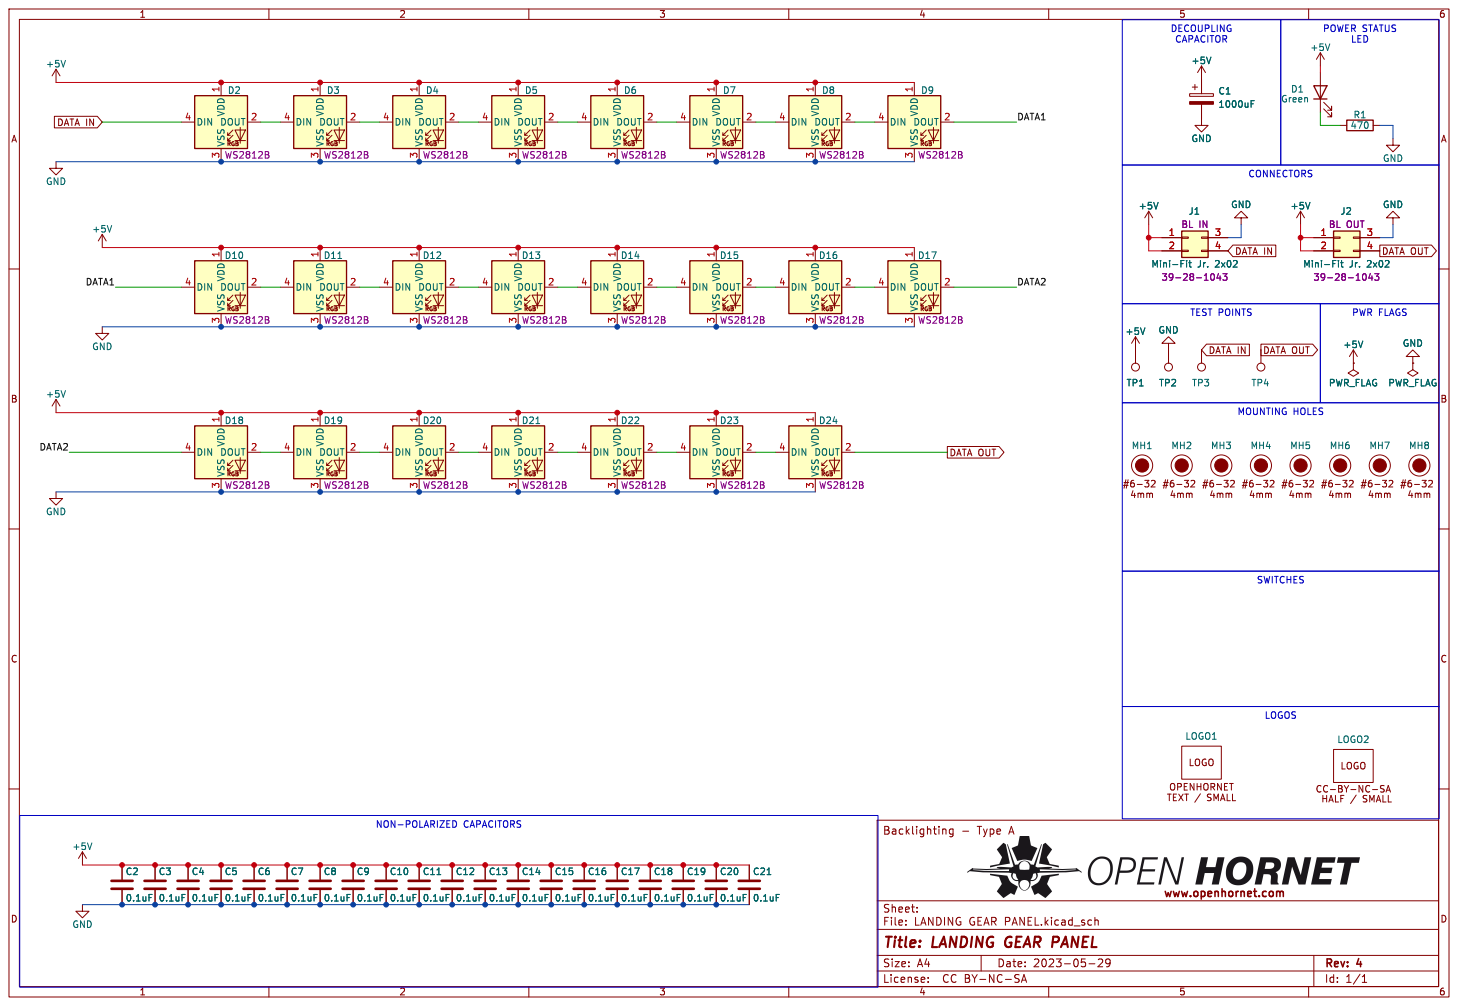
[picture p531: page 1]

CC-BY-NC-SA HALF / SMALL

Id: 1/1 Title: LANDING GEAR PANEL

Size: A4 | | Rev: 4
License: CC | BY-NC-SA
