jrsteensen/OpenHornet/release/OHE_Electronics/OH4A3A1-10 - PCB, SELECT JETT PANEL/SELECT JETT PANEL.pdf

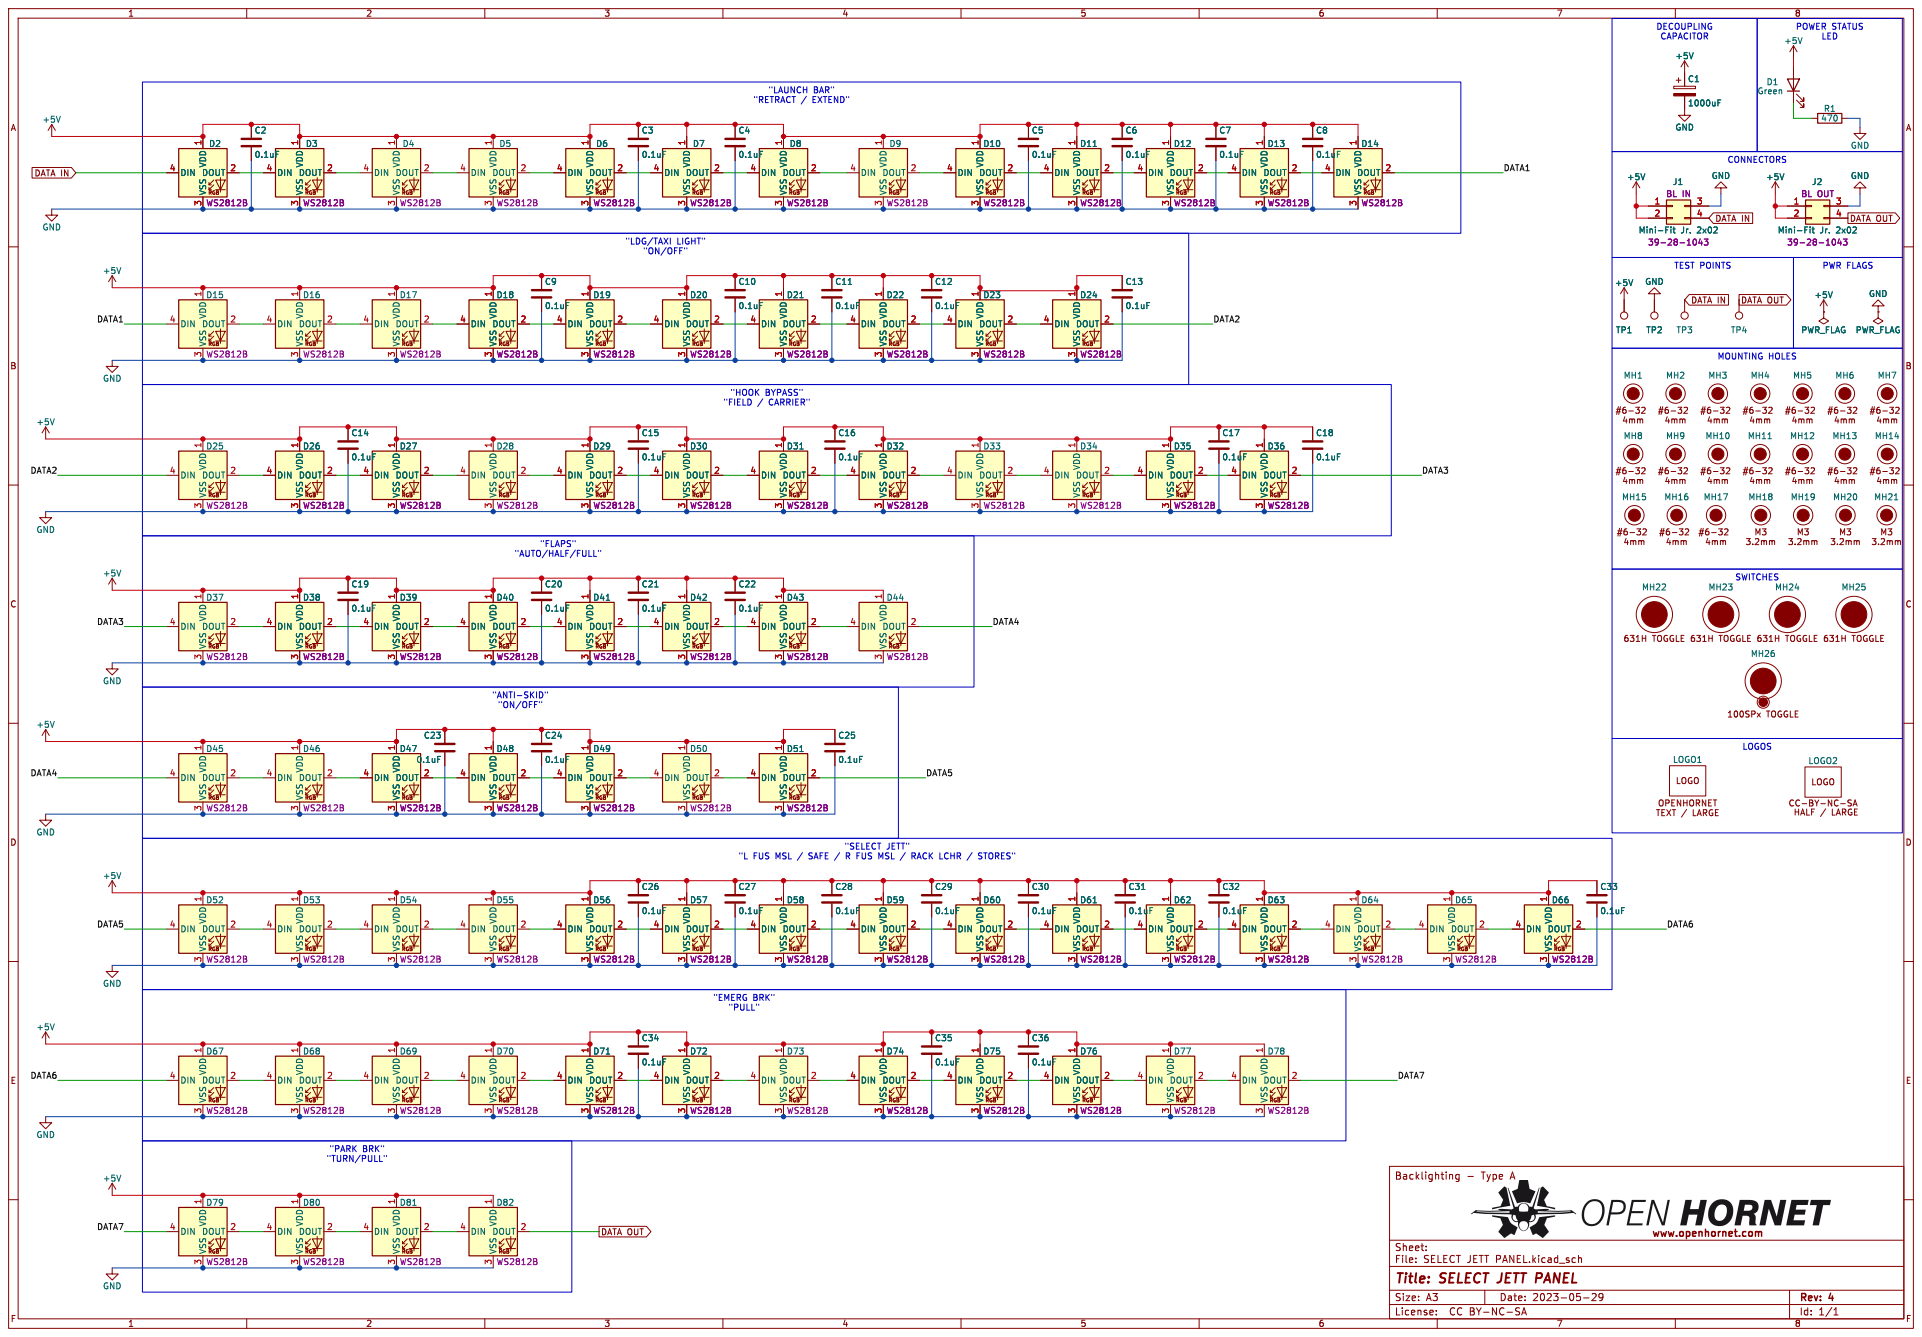
[picture p532: page 1]

PWR FLAGS DECOUPLING
CAPACITOR MOUNTING HOLES CONNECTORS
TP4 GND

"L FUS MSL / SAFE / R FUS MSL / RACK LCHR / STORES"

Id: 1/1 Title: SELECT JETT PANEL

Size: A3 | | Rev: 4 | F Date: 2023-05-29
License: CC | BY-NC-SA
