jrsteensen/OpenHornet/release/OHE_Electronics/OH4A4A1-10 - PCB, FIRE TEST PANEL/FIRE TEST PANEL.pdf

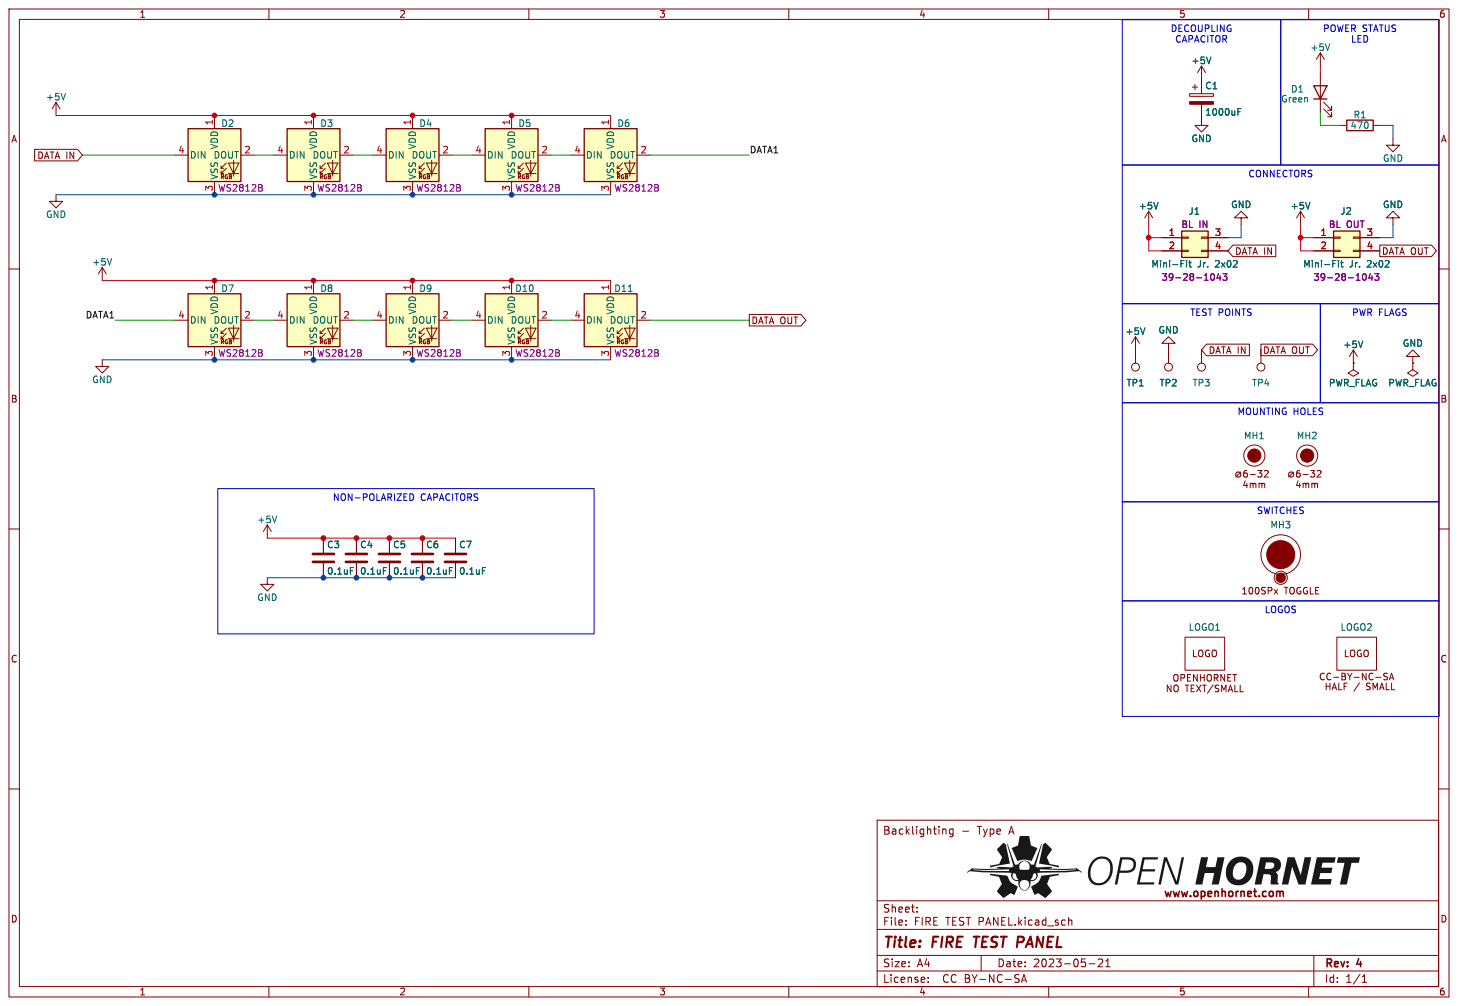
[picture p533: page 1]

3 DIN 4 D9 WS2812B CC-BY-NC-SA HALF / SMALL
RGB VDD

SWITCHES NON-POLARIZED CAPACITORS

Id: 1/1 Title: FIRE TEST PANEL

Size: A4 | | Rev: 4
License: CC | BY-NC-SA
