jrsteensen/OpenHornet/release/OHE_Electronics/OH4A5A1-10 - PCB, FUEL PANEL/FUEL PANEL.pdf

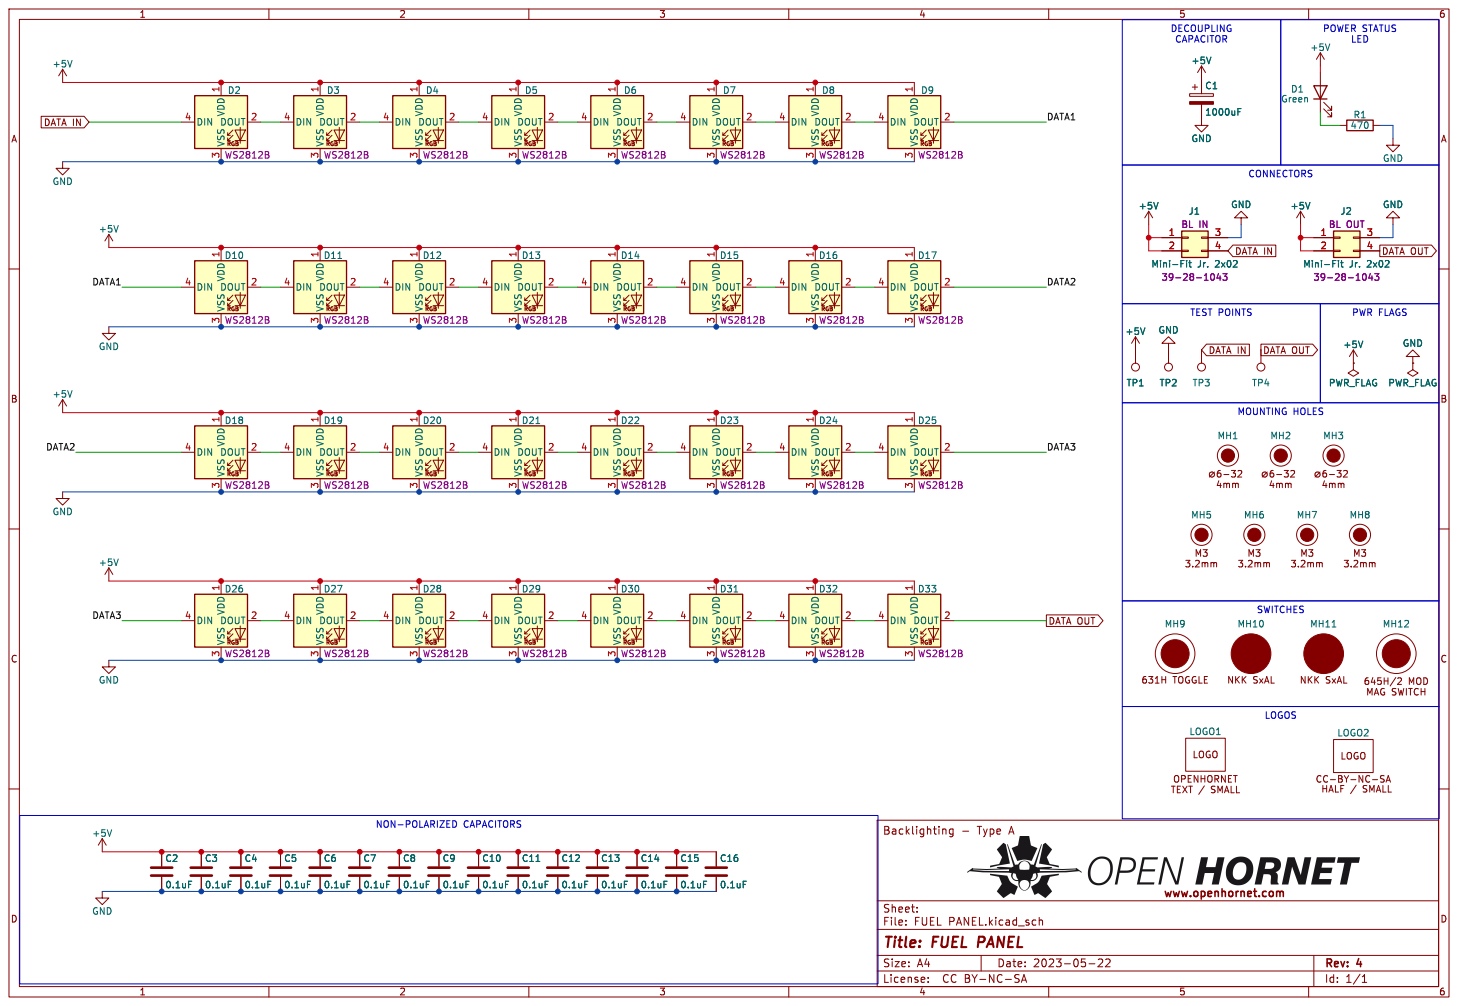
[picture p534: page 1]

3 DIN 4 D13 WS2812B CC-BY-NC-SA HALF / SMALL
RGB VDD

PWR FLAGS MOUNTING HOLES

Id: 1/1 Title: FUEL PANEL

Size: A4 | | Rev: 4
License: CC | BY-NC-SA
