jrsteensen/OpenHornet/release/OHE_Electronics/OH4A5A2-10 - PCB, APU ENG CRANK PANEL/APU ENG CRANK PANEL.pdf

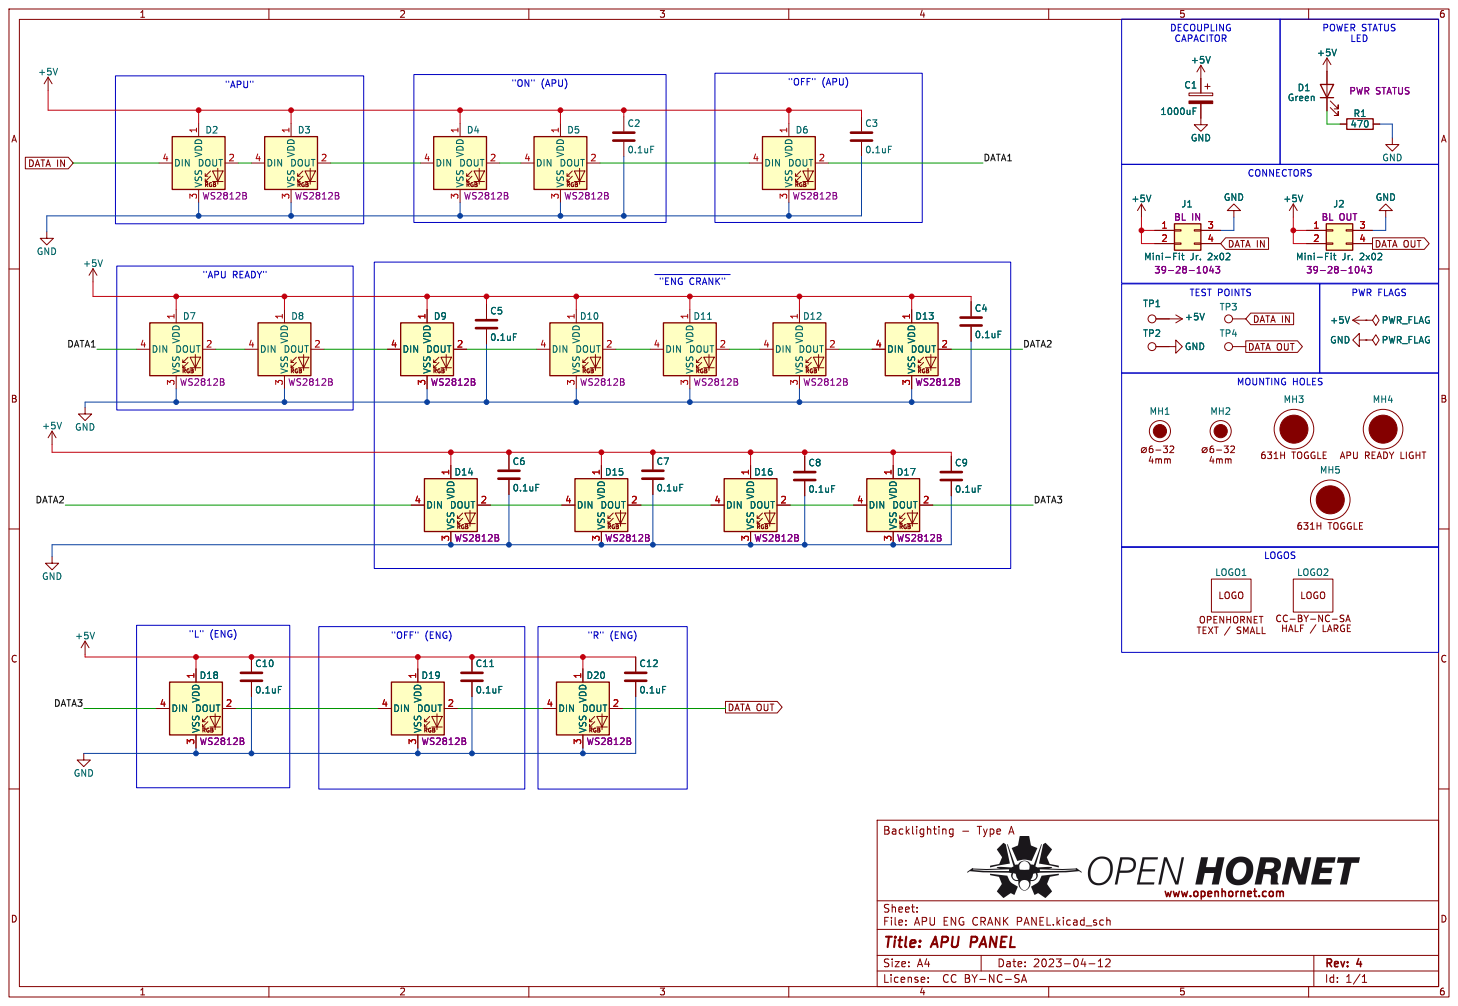
[picture p535: page 1]

DATA OUT DATA OUT DATA IN

TEST POINTS MOUNTING HOLES

631H TOGGLE MH5 CC-BY-NC-SA HALF / LARGE

Id: 1/1 Title: APU PANEL

Size: A4 | | Rev: 4
License: CC | BY-NC-SA
