jrsteensen/OpenHornet/release/OHE_Electronics/OH4A6A1-10 - PCB, FCS PANEL/FCS PANEL.pdf

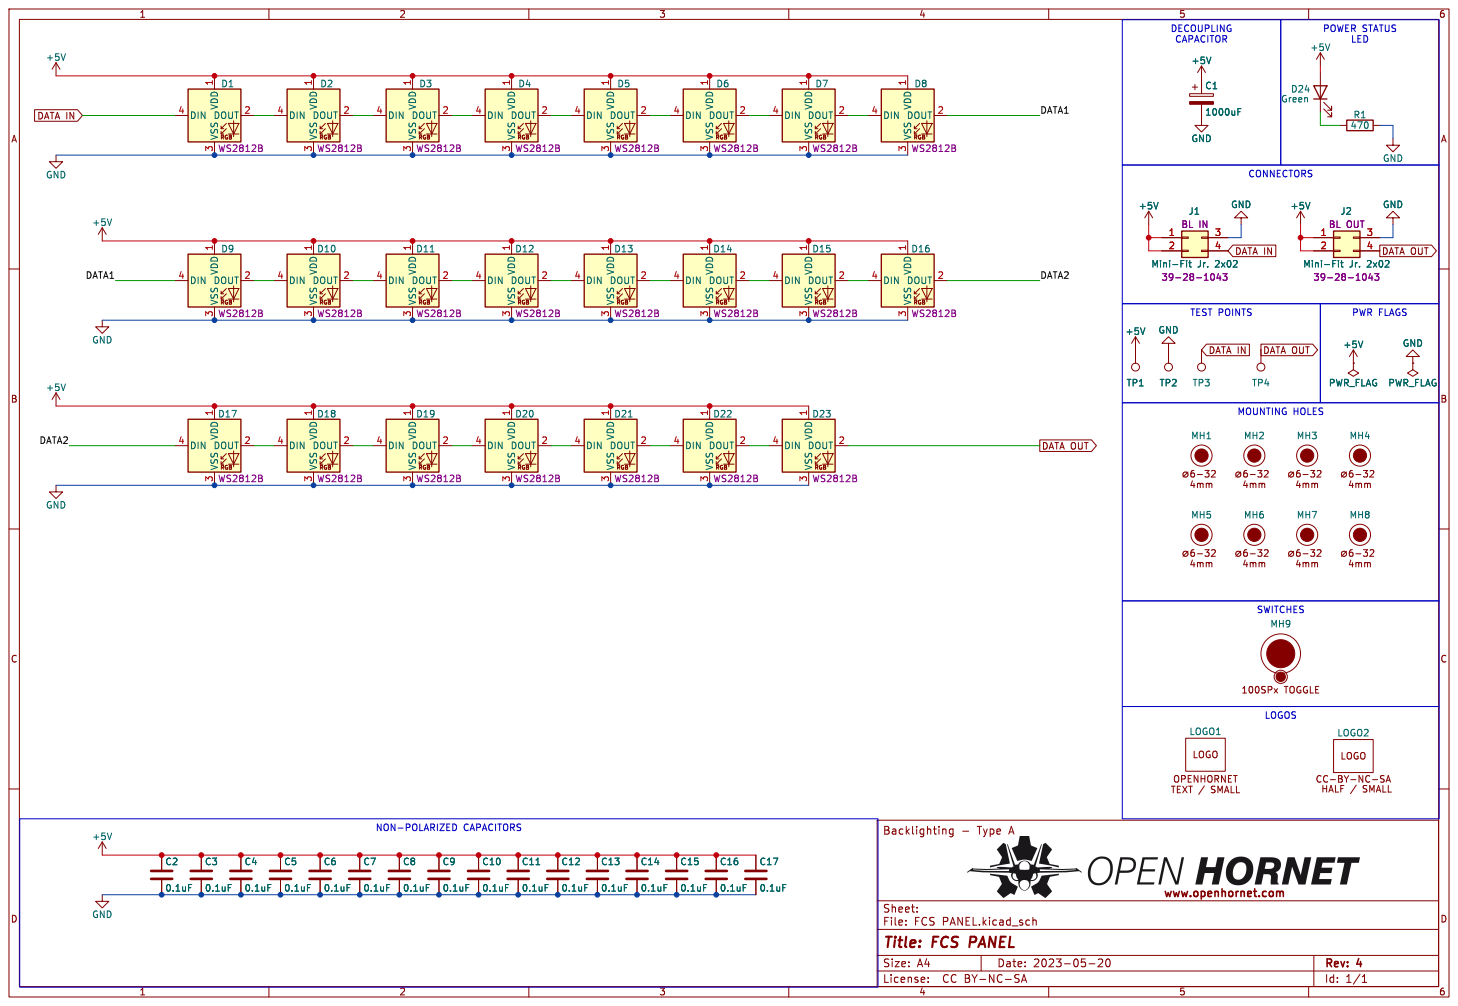
[picture p536: page 1]

POWER STATUS
LED MOUNTING HOLES CONNECTORS

CC-BY-NC-SA HALF / SMALL

Id: 1/1 Title: FCS PANEL

Size: A4 | | Rev: 4
License: CC | BY-NC-SA
