jrsteensen/OpenHornet/release/OHE_Electronics/OH4A7A3-10 - PCB, HYD ISO PANEL/HYD ISO PANEL.pdf

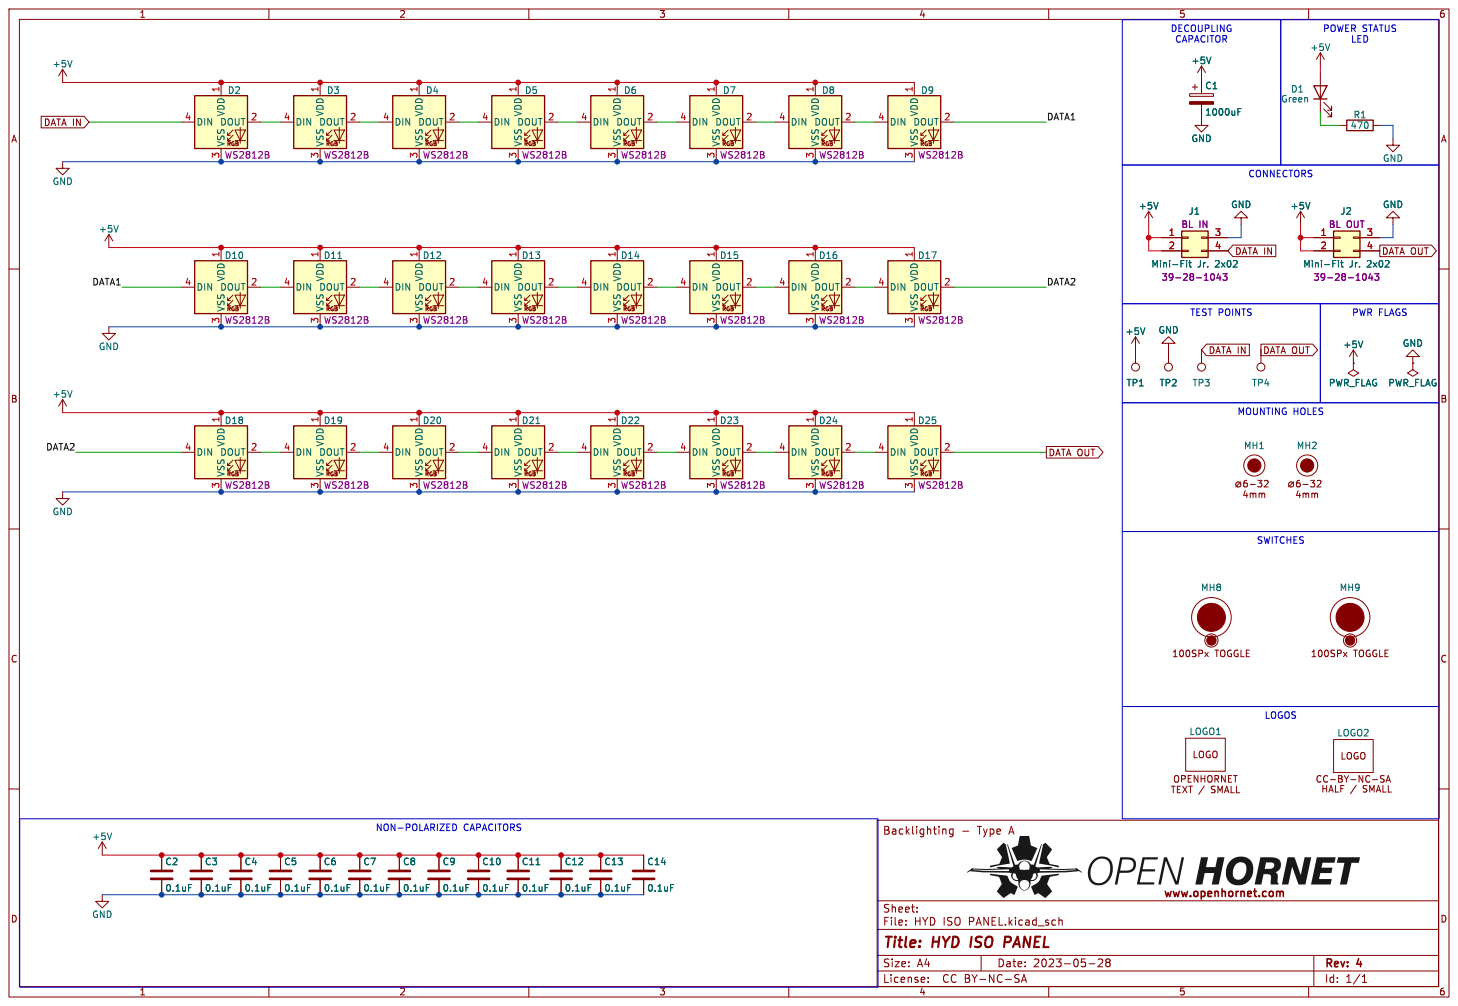
[picture p537: page 1]

TEST POINTS DECOUPLING
CAPACITOR MOUNTING HOLES CONNECTORS

Id: 1/1 Title: HYD ISO PANEL

Size: A4 | | Rev: 4
License: CC | BY-NC-SA
