jrsteensen/OpenHornet/release/OHE_Electronics/OH4A8A1-XX - PCB, LEFT CIRCUIT BREAKER/LEFT CIRCUIT BREAKER.pdf

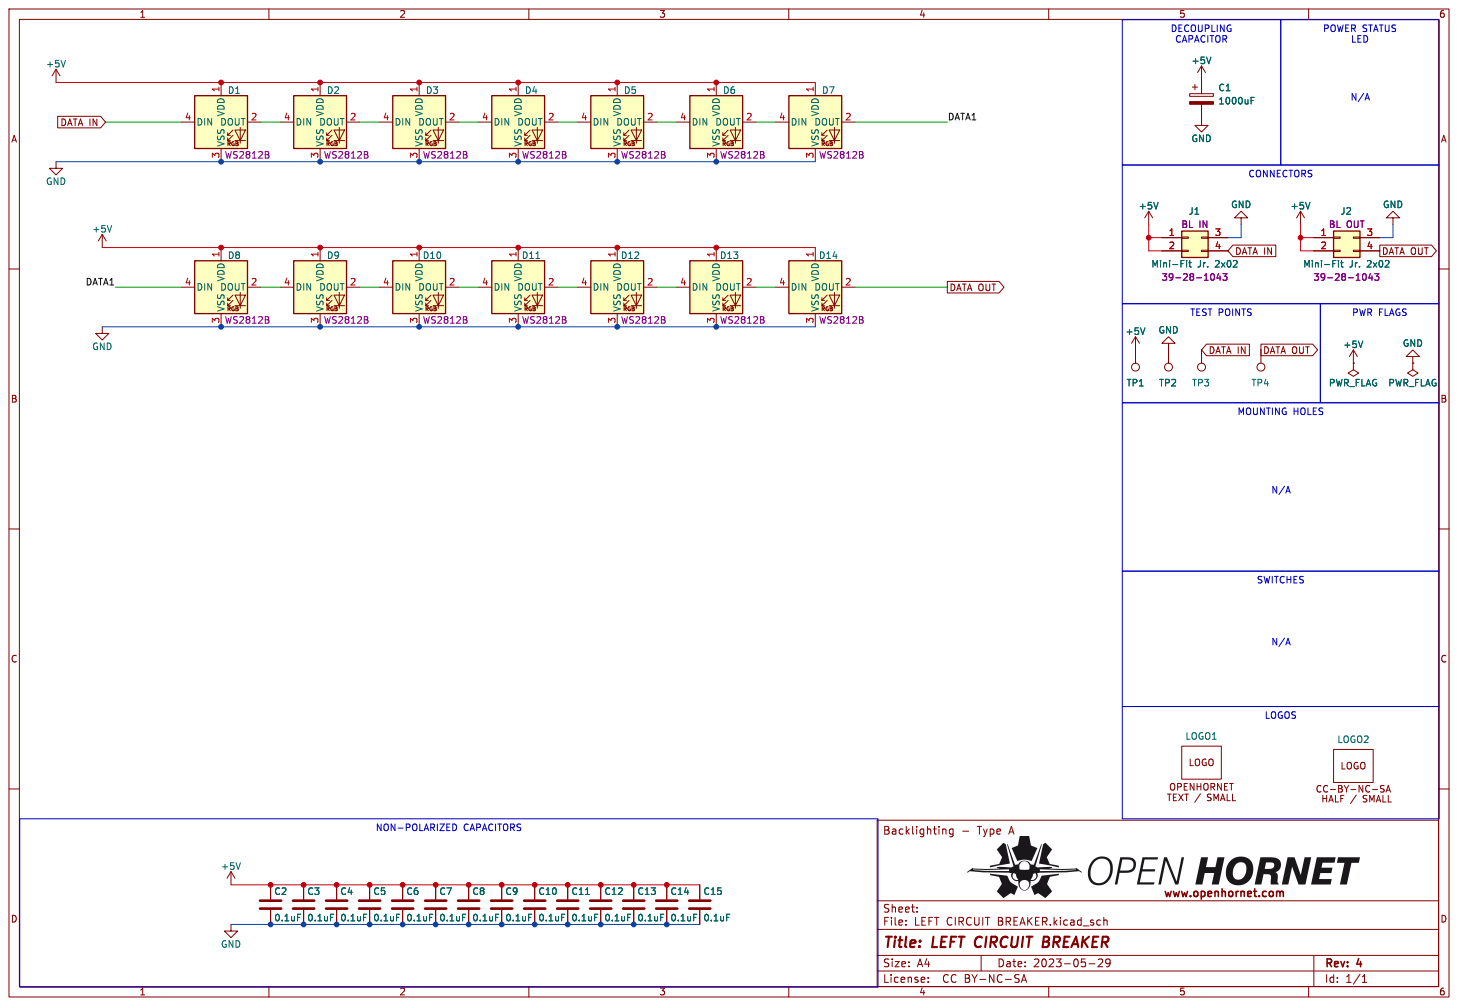
[picture p538: page 1]

DATA OUT DATA IN

TEST POINTSCONNECTORS NON-POLARIZED CAPACITORS

Id: 1/1 Title: LEFT CIRCUIT BREAKER

Size: A4 | | Rev: 4
License: CC | BY-NC-SA
