jrsteensen/OpenHornet/release/OHE_Electronics/OH4A9-125 - THROTTLE_INNER_GRIP_CONTROLLER_PCB/HOTAS_Throttle Inner Grip.pdf

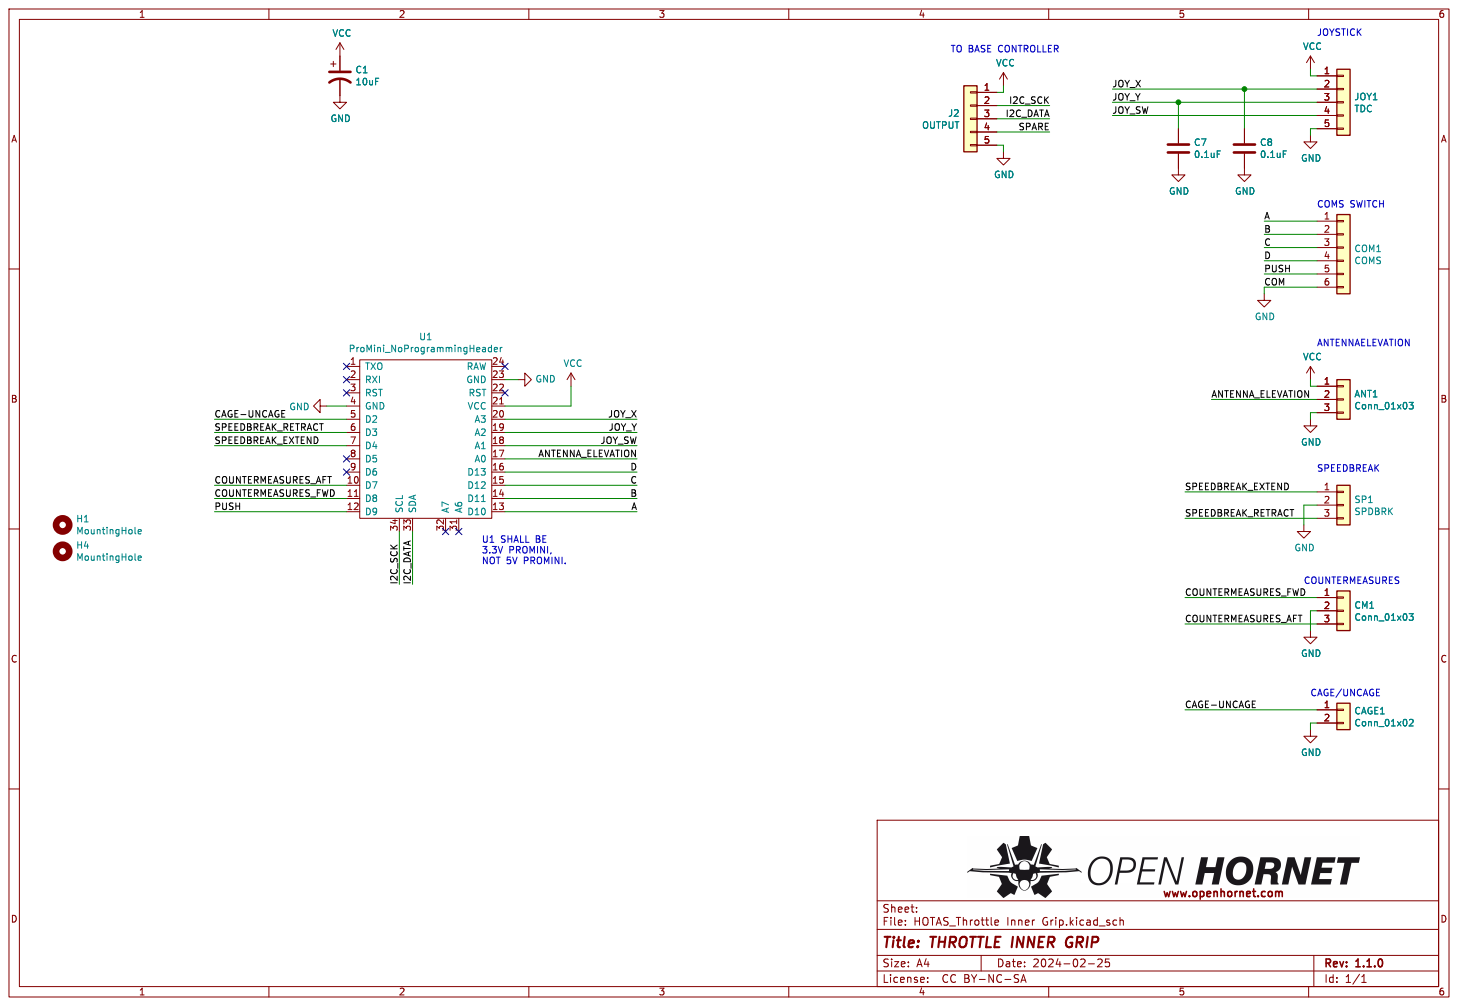
[picture p539: page 1]

Id: 1/1 Title: THROTTLE INNER GRIP

Size: A4 | | Rev: | 1.1.0
License: CC | BY-NC-SA
