jrsteensen/OpenHornet/release/OHE_Electronics/OH5A2A7-12 - PCB, LDG WING FOLD PLACARD/LDG WING FOLD PLACARD.pdf

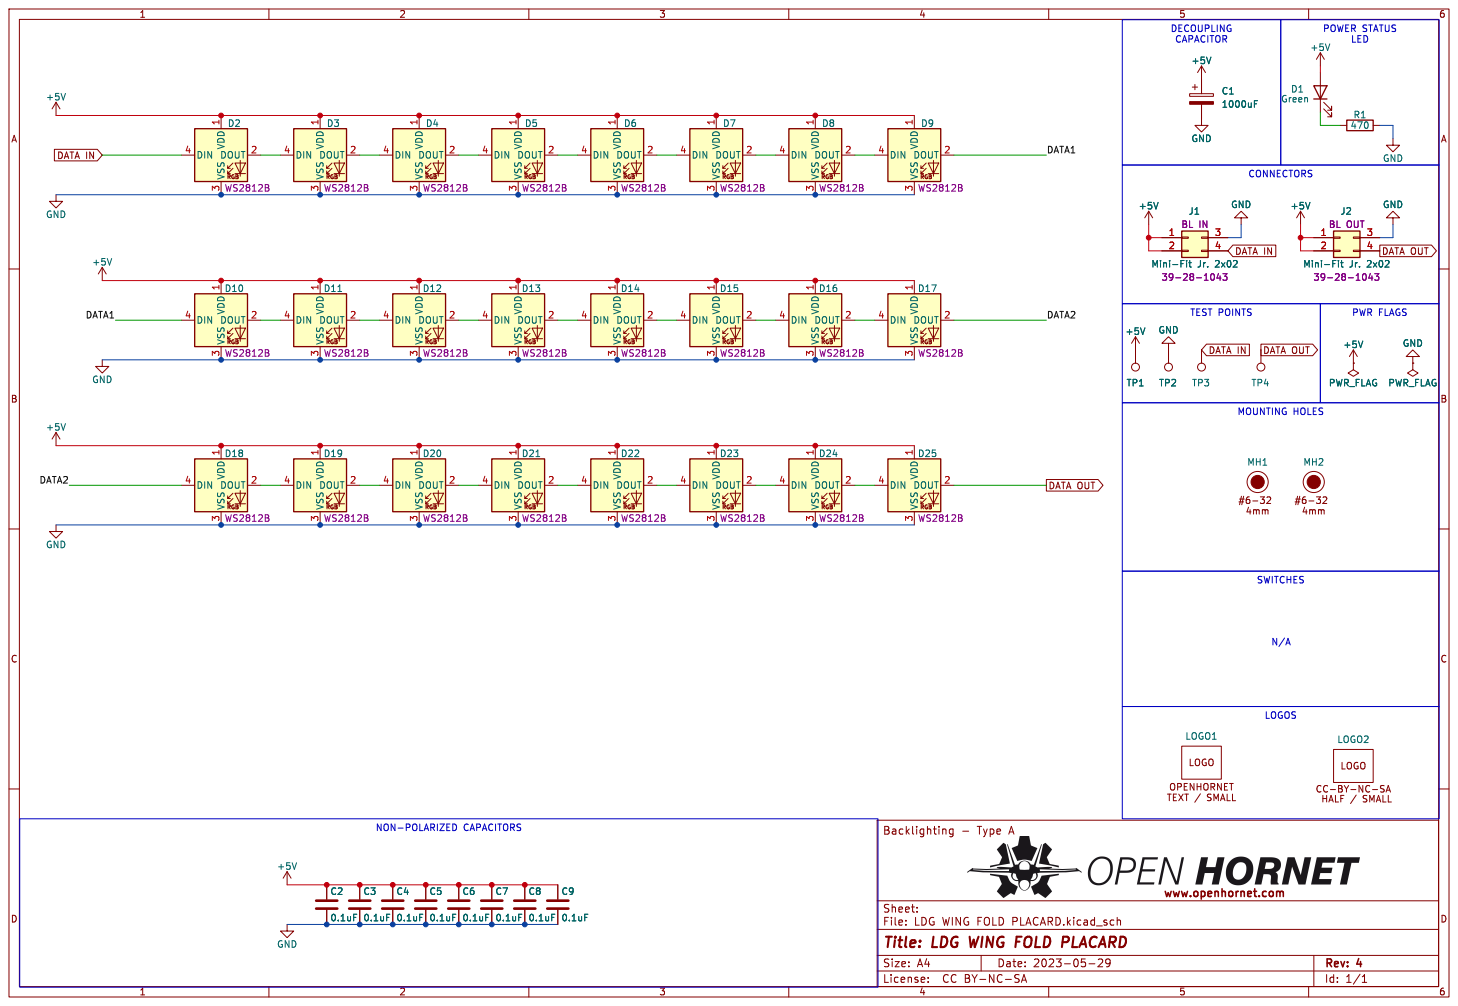
[picture p540: page 1]

LOGO1 DATA OUT DATA IN

Id: 1/1 Title: LDG WING FOLD PLACARD

Size: A4 | | Rev: 4
License: CC | BY-NC-SA
