jrsteensen/OpenHornet/release/OHE_Electronics/OH5A3A1-11 - PCB, CAUTION LIGHT PANEL/CAUTION LIGHTS PANEL.pdf

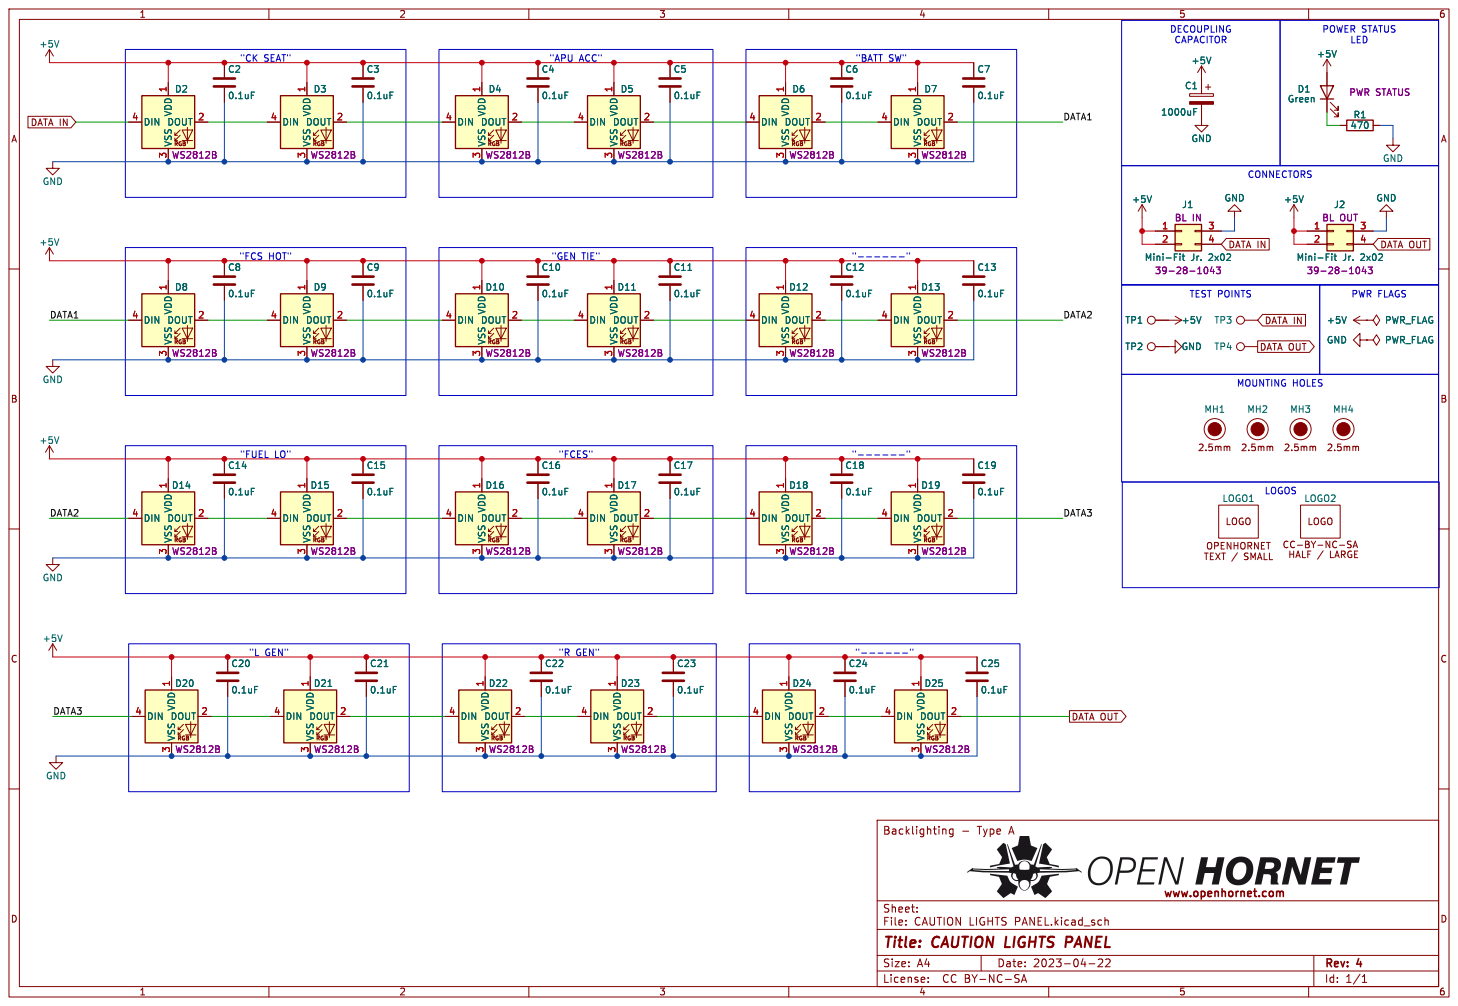
[picture p541: page 1]

TEST POINTS MOUNTING HOLES

3 DIN 4 D24 WS2812B CC-BY-NC-SA HALF / LARGE

Id: 1/1 Title: CAUTION LIGHTS PANEL

Size: A4 | | Rev: 4
License: CC | BY-NC-SA
