jrsteensen/OpenHornet/release/OHE_Electronics/OH5A5A1-13 - PCB, ECS PANEL/ECS PANEL.pdf

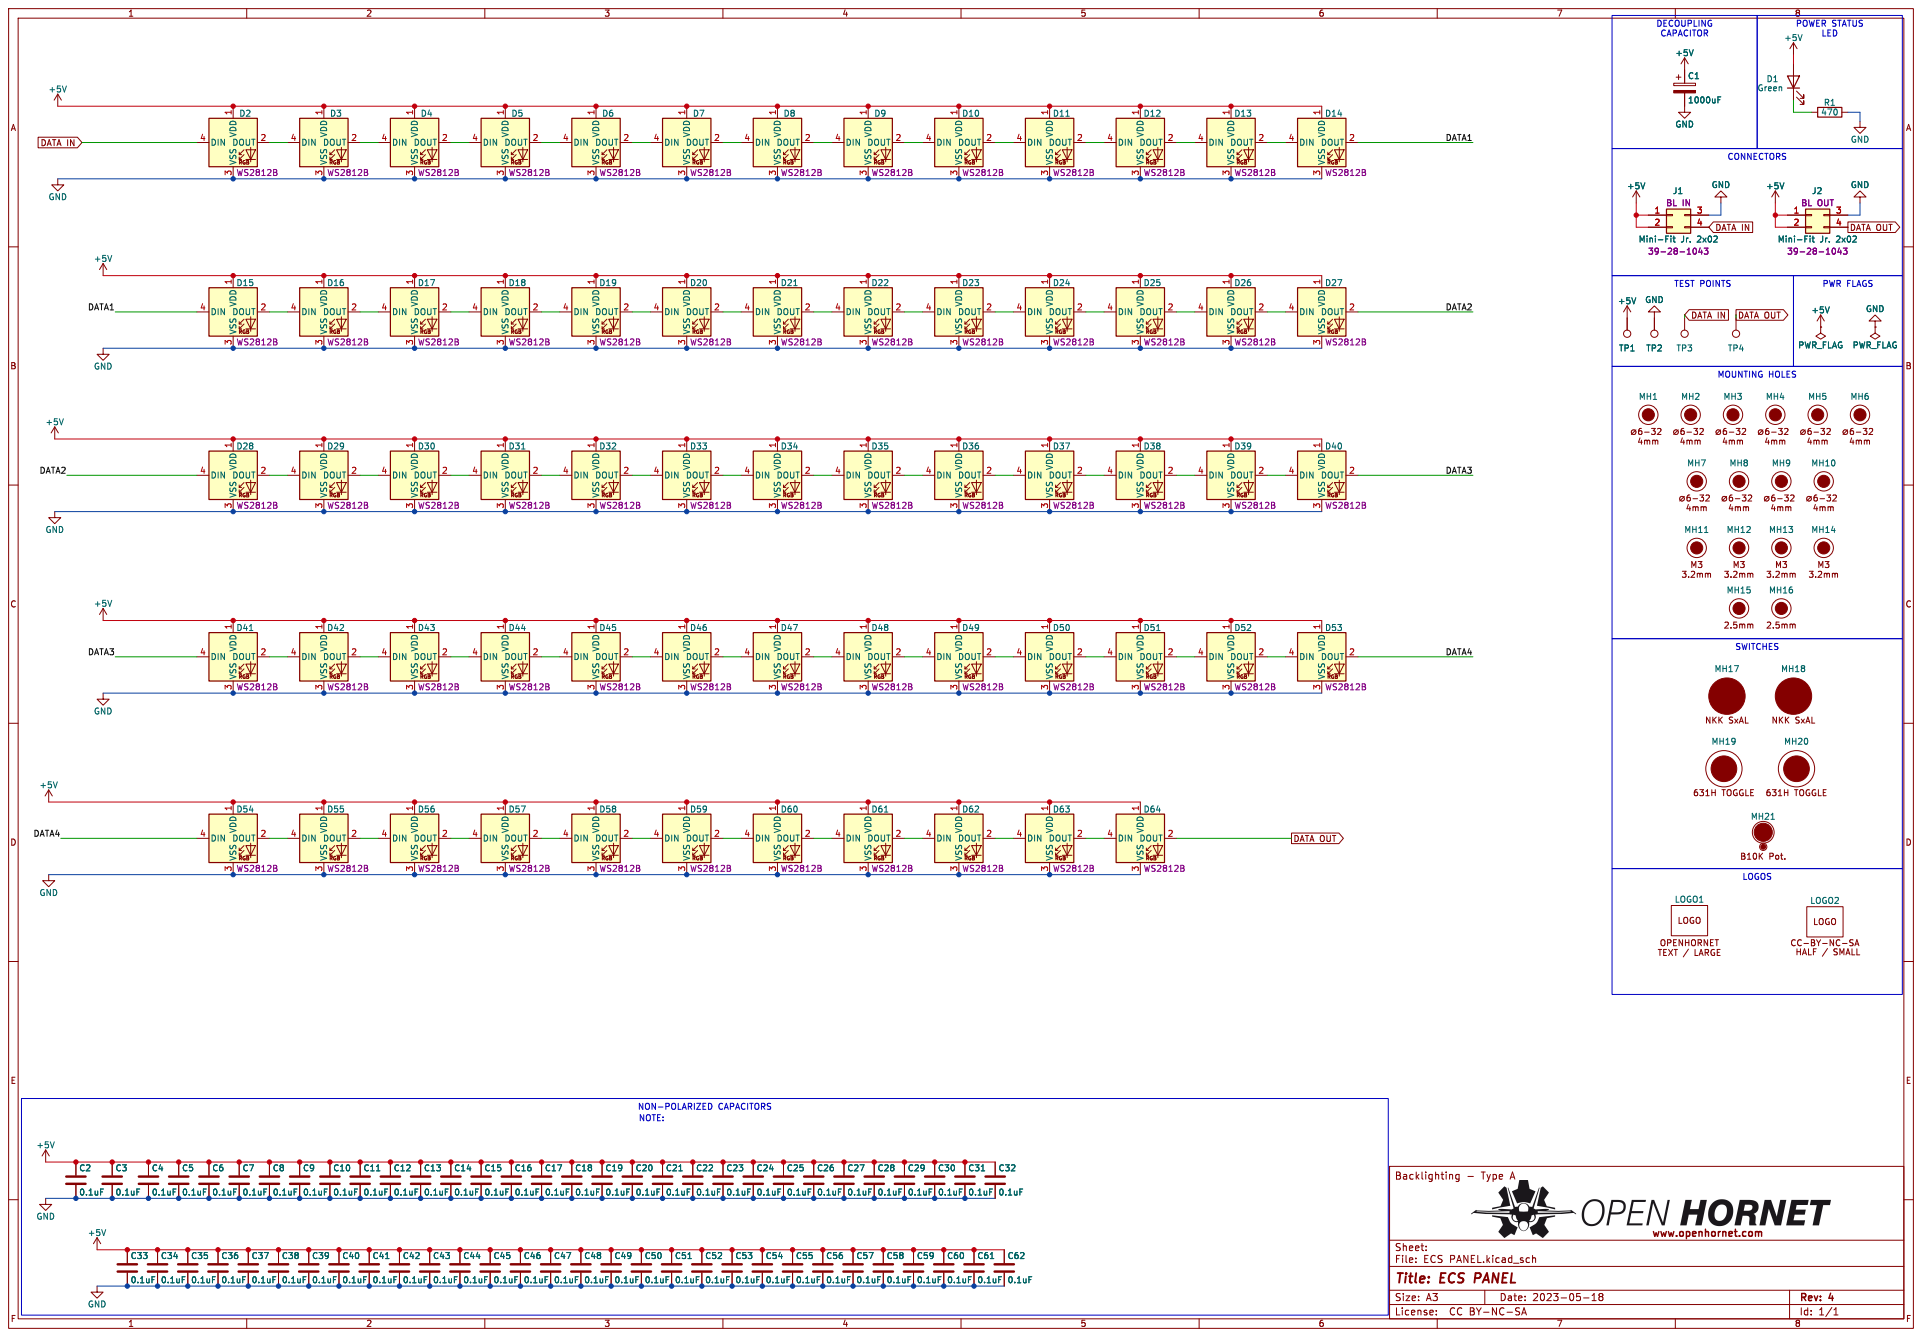
[picture p542: page 1]

DATA OUT

LOGOS NON-POLARIZED CAPACITORS C3

Id: 1/1 Title: ECS PANEL

Size: A3 | | Rev: 4 | F Date: 2023-05-18
License: CC | BY-NC-SA
