jrsteensen/OpenHornet/release/OHE_Electronics/OH5A7A1-13 - PCB, SNSR PANEL/SNSR PANEL.pdf

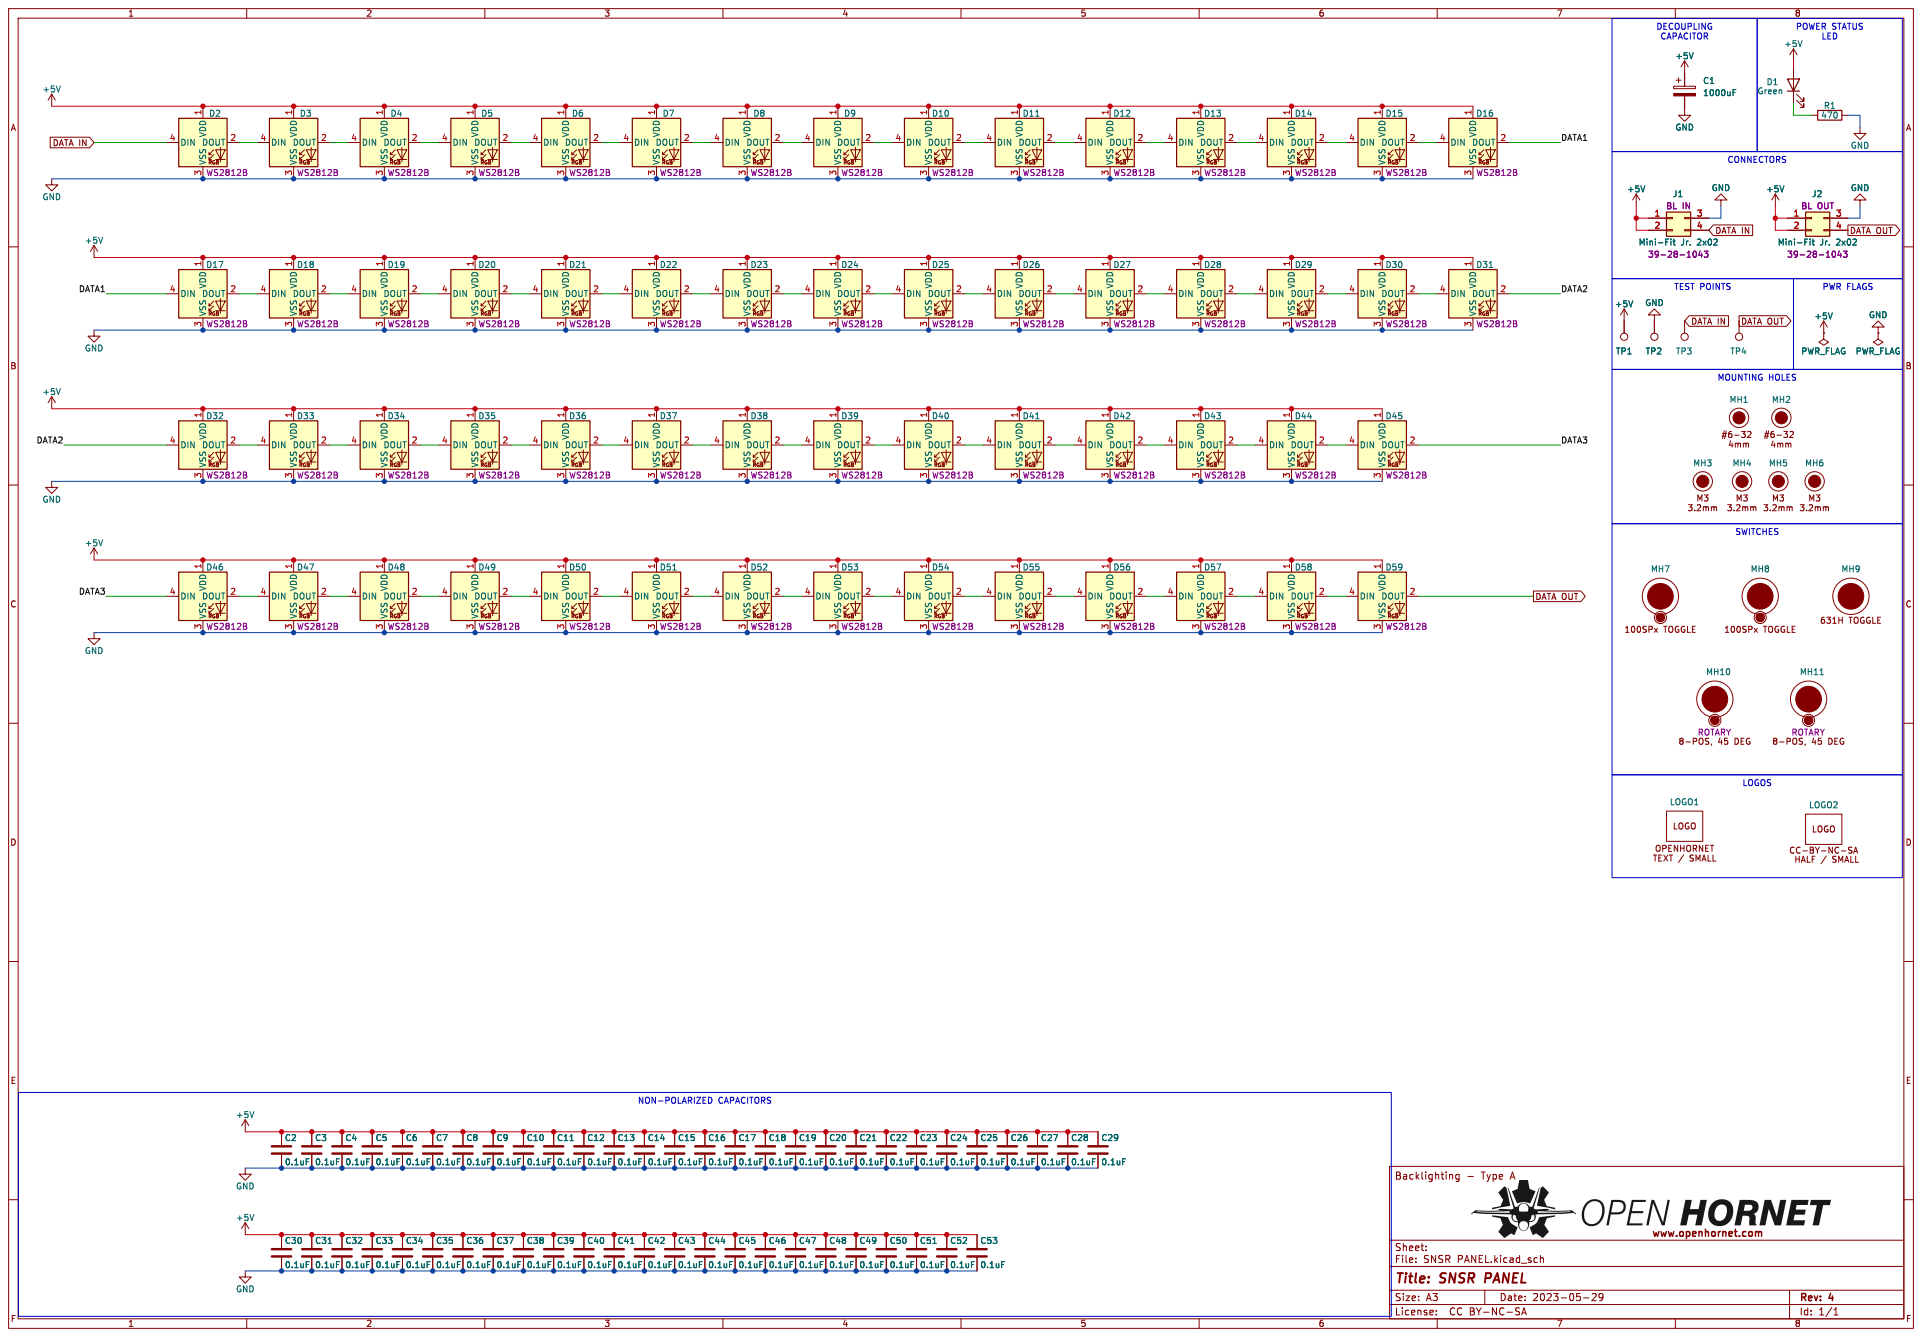
[picture p543: page 1]

PWR FLAGS MOUNTING HOLES DECOUPLING
CAPACITOR

Id: 1/1 Title: SNSR PANEL

Size: A3 | | Rev: 4 | F Date: 2023-05-29
License: CC | BY-NC-SA
