jrsteensen/OpenHornet/release/OH3_Center_Tub/OH3A2 - ASSY, EJECTION SEAT, SJU-17/Manufacturing/OH3A2A-9001 - DECAL, BAROSTATIC RELEASE UNIT.PDF

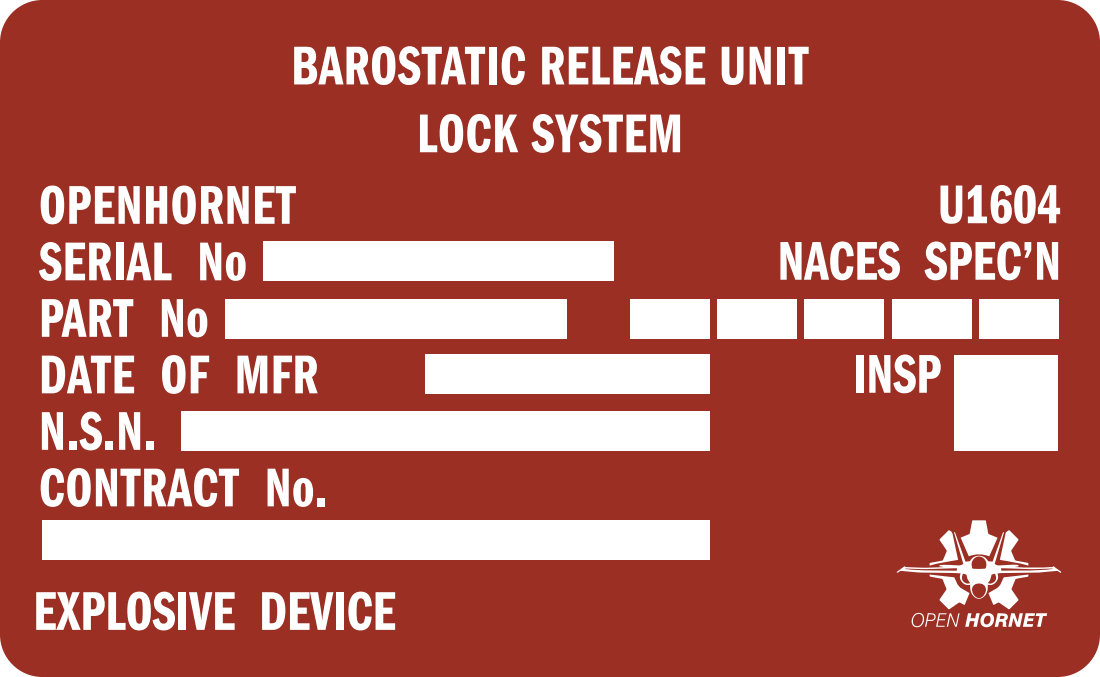
[picture p544: page 1]
U1604 NACES SPEC’N; INSP; EXPLOSIVE DEVICE

BAROSTATIC RELEASE UNIT
LOCK SYSTEM

OPENHORNET
SERIAL No
PART No
DATE OF MFR
CONTRACT No.
