jrsteensen/OpenHornet/release/OH3_Center_Tub/OH3A2 - ASSY, EJECTION SEAT, SJU-17/Manufacturing/OH3A2A-9002 - DECAL, BRIDLE AND BOX.PDF

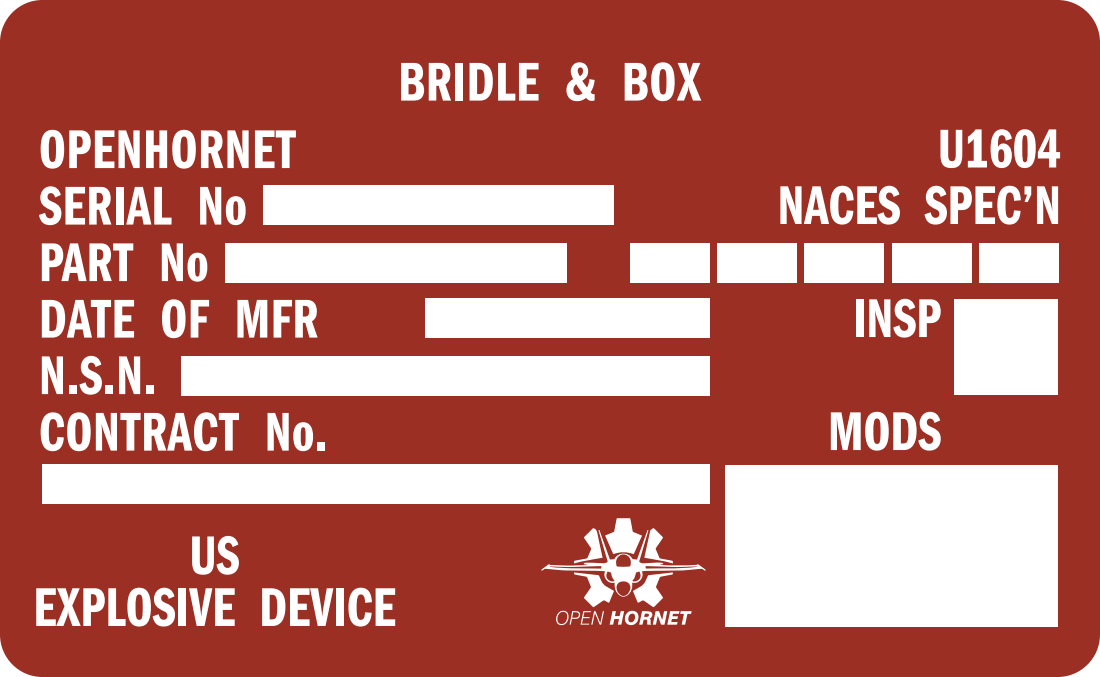
[picture p545: page 1]
BRIDLE & BOX; U1604 NACES SPEC’N; INSP; MODS; US EXPLOSIVE DEVICE

OPENHORNET
SERIAL No
PART No
DATE OF MFR
CONTRACT No.
