jrsteensen/OpenHornet/release/OH3_Center_Tub/OH3A2 - ASSY, EJECTION SEAT, SJU-17/Manufacturing/OH3A2A-9003 - DECAL, BUCKET-SEAT ASSY.PDF

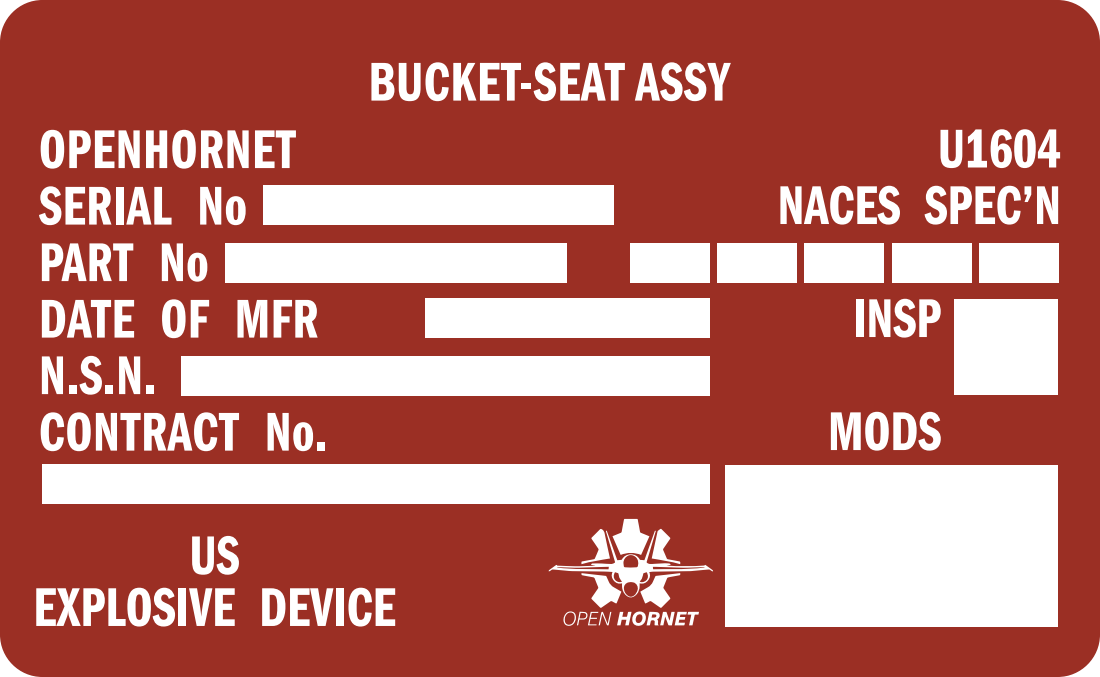
[picture p546: page 1]
U1604 NACES SPEC’N; INSP; MODS; US EXPLOSIVE DEVICE

BUCKET-SEAT ASSY

OPENHORNET
SERIAL No
PART No
DATE OF MFR
CONTRACT No.
