jrsteensen/OpenHornet/release/OHE_Electronics/ABSIS010 - DUAL NEEDLE GAUGE/Dual Needle Gauge.pdf

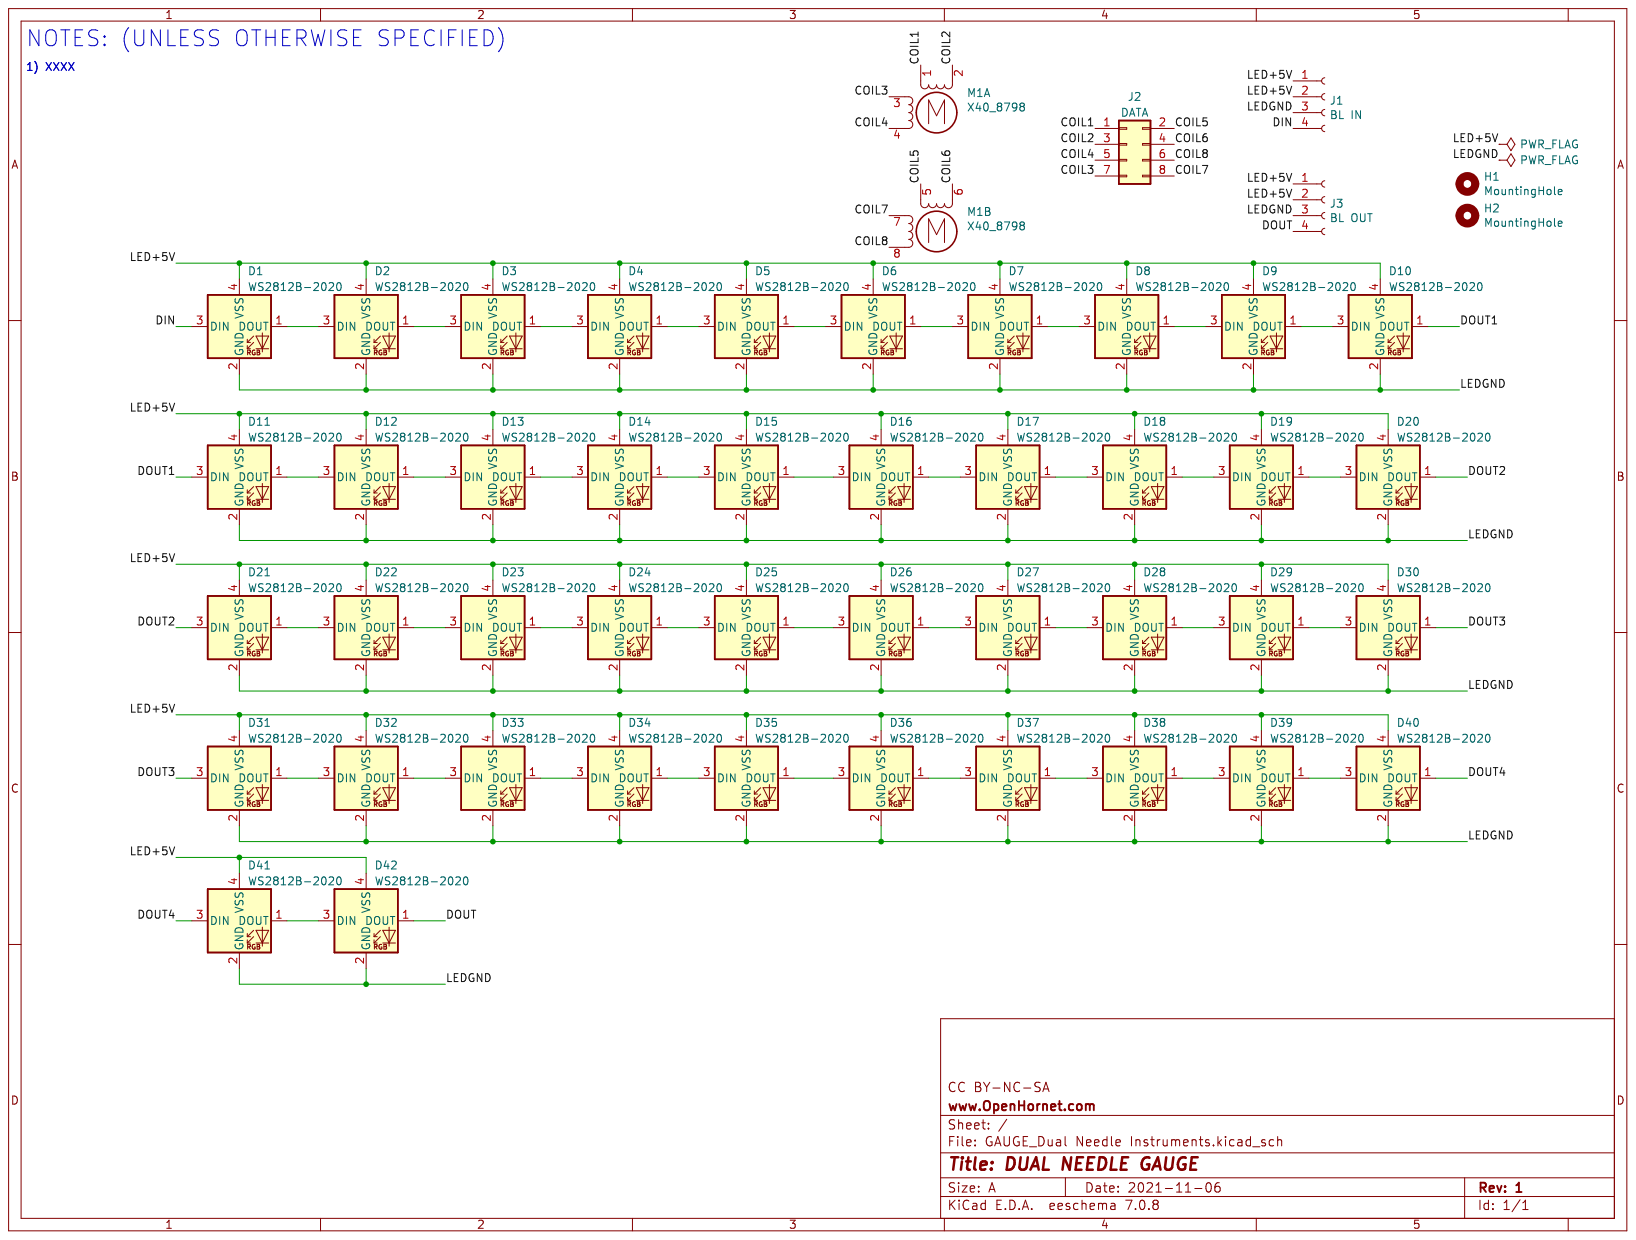
[picture p548: page 1]
