jrsteensen/OpenHornet/release/OHE_Electronics/OH1A3-13 - PCB, DDI/DDI.pdf

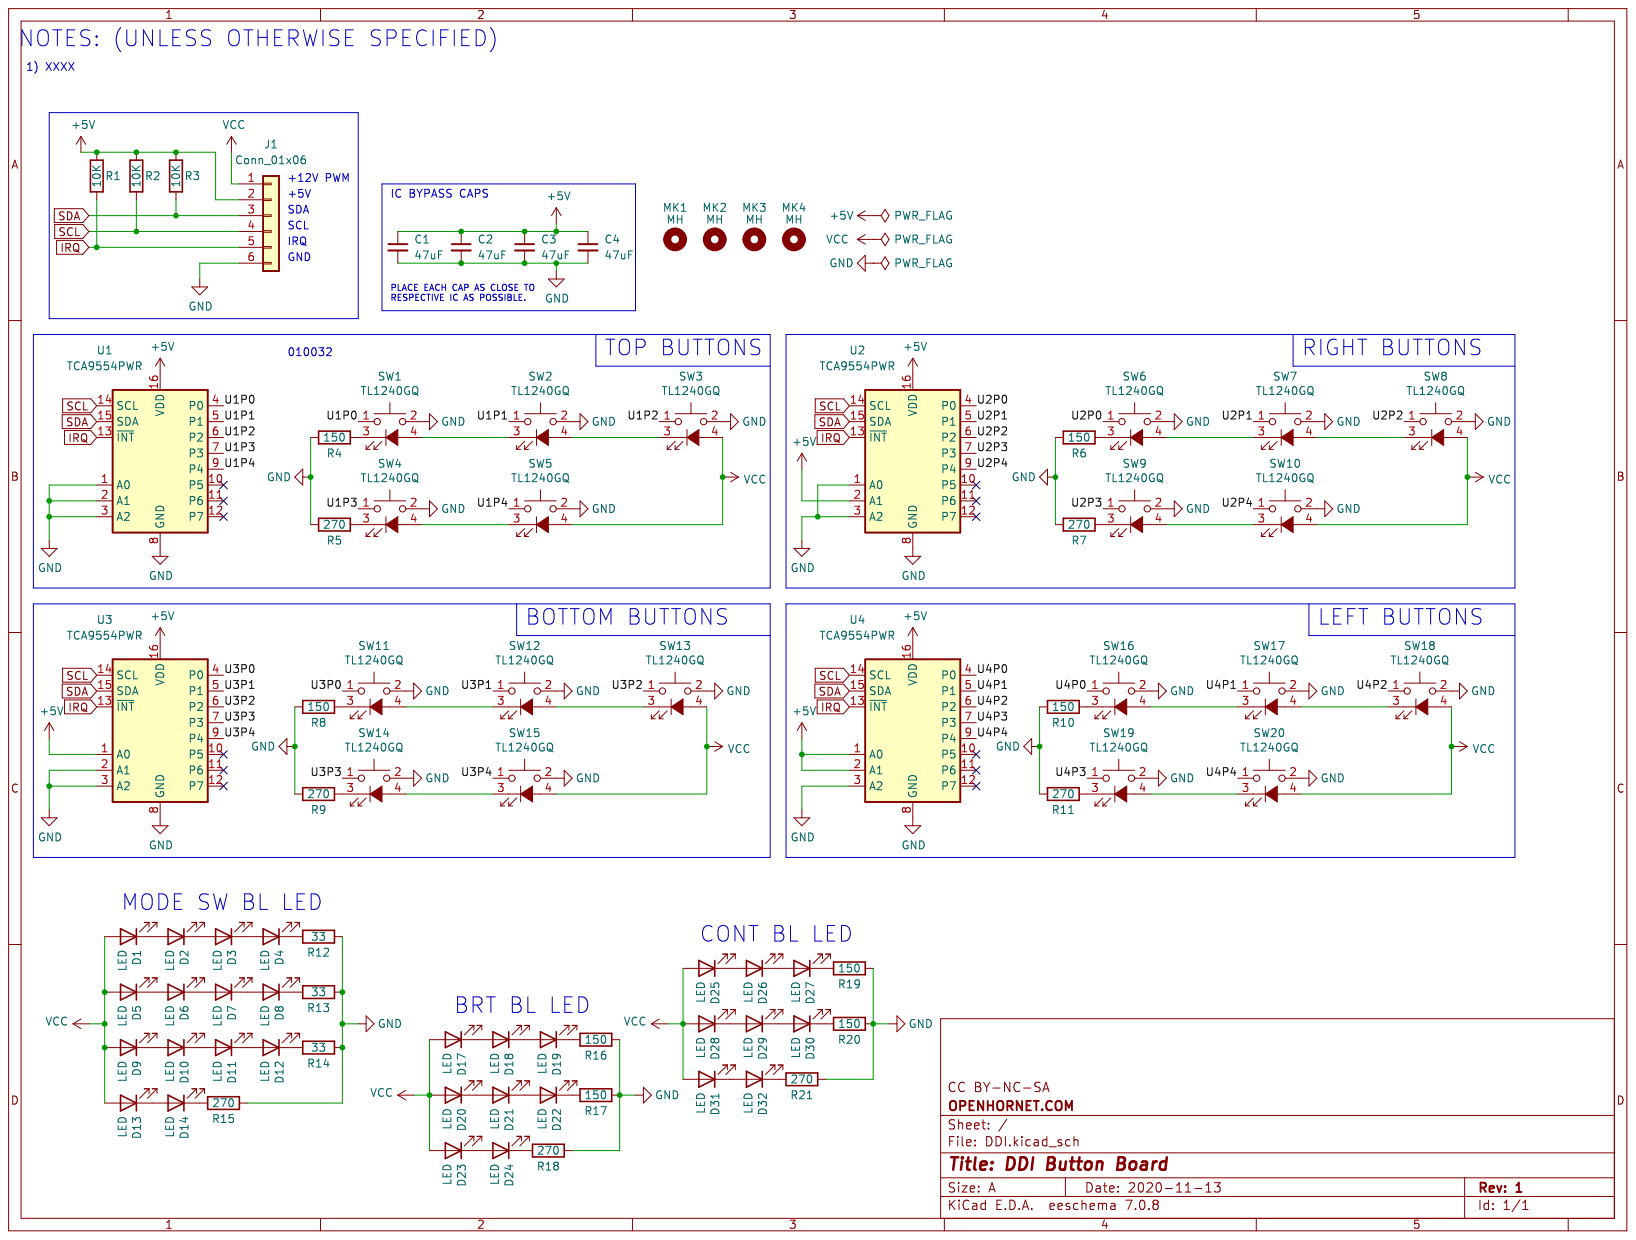
[picture p549: page 1]
