jrsteensen/OpenHornet/release/OHE_Electronics/OH1A5-15 - PCB, EWI_RIGHT/EWI_RIGHT.pdf

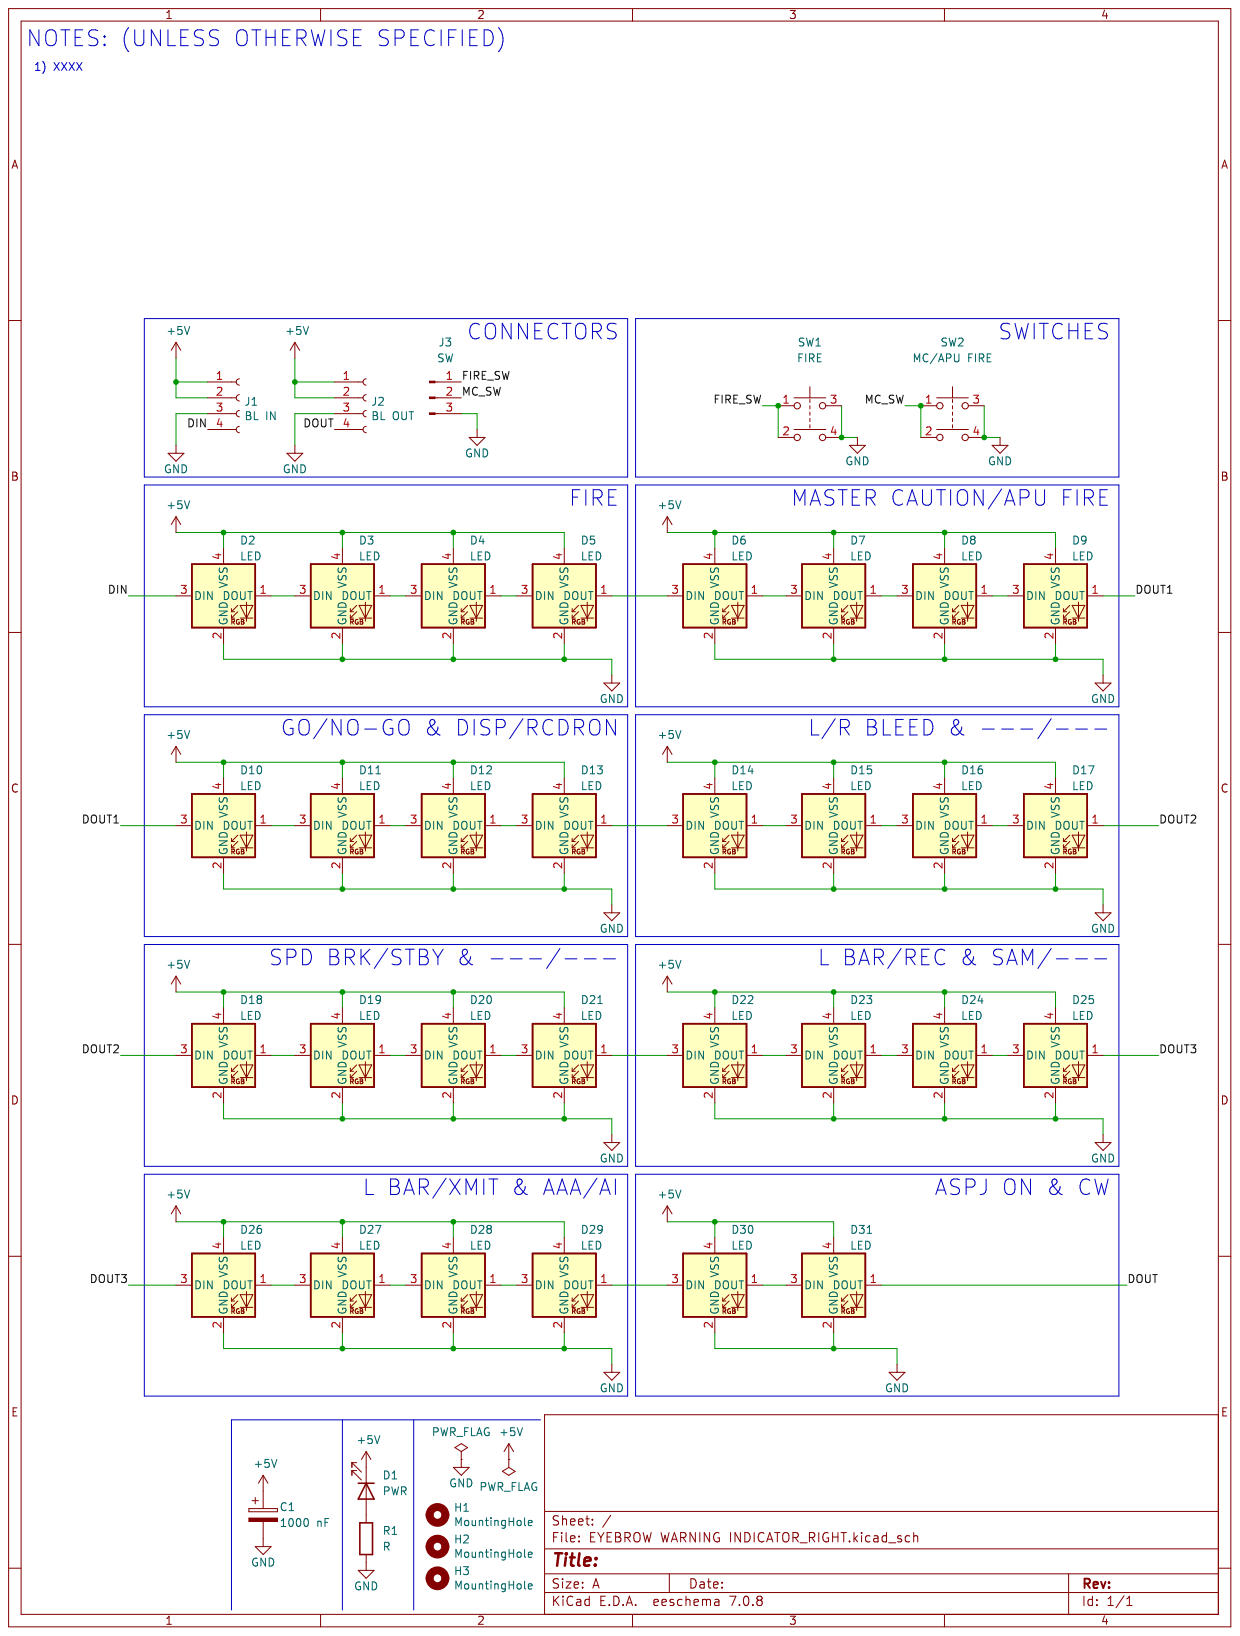
[picture p550: page 1]
