jrsteensen/OpenHornet/release/OHE_Electronics/OH1A7-101 - PCB, HUD PANEL/HUD PANEL.pdf

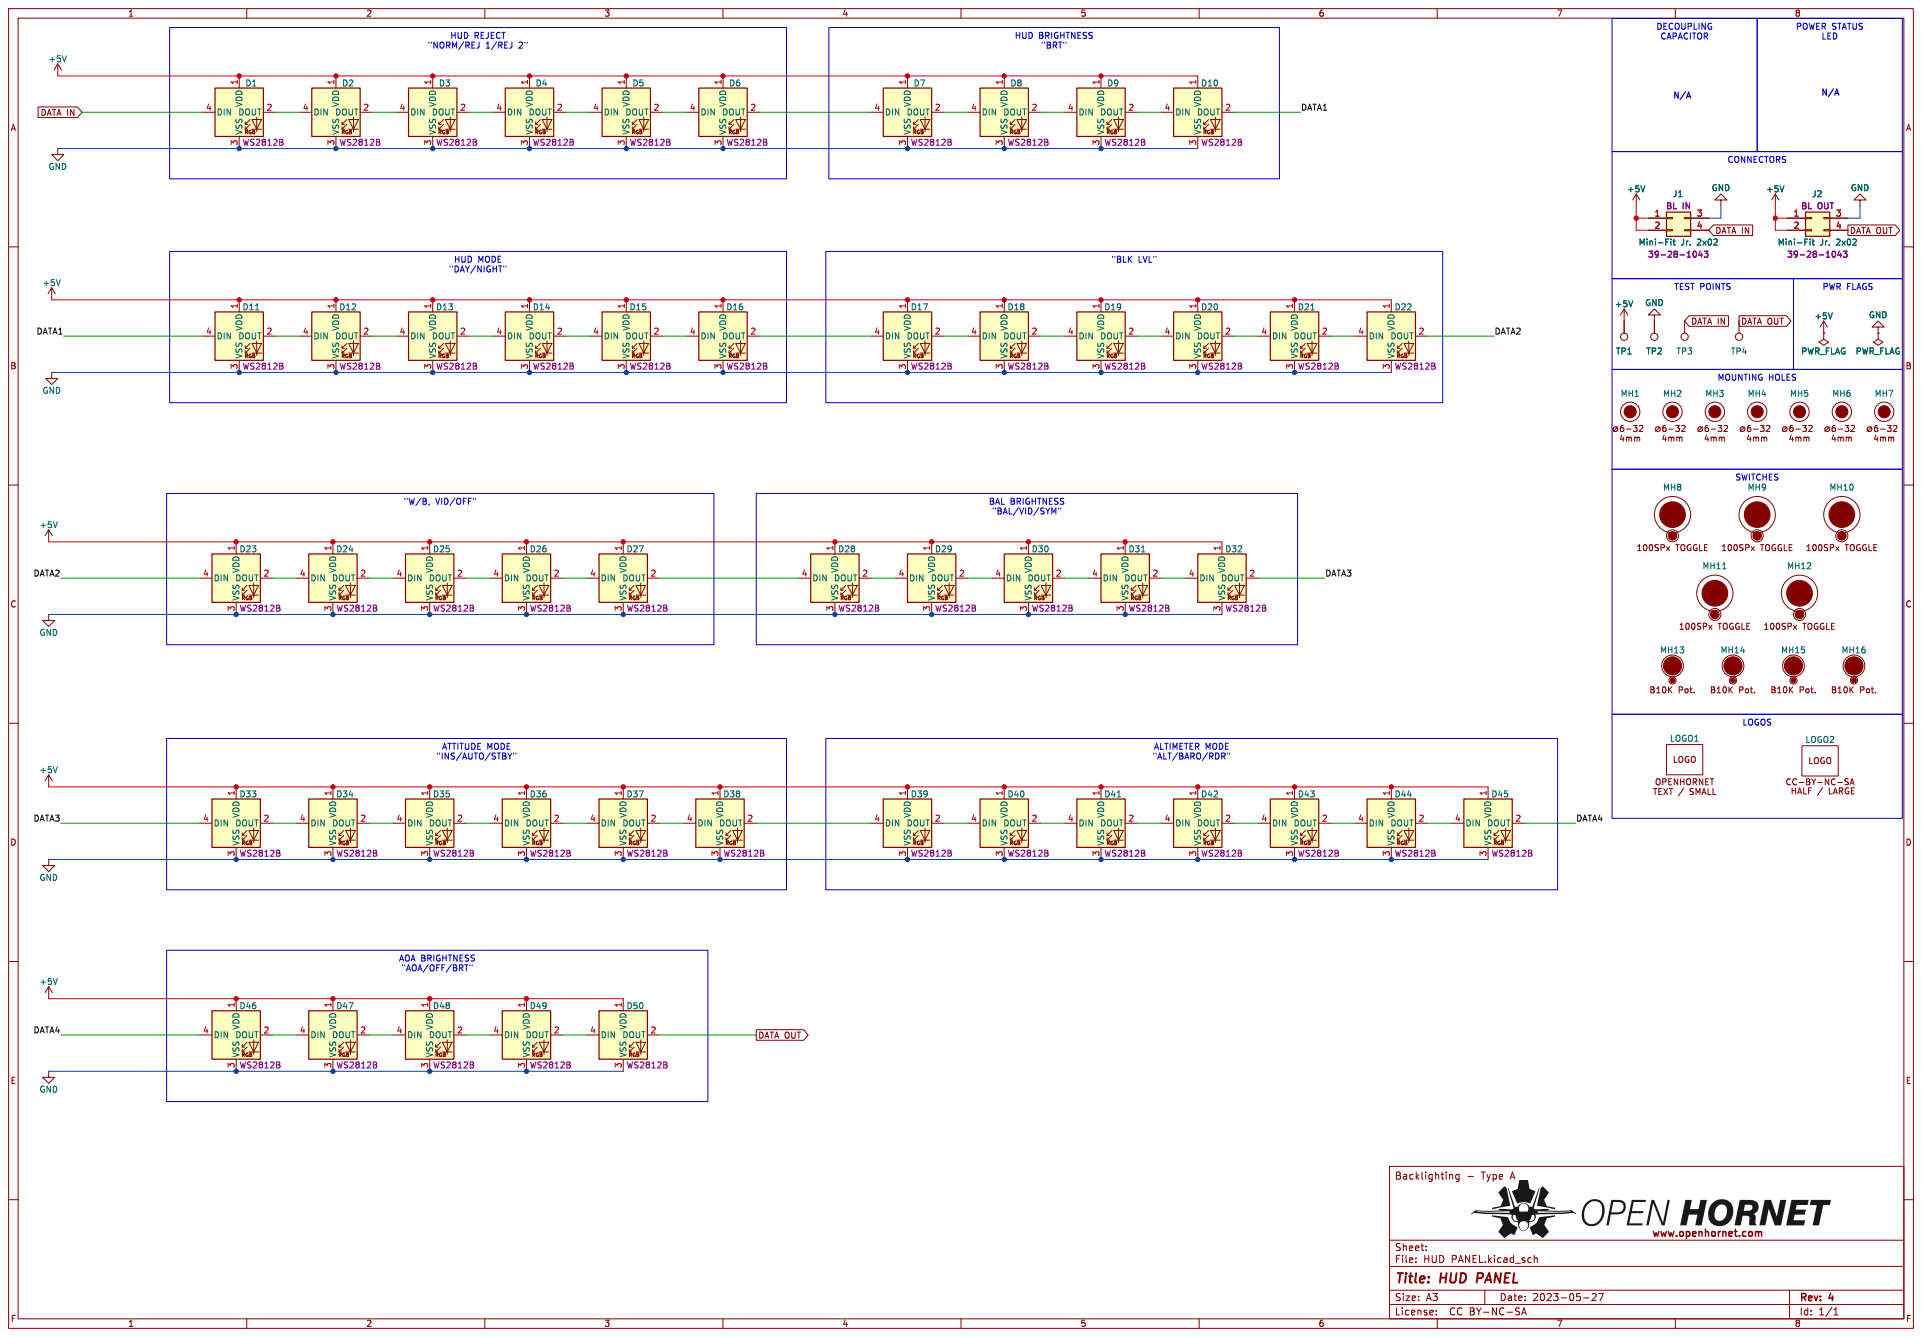
[picture p551: page 1]

"DAY/NIGHT" HUD REJECT

"BLK LVL" HUD BRIGHTNESS

"W/B, VID/OFF" AOA BRIGHTNESS

"BAL/VID/SYM" ATTITUDE MODE

CC-BY-NC-SA HALF / LARGE

Id: 1/1 Title: HUD PANEL

Size: A3 | | Rev: 4 | F Date: 2023-05-27
License: CC | BY-NC-SA
