jrsteensen/OpenHornet/release/OHE_Electronics/OH1A8A3-15 - PCB, UFC_FUNCTION_SELECT V4/UFC_Function Select.pdf

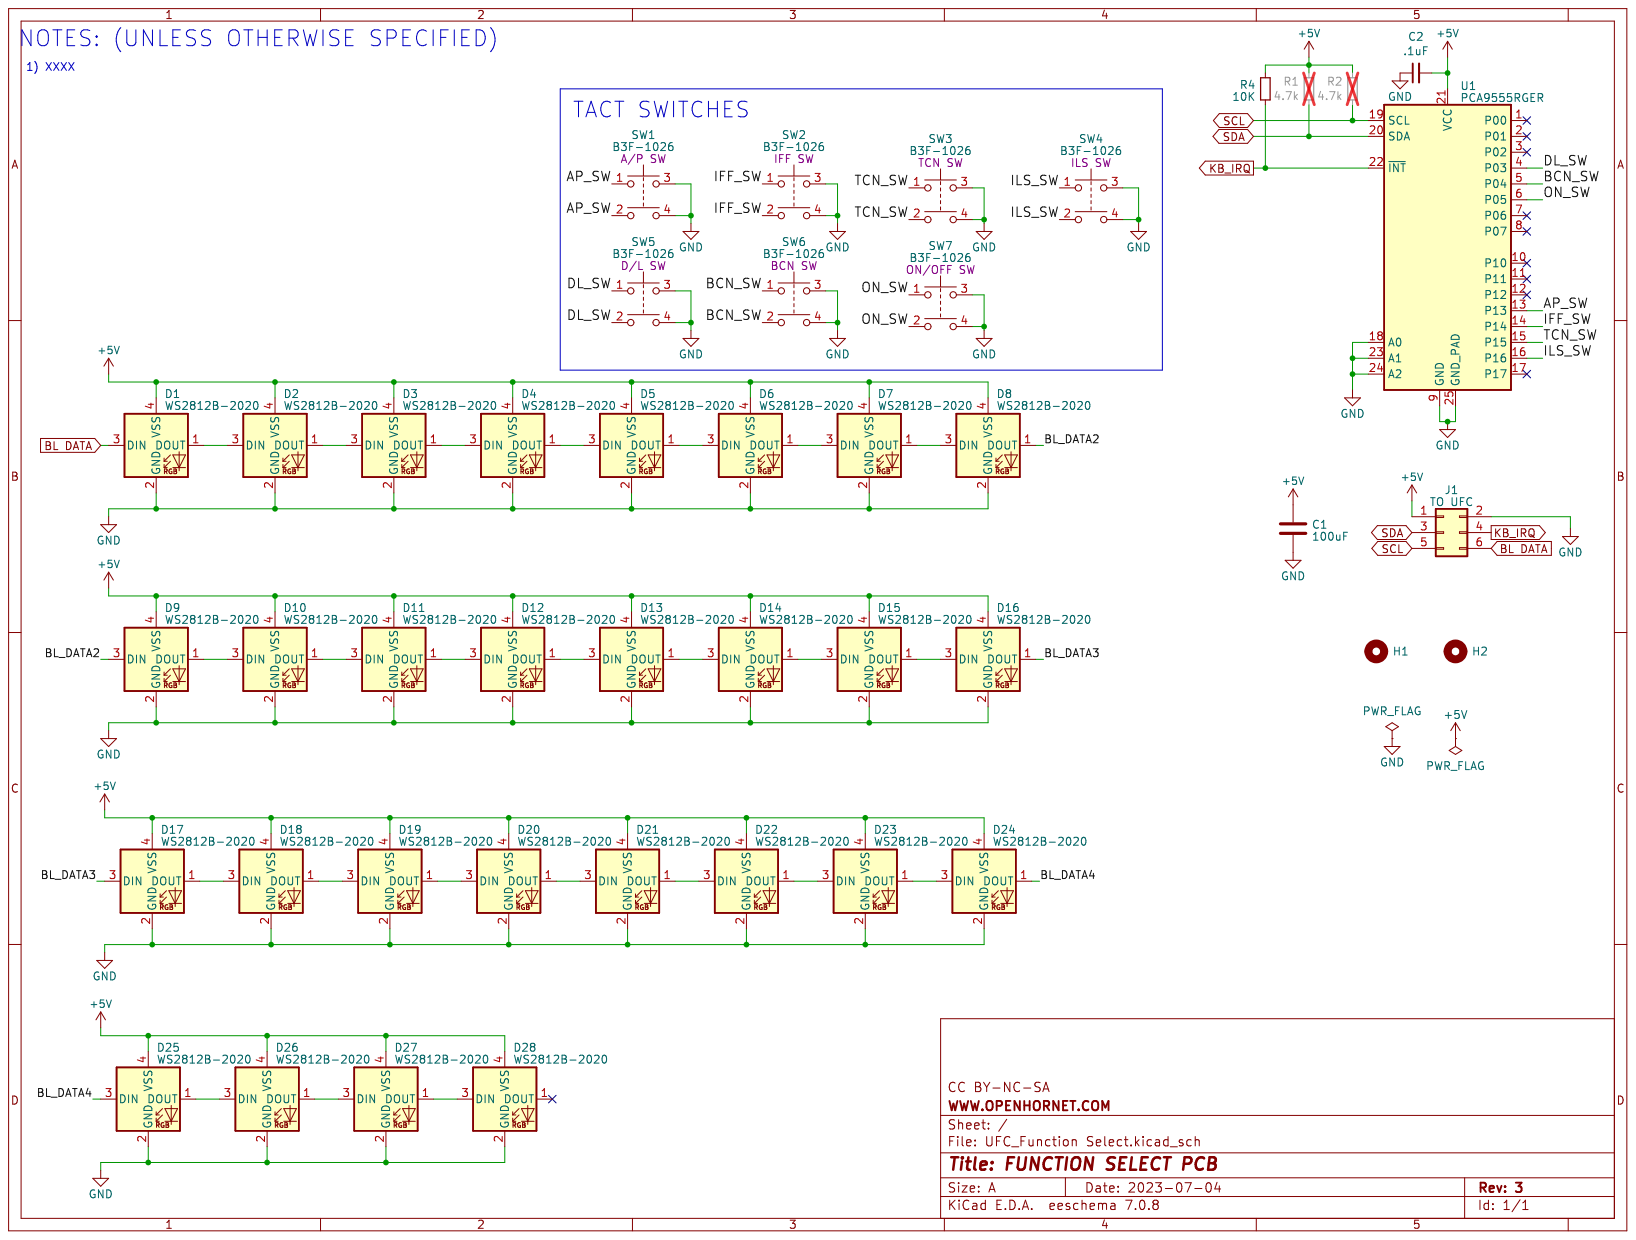
[picture p552: page 1]
