jrsteensen/OpenHornet/release/OHE_Electronics/OH2A2A1A1-32 - PCB, JETT STATION SELECT/Jett Station Select.pdf

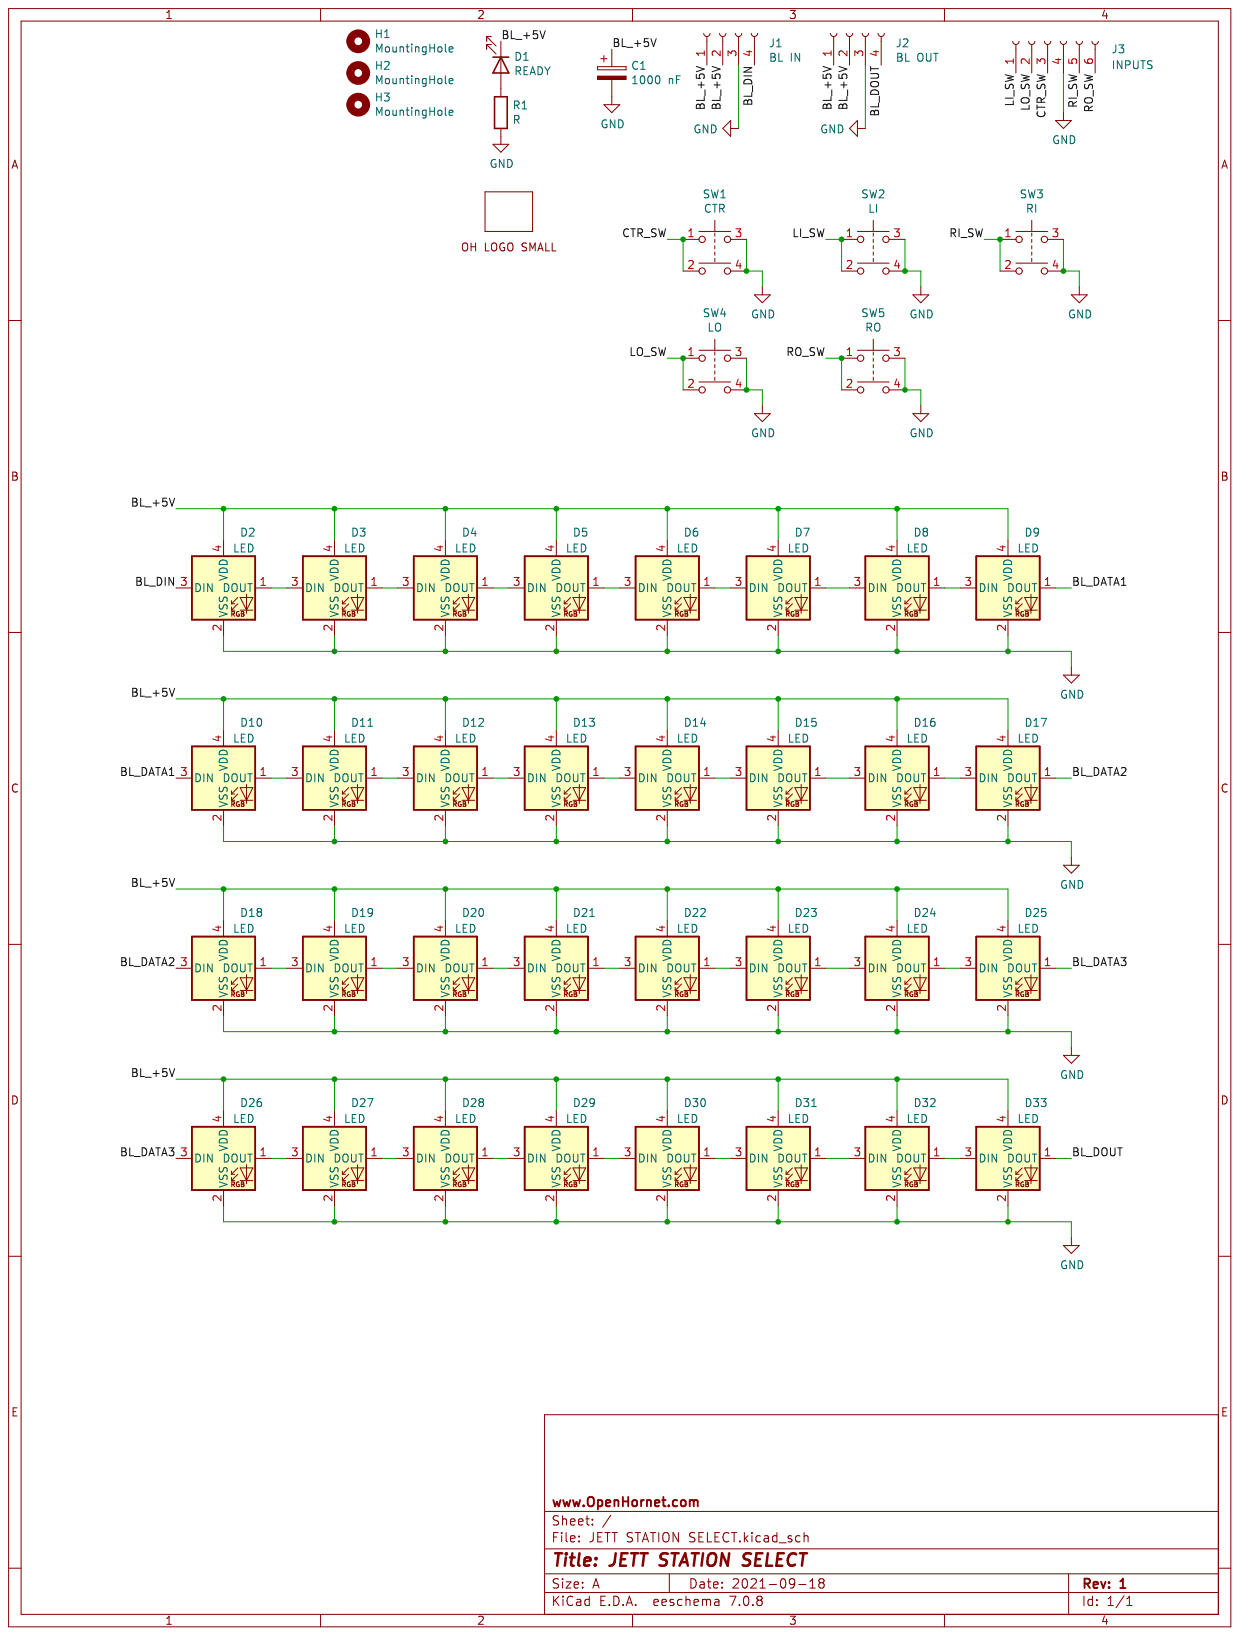
[picture p553: page 1]
