jrsteensen/OpenHornet/release/OHE_Electronics/OH2A2A1A2-16 - PCB, IFEI/IFEI.pdf

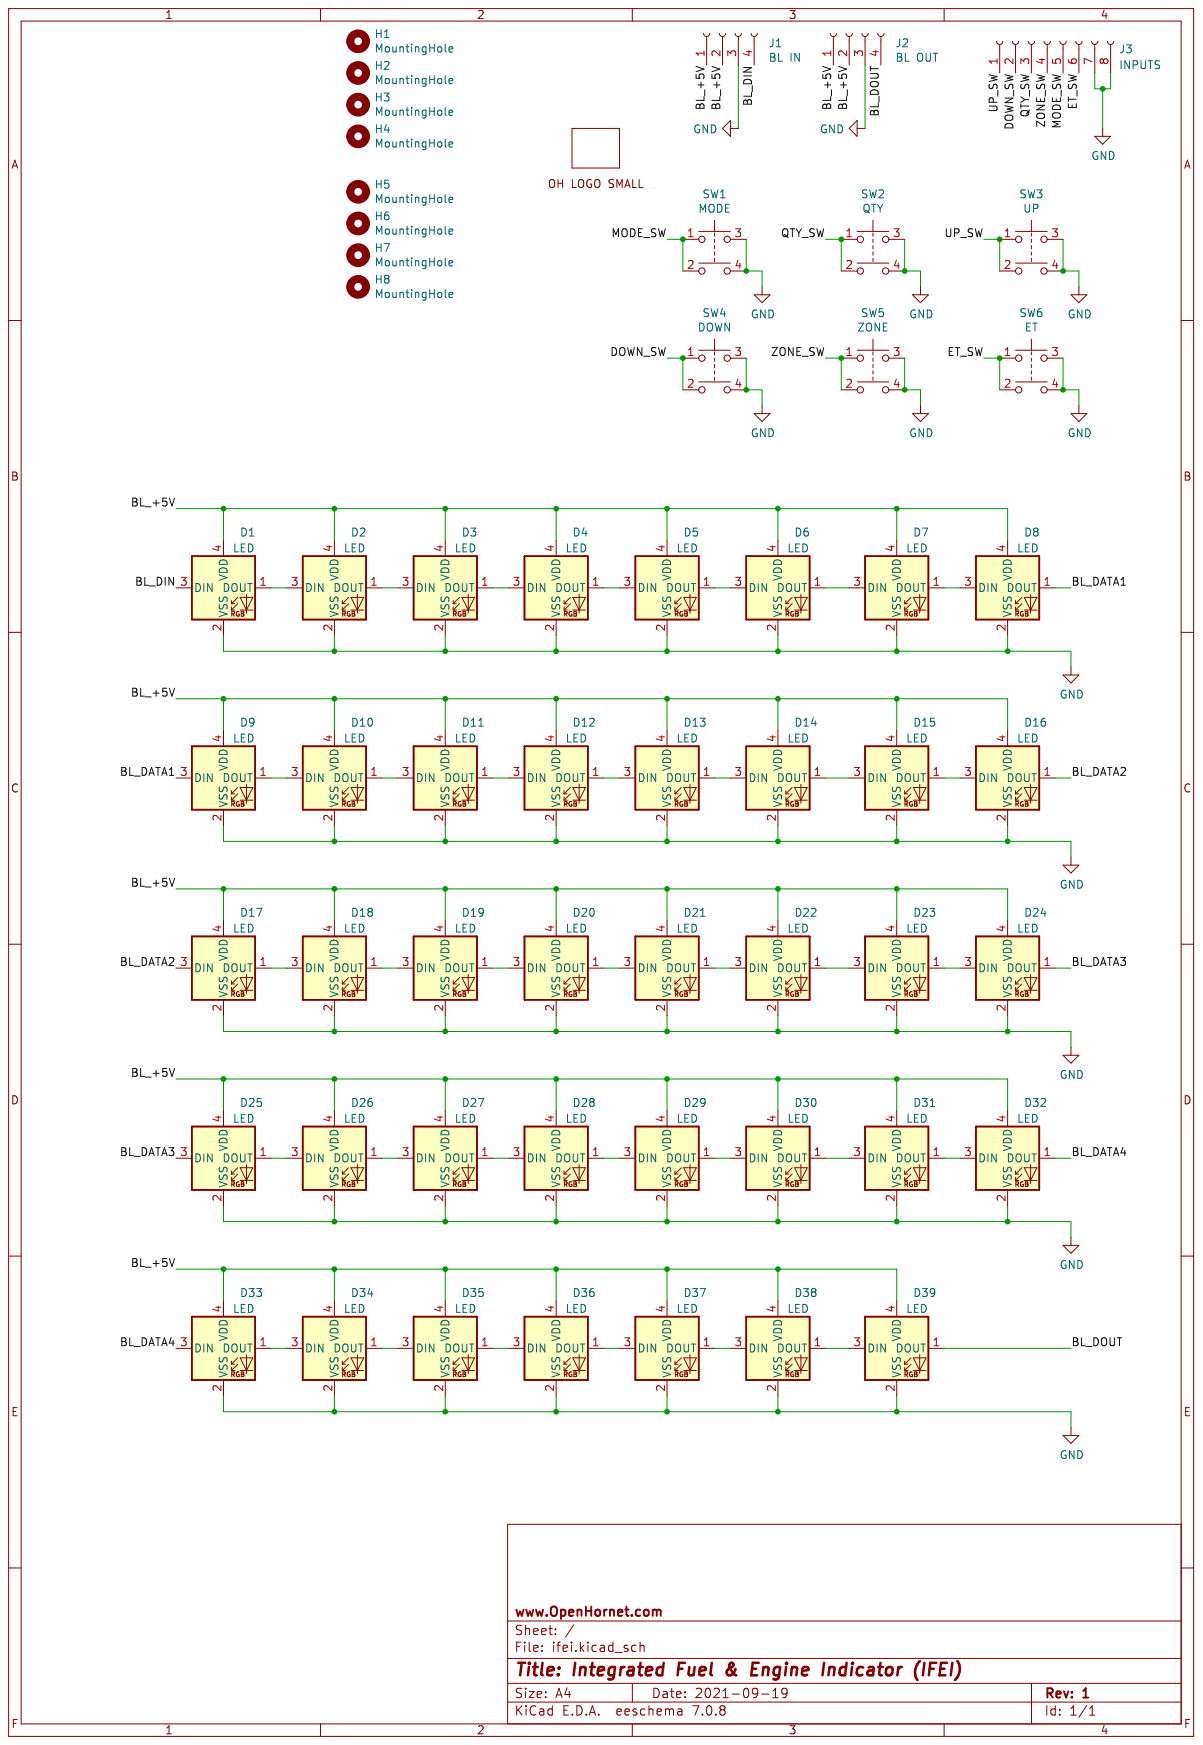
[picture p554: page 1]
