jrsteensen/OpenHornet/release/OHE_Electronics/OH2A2A1A3-13 - PCB, HUD VIDEO RECORD PANEL/HUD VID RCD PANEL.pdf

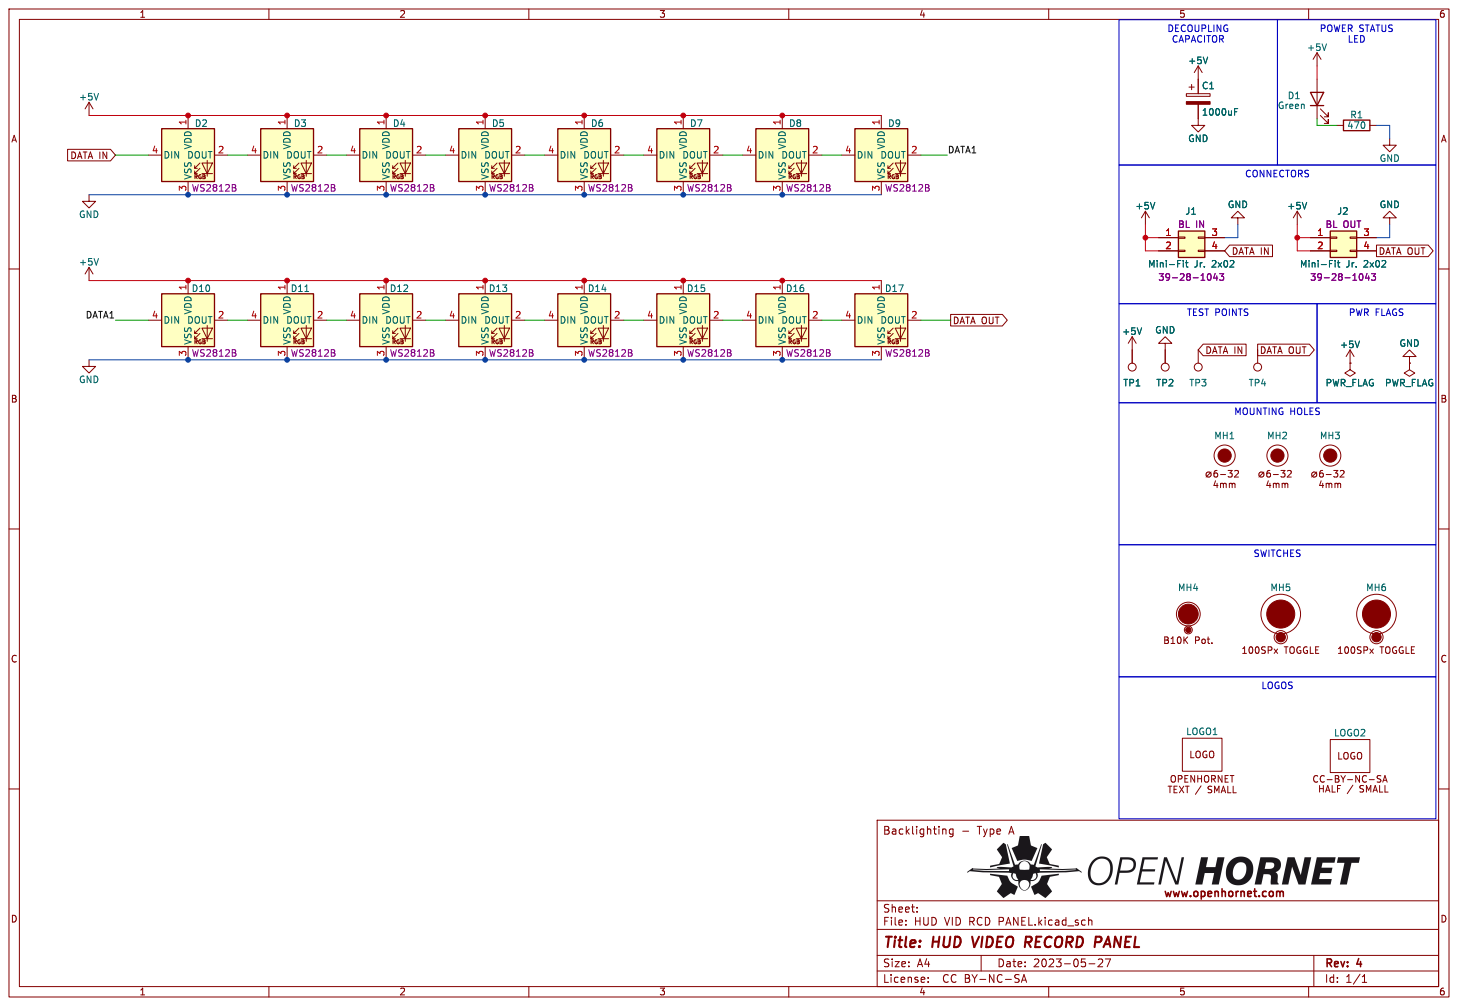
[picture p555: page 1]

CC-BY-NC-SA HALF / SMALL

Id: 1/1 Title: HUD VIDEO RECORD PANEL

Size: A4 | | Rev: 4
License: CC | BY-NC-SA
