jrsteensen/OpenHornet/release/OHE_Electronics/OH2A3A1-29 - PCB, AMPCD_BUTTON_BOARD/AMPCD.pdf

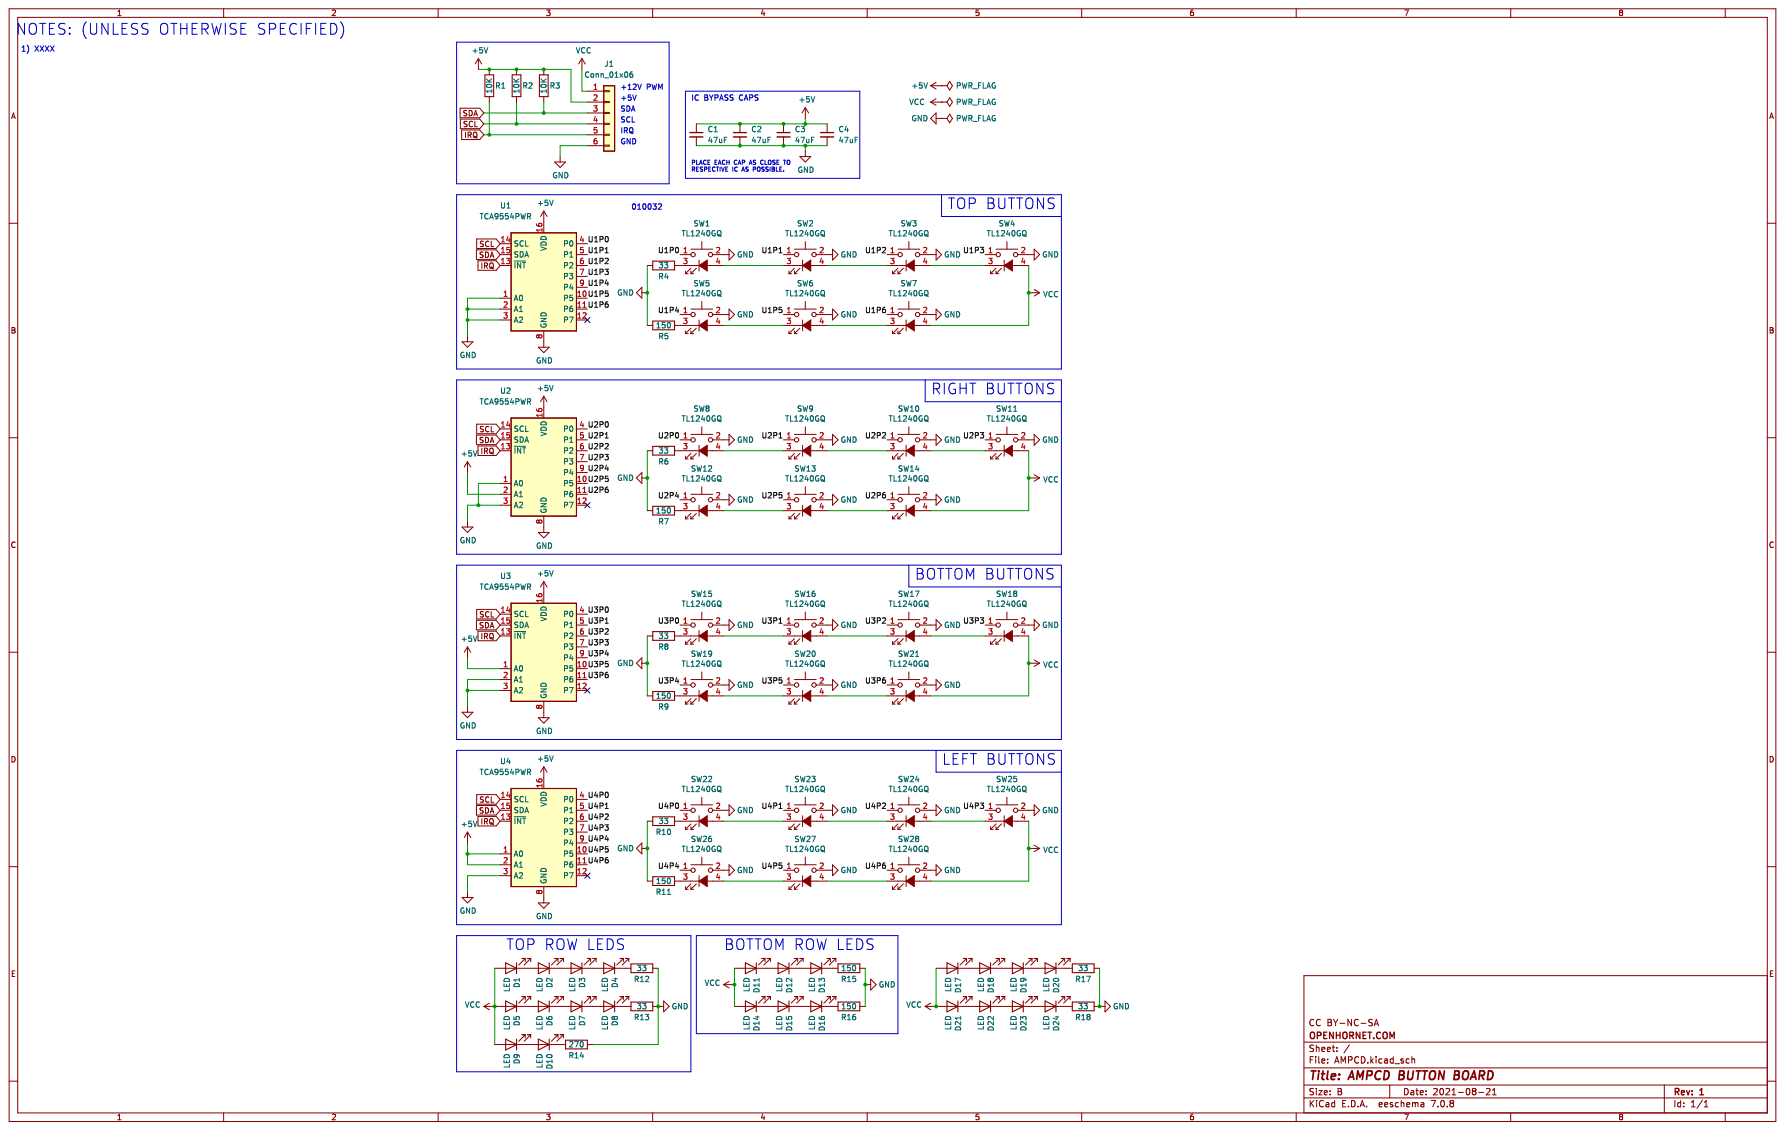
[picture p556: page 1]
