jrsteensen/OpenHornet/release/OHE_Electronics/OH2A4A1-506 - PCB, RWR CONTROL PANEL/RWR Control Panel.pdf

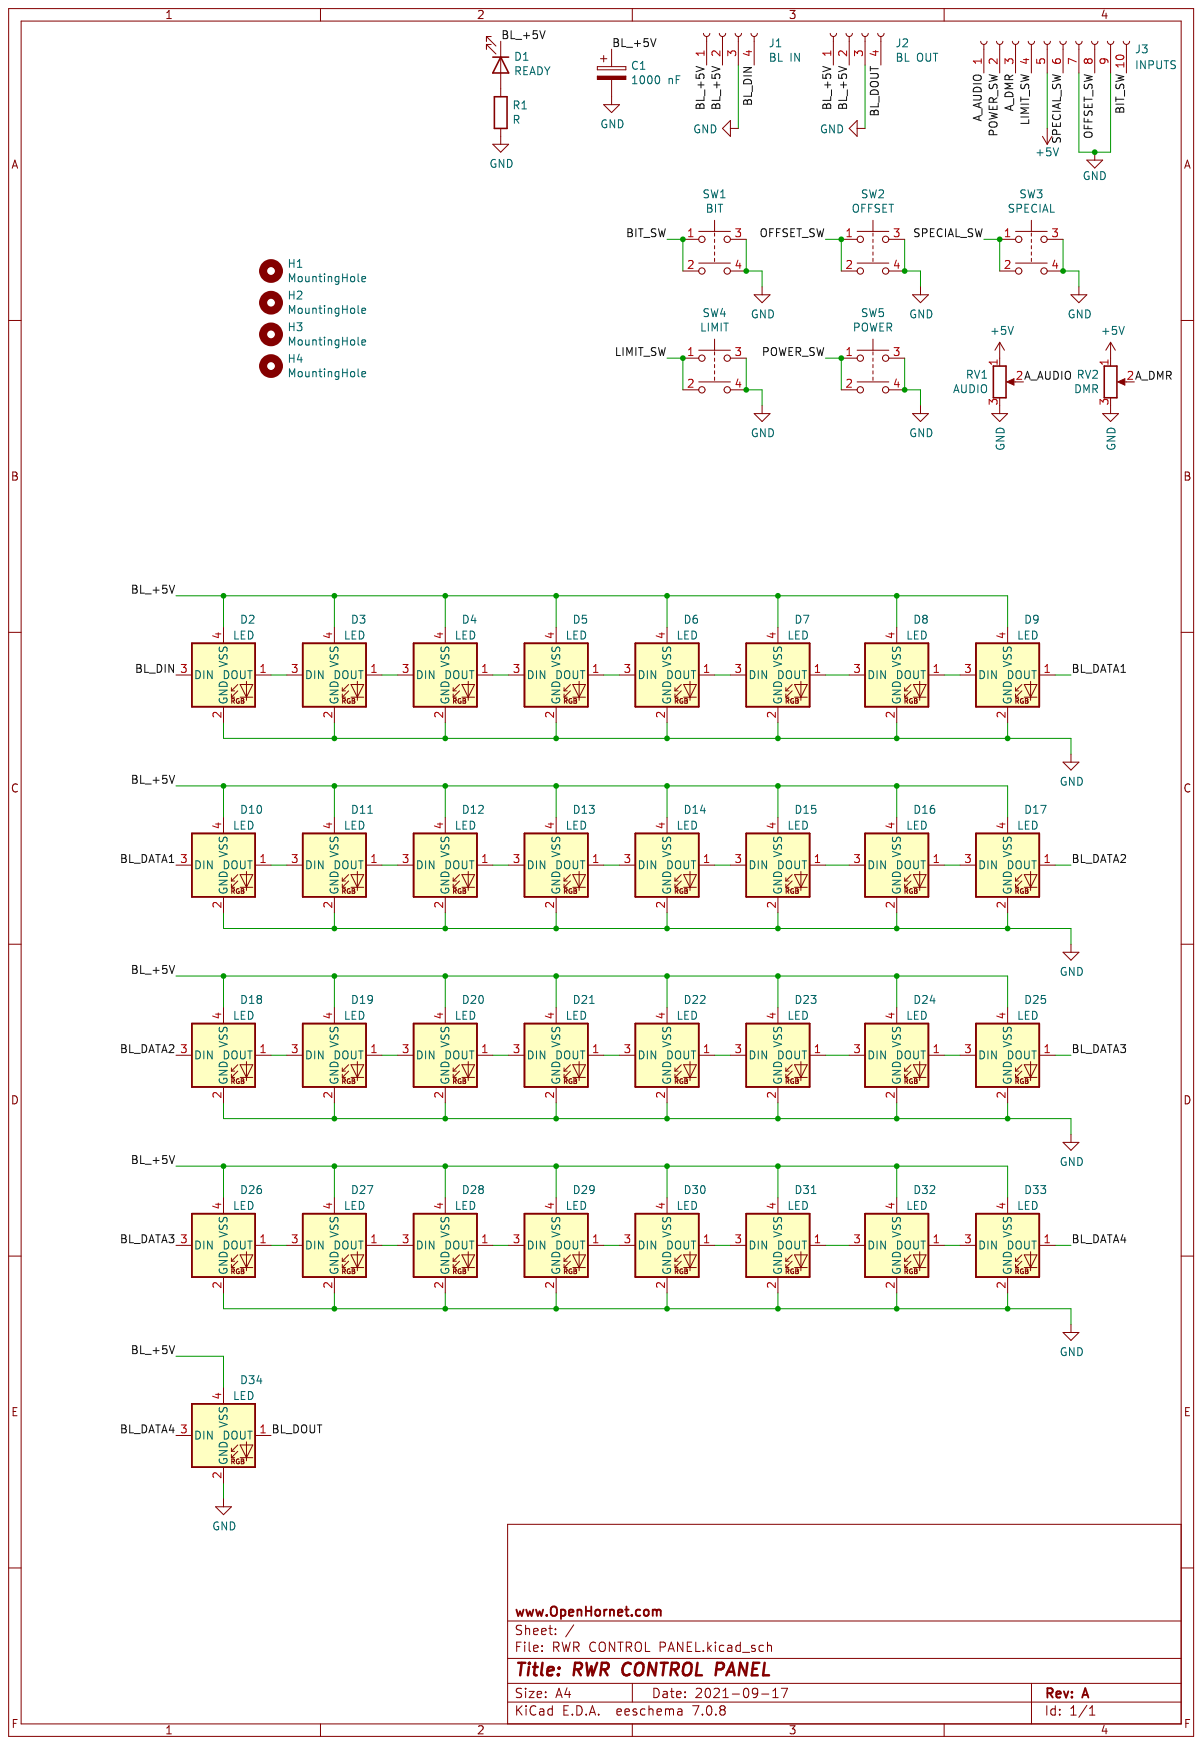
[picture p557: page 1]
