jrsteensen/OpenHornet/release/OHE_Electronics/OH2A7A1-210 - PCB, STANDBY ALTIMETER/Standby Altimeter.pdf

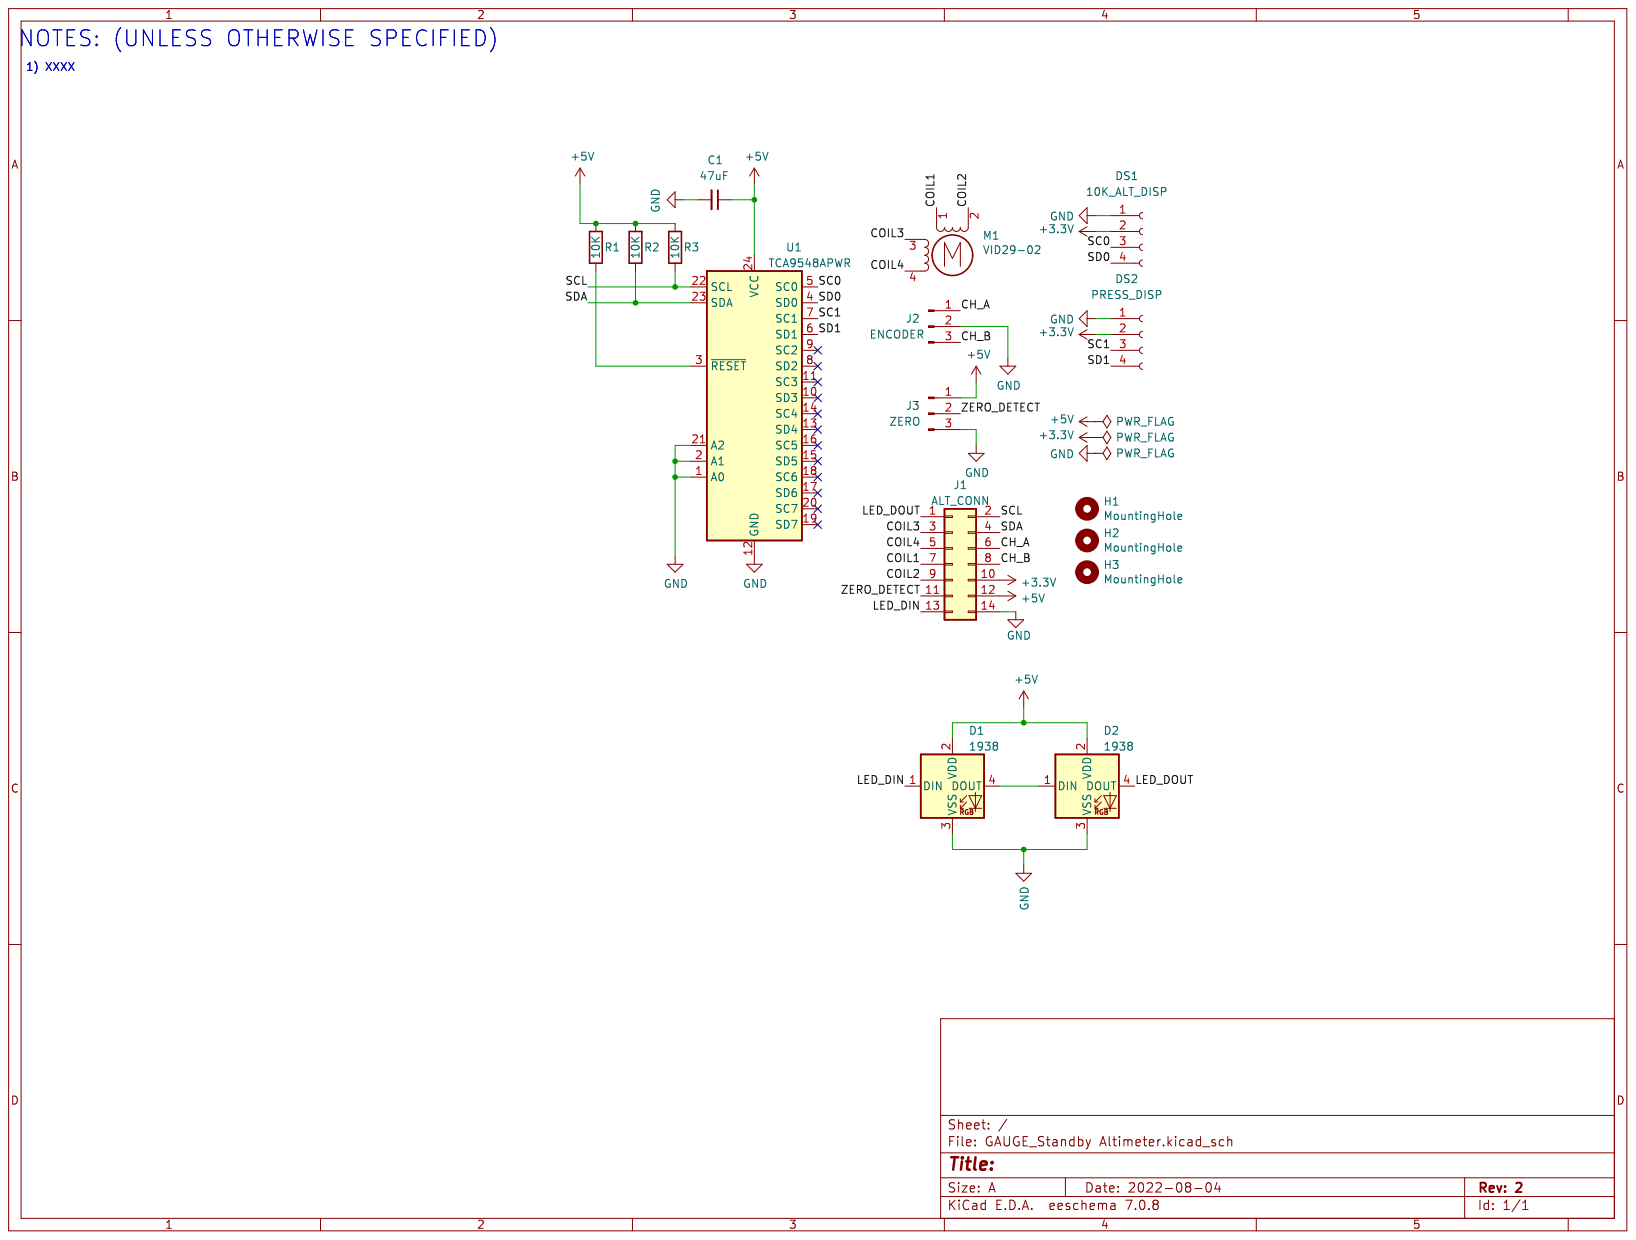
[picture p558: page 1]
