jrsteensen/OpenHornet/release/OHE_Electronics/OH3A3A1-10 - PCB, STICK CONTROLLER/Stick Controller.pdf

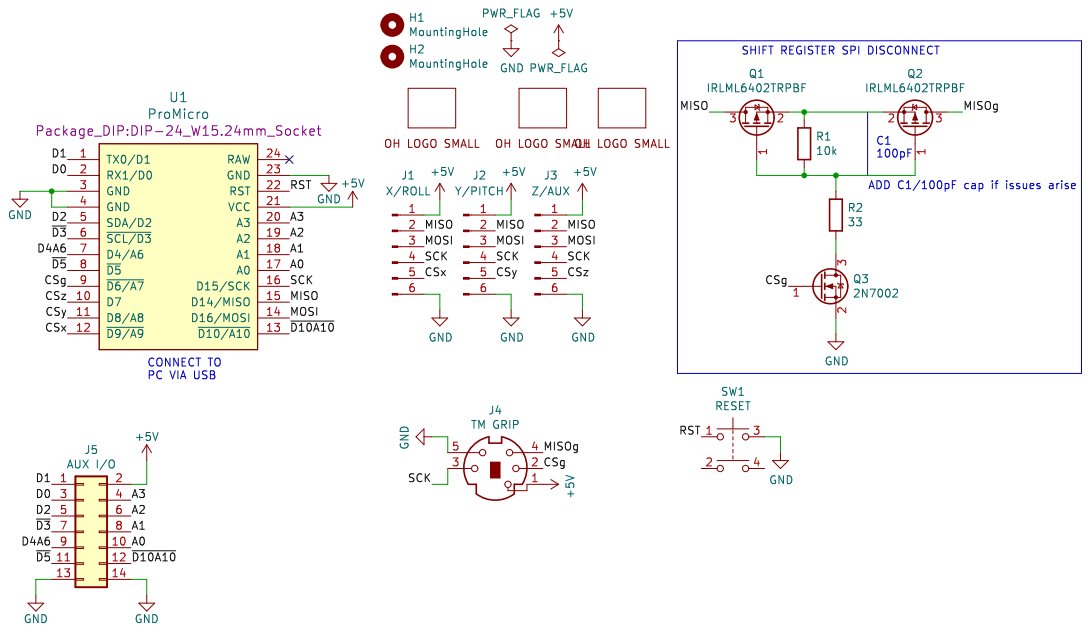
[picture p559: page 1]
