jrsteensen/OpenHornet/release/OHE_Electronics/OH4A4A2-10 - PCB, EXTERNAL LT PANEL/EXT LT PANEL.pdf

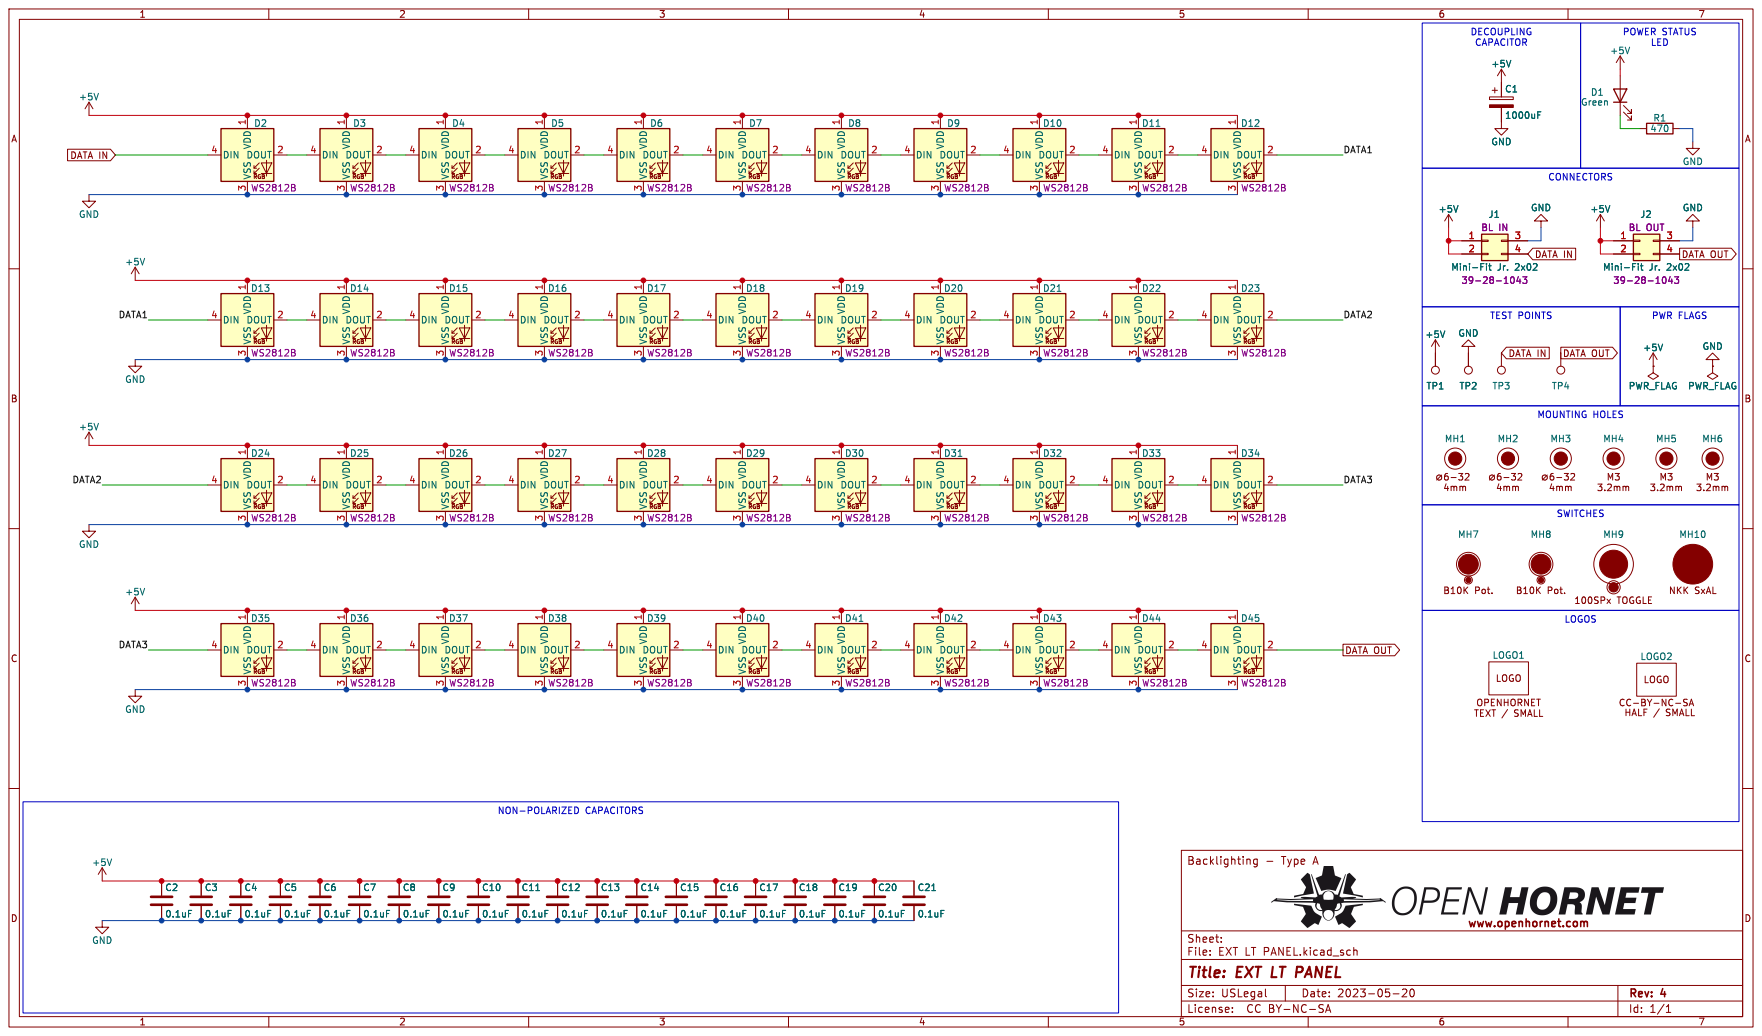
[picture p560: page 1]

Id: 1/1 Title: EXT LT PANEL

Size: USLegal | | Rev: 4
License: CC | BY-NC-SA
