jrsteensen/OpenHornet/release/OHE_Electronics/OH4A4A3-10 - PCB, GEN TIE PANEL/GEN TIE PANEL.pdf

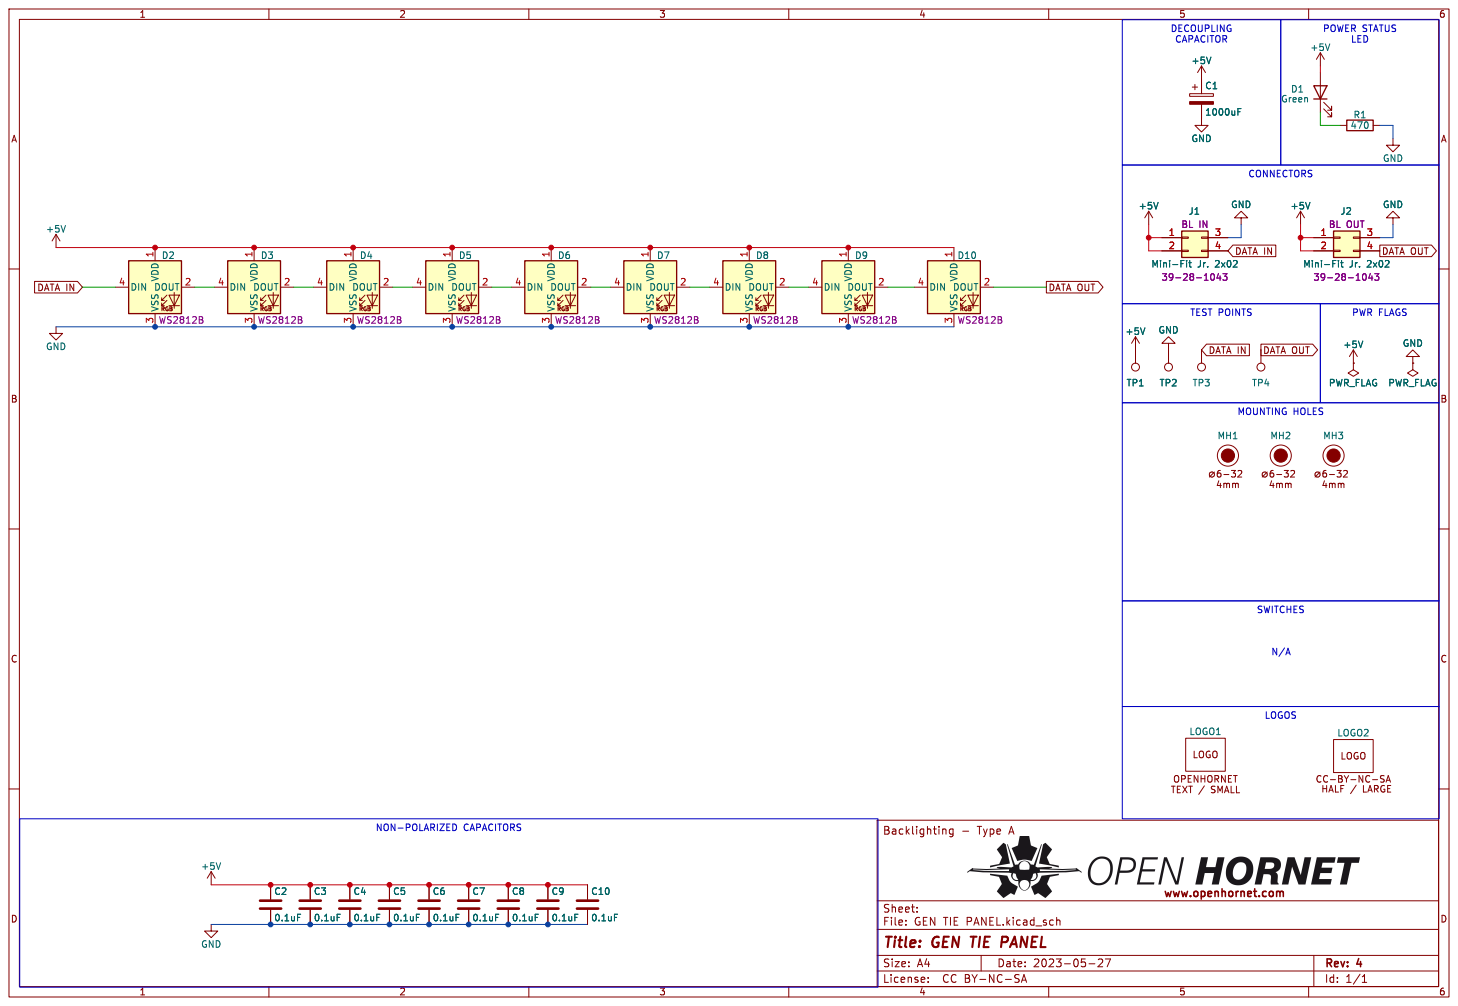
[picture p561: page 1]

Id: 1/1 Title: GEN TIE PANEL

Size: A4 | | Rev: 4
License: CC | BY-NC-SA
