jrsteensen/OpenHornet/release/OHE_Electronics/OH4A7A1-10 - PCB, COMM PANEL/COMM PANEL.pdf

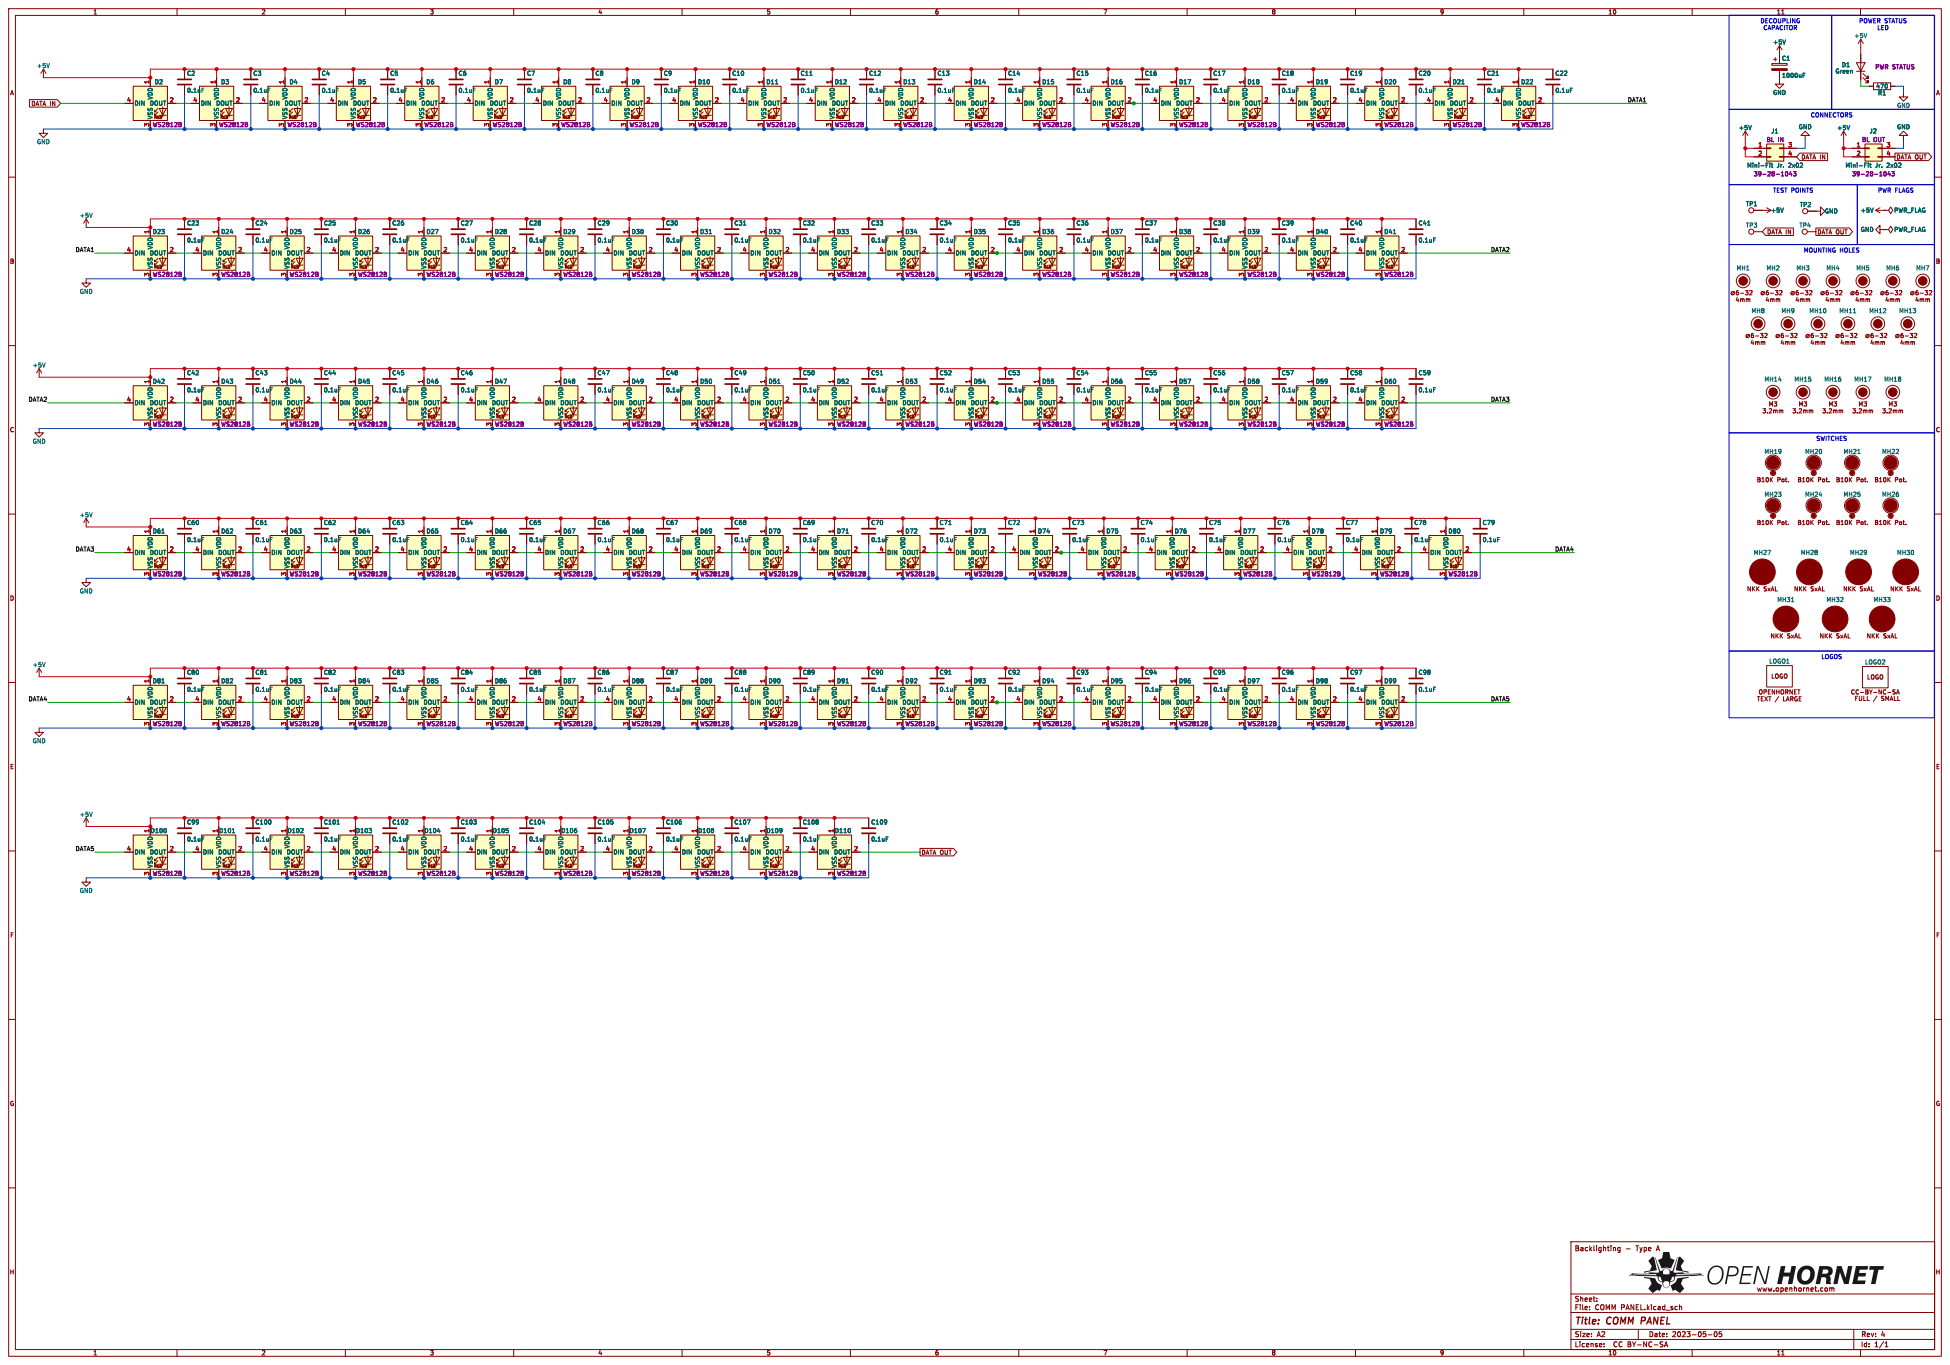
[picture p562: page 1]

LOGO2 B10K Pot. MH24 NKK SxAL MH28 NKK SxAL MH27 B10K Pot. MH23

Size: A2 | | Rev: 4
License: CC | BY-NC-SA
