jrsteensen/OpenHornet/release/OHE_Electronics/OH4A7A2-10 - PCB, OBOGS PANEL/OBOGS PANEL.pdf

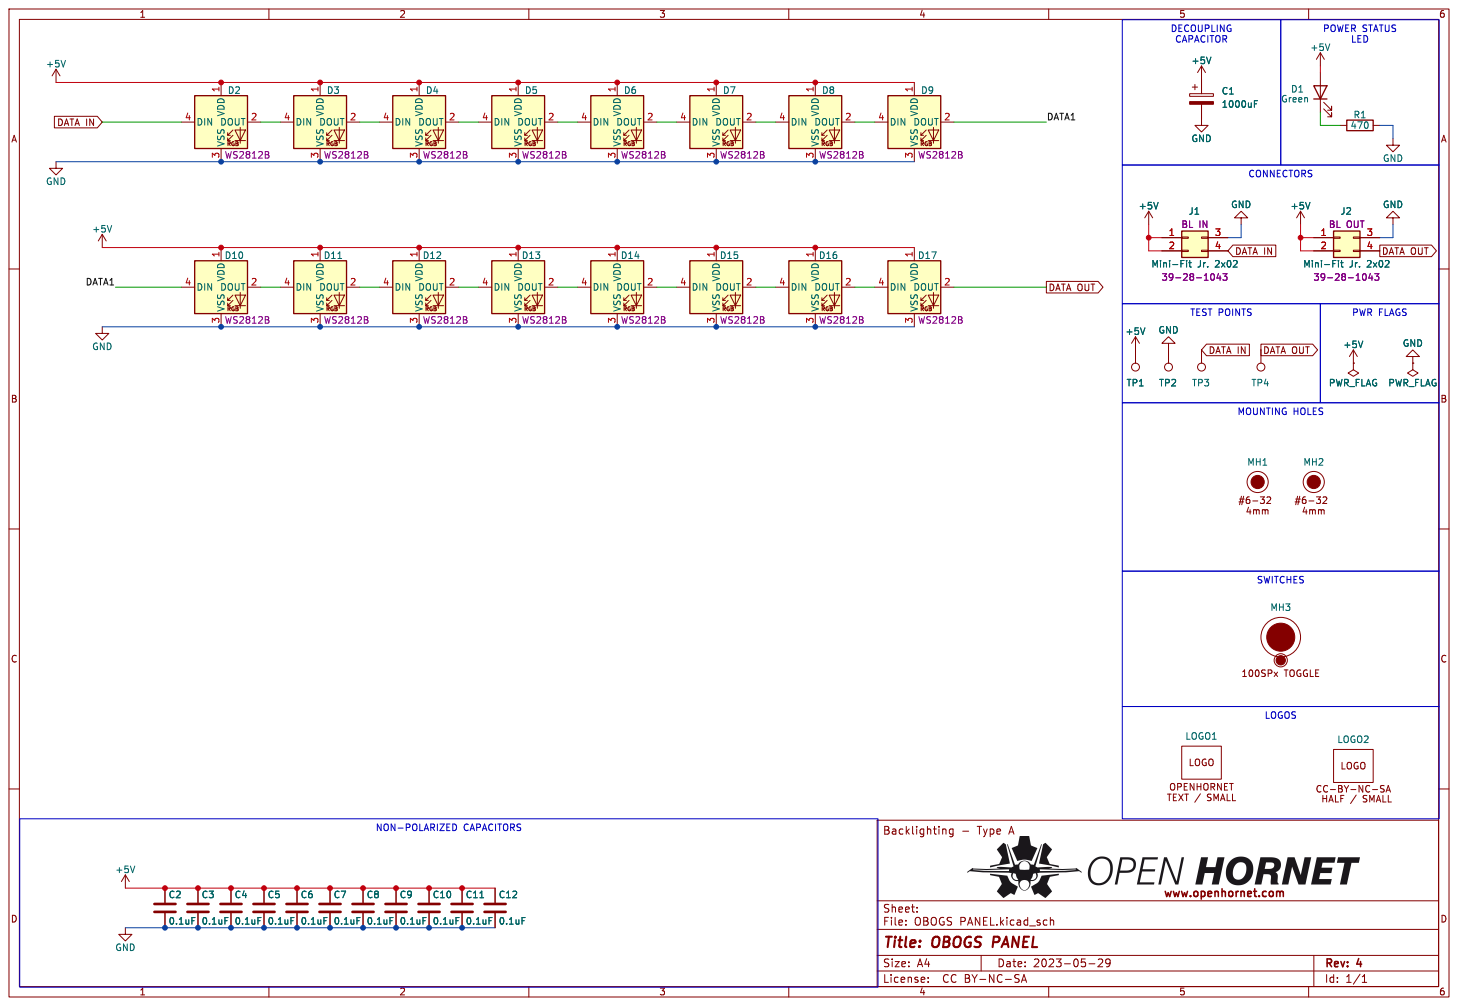
[picture p563: page 1]

Id: 1/1 Title: OBOGS PANEL

Size: A4 | | Rev: 4
License: CC | BY-NC-SA
