jrsteensen/OpenHornet/release/OHE_Electronics/OH4A7A4-10 - PCB, ANT SEL PANEL/ANT SEL PANEL.pdf

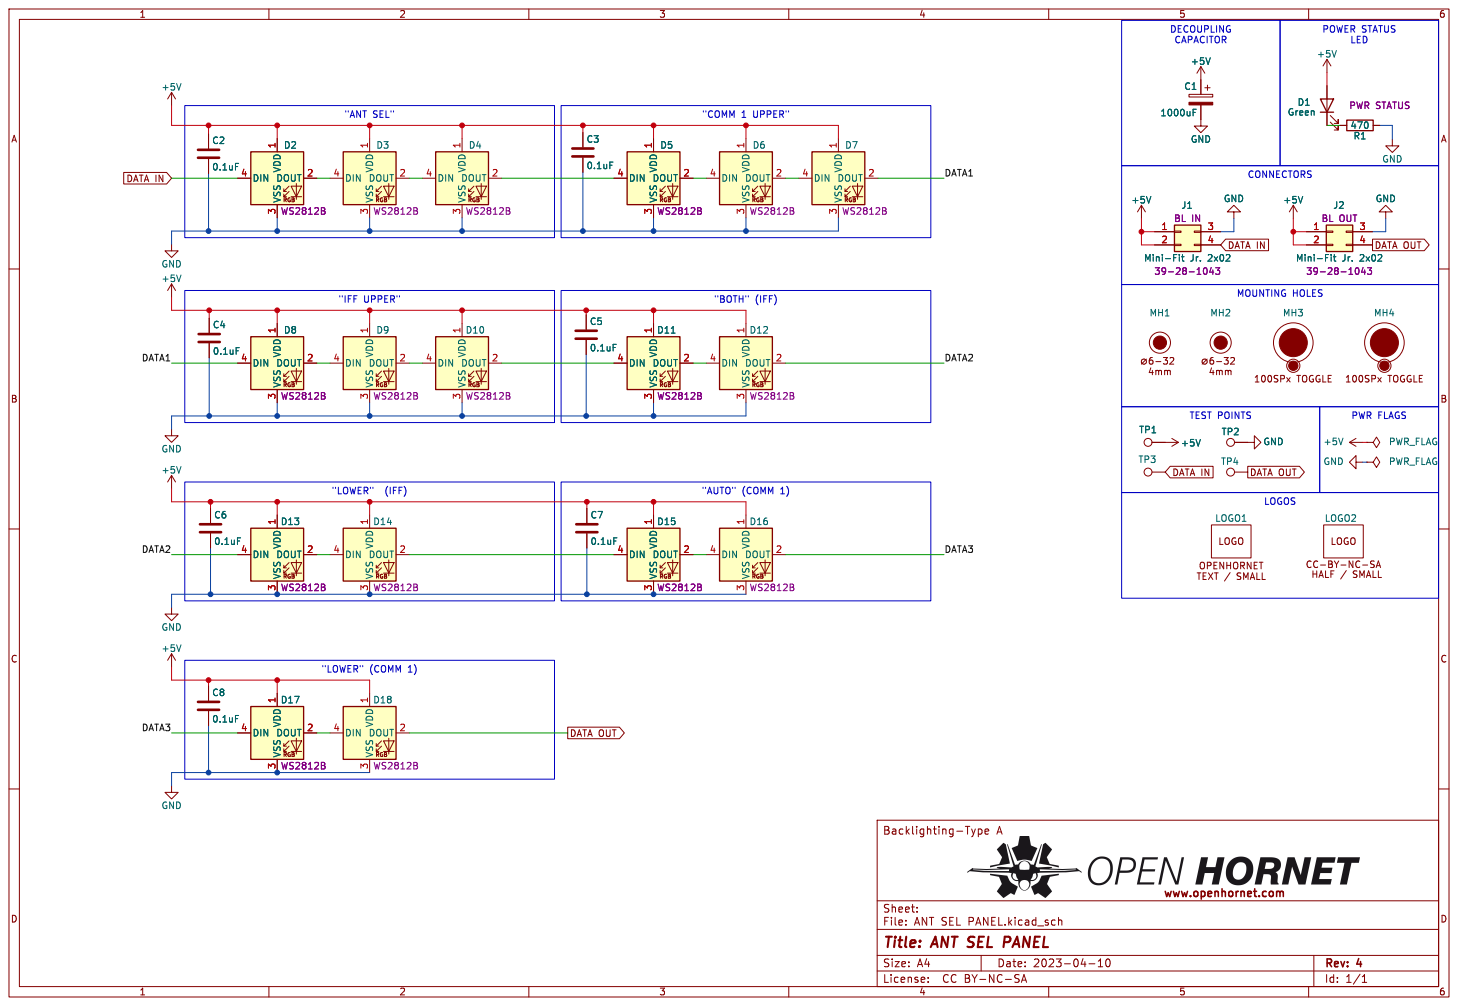
[picture p564: page 1]

3 DIN 4 D6 WS2812B C3
RGB VDD
"BOTH" (IFF) "AUTO" (COMM 1)

DATA OUT DATA OUT DATA IN

3 DIN 4 D18 WS2812B CC-BY-NC-SA HALF / SMALL

Id: 1/1 Title: ANT SEL PANEL

Size: A4 | | Rev: 4
License: CC | BY-NC-SA
