jrsteensen/OpenHornet/release/OHE_Electronics/OH4A9-121 - ANALOG_STICK_BREAKOUT_PCB/Analog Stick Breakout.pdf

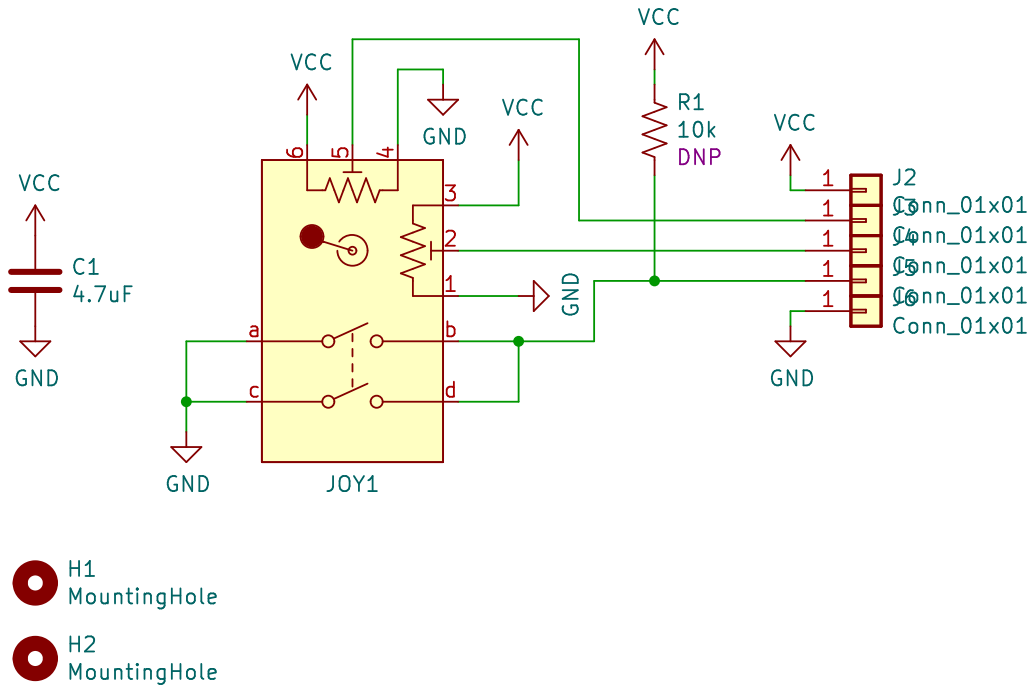
[picture p565: page 1]
