jrsteensen/OpenHornet/release/OHE_Electronics/OH4A9-123 - HAT_SWITCH_BREAKOUT_PCB/Hat Switch Breakout.pdf

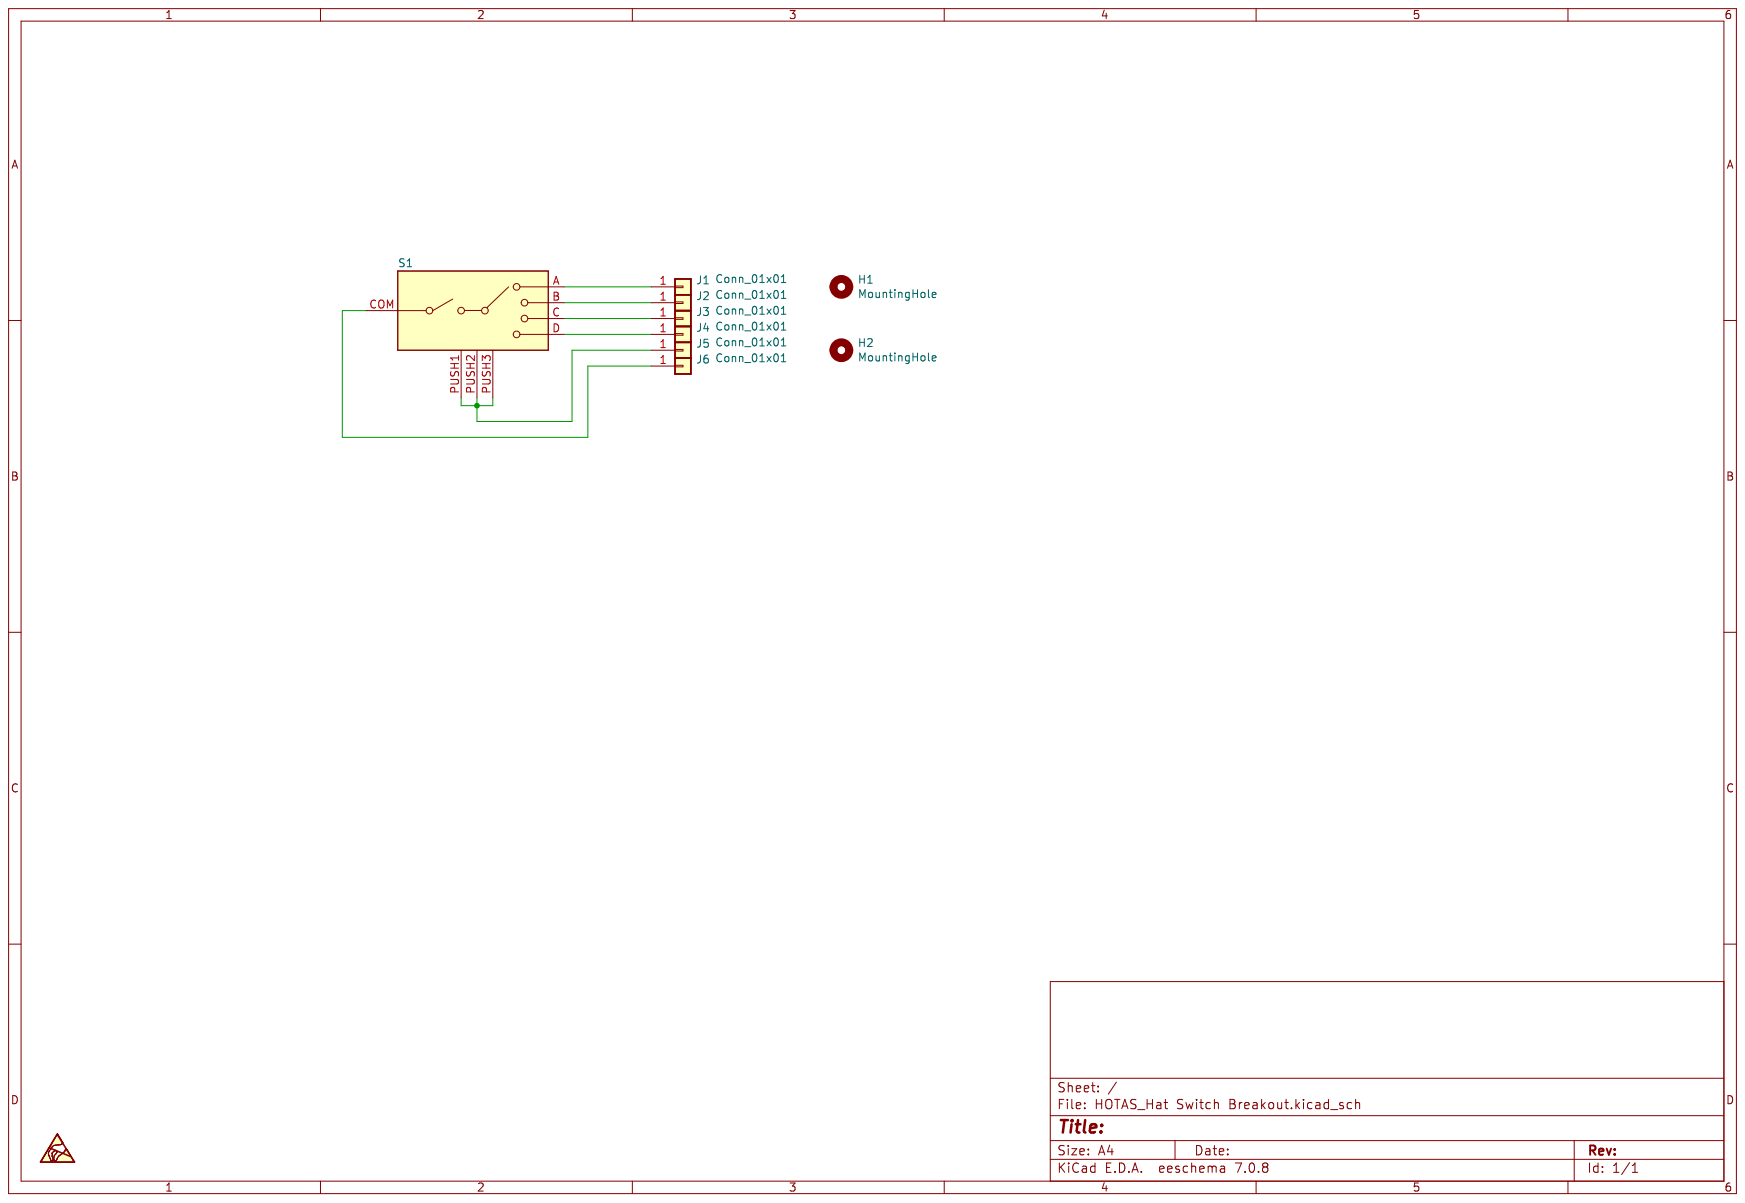
[picture p566: page 1]
