jrsteensen/OpenHornet/release/OHE_Electronics/OH4A9-301 - PCB, CONTROLLER, THROTTLE/Throttle.pdf

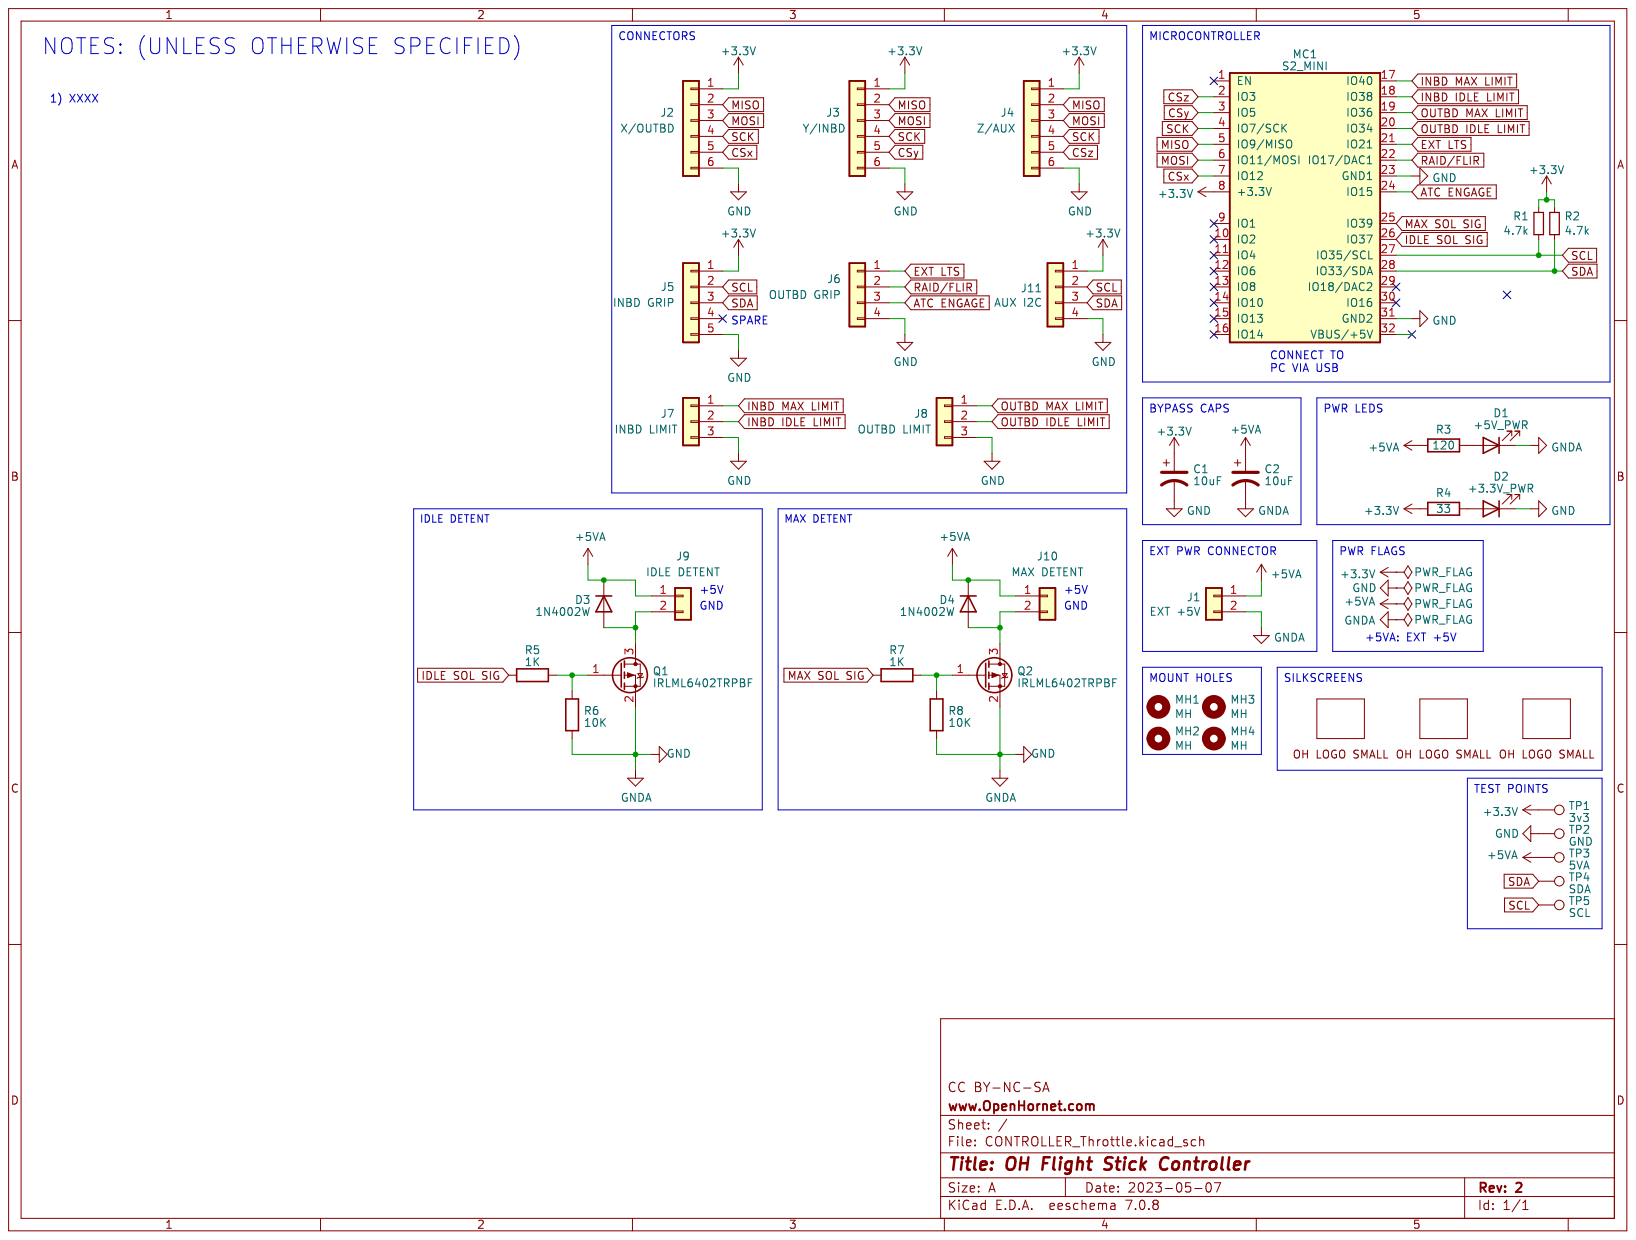
[picture p567: page 1]
