jrsteensen/OpenHornet/release/OHE_Electronics/OH5A2A3-12 - PCB, AV COOL SWITCH/AV COOL PANEL.pdf

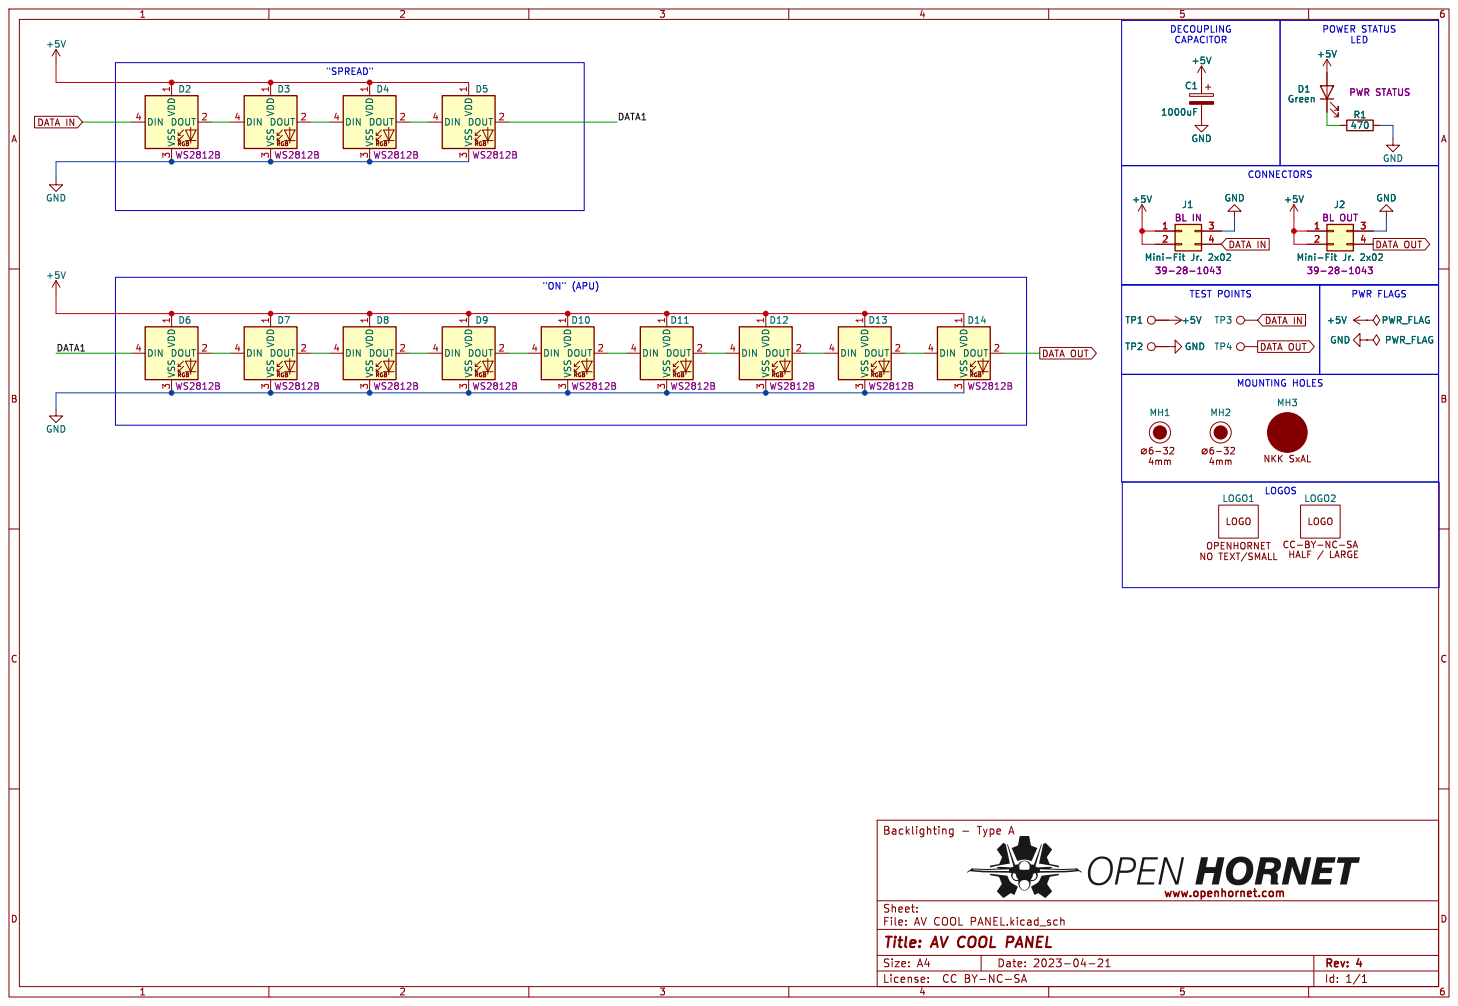
[picture p568: page 1]

470 DATA OUT DATA IN

Id: 1/1 Title: AV COOL PANEL

Size: A4 | | Rev: 4
License: CC | BY-NC-SA
