jrsteensen/OpenHornet/release/OHE_Electronics/OH5A4A1-13 - PCB, ELEC PANEL/ELEC PANEL.pdf

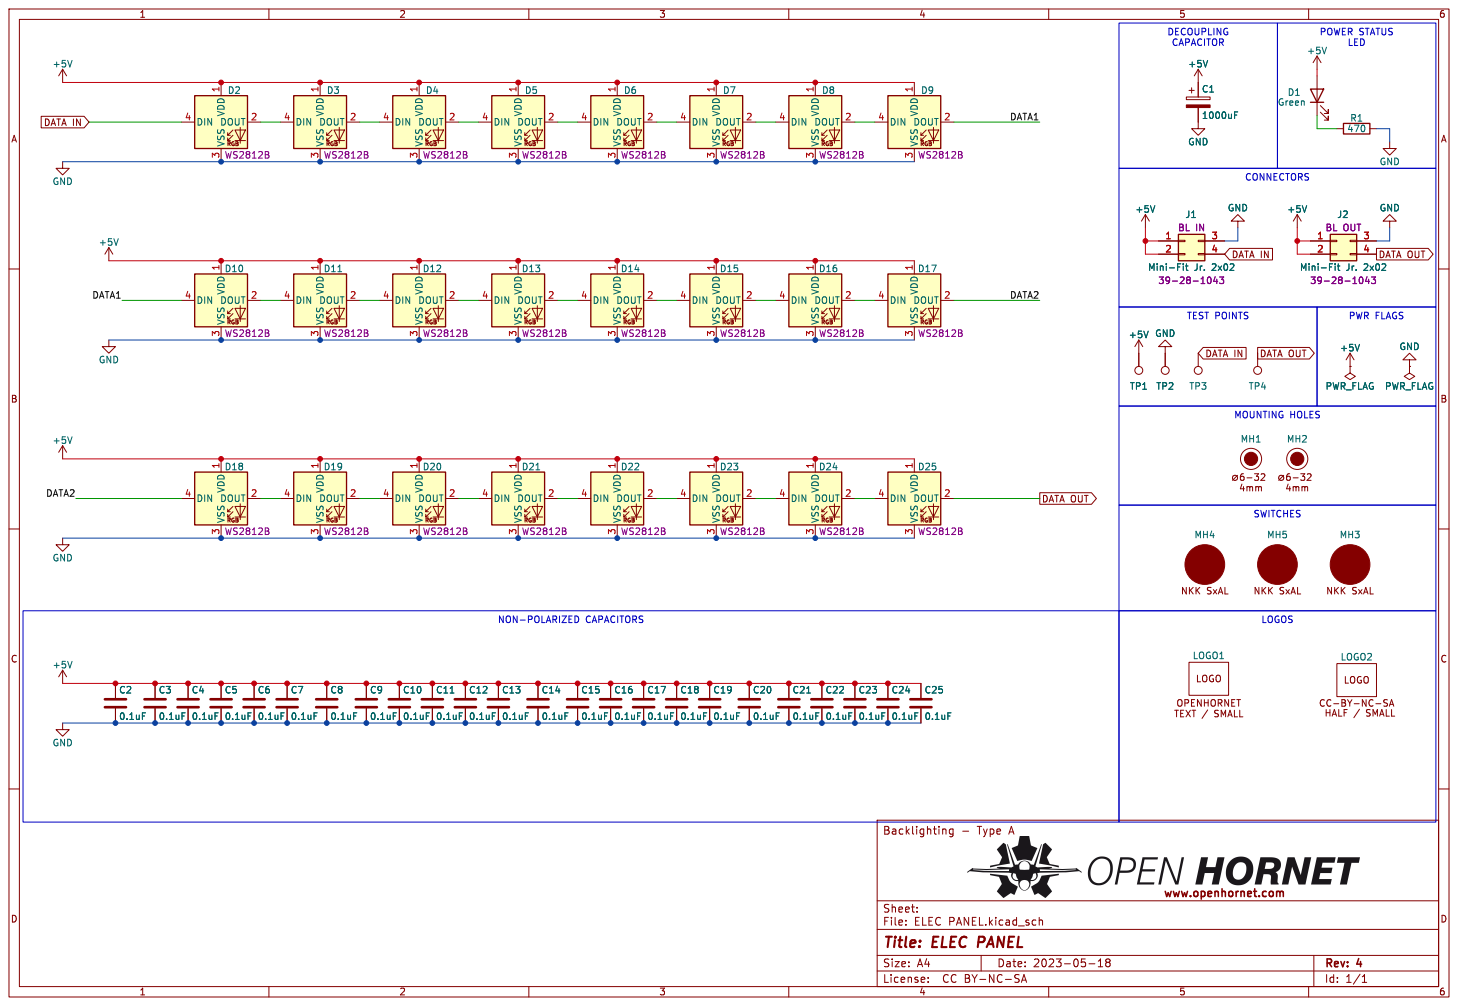
[picture p569: page 1]

Id: 1/1 Title: ELEC PANEL

Size: A4 | | Rev: 4
License: CC | BY-NC-SA
