jrsteensen/OpenHornet/release/OHE_Electronics/OH5A5A2-13 - PCB, DEFOG PANEL/DEFOG PANEL.pdf

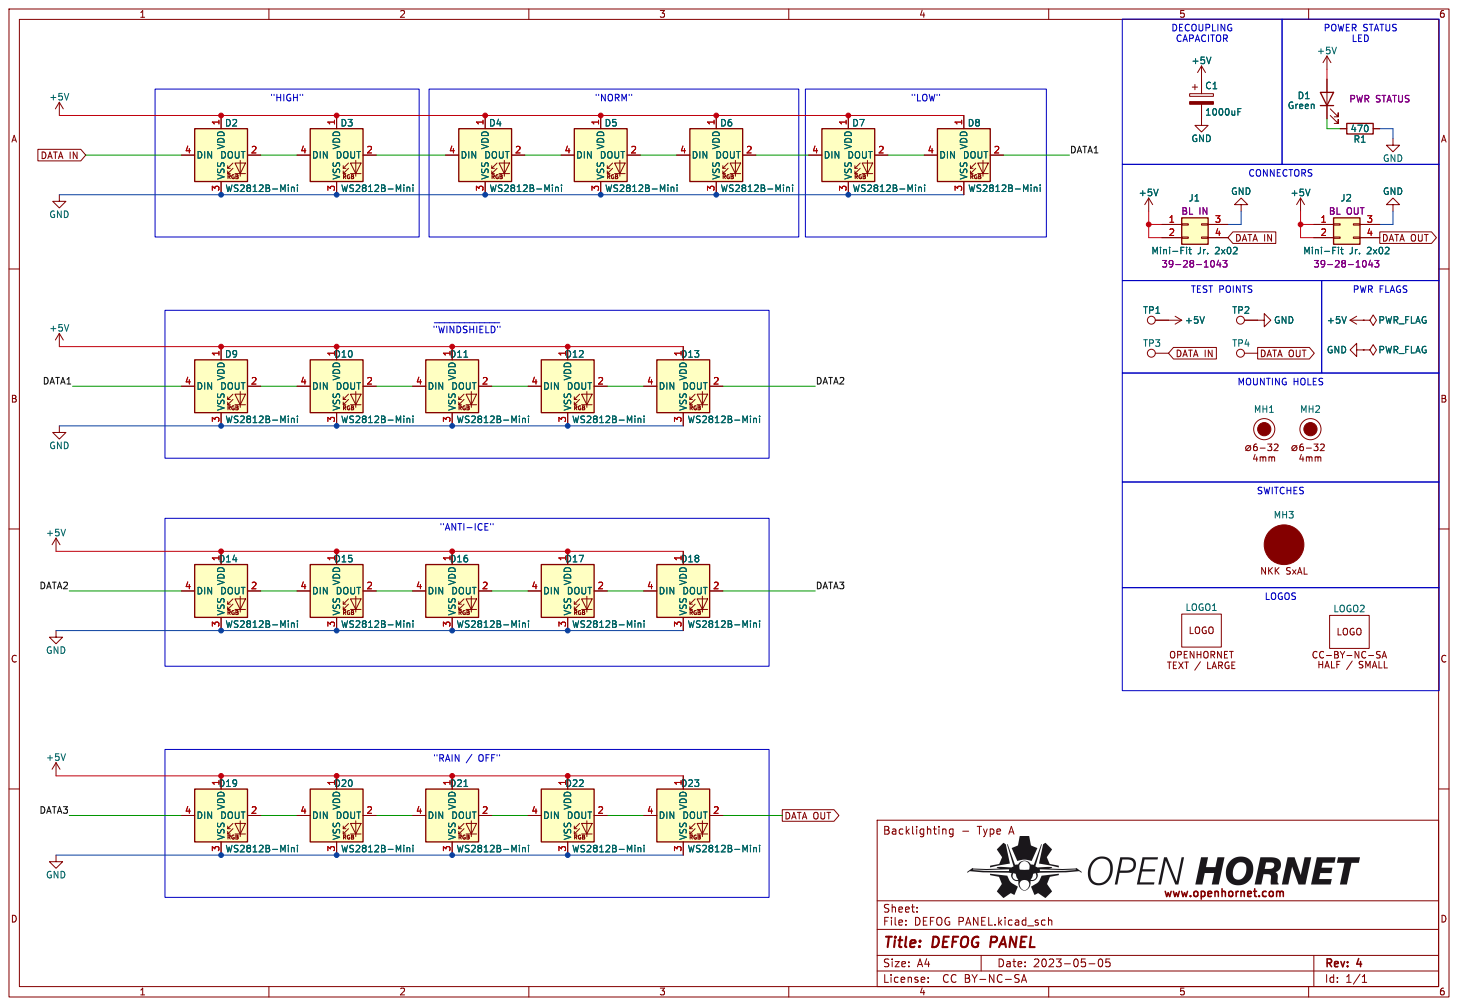
[picture p570: page 1]

3 DIN 4 D6WS2812B-Mini D1 Green PWR STATUS

3 DIN 4 D2WS2812B-Mini RGB VDD

3 DIN 4 D8WS2812B-Mini RGB VDD

3 DIN 4 D4WS2812B-Mini RGB VDD

3 DIN 4 D5WS2812B-Mini RGB VDD

3 DIN 4 D10WS2812B-Mini RGB VDD

3 DIN 4 GND J2 Mini-Fit Jr. 2x02

3 DIN 4 D13WS2812B-Mini DATA IN DATA OUT DATA IN DATA OUT DATA OUT

3 DIN 4 D9WS2812B-Mini RGB VDD

3 DIN 4 D11WS2812B-Mini RGB VDD

3 DIN 4 D12WS2812B-Mini RGB VDD

3 DIN 4 D20WS2812B-Mini RGB VDD

3 DIN 4 D17WS2812B-Mini RGB VDD
RGB VDD

3 DIN 4 D18WS2812B-Mini RGB VDD

Id: 1/1 Title: DEFOG PANEL

Size: A4 | | Rev: 4
License: CC | BY-NC-SA
