jrsteensen/OpenHornet/release/OHE_Electronics/OH5A6A1-13 - PCB, INTR LT PANEL/INTR LT PANEL.pdf

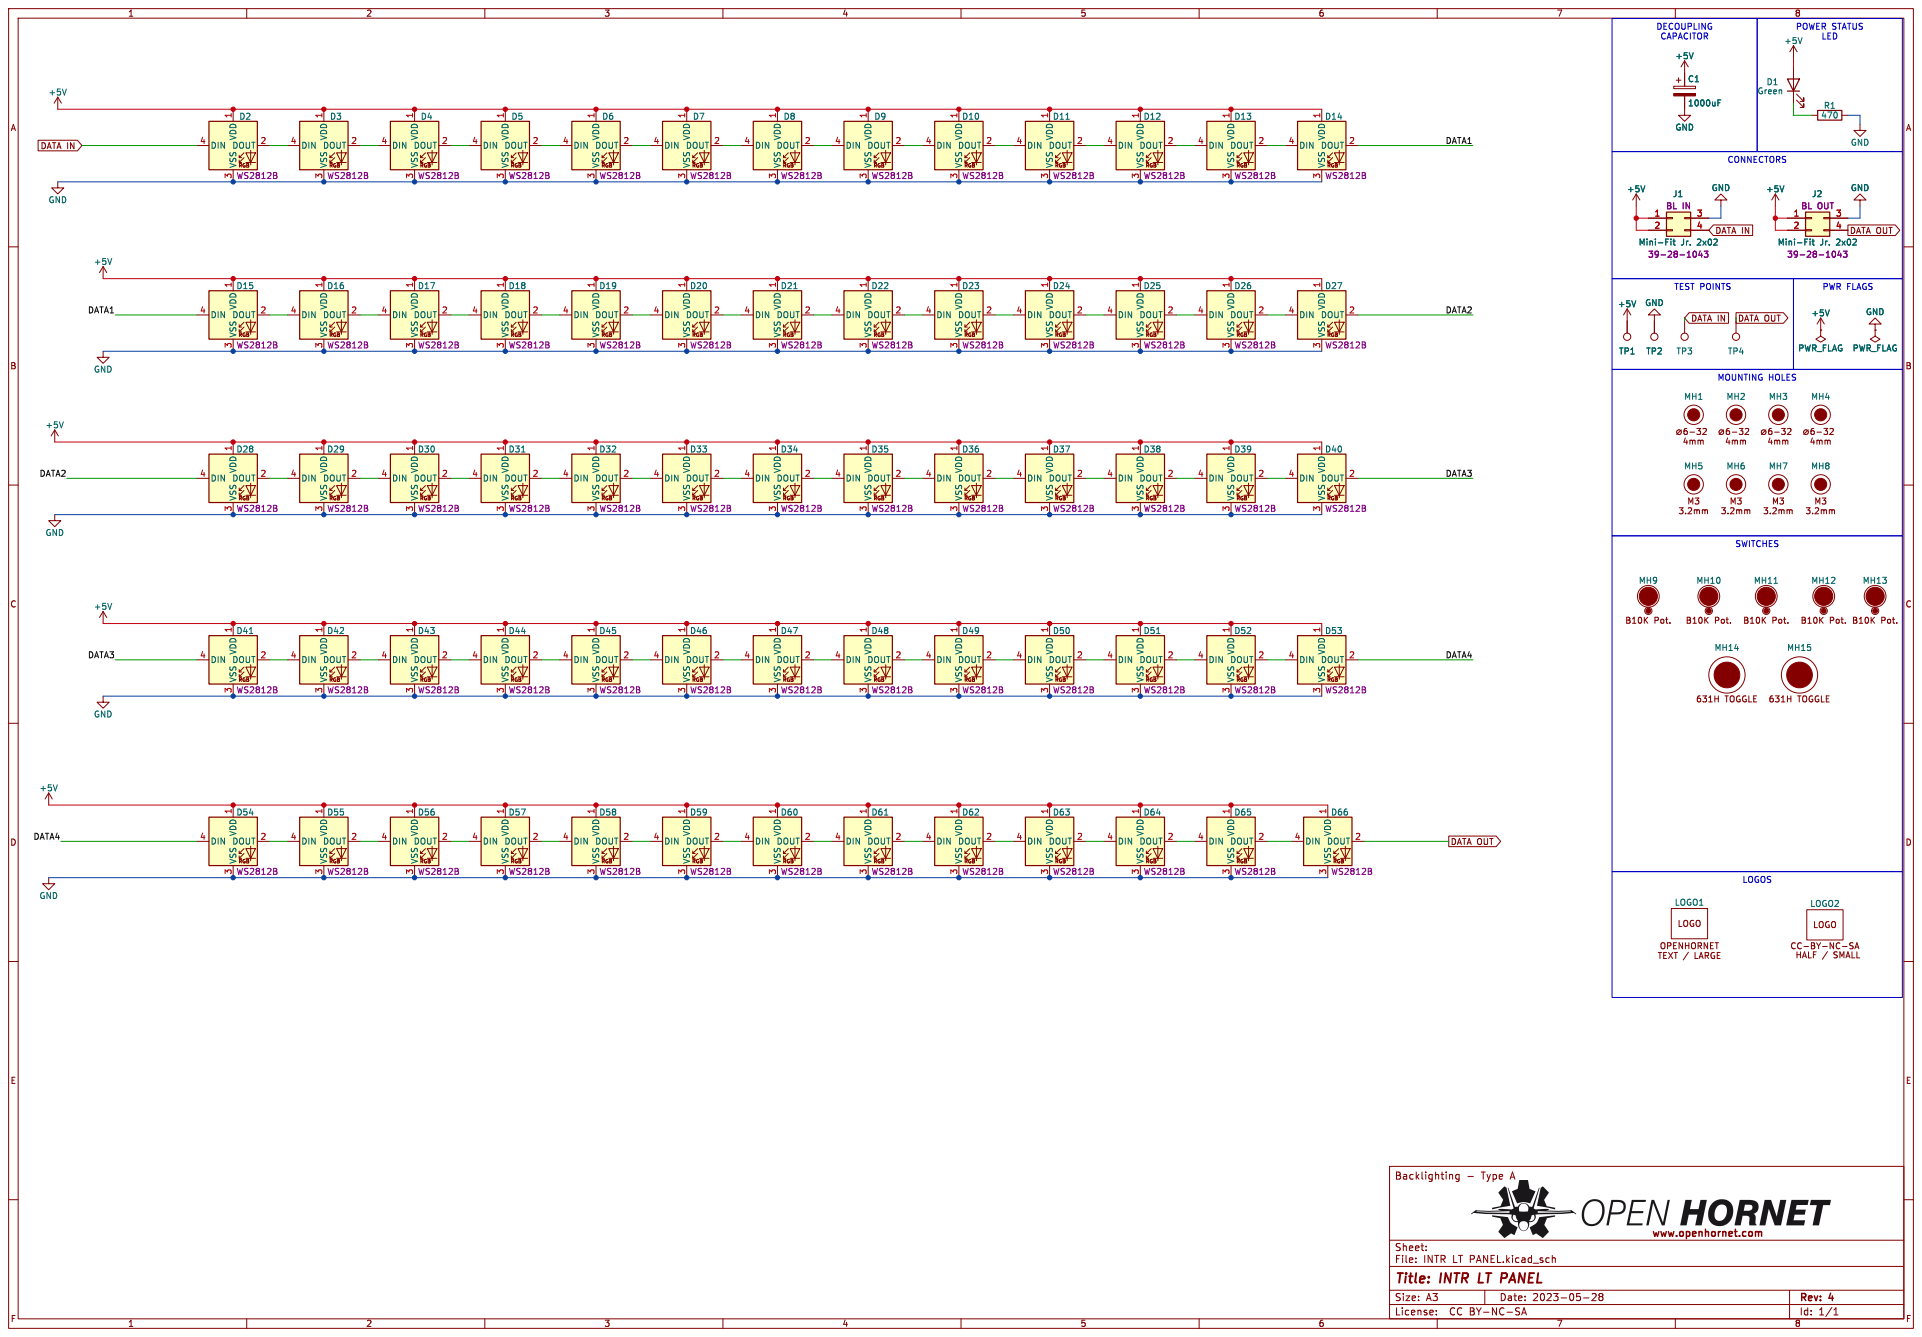
[picture p571: page 1]

Id: 1/1 Title: INTR LT PANEL

Size: A3 | | Rev: 4 | F Date: 2023-05-28
License: CC | BY-NC-SA
