jrsteensen/OpenHornet/release/OHE_Electronics/OH5A8A1-13 - PCB, SIM CONTROL PANEL/SIM CONTROL PANEL.pdf

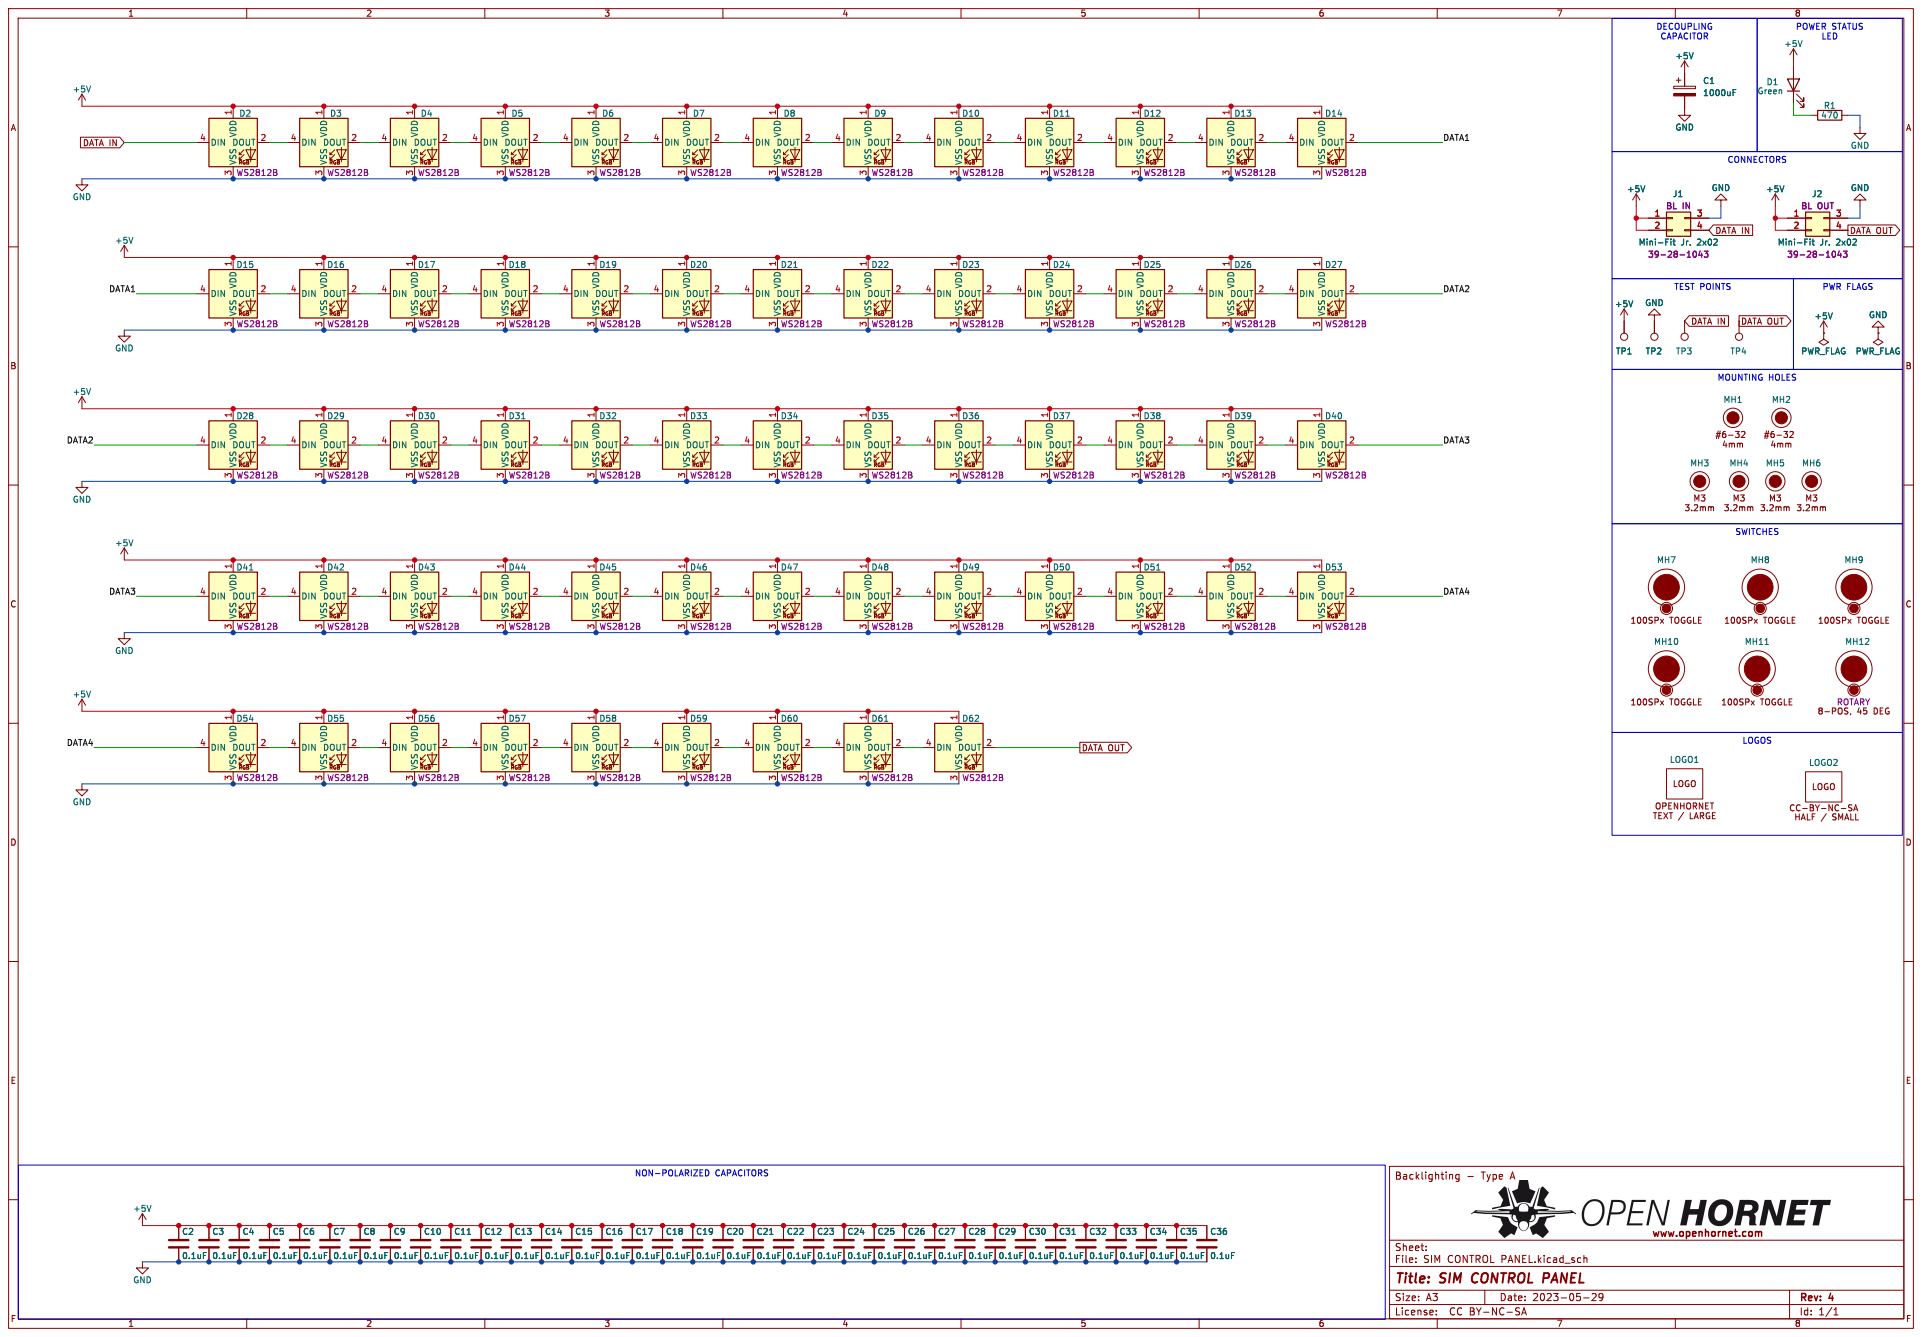
[picture p572: page 1]

3 DIN 4 D15 WS2812B DATA IN DATA OUT DATA IN

DATA OUT

Id: 1/1 Title: SIM CONTROL PANEL

Size: A3 | | Rev: 4 | F Date: 2023-05-29
License: CC | BY-NC-SA
