jrsteensen/OpenHornet/release/OHE_Electronics/OH5A9A1-16  - PCB, KY-58 PANEL/KY-58 PANEL.pdf

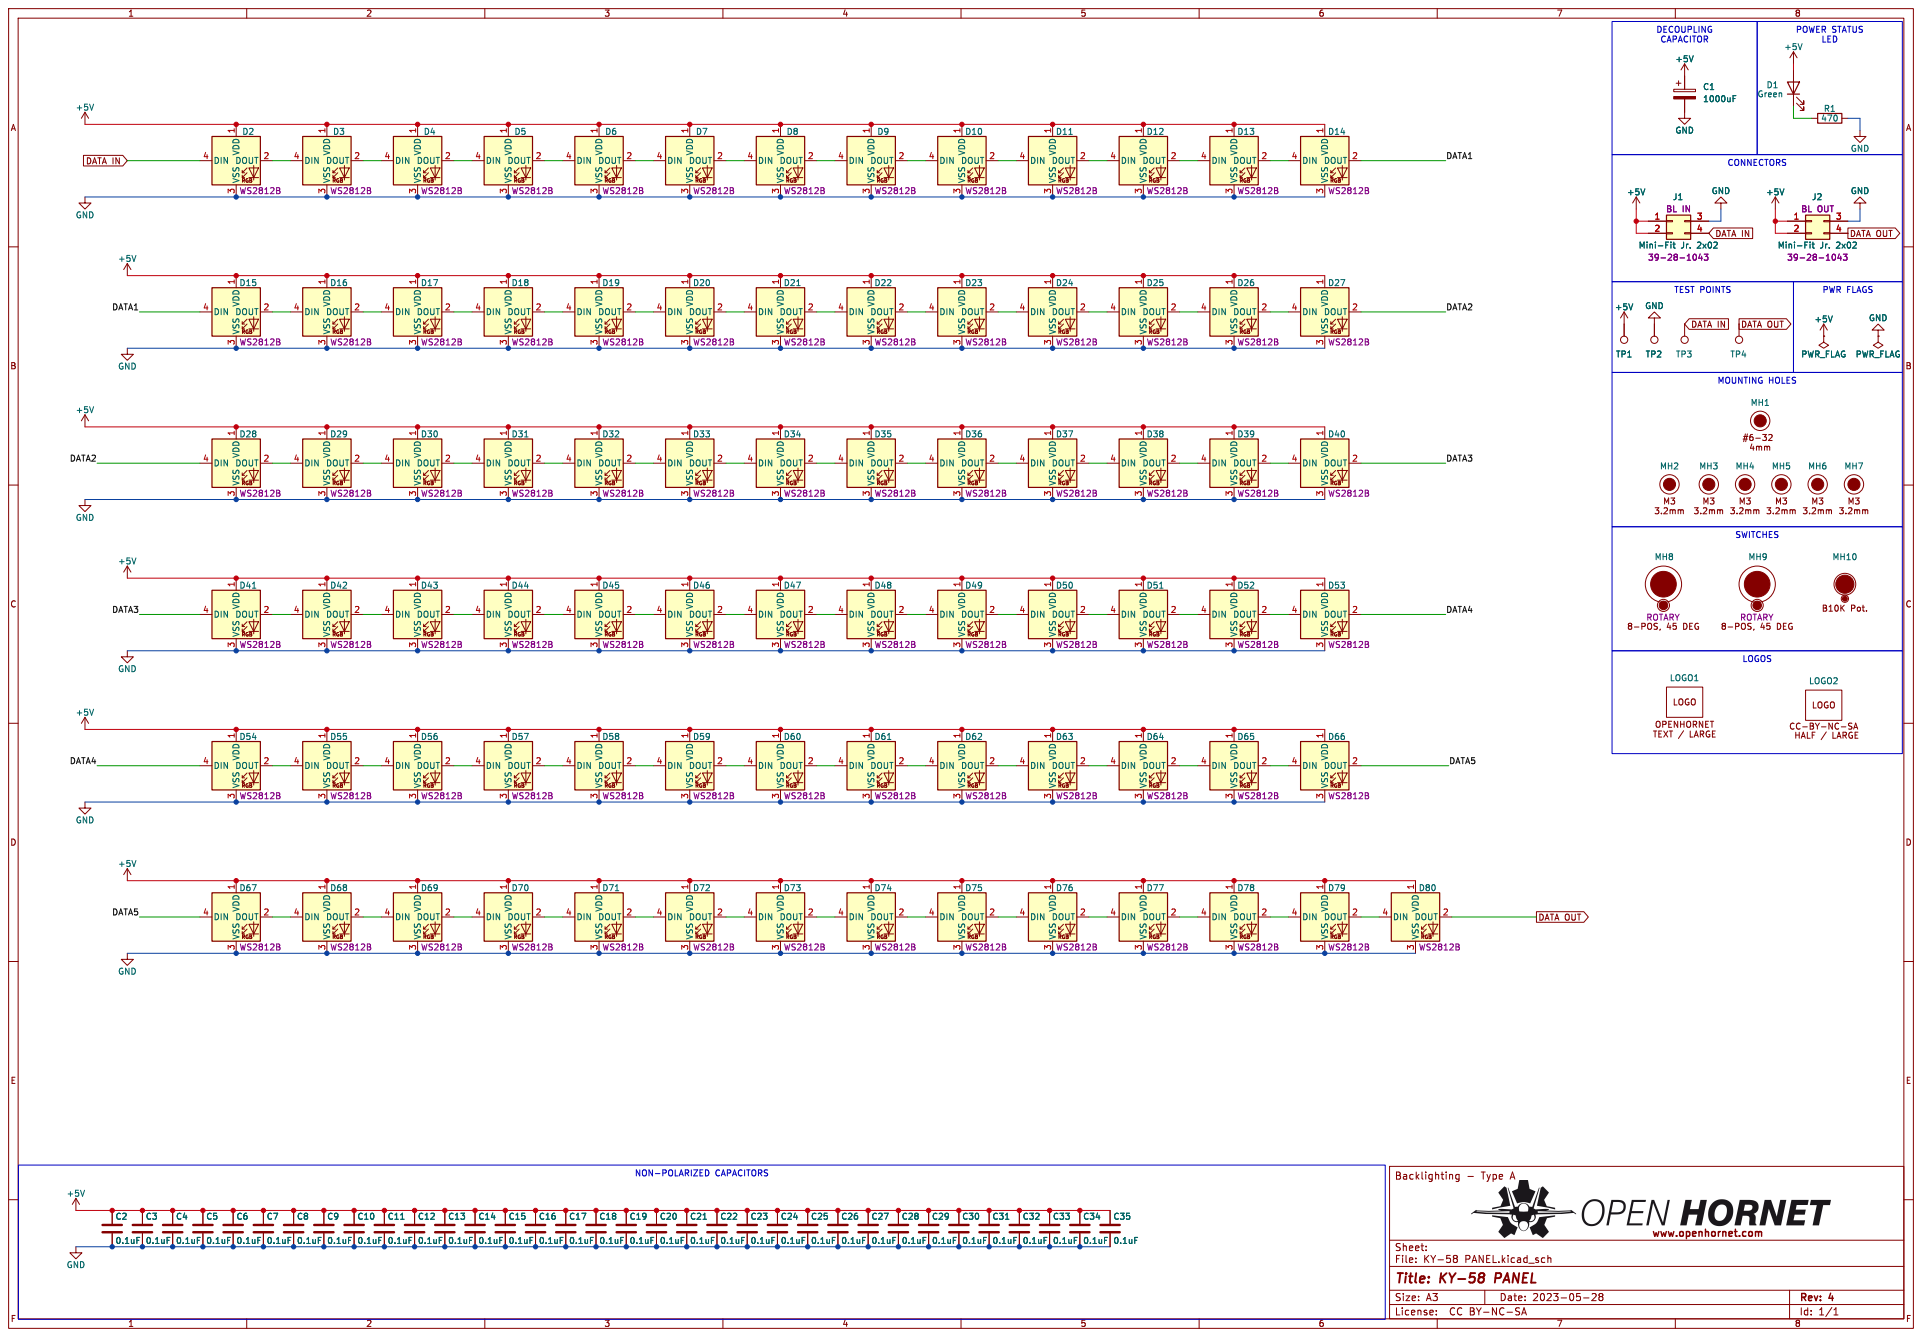
[picture p573: page 1]

Size: A3 | | Rev: 4 | F Date: 2023-05-28
License: CC | BY-NC-SA
