jrsteensen/OpenHornet/release/OHE_Electronics/OHC0007-100 - UTIL PHOTOSWITCH/Util Photoswitch.pdf

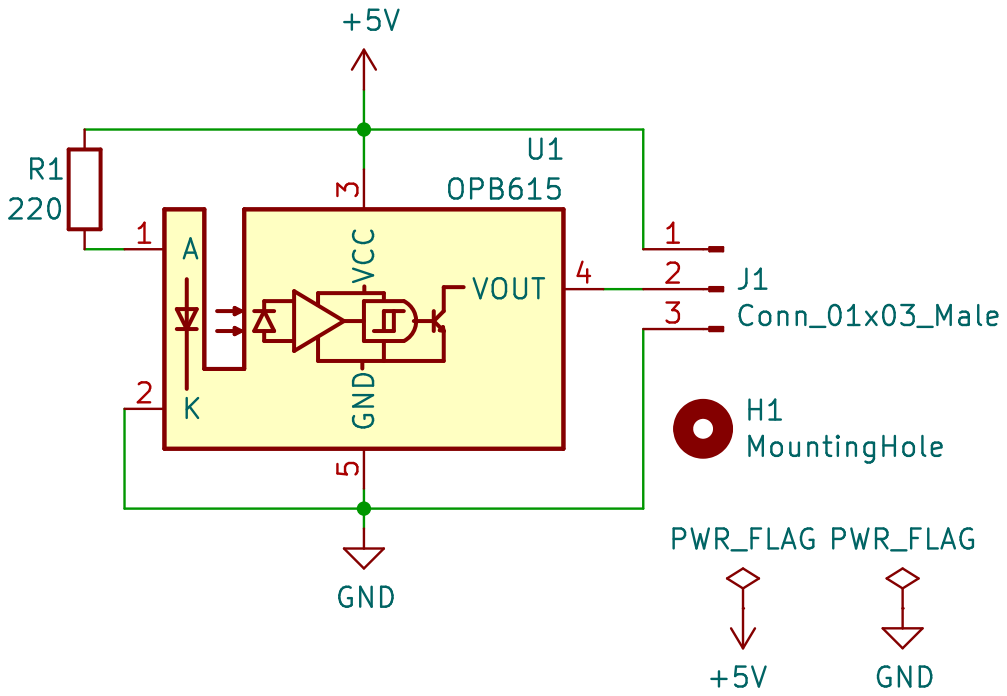
[picture p574: page 1]
