jrsteensen/OpenHornet/release/OHE_Electronics/OHC0007-14 - PCB, 2 IN GAUGE STEPPER/Analog Instruments.pdf

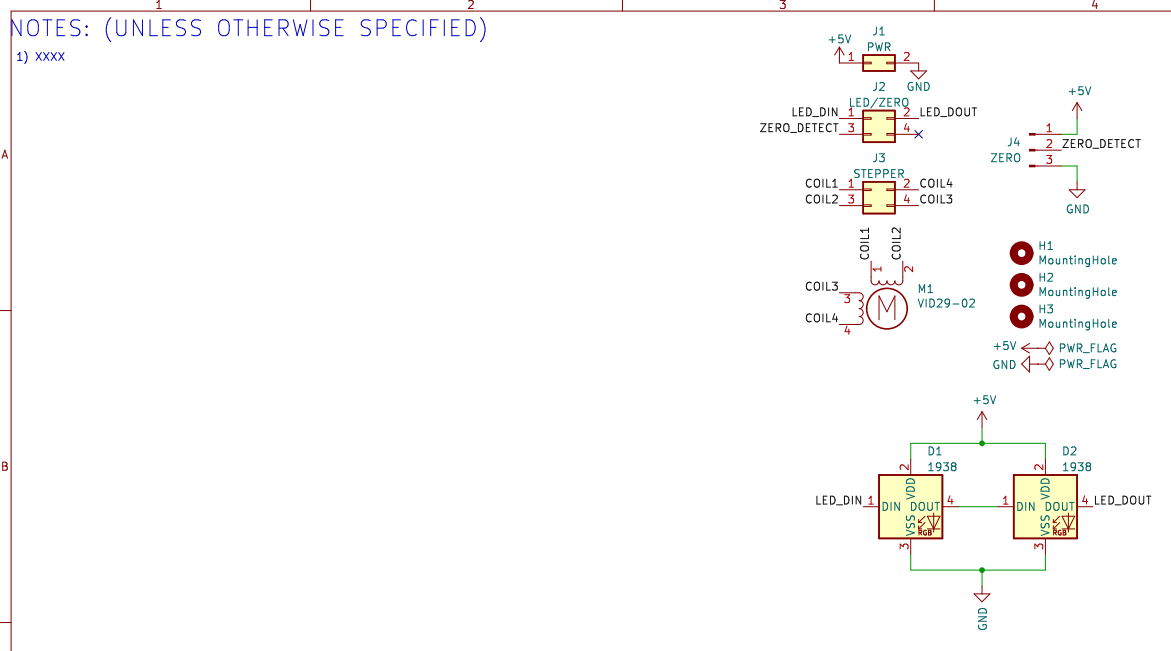
[picture p575: page 1]
