jrsteensen/OpenHornet/release/OHE_Electronics/OHC0015-10 - PCB, DDI_AMPCD_CONTROLLER/CONTROLLER_AMPCD DDI.pdf

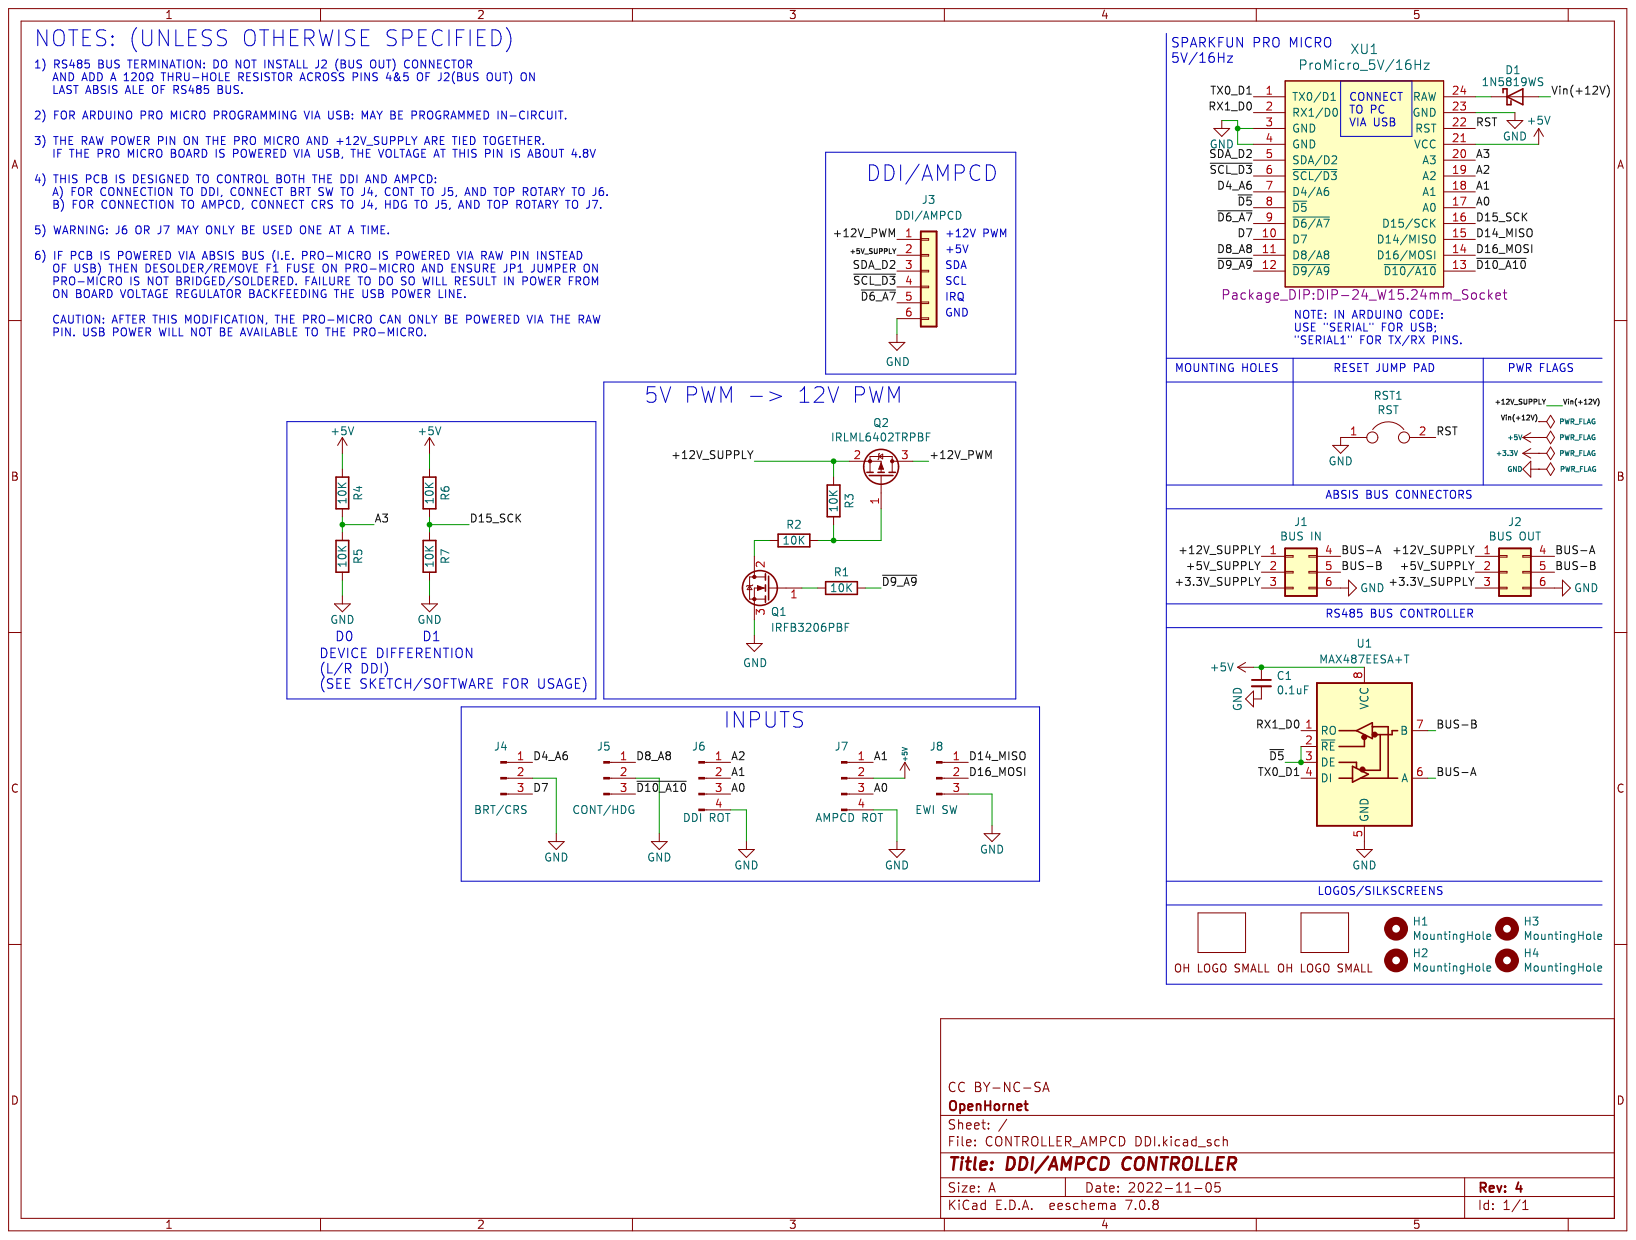
[picture p576: page 1]
