jrsteensen/OpenHornet/ECAD/PCBs/Backlight PCBs/Backlighting_Type A/HUD PANEL/HUD PANEL.kicad_pcb

## KiCad design ECAD/PCBs/Backlight PCBs/Backlighting_Type A/HUD PANEL/HUD PANEL.kicad_pcb (2026-04-08)

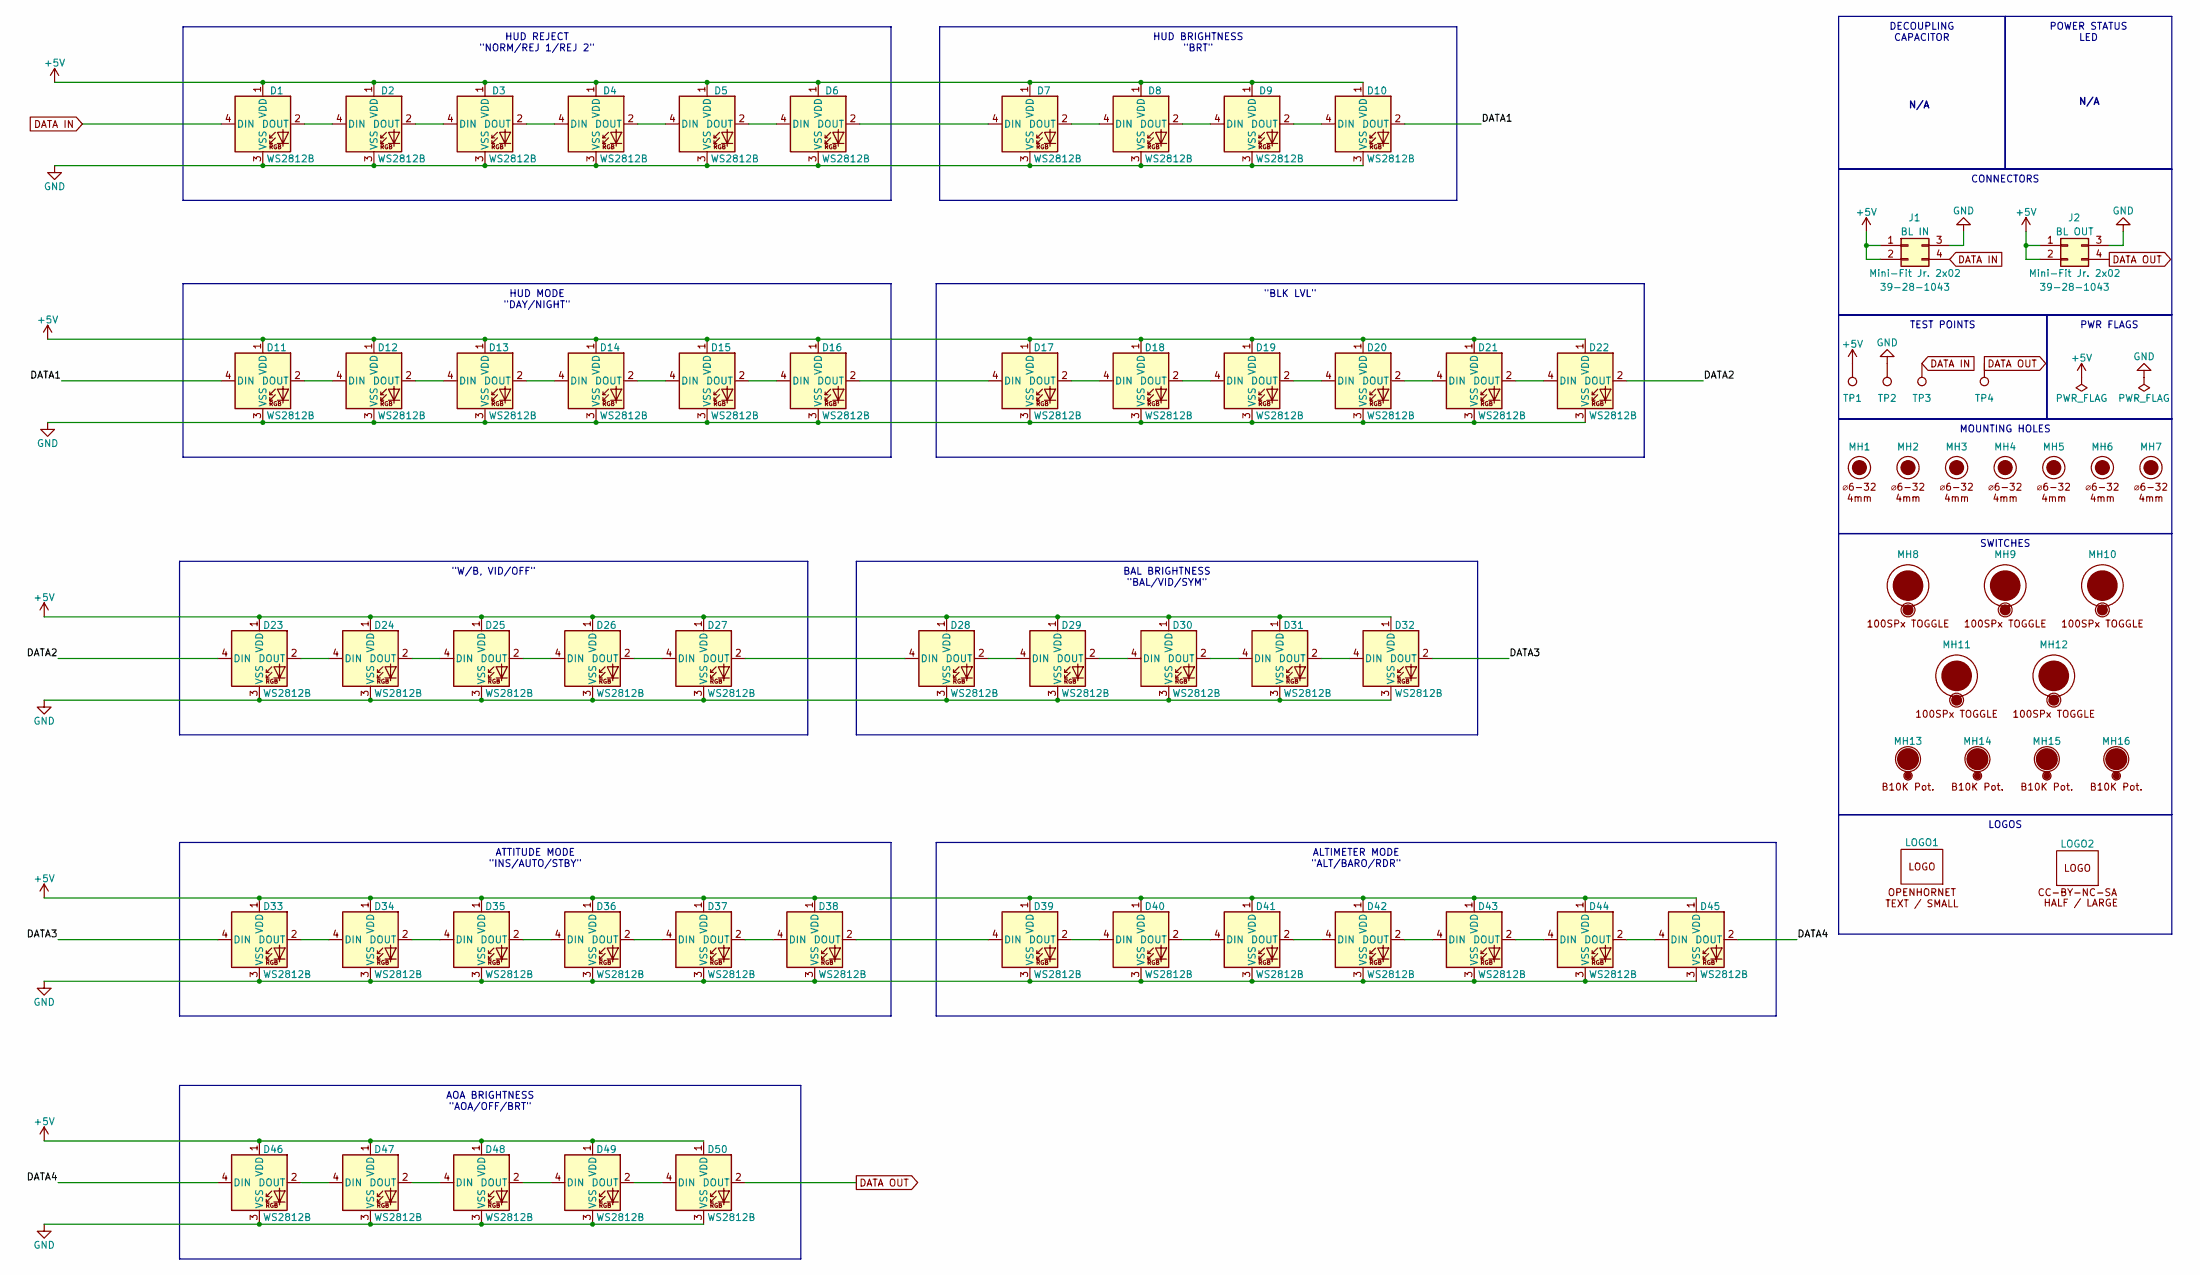
[picture p613: schematic HUD PANEL.kicad_sch]

Parts:
D1, D2, D3, D4, D5, D6, D7, D8, D9, D10, D11, D12, D13, D14, D15, D16, D17, D18, D19, D20, D21, D22, D23, D24, D25, D26, D27, D28, D29, D30, D31, D32, D33, D34, D35, D36, D37, D38, D39, D40, D41, D42, D43, D44, D45, D46, D47, D48, D49, D50: WS2812B; LED_WS2812B_PLCC4_5.0x5.0mm_P3.2mm; Manufacturer PN WS2812B; LCSC C2761795
J1, J2: Mini-Fit Jr. 2x02; Molex_Mini-Fit_Jr_5566-04A_2x02_P4.20mm_Vertical; Manufacturer PN 39-28-1043; LCSC C293502
LOGO1: LOGO; LOGO_OH_Text_Small
LOGO2: LOGO; LOGO_CC-BY-NC-SA_Half_Large
MH1, MH2, MH3, MH4, MH5, MH6, MH7: 6x32 / 4mm; MountingHole_6-32_PHS
MH8, MH9, MH10, MH11, MH12: Switch_100SPx; 100SPX_Toggle_13mm_x_18mm
MH13, MH14, MH15, MH16: Pot_B10K; BR10K_Pot_11mm_x_11mm; Manufacturer PN P0915N-FC20BR10K
TP1, TP2, TP3, TP4: TestPoint; TestPoint_THTPad_D1.5mm_Drill0.7mm

Connections:
+5V: D1.1 (VDD), D2.1 (VDD), D3.1 (VDD), D4.1 (VDD), D5.1 (VDD), D6.1 (VDD), D7.1 (VDD), D8.1 (VDD), D9.1 (VDD), D10.1 (VDD), D11.1 (VDD), D12.1 (VDD), D13.1 (VDD), D14.1 (VDD), D15.1 (VDD), D16.1 (VDD), D17.1 (VDD), D18.1 (VDD), D19.1 (VDD), D20.1 (VDD), D21.1 (VDD), D22.1 (VDD), D23.1 (VDD), D24.1 (VDD), D25.1 (VDD), D26.1 (VDD), D27.1 (VDD), D28.1 (VDD), D29.1 (VDD), D30.1 (VDD), D31.1 (VDD), D32.1 (VDD), D33.1 (VDD), D34.1 (VDD), D35.1 (VDD), D36.1 (VDD), D37.1 (VDD), D38.1 (VDD), D39.1 (VDD), D40.1 (VDD), D41.1 (VDD), D42.1 (VDD), D43.1 (VDD), D44.1 (VDD), D45.1 (VDD), D46.1 (VDD), D47.1 (VDD), D48.1 (VDD), D49.1 (VDD), D50.1 (VDD), J1.1, J1.2 (Pin_3), J2.1, J2.2 (Pin_3), TP1.1
/DATA1: D10.2 (DOUT), D11.4 (DIN)
/DATA2: D22.2 (DOUT), D23.4 (DIN)
/DATA3: D32.2 (DOUT), D33.4 (DIN)
/DATA4: D45.2 (DOUT), D46.4 (DIN)
DATA IN: D1.4 (DIN), J1.4, TP3.1
DATA OUT: D50.2 (DOUT), J2.4, TP4.1
GND: D1.3 (VSS), D2.3 (VSS), D3.3 (VSS), D4.3 (VSS), D5.3 (VSS), D6.3 (VSS), D7.3 (VSS), D8.3 (VSS), D9.3 (VSS), D10.3 (VSS), D11.3 (VSS), D12.3 (VSS), D13.3 (VSS), D14.3 (VSS), D15.3 (VSS), D16.3 (VSS), D17.3 (VSS), D18.3 (VSS), D19.3 (VSS), D20.3 (VSS), D21.3 (VSS), D22.3 (VSS), D23.3 (VSS), D24.3 (VSS), D25.3 (VSS), D26.3 (VSS), D27.3 (VSS), D28.3 (VSS), D29.3 (VSS), D30.3 (VSS), D31.3 (VSS), D32.3 (VSS), D33.3 (VSS), D34.3 (VSS), D35.3 (VSS), D36.3 (VSS), D37.3 (VSS), D38.3 (VSS), D39.3 (VSS), D40.3 (VSS), D41.3 (VSS), D42.3 (VSS), D43.3 (VSS), D44.3 (VSS), D45.3 (VSS), D46.3 (VSS), D47.3 (VSS), D48.3 (VSS), D49.3 (VSS), D50.3 (VSS), J1.3 (Pin_2), J2.3 (Pin_2), TP2.1
unnamed: D1.2 (DOUT), D2.4 (DIN)
unnamed: D2.2 (DOUT), D3.4 (DIN)
unnamed: D3.2 (DOUT), D4.4 (DIN)
unnamed: D4.2 (DOUT), D5.4 (DIN)
unnamed: D5.2 (DOUT), D6.4 (DIN)
unnamed: D6.2 (DOUT), D7.4 (DIN)
unnamed: D7.2 (DOUT), D8.4 (DIN)
unnamed: D8.2 (DOUT), D9.4 (DIN)
unnamed: D9.2 (DOUT), D10.4 (DIN)
unnamed: D11.2 (DOUT), D12.4 (DIN)
unnamed: D12.2 (DOUT), D13.4 (DIN)
unnamed: D13.2 (DOUT), D14.4 (DIN)
unnamed: D14.2 (DOUT), D15.4 (DIN)
unnamed: D15.2 (DOUT), D16.4 (DIN)
unnamed: D16.2 (DOUT), D17.4 (DIN)
unnamed: D17.2 (DOUT), D18.4 (DIN)
unnamed: D18.2 (DOUT), D19.4 (DIN)
unnamed: D19.2 (DOUT), D20.4 (DIN)
unnamed: D20.2 (DOUT), D21.4 (DIN)
unnamed: D21.2 (DOUT), D22.4 (DIN)
unnamed: D23.2 (DOUT), D24.4 (DIN)
unnamed: D24.2 (DOUT), D25.4 (DIN)
unnamed: D25.2 (DOUT), D26.4 (DIN)
unnamed: D26.2 (DOUT), D27.4 (DIN)
unnamed: D27.2 (DOUT), D28.4 (DIN)
unnamed: D28.2 (DOUT), D29.4 (DIN)
unnamed: D29.2 (DOUT), D30.4 (DIN)
unnamed: D30.2 (DOUT), D31.4 (DIN)
unnamed: D31.2 (DOUT), D32.4 (DIN)
unnamed: D33.2 (DOUT), D34.4 (DIN)
unnamed: D34.2 (DOUT), D35.4 (DIN)
unnamed: D35.2 (DOUT), D36.4 (DIN)
unnamed: D36.2 (DOUT), D37.4 (DIN)
unnamed: D37.2 (DOUT), D38.4 (DIN)
unnamed: D38.2 (DOUT), D39.4 (DIN)
unnamed: D39.2 (DOUT), D40.4 (DIN)
unnamed: D40.2 (DOUT), D41.4 (DIN)
unnamed: D41.2 (DOUT), D42.4 (DIN)
unnamed: D42.2 (DOUT), D43.4 (DIN)
unnamed: D43.2 (DOUT), D44.4 (DIN)
unnamed: D44.2 (DOUT), D45.4 (DIN)
unnamed: D46.2 (DOUT), D47.4 (DIN)
unnamed: D47.2 (DOUT), D48.4 (DIN)
unnamed: D48.2 (DOUT), D49.4 (DIN)
unnamed: D49.2 (DOUT), D50.4 (DIN)

Notes on the sheet:
PWR FLAGS
CONNECTORS
"W/B, VID/OFF"
"BLK LVL"
HUD BRIGHTNESS "BRT"
ATTITUDE MODE "INS/AUTO/STBY"
DECOUPLING CAPACITOR
ALTIMETER MODE "ALT/BARO/RDR"
MOUNTING HOLES
SWITCHES
LOGOS
HUD MODE "DAY/NIGHT"
POWER STATUS LED
AOA BRIGHTNESS "AOA/OFF/BRT"
BAL BRIGHTNESS "BAL/VID/SYM"
HUD REJECT "NORM/REJ 1/REJ 2"
TEST POINTS
N/A

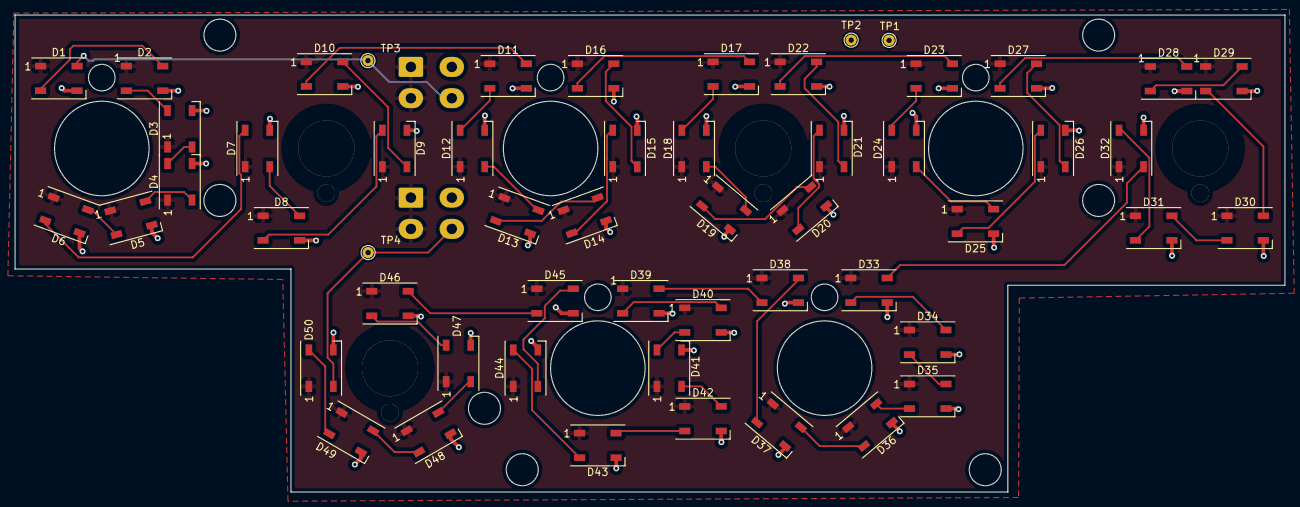
[picture p614: board HUD PANEL.kicad_pcb from above]

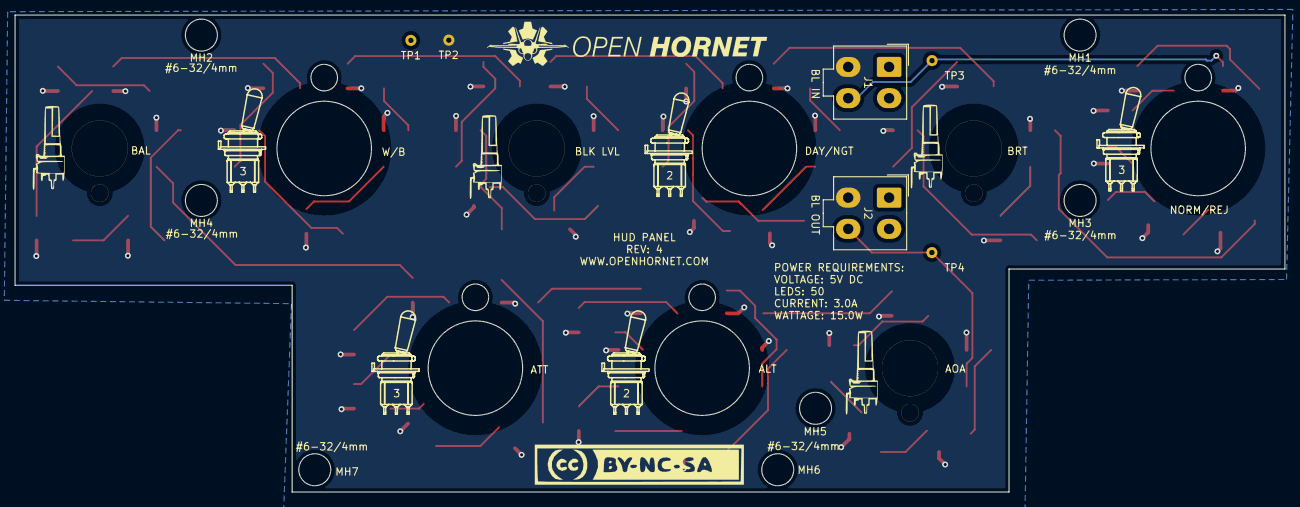
[picture p615: board HUD PANEL.kicad_pcb from below]

Board: 2 copper layers, 170.7 x 64.1 mm, 83 parts (20 on the bottom side), 53 nets.

Other parts of the board:
LOGO3, LOGO6, LOGO11: LOGO; 100SP3_Toggle_Silkscreen
LOGO4, LOGO5, LOGO9, LOGO10: LOGO; BR10K_Pot_Silkscreen
LOGO7, LOGO8: LOGO; 100SP1_Toggle_Silkscreen
