jrsteensen/OpenHornet/ECAD/PCBs/Functional PCBs/HOTAS_Hat Switch Breakout/HOTAS_Hat Switch Breakout.kicad_pcb

## KiCad design ECAD/PCBs/Functional PCBs/HOTAS_Hat Switch Breakout/HOTAS_Hat Switch Breakout.kicad_pcb (2026-04-08)

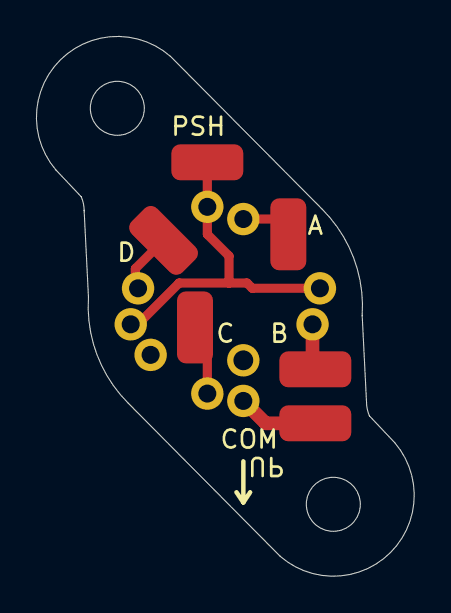
[picture p616: board HOTAS_Hat Switch Breakout.kicad_pcb from above]

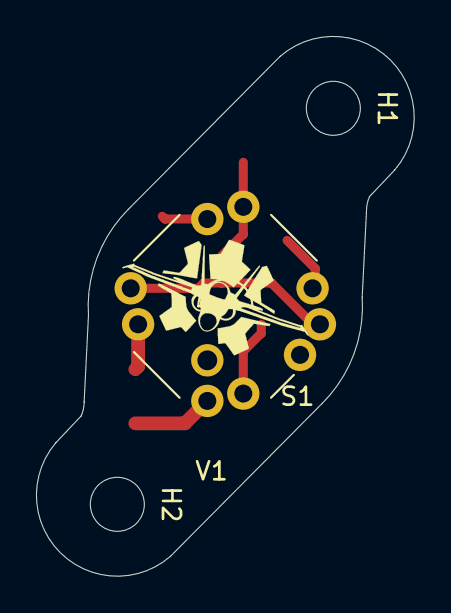
[picture p617: board HOTAS_Hat Switch Breakout.kicad_pcb from below]

Board: 2 copper layers, 21.0 x 30.0 mm, 9 parts (3 on the bottom side), 6 nets.

Parts:
H1, H2: MountingHole; MountingHole_3mm
J1, J2, J3, J4, J5, J6: Conn_01x01; SolderWirePad_1x01_SMD_2x4mm
S1: 8WayHat_CenterPush; RKJXM10

Connections:
unnamed: J1.1, S1.A
unnamed: J2.1, S1.B
unnamed: J3.1, S1.C
unnamed: J4.1, S1.D
unnamed: J5.1, S1.PUSH1, S1.PUSH2, S1.PUSH3
unnamed: J6.1, S1.COM
