jrsteensen/OpenHornet/ECAD/PCBs/Functional PCBs/CONTROLLER_Throttle/CONTROLLER_Throttle.kicad_pcb

## KiCad design ECAD/PCBs/Functional PCBs/CONTROLLER_Throttle/CONTROLLER_Throttle.kicad_pcb (2024-02-26)

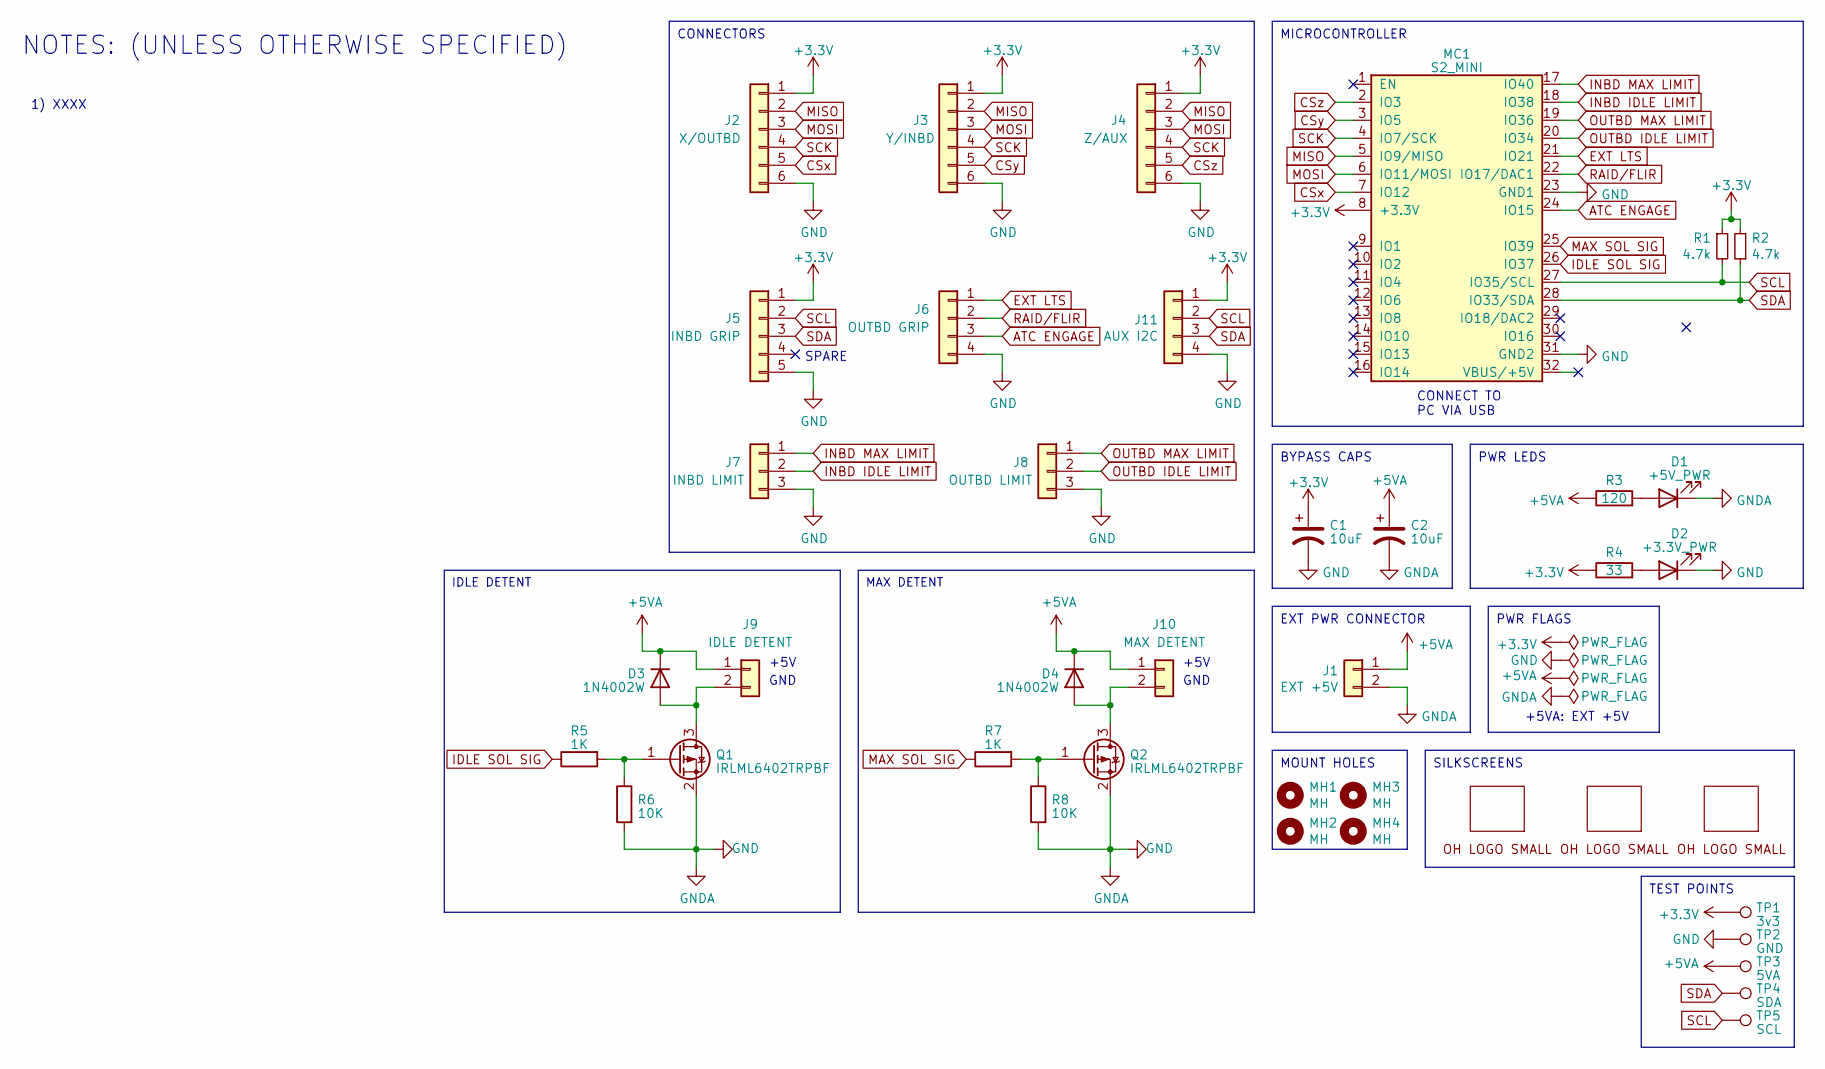
[picture p620: schematic CONTROLLER_Throttle.kicad_sch, OH Flight Stick Controller]

Parts:
C1, C2: 10uF; C_1206_3216Metric; LCSC C13585
D1: +5V_PWR; LED_0603_1608Metric_Pad1.05x0.95mm_HandSolder; LCSC C72043
D2: +3.3V_PWR; LED_0603_1608Metric_Pad1.05x0.95mm_HandSolder; LCSC C72043
D3, D4: 1N4002W; D_SOD-123F; LCSC C169542
J1: EXT +5V; PinHeader_1x02_P2.54mm_Vertical
J2: X/OUTBD; JST_PH_S6B-PH-K_1x06_P2.00mm_Horizontal; LCSC C265105
J3: Y/INBD; JST_PH_S6B-PH-K_1x06_P2.00mm_Horizontal; LCSC C265105
J4: Z/AUX; JST_PH_S6B-PH-K_1x06_P2.00mm_Horizontal; LCSC C265105
J5: INBD GRIP; JST_PH_B5B-PH-K_1x05_P2.00mm_Vertical
J6: OUTBD GRIP; JST_PH_B4B-PH-K_1x04_P2.00mm_Vertical
J7: INBD LIMIT; JST_PH_B3B-PH-K_1x03_P2.00mm_Vertical
J8: OUTBD LIMIT; JST_PH_B3B-PH-K_1x03_P2.00mm_Vertical
J9: IDLE DETENT; JST_PH_B2B-PH-K_1x02_P2.00mm_Vertical
J10: MAX DETENT; JST_PH_B2B-PH-K_1x02_P2.00mm_Vertical
J11: AUX I2C; PinHeader_1x04_P2.54mm_Vertical
LOGO1: OpenHornetLogoSmall; OH_LOGO_37.7mm_5.9mm
LOGO2: OpenHornetLogoSmall; CC-BY-NC-SA-Small
LOGO3: OpenHornetLogoSmall; OH_LOGO_ONLY_11x6mm
MC1: S2_MINI
MH1, MH2, MH3, MH4: MH; MountingHole_2.5mm
Q1, Q2: IRLML6402TRPBF; SOT-23; LCSC C2593
R1, R2: 4.7k; R_0603_1608Metric; LCSC C23162
R3: 120; R_0603_1608Metric; LCSC C22787
R4: 33; R_0402_1005Metric; LCSC C25105
R5, R7: 1K; R_0805_2012Metric_Pad1.20x1.40mm_HandSolder; LCSC C17513
R6, R8: 10K; R_0603_1608Metric_Pad0.98x0.95mm_HandSolder; LCSC C25804
TP1: 3v3; TestPoint_THTPad_D1.5mm_Drill0.7mm
TP2: GND; TestPoint_THTPad_D1.5mm_Drill0.7mm
TP3: 5VA; TestPoint_THTPad_D1.5mm_Drill0.7mm
TP4: SDA; TestPoint_THTPad_D1.5mm_Drill0.7mm
TP5: SCL; TestPoint_THTPad_D1.5mm_Drill0.7mm

Connections:
+3.3V: C1.1, J2.1, J3.1, J4.1, J5.1, J11.1, MC1.8 (+3.3V), R1.1, R2.2, R4.1, TP1.1
+5VA: C2.1, D3.1 (K), D4.1 (K), J1.1, J9.1, J10.1, R3.1, TP3.1
ATC ENGAGE: J6.3, MC1.24 (IO15)
CSx: J2.5, MC1.7 (IO12)
CSy: J3.5, MC1.3 (IO5)
CSz: J4.5, MC1.2 (IO3)
EXT LTS: J6.1, MC1.21 (IO21)
GND: C1.2, C2.2, D1.1 (K), D2.1 (K), J1.2, J2.6, J3.6, J4.6, J5.5, J6.4, J7.3, J8.3, J11.4, MC1.23 (GND1), MC1.31 (GND2), Q1.2 (S), Q2.2 (S), R6.2, R8.2, TP2.1
IDLE SOL SIG: MC1.26 (IO37), R5.1
INBD IDLE LIMIT: J7.2, MC1.18 (IO38)
INBD MAX LIMIT: J7.1, MC1.17 (IO40)
MAX SOL SIG: MC1.25 (IO39), R7.1
MISO: J2.2, J3.2, J4.2, MC1.5 (IO9/MISO)
MOSI: J2.3, J3.3, J4.3, MC1.6 (IO11/MOSI)
unnamed: D1.2 (A), R3.2
unnamed: D2.2 (A), R4.2
unnamed: D3.2 (A), J9.2, Q1.3 (D)
unnamed: D4.2 (A), J10.2, Q2.3 (D)
unnamed: Q1.1 (G), R5.2, R6.1
unnamed: Q2.1 (G), R7.2, R8.1
OUTBD IDLE LIMIT: J8.2, MC1.20 (IO34)
OUTBD MAX LIMIT: J8.1, MC1.19 (IO36)
RAID/FLIR: J6.2, MC1.22 (IO17/DAC1)
SCK: J2.4, J3.4, J4.4, MC1.4 (IO7/SCK)
SCL: J5.2, J11.2, MC1.27 (IO35/SCL), R1.2, TP5.1
SDA: J5.3, J11.3, MC1.28 (IO33/SDA), R2.1, TP4.1

Notes on the sheet:
TEST POINTS
CONNECTORS
EXT PWR CONNECTOR
MICROCONTROLLER
MAX DETENT
SILKSCREENS
IDLE DETENT
MOUNT HOLES
PWR LEDS
PWR FLAGS
BYPASS CAPS
+5VA: EXT +5V
SPARE
+5V
CONNECT TO PC VIA USB
GND
1) XXXX
NOTES: (UNLESS OTHERWISE SPECIFIED)

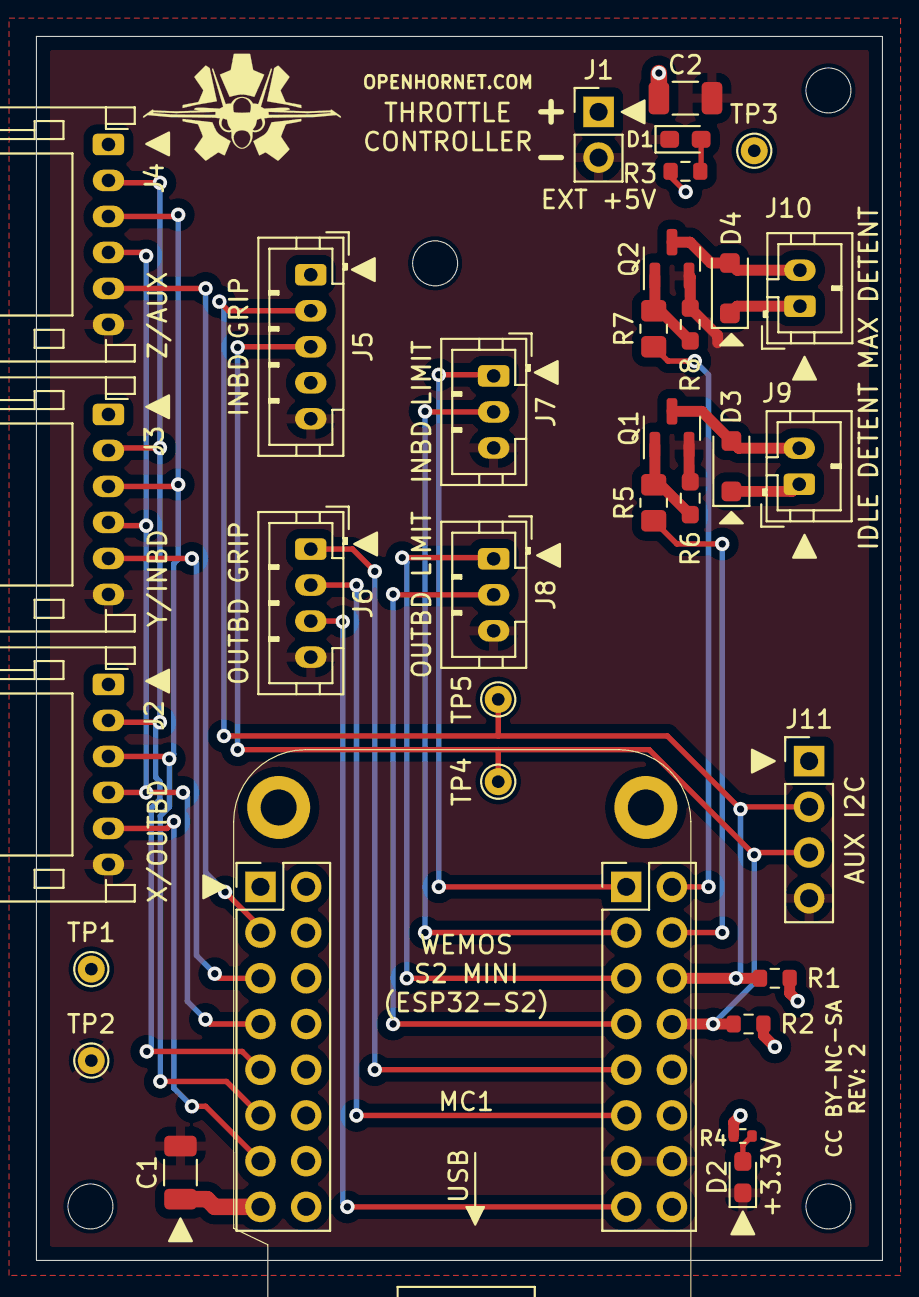
[picture p621: board CONTROLLER_Throttle.kicad_pcb from above]

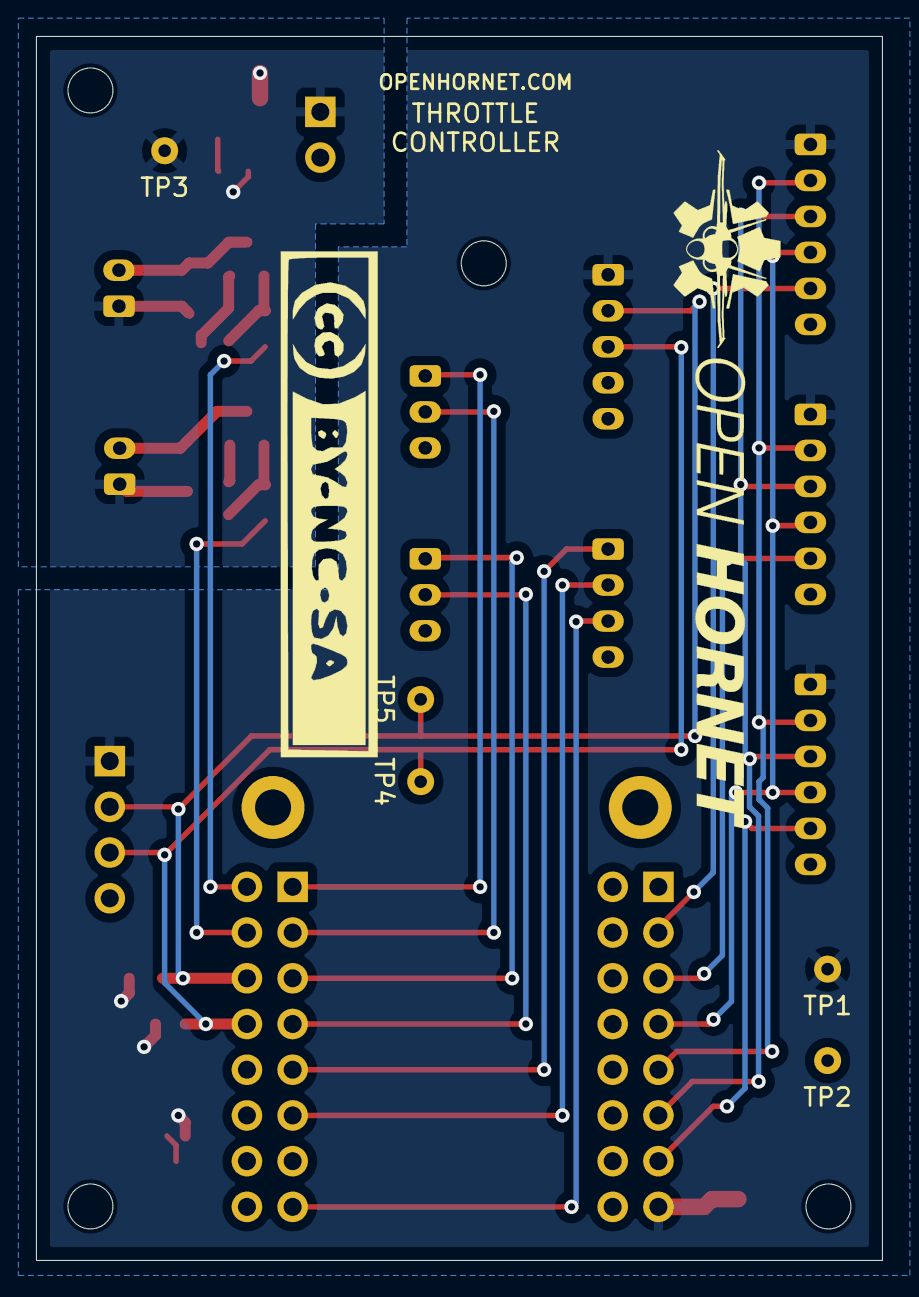
[picture p622: board CONTROLLER_Throttle.kicad_pcb from below]

Board: 2 copper layers, 47.0 x 68.0 mm, 40 parts (2 on the bottom side), 26 nets.
