jrsteensen/OpenHornet/ECAD/PCBs/Functional PCBs/CONTROLLER_Standby Instrument/CONTROLLER_Standby Instrument.kicad_pcb

## KiCad design ECAD/PCBs/Functional PCBs/CONTROLLER_Standby Instrument/CONTROLLER_Standby Instrument.kicad_pcb (2024-02-26)

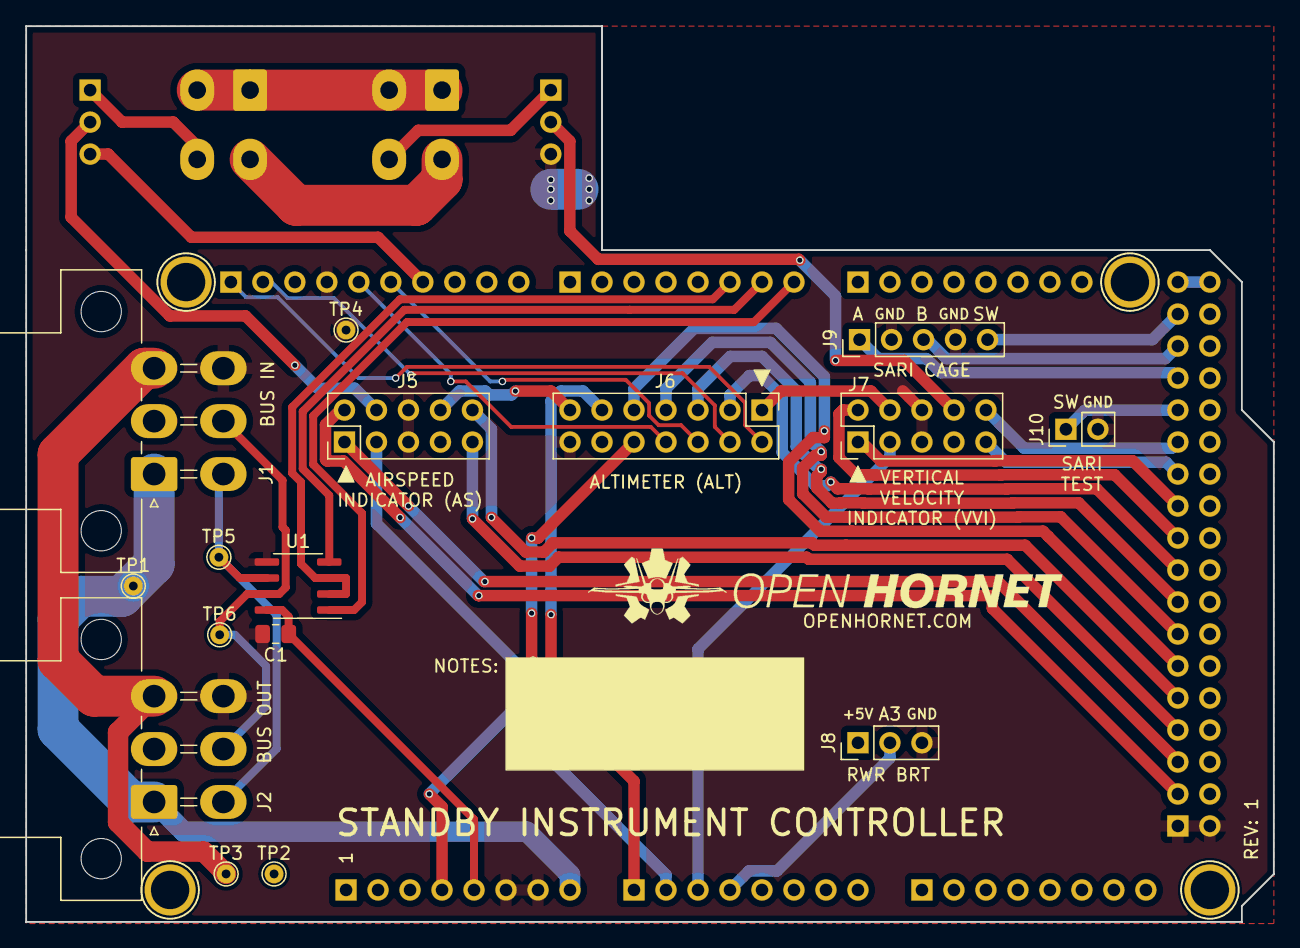
[picture p623: board CONTROLLER_Standby Instrument.kicad_pcb from above]

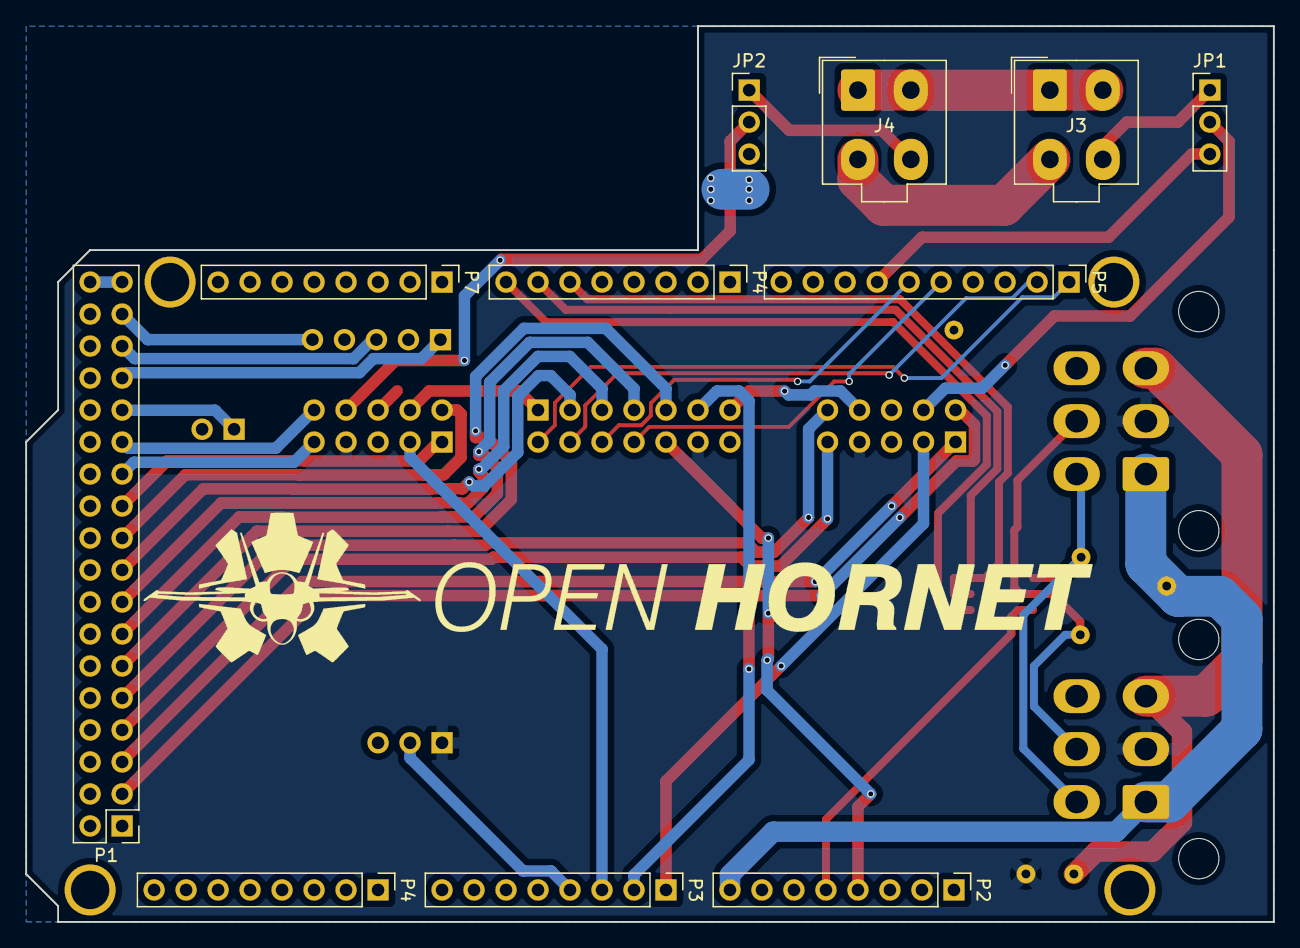
[picture p624: board CONTROLLER_Standby Instrument.kicad_pcb from below]

Board: 2 copper layers, 99.1 x 71.1 mm, 31 parts (11 on the bottom side), 45 nets.

Parts:
C1: 0.1uF; C_0805_2012Metric_Pad1.18x1.45mm_HandSolder
J1: BUS IN; Molex_Mini-Fit_Jr_5569-06A1_2x03_P4.20mm_Horizontal
J2: BUS OUT; Molex_Mini-Fit_Jr_5569-06A1_2x03_P4.20mm_Horizontal
J3: BL IN; Molex_Mini-Fit_Jr_5566-04A_2x02_P4.20mm_Vertical
J4: BL OUT; Molex_Mini-Fit_Jr_5566-04A_2x02_P4.20mm_Vertical
J5: AIRSPEED; PinHeader_2x05_P2.54mm_Vertical
J6: ALTIMETER; PinHeader_2x07_P2.54mm_Vertical
J7: VVI; PinHeader_2x05_P2.54mm_Vertical
J8: RWR_BRT; PinHeader_1x03_P2.54mm_Vertical
J9: SARI_CAGE; PinHeader_1x05_P2.54mm_Vertical
J10: SARI_TEST; PinHeader_1x02_P2.54mm_Vertical
JP1: BL_DIN_SEL; PinHeader_1x03_P2.54mm_Vertical
JP2: BL_DOUT_SEL; PinHeader_1x03_P2.54mm_Vertical
MK1, MK3, MK4, MK4#2: MH; Arduino_1pin
P1: Digital; PinHeader_2x18_P2.54mm_Vertical
P2: Power; PinHeader_1x08_P2.54mm_Vertical
P3, P4: Analog; PinHeader_1x08_P2.54mm_Vertical
P4#2: PWM; PinHeader_1x08_P2.54mm_Vertical
P5: PWM; PinHeader_1x10_P2.54mm_Vertical
P7: Communication; PinHeader_1x08_P2.54mm_Vertical
TP1: TP-12; TestPoint_THTPad_D1.5mm_Drill0.7mm
TP2: TP-5V; TestPoint_THTPad_D1.5mm_Drill0.7mm
TP3: TP-3.3V; TestPoint_THTPad_D1.5mm_Drill0.7mm
TP4: TP-GND; TestPoint_THTPad_D1.5mm_Drill0.7mm
TP5: TP-A; TestPoint_THTPad_D1.5mm_Drill0.7mm
TP6: TP-B; TestPoint_THTPad_D1.5mm_Drill0.7mm
U1: MAX487EESA+T; SOIC-8_3.9x4.9mm_P1.27mm

Connections:
+3V3: J6.10, P2.4
+5V: C1.1, P2.5, U1.8
+5VD: P1.35, P1.36
/0(Rx0): P4#2.8, U1.1
/1(Tx0): P4#2.7, U1.4
/2(**): P4#2.6, U1.2, U1.3
/11(**): JP1.3, P5.7
/12(**): J6.6, P5.6
/13(**): J6.8, P5.5
/22: J9.5, P1.33
/24: J9.3, P1.31
/26: J9.1, P1.29
/28: J10.1, P1.27
/30: J7.10, P1.25
/32: J7.9, P1.23
/34: J7.1, P1.21
/36: J7.2, P1.19
/38: J6.3, P1.17
/40: J6.5, P1.15
/42: J6.7, P1.13
/44: J6.9, P1.11
/46: J5.10, P1.9
/48: J5.9, P1.7
/50(MISO): J5.1, P1.5
/52(SCK): J5.2, P1.3
/+3.3V_SUPPLY: J1.3, J2.3, TP3.1
/+5V_SUPPLY: J1.2, J2.2, J5.7, J6.12, J7.7, J8.1, TP2.1
/+12V_SUPPLY: J1.1, J2.1, P2.8, TP1.1
/A0: J5.3, P3.1
/A1: J6.11, P3.2
/A2: J7.3, P3.3
/A3: J8.2, P3.4
/BUS-A: J1.4, J2.4, TP5.1, U1.6
/BUS-B: J1.5, J2.5, TP6.1, U1.7
/DATAIN: J3.4, JP1.1
/DATAOUT: J4.4, JP2.1
/LED+5V: J3.1, J3.2, J4.1, J4.2
/LEDGND: J3.3, J4.3
/LED_DIN: J5.4, JP1.2
/LED_DOUT: J7.8, JP2.2
/LED_DOUT1: J5.8, J6.13
/LED_DOUT2: J6.1, J7.4
/SCL: J6.2, P5.1
/SDA: J6.4, P5.2
GND: C1.2, J1.6, J2.6, J5.5, J5.6, J6.14, J7.5, J7.6, J8.3, J9.2, J9.4, J10.2, JP2.3, P1.1, P1.2, P2.6, P2.7, P5.4, TP4.1, U1.5
