jrsteensen/OpenHornet/ECAD/PCBs/ABSIS/ABSIS_Backlight Controller/ABSIS_Backlight Controller.kicad_pcb

## KiCad design ECAD/PCBs/ABSIS/ABSIS_Backlight Controller/ABSIS_Backlight Controller.kicad_pcb (2024-02-26)

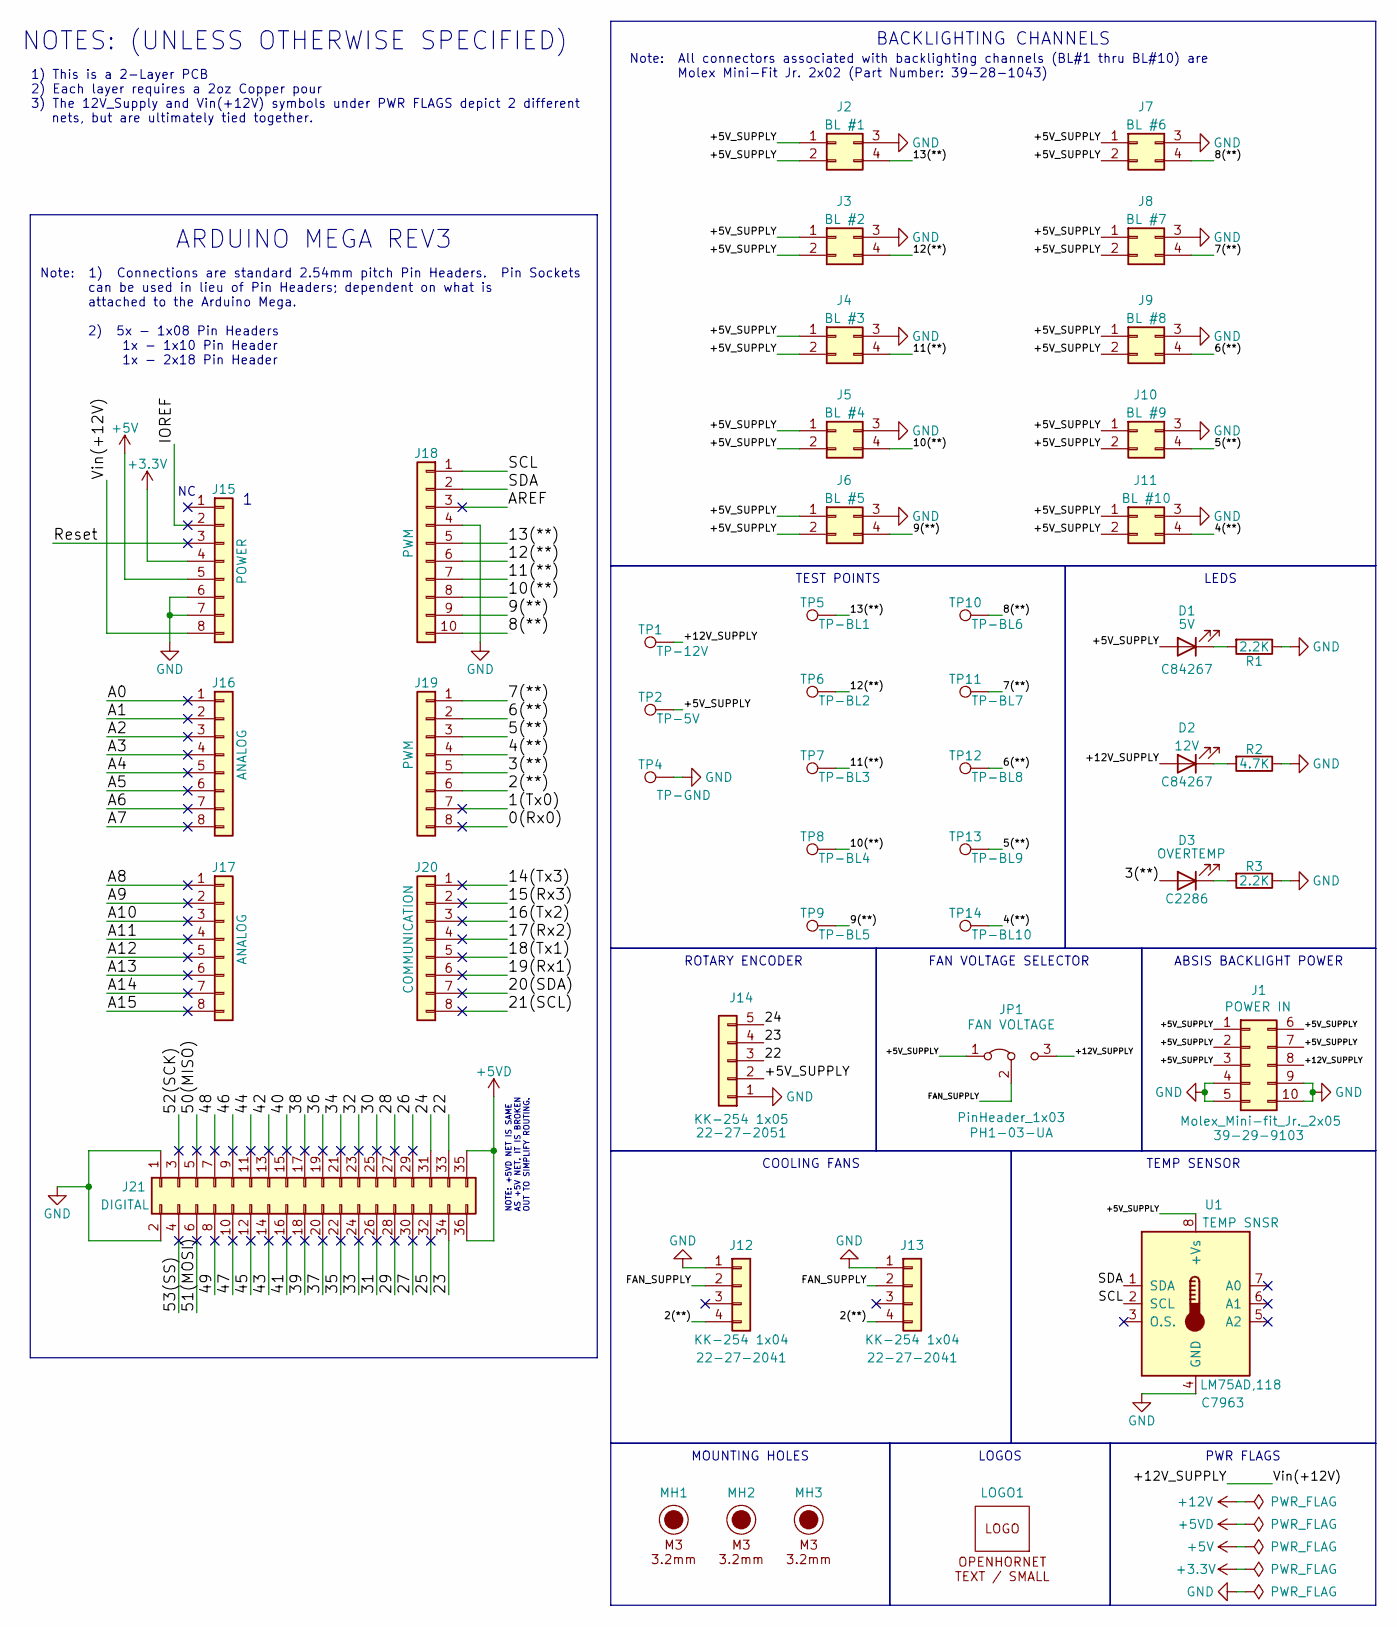
[picture p625: schematic ABSIS_Backlight Controller.kicad_sch, ABSIS Backlight Controller]

Parts:
D1, D2: Green; LED_0603_1608Metric_Pad1.05x0.95mm_HandSolder; Manufacturer PN NCD0603G1; LCSC C84267
D3: Red; LED_0603_1608Metric_Pad1.05x0.95mm_HandSolder; Manufacturer PN KT-0603R; LCSC C2286
J1: Molex_Mini-fit_Jr._2x05; Molex_Mini-Fit_Jr_5566-10A2_2x05_P4.20mm_Vertical; Manufacturer PN 39-29-9103; LCSC C587474
J2, J3, J4, J5, J6, J7, J8, J9, J10, J11: Mini-Fit Jr. 2x02; Molex_Mini-Fit_Jr_5566-04A_2x02_P4.20mm_Vertical; Manufacturer PN 39-28-1043; LCSC C293502
J12, J13: KK-254 1x04; Molex_KK-254_AE-6410-04A_1x04_P2.54mm_Vertical; Manufacturer PN 22-27-2041; LCSC C504991
J14: KK-254 1x05; Molex_KK-254_AE-6410-05A_1x05_P2.54mm_Vertical; Manufacturer PN 22-27-2051; LCSC C585785
J15, J16, J17, J19, J20: PinHeader_1x08; PinHeader_1x08_P2.54mm_Vertical; Manufacturer PN PH1-08-UA
J18: PinHeader_1x10; PinHeader_1x10_P2.54mm_Vertical; Manufacturer PN PH1-10-UA
J21: PinHeader_2x18; PinHeader_2x18_P2.54mm_Vertical; Manufacturer PN PH2-18-UA
JP1: PinHeader_1x03; PinHeader_1x03_P2.54mm_Vertical; Manufacturer PN PH1-03-UA
LOGO1: LOGO; LOGO_OH_Text_Small
MH1, MH2, MH3: M3 / 3.2mm; MountingHole_3.2mm_M3_DIN965
R1, R3: 2.2K; R_0603_1608Metric; Manufacturer PN 0603WAF2201T5E; LCSC C4190
R2: 4.7K; R_0603_1608Metric; Manufacturer PN 0603WAF4701T5E; LCSC C23162
TP1, TP2, TP4, TP5, TP6, TP7, TP8, TP9, TP10, TP11, TP12, TP13, TP14: TestPoint; TestPoint_THTPad_D1.5mm_Drill0.7mm
U1: LM75AD,118; SOIC-8_3.9x4.9mm_P1.27mm; Manufacturer PN LM75AD,118; LCSC C7963

Connections:
+3.3V: J15.4
+5V: J15.5
+5VD: J21.35, J21.36
/0(Rx0): J19.8
/1(Tx0): J19.7
/2(**): J12.4, J13.4, J19.6
/3(**): D3.2 (A), J19.5
/4(**): J11.4, J19.4, TP14.1
/5(**): J10.4, J19.3, TP13.1
/6(**): J9.4, J19.2, TP12.1
/7(**): J8.4, J19.1, TP11.1
/8(**): J7.4, J18.10, TP10.1
/9(**): J6.4, J18.9, TP9.1
/10(**): J5.4, J18.8, TP8.1
/11(**): J4.4, J18.7, TP7.1
/12(**): J3.4, J18.6, TP6.1
/13(**): J2.4, J18.5, TP5.1
/14(Tx3): J20.1
/15(Rx3): J20.2
/16(Tx2): J20.3
/17(Rx2): J20.4
/18(Tx1): J20.5
/19(Rx1): J20.6
/20(SDA): J20.7
/21(SCL): J20.8
/22: J14.3, J21.33
/23: J14.4, J21.34
/24: J14.5, J21.31
/25: J21.32
/26: J21.29
/27: J21.30
/28: J21.27
/29: J21.28
/30: J21.25
/31: J21.26
/32: J21.23
/33: J21.24
/34: J21.21
/35: J21.22
/36: J21.19
/37: J21.20
/38: J21.17
/39: J21.18
/40: J21.15
/41: J21.16
/42: J21.13
/43: J21.14
/44: J21.11
/45: J21.12
/46: J21.9
/47: J21.10
/48: J21.7
/49: J21.8
/50(MISO): J21.5
/51(MOSI): J21.6
/52(SCK): J21.3
/53(SS): J21.4
/+5V_SUPPLY: D1.2 (A), J1.1, J1.2, J1.3, J1.6, J1.7, J2.1, J2.2 (Pin_3), J3.1, J3.2 (Pin_3), J4.1, J4.2 (Pin_3), J5.1, J5.2 (Pin_3), J6.1, J6.2 (Pin_3), J7.1, J7.2 (Pin_3), J8.1, J8.2 (Pin_3), J9.1, J9.2 (Pin_3), J10.1, J10.2 (Pin_3), J11.1, J11.2 (Pin_3), J14.2, JP1.1 (A), TP2.1, U1.8 (+Vs)
/+12V_SUPPLY: D2.2 (A), J1.8, J15.8, JP1.3 (B), TP1.1
/A0: J16.1
/A1: J16.2
/A2: J16.3
/A3: J16.4
/A4: J16.5
/A5: J16.6
/A6: J16.7
/A7: J16.8
/A8: J17.1
/A9: J17.2
/A10: J17.3
/A11: J17.4
/A12: J17.5
/A13: J17.6
/A14: J17.7
/A15: J17.8
/AREF: J18.3
/FAN_SUPPLY: J12.2, J13.2, JP1.2 (C)
/IOREF: J15.2
/Reset: J15.3
/SCL: J18.1, U1.2 (SCL)
/SDA: J18.2, U1.1 (SDA)
GND: J1.4, J1.5, J1.9, J1.10, J2.3 (Pin_2), J3.3 (Pin_2), J4.3 (Pin_2), J5.3 (Pin_2), J6.3 (Pin_2), J7.3 (Pin_2), J8.3 (Pin_2), J9.3 (Pin_2), J10.3 (Pin_2), J11.3 (Pin_2), J12.1, J13.1, J14.1, J15.6, J15.7, J18.4, J21.1, J21.2, R1.1, R2.1, R3.1, TP4.1, U1.4 (GND)
unnamed: D1.1 (K), R1.2
unnamed: D2.1 (K), R2.2
unnamed: D3.1 (K), R3.2

Notes on the sheet:
LEDS
BACKLIGHTING CHANNELS
ABSIS BACKLIGHT POWER
ROTARY ENCODER
ARDUINO MEGA REV3
TEMP SENSOR
PWR FLAGS
COOLING FANS
LOGOS
FAN VOLTAGE SELECTOR
MOUNTING HOLES
TEST POINTS
1) This is a 2-Layer PCB 2) Each layer requires a 2oz Copper pour 3) The 12V_Supply and Vin(+12V) symbols under PWR FLAGS depict 2 different nets, but are ultimately tied together.
Note: All connectors associated with backlighting channels (BL#1 thru BL#10) are Molex Mini-Fit Jr. 2x02 (Part Number: 39-28-1043)
NOTE: +5VD NET IS SAME AS +5V NET. IT IS BROKEN OUT TO SIMPLIFY ROUTING.
Note: 1) Connections are standard 2.54mm pitch Pin Headers. Pin Sockets can be used in lieu of Pin Headers; dependent on what is attached to the Arduino Mega. 2) 5x - 1x08 Pin Headers 1x - 1x10 Pin Header 1x - 2x18 Pin Header
NOTES: (UNLESS OTHERWISE SPECIFIED)

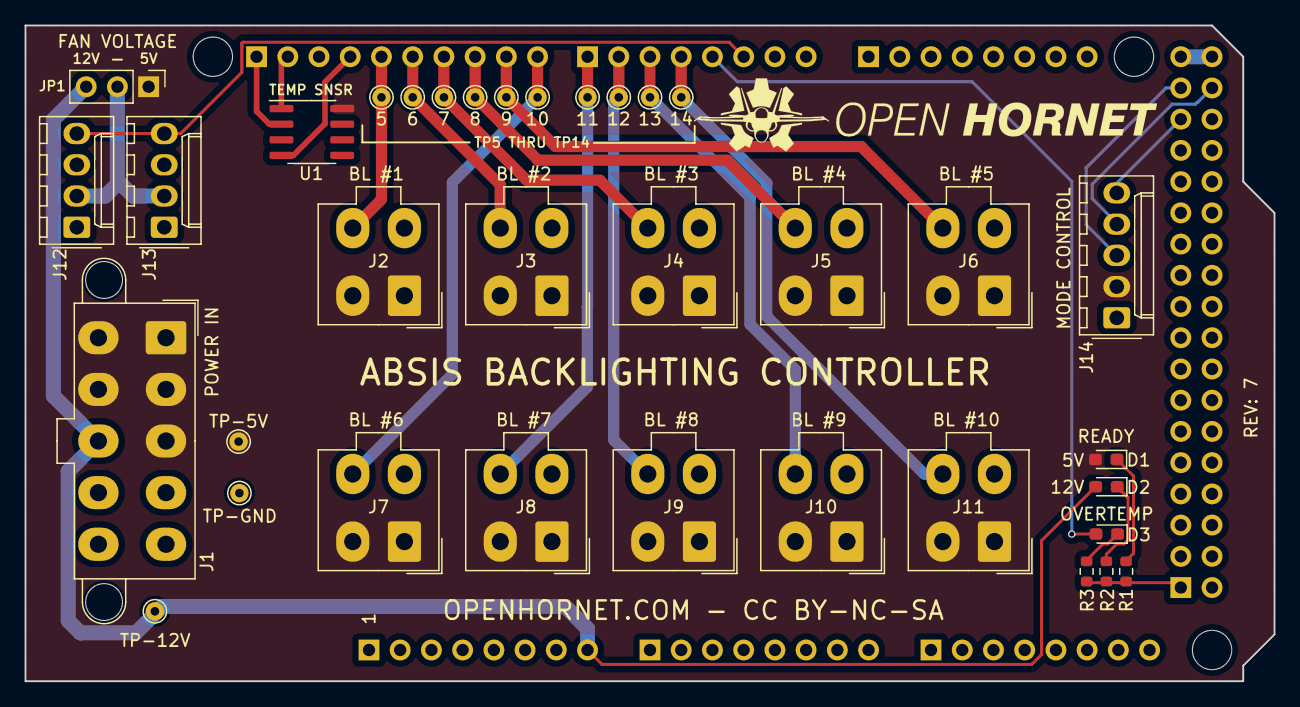
[picture p626: board ABSIS_Backlight Controller.kicad_pcb from above]

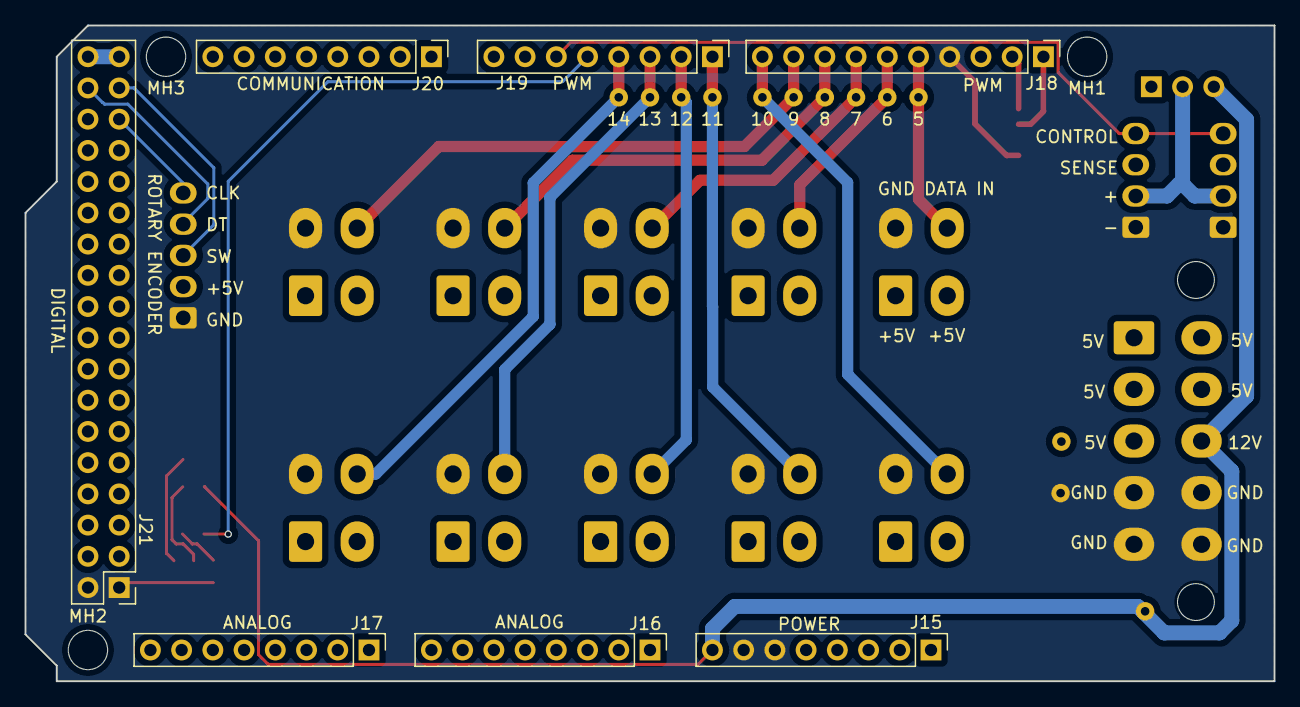
[picture p627: board ABSIS_Backlight Controller.kicad_pcb from below]

Board: 2 copper layers, 101.6 x 53.3 mm, 46 parts (10 on the bottom side), 25 nets.
