jrsteensen/OpenHornet/ECAD/PCBs/Functional PCBs/util_photoswitch/util_photoswitch.kicad_pcb

## KiCad design ECAD/PCBs/Functional PCBs/util_photoswitch/util_photoswitch.kicad_pcb (2024-02-26)

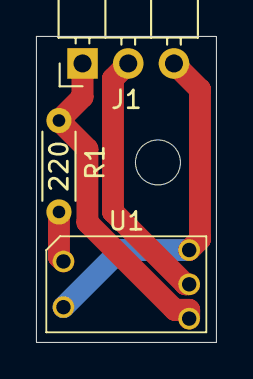
[picture p628: board util_photoswitch.kicad_pcb from above]

Board: 2 copper layers, 10.0 x 17.0 mm, 4 parts (0 on the bottom side), 4 nets.

Parts:
H1: MountingHole; MountingHole_2.5mm
J1: Conn_01x03_Male; PinHeader_1x03_P2.54mm_Horizontal
R1: 220; R_Axial_DIN0204_L3.6mm_D1.6mm_P5.08mm_Horizontal
U1: OPB615; OPB61x

Connections:
+5V: J1.1, R1.2, U1.3
GND: J1.3, U1.2, U1.5
unnamed: J1.2, U1.4
unnamed: R1.1, U1.1
