jrsteensen/OpenHornet/ECAD/interconnects/OH_Interconnect.kicad_sch

## KiCad design ECAD/interconnects/OH_Interconnect.kicad_sch (2026-09-24)

Schematic: OH_Interconnect.kicad_sch

Parts:
P3, P4: M20-1070600
P5: M20-1060600
P6: M20-1070200

Notes on the sheet:
+3.3V_J7-2
D7_J4-4
D37_J6-2
GND_J5-2
NOTES: (UNLESS OTHERWISE SPECIFIED)
+5V_J7-3
GND_J5-19
A5_J4-11
GND_J5-17
~{D3_SCL}_J3-4
D4-A6_J3-6
~{D9_J3-9}
GND_J6-19
~{D3_J3-2}
A6_J4-13
~{D5_J3-17}
GND_J6-4
+5V_J4-19
D15_J3-6
~{D7_J3-13}
D8-A8_J4-6
GND_J3-10
D14-MISO_J4-3
D45_J5-10
GND_J5-4
A1_J3-5
A3_J3-1
1. SEE OH-PL-INTERCONNECT FOR SEPARATE INTERCONNECT PARTS LIST. 2. SEE OH-SPEC-002 FOR ABSIS CABLE SPECIFICATIONS. 3. ALL CONDUCTORS SHALL BE STRANDED COPPER, 16AWG FOR POWER CONNECTIONS AND 26AWG FOR SIGNAL/DATA CONNECTIONS, EXCEPT AS OTHERWISE SPECIFIED BY OH-SPEC-002, THE APPLICABLE CABLE/ASSEMB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
(EXTERNAL CONNECTIONS)
D49_J5-6
D17_J3-10
~{D9-A9}_J4-8
GND_J4-12
D31_J6-8
GND_J4-20
GND_J4-18
D26_J6-11
+5V_J5-20
~{D13_J3-1}
D27_J6-12
D21_J3-18
+5V_J4-17
D52_J5-1
A13_J4-6
A11_J4-10
D2-SDA_J3-2
D42_J5-11
D46_J5-7
GND_J4-10
D15-SCK_J4-1
~{D6_J3-15}
D10_J3-7
GND_J3-22
+5V_J4-9
TOP LEVEL SYSTEM
A2_J3-3
A1_J4-3
+5V_J3-11
~{D10-A10}_J4-7
D32_J6-5
D28_J6-9
D50_J5-3
D53_J5-2
GND_J6-17
+5V_J6-18
~{D6-A7}_J4-2
D22_J6-15
D24_J6-13
A15_J4-2
D18_J3-12
~{D4_J3-19}
+12V_J7-1
A8_J4-16
+5V_J6-20
D40_J5-13
+5V_J3-9
D44_J5-9
A0_J3-7
+3.3V_J6-2
GND_J5-5
D36_J6-1
D51_J5-4
GND_J7-4
GND_J5-1
D11_J3-5
D14_J3-4
GND_J5-6
D16-MOSI_J4-5
D12_J3-3
D43_J5-12
D19_J3-14
D23_J6-16
D39_J5-16
D29_J6-10
BLOCK DIAGRAM
A7_J4-15
D41_J5-14
D33_J6-6
D20_J3-16
ALE PLUG REFERENCE ("DUPONT") NOTE: ALL WIRES ARE 26AWG UNLESS OTHERWISE SPECIFIED. ALE P1/P2: 2x6: M20-1070600 (F CRIMP: M20-1160042) ALE P3: 1x6: M20-1060600 (F CRIMP: M20-1160042) ALE P4: 2x2: M20-1070200 (F CRIMP: M20-1160042) USE IWISS SN-28B OR SIMILAR FOR CRIMPING TERMINALS ABSIS TO SEPARATE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
KK MATING CONNECTORS 10-11-2023 (OLD PN: 7880-2B) - 2 POS 10-11-2033 (OLD PN: 7880-3B) - 3 POS 10-11-2043 (OLD PN: 7880-4B) - 4 POS 10-11-2053 (OLD PN: 7880-5B) - 5 POS 10-11-2063 (OLD PN: 7880-6B) - 6 POS 10-11-2073 (OLD PN: 7880-7B) - 7 POS 10-11-2083 (OLD PN: 7880-8B) - 8 POS 10-11-2093 (OLD PN: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
D34_J6-3
A0_J4-1
A10_J4-12
D47_J5-8
D25_J6-14
+5V_J4-11
A12_J4-8
+12V_J6-1
~{D8_J3-11}
D30_J6-7
A9_J4-14
GND_J3-8
GND_J3-12
GND_J3-20
GND_J3-21
DUAL ROW DUPONT M20-1070200 - 4 POS M20-1070300 - 6 POS M20-1070400 - 8 POS M20-1070500 - 10 POS M20-1070600 - 12 POS M20-1070700 - 14 POS M20-1070800 - 16 POS M20-1070900 - 18 POS M20-1071000 - 20 POS M20-1071100 - 22 POS M20-1071200 - 24 POS SINGLE ROW DUPONT M20-1060200 - 2 POS M20-1060300 - 3 P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
A3_J4-7
+5V_J5-18
D16_J3-8
+5V_J6-3
D48_J5-5
GND_J5-3
A14_J4-4
D38_J5-15
A4_J4-9
D35_J6-4
A2_J4-5
CABLE AND CONNECTOR QUICK REFERENCE
COMMON PCB QUICK REF
