jrsteensen/OpenHornet/ECAD/interconnects/OH_Left_Console.kicad_sch

## KiCad design ECAD/interconnects/OH_Left_Console.kicad_sch (2026-09-24)

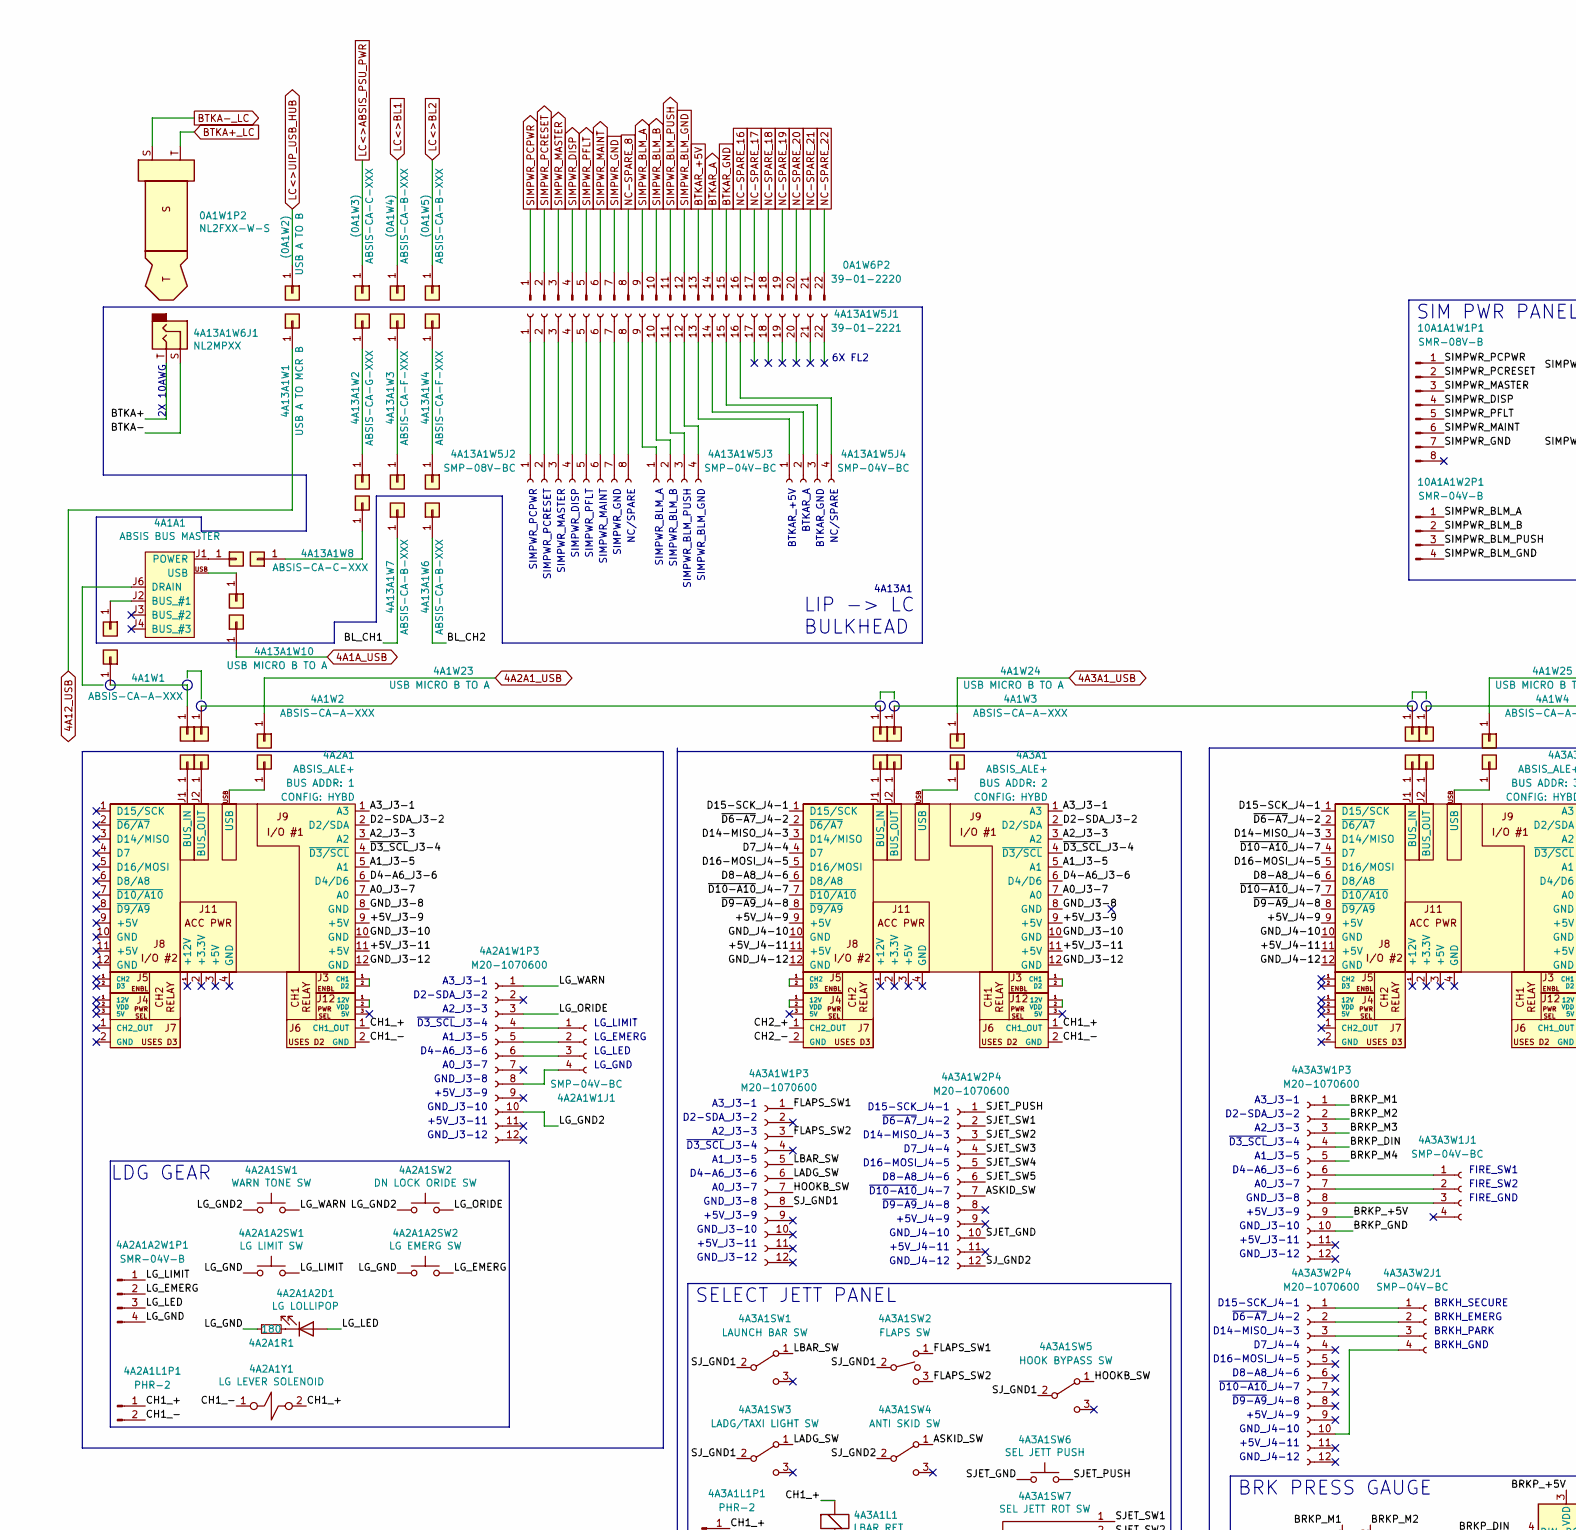
[picture p630: schematic OH_Left_Console.kicad_sch, part in row 1, column 1]

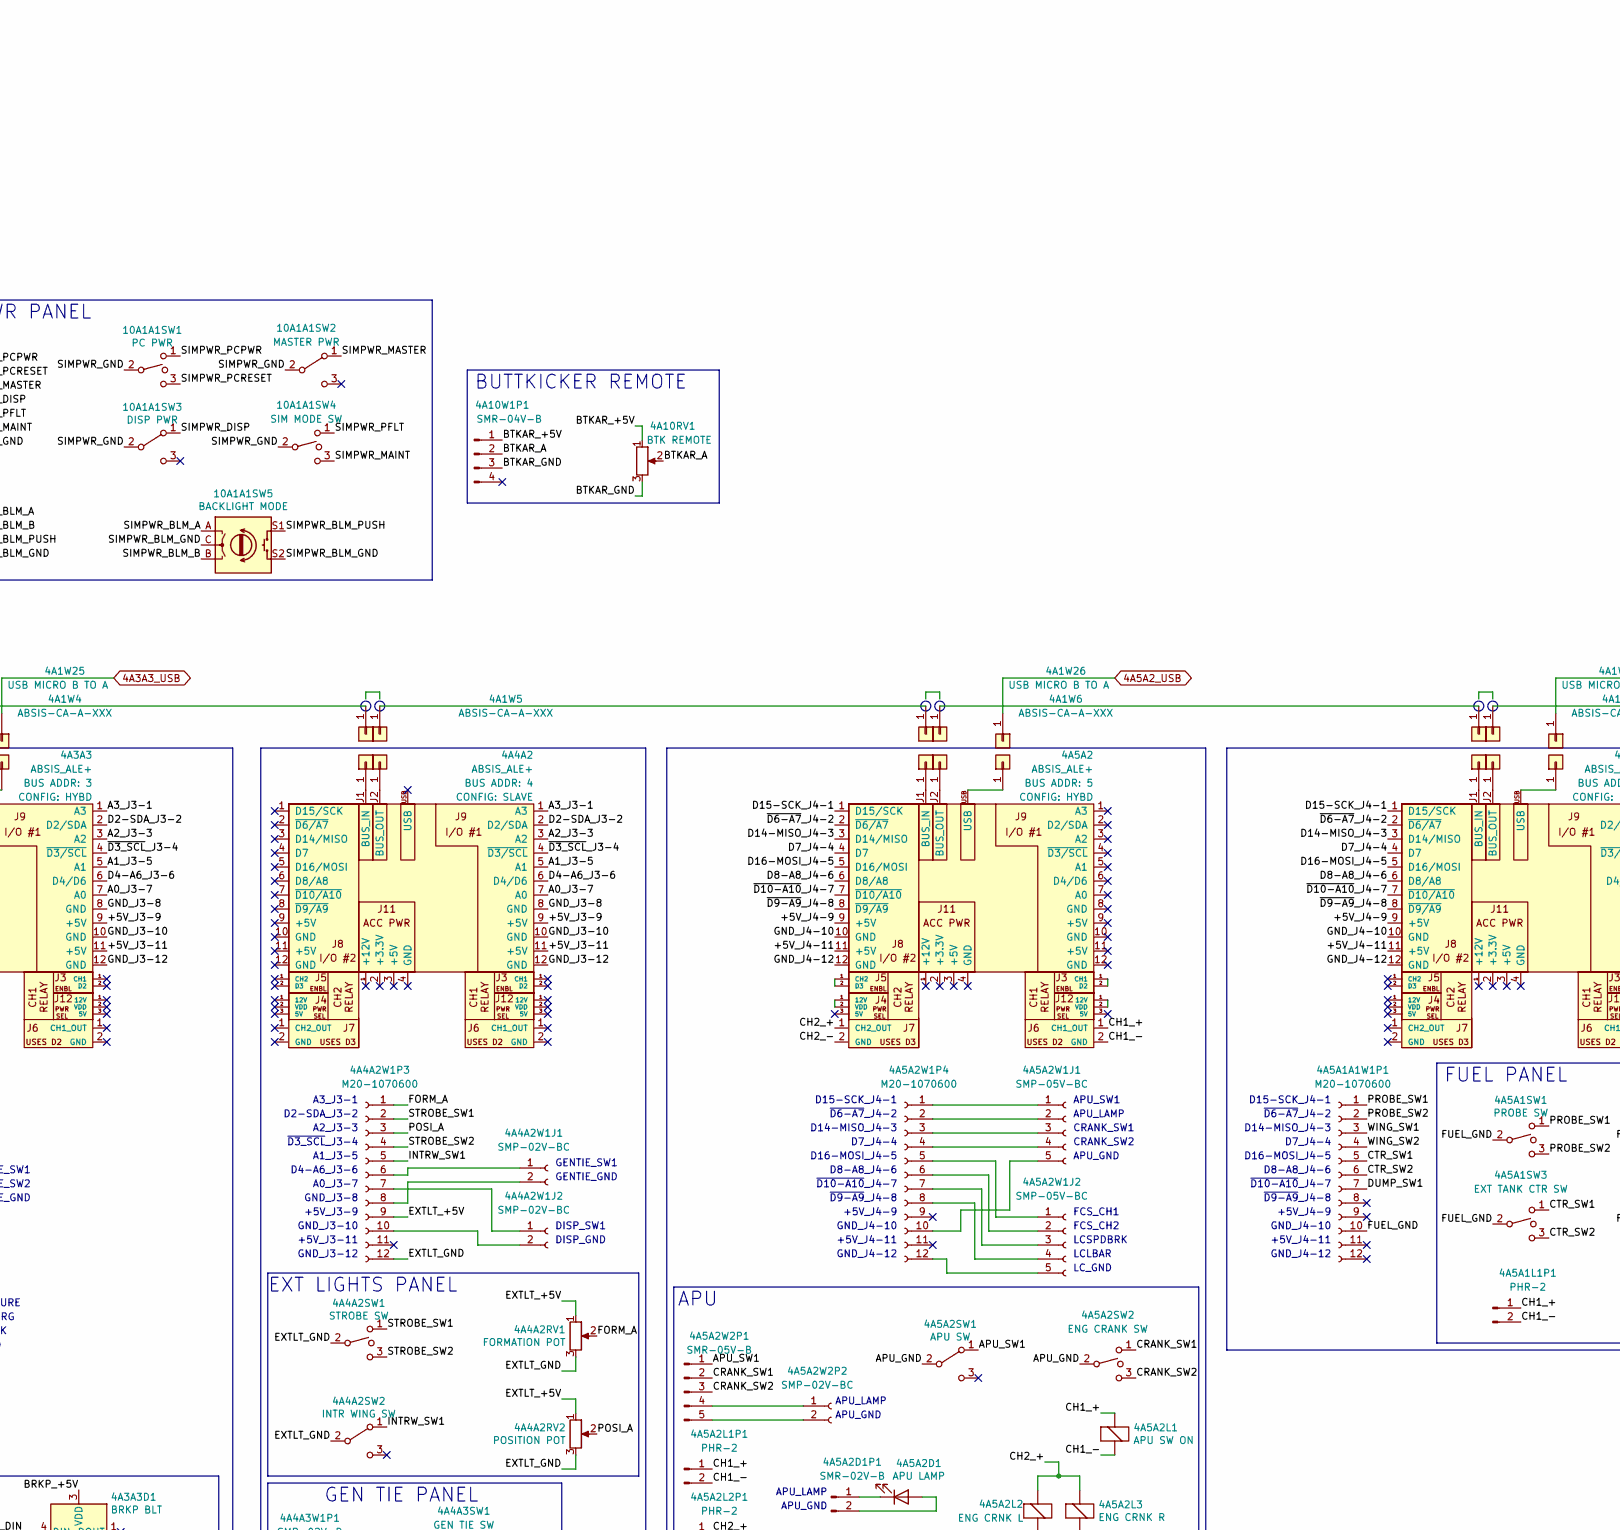
[picture p631: schematic OH_Left_Console.kicad_sch, part in row 1, column 2]

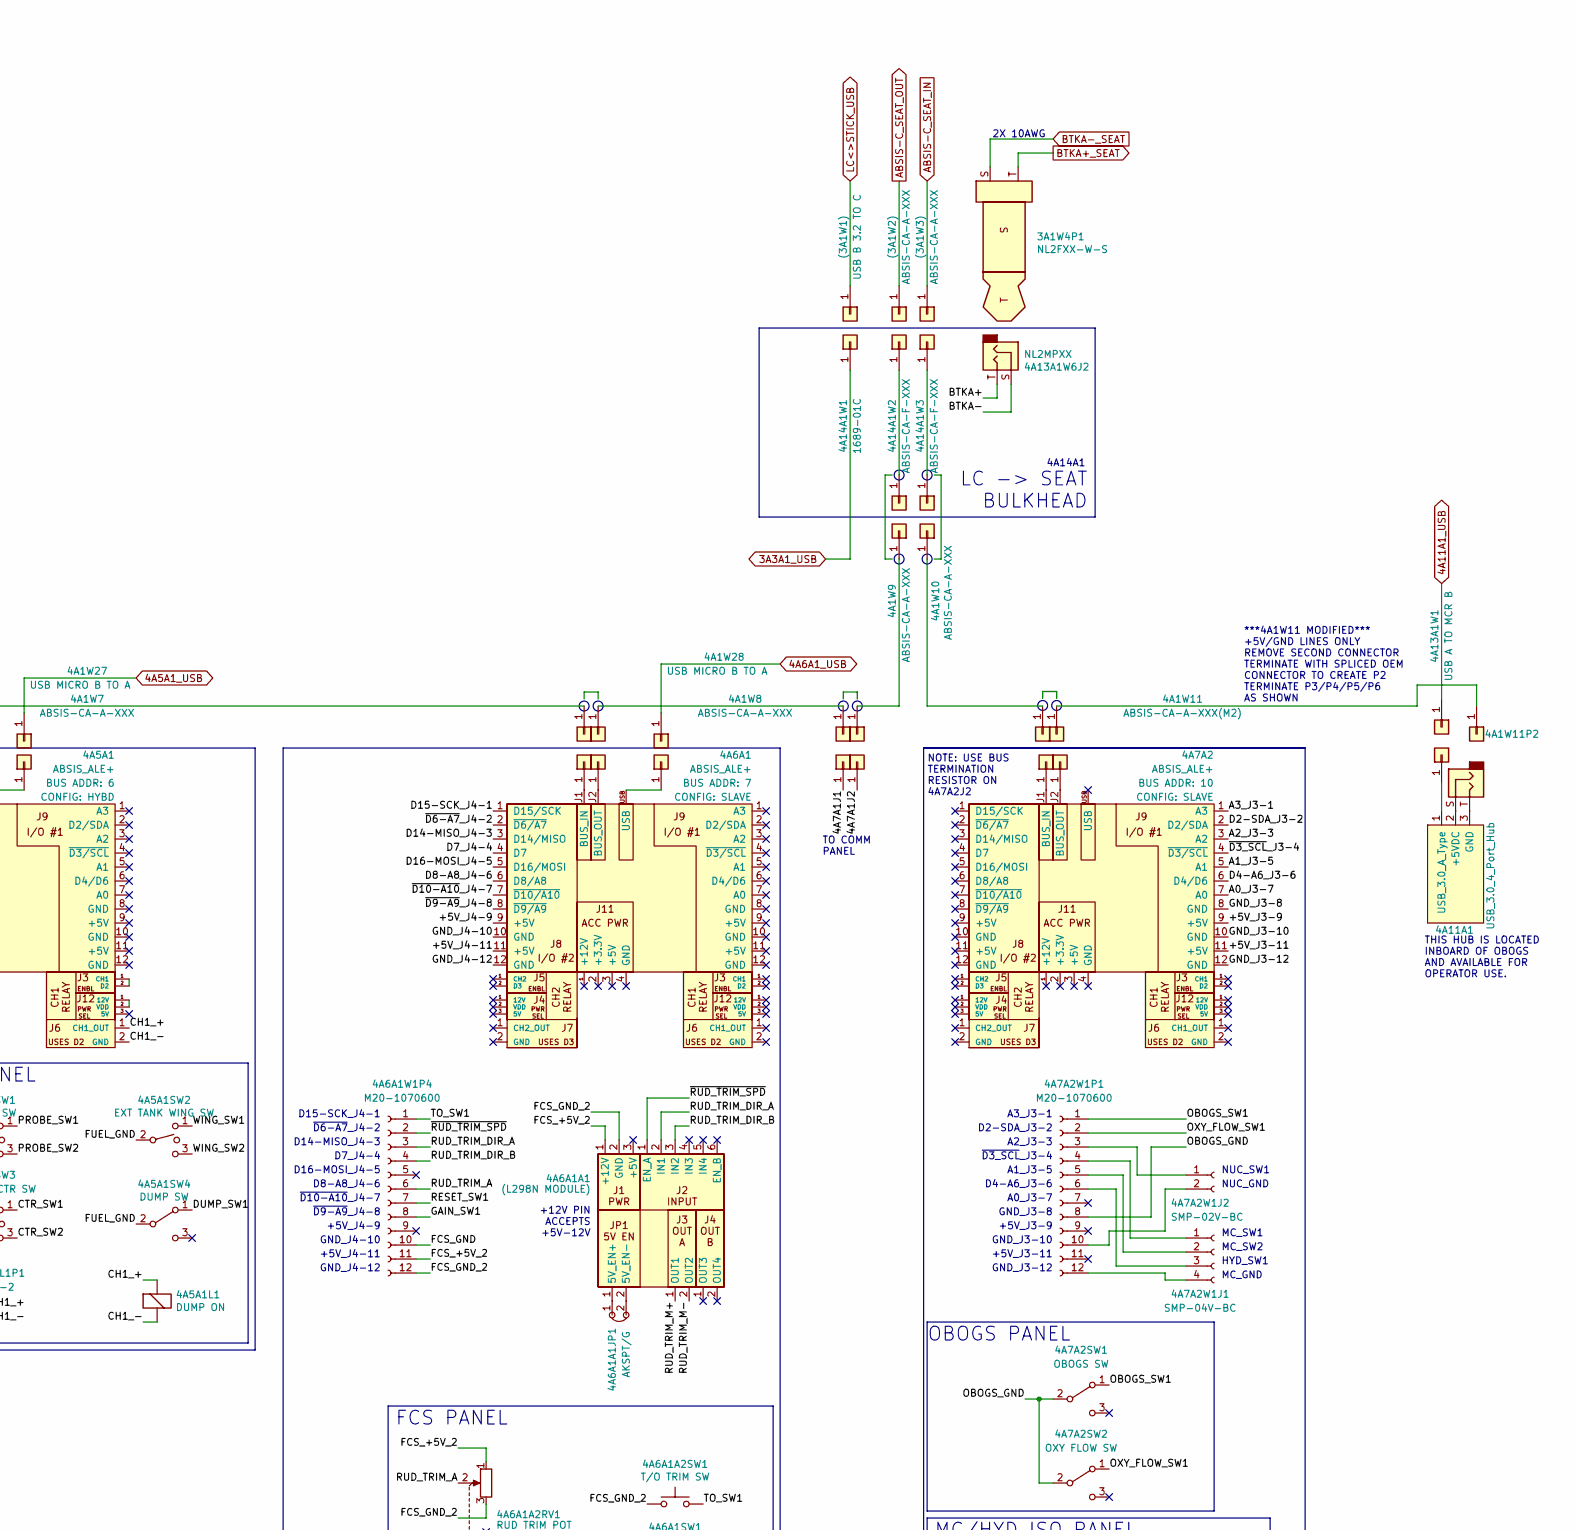
[picture p632: schematic OH_Left_Console.kicad_sch, part in row 1, column 3]

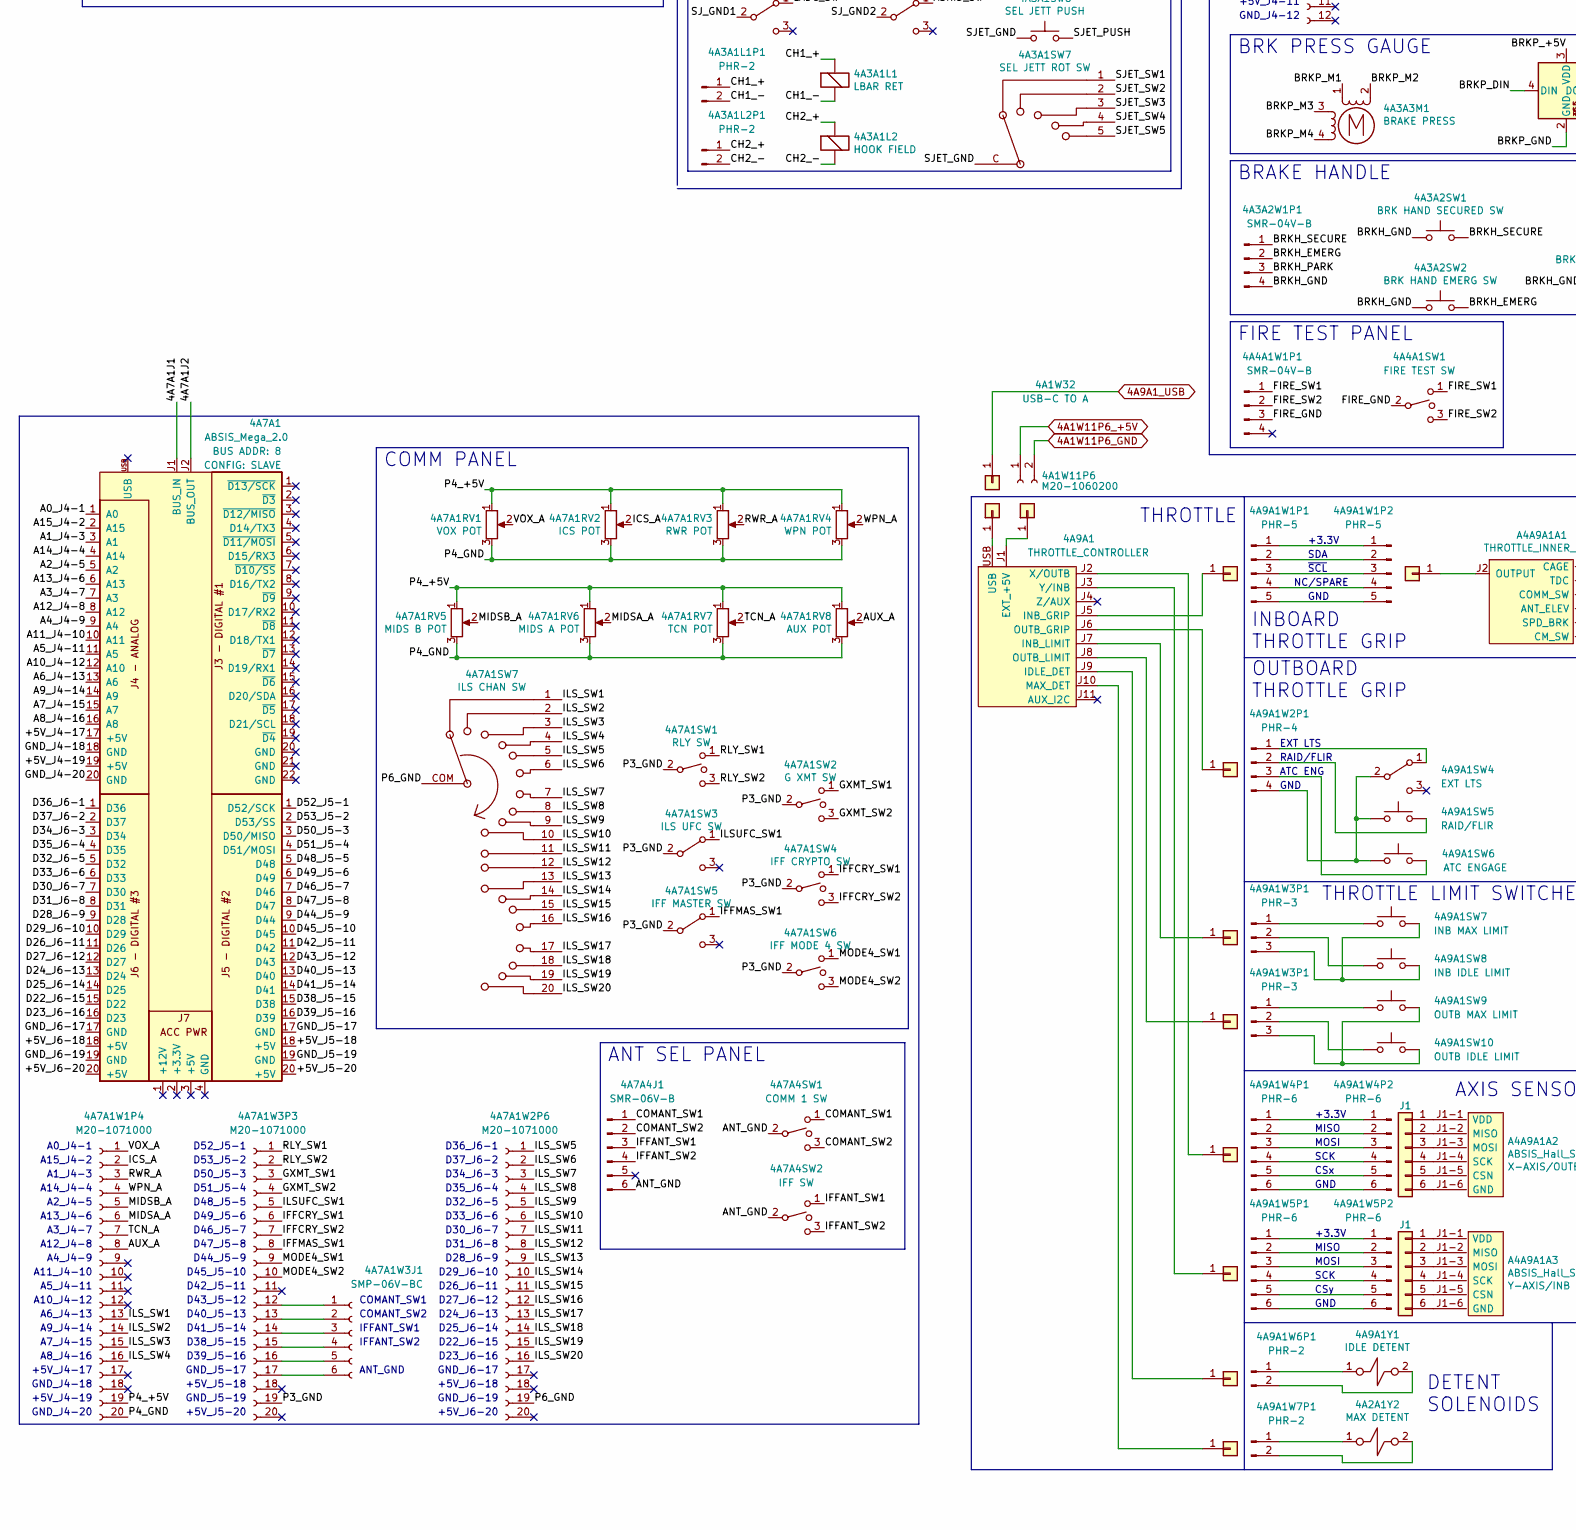
[picture p633: schematic OH_Left_Console.kicad_sch, part in row 2, column 1]

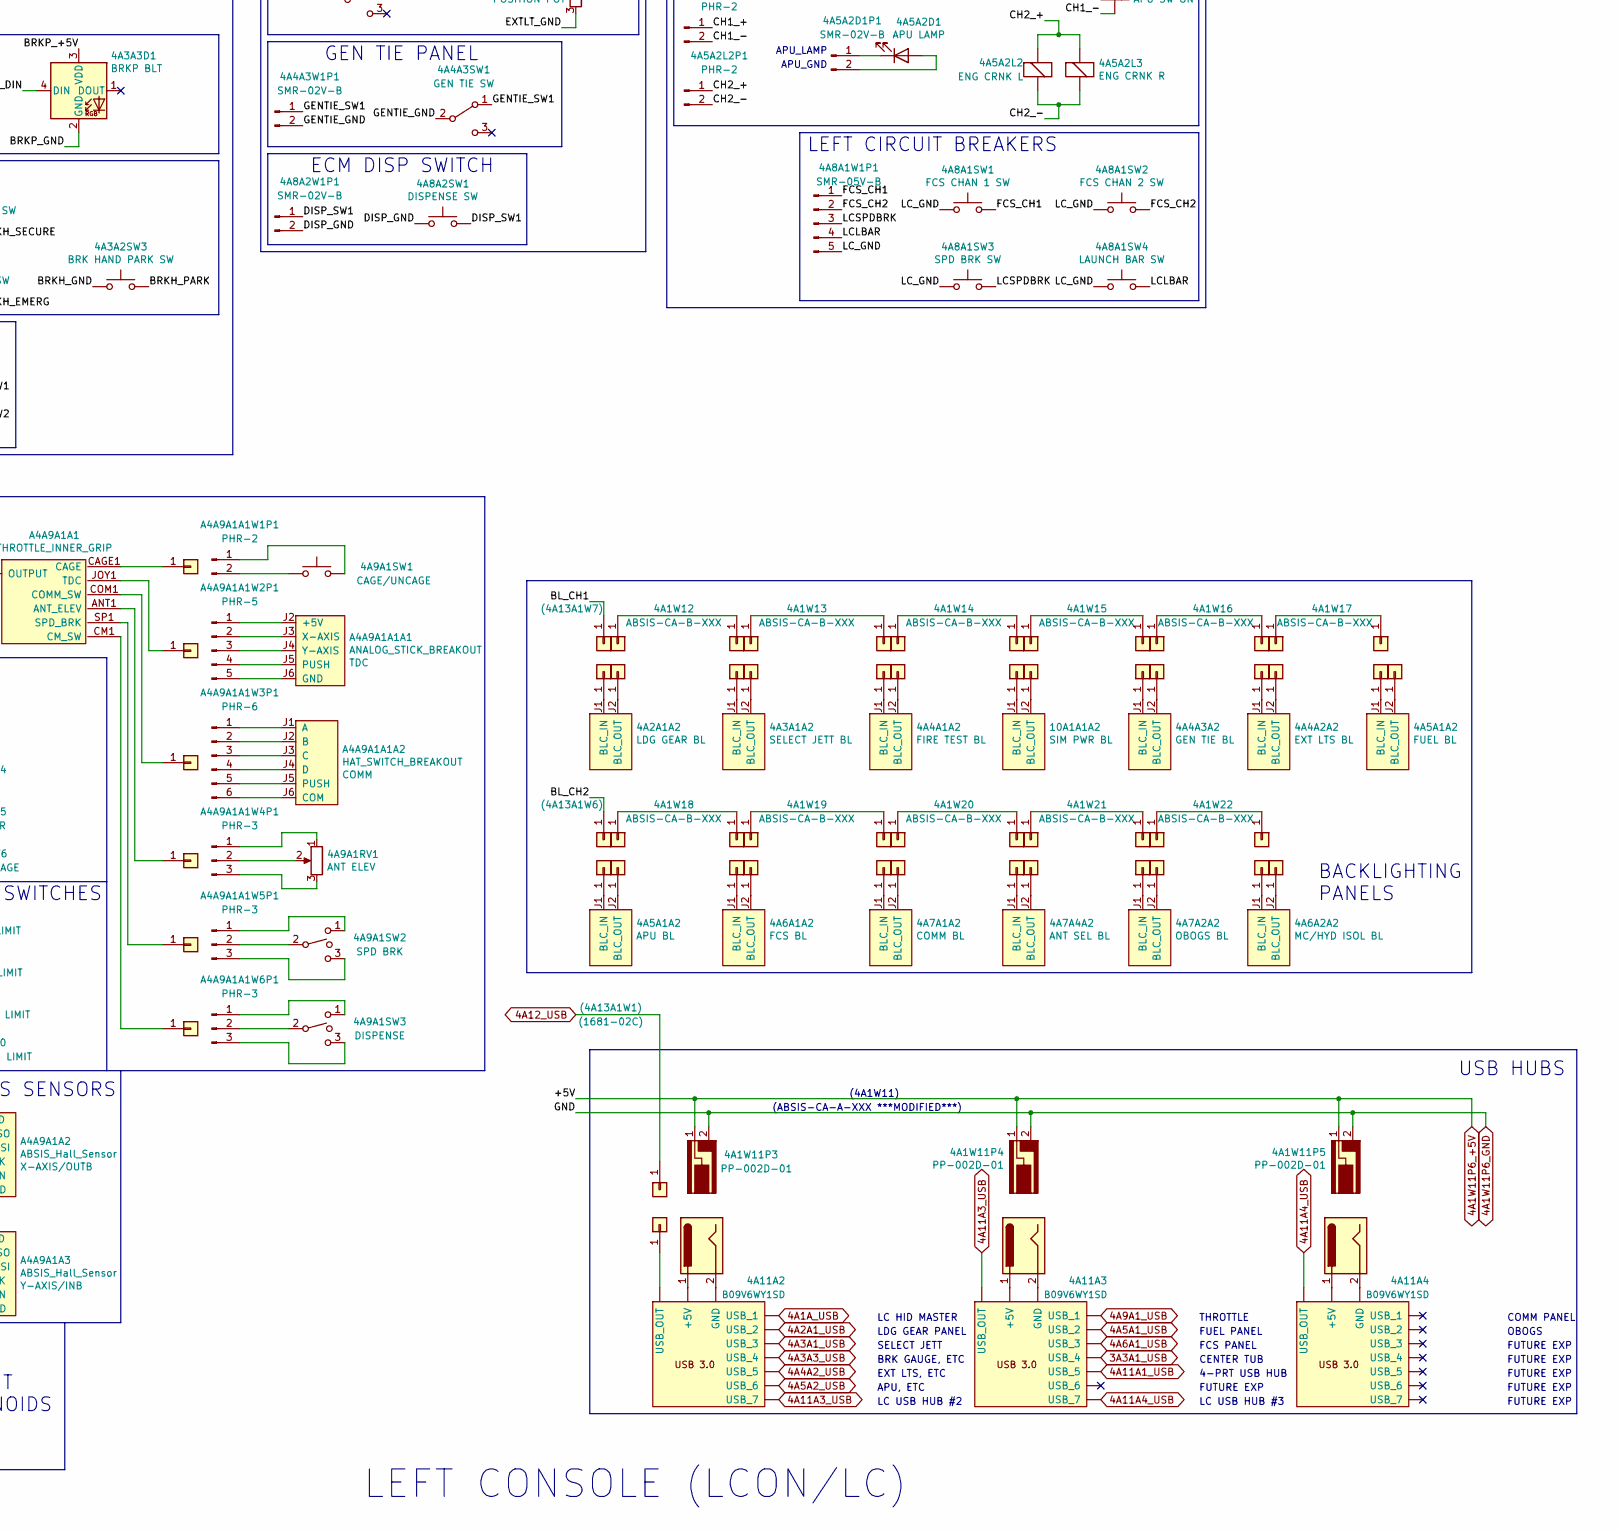
[picture p634: schematic OH_Left_Console.kicad_sch, part in row 2, column 2]

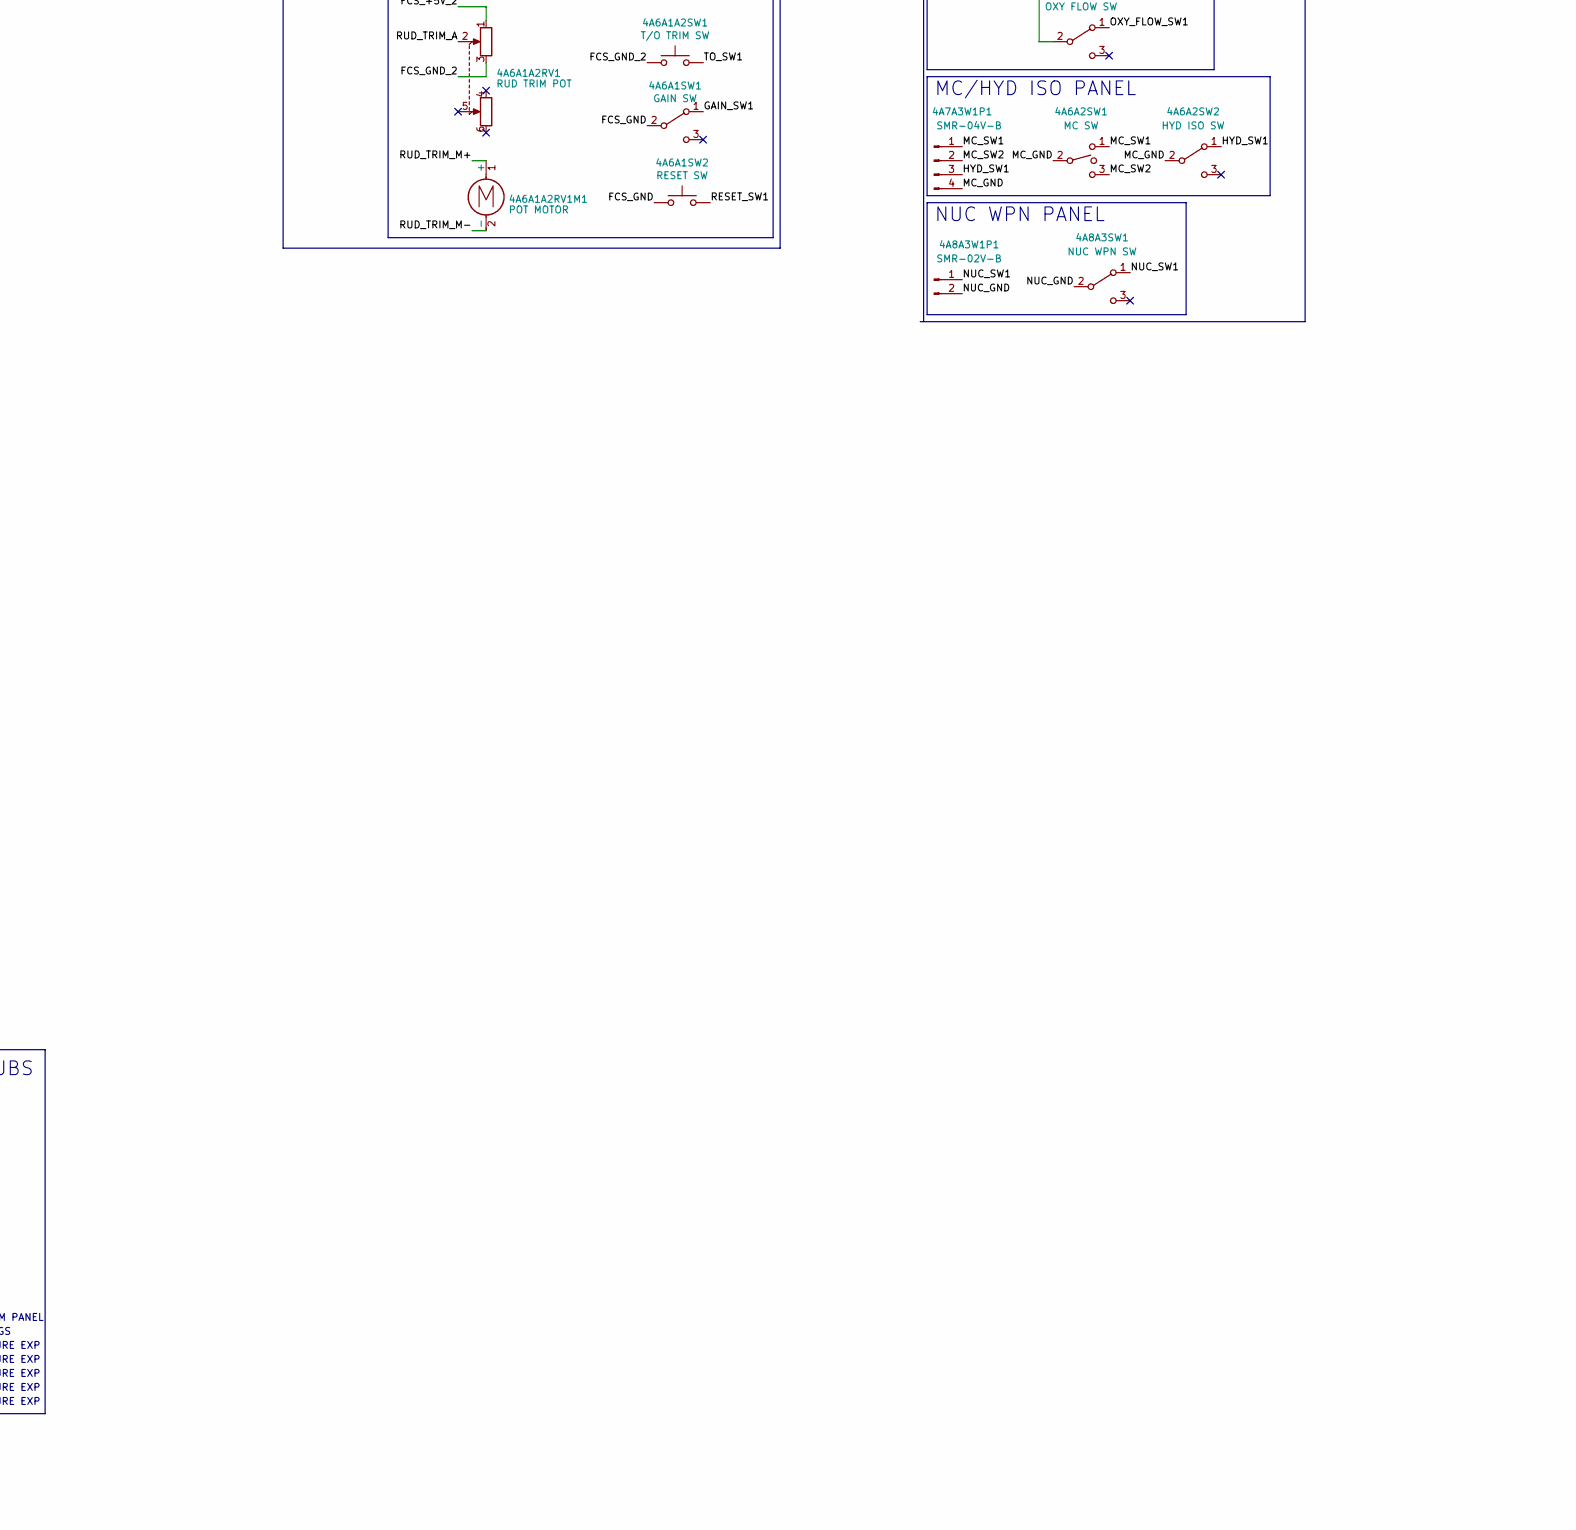
[picture p635: schematic OH_Left_Console.kicad_sch, part in row 2, column 3]

Parts:
0A1W1P2, 3A1W4P1: NL2FXX-W-S
0A1W6P2: 39-01-2220
4A1A1: ABSIS BUS MASTER
4A1W1, 4A1W2, 4A1W3, 4A1W4, 4A1W5, 4A1W6, 4A1W7, 4A1W8, 4A1W9, 4A1W10: ABSIS-CA-A-XXX
4A1W11: ABSIS-CA-A-XXX(M2)
4A1W11P2, 4A2A1J1, 4A2A1J2, 4A2A1~, 4A3A1J1, 4A3A1J2, 4A3A3J1, 4A3A3J2, 4A4A2J1, 4A4A2J2, 4A5A1J1, 4A5A1J2, 4A5A2J1, 4A5A2J2, 4A6A1J1: (no value)
4A1W11P3, 4A1W11P4, 4A1W11P5: PP-002D-01
4A1W11P6: M20-1060200
4A1W12, 4A1W13, 4A1W14, 4A1W15, 4A1W16, 4A1W17, 4A1W18, 4A1W19, 4A1W20, 4A1W21, 4A1W22, 4A13A1W6, 4A13A1W7: ABSIS-CA-B-XXX
4A1W23, 4A1W24, 4A1W25, 4A1W26, 4A1W27, 4A1W28, 4A13A1W10: USB MICRO B TO A
4A1W32: USB-C TO A
4A2A1, 4A3A1, 4A3A3, 4A4A2, 4A5A1, 4A5A2, 4A6A1, 4A7A2: ABSIS_ALE+
4A2A1A2: LDG GEAR BL
4A2A1A2D1: LG LOLLIPOP
4A2A1A2SW1: LG LIMIT SW
4A2A1A2SW2: LG EMERG SW
4A2A1A2W1P1, 4A3A2W1P1, 4A4A1W1P1, 4A7A3W1P1, 4A10W1P1, 10A1A1W2P1: SMR-04V-B
4A2A1L1P1, 4A3A1L1P1, 4A3A1L2P1, 4A5A1L1P1, 4A5A2L1P1, 4A5A2L2P1, 4A9A1W6P1, 4A9A1W7P1: PHR-2
4A2A1R1: 180
4A2A1SW1: WARN TONE SW
4A2A1SW2: DN LOCK ORIDE SW
4A2A1W1J1, 4A3A3W1J1, 4A3A3W2J1, 4A7A2W1J1, 4A13A1W5J3, 4A13A1W5J4: SMP-04V-BC
4A2A1W1P3, 4A3A1W1P3, 4A3A1W2P4, 4A3A3W1P3, 4A3A3W2P4, 4A4A2W1P3, 4A5A1A1W1P1, 4A5A2W1P4, 4A6A1W1P4, 4A7A2W1P1: M20-1070600
4A2A1Y1: LG LEVER SOLENOID
4A2A1Y2: MAX DETENT
4A3A1A2: SELECT JETT BL
4A3A1L1: LBAR RET
4A3A1L2: HOOK FIELD
4A3A1SW1, 4A8A1SW4: LAUNCH BAR SW
4A3A1SW2: FLAPS SW
4A3A1SW3: LADG/TAXI LIGHT SW
4A3A1SW4: ANTI SKID SW
4A3A1SW5: HOOK BYPASS SW
4A3A1SW6: SEL JETT PUSH
4A3A1SW7: SEL JETT ROT SW
4A3A2SW1: BRK HAND SECURED SW
4A3A2SW2: BRK HAND EMERG SW
4A3A2SW3: BRK HAND PARK SW
4A3A3D1: BRKP BLT
4A3A3M1: BRAKE PRESS
4A4A1A2: FIRE TEST BL
4A4A1SW1: FIRE TEST SW
4A4A2A2: EXT LTS BL
4A4A2RV1: FORMATION POT
4A4A2RV2: POSITION POT
4A4A2SW1: STROBE SW
4A4A2SW2: INTR WING SW
4A4A2W1J1, 4A4A2W1J2, 4A5A2W2P2, 4A7A2W1J2: SMP-02V-BC
4A4A3A2: GEN TIE BL
4A4A3SW1: GEN TIE SW
4A4A3W1P1, 4A5A2D1P1, 4A8A2W1P1, 4A8A3W1P1: SMR-02V-B
4A5A1A2: FUEL BL
4A5A1L1: DUMP ON
4A5A1SW1: PROBE SW
4A5A1SW2: EXT TANK WING SW
4A5A1SW3: EXT TANK CTR SW
4A5A1SW4: DUMP SW
4A5A2D1: APU LAMP
4A5A2L1: APU SW ON
4A5A2L2: ENG CRNK L
4A5A2L3: ENG CRNK R
4A5A2SW1: APU SW
4A5A2SW2: ENG CRANK SW
4A5A2W1J1, 4A5A2W1J2: SMP-05V-BC
4A5A2W2P1, 4A8A1W1P1: SMR-05V-B
4A6A1A1: (L298N MODULE)
4A6A1A1JP1: AKSPT/G
4A6A1A2: FCS BL
4A6A1A2RV1: RUD TRIM POT
4A6A1A2RV1M1: POT MOTOR
4A6A1A2SW1: T/O TRIM SW
4A6A1SW1: GAIN SW
4A6A1SW2: RESET SW
4A6A2A2: MC/HYD ISOL BL
4A6A2SW1: MC SW
4A6A2SW2: HYD ISO SW
4A7A1: ABSIS_Mega_2.0
4A7A1A2: COMM BL
4A7A1RV1: VOX POT
4A7A1RV2: ICS POT
4A7A1RV3: RWR POT
4A7A1RV4: WPN POT
4A7A1RV5: MIDS B POT
4A7A1RV6: MIDS A POT
4A7A1RV7: TCN POT
4A7A1RV8: AUX POT
4A7A1SW1: RLY SW
4A7A1SW2: G XMT SW
4A7A1SW3: ILS UFC SW
4A7A1SW4: IFF CRYPTO SW
4A7A1SW5: IFF MASTER SW
4A7A1SW6: IFF MODE 4 SW
4A7A1SW7: ILS CHAN SW
4A7A1W1P4, 4A7A1W2P6, 4A7A1W3P3: M20-1071000
4A7A1W3J1: SMP-06V-BC
4A7A2A2: OBOGS BL
4A7A2SW1: OBOGS SW
4A7A2SW2: OXY FLOW SW
4A7A4A2: ANT SEL BL
4A7A4J1: SMR-06V-B
4A7A4SW1: COMM 1 SW
4A7A4SW2: IFF SW
4A8A1SW1: FCS CHAN 1 SW
4A8A1SW2: FCS CHAN 2 SW
4A8A1SW3: SPD BRK SW
4A8A2SW1: DISPENSE SW
4A8A3SW1: NUC WPN SW
4A9A1: THROTTLE_CONTROLLER
4A9A1RV1: ANT ELEV
4A9A1SW1: CAGE/UNCAGE
4A9A1SW2: SPD BRK
4A9A1SW3: DISPENSE
4A9A1SW4: EXT LTS
4A9A1SW5: RAID/FLIR
4A9A1SW6: ATC ENGAGE
4A9A1SW7: INB MAX LIMIT
4A9A1SW8: INB IDLE LIMIT
4A9A1SW9: OUTB MAX LIMIT
4A9A1SW10: OUTB IDLE LIMIT
4A9A1W1P1, 4A9A1W1P2: PHR-5
4A9A1W2P1: PHR-4
4A9A1W3P1: PHR-3
4A9A1W4P1, 4A9A1W4P2, 4A9A1W5P1, 4A9A1W5P2: PHR-6
4A9A1Y1: IDLE DETENT
4A10RV1: BTK REMOTE
4A11A1: USB_3.0_4_Port_Hub
4A11A2, 4A11A3, 4A11A4: B09V6WY1SD
4A13A1W1: USB A TO MCR B
4A13A1W2: ABSIS-CA-G-XXX
4A13A1W3, 4A13A1W4, 4A14A1W2, 4A14A1W3: ABSIS-CA-F-XXX
4A13A1W5J1: 39-01-2221
4A13A1W5J2: SMP-08V-BC
4A13A1W6J1, 4A13A1W6J2: NL2MPXX
4A13A1W8: ABSIS-CA-C-XXX
4A14A1W1: 1689-01C
10A1A1A2: SIM PWR BL
10A1A1SW1: PC PWR
10A1A1SW2: MASTER PWR
10A1A1SW3: DISP PWR
10A1A1SW4: SIM MODE SW
10A1A1SW5: BACKLIGHT MODE
10A1A1W1P1: SMR-08V-B
(0A1W2): USB A TO B
(0A1W3): ABSIS-CA-C-XXX
(0A1W4), (0A1W5): ABSIS-CA-B-XXX
(3A1W1): USB B 3.2 TO C
(3A1W2), (3A1W3): ABSIS-CA-A-XXX
(4A13A1W1): (1681-02C)
(4A13A1W6), (4A13A1W7): (no value)
A4A9A1A1: THROTTLE_INNER_GRIP
A4A9A1A1A1: ANALOG_STICK_BREAKOUT
A4A9A1A1A2: HAT_SWITCH_BREAKOUT
A4A9A1A1W1P1: PHR-2
A4A9A1A1W2P1: PHR-5
A4A9A1A1W3P1: PHR-6
A4A9A1A1W4P1, A4A9A1A1W5P1, A4A9A1A1W6P1: PHR-3
A4A9A1A2, A4A9A1A3: ABSIS_Hall_Sensor
J1: (no value)
~: (no value)

Connections:
3A3A1_USB: 4A11A3., 4A14A1W1.1
4A1A_USB: 4A11A2., 4A13A1W10.1
4A1W11P6_+5V: 4A1W11P3.1, 4A1W11P4.1, 4A1W11P5.1, 4A1W11P6.1
4A1W11P6_GND: 4A1W11P3.2, 4A1W11P4.2, 4A1W11P5.2, 4A1W11P6.2
4A2A1_USB: 4A1W23.1, 4A11A2.
4A3A1_USB: 4A1W24.1, 4A11A2.
4A3A3_USB: 4A1W25.1, 4A11A2.
4A4A2_USB: 4A11A2.
4A5A1_USB: 4A1W27.1, 4A11A3.
4A5A2_USB: 4A1W26.1, 4A11A2.
4A6A1_USB: 4A1W28.1, 4A11A3.
4A7A1J1: 4A7A1.J1 (BUS_IN)
4A7A1J2: 4A7A1.J2 (BUS_OUT)
4A9A1_USB: 4A1W32.1, 4A11A3.
4A11A1_USB: 4A11A3., 4A13A1W1.1
4A11A3_USB: 4A11A2., 4A11A3.
4A11A4_USB: 4A11A3., 4A11A4.
4A12_USB: 4A13A1W1.1, (4A13A1W1).1
+5V_J3-9: 4A2A1.9 (+5V), 4A3A1.9 (+5V), 4A3A3.9 (+5V), 4A4A2.9 (+5V), 4A7A2.9 (+5V)
+5V_J3-11: 4A2A1.11 (+5V), 4A3A1.11 (+5V), 4A3A3.11 (+5V), 4A4A2.11 (+5V), 4A7A2.11 (+5V)
+5V_J4-9: 4A3A1.9 (+5V), 4A3A3.9 (+5V), 4A5A1.9 (+5V), 4A5A2.9 (+5V), 4A6A1.9 (+5V)
+5V_J4-11: 4A3A1.11 (+5V), 4A3A3.11 (+5V), 4A5A1.11 (+5V), 4A5A2.11 (+5V), 4A6A1.11 (+5V)
+5V_J4-17: 4A7A1.17 (+5V)
+5V_J4-19: 4A7A1.19 (+5V)
+5V_J5-18: 4A7A1.18 (GND)
+5V_J5-20: 4A7A1.20 (GND)
+5V_J6-18: 4A7A1.18 (GND)
+5V_J6-20: 4A7A1.20 (GND)
A0_J3-7: 4A2A1.7 (~D10/A10), 4A3A1.7 (~D10/A10), 4A3A3.7 (~D10/A10), 4A4A2.7 (~D10/A10), 4A7A2.7 (~D10/A10)
A0_J4-1: 4A7A1.1 (A0)
A1_J3-5: 4A2A1.5 (D16/MOSI), 4A3A1.5 (D16/MOSI), 4A3A3.5 (D16/MOSI), 4A4A2.5 (D16/MOSI), 4A7A2.5 (D16/MOSI)
A1_J4-3: 4A7A1.3 (A1)
A2_J3-3: 4A2A1.3 (D14/MISO), 4A3A1.3 (D14/MISO), 4A3A3.3 (D14/MISO), 4A4A2.3 (D14/MISO), 4A7A2.3 (D14/MISO)
A2_J4-5: 4A7A1.5 (A2)
A3_J3-1: 4A2A1.1 (D15/SCK), 4A3A1.1 (D15/SCK), 4A3A3.1 (D15/SCK), 4A4A2.1 (D15/SCK), 4A7A2.1 (D15/SCK)
A3_J4-7: 4A7A1.7 (A3)
A4_J4-9: 4A7A1.9 (A4)
A5_J4-11: 4A7A1.11 (A5)
A6_J4-13: 4A7A1.13 (A6)
A7_J4-15: 4A7A1.15 (A7)
A8_J4-16: 4A7A1.16 (A8)
A9_J4-14: 4A7A1.14 (A9)
A10_J4-12: 4A7A1.12 (A10)
A11_J4-10: 4A7A1.10 (A11)
A12_J4-8: 4A7A1.8 (A12)
A13_J4-6: 4A7A1.6 (A13)
A14_J4-4: 4A7A1.4 (A14)
A15_J4-2: 4A7A1.2 (A15)
ABSIS-C_SEAT_IN: (3A1W3).1
ABSIS-C_SEAT_OUT: (3A1W2).1
ANT_GND: 4A7A4J1.6, 4A7A4SW1.2, 4A7A4SW2.2
APU_GND: 4A5A2SW1.2 (B), 4A5A2SW2.2
APU_SW1: 4A5A2SW1.1 (A), 4A5A2W2P1.1
ASKID_SW: 4A3A1SW4.1 (A), 4A3A1W2P4.7
AUX_A: 4A7A1RV8.2, 4A7A1W1P4.8
BL_CH1: 4A13A1W7.1, (4A13A1W7).1
BL_CH2: 4A13A1W6.1, (4A13A1W6).1
BRKH_EMERG: 4A3A2SW2.2, 4A3A2W1P1.2
BRKH_GND: 4A3A2SW1.1, 4A3A2SW2.1, 4A3A2SW3.1, 4A3A2W1P1.4
BRKH_PARK: 4A3A2SW3.2, 4A3A2W1P1.3
BRKH_SECURE: 4A3A2SW1.2, 4A3A2W1P1.1
BRKP_+5V: 4A3A3D1.3 (VDD), 4A3A3W1P3.9
BRKP_DIN: 4A3A3D1.4 (DIN), 4A3A3W1P3.4
BRKP_GND: 4A3A3D1.2 (GND), 4A3A3W1P3.10
BRKP_M1: 4A3A3M1.1, 4A3A3W1P3.1
BRKP_M2: 4A3A3M1.2 (-), 4A3A3W1P3.2
BRKP_M3: 4A3A3M1.3, 4A3A3W1P3.3
BRKP_M4: 4A3A3M1.4, 4A3A3W1P3.5
BTKA+: 4A13A1W6J1.T, 4A13A1W6J2.T
BTKA+_LC: 0A1W1P2.T
BTKA+_SEAT: 3A1W4P1.T
BTKA-: 4A13A1W6J1.S, 4A13A1W6J2.S
BTKA-_LC: 0A1W1P2.S
BTKA-_SEAT: 3A1W4P1.S
BTKAR_+5V: 0A1W6P2.13, 4A10RV1.1, 4A10W1P1.1
BTKAR_A: 0A1W6P2.14, 4A10RV1.2, 4A10W1P1.2
BTKAR_GND: 0A1W6P2.15, 4A10RV1.3, 4A10W1P1.3
CH1_+: 4A2A1.1 (D15/SCK), 4A2A1L1P1.1, 4A2A1Y1.2, 4A3A1.1 (D15/SCK), 4A3A1L1.1 (-), 4A3A1L1P1.1, 4A5A1.1 (D15/SCK), 4A5A1L1.1 (-), 4A5A1L1P1.1, 4A5A2.1 (D15/SCK), 4A5A2L1.1 (-), 4A5A2L1P1.1
CH1_-: 4A2A1.2 (~D6/A7), 4A2A1L1P1.2, 4A2A1Y1.1, 4A3A1.2 (~D6/A7), 4A3A1L1.2 (+), 4A3A1L1P1.2, 4A5A1.2 (~D6/A7), 4A5A1L1.2 (+), 4A5A1L1P1.2, 4A5A2.2 (~D6/A7), 4A5A2L1.2 (+), 4A5A2L1P1.2
CH2_+: 4A3A1.1 (D15/SCK), 4A3A1L2.1 (-), 4A3A1L2P1.1, 4A5A2.1 (D15/SCK), 4A5A2L2.1 (-), 4A5A2L2P1.1, 4A5A2L3.1 (-)
CH2_-: 4A3A1.2 (~D6/A7), 4A3A1L2.2 (+), 4A3A1L2P1.2, 4A5A2.2 (~D6/A7), 4A5A2L2.2 (+), 4A5A2L2P1.2, 4A5A2L3.2 (+)
COMANT_SW1: 4A7A4J1.1, 4A7A4SW1.1
COMANT_SW2: 4A7A4J1.2, 4A7A4SW1.3
CRANK_SW1: 4A5A2SW2.1, 4A5A2W2P1.2
CRANK_SW2: 4A5A2SW2.3, 4A5A2W2P1.3
CTR_SW1: 4A5A1A1W1P1.5, 4A5A1SW3.1
CTR_SW2: 4A5A1A1W1P1.6, 4A5A1SW3.3
D2-SDA_J3-2: 4A2A1.2 (~D6/A7), 4A3A1.2 (~D6/A7), 4A3A3.2 (~D6/A7), 4A4A2.2 (~D6/A7), 4A7A2.2 (~D6/A7)
D4-A6_J3-6: 4A2A1.6 (D8/A8), 4A3A1.6 (D8/A8), 4A3A3.6 (D8/A8), 4A4A2.6 (D8/A8), 4A7A2.6 (D8/A8)
D7_J4-4: 4A3A1.4 (D7), 4A5A1.4 (D7), 4A5A2.4 (D7), 4A6A1.4 (D7)
D8-A8_J4-6: 4A3A1.6 (D8/A8), 4A3A3.6 (D8/A8), 4A5A1.6 (D8/A8), 4A5A2.6 (D8/A8), 4A6A1.6 (D8/A8)
D14-MISO_J4-3: 4A3A1.3 (D14/MISO), 4A3A3.3 (D14/MISO), 4A5A1.3 (D14/MISO), 4A5A2.3 (D14/MISO), 4A6A1.3 (D14/MISO)
D15-SCK_J4-1: 4A3A1.1 (D15/SCK), 4A3A3.1 (D15/SCK), 4A5A1.1 (D15/SCK), 4A5A2.1 (D15/SCK), 4A6A1.1 (D15/SCK)
D16-MOSI_J4-5: 4A3A1.5 (D16/MOSI), 4A3A3.5 (D16/MOSI), 4A5A1.5 (D16/MOSI), 4A5A2.5 (D16/MOSI), 4A6A1.5 (D16/MOSI)
D22_J6-15: 4A7A1.15 (A7)
D23_J6-16: 4A7A1.16 (A8)
D24_J6-13: 4A7A1.13 (A6)
D25_J6-14: 4A7A1.14 (A9)
D26_J6-11: 4A7A1.11 (A5)
D27_J6-12: 4A7A1.12 (A10)
D28_J6-9: 4A7A1.9 (A4)
D29_J6-10: 4A7A1.10 (A11)
D30_J6-7: 4A7A1.7 (A3)
D31_J6-8: 4A7A1.8 (A12)
D32_J6-5: 4A7A1.5 (A2)
D33_J6-6: 4A7A1.6 (A13)
D34_J6-3: 4A7A1.3 (A1)
D35_J6-4: 4A7A1.4 (A14)
D36_J6-1: 4A7A1.1 (A0)
D37_J6-2: 4A7A1.2 (A15)
D38_J5-15: 4A7A1.15 (A7)
D39_J5-16: 4A7A1.16 (A8)
D40_J5-13: 4A7A1.13 (A6)
D41_J5-14: 4A7A1.14 (A9)
D42_J5-11: 4A7A1.11 (A5)
D43_J5-12: 4A7A1.12 (A10)
D44_J5-9: 4A7A1.9 (A4)
D45_J5-10: 4A7A1.10 (A11)
D46_J5-7: 4A7A1.7 (A3)
D47_J5-8: 4A7A1.8 (A12)
D48_J5-5: 4A7A1.5 (A2)
D49_J5-6: 4A7A1.6 (A13)
D50_J5-3: 4A7A1.3 (A1)
D51_J5-4: 4A7A1.4 (A14)
D52_J5-1: 4A7A1.1 (A0)
D53_J5-2: 4A7A1.2 (A15)
DISP_GND: 4A8A2SW1.1, 4A8A2W1P1.2
DISP_SW1: 4A8A2SW1.2, 4A8A2W1P1.1
DUMP_SW1: 4A5A1A1W1P1.7, 4A5A1SW4.1 (A)
EXTLT_+5V: 4A4A2RV1.1, 4A4A2RV2.1, 4A4A2W1P3.9
EXTLT_GND: 4A4A2RV1.3, 4A4A2RV2.3, 4A4A2SW1.2, 4A4A2SW2.2 (B), 4A4A2W1P3.12
FCS_+5V_2: 4A6A1A1.1 (+12V), 4A6A1A2RV1.1, 4A6A1W1P4.11
FCS_CH1: 4A8A1SW1.2, 4A8A1W1P1.1
FCS_CH2: 4A8A1SW2.2, 4A8A1W1P1.2
FCS_GND: 4A6A1SW1.2 (B), 4A6A1SW2.1, 4A6A1W1P4.10
FCS_GND_2: 4A6A1A1.2 (GND), 4A6A1A2RV1.3, 4A6A1A2SW1.1, 4A6A1W1P4.12
FIRE_GND: 4A4A1SW1.2, 4A4A1W1P1.3
FIRE_SW1: 4A4A1SW1.1, 4A4A1W1P1.1
FIRE_SW2: 4A4A1SW1.3, 4A4A1W1P1.2
FLAPS_SW1: 4A3A1SW2.1, 4A3A1W1P3.1
FLAPS_SW2: 4A3A1SW2.3, 4A3A1W1P3.3
FORM_A: 4A4A2RV1.2, 4A4A2W1P3.1
FUEL_GND: 4A5A1A1W1P1.10, 4A5A1SW1.2, 4A5A1SW2.2, 4A5A1SW3.2, 4A5A1SW4.2 (B)
GAIN_SW1: 4A6A1SW1.1 (A), 4A6A1W1P4.8
GENTIE_GND: 4A4A3SW1.2 (B), 4A4A3W1P1.2
GENTIE_SW1: 4A4A3SW1.1 (A), 4A4A3W1P1.1
GND_J3-8: 4A2A1.8 (~D9/A9), 4A3A1.8 (~D9/A9), 4A3A3.8 (~D9/A9), 4A4A2.8 (~D9/A9), 4A7A2.8 (~D9/A9)
GND_J3-10: 4A2A1.10 (GND), 4A3A1.10 (GND), 4A3A3.10 (GND), 4A4A2.10 (GND), 4A7A2.10 (GND)
GND_J3-12: 4A2A1.12 (GND), 4A3A1.12 (GND), 4A3A3.12 (GND), 4A4A2.12 (GND), 4A7A2.12 (GND)
GND_J4-10: 4A3A1.10 (GND), 4A3A3.10 (GND), 4A5A1.10 (GND), 4A5A2.10 (GND), 4A6A1.10 (GND)
GND_J4-12: 4A3A1.12 (GND), 4A3A3.12 (GND), 4A5A1.12 (GND), 4A5A2.12 (GND), 4A6A1.12 (GND)
GND_J4-18: 4A7A1.18 (GND)
GND_J4-20: 4A7A1.20 (GND)
GND_J5-17: 4A7A1.17 (+5V)
GND_J5-19: 4A7A1.19 (+5V)
GND_J6-17: 4A7A1.17 (+5V)
GND_J6-19: 4A7A1.19 (+5V)
GXMT_SW1: 4A7A1SW2.1, 4A7A1W3P3.3
GXMT_SW2: 4A7A1SW2.3, 4A7A1W3P3.4
HOOKB_SW: 4A3A1SW5.1 (A), 4A3A1W1P3.7
HYD_SW1: 4A6A2SW2.1 (A), 4A7A3W1P1.3
ICS_A: 4A7A1RV2.2, 4A7A1W1P4.2
IFFANT_SW1: 4A7A4J1.3, 4A7A4SW2.1
IFFANT_SW2: 4A7A4J1.4, 4A7A4SW2.3
IFFCRY_SW1: 4A7A1SW4.1, 4A7A1W3P3.6
IFFCRY_SW2: 4A7A1SW4.3, 4A7A1W3P3.7
IFFMAS_SW1: 4A7A1SW5.1 (A), 4A7A1W3P3.8
ILSUFC_SW1: 4A7A1SW3.1 (A), 4A7A1W3P3.5
ILS_SW1: 4A7A1SW7.1, 4A7A1W1P4.13
ILS_SW2: 4A7A1SW7.2, 4A7A1W1P4.14
ILS_SW3: 4A7A1SW7.3, 4A7A1W1P4.15
ILS_SW4: 4A7A1SW7.4, 4A7A1W1P4.16
ILS_SW5: 4A7A1SW7.5, 4A7A1W2P6.1
ILS_SW6: 4A7A1SW7.6, 4A7A1W2P6.2
ILS_SW7: 4A7A1SW7.7, 4A7A1W2P6.3
ILS_SW8: 4A7A1SW7.8, 4A7A1W2P6.4
ILS_SW9: 4A7A1SW7.9, 4A7A1W2P6.5
ILS_SW10: 4A7A1SW7.10, 4A7A1W2P6.6
ILS_SW11: 4A7A1SW7.11, 4A7A1W2P6.7
ILS_SW12: 4A7A1SW7.12, 4A7A1W2P6.8
ILS_SW13: 4A7A1SW7.13, 4A7A1W2P6.9
ILS_SW14: 4A7A1SW7.14, 4A7A1W2P6.10
ILS_SW15: 4A7A1SW7.15, 4A7A1W2P6.11
ILS_SW16: 4A7A1SW7.16, 4A7A1W2P6.12
ILS_SW17: 4A7A1SW7.17, 4A7A1W2P6.13
ILS_SW18: 4A7A1SW7.18, 4A7A1W2P6.14
ILS_SW19: 4A7A1SW7.19, 4A7A1W2P6.15
ILS_SW20: 4A7A1SW7.20, 4A7A1W2P6.16
INTRW_SW1: 4A4A2SW2.1 (A), 4A4A2W1P3.5
LADG_SW: 4A3A1SW3.1 (A), 4A3A1W1P3.6
LBAR_SW: 4A3A1SW1.1 (A), 4A3A1W1P3.5
LC<>ABSIS_PSU_PWR: (0A1W3).1
LC<>BL1: (0A1W4).1
LC<>BL2: (0A1W5).1
LC<>STICK_USB: (3A1W1).1
LC<>UIP_USB_HUB: (0A1W2).1
LCLBAR: 4A8A1SW4.2, 4A8A1W1P1.4
LCSPDBRK: 4A8A1SW3.2, 4A8A1W1P1.3
LC_GND: 4A8A1SW1.1, 4A8A1SW2.1, 4A8A1SW3.1, 4A8A1SW4.1, 4A8A1W1P1.5
LG_EMERG: 4A2A1A2SW2.2, 4A2A1A2W1P1.2
LG_GND: 4A2A1A2SW1.1, 4A2A1A2SW2.1, 4A2A1A2W1P1.4, 4A2A1R1.1
LG_GND2: 4A2A1SW1.1, 4A2A1SW2.1, 4A2A1W1P3.10
LG_LED: 4A2A1A2D1.2 (A), 4A2A1A2W1P1.3
LG_LIMIT: 4A2A1A2SW1.2, 4A2A1A2W1P1.1
LG_ORIDE: 4A2A1SW2.2, 4A2A1W1P3.3
LG_WARN: 4A2A1SW1.2, 4A2A1W1P3.1
MC_GND: 4A6A2SW1.2, 4A6A2SW2.2 (B), 4A7A3W1P1.4
MC_SW1: 4A6A2SW1.1, 4A7A3W1P1.1
MC_SW2: 4A6A2SW1.3, 4A7A3W1P1.2
MIDSA_A: 4A7A1RV6.2, 4A7A1W1P4.6
MIDSB_A: 4A7A1RV5.2, 4A7A1W1P4.5
MODE4_SW1: 4A7A1SW6.1, 4A7A1W3P3.9
MODE4_SW2: 4A7A1SW6.3, 4A7A1W3P3.10
NC-SPARE_8: 0A1W6P2.8
NC-SPARE_16: 0A1W6P2.16
NC-SPARE_17: 0A1W6P2.17
NC-SPARE_18: 0A1W6P2.18
NC-SPARE_19: 0A1W6P2.19
NC-SPARE_20: 0A1W6P2.20
NC-SPARE_21: 0A1W6P2.21
NC-SPARE_22: 0A1W6P2.22
NUC_GND: 4A8A3SW1.2 (B), 4A8A3W1P1.2
NUC_SW1: 4A8A3SW1.1 (A), 4A8A3W1P1.1
unnamed: 4A1A1.J1 (POWER), ~.1
unnamed: 4A1A1.J2 (BUS_#1), ~.1
unnamed: 4A1A1.USB, ~.1
unnamed: 4A1W1.1, ~.1
unnamed: 4A1W2.1, ~.1
unnamed: 4A1W3.1, ~.1
unnamed: 4A1W4.1, ~.1
unnamed: 4A1W5.1, ~.1
unnamed: 4A1W6.1, ~.1
unnamed: 4A1W7.1, ~.1
unnamed: 4A1W8.1, ~.1
unnamed: 4A1W10.1, ~.1
unnamed: 4A1W11.1, 4A1W11P2.1
unnamed: 4A1W12.1, ~.1
unnamed: 4A1W13.1, ~.1
unnamed: 4A1W14.1, ~.1
unnamed: 4A1W15.1, ~.1
unnamed: 4A1W16.1, ~.1
unnamed: 4A1W17.1, ~.1
unnamed: 4A1W18.1, ~.1
unnamed: 4A1W19.1, ~.1
unnamed: 4A1W20.1, ~.1
unnamed: 4A1W21.1, ~.1
unnamed: 4A1W22.1, ~.1
unnamed: 4A2A1.1 (D15/SCK), 4A2A1.2 (~D6/A7)
unnamed: 4A2A1.J1 (BUS_IN), 4A2A1J1.1
unnamed: 4A2A1.J2 (BUS_OUT), 4A2A1J2.1
unnamed: 4A2A1.USB, 4A2A1~.1
unnamed: 4A2A1A2.J1 (BLC_IN), ~.1
unnamed: 4A2A1A2.J2 (BLC_OUT), ~.1
unnamed: 4A2A1A2D1.1 (K), 4A2A1R1.2
unnamed: 4A2A1W1J1.1, 4A2A1W1P3.4
unnamed: 4A2A1W1J1.2, 4A2A1W1P3.5
unnamed: 4A2A1W1J1.3, 4A2A1W1P3.6
unnamed: 4A2A1W1J1.4, 4A2A1W1P3.8
unnamed: 4A2A1Y2.1, 4A9A1W7P1.1
unnamed: 4A2A1Y2.2, 4A9A1W7P1.2
unnamed: 4A2A1~.1, 4A3A1.USB, 4A3A3.USB, 4A5A1.USB, 4A5A1A2.J1 (BLC_IN), 4A5A1A2.J2 (BLC_OUT), 4A5A2.USB, 4A6A1.USB, 4A6A1A2.J1 (BLC_IN), 4A6A1A2.J2 (BLC_OUT), 4A6A2A2.J1 (BLC_IN), 4A6A2A2.J2 (BLC_OUT), 4A7A1A2.J1 (BLC_IN), 4A7A1A2.J2 (BLC_OUT), 4A7A2A2.J1 (BLC_IN), 4A7A2A2.J2 (BLC_OUT), 4A7A4A2.J1 (BLC_IN), 4A7A4A2.J2 (BLC_OUT), 4A9A1.J1 (EXT_+5V), 4A9A1.USB
unnamed: 4A3A1.1 (D15/SCK), 4A3A1.2 (~D6/A7)
unnamed: 4A3A1.J1 (BUS_IN), 4A3A1J1.1
unnamed: 4A3A1.J2 (BUS_OUT), 4A3A1J2.1
unnamed: 4A3A1A2.J1 (BLC_IN), ~.1
unnamed: 4A3A1A2.J2 (BLC_OUT), ~.1
unnamed: 4A3A3.J1 (BUS_IN), 4A3A3J1.1
unnamed: 4A3A3.J2 (BUS_OUT), 4A3A3J2.1
unnamed: 4A3A3W1J1.1, 4A3A3W1P3.6
unnamed: 4A3A3W1J1.2, 4A3A3W1P3.7
unnamed: 4A3A3W1J1.3, 4A3A3W1P3.8
unnamed: 4A3A3W2J1.1, 4A3A3W2P4.1
unnamed: 4A3A3W2J1.2, 4A3A3W2P4.2
unnamed: 4A3A3W2J1.3, 4A3A3W2P4.3
unnamed: 4A3A3W2J1.4, 4A3A3W2P4.10
unnamed: 4A4A1A2.J1 (BLC_IN), ~.1
unnamed: 4A4A1A2.J2 (BLC_OUT), ~.1
unnamed: 4A4A2.J1 (BUS_IN), 4A4A2J1.1
unnamed: 4A4A2.J2 (BUS_OUT), 4A4A2J2.1
unnamed: 4A4A2A2.J1 (BLC_IN), ~.1
unnamed: 4A4A2A2.J2 (BLC_OUT), ~.1
unnamed: 4A4A2W1J1.1, 4A4A2W1P3.6
unnamed: 4A4A2W1J1.2, 4A4A2W1P3.8
unnamed: 4A4A2W1J2.1, 4A4A2W1P3.7
unnamed: 4A4A2W1J2.2, 4A4A2W1P3.10
unnamed: 4A4A3A2.J1 (BLC_IN), ~.1
unnamed: 4A4A3A2.J2 (BLC_OUT), ~.1
unnamed: 4A5A1.1 (D15/SCK), 4A5A1.2 (~D6/A7)
unnamed: 4A5A1.J1 (BUS_IN), 4A5A1J1.1
unnamed: 4A5A1.J2 (BUS_OUT), 4A5A1J2.1
unnamed: 4A5A1A2.J1 (BLC_IN), ~.1
unnamed: 4A5A1A2.J2 (BLC_OUT), ~.1
unnamed: 4A5A2.1 (D15/SCK), 4A5A2.2 (~D6/A7)
unnamed: 4A5A2.J1 (BUS_IN), 4A5A2J1.1
unnamed: 4A5A2.J2 (BUS_OUT), 4A5A2J2.1
unnamed: 4A5A2D1.1 (K), 4A5A2D1P1.1
unnamed: 4A5A2D1.2 (A), 4A5A2D1P1.2
unnamed: 4A5A2W1J1.1, 4A5A2W1P4.1
unnamed: 4A5A2W1J1.2, 4A5A2W1P4.2
unnamed: 4A5A2W1J1.3, 4A5A2W1P4.3
unnamed: 4A5A2W1J1.4, 4A5A2W1P4.4
unnamed: 4A5A2W1J1.5, 4A5A2W1P4.10
unnamed: 4A5A2W1J2.1, 4A5A2W1P4.5
unnamed: 4A5A2W1J2.2, 4A5A2W1P4.6
unnamed: 4A5A2W1J2.3, 4A5A2W1P4.7
unnamed: 4A5A2W1J2.4, 4A5A2W1P4.8
unnamed: 4A5A2W1J2.5, 4A5A2W1P4.12
unnamed: 4A5A2W2P1.4, 4A5A2W2P2.1
unnamed: 4A5A2W2P1.5, 4A5A2W2P2.2
unnamed: 4A6A1.J1 (BUS_IN), 4A6A1J1.1
unnamed: 4A6A1.J2 (BUS_OUT), 4A6A1J1.1
unnamed: 4A6A1A1.1 (+12V), 4A6A1A1JP1.1 (A)
unnamed: 4A6A1A1.2 (GND), 4A6A1A1JP1.2 (B)
unnamed: 4A7A1W3J1.1, 4A7A1W3P3.12
unnamed: 4A7A1W3J1.2, 4A7A1W3P3.13
unnamed: 4A7A1W3J1.3, 4A7A1W3P3.14
unnamed: 4A7A1W3J1.4, 4A7A1W3P3.15
unnamed: 4A7A1W3J1.5, 4A7A1W3P3.16
unnamed: 4A7A1W3J1.6, 4A7A1W3P3.17
unnamed: 4A7A2.J1 (BUS_IN), ~.1
unnamed: 4A7A2.J2 (BUS_OUT), ~.1
unnamed: 4A7A2W1J1.1, 4A7A2W1P1.4
unnamed: 4A7A2W1J1.2, 4A7A2W1P1.5
unnamed: 4A7A2W1J1.3, 4A7A2W1P1.6
unnamed: 4A7A2W1J1.4, 4A7A2W1P1.12
unnamed: 4A7A2W1J2.1, 4A7A2W1P1.3
unnamed: 4A7A2W1J2.2, 4A7A2W1P1.10
unnamed: 4A9A1.J2 (X/OUTB), ~.1
unnamed: 4A9A1.J3 (Y/INB), ~.1
unnamed: 4A9A1.J5 (INB_GRIP), ~.1
unnamed: 4A9A1.J6 (OUTB_GRIP), ~.1
unnamed: 4A9A1.J7 (INB_LIMIT), ~.1
unnamed: 4A9A1.J8 (OUTB_LIMIT), ~.1
unnamed: 4A9A1.J9 (IDLE_DET), ~.1
unnamed: 4A9A1.J10 (MAX_DET), ~.1
unnamed: 4A9A1RV1.1, A4A9A1A1W4P1.1
unnamed: 4A9A1RV1.2, A4A9A1A1W4P1.2
unnamed: 4A9A1RV1.3, A4A9A1A1W4P1.3
unnamed: 4A9A1SW1.1, A4A9A1A1W1P1.2
unnamed: 4A9A1SW1.2, A4A9A1A1W1P1.1
unnamed: 4A9A1SW2.1, A4A9A1A1W5P1.1
unnamed: 4A9A1SW2.2, A4A9A1A1W5P1.2
unnamed: 4A9A1SW2.3, A4A9A1A1W5P1.3
unnamed: 4A9A1SW3.1, A4A9A1A1W6P1.1
unnamed: 4A9A1SW3.2, A4A9A1A1W6P1.2
unnamed: 4A9A1SW3.3, A4A9A1A1W6P1.3
unnamed: 4A9A1SW4.1 (A), 4A9A1W2P1.1
unnamed: 4A9A1SW4.2 (B), 4A9A1SW5.1, 4A9A1SW6.1, 4A9A1W2P1.4
unnamed: 4A9A1SW5.2, 4A9A1W2P1.2
unnamed: 4A9A1SW6.2, 4A9A1W2P1.3
unnamed: 4A9A1SW7.1, 4A9A1W3P1.1
unnamed: 4A9A1SW7.2, 4A9A1SW8.2, 4A9A1W3P1.3
unnamed: 4A9A1SW8.1, 4A9A1W3P1.2
unnamed: 4A9A1SW9.1, 4A9A1W3P1.1
unnamed: 4A9A1SW10.1, 4A9A1W3P1.2
unnamed: 4A9A1SW9.2, 4A9A1SW10.2, 4A9A1W3P1.3
unnamed: 4A9A1W1P1.1, 4A9A1W1P2.1
unnamed: 4A9A1W1P1.2, 4A9A1W1P2.2
unnamed: 4A9A1W1P1.3, 4A9A1W1P2.3
unnamed: 4A9A1W1P1.4, 4A9A1W1P2.4
unnamed: 4A9A1W1P1.5, 4A9A1W1P2.5
unnamed: 4A9A1W4P1.1, 4A9A1W4P2.1
unnamed: 4A9A1W4P1.2, 4A9A1W4P2.2
unnamed: 4A9A1W4P1.3, 4A9A1W4P2.3
unnamed: 4A9A1W4P1.4, 4A9A1W4P2.4
unnamed: 4A9A1W4P1.5, 4A9A1W4P2.5
unnamed: 4A9A1W4P1.6, 4A9A1W4P2.6
unnamed: 4A9A1W5P1.1, 4A9A1W5P2.1
unnamed: 4A9A1W5P1.2, 4A9A1W5P2.2
unnamed: 4A9A1W5P1.3, 4A9A1W5P2.3
unnamed: 4A9A1W5P1.4, 4A9A1W5P2.4
unnamed: 4A9A1W5P1.5, 4A9A1W5P2.5
unnamed: 4A9A1W5P1.6, 4A9A1W5P2.6
unnamed: 4A9A1W6P1.1, 4A9A1Y1.1
unnamed: 4A9A1W6P1.2, 4A9A1Y1.2
unnamed: 4A11A1.1 (USB_3.0_A_Type), ~.1
unnamed: 4A11A1.2 (+5VDC), ~.S
unnamed: 4A11A1.3 (GND), ~.T
unnamed: 4A11A2., ~.1, ~.2
unnamed: 4A11A3., ~.1, ~.2
unnamed: 4A11A4., ~.1, ~.2
unnamed: 4A13A1W2.1, ~.1
unnamed: 4A13A1W3.1, ~.1
unnamed: 4A13A1W4.1, ~.1
unnamed: 4A13A1W5J1.1, 4A13A1W5J2.1
unnamed: 4A13A1W5J1.2, 4A13A1W5J2.2
unnamed: 4A13A1W5J1.3, 4A13A1W5J2.3
unnamed: 4A13A1W5J1.4, 4A13A1W5J2.4
unnamed: 4A13A1W5J1.5, 4A13A1W5J2.5
unnamed: 4A13A1W5J1.6, 4A13A1W5J2.6
unnamed: 4A13A1W5J1.7, 4A13A1W5J2.7
unnamed: 4A13A1W5J1.8, 4A13A1W5J2.8
unnamed: 4A13A1W5J1.9, 4A13A1W5J3.1
unnamed: 4A13A1W5J1.10, 4A13A1W5J3.2
unnamed: 4A13A1W5J1.11, 4A13A1W5J3.3
unnamed: 4A13A1W5J1.12, 4A13A1W5J3.4
unnamed: 4A13A1W5J1.13, 4A13A1W5J4.1
unnamed: 4A13A1W5J1.14, 4A13A1W5J4.2
unnamed: 4A13A1W5J1.15, 4A13A1W5J4.3
unnamed: 4A13A1W5J1.16, 4A13A1W5J4.4
unnamed: 4A13A1W8.1, ~.1
unnamed: 10A1A1A2.J1 (BLC_IN), ~.1
unnamed: 10A1A1A2.J2 (BLC_OUT), ~.1
unnamed: A4A9A1A1.ANT1 (ANT_ELEV), ~.1
unnamed: A4A9A1A1.CAGE1 (CAGE), ~.1
unnamed: A4A9A1A1.CM1 (CM_SW), ~.1
unnamed: A4A9A1A1.COM1 (COMM_SW), ~.1
unnamed: A4A9A1A1.J2 (OUTPUT), ~.1
unnamed: A4A9A1A1.JOY1 (TDC), ~.1
unnamed: A4A9A1A1.SP1 (SPD_BRK), ~.1
unnamed: A4A9A1A1A1.J2 (+5V), A4A9A1A1W2P1.1
unnamed: A4A9A1A1A1.J3 (X-AXIS), A4A9A1A1W2P1.2
unnamed: A4A9A1A1A1.J4 (Y-AXIS), A4A9A1A1W2P1.3
unnamed: A4A9A1A1A1.J5 (PUSH), A4A9A1A1W2P1.4
unnamed: A4A9A1A1A1.J6 (GND), A4A9A1A1W2P1.5
unnamed: A4A9A1A1A2.J1 (A), A4A9A1A1W3P1.1
unnamed: A4A9A1A1A2.J2 (B), A4A9A1A1W3P1.2
unnamed: A4A9A1A1A2.J3 (C), A4A9A1A1W3P1.3
unnamed: A4A9A1A1A2.J4 (D), A4A9A1A1W3P1.4
unnamed: A4A9A1A1A2.J5 (PUSH), A4A9A1A1W3P1.5
unnamed: A4A9A1A1A2.J6 (COM), A4A9A1A1W3P1.6
unnamed: A4A9A1A2.J1-1 (VDD), J1.1
unnamed: A4A9A1A2.J1-2 (MISO), J1.2
unnamed: A4A9A1A2.J1-3 (MOSI), J1.3
unnamed: A4A9A1A2.J1-4 (SCK), J1.4
unnamed: A4A9A1A2.J1-5 (CSN), J1.5
unnamed: A4A9A1A2.J1-6 (GND), J1.6
unnamed: A4A9A1A3.J1-1 (VDD), J1.1
unnamed: A4A9A1A3.J1-2 (MISO), J1.2
unnamed: A4A9A1A3.J1-3 (MOSI), J1.3
unnamed: A4A9A1A3.J1-4 (SCK), J1.4
unnamed: A4A9A1A3.J1-5 (CSN), J1.5
unnamed: A4A9A1A3.J1-6 (GND), J1.6
OBOGS_GND: 4A7A2SW1.2 (B), 4A7A2SW2.2 (B), 4A7A2W1P1.8
OBOGS_SW1: 4A7A2SW1.1 (A), 4A7A2W1P1.1
OXY_FLOW_SW1: 4A7A2SW2.1 (A), 4A7A2W1P1.2
P3_GND: 4A7A1SW1.2, 4A7A1SW2.2, 4A7A1SW3.2 (B), 4A7A1SW4.2, 4A7A1SW5.2 (B), 4A7A1SW6.2, 4A7A1W3P3.19
P4_+5V: 4A7A1RV1.1, 4A7A1RV2.1, 4A7A1RV3.1, 4A7A1RV4.1, 4A7A1RV5.1, 4A7A1RV6.1, 4A7A1RV7.1, 4A7A1RV8.1, 4A7A1W1P4.19
P4_GND: 4A7A1RV1.3, 4A7A1RV2.3, 4A7A1RV3.3, 4A7A1RV4.3, 4A7A1RV5.3, 4A7A1RV6.3, 4A7A1RV7.3, 4A7A1RV8.3, 4A7A1W1P4.20
P6_GND: 4A7A1SW7.COM, 4A7A1W2P6.19
POSI_A: 4A4A2RV2.2, 4A4A2W1P3.3
PROBE_SW1: 4A5A1A1W1P1.1, 4A5A1SW1.1
PROBE_SW2: 4A5A1A1W1P1.2, 4A5A1SW1.3
RESET_SW1: 4A6A1SW2.2, 4A6A1W1P4.7
RLY_SW1: 4A7A1SW1.1, 4A7A1W3P3.1
RLY_SW2: 4A7A1SW1.3, 4A7A1W3P3.2
RUD_TRIM_A: 4A6A1A2RV1.2, 4A6A1W1P4.6
RUD_TRIM_DIR_A: 4A6A1A1.2 (GND), 4A6A1W1P4.3
RUD_TRIM_DIR_B: 4A6A1A1.3 (+5V), 4A6A1W1P4.4
RUD_TRIM_M+: 4A6A1A1.1 (+12V), 4A6A1A2RV1M1.1 (+)
RUD_TRIM_M-: 4A6A1A1.2 (GND), 4A6A1A2RV1M1.2 (-)
RWR_A: 4A7A1RV3.2, 4A7A1W1P4.3
SIMPWR_BLM_A: 0A1W6P2.9, 10A1A1SW5.A, 10A1A1W2P1.1
SIMPWR_BLM_B: 0A1W6P2.10, 10A1A1SW5.B, 10A1A1W2P1.2
SIMPWR_BLM_GND: 0A1W6P2.12, 10A1A1SW5.C, 10A1A1SW5.S2, 10A1A1W2P1.4
SIMPWR_BLM_PUSH: 0A1W6P2.11, 10A1A1SW5.S1, 10A1A1W2P1.3
SIMPWR_DISP: 0A1W6P2.4, 10A1A1SW3.1 (A), 10A1A1W1P1.4
SIMPWR_GND: 0A1W6P2.7, 10A1A1SW1.2, 10A1A1SW2.2 (B), 10A1A1SW3.2 (B), 10A1A1SW4.2, 10A1A1W1P1.7
SIMPWR_MAINT: 0A1W6P2.6, 10A1A1SW4.3, 10A1A1W1P1.6
SIMPWR_MASTER: 0A1W6P2.3, 10A1A1SW2.1 (A), 10A1A1W1P1.3
SIMPWR_PCPWR: 0A1W6P2.1, 10A1A1SW1.1, 10A1A1W1P1.1
SIMPWR_PCRESET: 0A1W6P2.2, 10A1A1SW1.3, 10A1A1W1P1.2
SIMPWR_PFLT: 0A1W6P2.5, 10A1A1SW4.1, 10A1A1W1P1.5
SJET_GND: 4A3A1SW6.1, 4A3A1SW7.C (COM), 4A3A1W2P4.10
SJET_PUSH: 4A3A1SW6.2, 4A3A1W2P4.1
SJET_SW1: 4A3A1SW7.1, 4A3A1W2P4.2
SJET_SW2: 4A3A1SW7.2, 4A3A1W2P4.3
SJET_SW3: 4A3A1SW7.3, 4A3A1W2P4.4
SJET_SW4: 4A3A1SW7.4, 4A3A1W2P4.5
SJET_SW5: 4A3A1SW7.5, 4A3A1W2P4.6
SJ_GND1: 4A3A1SW1.2 (B), 4A3A1SW2.2, 4A3A1SW3.2 (B), 4A3A1SW5.2 (B), 4A3A1W1P3.8
SJ_GND2: 4A3A1SW4.2 (B), 4A3A1W2P4.12
STROBE_SW1: 4A4A2SW1.1, 4A4A2W1P3.2
STROBE_SW2: 4A4A2SW1.3, 4A4A2W1P3.4
TCN_A: 4A7A1RV7.2, 4A7A1W1P4.7
TO_SW1: 4A6A1A2SW1.2, 4A6A1W1P4.1
VOX_A: 4A7A1RV1.2, 4A7A1W1P4.1
WING_SW1: 4A5A1A1W1P1.3, 4A5A1SW2.1
WING_SW2: 4A5A1A1W1P1.4, 4A5A1SW2.3
WPN_A: 4A7A1RV4.2, 4A7A1W1P4.4
~D3_SCL_J3-4: 4A2A1.4 (D7), 4A3A1.4 (D7), 4A3A3.4 (D7), 4A4A2.4 (D7), 4A7A2.4 (D7)
~D6-A7_J4-2: 4A3A1.2 (~D6/A7), 4A3A3.2 (~D6/A7), 4A5A1.2 (~D6/A7), 4A5A2.2 (~D6/A7), 4A6A1.2 (~D6/A7)
~D9-A9_J4-8: 4A3A1.8 (~D9/A9), 4A3A3.8 (~D9/A9), 4A5A1.8 (~D9/A9), 4A5A2.8 (~D9/A9), 4A6A1.8 (~D9/A9)
~D10-A10_J4-7: 4A3A1.7 (~D10/A10), 4A3A3.4 (D7), 4A3A3.7 (~D10/A10), 4A5A1.7 (~D10/A10), 4A5A2.7 (~D10/A10), 4A6A1.7 (~D10/A10)
~RUD_TRIM_SPD: 4A6A1A1.1 (+12V), 4A6A1W1P4.2

Notes on the sheet:
SIMPWR_MAINT
+5V_J3-9
D8-A8_J4-6
SIMPWR_PCPWR
GND
D39_J5-16
A1_J3-5
+5V_J3-11
BTKAR_GND
A0_J4-1
+5V_J4-9
~{D3_SCL}_J3-4
D4-A6_J3-6
~{D10-A10}_J4-7
D53_J5-2
GND_J3-8
BRKH_PARK
APU
OBOGS
GEN TIE PANEL
GND_J3-12
GENTIE_GND
~{SCL}
OBOGS PANEL
A3_J3-1
GND_J4-12
+5V_J4-11
A5_J4-11
SELECT JETT
D49_J5-6
DISP_GND
D38_J5-15
APU_GND
D7_J4-4
A12_J4-8
ANT SEL PANEL
NC/SPARE
CRANK_SW1
APU_LAMP
A0_J3-7
USB HUBS
D45_J5-10
GND_J4-10
A2_J3-3
SIMPWR_DISP
SDA
D52_J5-1
BRK GAUGE, ETC
D47_J5-8
FCS PANEL
MOSI
+5V_J6-20
D16-MOSI_J4-5
A2_J4-5
A13_J4-6
EXT LTS
2X 10AWG
NUC_GND
D27_J6-12
A6_J4-13
LG_LIMIT
+5V_J5-20
LG_GND
D2-SDA_J3-2
~{D9-A9}_J4-8
FIRE_GND
D41_J5-14
D26_J6-11
THROTTLE
D32_J6-5
MC_SW1
4A14A1
+5V_J4-17
APU_SW1
A1_J4-3
D44_J5-9
BTKAR_+5V
A10_J4-12
BRKH_SECURE
HYD_SW1
GND_J3-10
A9_J4-14
FIRE TEST PANEL
LEFT CONSOLE (LCON/LC)
(4A1W11)
4-PRT USB HUB
BRKH_GND
D43_J5-12
D29_J6-10
A8_J4-16
COMM PANEL
FIRE_SW2
FUTURE EXP
SIMPWR_MASTER
D35_J6-4
~{D6-A7}_J4-2
+12V PIN ACCEPTS +5V-12V
D14-MISO_J4-3
4A13A1
LG_LED
MC/HYD ISO PANEL
LDG GEAR PANEL
D15-SCK_J4-1
SIMPWR_BLM_A
NOTE: USE BUS TERMINATION RESISTOR ON 4A7A2J2
SCK
CSy
D25_J6-14
+5V_J6-18
EXT LIGHTS PANEL
LC USB HUB #2
BUTTKICKER REMOTE
BRAKE HANDLE
EXT LTS, ETC
LDG GEAR
SELECT JETT PANEL
D33_J6-6
A7_J4-15
ECM DISP SWITCH
LEFT CIRCUIT BREAKERS
SIMPWR_PCRESET
IFFANT_SW2
FIRE_SW1
DISP_SW1
+5V_J4-19
LCSPDBRK
BTKAR_A
INBOARD THROTTLE GRIP
GND_J6-19
D46_J5-7
BRK PRESS GAUGE
NUC WPN PANEL
GENTIE_SW1
APU, ETC
***4A1W11 MODIFIED*** +5V/GND LINES ONLY REMOVE SECOND CONNECTOR TERMINATE WITH SPLICED OEM CONNECTOR TO CREATE P2 TERMINATE P3/P4/P5/P6 AS SHOWN
LIP -> LC BULKHEAD
SIMPWR_BLM_GND
FUEL PANEL
D48_J5-5
D30_J6-7
GND_J5-17
SIMPWR_BLM_B
CENTER TUB
MISO
ANT_GND
LC USB HUB #3
6X FL2
LC_GND
COMANT_SW1
BRKH_EMERG
SIMPWR_BLM_PUSH
AXIS SENSORS
(ABSIS-CA-A-XXX ***MODIFIED***)
CRANK_SW2
D42_J5-11
THROTTLE LIMIT SWITCHES
RAID/FLIR
A3_J4-7
D50_J5-3
GND_J4-18
+3.3V
D22_J6-15
THIS HUB IS LOCATED INBOARD OF OBOGS AND AVAILABLE FOR OPERATOR USE.
D28_J6-9
A4_J4-9
DETENT SOLENOIDS
LG_EMERG
LCLBAR
TO COMM PANEL
A11_J4-10
FCS_CH1
D34_J6-3
BACKLIGHTING PANELS
OUTBOARD THROTTLE GRIP
D51_J5-4
D40_J5-13
LC HID MASTER
D23_J6-16
D37_J6-2
LC -> SEAT BULKHEAD
GND_J6-17
D36_J6-1
CSx
COMANT_SW2
A15_J4-2
ATC ENG
+5V_J5-18
IFFANT_SW1
GND_J4-20
D31_J6-8
FCS_CH2
SIMPWR_PFLT
MC_GND
MC_SW2
NUC_SW1
SIM PWR PANEL
D24_J6-13
A14_J4-4
SIMPWR_GND
GND_J5-19
