jrsteensen/OpenHornet/ECAD/interconnects/OH_Lower_Instrument_Panel.kicad_sch

## KiCad design ECAD/interconnects/OH_Lower_Instrument_Panel.kicad_sch (2026-09-24)

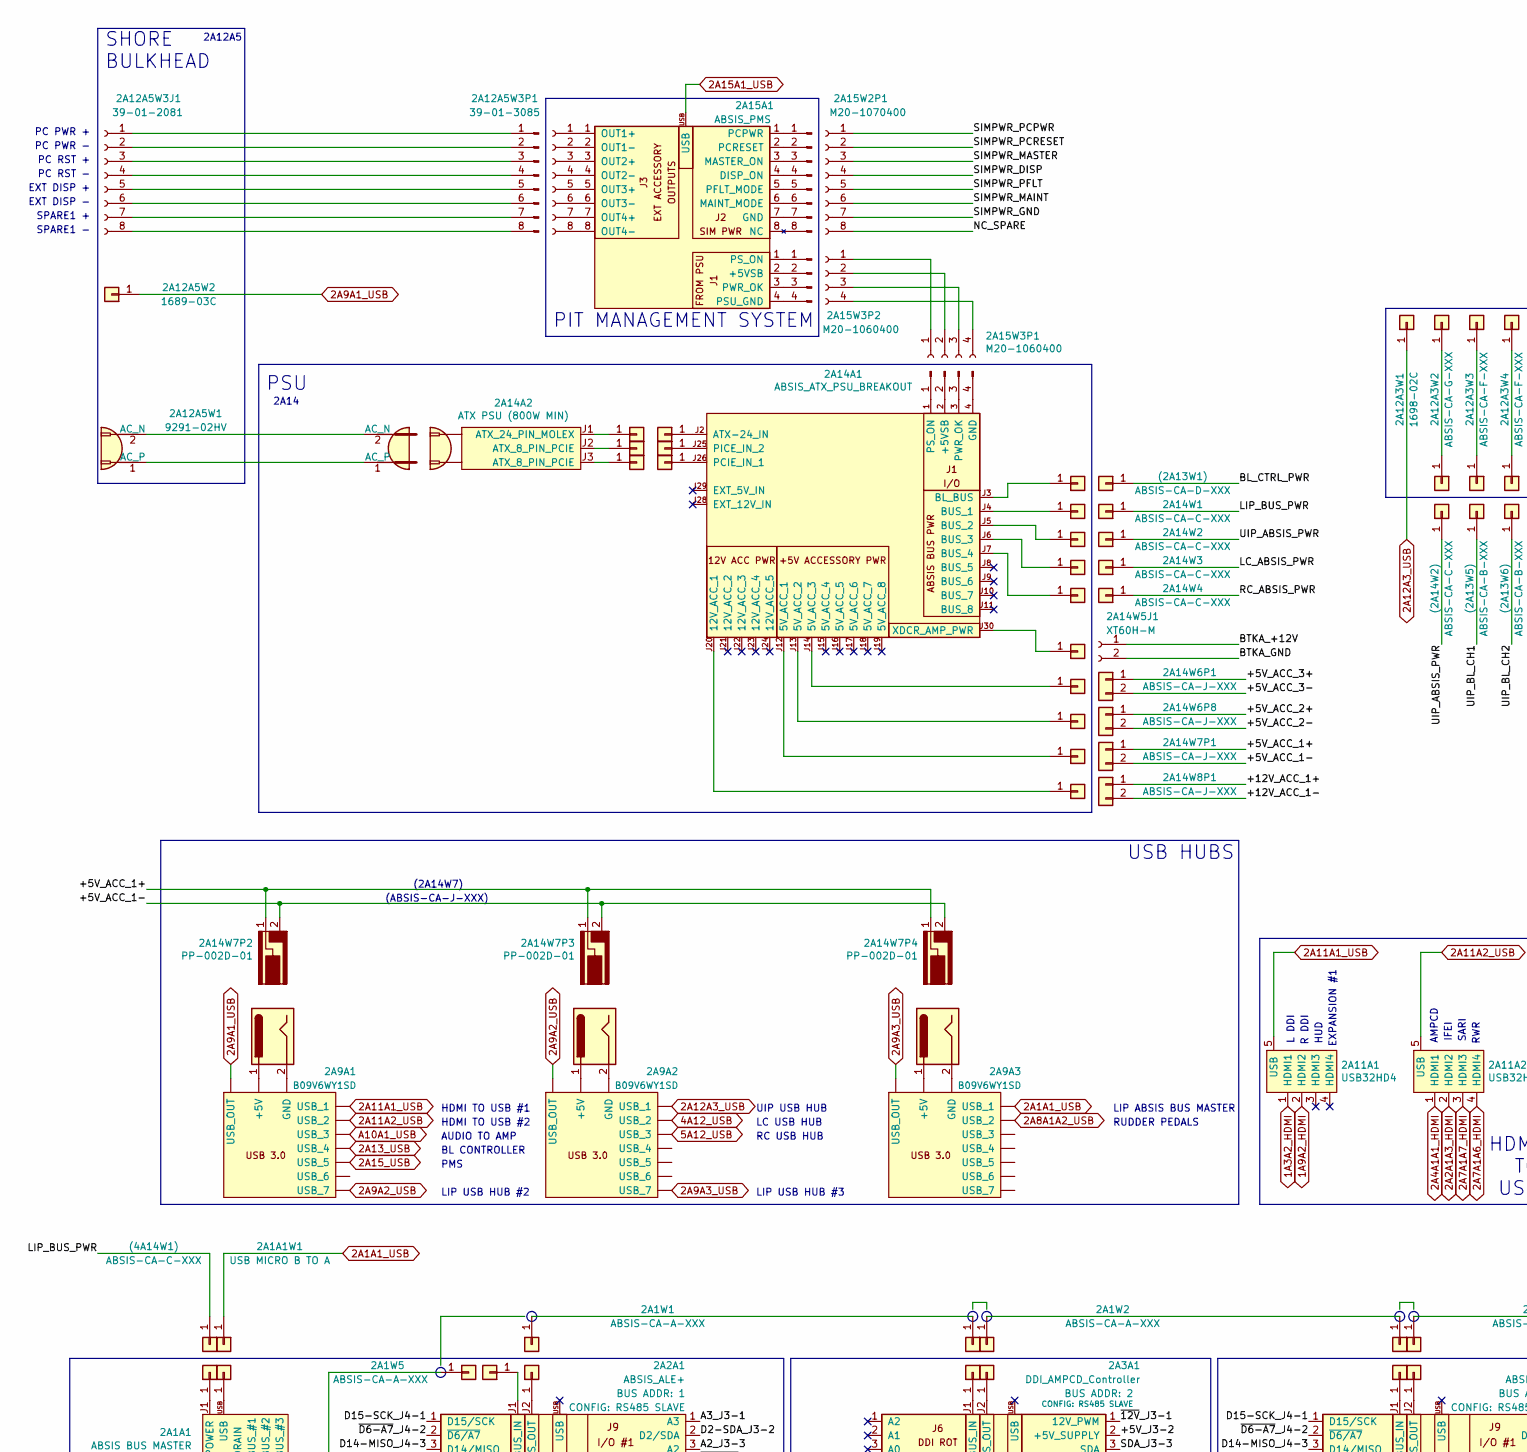
[picture p636: schematic OH_Lower_Instrument_Panel.kicad_sch, part in row 1, column 1]

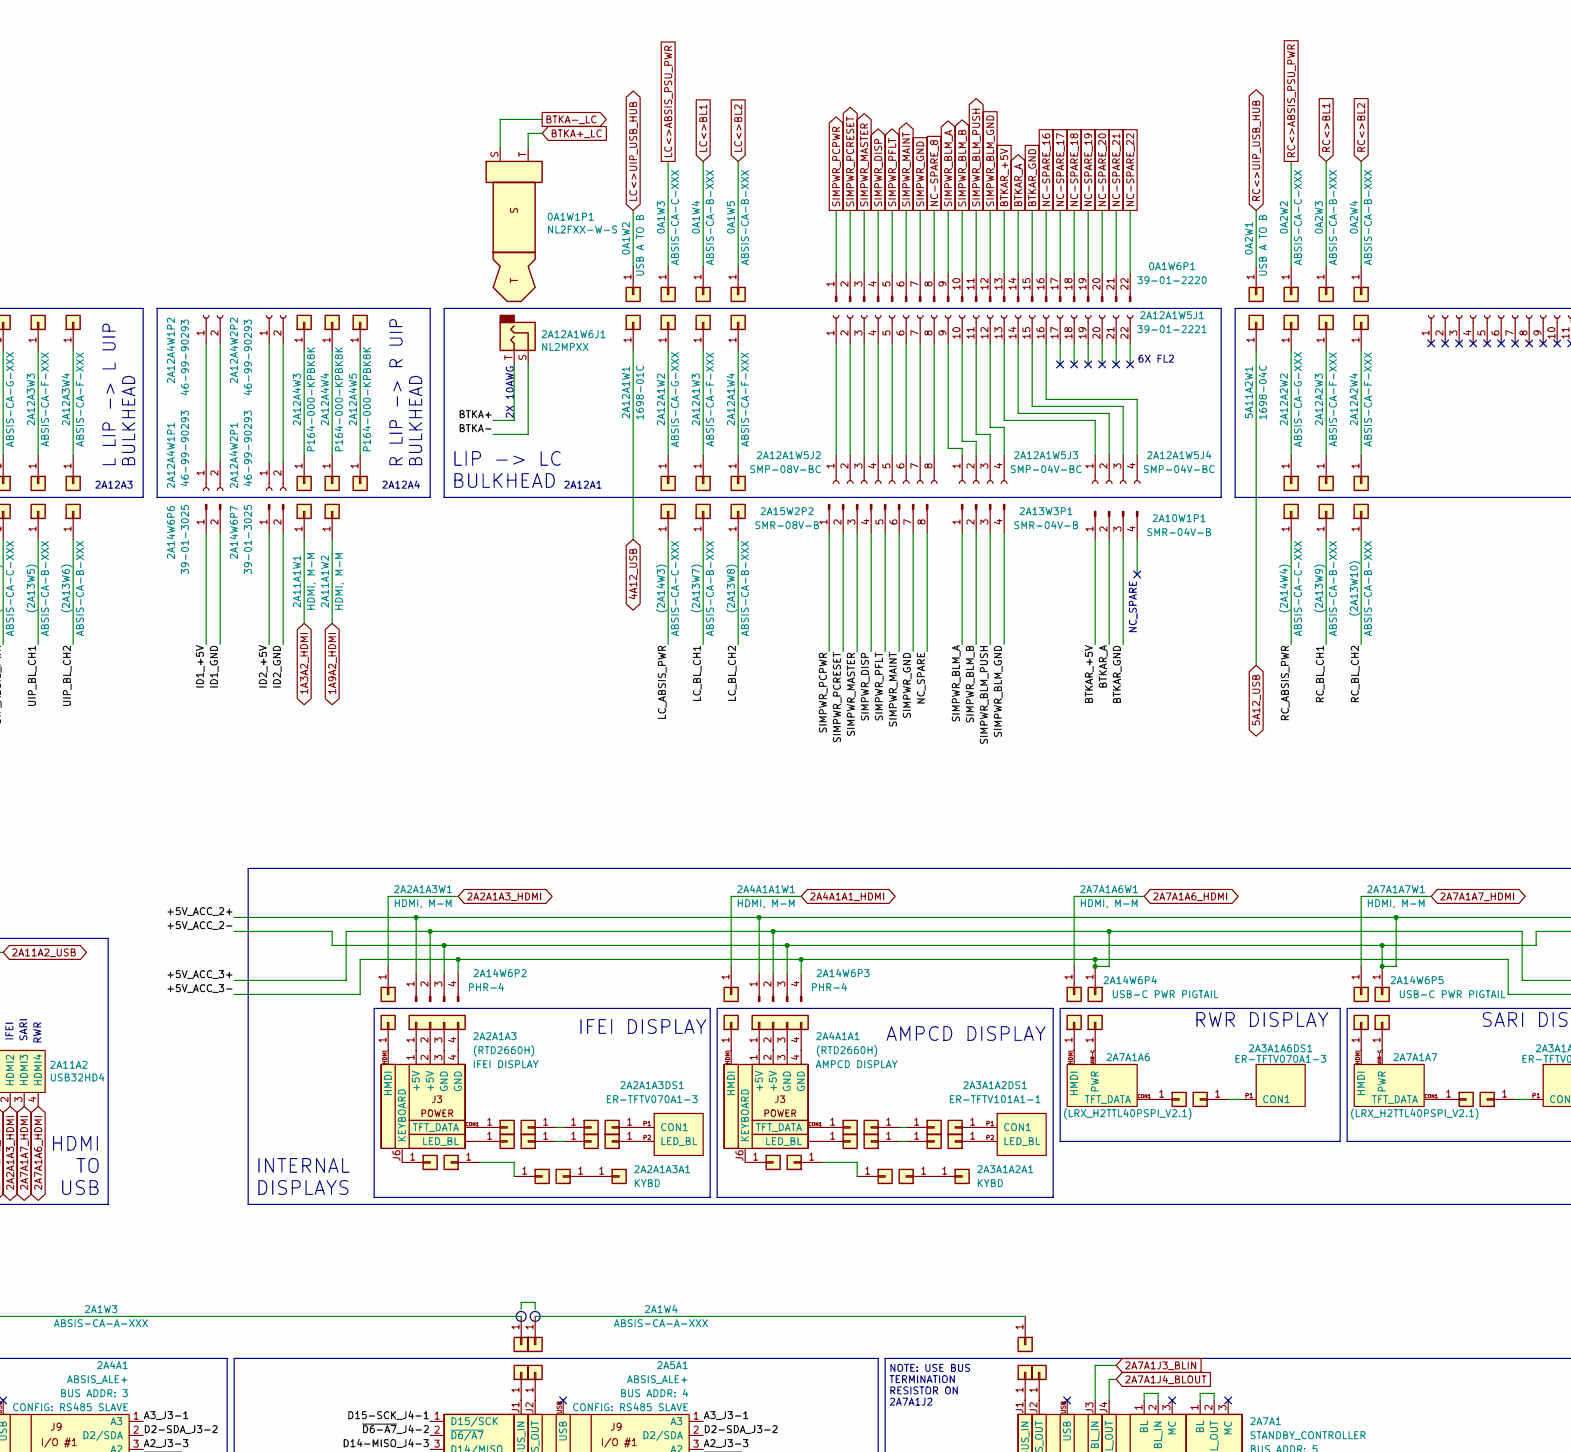
[picture p637: schematic OH_Lower_Instrument_Panel.kicad_sch, part in row 1, column 2]

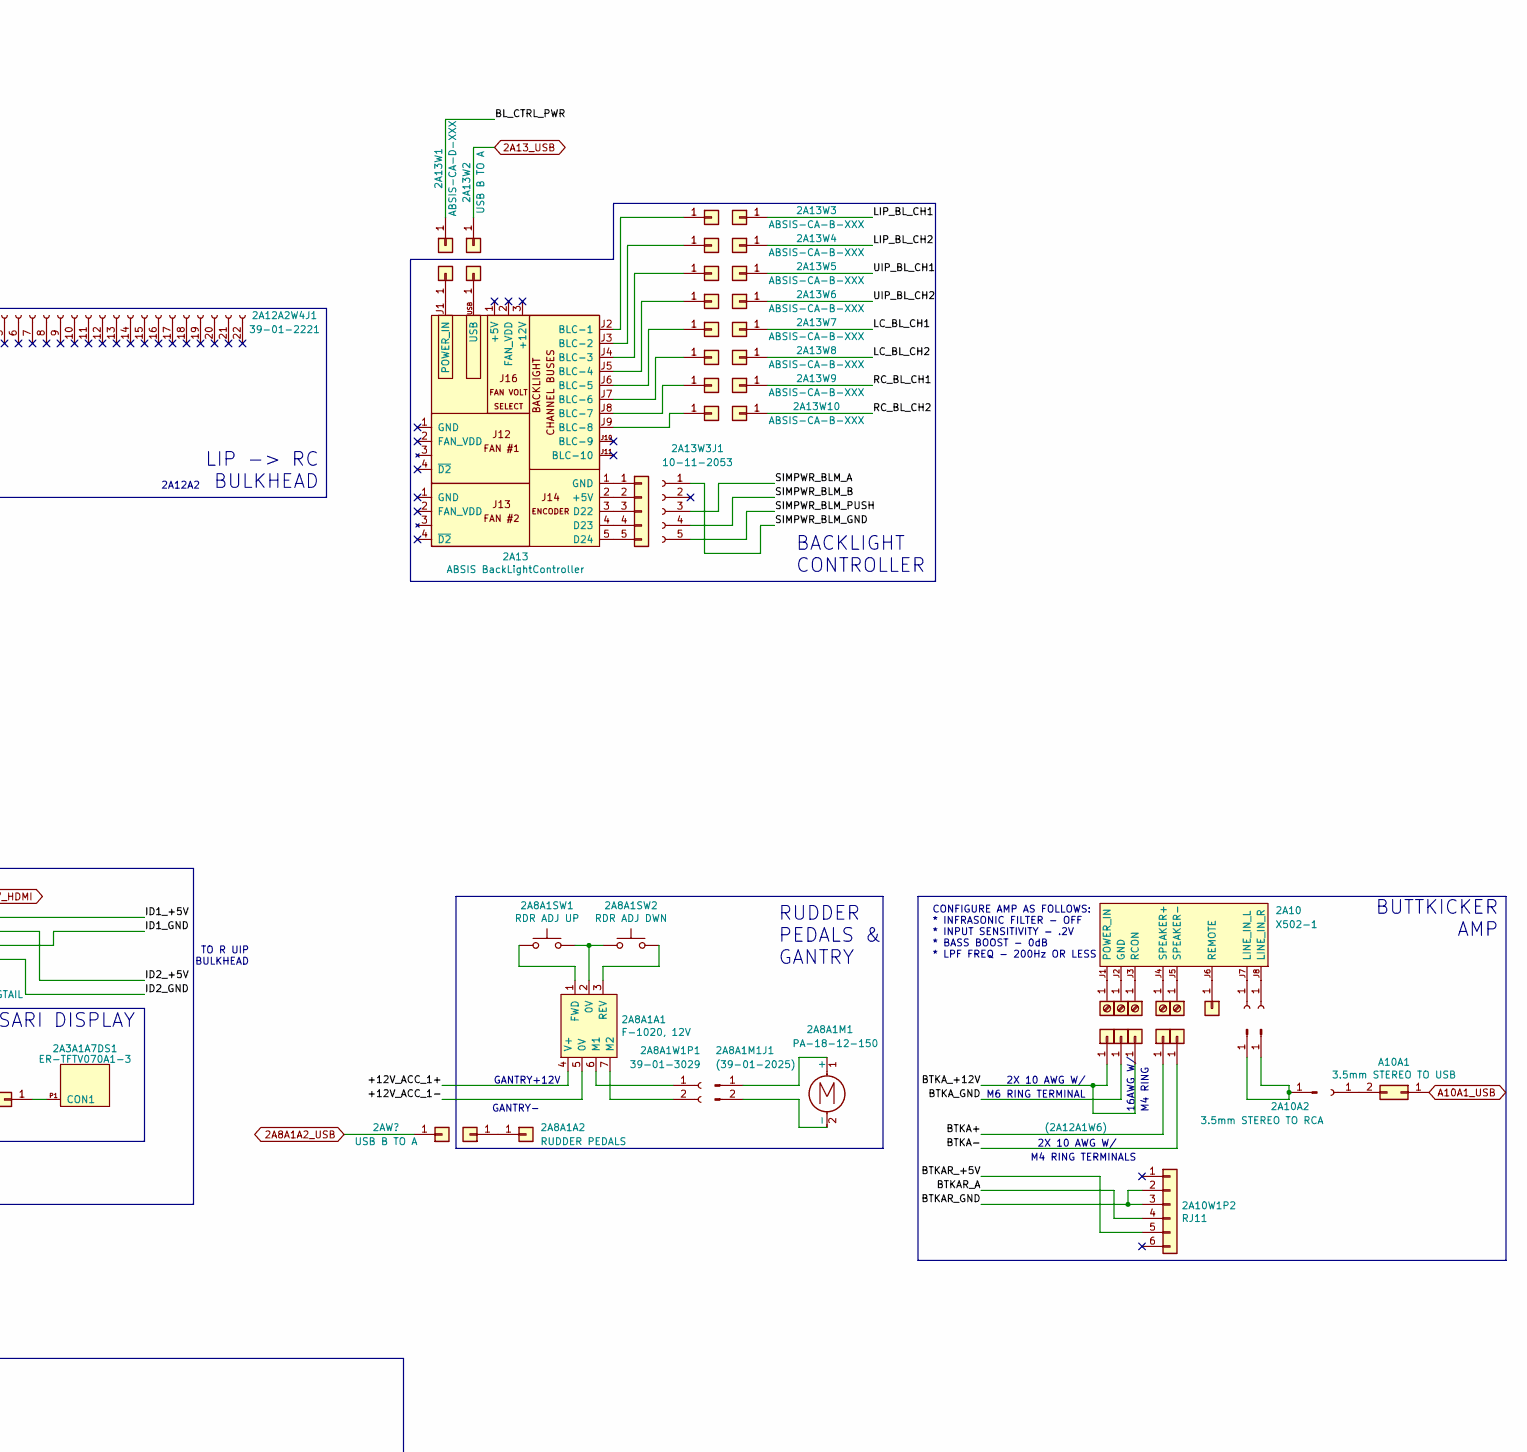
[picture p638: schematic OH_Lower_Instrument_Panel.kicad_sch, part in row 1, column 3]

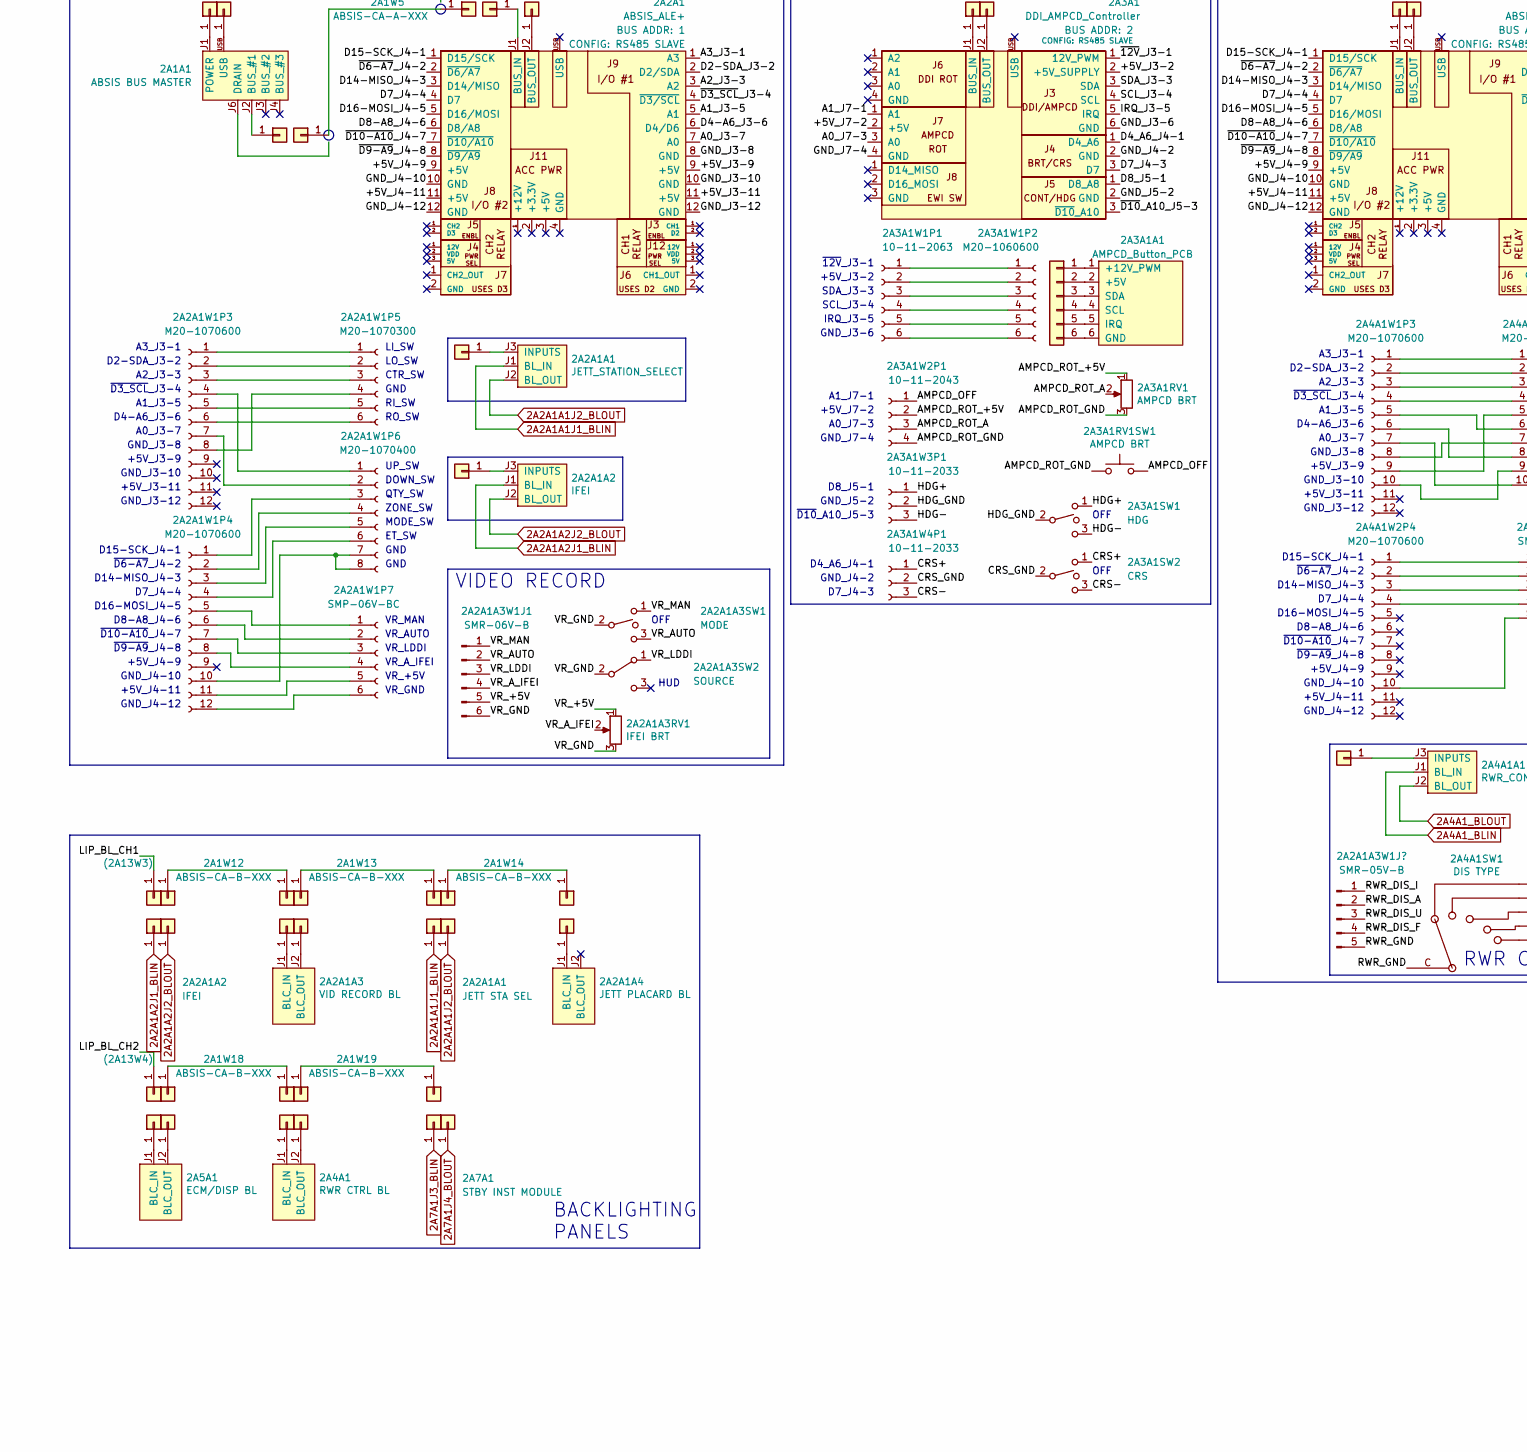
[picture p639: schematic OH_Lower_Instrument_Panel.kicad_sch, part in row 2, column 1]

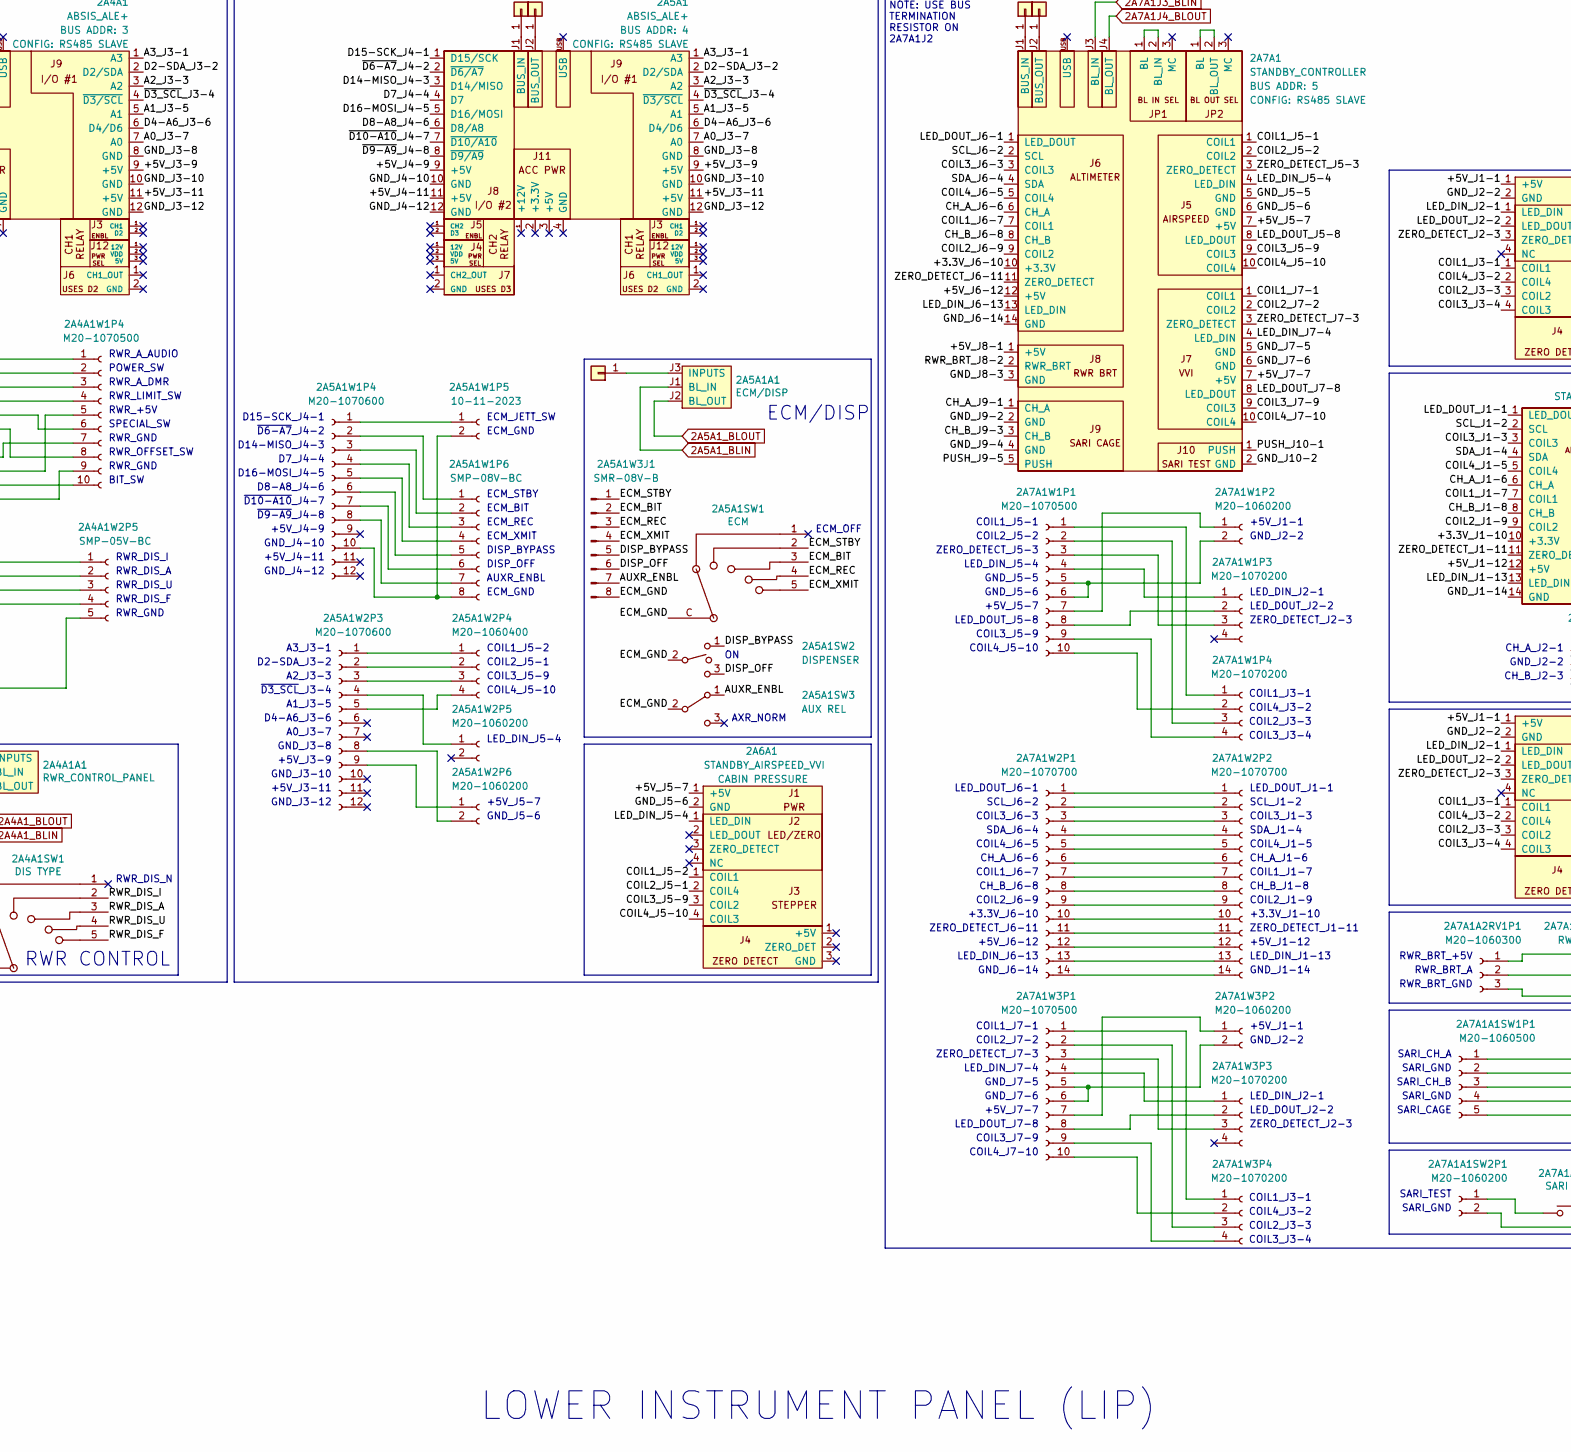
[picture p640: schematic OH_Lower_Instrument_Panel.kicad_sch, part in row 2, column 2]

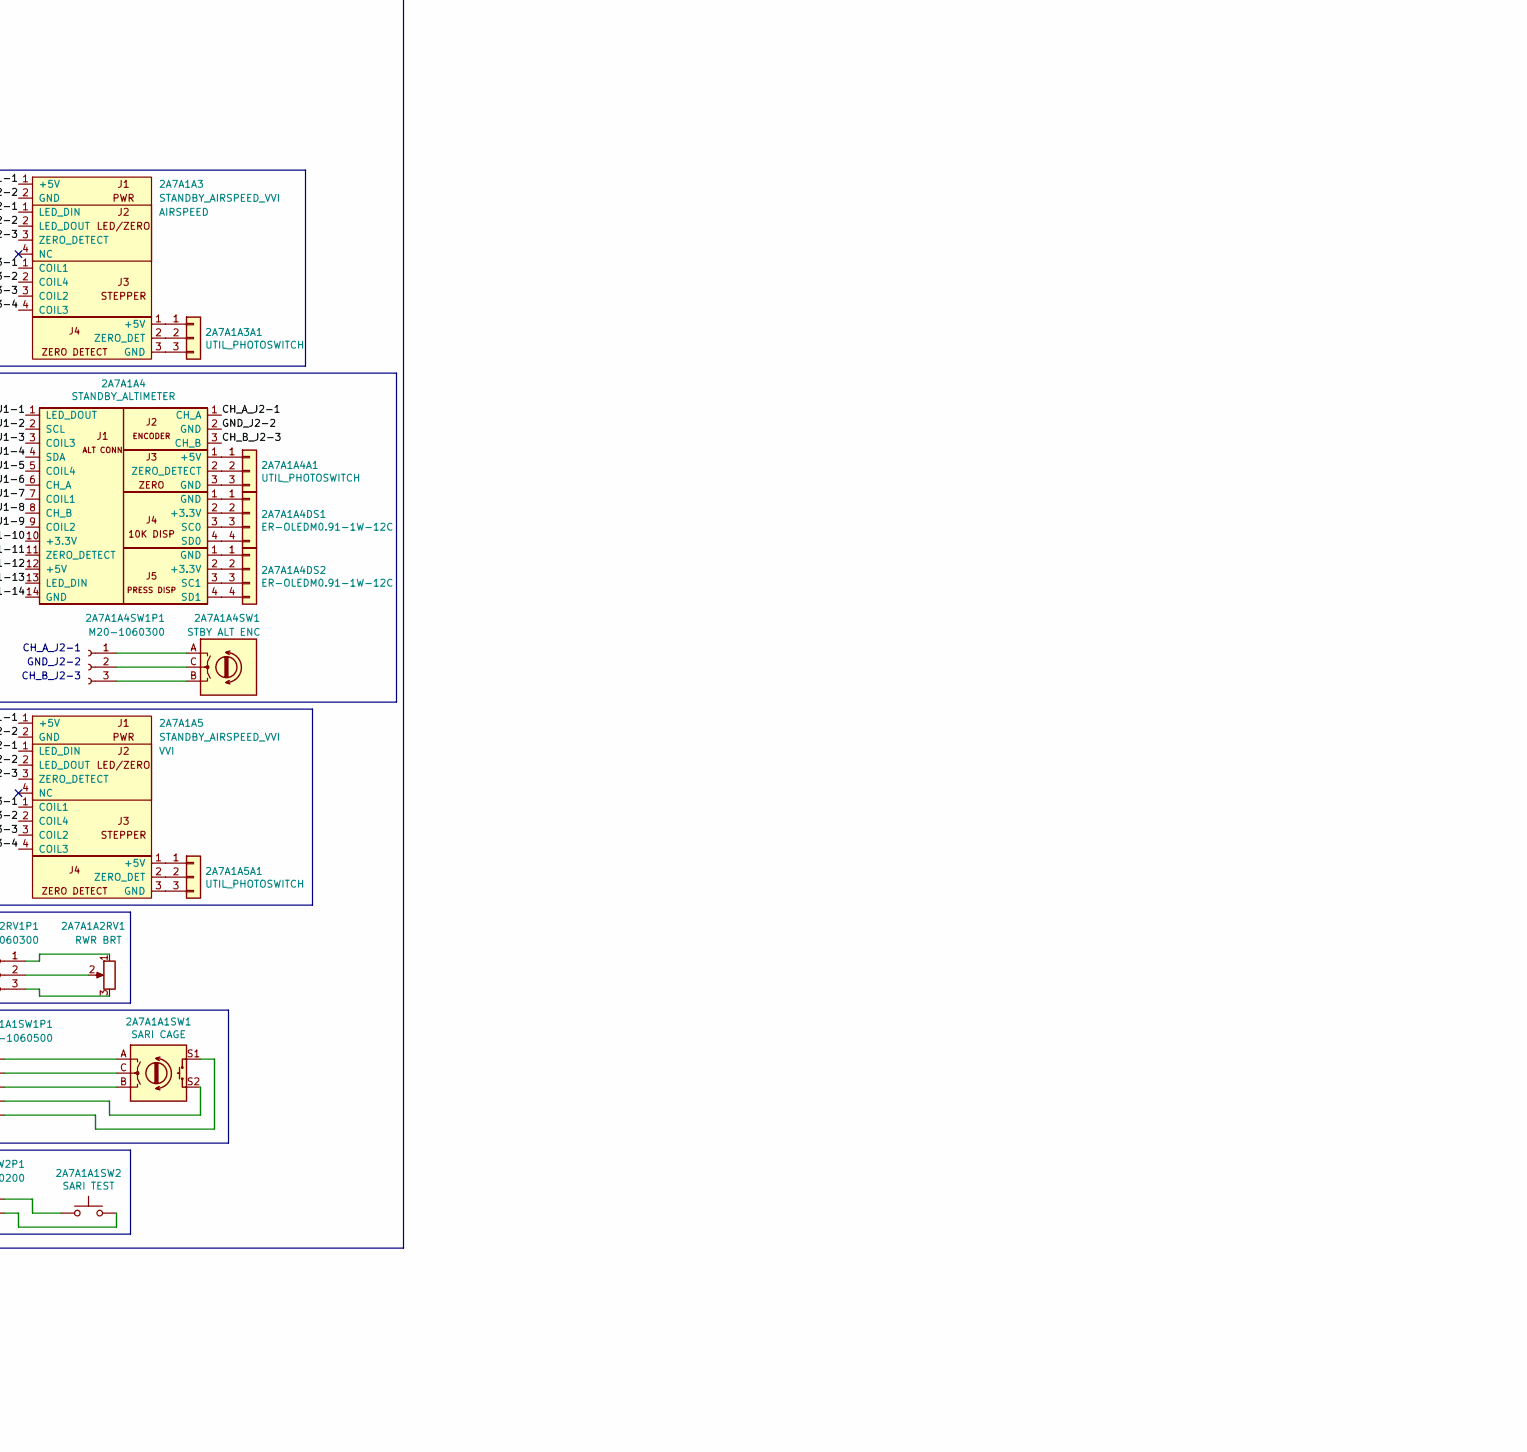
[picture p641: schematic OH_Lower_Instrument_Panel.kicad_sch, part in row 2, column 3]

Parts:
0A1W1P1: NL2FXX-W-S
0A1W2, 0A2W1: USB A TO B
0A1W3, 0A2W2, 2A14W1, 2A14W2, 2A14W3, 2A14W4: ABSIS-CA-C-XXX
0A1W4, 0A1W5, 0A2W3, 0A2W4, 2A1W12, 2A1W13, 2A1W14, 2A1W18, 2A1W19, 2A13W3, 2A13W4, 2A13W5, 2A13W6, 2A13W7, 2A13W8, 2A13W9, 2A13W10: ABSIS-CA-B-XXX
0A1W6P1: 39-01-2220
2A1A1: ABSIS BUS MASTER
2A1A1W1: USB MICRO B TO A
2A1W1, 2A1W2, 2A1W3, 2A1W4, 2A1W5: ABSIS-CA-A-XXX
2A2A1, 2A4A1: ABSIS_ALE+
2A2A1A1: JETT_STATION_SELECT
2A2A1A2: IFEI
2A2A1A3: VID RECORD BL
2A2A1A3A1, 2A3A1A2A1: KYBD
2A2A1A3DS1, 2A3A1A6DS1, 2A3A1A7DS1: ER-TFTV070A1-3
2A2A1A3RV1: IFEI BRT
2A2A1A3SW1: MODE
2A2A1A3SW2: SOURCE
2A2A1A3W1, 2A4A1A1W1, 2A7A1A6W1, 2A7A1A7W1, 2A11A1W1, 2A11A1W2: HDMI, M-M
2A2A1A3W1J1: SMR-06V-B
2A2A1A4: JETT PLACARD BL
2A2A1W1P3, 2A2A1W1P4, 2A4A1W1P3, 2A4A1W2P4, 2A5A1W1P4, 2A5A1W2P3: M20-1070600
2A2A1W1P5: M20-1070300
2A2A1W1P6, 2A15W2P1: M20-1070400
2A2A1W1P7: SMP-06V-BC
2A3A1: DDI_AMPCD_Controller
2A3A1A1: AMPCD_Button_PCB
2A3A1A2DS1: ER-TFTV101A1-1
2A3A1RV1, 2A3A1RV1SW1: AMPCD BRT
2A3A1SW1: HDG
2A3A1SW2: CRS
2A3A1W1P1: 10-11-2063
2A3A1W1P2: M20-1060600
2A3A1W2P1: 10-11-2043
2A3A1W3P1, 2A3A1W4P1: 10-11-2033
2A4A1A1: (RTD2660H)
2A4A1SW1: DIS TYPE
2A4A1W1P4, 2A7A1W1P1, 2A7A1W3P1: M20-1070500
2A4A1W2P5: SMP-05V-BC
2A5A1: ECM/DISP BL
2A5A1A1: ECM/DISP
2A5A1SW1: ECM
2A5A1SW2: DISPENSER
2A5A1SW3: AUX REL
2A5A1W1P5: 10-11-2023
2A5A1W1P6, 2A12A1W5J2: SMP-08V-BC
2A5A1W2P4, 2A15W3P1, 2A15W3P2: M20-1060400
2A5A1W2P5, 2A5A1W2P6, 2A7A1A1SW2P1, 2A7A1W1P2, 2A7A1W3P2: M20-1060200
2A5A1W3J1, 2A15W2P2: SMR-08V-B
2A6A1, 2A7A1A3, 2A7A1A5: STANDBY_AIRSPEED_VVI
2A7A1: STANDBY_CONTROLLER
2A7A1A1SW1: SARI CAGE
2A7A1A1SW1P1: M20-1060500
2A7A1A1SW2: SARI TEST
2A7A1A2RV1: RWR BRT
2A7A1A2RV1P1, 2A7A1A4SW1P1: M20-1060300
2A7A1A3A1, 2A7A1A4A1, 2A7A1A5A1: UTIL_PHOTOSWITCH
2A7A1A4: STANDBY_ALTIMETER
2A7A1A4DS1, 2A7A1A4DS2: ER-OLEDM0.91-1W-12C
2A7A1A4SW1: STBY ALT ENC
2A7A1A6, 2A7A1A7: (LRX_H2TTL40PSPI_V2.1)
2A7A1W1P3, 2A7A1W1P4, 2A7A1W3P3, 2A7A1W3P4: M20-1070200
2A7A1W2P1, 2A7A1W2P2: M20-1070700
2A8A1A1: F-1020, 12V
2A8A1A2: RUDDER PEDALS
2A8A1M1: PA-18-12-150
2A8A1M1J1: (39-01-2025)
2A8A1SW1: RDR ADJ UP
2A8A1SW2: RDR ADJ DWN
2A8A1W1P1: 39-01-3029
2A9A1, 2A9A2, 2A9A3: B09V6WY1SD
2A10: X502-1
2A10A2: 3.5mm STEREO TO RCA
2A10W1P1, 2A13W3P1: SMR-04V-B
2A10W1P2: RJ11
2A11A1, 2A11A2: USB32HD4
2A12A1W1: 1698-01C
2A12A1W2, 2A12A2W2, 2A12A3W2: ABSIS-CA-G-XXX
2A12A1W3, 2A12A1W4, 2A12A2W3, 2A12A2W4, 2A12A3W3, 2A12A3W4: ABSIS-CA-F-XXX
2A12A1W5J1, 2A12A2W4J1: 39-01-2221
2A12A1W5J3, 2A12A1W5J4: SMP-04V-BC
2A12A1W6J1: NL2MPXX
2A12A3W1: 1698-02C
2A12A4W1P1, 2A12A4W1P2, 2A12A4W2P1, 2A12A4W2P2: 46-99-90293
2A12A4W3, 2A12A4W4, 2A12A4W5: P164-000-KPBK8K
2A12A5W1: 9291-02HV
2A12A5W2: 1689-03C
2A12A5W3J1: 39-01-2081
2A12A5W3P1: 39-01-3085
2A13: ABSIS BackLightController
2A13W1: ABSIS-CA-D-XXX
2A13W2: USB B TO A
2A13W3J1: 10-11-2053
2A14A1: ABSIS_ATX_PSU_BREAKOUT
2A14A2: ATX PSU (800W MIN)
2A14W5J1: XT60H-M
2A14W6P1, 2A14W6P8, 2A14W7P1, 2A14W8P1: ABSIS-CA-J-XXX
2A14W6P2, 2A14W6P3: PHR-4
2A14W6P4, 2A14W6P5: USB-C PWR PIGTAIL
2A14W6P6, 2A14W6P7: 39-01-3025
2A14W7P2, 2A14W7P3, 2A14W7P4: PP-002D-01
2A15A1: ABSIS_PMS
4A2A1~: (no value)
5A11A2W1: 1698-04C
(2A12A1W6), (2A13W3), (2A13W4): (no value)
(2A13W1): ABSIS-CA-D-XXX
(2A13W5), (2A13W6), (2A13W7), (2A13W8), (2A13W9), (2A13W10): ABSIS-CA-B-XXX
(2A14W2), (2A14W3), (2A14W4), (4A14W1): ABSIS-CA-C-XXX
A10A1: 3.5mm STEREO TO USB
~: (no value)

Connections:
1A3A2_HDMI: 2A11A1.1 (HDMI1), 2A11A1W1.1
1A9A2_HDMI: 2A11A1.2 (HDMI2), 2A11A1W2.1
2A1A1_USB: 2A1A1W1.1, 2A9A3.
2A2A1A1J1_BLIN: 2A2A1A1.J1 (BL_IN), ~.1
2A2A1A1J2_BLOUT: 2A2A1A1.1, 2A2A1A1.J2 (BL_OUT)
2A2A1A2J1_BLIN: 2A2A1A2.J1 (BL_IN), ~.1
2A2A1A2J2_BLOUT: 2A2A1A2.1, 2A2A1A2.J2 (BL_OUT)
2A2A1A3_HDMI: 2A2A1A3W1.1, 2A11A2.2 (HDMI2)
2A4A1A1_HDMI: 2A4A1A1W1.1, 2A11A2.1 (HDMI1)
2A4A1_BLIN: 2A4A1A1.J1 (BL_IN)
2A4A1_BLOUT: 2A4A1A1.J2 (BL_OUT)
2A5A1_BLIN: 2A5A1A1.J1 (BL_IN)
2A5A1_BLOUT: 2A5A1A1.J2 (BL_OUT)
2A7A1A6_HDMI: 2A7A1A6W1.1, 2A11A2.4 (HDMI4)
2A7A1A7_HDMI: 2A7A1A7W1.1, 2A11A2.3 (HDMI3)
2A7A1J3_BLIN: 2A7A1.J3 (BL_IN), ~.1
2A7A1J4_BLOUT: 2A7A1.1, 2A7A1.J4 (BL_OUT)
2A8A1A2_USB: 2A9A3.
2A9A1_USB: 2A9A1., 2A12A5W2.1
2A9A2_USB: 2A9A1., 2A9A2.
2A9A3_USB: 2A9A2., 2A9A3.
2A11A1_USB: 2A9A1., 2A11A1.5 (USB)
2A11A2_USB: 2A9A1., 2A11A2.5 (USB)
2A12A3_USB: 2A9A2., 2A12A3W1.1
2A13_USB: 2A9A1., 2A13W2.1
2A15A1_USB: 2A15A1.USB
2A15_USB: 2A9A1.
4A12_USB: 2A9A2., 2A12A1W1.1
5A12_USB: 2A9A2., 5A11A2W1.1
+3.3V_J1-10: 2A7A1A4.10 (+3.3V)
+3.3V_J6-10: 2A7A1.10 (COIL4)
+5V_ACC_1+: 2A14W7P1.1, 2A14W7P2.1, 2A14W7P3.1, 2A14W7P4.1
+5V_ACC_1-: 2A14W7P1.2, 2A14W7P2.2, 2A14W7P3.2, 2A14W7P4.2
+5V_ACC_2+: 2A14W6P2.1, 2A14W6P2.3, 2A14W6P3.1, 2A14W6P3.3, 2A14W6P5.1, 2A14W6P6.1, 2A14W6P6.2, 2A14W6P8.1, 2A14W6P8.2
+5V_ACC_3+: 2A14W6P1.1, 2A14W6P1.2, 2A14W6P2.2, 2A14W6P2.4, 2A14W6P3.2, 2A14W6P3.4, 2A14W6P4.1, 2A14W6P7.1, 2A14W6P7.2
+5V_J1-1: 2A7A1A3.1 (+5V), 2A7A1A5.1 (+5V)
+5V_J1-12: 2A7A1A4.12 (+5V)
+5V_J3-2: 2A3A1.2 (A1)
+5V_J3-9: 2A2A1.9 (+5V), 2A4A1.9 (+5V), 2A5A1.9 (+5V)
+5V_J3-11: 2A2A1.11 (+5V), 2A4A1.11 (+5V), 2A5A1.11 (+5V)
+5V_J4-9: 2A2A1.9 (+5V), 2A4A1.9 (+5V), 2A5A1.9 (+5V)
+5V_J4-11: 2A2A1.11 (+5V), 2A4A1.11 (+5V), 2A5A1.11 (+5V)
+5V_J5-7: 2A6A1.1 (+5V), 2A7A1.7 (+5V)
+5V_J6-12: 2A7A1.12 (+5V)
+5V_J7-2: 2A3A1.2 (A1)
+5V_J7-7: 2A7A1.7 (+5V)
+5V_J8-1: 2A7A1.1
+12V_ACC_1+: 2A8A1A1.4 (V+), 2A14W8P1.1
+12V_ACC_1-: 2A8A1A1.5 (0V), 2A14W8P1.2
A0_J3-7: 2A2A1.7 (~D10/A10), 2A4A1.7 (~D10/A10), 2A5A1.7 (~D10/A10)
A0_J7-3: 2A3A1.3 (A0)
A1_J3-5: 2A2A1.5 (D16/MOSI), 2A4A1.5 (D16/MOSI), 2A5A1.5 (D16/MOSI)
A1_J7-1: 2A3A1.1 (A2)
A2_J3-3: 2A2A1.3 (D14/MISO), 2A4A1.3 (D14/MISO), 2A5A1.3 (D14/MISO)
A3_J3-1: 2A2A1.1 (D15/SCK), 2A4A1.1 (D15/SCK), 2A5A1.1 (D15/SCK)
A10A1_USB: 2A9A1., A10A1.1
AMPCD_OFF: 2A3A1RV1SW1.2, 2A3A1W2P1.1
AMPCD_ROT_+5V: 2A3A1RV1.1, 2A3A1W2P1.2
AMPCD_ROT_A: 2A3A1RV1.2, 2A3A1W2P1.3
AMPCD_ROT_GND: 2A3A1RV1.3, 2A3A1RV1SW1.1, 2A3A1W2P1.4
AUXR_ENBL: 2A5A1SW3.1 (A), 2A5A1W3J1.7
BL_CTRL_PWR: 2A13W1.1, (2A13W1).1
BTKA+: 2A12A1W6J1.T, (2A12A1W6).1
BTKA+_LC: 0A1W1P1.T
BTKA-: 2A12A1W6J1.S, ~.1
BTKA-_LC: 0A1W1P1.S
BTKAR_+5V: 0A1W6P1.13, 2A10W1P1.1, 2A10W1P2.5
BTKAR_A: 0A1W6P1.14, 2A10W1P1.2, 2A10W1P2.4
BTKAR_GND: 0A1W6P1.15, 2A10W1P1.3, 2A10W1P2.2, 2A10W1P2.3
BTKA_+12V: 2A14W5J1.1, ~.1
BTKA_GND: 2A14W5J1.2, ~.1
CH_A_J1-6: 2A7A1A4.6 (CH_A)
CH_A_J2-1: 2A7A1A4.1 (LED_DOUT)
CH_A_J6-6: 2A7A1.6 (GND)
CH_A_J9-1: 2A7A1.1
CH_B_J1-8: 2A7A1A4.8 (CH_B)
CH_B_J2-3: 2A7A1A4.3 (COIL3)
CH_B_J6-8: 2A7A1.8 (LED_DOUT)
CH_B_J9-3: 2A7A1.3 (MC)
COIL1_J1-7: 2A7A1A4.7 (COIL1)
COIL1_J3-1: 2A7A1A3.1 (+5V), 2A7A1A5.1 (+5V)
COIL1_J5-1: 2A7A1.1
COIL1_J5-2: 2A6A1.1 (+5V)
COIL1_J6-7: 2A7A1.7 (+5V)
COIL1_J7-1: 2A7A1.1
COIL2_J1-9: 2A7A1A4.9 (COIL2)
COIL2_J3-3: 2A7A1A3.3 (ZERO_DETECT), 2A7A1A5.3 (ZERO_DETECT)
COIL2_J5-1: 2A6A1.2 (GND)
COIL2_J5-2: 2A7A1.2 (BL_IN)
COIL2_J6-9: 2A7A1.9 (COIL3)
COIL2_J7-2: 2A7A1.2 (BL_IN)
COIL3_J1-3: 2A7A1A4.3 (COIL3)
COIL3_J3-4: 2A7A1A3.4 (NC), 2A7A1A5.4 (NC)
COIL3_J5-9: 2A6A1.3 (ZERO_DETECT), 2A7A1.9 (COIL3)
COIL3_J6-3: 2A7A1.3 (MC)
COIL3_J7-9: 2A7A1.9 (COIL3)
COIL4_J1-5: 2A7A1A4.5 (COIL4)
COIL4_J3-2: 2A7A1A3.2 (GND), 2A7A1A5.2 (GND)
COIL4_J5-10: 2A6A1.4 (NC), 2A7A1.10 (COIL4)
COIL4_J6-5: 2A7A1.5 (GND)
COIL4_J7-10: 2A7A1.10 (COIL4)
CRS+: 2A3A1SW2.1, 2A3A1W4P1.1
CRS-: 2A3A1SW2.3, 2A3A1W4P1.3
CRS_GND: 2A3A1SW2.2, 2A3A1W4P1.2
D2-SDA_J3-2: 2A2A1.2 (~D6/A7), 2A4A1.2 (~D6/A7), 2A5A1.2 (~D6/A7)
D4-A6_J3-6: 2A2A1.6 (D8/A8), 2A4A1.6 (D8/A8), 2A5A1.6 (D8/A8)
D4_A6_J4-1: 2A3A1.1 (A2)
D7_J4-3: 2A3A1.3 (A0)
D7_J4-4: 2A2A1.4 (D7), 2A4A1.4 (D7), 2A5A1.4 (D7)
D8-A8_J4-6: 2A2A1.6 (D8/A8), 2A4A1.6 (D8/A8), 2A5A1.6 (D8/A8)
D8_J5-1: 2A3A1.1 (A2)
D14-MISO_J4-3: 2A2A1.3 (D14/MISO), 2A4A1.3 (D14/MISO), 2A5A1.3 (D14/MISO)
D15-SCK_J4-1: 2A2A1.1 (D15/SCK), 2A4A1.1 (D15/SCK), 2A5A1.1 (D15/SCK)
D16-MOSI_J4-5: 2A2A1.5 (D16/MOSI), 2A4A1.5 (D16/MOSI), 2A5A1.5 (D16/MOSI)
DISP_BYPASS: 2A5A1SW2.1, 2A5A1W3J1.5
DISP_OFF: 2A5A1SW2.3, 2A5A1W3J1.6
ECM_BIT: 2A5A1SW1.3, 2A5A1W3J1.2
ECM_GND: 2A5A1SW1.C (COM), 2A5A1SW2.2, 2A5A1SW3.2 (B), 2A5A1W3J1.8
ECM_REC: 2A5A1SW1.4, 2A5A1W3J1.3
ECM_STBY: 2A5A1SW1.2, 2A5A1W3J1.1
ECM_XMIT: 2A5A1SW1.5, 2A5A1W3J1.4
GND_J1-14: 2A7A1A4.14 (GND)
GND_J2-2: 2A7A1A3.2 (GND), 2A7A1A4.2 (SCL), 2A7A1A5.2 (GND)
GND_J3-6: 2A3A1.6 (GND)
GND_J3-8: 2A2A1.8 (~D9/A9), 2A4A1.8 (~D9/A9), 2A5A1.8 (~D9/A9)
GND_J3-10: 2A2A1.10 (GND), 2A4A1.10 (GND), 2A5A1.10 (GND)
GND_J3-12: 2A2A1.12 (GND), 2A4A1.12 (GND), 2A5A1.12 (GND)
GND_J4-2: 2A3A1.2 (A1)
GND_J4-10: 2A2A1.10 (GND), 2A4A1.10 (GND), 2A5A1.10 (GND)
GND_J4-12: 2A2A1.12 (GND), 2A4A1.12 (GND), 2A5A1.12 (GND)
GND_J5-2: 2A3A1.2 (A1)
GND_J5-5: 2A7A1.5 (GND)
GND_J5-6: 2A6A1.2 (GND), 2A7A1.6 (GND)
GND_J6-14: 2A7A1.14 (GND)
GND_J7-4: 2A3A1.4 (GND)
GND_J7-5: 2A7A1.5 (GND)
GND_J7-6: 2A7A1.6 (GND)
GND_J8-3: 2A7A1.3 (MC)
GND_J9-2: 2A7A1.2 (BL_IN)
GND_J9-4: 2A7A1.4 (LED_DIN)
GND_J10-2: 2A7A1.2 (BL_IN)
HDG+: 2A3A1SW1.1, 2A3A1W3P1.1
HDG-: 2A3A1SW1.3, 2A3A1W3P1.3
HDG_GND: 2A3A1SW1.2, 2A3A1W3P1.2
IRQ_J3-5: 2A3A1.5 (IRQ)
LC<>ABSIS_PSU_PWR: 0A1W3.1
LC<>BL1: 0A1W4.1
LC<>BL2: 0A1W5.1
LC<>UIP_USB_HUB: 0A1W2.1
LC_ABSIS_PWR: 2A14W3.1, (2A14W3).1
LC_BL_CH1: 2A13W7.1, (2A13W7).1
LC_BL_CH2: 2A13W8.1, (2A13W8).1
LED_DIN_J1-13: 2A7A1A4.13 (LED_DIN)
LED_DIN_J2-1: 2A7A1A3.1 (+5V), 2A7A1A5.1 (+5V)
LED_DIN_J5-4: 2A6A1.1 (+5V), 2A7A1.4 (LED_DIN)
LED_DIN_J6-13: 2A7A1.13 (LED_DIN)
LED_DIN_J7-4: 2A7A1.4 (LED_DIN)
LED_DOUT_J1-1: 2A7A1A4.1 (LED_DOUT)
LED_DOUT_J2-2: 2A7A1A3.2 (GND), 2A7A1A5.2 (GND)
LED_DOUT_J5-8: 2A7A1.8 (LED_DOUT)
LED_DOUT_J6-1: 2A7A1.1
LED_DOUT_J7-8: 2A7A1.8 (LED_DOUT)
LIP_BL_CH1: 2A13W3.1, (2A13W3).1
LIP_BL_CH2: 2A13W4.1, (2A13W4).1
LIP_BUS_PWR: 2A14W1.1, (4A14W1).1
NC-SPARE_8: 0A1W6P1.8
NC-SPARE_16: 0A1W6P1.16
NC-SPARE_17: 0A1W6P1.17
NC-SPARE_18: 0A1W6P1.18
NC-SPARE_19: 0A1W6P1.19
NC-SPARE_20: 0A1W6P1.20
NC-SPARE_21: 0A1W6P1.21
NC-SPARE_22: 0A1W6P1.22
NC_SPARE: 2A15W2P1.8, 2A15W2P2.8
unnamed: 2A1W1.1, ~.1
unnamed: 2A1W2.1, ~.1
unnamed: 2A1W3.1, ~.1
unnamed: 2A1W4.1, ~.1
unnamed: 2A1W5.1, ~.1
unnamed: 2A1W12.1, ~.1
unnamed: 2A1W13.1, ~.1
unnamed: 2A1W14.1, ~.1
unnamed: 2A1W18.1, ~.1
unnamed: 2A1W19.1, ~.1
unnamed: 2A2A1.J1 (BUS_IN), ~.1
unnamed: 2A2A1A1.J3 (INPUTS), ~.1
unnamed: 2A2A1A2.J3 (INPUTS), ~.1
unnamed: 2A2A1A3.1 (+5V), ~.1
unnamed: 2A2A1A3.2 (+5V), ~.2
unnamed: 2A2A1A3.3 (GND), ~.3
unnamed: 2A2A1A3.4 (GND), ~.4
unnamed: 2A2A1A3. (LED_BL), ~.1
unnamed: 2A2A1A3.CON1 (TFT_DATA), ~.1
unnamed: 2A2A1A3.HDMI (HMDI), ~.1
unnamed: 2A2A1A3.J1 (BLC_IN), ~.1
unnamed: 2A2A1A3.J2 (BLC_OUT), ~.1
unnamed: 2A2A1A3.J6 (KEYBOARD), ~.1
unnamed: 2A2A1A3A1.1, ~.1
unnamed: 2A2A1A3DS1.P1 (CON1), ~.1
unnamed: 2A2A1A3DS1.P2 (LED_BL), ~.1
unnamed: 2A2A1A4.J1 (BLC_IN), ~.1
unnamed: 2A2A1W1P3.1, 2A2A1W1P5.1
unnamed: 2A2A1W1P3.2, 2A2A1W1P5.2
unnamed: 2A2A1W1P3.3, 2A2A1W1P5.3
unnamed: 2A2A1W1P3.4, 2A2A1W1P6.1
unnamed: 2A2A1W1P3.5, 2A2A1W1P5.5
unnamed: 2A2A1W1P3.6, 2A2A1W1P5.6
unnamed: 2A2A1W1P3.7, 2A2A1W1P6.2
unnamed: 2A2A1W1P3.8, 2A2A1W1P5.4
unnamed: 2A2A1W1P4.1, 2A2A1W1P6.3
unnamed: 2A2A1W1P4.2, 2A2A1W1P6.4
unnamed: 2A2A1W1P4.3, 2A2A1W1P6.5
unnamed: 2A2A1W1P4.4, 2A2A1W1P6.6
unnamed: 2A2A1W1P4.5, 2A2A1W1P7.1
unnamed: 2A2A1W1P4.6, 2A2A1W1P7.2
unnamed: 2A2A1W1P4.7, 2A2A1W1P7.3
unnamed: 2A2A1W1P4.8, 2A2A1W1P7.4
unnamed: 2A2A1W1P4.10, 2A2A1W1P6.7, 2A2A1W1P6.8
unnamed: 2A2A1W1P4.11, 2A2A1W1P7.5
unnamed: 2A2A1W1P4.12, 2A2A1W1P7.6
unnamed: 2A3A1.J1 (BUS_IN), ~.1
unnamed: 2A3A1.J2 (BUS_OUT), ~.1
unnamed: 2A3A1A1.1 (+12V_PWM), ~.1
unnamed: 2A3A1A1.2 (+5V), ~.2
unnamed: 2A3A1A1.3 (SDA), ~.3
unnamed: 2A3A1A1.4 (SCL), ~.4
unnamed: 2A3A1A1.5 (IRQ), ~.5
unnamed: 2A3A1A1.6 (GND), ~.6
unnamed: 2A3A1A2A1.1, ~.1
unnamed: 2A3A1A2DS1.P1 (CON1), ~.1
unnamed: 2A3A1A2DS1.P2 (LED_BL), ~.1
unnamed: 2A3A1A6DS1.P1, ~.1
unnamed: 2A3A1W1P1.1, 2A3A1W1P2.1
unnamed: 2A3A1W1P1.2, 2A3A1W1P2.2
unnamed: 2A3A1W1P1.3, 2A3A1W1P2.3
unnamed: 2A3A1W1P1.4, 2A3A1W1P2.4
unnamed: 2A3A1W1P1.5, 2A3A1W1P2.5
unnamed: 2A3A1W1P1.6, 2A3A1W1P2.6
unnamed: 2A4A1.J1 (BLC_IN), 4A2A1~.1
unnamed: 2A4A1.J2 (BLC_OUT), 4A2A1~.1
unnamed: 2A4A1A1.1 (+5V), ~.1
unnamed: 2A4A1A1.2 (+5V), ~.2
unnamed: 2A4A1A1.3 (GND), ~.3
unnamed: 2A4A1A1.4 (GND), ~.4
unnamed: 2A4A1A1. (LED_BL), ~.1
unnamed: 2A4A1A1.CON1 (TFT_DATA), ~.1
unnamed: 2A4A1A1.HDMI (HMDI), ~.1
unnamed: 2A4A1A1.J6 (KEYBOARD), ~.1
unnamed: 2A4A1W1P3.1, 2A4A1W1P4.1
unnamed: 2A4A1W1P3.2, 2A4A1W1P4.2
unnamed: 2A4A1W1P3.3, 2A4A1W1P4.3
unnamed: 2A4A1W1P3.4, 2A4A1W1P4.4
unnamed: 2A4A1W1P3.5, 2A4A1W1P4.6
unnamed: 2A4A1W1P3.6, 2A4A1W1P4.8
unnamed: 2A4A1W1P3.7, 2A4A1W1P4.10
unnamed: 2A4A1W1P3.8, 2A4A1W1P4.7
unnamed: 2A4A1W1P3.9, 2A4A1W1P4.5
unnamed: 2A4A1W1P3.10, 2A4A1W1P4.9
unnamed: 2A4A1W2P4.1, 2A4A1W2P5.1
unnamed: 2A4A1W2P4.2, 2A4A1W2P5.2
unnamed: 2A4A1W2P4.3, 2A4A1W2P5.3
unnamed: 2A4A1W2P4.4, 2A4A1W2P5.4
unnamed: 2A4A1W2P4.10, 2A4A1W2P5.5
unnamed: 2A5A1.J1 (BUS_IN), 4A2A1~.1
unnamed: 2A5A1.J2 (BUS_OUT), 4A2A1~.1
unnamed: 2A5A1W1P4.1, 2A5A1W1P5.1
unnamed: 2A5A1W1P4.2, 2A5A1W1P6.1
unnamed: 2A5A1W1P4.3, 2A5A1W1P6.2
unnamed: 2A5A1W1P4.4, 2A5A1W1P6.3
unnamed: 2A5A1W1P4.5, 2A5A1W1P6.4
unnamed: 2A5A1W1P4.6, 2A5A1W1P6.5
unnamed: 2A5A1W1P4.7, 2A5A1W1P6.6
unnamed: 2A5A1W1P4.8, 2A5A1W1P6.7
unnamed: 2A5A1W1P4.10, 2A5A1W1P5.2, 2A5A1W1P6.8
unnamed: 2A5A1W2P3.1, 2A5A1W2P4.1
unnamed: 2A5A1W2P3.2, 2A5A1W2P4.2
unnamed: 2A5A1W2P3.3, 2A5A1W2P4.3
unnamed: 2A5A1W2P3.4, 2A5A1W2P5.1
unnamed: 2A5A1W2P3.5, 2A5A1W2P4.4
unnamed: 2A5A1W2P3.8, 2A5A1W2P6.2
unnamed: 2A5A1W2P3.9, 2A5A1W2P6.1
unnamed: 2A7A1.1, 2A7A1.2 (BL_IN)
unnamed: 2A7A1A1SW1.A, 2A7A1A1SW1P1.1
unnamed: 2A7A1A1SW1.B, 2A7A1A1SW1P1.3
unnamed: 2A7A1A1SW1.C, 2A7A1A1SW1P1.2
unnamed: 2A7A1A1SW1.S1, 2A7A1A1SW1P1.5
unnamed: 2A7A1A1SW1.S2, 2A7A1A1SW1P1.4
unnamed: 2A7A1A1SW2.1, 2A7A1A1SW2P1.1
unnamed: 2A7A1A1SW2.2, 2A7A1A1SW2P1.2
unnamed: 2A7A1A2RV1.1, 2A7A1A2RV1P1.1
unnamed: 2A7A1A2RV1.2, 2A7A1A2RV1P1.2
unnamed: 2A7A1A2RV1.3, 2A7A1A2RV1P1.3
unnamed: 2A7A1A3.1 (+5V), 2A7A1A3A1.1
unnamed: 2A7A1A3.2 (GND), 2A7A1A3A1.2
unnamed: 2A7A1A3.3 (ZERO_DETECT), 2A7A1A3A1.3
unnamed: 2A7A1A4.1 (LED_DOUT), 2A7A1A4A1.1, 2A7A1A4DS1.1, 2A7A1A4DS2.1
unnamed: 2A7A1A4.2 (SCL), 2A7A1A4A1.2, 2A7A1A4DS1.2, 2A7A1A4DS2.2
unnamed: 2A7A1A4.3 (COIL3), 2A7A1A4A1.3, 2A7A1A4DS1.3, 2A7A1A4DS2.3
unnamed: 2A7A1A4.4 (SDA), 2A7A1A4DS1.4, 2A7A1A4DS2.4
unnamed: 2A7A1A4SW1.A, 2A7A1A4SW1P1.1
unnamed: 2A7A1A4SW1.B, 2A7A1A4SW1P1.3
unnamed: 2A7A1A4SW1.C, 2A7A1A4SW1P1.2
unnamed: 2A7A1A5.1 (+5V), 2A7A1A5A1.1
unnamed: 2A7A1A5.2 (GND), 2A7A1A5A1.2
unnamed: 2A7A1A5.3 (ZERO_DETECT), 2A7A1A5A1.3
unnamed: 2A7A1A6.CON1 (TFT_DATA), ~.1
unnamed: 2A7A1A6.HDMI (HMDI), ~.1
unnamed: 2A7A1W1P1.1, 2A7A1W1P4.1
unnamed: 2A7A1W1P1.2, 2A7A1W1P4.3
unnamed: 2A7A1W1P1.3, 2A7A1W1P3.3
unnamed: 2A7A1W1P1.4, 2A7A1W1P3.1
unnamed: 2A7A1W1P1.5, 2A7A1W1P1.6, 2A7A1W1P2.2
unnamed: 2A7A1W1P1.7, 2A7A1W1P2.1
unnamed: 2A7A1W1P1.8, 2A7A1W1P3.2
unnamed: 2A7A1W1P1.9, 2A7A1W1P4.4
unnamed: 2A7A1W1P1.10, 2A7A1W1P4.2
unnamed: 2A7A1W2P1.1, 2A7A1W2P2.1
unnamed: 2A7A1W2P1.2, 2A7A1W2P2.2
unnamed: 2A7A1W2P1.3, 2A7A1W2P2.3
unnamed: 2A7A1W2P1.4, 2A7A1W2P2.4
unnamed: 2A7A1W2P1.5, 2A7A1W2P2.5
unnamed: 2A7A1W2P1.6, 2A7A1W2P2.6
unnamed: 2A7A1W2P1.7, 2A7A1W2P2.7
unnamed: 2A7A1W2P1.8, 2A7A1W2P2.8
unnamed: 2A7A1W2P1.9, 2A7A1W2P2.9
unnamed: 2A7A1W2P1.10, 2A7A1W2P2.10
unnamed: 2A7A1W2P1.11, 2A7A1W2P2.11
unnamed: 2A7A1W2P1.12, 2A7A1W2P2.12
unnamed: 2A7A1W2P1.13, 2A7A1W2P2.13
unnamed: 2A7A1W2P1.14, 2A7A1W2P2.14
unnamed: 2A7A1W3P1.1, 2A7A1W3P4.1
unnamed: 2A7A1W3P1.2, 2A7A1W3P4.3
unnamed: 2A7A1W3P1.3, 2A7A1W3P3.3
unnamed: 2A7A1W3P1.4, 2A7A1W3P3.1
unnamed: 2A7A1W3P1.5, 2A7A1W3P1.6, 2A7A1W3P2.2
unnamed: 2A7A1W3P1.7, 2A7A1W3P2.1
unnamed: 2A7A1W3P1.8, 2A7A1W3P3.2
unnamed: 2A7A1W3P1.9, 2A7A1W3P4.4
unnamed: 2A7A1W3P1.10, 2A7A1W3P4.2
unnamed: 2A8A1A1.1 (FWD), 2A8A1SW1.1
unnamed: 2A8A1A1.2 (0V), 2A8A1SW1.2, 2A8A1SW2.1
unnamed: 2A8A1A1.3 (REV), 2A8A1SW2.2
unnamed: 2A8A1A1.6 (M1), 2A8A1W1P1.1
unnamed: 2A8A1A1.7 (M2), 2A8A1W1P1.2
unnamed: 2A8A1A2.1, ~.1
unnamed: 2A8A1M1.1 (+), 2A8A1M1J1.1
unnamed: 2A8A1M1.2 (-), 2A8A1M1J1.2
unnamed: 2A9A1., ~.1, ~.2
unnamed: 2A9A2., ~.1, ~.2
unnamed: 2A9A3., ~.1, ~.2
unnamed: 2A10.J1 (POWER_IN), ~.1
unnamed: 2A10.J2 (GND), ~.1
unnamed: 2A10.J3 (RCON), ~.1
unnamed: 2A10.J4 (SPEAKER+), ~.1
unnamed: 2A10.J5 (SPEAKER-), ~.1
unnamed: 2A10.J6 (REMOTE), ~.1
unnamed: 2A10.J7 (LINE_IN_L), ~.1
unnamed: 2A10.J8 (LINE_IN_R), ~.1
unnamed: 2A10A2.1, ~.1
unnamed: 2A12A1W2.1, ~.1
unnamed: 2A12A1W3.1, ~.1
unnamed: 2A12A1W4.1, ~.1
unnamed: 2A12A1W5J1.1, 2A12A1W5J2.1
unnamed: 2A12A1W5J1.2, 2A12A1W5J2.2
unnamed: 2A12A1W5J1.3, 2A12A1W5J2.3
unnamed: 2A12A1W5J1.4, 2A12A1W5J2.4
unnamed: 2A12A1W5J1.5, 2A12A1W5J2.5
unnamed: 2A12A1W5J1.6, 2A12A1W5J2.6
unnamed: 2A12A1W5J1.7, 2A12A1W5J2.7
unnamed: 2A12A1W5J1.8, 2A12A1W5J2.8
unnamed: 2A12A1W5J1.9, 2A12A1W5J3.1
unnamed: 2A12A1W5J1.10, 2A12A1W5J3.2
unnamed: 2A12A1W5J1.11, 2A12A1W5J3.3
unnamed: 2A12A1W5J1.12, 2A12A1W5J3.4
unnamed: 2A12A1W5J1.13, 2A12A1W5J4.1
unnamed: 2A12A1W5J1.14, 2A12A1W5J4.2
unnamed: 2A12A1W5J1.15, 2A12A1W5J4.3
unnamed: 2A12A1W5J1.16, 2A12A1W5J4.4
unnamed: 2A12A2W2.1, ~.1
unnamed: 2A12A2W3.1, ~.1
unnamed: 2A12A2W4.1, ~.1
unnamed: 2A12A4W1P1.1, 2A12A4W1P2.1
unnamed: 2A12A4W1P1.2, 2A12A4W1P2.2
unnamed: 2A12A4W2P1.1, 2A12A4W2P2.1
unnamed: 2A12A4W2P1.2, 2A12A4W2P2.2
unnamed: 2A12A5W1.1 (AC_P), ~.1
unnamed: 2A12A5W1.2 (AC_N), ~.2
unnamed: 2A12A5W3J1.1, 2A12A5W3P1.1
unnamed: 2A12A5W3J1.2, 2A12A5W3P1.2
unnamed: 2A12A5W3J1.3, 2A12A5W3P1.3
unnamed: 2A12A5W3J1.4, 2A12A5W3P1.4
unnamed: 2A12A5W3J1.5, 2A12A5W3P1.5
unnamed: 2A12A5W3J1.6, 2A12A5W3P1.6
unnamed: 2A12A5W3J1.7, 2A12A5W3P1.7
unnamed: 2A12A5W3J1.8, 2A12A5W3P1.8
unnamed: 2A14A1.1 (PS_ON), ~.1
unnamed: 2A14A1.2 (+5VSB), ~.2
unnamed: 2A14A1.3 (PWR_OK), ~.3
unnamed: 2A14A1.4 (GND), ~.4
unnamed: 2A15A1.1 (OUT1+), ~.1
unnamed: 2A15A1.2 (OUT1-), ~.2
unnamed: 2A15A1.3 (OUT2+), ~.3
unnamed: 2A15A1.4 (OUT2-), ~.4
unnamed: 2A15A1.5 (OUT3+), ~.5
unnamed: 2A15A1.6 (OUT3-), ~.6
unnamed: 2A15A1.7 (OUT4+), ~.7
unnamed: 2A15A1.8 (OUT4-), ~.8
unnamed: 2A15W3P1.1, 2A15W3P2.1
unnamed: 2A15W3P1.2, 2A15W3P2.2
unnamed: 2A15W3P1.3, 2A15W3P2.3
unnamed: 2A15W3P1.4, 2A15W3P2.4
unnamed: A10A1.2, ~.1
PUSH_J9-5: 2A7A1.5 (GND)
PUSH_J10-1: 2A7A1.1
RC<>ABSIS_PSU_PWR: 0A2W2.1
RC<>BL1: 0A2W3.1
RC<>BL2: 0A2W4.1
RC<>UIP_USB_HUB: 0A2W1.1
RC_ABSIS_PWR: 2A14W4.1, (2A14W4).1
RC_BL_CH1: 2A13W9.1, (2A13W9).1
RC_BL_CH2: 2A13W10.1, (2A13W10).1
RWR_BRT_J8-2: 2A7A1.2 (BL_IN)
RWR_DIS_A: 2A4A1SW1.3
RWR_DIS_F: 2A4A1SW1.5
RWR_DIS_I: 2A4A1SW1.2
RWR_DIS_U: 2A4A1SW1.4
RWR_GND: 2A4A1SW1.C (COM)
SCL_J1-2: 2A7A1A4.2 (SCL)
SCL_J3-4: 2A3A1.4 (GND)
SCL_J6-2: 2A7A1.2 (BL_IN)
SDA_J1-4: 2A7A1A4.4 (SDA)
SDA_J3-3: 2A3A1.3 (A0)
SDA_J6-4: 2A7A1.4 (LED_DIN)
SIMPWR_BLM_A: 0A1W6P1.9, 2A13W3J1.3, 2A13W3P1.1
SIMPWR_BLM_B: 0A1W6P1.10, 2A13W3J1.4, 2A13W3P1.2
SIMPWR_BLM_GND: 0A1W6P1.12, 2A13W3J1.1, 2A13W3P1.4
SIMPWR_BLM_PUSH: 0A1W6P1.11, 2A13W3J1.5, 2A13W3P1.3
SIMPWR_DISP: 0A1W6P1.4, 2A15W2P1.4, 2A15W2P2.4
SIMPWR_GND: 0A1W6P1.7, 2A15W2P1.7, 2A15W2P2.7
SIMPWR_MAINT: 0A1W6P1.6, 2A15W2P1.6, 2A15W2P2.6
SIMPWR_MASTER: 0A1W6P1.3, 2A15W2P1.3, 2A15W2P2.3
SIMPWR_PCPWR: 0A1W6P1.1, 2A15W2P1.1, 2A15W2P2.1
SIMPWR_PCRESET: 0A1W6P1.2, 2A15W2P1.2, 2A15W2P2.2
SIMPWR_PFLT: 0A1W6P1.5, 2A15W2P1.5, 2A15W2P2.5
UIP_ABSIS_PWR: 2A14W2.1, (2A14W2).1
UIP_BL_CH1: 2A13W5.1, (2A13W5).1
UIP_BL_CH2: 2A13W6.1, (2A13W6).1
VR_+5V: 2A2A1A3RV1.1, 2A2A1A3W1J1.5
VR_AUTO: 2A2A1A3SW1.3, 2A2A1A3W1J1.2
VR_A_IFEI: 2A2A1A3RV1.2, 2A2A1A3W1J1.4
VR_GND: 2A2A1A3RV1.3, 2A2A1A3SW1.2, 2A2A1A3SW2.2 (B), 2A2A1A3W1J1.6
VR_LDDI: 2A2A1A3SW2.1 (A), 2A2A1A3W1J1.3
VR_MAN: 2A2A1A3SW1.1, 2A2A1A3W1J1.1
ZERO_DETECT_J1-11: 2A7A1A4.11 (ZERO_DETECT)
ZERO_DETECT_J2-3: 2A7A1A3.3 (ZERO_DETECT), 2A7A1A5.3 (ZERO_DETECT)
ZERO_DETECT_J5-3: 2A7A1.3 (MC)
ZERO_DETECT_J6-11: 2A7A1.11 (ZERO_DETECT)
ZERO_DETECT_J7-3: 2A7A1.3 (MC)
~12V_J3-1: 2A3A1.1 (A2)
~D3_SCL_J3-4: 2A2A1.4 (D7), 2A4A1.4 (D7), 2A5A1.4 (D7)
~D6-A7_J4-2: 2A2A1.2 (~D6/A7), 2A4A1.2 (~D6/A7), 2A5A1.2 (~D6/A7)
~D9-A9_J4-8: 2A2A1.8 (~D9/A9), 2A4A1.8 (~D9/A9), 2A5A1.8 (~D9/A9)
~D10-A10_J4-7: 2A2A1.7 (~D10/A10), 2A4A1.7 (~D10/A10), 2A5A1.7 (~D10/A10)
~D10_A10_J5-3: 2A3A1.3 (A0)

Notes on the sheet:
GND_J2-2
+5V_J1-1
PSU
2A12A5
RWR_DIS_I
2A12A2
LED_DOUT_J6-1
D15-SCK_J4-1
A2_J3-3
LED_DOUT_J2-2
LED_DIN_J2-1
~{D10-A10}_J4-7
COIL3_J5-9
~{D10}_A10_J5-3
GND_J5-6
A0_J7-3
+5V_J4-11
DISP_BYPASS
VIDEO RECORD
VR_+5V
2A12A1
D14-MISO_J4-3
D8-A8_J4-6
RWR_LIMIT_SW
+5V_J3-11
LIP -> RC BULKHEAD
GND_J1-14
COIL2_J3-3
ET_SW
D2-SDA_J3-2
GND_J3-6
ZERO_DETECT_J7-3
RWR_BRT_A
BL CONTROLLER
GND_J3-8
GND_J3-10
COIL1_J6-7
SARI_GND
LED_DIN_J6-13
M6 RING TERMINAL
COIL3_J7-9
M4 RING TERMINALS
CONFIGURE AMP AS FOLLOWS: * INFRASONIC FILTER - OFF * INPUT SENSITIVITY - .2V * BASS BOOST - 0dB * LPF FREQ - 200Hz OR LESS
+5V_J1-12
VR_MAN
A0_J3-7
OFF
SDA_J6-4
COIL3_J3-4
ECM_STBY
COIL1_J5-2
R LIP -> R UIP BULKHEAD
+5V_J4-9
LOWER INSTRUMENT PANEL (LIP)
GND_J6-14
CH_A_J6-6
GND_J4-10
R DDI
COIL4_J5-10
RWR_A_DMR
SCL_J6-2
CH_A_J2-1
LI_SW
COIL2_J5-1
UP_SW
RWR_BRT_GND
DOWN_SW
POWER_SW
D16-MOSI_J4-5
HUD
LC USB HUB
L DDI
GND_J3-12
HDMI TO USB #2
SHORE BULKHEAD
ECM_JETT_SW
D7_J4-3
A1_J3-5
RWR_DIS_A
6X FL2
RUDDER PEDALS & GANTRY
IFEI
~{D3_SCL}_J3-4
COIL1_J5-1
GND_J7-5
COIL1_J7-1
BACKLIGHTING PANELS
GND_J5-2
QTY_SW
SARI_CH_A
SCL_J3-4
CTR_SW
D7_J4-4
MODE_SW
RWR_A_AUDIO
VR_LDDI
COIL3_J6-3
SDA_J1-4
ZERO_DETECT_J1-11
LO_SW
TO R UIP BULKHEAD
GND_J4-12
ECM/DISP
+5V_J7-2
ECM_REC
ECM_GND
RWR CONTROL
A3_J3-1
GND_J5-5
PC RST +
CH_B_J1-8
LIP USB HUB #2
~{D6-A7}_J4-2
RWR_DIS_U
D4-A6_J3-6
PC PWR -
RUDDER PEDALS
RWR_GND
COIL4_J6-5
AMPCD DISPLAY
GND_J7-6
+5V_J5-7
SARI_CAGE
2X 10 AWG W/
+5V_J7-7
RWR_BRT_+5V
COIL2_J7-2
~{D9-A9}_J4-8
INTERNAL DISPLAYS
16AWG W/
COIL2_J5-2
ZERO_DETECT_J2-3
2A12A3
CH_B_J2-3
GND
2A14
RWR_DIS_N
BACKLIGHT CONTROLLER
CH_B_J6-8
ECM_OFF
GANTRY-
COIL4_J3-2
M4 RING
D4_A6_J4-1
+3.3V_J1-10
COIL2_J1-9
LED_DIN_J7-4
SPECIAL_SW
GND_J7-4
COIL1_J3-1
AXR_NORM
SCL_J1-2
COIL4_J7-10
BUTTKICKER AMP
USB HUBS
NC_SPARE
LED_DIN_J1-13
EXPANSION #1
NOTE: USE BUS TERMINATION RESISTOR ON 2A7A1J2
VR_A_IFEI
UIP USB HUB
RWR
AMPCD
LED_DOUT_J5-8
PMS
SARI_TEST
GND_J4-2
RWR_DIS_F
HDMI TO USB #1
VR_AUTO
AUXR_ENBL
COIL4_J1-5
SPARE1 +
ZERO_DETECT_J6-11
RWR_+5V
+5V_J3-2
+3.3V_J6-10
LED_DIN_J5-4
L LIP -> L UIP BULKHEAD
LIP ABSIS BUS MASTER
(ABSIS-CA-J-XXX)
PC PWR +
COIL3_J1-3
EXT DISP -
RO_SW
IRQ_J3-5
RC USB HUB
+5V_J6-12
ECM_XMIT
CH_A_J1-6
RWR_OFFSET_SW
SARI_CH_B
PIT MANAGEMENT SYSTEM
2A12A4
ECM_BIT
EXT DISP +
LIP USB HUB #3
ZONE_SW
SDA_J3-3
LED_DOUT_J1-1
