jrsteensen/OpenHornet/ECAD/specifications/OH-SPEC-002.kicad_sch

## KiCad design ECAD/specifications/OH-SPEC-002.kicad_sch (2026-09-24)

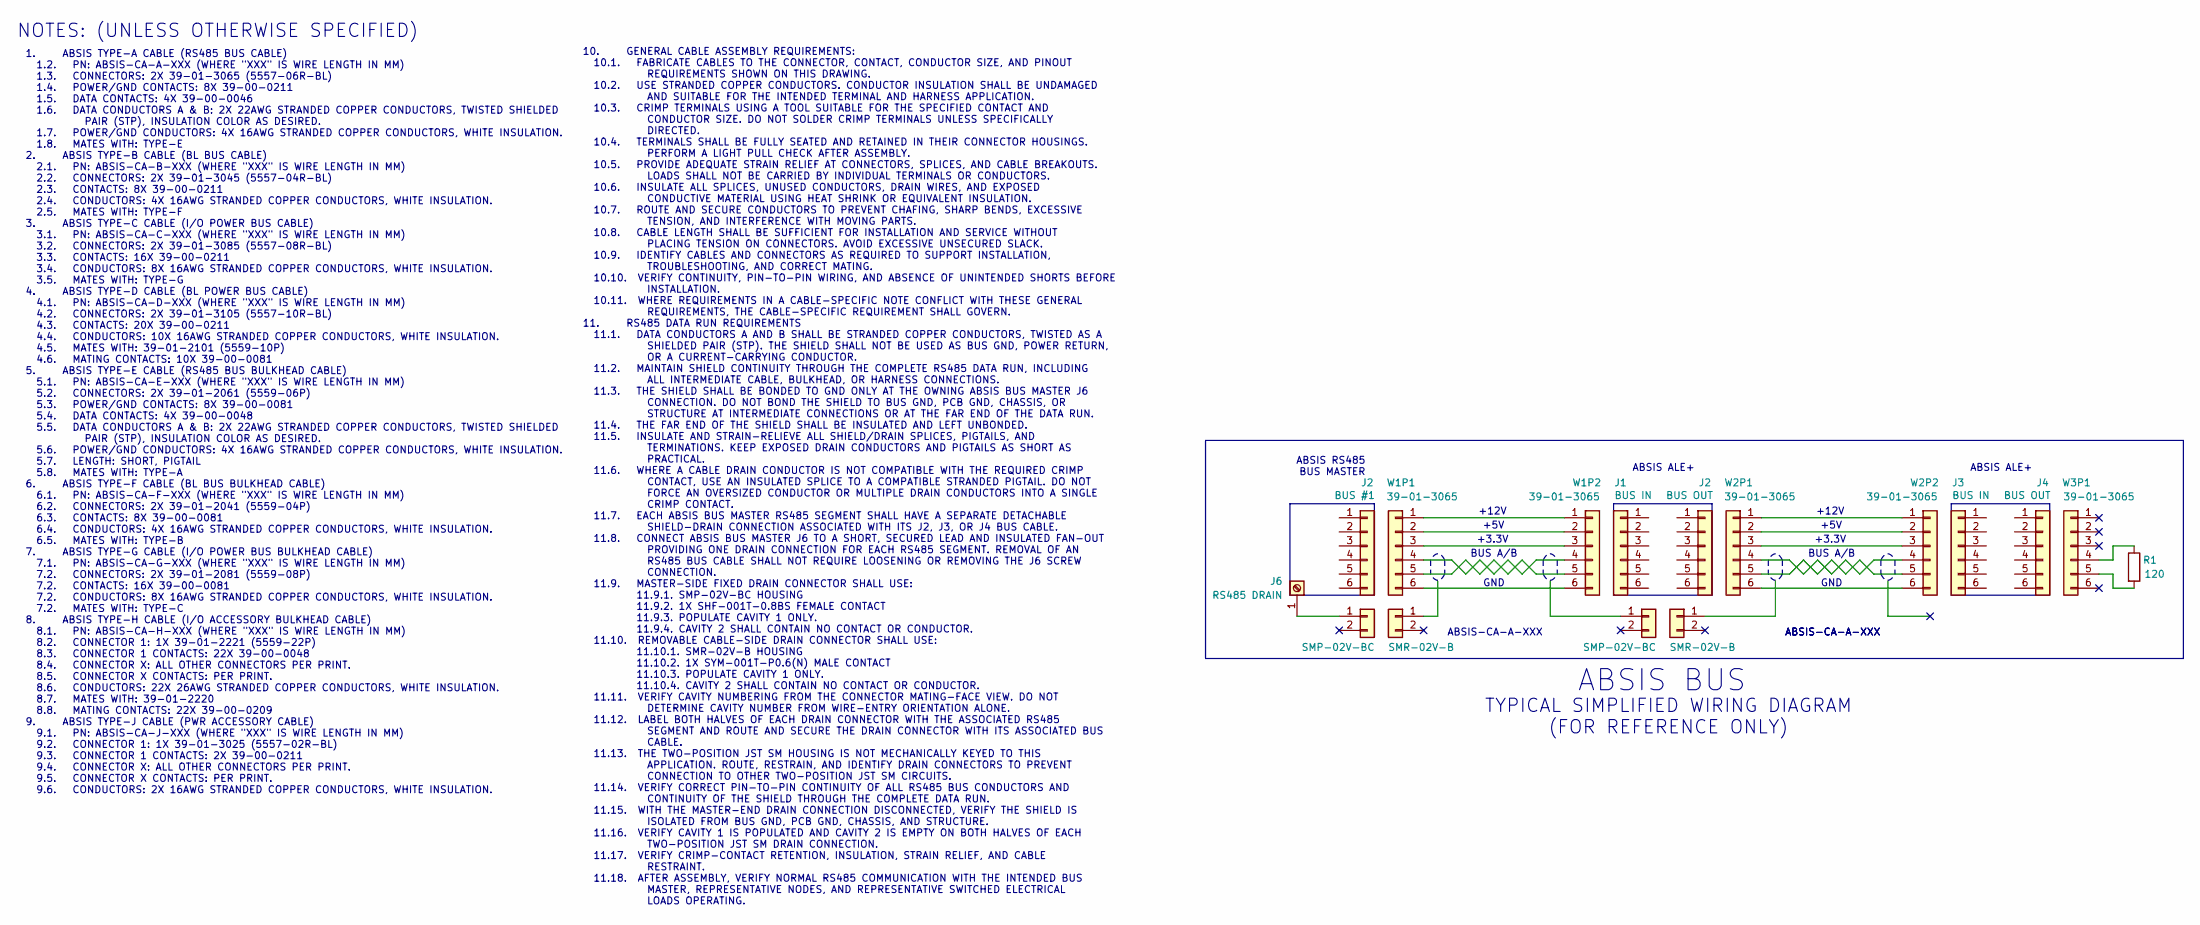
[picture p650: schematic OH-SPEC-002.kicad_sch]

Parts:
J1, J3: BUS IN; PinHeader_1x06_P2.54mm_Vertical
J2: BUS #1; PinHeader_1x06_P2.54mm_Vertical
J4: BUS OUT; PinHeader_1x06_P2.54mm_Vertical
J5, J9: SMR-02V-B; PinHeader_1x06_P2.54mm_Vertical
J6, J8: SMP-02V-BC; PinHeader_1x06_P2.54mm_Vertical
R1: 120
W1P1, W1P2, W2P1, W2P2, W3P1: 39-01-3065; PinHeader_1x06_P2.54mm_Vertical

Connections:
unnamed: R1.1, W3P1.4
unnamed: R1.2, W3P1.5
unnamed: W1P1.1, W1P2.1
unnamed: W1P1.2, W1P2.2
unnamed: W1P1.3, W1P2.3
unnamed: W1P1.4, W1P2.4
unnamed: W1P1.5, W1P2.5
unnamed: W1P1.6, W1P2.6
unnamed: W2P1.1, W2P2.1
unnamed: W2P1.2, W2P2.2
unnamed: W2P1.3, W2P2.3
unnamed: W2P1.4, W2P2.4
unnamed: W2P1.5, W2P2.5
unnamed: W2P1.6, W2P2.6

Notes on the sheet:
NOTES: (UNLESS OTHERWISE SPECIFIED)
+5V
+3.3V
1. ABSIS TYPE-A CABLE (RS485 BUS CABLE) 1.2. PN: ABSIS-CA-A-XXX (WHERE "XXX" IS WIRE LENGTH IN MM) 1.3. CONNECTORS: 2X 39-01-3065 (5557-06R-BL) 1.4. POWER/GND CONTACTS: 8X 39-00-0211 1.5. DATA CONTACTS: 4X 39-00-0046 1.6. DATA CONDUCTORS A & B: 2X 22AWG STRANDED COPPER CONDUCTORS, TWISTED SHIELDED 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
GND
ABSIS-CA-A-XXX
ABSIS ALE+
ABSIS BUS
BUS A/B
+12V
ABSIS RS485 BUS MASTER
TYPICAL SIMPLIFIED WIRING DIAGRAM (FOR REFERENCE ONLY)
10. GENERAL CABLE ASSEMBLY REQUIREMENTS: 10.1. FABRICATE CABLES TO THE CONNECTOR, CONTACT, CONDUCTOR SIZE, AND PINOUT REQUIREMENTS SHOWN ON THIS DRAWING. 10.2. USE STRANDED COPPER CONDUCTORS. CONDUCTOR INSULATION SHALL BE UNDAMAGED AND SUITABLE FOR THE INTENDED TERMINAL AND HARNESS APPLICATION. 10.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
