jrsteensen/OpenHornet/ECAD/PCBs/Specialty/55_SQ_Indicator/sq_indicator.sch

## KiCad design ECAD/PCBs/Specialty/55_SQ_Indicator/sq_indicator.sch (2019-10-15)

Schematic: sq_indicator.sch

Parts:
D1, D2, D3, D4: LED; LED_0603_HandSoldering
J1: Conn_01x04; Pin_Header_Straight_1x04_Pitch2.54mm_SMD_Pin1Left
R1, R2: 68; R_0603_HandSoldering
SW1: push; SWITCH_SNAP_DOME_6.3mm_DIA_SINGLE_SIDE_PCB

Notes on the sheet:
in order to control the LED intensity change R1 and R2 value using the following values. 90ohm = 7.5 mA/LED 68ohm = 10 mA/LED 47ohm = 15 mA/LED 33ohm = 20 mA/LED* *this configuration might bee too much for arduino pins to drive. to drive currents 20mA and higher use a Mosfet
