jrsteensen/OpenHornet/ECAD/PCBs/Specialty/ANALOG_STICK_BREAKOUT/ANALOG_STICK_BREAKOUT.sch

## KiCad design ECAD/PCBs/Specialty/ANALOG_STICK_BREAKOUT/ANALOG_STICK_BREAKOUT.sch (2022-09-23)

Schematic: ANALOG_STICK_BREAKOUT.sch

Parts:
C1: 4.7uF; C_1206_3216Metric; LCSC C29823
H1, H2: MountingHole; MountingHole_3mm
J2, J3, J4, J5, J6: Conn_01x01; SolderWirePad_1x01_SMD_2x4mm
JOY1: ANALOGSTICK_CENTERPUSH; RKJXV12
R1: 10k; R_0603_1608Metric
