jrsteensen/OpenHornet/ECAD/PCBs/Specialty/AP/AP.sch

## KiCad design ECAD/PCBs/Specialty/AP/AP.sch (2019-10-15)

Schematic: AP.sch

Parts:
J1: Conn_02x04_Odd_Even; Pin_Header_Straight_2x04_Pitch2.54mm_SMD
SW1, SW2, SW3, SW4, SW5, SW6, SW7: SW_SPST; SWITCH_SNAP_DOME_6.3mm_DIA_SINGLE_SIDE_PCB
