jrsteensen/OpenHornet/ECAD/PCBs/Specialty/Caution_lights_panel/Caution_Light_Panel.sch

## KiCad design ECAD/PCBs/Specialty/Caution_lights_panel/Caution_Light_Panel.sch (2019-10-15)

Schematic: Caution_Light_Panel.sch

Parts:
C1: 0.1uF; C_0603_HandSoldering
C2: 100nF; C_0603_HandSoldering
C3: 47uF; C_0603_HandSoldering
D1: 0,0; LED_0603_HandSoldering
D2: 1,0; LED_0603_HandSoldering
D3: 2,0; LED_0603_HandSoldering
D4: 3,0; LED_0603_HandSoldering
D7: 0,1; LED_0603_HandSoldering
D8: 1,1; LED_0603_HandSoldering
D9: 2,1; LED_0603_HandSoldering
D10: 3,1; LED_0603_HandSoldering
D13: 0,2; LED_0603_HandSoldering
D14: 1,2; LED_0603_HandSoldering
D15: 2,2; LED_0603_HandSoldering
D16: 3,2; LED_0603_HandSoldering
D18: 0,3; LED_0603_HandSoldering
D19: 1.3; LED_0603_HandSoldering
D20: 2,3; LED_0603_HandSoldering
D21: 3,3; LED_0603_HandSoldering
D22: 0.4; LED_0603_HandSoldering
D23: 1.4; LED_0603_HandSoldering
D24: 2,4; LED_0603_HandSoldering
D25: 3,4; LED_0603_HandSoldering
D26: 0.5; LED_0603_HandSoldering
D27: 1.5; LED_0603_HandSoldering
D28: 2,5; LED_0603_HandSoldering
D29: 3,5; LED_0603_HandSoldering
IC1: MAX7219; SOIC-24W_7.5x15.4mm_Pitch1.27mm
J1: PWR; Molex_KK-6410-04_04x2.54mm_Straight
J2: BUS IN; Molex_KK-6410-03_03x2.54mm_Straight
J3: BUS OUT; Molex_KK-6410-03_03x2.54mm_Straight
J4: PGM ENBLE; Pin_Header_Straight_1x02_Pitch2.54mm
MK1, MK2, MK3, MK4: Mounting_Hole; MountingHole_2.5mm
P1: Digital; Pin_Header_Straight_1x15_Pitch2.54mm_SMD_Pin1Left
P2: Analog; Pin_Header_Straight_1x15_Pitch2.54mm_SMD_Pin1Left
R2: 120; R_0603_HandSoldering
Rset1: 30K; R_0603_HandSoldering
U1: MAX487EESA; SOIC-8_3.9x4.9mm_Pitch1.27mm

Notes on the sheet:
Shield for Arduino Nano
RS-485 BUS
1) INSTALL 120 OHM RESISTOR ACROSS A AND B OF MAX487 ONLY FOR BUS TERMINATION. 2) INSTALL JUMPER BETWEEN PIN 1 AND 2 OF PGM SEL FOR RS487 BUS ENABLE. REMOVE JUMPER FOR PROGRAMMING ARDUINO NANO.
NOTES: (UNLESS OTHERWISE SPECIFIED)
PWR IN
PWR FLAGS
MOUNTING HOLES
MAX7219 LED DRIVER
LED MATRIX
place close to IC1
OUTBOARD
INBOARD
