jrsteensen/OpenHornet/ECAD/PCBs/Specialty/DDI/DDI_shield.sch

## KiCad design ECAD/PCBs/Specialty/DDI/DDI_shield.sch (2020-01-07)

Schematic: DDI_shield.sch

Parts:
C1: 0.1uF; C_0805_2012Metric_Pad1.15x1.40mm_HandSolder
J1: PWR; Molex_KK-254_AE-6410-04A_1x04_P2.54mm_Vertical
J2: BUS IN; Molex_KK-254_AE-6410-03A_1x03_P2.54mm_Vertical
J3: BUS OUT; Molex_KK-254_AE-6410-03A_1x03_P2.54mm_Vertical
J4: PGM SEL; Pin_Header_Straight_1x02_Pitch2.54mm
J5: BRT; Molex_KK-254_AE-6410-03A_1x03_P2.54mm_Vertical
J6: ExpansionPort; PinHeader_1x05_P2.54mm_Vertical
J7: CONT; Molex_KK-254_AE-6410-03A_1x03_P2.54mm_Vertical
J8: ROT SW; PinHeader_1x04_P2.54mm_Vertical
J9: CRS; PinHeader_1x03_P2.54mm_Vertical
J10: HDG; PinHeader_1x03_P2.54mm_Vertical
P1: Digital; Socket_Strip_Arduino_1x15
P2: Analog; Socket_Strip_Arduino_1x15
P3, P4, P5, P6: mounting; 1pin_Nano
R1: 120; R_0805_2012Metric_Pad1.15x1.40mm_HandSolder
R2, R3, R4, R5: 10k; R_0805_2012Metric_Pad1.15x1.40mm_HandSolder
U1: MAX487EESA; SOIC-8_3.9x4.9mm_Pitch1.27mm

Notes on the sheet:
Holes
NANO CONNECTIONS
RS-485 BUS
1) INSTALL 120 OHM RESISTOR ACROSS A AND B OF MAX487 ONLY FOR BUS TERMINATION. 2) INSTALL JUMPER BETWEEN PIN 1 AND 2 OF PGM SEL FOR RS487 BUS ENABLE. REMOVE JUMPER FOR PROGRAMMING ARDUINO NANO. 3) SEE DOCUMENTATION FOR CONNECTIVITY AND CONFIGURATION.
NOTES: (UNLESS OTHERWISE SPECIFIED)
PWR IN
PWR FLAGS
Inputs
I2C addresses 0b0111000 0b0111001 0b0111010 0b0111011
DEVICE differentiation see documentation
13(SCK)
6(**)
