jrsteensen/OpenHornet/ECAD/PCBs/Specialty/HAT_SWITCH_BREAKOUT/HAT_SWITCH_BREAKOUT.sch

## KiCad design ECAD/PCBs/Specialty/HAT_SWITCH_BREAKOUT/HAT_SWITCH_BREAKOUT.sch (2022-09-23)

Schematic: HAT_SWITCH_BREAKOUT.sch

Parts:
H1, H2: MountingHole; MountingHole_3mm
J1, J2, J3, J4, J5, J6: Conn_01x01; SolderWirePad_1x01_SMD_2x4mm
S1: 8WayHat_CenterPush; RKJXM10
