jrsteensen/OpenHornet/ECAD/PCBs/Specialty/IFEI/IFEI.sch

## KiCad design ECAD/PCBs/Specialty/IFEI/IFEI.sch (2019-11-01)

Schematic: IFEI.sch

Parts:
J1: Conn_02x04_Male; PinHeader_2x04_P2.54mm_Horizontal
MK1, MK2, MK3, MK4: Mounting_Hole; Mouting_Hole_1.85mm
SW1: mode; SWITCH_SNAP_DOME_6.3mm_DIA_SINGLE_SIDE_PCB
SW2: qty; SWITCH_SNAP_DOME_6.3mm_DIA_SINGLE_SIDE_PCB
SW3: up; SWITCH_SNAP_DOME_6.3mm_DIA_SINGLE_SIDE_PCB
SW4: down; SWITCH_SNAP_DOME_6.3mm_DIA_SINGLE_SIDE_PCB
SW5: zone; SWITCH_SNAP_DOME_6.3mm_DIA_SINGLE_SIDE_PCB
SW6: ET; SWITCH_SNAP_DOME_6.3mm_DIA_SINGLE_SIDE_PCB
