jrsteensen/OpenHornet/ECAD/PCBs/Specialty/LED_MATRIX_debug/debug.sch

## KiCad design ECAD/PCBs/Specialty/LED_MATRIX_debug/debug.sch (2019-10-15)

Schematic: debug.sch

Parts:
C1: 220uF; CP_Elec_6.3x7.7
C2: 47uF; C_0603_HandSoldering
C5: 27pF; C_0603_HandSoldering
C8: 100nF; C_0603_HandSoldering
DIG0-0, DIG0-1, DIG0-2, DIG0-3: LTP-305G
IC0: MAX6953
J1: PWR IN; Pin_Header_Straight_1x04_Pitch2.54mm
J2: OLED DISP; Pin_Header_Straight_1x07_Pitch2.54mm_SMD_Pin1Left
J3: SDA bypass; Pin_Header_Straight_1x02_Pitch2.54mm
J4: SCL bypass; Pin_Header_Straight_1x02_Pitch2.54mm
J5: Pwr sel; Pin_Header_Straight_1x03_Pitch2.54mm
J6: ADD1; Pin_Header_Straight_2x04_Pitch2.54mm
J7: ADD0; Pin_Header_Straight_2x04_Pitch2.54mm
J8: GND; Test_Point
J9: SDA; Test_Point
J10: SCL; Test_Point
P1: Power; Socket_Strip_Arduino_1x08
P2, P3: Analog; Socket_Strip_Arduino_1x08
P4: Digital; Socket_Strip_Arduino_2x18
P5: PWM; Socket_Strip_Arduino_1x10
P6: PWM; Socket_Strip_Arduino_1x08
P7: Communication; Socket_Strip_Arduino_1x08
P8, P9, P10, P11, P12, P13: CONN_01X01; Arduino_1pin
Q1, Q2: BSS138; SOT-23
R1: 5; R_Axial_DIN0204_L3.6mm_D1.6mm_P2.54mm_Vertical
R6, R7, R8, R9: 10k; R_0603_HandSoldering
R15: 53.6k; R_0603_HandSoldering

Notes on the sheet:
OPTION #1 DOT MATRIX DISPLAYS
ADDRESS: 1010000
PWR IN
SCRATCHPAD DISPLAY (SPI) OLED
Power flags
place Rset as close as possible to pin 15, ground of Rset MUST be ground bounce mitigated (cut in copper connecting to pin 17)
when using 4 matrices power might use up to 0.5 amps
3.3v-5v Level shifter
place C2 close to J2
Shield for Arduino Mega Rev 3
Holes
Address selection
select 3.3v when using external power. select 5v when using 5v from arduino. 5v might not have enoufh current!
Install jumpers when working with 4v power supply
