jrsteensen/OpenHornet/ECAD/PCBs/Specialty/Master_Mode_Pushbutton/MasterModePushbutton.sch

## KiCad design ECAD/PCBs/Specialty/Master_Mode_Pushbutton/MasterModePushbutton.sch (2019-10-15)

Schematic: MasterModePushbutton.sch

Parts:
D1, D2, D3, D4: LED; LED_0603_HandSoldering
J1: Conn_02x03; Pin_Header_Straight_2x03_Pitch2.54mm_SMD
R1, R2: 68; R_0603_HandSoldering
SW1, SW2: push; SWITCH_SNAP_DOME_6.3mm_DIA_SINGLE_SIDE_PCB

Notes on the sheet:
in order to control the LED intensity change R1 and R2 value using the following values. 90ohm = 7.5 mA/LED 68ohm = 10 mA/LED 47ohm = 15 mA/LED 33ohm = 20 mA/LED* *this configuration might bee too much for arduino pins to drive. to drive currents 20mA and higher use a Mosfet
