jrsteensen/OpenHornet/ECAD/PCBs/Specialty/RWR_Control_Panel/RWR_Control_Panel.sch

## KiCad design ECAD/PCBs/Specialty/RWR_Control_Panel/RWR_Control_Panel.sch (2019-11-10)

Schematic: RWR_Control_Panel.sch

Parts:
C1: 0.1uF; C_0805_HandSoldering
C2: 100nF; C_0805_HandSoldering
D1, D2, D4, D5, D7, D8, D11, D12, D13, D14, D15, D16, D18, D19, D20, D21, D22, D23, D24, D25: WHT; LED_0603_HandSoldering
J1: PWR; Molex_KK-6410-04_04x2.54mm_Straight
J2: BUS IN; Molex_KK-6410-03_03x2.54mm_Straight
J3: BUS OUT; Molex_KK-6410-03_03x2.54mm_Straight
J4: PGM SEL; Pin_Header_Straight_1x02_Pitch2.54mm
J5: RPOT1; Pin_Header_Straight_1x03_Pitch2.54mm
J6: RPOT2; Pin_Header_Straight_1x03_Pitch2.54mm
J7: 5POS; Pin_Header_Straight_1x06_Pitch2.54mm
P1: Digital; Socket_Strip_Straight_1x15_Pitch2.54mm
P2: Analog; Socket_Strip_Straight_1x15_Pitch2.54mm
P3, P4, P5, P6: CONN_01X01; MountingHole_4.3mm_M4
R1: 120; R_0805_HandSoldering
R11: 1K; R_0805_HandSoldering
SW1, SW2, SW3, SW4, SW5: SW_Push; SWITCH_SNAP_DOME_6.3mm_DIA_SINGLE_SIDE_PCB
U1: MAX487EESA; Texas_S-PWSON-N10
U2: STP16CPC26; SOIC-24W_7.5x15.4mm_Pitch1.27mm

Notes on the sheet:
Holes
NANO CONNECTIONS
RS-485 BUS
1) INSTALL 120 OHM RESISTOR ACROSS A AND B OF MAX487 ONLY FOR BUS TERMINATION. 2) INSTALL JUMPER BETWEEN PIN 1 AND 2 OF PGM SEL FOR RS487 BUS ENABLE. REMOVE JUMPER FOR PROGRAMMING ARDUINO NANO.
NOTES: (UNLESS OTHERWISE SPECIFIED)
PWR IN
PWR FLAGS
OUTPUT 1
OUTPUT 2
OUTPUT 3
OUTPUT 4
OUTPUT 5
OUTPUT 6
OUTPUT 7
OUTPUT 8
OUTPUT 9
OUTPUT 10
INPUT 1
INPUT 2
INPUT 3
INPUT 4
INPUT 5
CONFIGURE INTERNAL PULLUPS FOR ALL INPUTS
R11 SET TO 1K FOR 20mA
ROTARY POT CONNECTIONS
ROTARY SWITCH CONNECTIONs
