jrsteensen/OpenHornet/ECAD/PCBs/Specialty/THROTTLE_INNER_GRIP/THROTTLE_INNER_GRIP.sch

## KiCad design ECAD/PCBs/Specialty/THROTTLE_INNER_GRIP/THROTTLE_INNER_GRIP.sch (2022-09-23)

Schematic: THROTTLE_INNER_GRIP.sch

Parts:
ANT1: Conn_01x03; JST_PH_B3B-PH-K_1x03_P2.00mm_Vertical
C1: 10uF; C_1206_3216Metric; LCSC C13585
C7, C8: 0.1uF; C_0603_1608Metric; LCSC C14663
CAGE1: Conn_01x02; JST_PH_B2B-PH-K_1x02_P2.00mm_Vertical
CM1: Conn_01x03; JST_PH_B3B-PH-K_1x03_P2.00mm_Vertical
COM1: COMS; JST_PH_B6B-PH-K_1x06_P2.00mm_Vertical
H1, H4: MountingHole; MountingHole_3mm
J2: BASE; JST_PH_B5B-PH-K_1x05_P2.00mm_Vertical
JOY1: JOYSTICK; JST_PH_B5B-PH-K_1x05_P2.00mm_Vertical
SP1: Conn_01x03; JST_PH_B3B-PH-K_1x03_P2.00mm_Vertical
U1: ProMini_NoProgrammingHeader; Arduino_Mini_Pro_No_Programming_Header

Notes on the sheet:
JOYSTICK
COMS SWITCH
SPEEDBREAK
COUNTERMEASURES
CAGE/UNCAGE
ANTENNAELEVATION
TO BASE CONTROLLER
