jrsteensen/OpenHornet/ECAD/PCBs/Specialty/UFC/UFC.sch

## KiCad design ECAD/PCBs/Specialty/UFC/UFC.sch (2019-10-23)

Schematic: UFC.sch

Parts:
C1: 220uF; CP_Elec_6.3x7.7
C2, C3, C4, C11, C12, C13: 47uF; C_0805_2012Metric_Pad1.15x1.40mm_HandSolder
C5, C6, C7, C14, C15, C16: 27pF; C_0805_2012Metric_Pad1.15x1.40mm_HandSolder
C8, C9, C10, C17, C18, C19: 100nF; C_0805_2012Metric_Pad1.15x1.40mm_HandSolder
D1, D2, D3, D4, D5, D6, D7, D8, D9, D10: WP914GDT; LED_0805_2012Metric_Pad1.15x1.40mm_HandSolder
DIG0-0, DIG0-1, DIG0-2, DIG0-3, DIG1-0, DIG1-1, DIG1-2, DIG1-3, DIG2-0, DIG2-1, DIG2-2, DIG2-3, DIG3-0, DIG3-1, DIG3-2, DIG3-3, DIG4-0, DIG4-1, DIG4-2, DIG4-3, DIG5-0, DIG5-1: LTP-305G
IC0, IC1, IC2, IC3, IC4, IC5: MAX6953
J1: PWR IN; PinHeader_1x04_P2.54mm_Vertical_SMD_Pin1Left
J2: OLED DISP; PinHeader_1x07_P2.54mm_Vertical_SMD_Pin1Left
J3: BRT/COMM2; PinHeader_2x03_P2.54mm_Vertical_SMD
J4: COM1 ENC; PinHeader_1x04_P2.54mm_Vertical_SMD_Pin1Left
J5: COM2 ENC; PinHeader_1x04_P2.54mm_Vertical_SMD_Pin1Left
J6: AP BTNS; PinHeader_2x04_P2.54mm_Vertical_SMD
J7: HUD PANL; PinHeader_2x08_P2.54mm_Vertical_SMD
J8: HUD BIT; PinHeader_1x04_P2.54mm_Vertical_SMD_Pin1Left
J9: ADF/COMM1; PinHeader_2x03_P2.54mm_Vertical_SMD
MK1, MK2, MK3, MK4: Mounting_Hole; MountingHole_4.3mm_M4
P1: MEGA CONN 2; PinHeader_2x18_P2.54mm_Vertical_SMD
P2: MEGA CONN 1; PinHeader_2x18_P2.54mm_Vertical_SMD
Q1, Q2: BSS138; SOT-23
R1, R2, R3, R4, R5: 33; R_0805_2012Metric_Pad1.15x1.40mm_HandSolder
R6, R7, R8, R9: 10k; R_0805_2012Metric_Pad1.15x1.40mm_HandSolder
R15, R16, R17, R27, R28, R29: 53.6k; R_0805_2012Metric_Pad1.15x1.40mm_HandSolder
SW1: 1; SWITCH_SNAP_DOME_6.3mm_DIA_SINGLE_SIDE_PCB
SW2: 4; SWITCH_SNAP_DOME_6.3mm_DIA_SINGLE_SIDE_PCB
SW3: 7; SWITCH_SNAP_DOME_6.3mm_DIA_SINGLE_SIDE_PCB
SW4: CLR; SWITCH_SNAP_DOME_6.3mm_DIA_SINGLE_SIDE_PCB
SW5: 2; SWITCH_SNAP_DOME_6.3mm_DIA_SINGLE_SIDE_PCB
SW6: 5; SWITCH_SNAP_DOME_6.3mm_DIA_SINGLE_SIDE_PCB
SW7: 8; SWITCH_SNAP_DOME_6.3mm_DIA_SINGLE_SIDE_PCB
SW8: ~0; SWITCH_SNAP_DOME_6.3mm_DIA_SINGLE_SIDE_PCB
SW9: I/P; SWITCH_SNAP_DOME_6.3mm_DIA_SINGLE_SIDE_PCB
SW10: 3; SWITCH_SNAP_DOME_6.3mm_DIA_SINGLE_SIDE_PCB
SW11: 6; SWITCH_SNAP_DOME_6.3mm_DIA_SINGLE_SIDE_PCB
SW12: 9; SWITCH_SNAP_DOME_6.3mm_DIA_SINGLE_SIDE_PCB
SW13: ENT; SWITCH_SNAP_DOME_6.3mm_DIA_SINGLE_SIDE_PCB
SW14: EMCON; SWITCH_SNAP_DOME_6.3mm_DIA_SINGLE_SIDE_PCB
SW15: OPT2; SWITCH_SNAP_DOME_6.3mm_DIA_SINGLE_SIDE_PCB
SW16: OPT3; SWITCH_SNAP_DOME_6.3mm_DIA_SINGLE_SIDE_PCB
SW17: OPT4; SWITCH_SNAP_DOME_6.3mm_DIA_SINGLE_SIDE_PCB
SW18: OPT5; SWITCH_SNAP_DOME_6.3mm_DIA_SINGLE_SIDE_PCB
SW19: OPT1; SWITCH_SNAP_DOME_6.3mm_DIA_SINGLE_SIDE_PCB

Notes on the sheet:
OPTION #1 DOT MATRIX DISPLAYS
OPTION #2 DOT MATRIX DISPLAYS
OPTION #3 DOT MATRIX DISPLAYS
OPTION #4 DOT MATRIX DISPLAYS
OPTION #5 DOT MATRIX DISPLAYS
COMM 1/COMM 2 DOT MATRIX DISPLAYS
ADDRESS: 1010000
ADDRESS: 1010001
ADDRESS: 1010010
ADDRESS: 1010011
ADDRESS: 1010100
ARDUINO MEGA HEADERS
PANEL MOUNTED UFC SWITCHES (BRT/VOL2/ADF/VOL1)
PWR IN
ENCODERS COMM 1/2
SCRATCHPAD DISPLAY (SPI) OLED
AP PANEL
UFC PANEL SNAP DOME SWITCHES
SPI BUS (5 X 7 DOT MATRIX DISPLAYS)
LEDs OPTION INDICATORS
HUD PANEL
HUD BIT TEST
PWR FLAGS
place Rset as close as possible to pin 15, ground of Rset MUST be ground bounce mitigated (cut in copper connecting to pin 17)
3.3v line might require more than 3A!!!
3.3v-5v Level shifter
Note, if we want to use 5v for the matrices thus avoiding the level shifter we need to 1) get the 5v directly from PSU as we will need a few Watts 2) add three (3) 2.2ohm 1W resistors in PARALLEL between 5v rail and matrixpower net, this is done to reduce the amount of power used by the system
see note below
place C2 close to J2
MOUNTING HOLES
