jrsteensen/OpenHornet/ECAD/PCBs/OH_Specific/Backlighting/APU_Panel_PCB_V2/APU Panel PCB V2.sch

## KiCad design ECAD/PCBs/OH_Specific/Backlighting/APU_Panel_PCB_V2/APU Panel PCB V2.sch (2021-02-01)

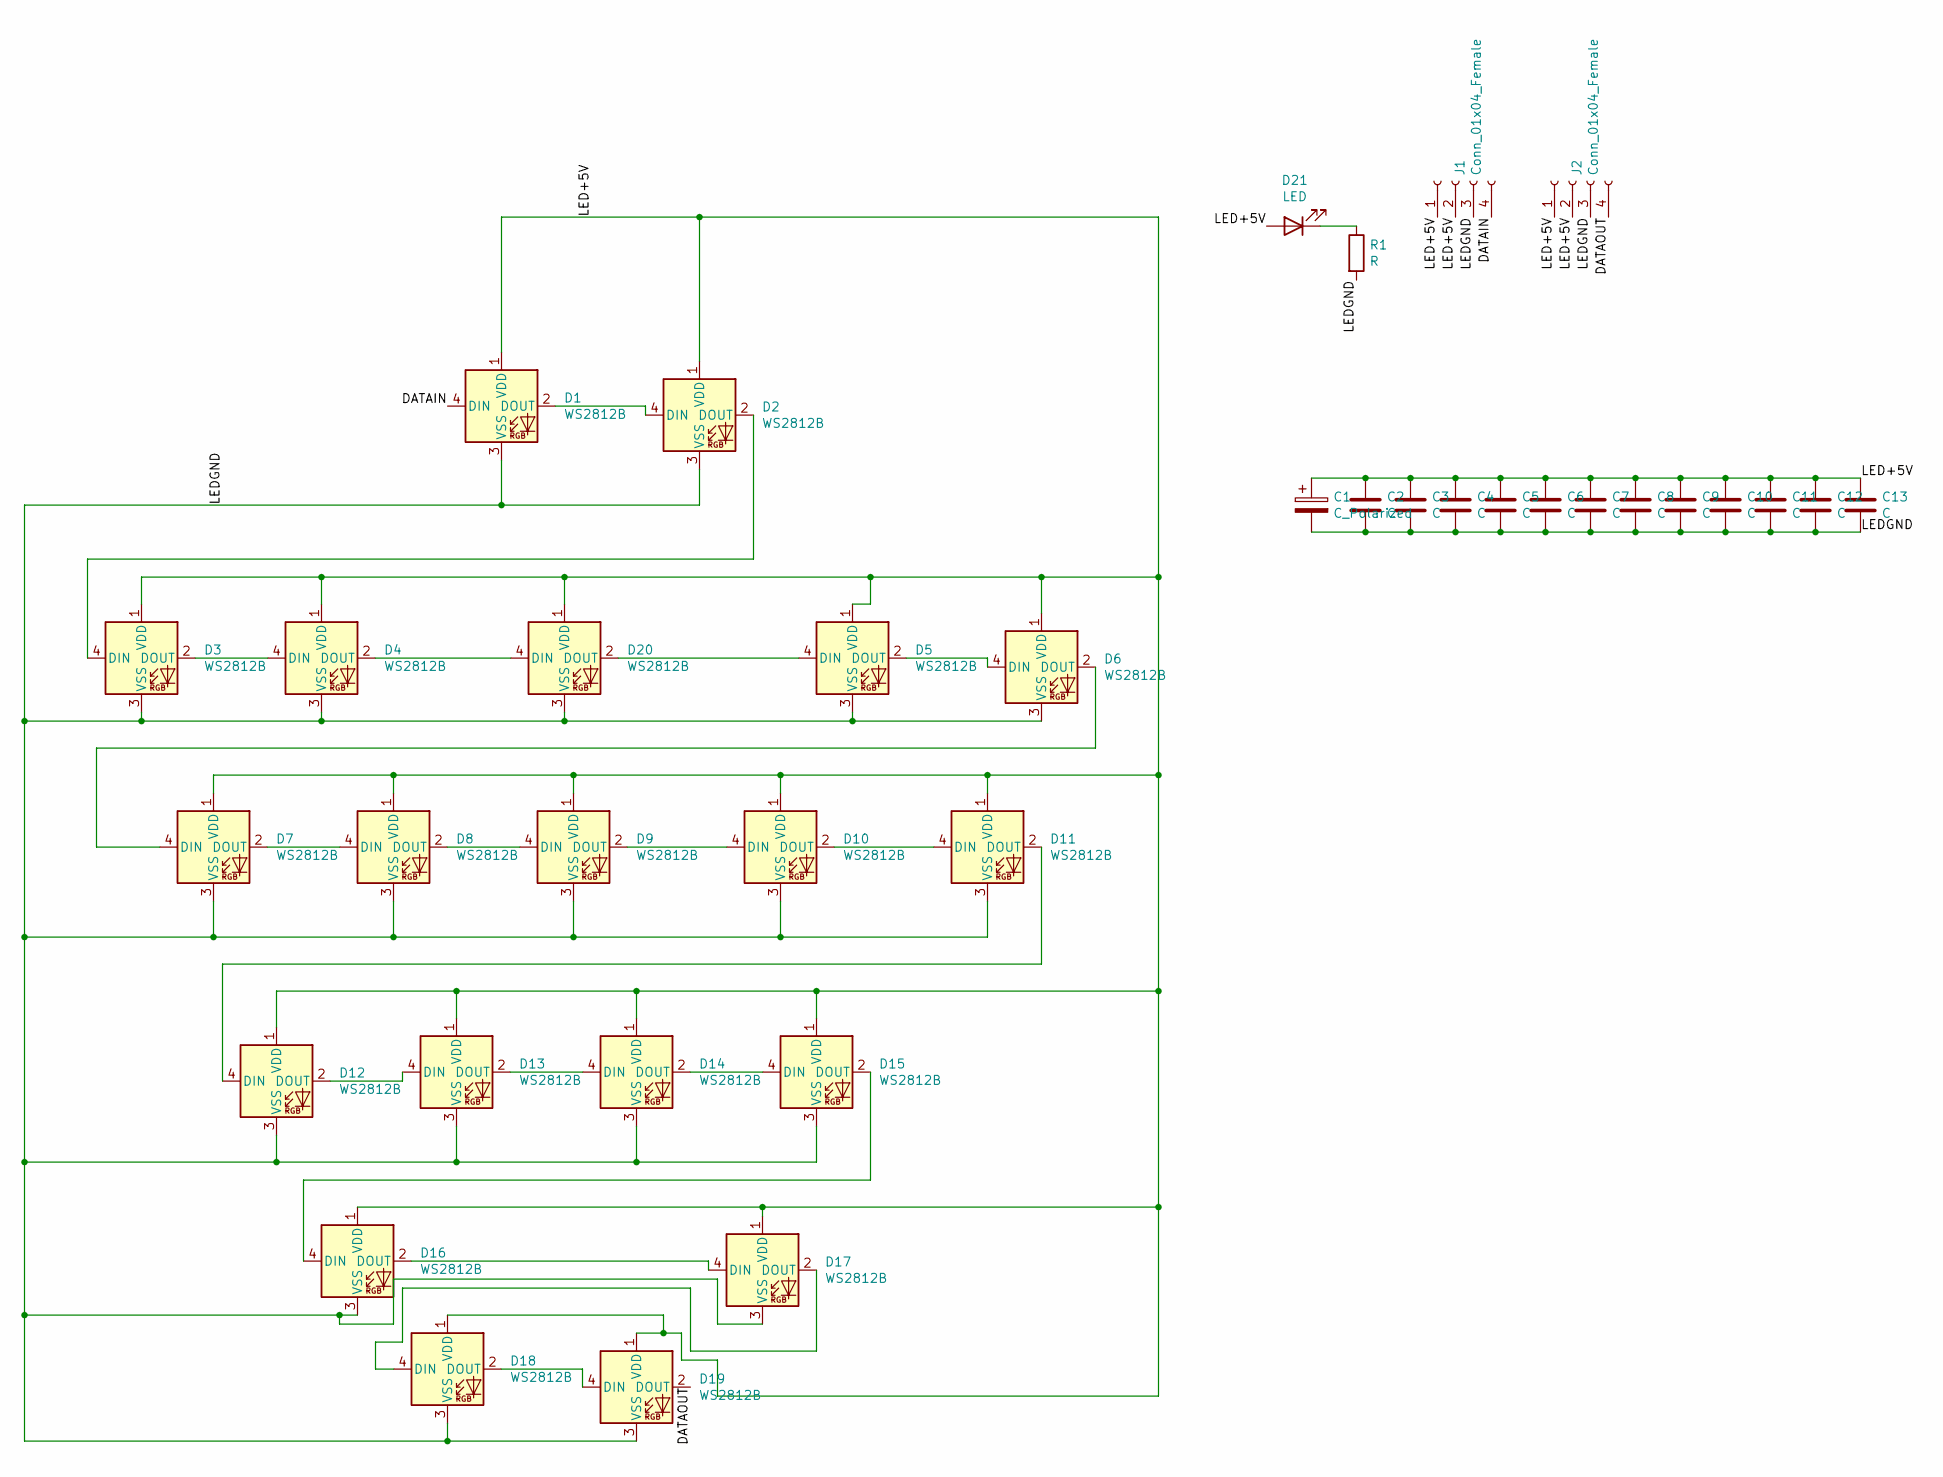
[picture p653: schematic APU Panel PCB V2.sch]

Parts:
C1: C_Polarized; CP_Elec_8x10
C2, C3, C4, C5, C6, C7, C8, C9, C10, C11, C12, C13: C; C_0603_1608Metric
D1, D2, D3, D4, D5, D6, D7, D8, D9, D10, D11, D12, D13, D14, D15, D16, D17, D18, D19, D20: WS2812B; LED_WS2812B_PLCC4_5.0x5.0mm_P3.2mm
D21: LED; LED_D3.0mm
J1, J2: Conn_01x04_Female; Molex_Mini-Fit_Jr_5566-04A_2x02_P4.20mm_Vertical
R1: R; R_0603_1608Metric

Connections:
DATAIN: D1.4 (DIN), J1.4
DATAOUT: D19.2 (DOUT), J2.4
LED+5V: C1.1, C2.1, C3.1, C4.1, C5.1, C6.1, C7.1, C8.1, C9.1, C10.1, C11.1, C12.1, C13.1, D1.1 (VDD), D2.1 (VDD), D3.1 (VDD), D4.1 (VDD), D5.1 (VDD), D6.1 (VDD), D7.1 (VDD), D8.1 (VDD), D9.1 (VDD), D10.1 (VDD), D11.1 (VDD), D12.1 (VDD), D13.1 (VDD), D14.1 (VDD), D15.1 (VDD), D16.1 (VDD), D17.1 (VDD), D18.1 (VDD), D19.1 (VDD), D20.1 (VDD), D21.2 (A), J1.1, J1.2, J2.1, J2.2
LEDGND: C1.2, C2.2, C3.2, C4.2, C5.2, C6.2, C7.2, C8.2, C9.2, C10.2, C11.2, C12.2, C13.2, D1.3 (VSS), D2.3 (VSS), D3.3 (VSS), D4.3 (VSS), D5.3 (VSS), D6.3 (VSS), D7.3 (VSS), D8.3 (VSS), D9.3 (VSS), D10.3 (VSS), D11.3 (VSS), D12.3 (VSS), D13.3 (VSS), D14.3 (VSS), D15.3 (VSS), D16.3 (VSS), D17.3 (VSS), D18.3 (VSS), D19.3 (VSS), D20.3 (VSS), J1.3, J2.3, R1.2
unnamed: D1.2 (DOUT), D2.4 (DIN)
unnamed: D2.2 (DOUT), D3.4 (DIN)
unnamed: D3.2 (DOUT), D4.4 (DIN)
unnamed: D5.2 (DOUT), D6.4 (DIN)
unnamed: D6.2 (DOUT), D7.4 (DIN)
unnamed: D7.2 (DOUT), D8.4 (DIN)
unnamed: D8.2 (DOUT), D9.4 (DIN)
unnamed: D10.2 (DOUT), D11.4 (DIN)
unnamed: D9.2 (DOUT), D10.4 (DIN)
unnamed: D11.2 (DOUT), D12.4 (DIN)
unnamed: D12.2 (DOUT), D13.4 (DIN)
unnamed: D13.2 (DOUT), D14.4 (DIN)
unnamed: D14.2 (DOUT), D15.4 (DIN)
unnamed: D15.2 (DOUT), D16.4 (DIN)
unnamed: D16.2 (DOUT), D17.4 (DIN)
unnamed: D17.2 (DOUT), D18.4 (DIN)
unnamed: D18.2 (DOUT), D19.4 (DIN)
unnamed: D5.4 (DIN), D20.2 (DOUT)
unnamed: D4.2 (DOUT), D20.4 (DIN)
unnamed: D21.1 (K), R1.1
