jrsteensen/OpenHornet/ECAD/PCBs/OH_Specific/Backlighting/COM_Panel_PCB_V2/COMM Panel PCB V2.sch

## KiCad design ECAD/PCBs/OH_Specific/Backlighting/COM_Panel_PCB_V2/COMM Panel PCB V2.sch (2022-09-23)

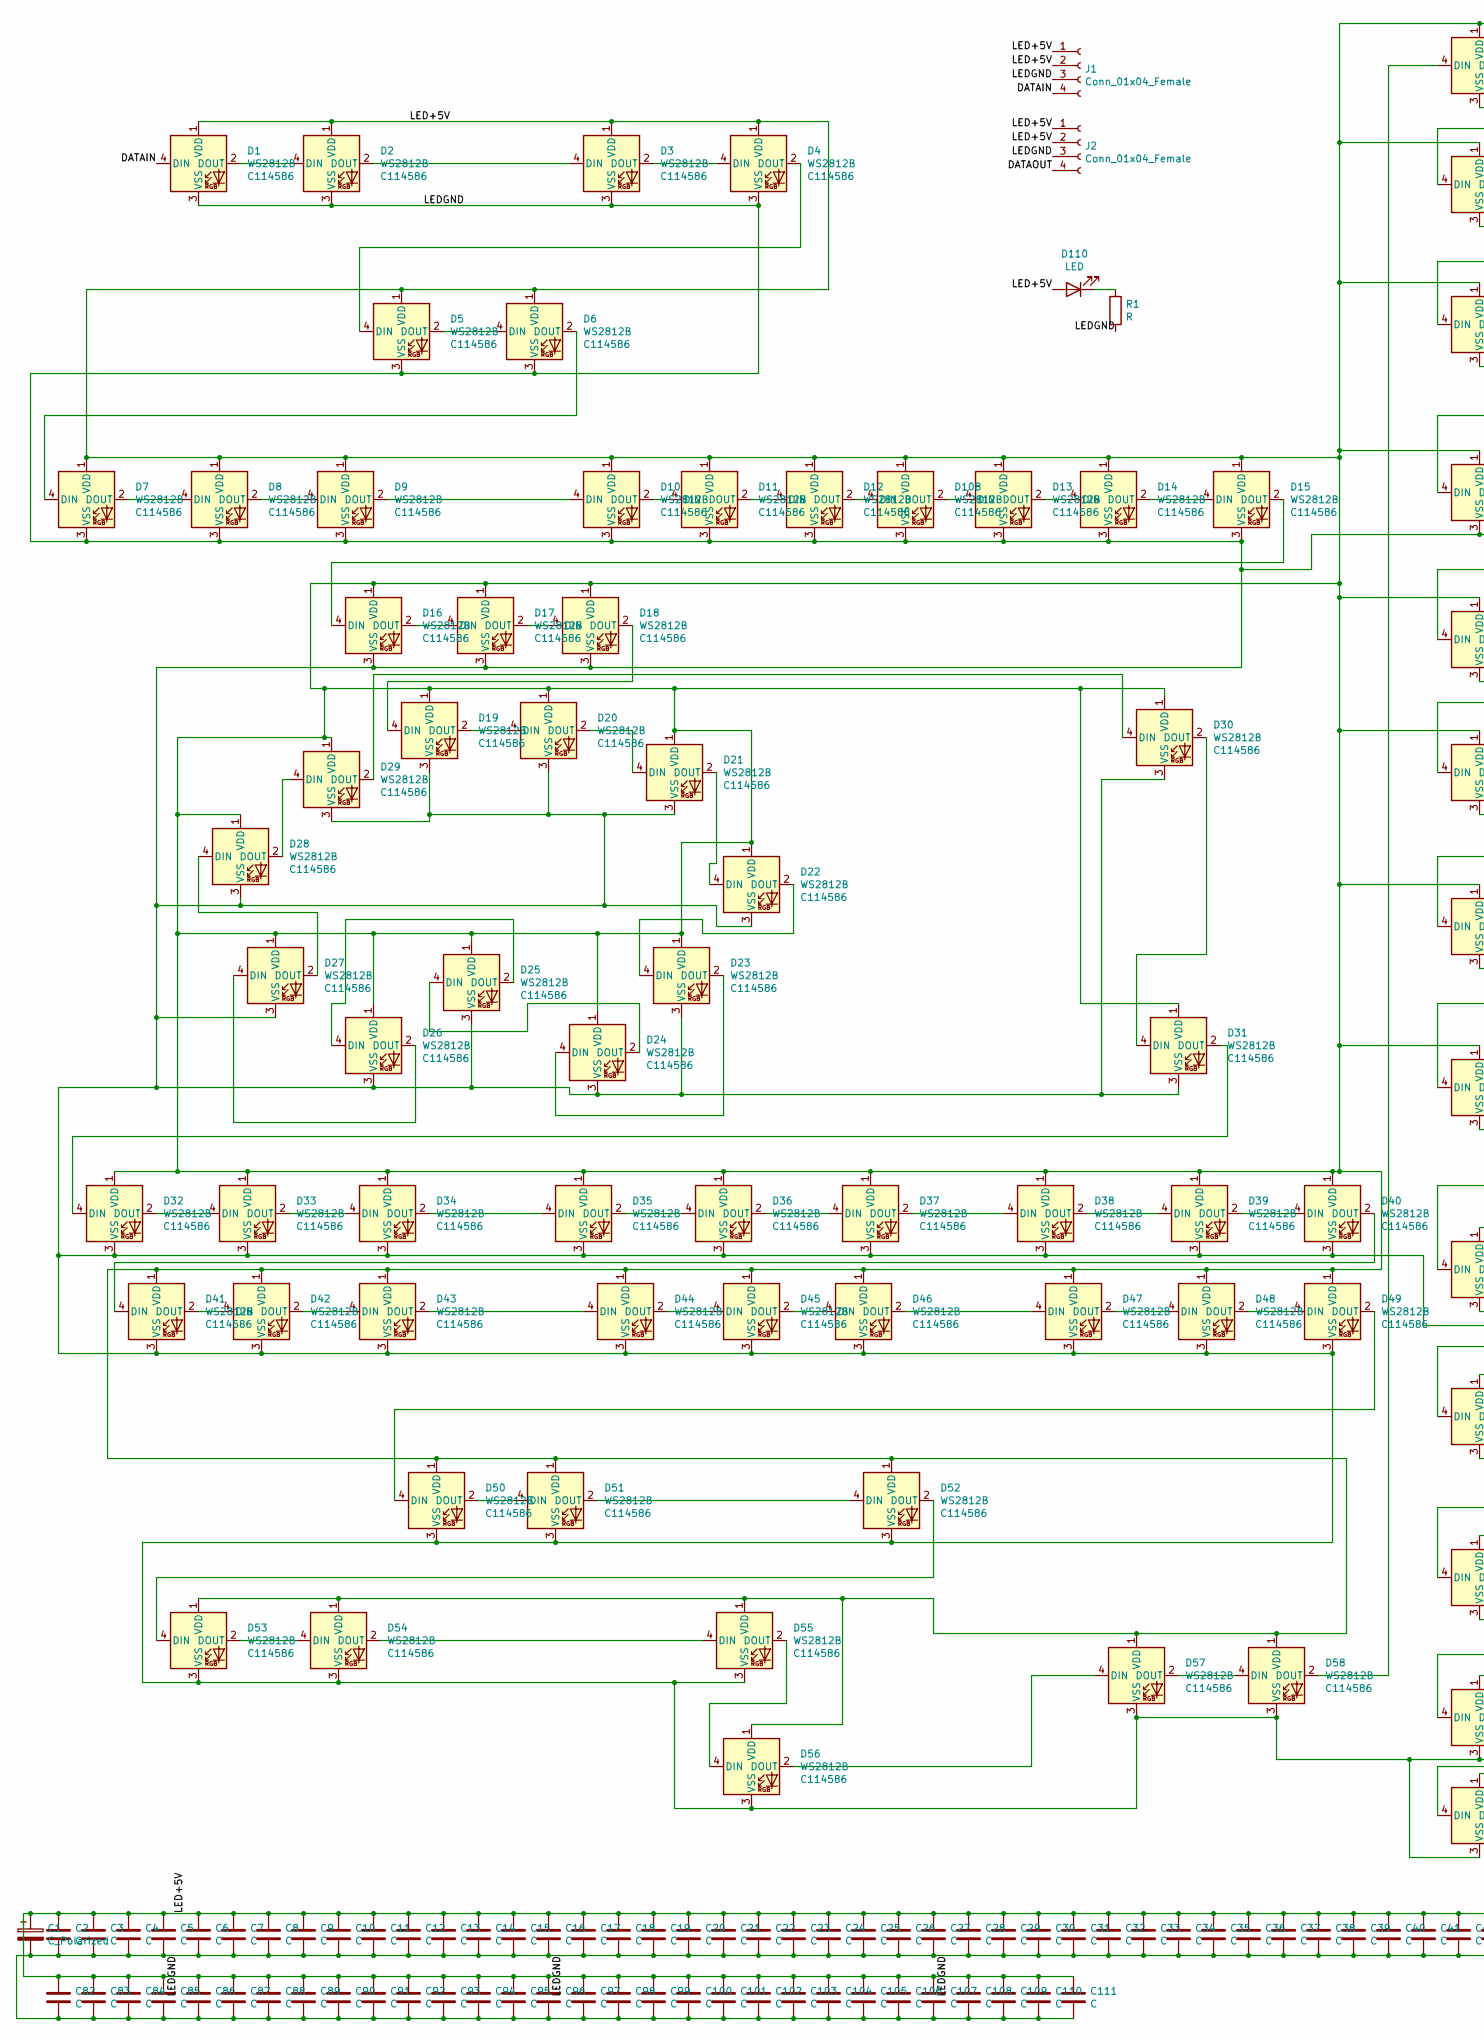
[picture p655: schematic COMM Panel PCB V2.sch, part in row 1, column 1]

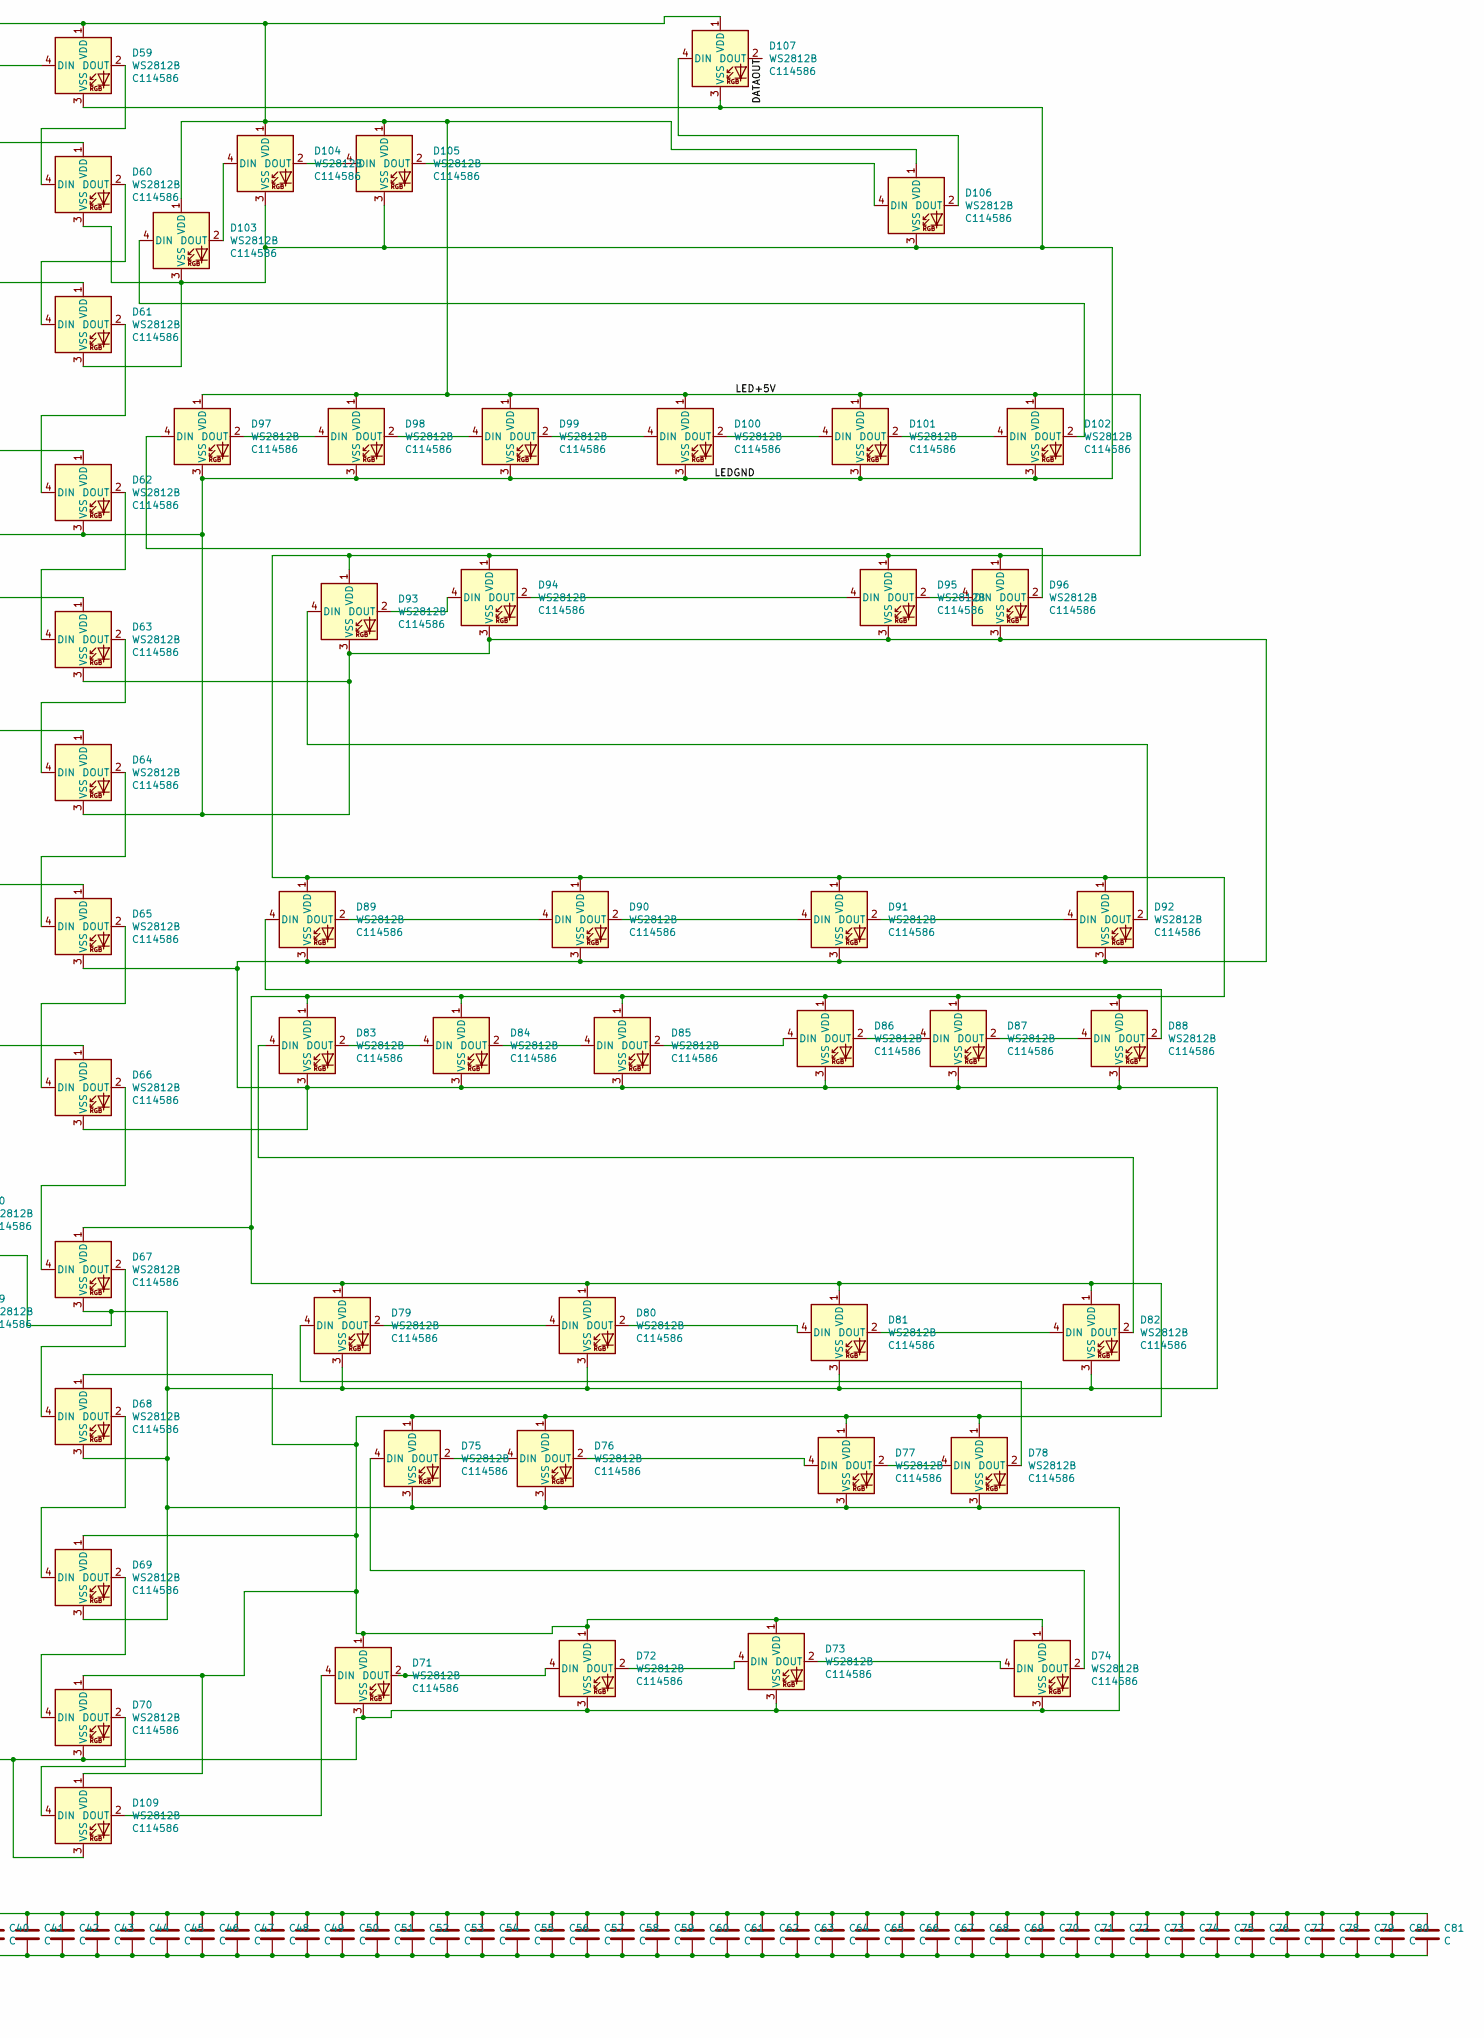
[picture p656: schematic COMM Panel PCB V2.sch, part in row 1, column 2]

Parts:
C1: C_Polarized; CP_Elec_8x10
C2, C3, C4, C5, C6, C7, C8, C9, C10, C11, C12, C13, C14, C15, C16, C17, C18, C19, C20, C21, C22, C23, C24, C25, C26, C27, C28, C29, C30, C31, C32, C33, C34, C35, C36, C37, C38, C39, C40, C41, C42, C43, C44, C45, C46, C47, C48, C49, C50, C51, C52, C53, C54, C55, C56, C57, C58, C59, C60, C61, C62, C63, C64, C65, C66, C67, C68, C69, C70, C71, C72, C73, C74, C75, C76, C77, C78, C79, C80, C81, C82, C83, C84, C85, C86, C87, C88, C89, C90, C91, C92, C93, C94, C95, C96, C97, C98, C99, C100, C101, C102, C103, C104, C105, C106, C107, C108, C109, C110, C111: C; C_0603_1608Metric
D1, D2, D3, D4, D5, D6, D7, D8, D9, D10, D11, D12, D13, D14, D15, D16, D17, D18, D19, D20, D21, D22, D23, D24, D25, D26, D27, D28, D29, D30, D31, D32, D33, D34, D35, D36, D37, D38, D39, D40, D41, D42, D43, D44, D45, D46, D47, D48, D49, D50, D51, D52, D53, D54, D55, D56, D57, D58, D59, D60, D61, D62, D63, D64, D65, D66, D67, D68, D69, D70, D71, D72, D73, D74, D75, D76, D77, D78, D79, D80, D81, D82, D83, D84, D85, D86, D87, D88, D89, D90, D91, D92, D93, D94, D95, D96, D97, D98, D99, D100, D101, D102, D103, D104, D105, D106, D107, D108, D109: WS2812B; LED_WS2812B_PLCC4_5.0x5.0mm_P3.2mm; LCSC Part Number C114586
D110: LED; LED_D3.0mm
J1, J2: Conn_01x04_Female; Molex_Mini-Fit_Jr_5566-04A_2x02_P4.20mm_Vertical
R1: R; R_0603_1608Metric

Connections:
DATAIN: D1.4 (DIN), J1.4
DATAOUT: D107.2 (DOUT), J2.4
LED+5V: C1.1, C2.1, C3.1, C4.1, C5.1, C6.1, C7.1, C8.1, C9.1, C10.1, C11.1, C12.1, C13.1, C14.1, C15.1, C16.1, C17.1, C18.1, C19.1, C20.1, C21.1, C22.1, C23.1, C24.1, C25.1, C26.1, C27.1, C28.1, C29.1, C30.1, C31.1, C32.1, C33.1, C34.1, C35.1, C36.1, C37.1, C38.1, C39.1, C40.1, C41.1, C42.1, C43.1, C44.1, C45.1, C46.1, C47.1, C48.1, C49.1, C50.1, C51.1, C52.1, C53.1, C54.1, C55.1, C56.1, C57.1, C58.1, C59.1, C60.1, C61.1, C62.1, C63.1, C64.1, C65.1, C66.1, C67.1, C68.1, C69.1, C70.1, C71.1, C72.1, C73.1, C74.1, C75.1, C76.1, C77.1, C78.1, C79.1, C80.1, C81.1, C82.1, C83.1, C84.1, C85.1, C86.1, C87.1, C88.1, C89.1, C90.1, C91.1, C92.1, C93.1, C94.1, C95.1, C96.1, C97.1, C98.1, C99.1, C100.1, C101.1, C102.1, C103.1, C104.1, C105.1, C106.1, C107.1, C108.1, C109.1, C110.1, C111.1, D1.1 (VDD), D2.1 (VDD), D3.1 (VDD), D4.1 (VDD), D5.1 (VDD), D6.1 (VDD), D7.1 (VDD), D8.1 (VDD), D9.1 (VDD), D10.1 (VDD), D11.1 (VDD), D12.1 (VDD), D13.1 (VDD), D14.1 (VDD), D15.1 (VDD), D16.1 (VDD), D17.1 (VDD), D18.1 (VDD), D19.1 (VDD), D20.1 (VDD), D21.1 (VDD), D22.1 (VDD), D23.1 (VDD), D24.1 (VDD), D25.1 (VDD), D26.1 (VDD), D27.1 (VDD), D28.1 (VDD), D29.1 (VDD), D30.1 (VDD), D31.1 (VDD), D32.1 (VDD), D33.1 (VDD), D34.1 (VDD), D35.1 (VDD), D36.1 (VDD), D37.1 (VDD), D38.1 (VDD), D39.1 (VDD), D40.1 (VDD), D41.1 (VDD), D42.1 (VDD), D43.1 (VDD), D44.1 (VDD), D45.1 (VDD), D46.1 (VDD), D47.1 (VDD), D48.1 (VDD), D49.1 (VDD), D50.1 (VDD), D51.1 (VDD), D52.1 (VDD), D53.1 (VDD), D54.1 (VDD), D55.1 (VDD), D56.1 (VDD), D57.1 (VDD), D58.1 (VDD), D59.1 (VDD), D60.1 (VDD), D61.1 (VDD), D62.1 (VDD), D63.1 (VDD), D64.1 (VDD), D65.1 (VDD), D66.1 (VDD), D67.1 (VDD), D68.1 (VDD), D69.1 (VDD), D70.1 (VDD), D71.1 (VDD), D72.1 (VDD), D73.1 (VDD), D74.1 (VDD), D75.1 (VDD), D76.1 (VDD), D77.1 (VDD), D78.1 (VDD), D79.1 (VDD), D80.1 (VDD), D81.1 (VDD), D82.1 (VDD), D83.1 (VDD), D84.1 (VDD), D85.1 (VDD), D86.1 (VDD), D87.1 (VDD), D88.1 (VDD), D89.1 (VDD), D90.1 (VDD), D91.1 (VDD), D92.1 (VDD), D93.1 (VDD), D94.1 (VDD), D95.1 (VDD), D96.1 (VDD), D97.1 (VDD), D98.1 (VDD), D99.1 (VDD), D100.1 (VDD), D101.1 (VDD), D102.1 (VDD), D103.1 (VDD), D104.1 (VDD), D105.1 (VDD), D106.1 (VDD), D107.1 (VDD), D108.1 (VDD), D109.1 (VDD), D110.2 (A), J1.1, J1.2, J2.1, J2.2
LEDGND: C1.2, C2.2, C3.2, C4.2, C5.2, C6.2, C7.2, C8.2, C9.2, C10.2, C11.2, C12.2, C13.2, C14.2, C15.2, C16.2, C17.2, C18.2, C19.2, C20.2, C21.2, C22.2, C23.2, C24.2, C25.2, C26.2, C27.2, C28.2, C29.2, C30.2, C31.2, C32.2, C33.2, C34.2, C35.2, C36.2, C37.2, C38.2, C39.2, C40.2, C41.2, C42.2, C43.2, C44.2, C45.2, C46.2, C47.2, C48.2, C49.2, C50.2, C51.2, C52.2, C53.2, C54.2, C55.2, C56.2, C57.2, C58.2, C59.2, C60.2, C61.2, C62.2, C63.2, C64.2, C65.2, C66.2, C67.2, C68.2, C69.2, C70.2, C71.2, C72.2, C73.2, C74.2, C75.2, C76.2, C77.2, C78.2, C79.2, C80.2, C81.2, C82.2, C83.2, C84.2, C85.2, C86.2, C87.2, C88.2, C89.2, C90.2, C91.2, C92.2, C93.2, C94.2, C95.2, C96.2, C97.2, C98.2, C99.2, C100.2, C101.2, C102.2, C103.2, C104.2, C105.2, C106.2, C107.2, C108.2, C109.2, C110.2, C111.2, D1.3 (VSS), D2.3 (VSS), D3.3 (VSS), D4.3 (VSS), D5.3 (VSS), D6.3 (VSS), D7.3 (VSS), D8.3 (VSS), D9.3 (VSS), D10.3 (VSS), D11.3 (VSS), D12.3 (VSS), D13.3 (VSS), D14.3 (VSS), D15.3 (VSS), D16.3 (VSS), D17.3 (VSS), D18.3 (VSS), D19.3 (VSS), D20.3 (VSS), D21.3 (VSS), D22.3 (VSS), D23.3 (VSS), D24.3 (VSS), D25.3 (VSS), D26.3 (VSS), D27.3 (VSS), D28.3 (VSS), D29.3 (VSS), D30.3 (VSS), D31.3 (VSS), D32.3 (VSS), D33.3 (VSS), D34.3 (VSS), D35.3 (VSS), D36.3 (VSS), D37.3 (VSS), D38.3 (VSS), D39.3 (VSS), D40.3 (VSS), D41.3 (VSS), D42.3 (VSS), D43.3 (VSS), D44.3 (VSS), D45.3 (VSS), D46.3 (VSS), D47.3 (VSS), D48.3 (VSS), D49.3 (VSS), D50.3 (VSS), D51.3 (VSS), D52.3 (VSS), D53.3 (VSS), D54.3 (VSS), D55.3 (VSS), D56.3 (VSS), D57.3 (VSS), D58.3 (VSS), D59.3 (VSS), D60.3 (VSS), D61.3 (VSS), D62.3 (VSS), D63.3 (VSS), D64.3 (VSS), D65.3 (VSS), D66.3 (VSS), D67.3 (VSS), D68.3 (VSS), D69.3 (VSS), D70.3 (VSS), D71.3 (VSS), D72.3 (VSS), D73.3 (VSS), D74.3 (VSS), D75.3 (VSS), D76.3 (VSS), D77.3 (VSS), D78.3 (VSS), D79.3 (VSS), D80.3 (VSS), D81.3 (VSS), D82.3 (VSS), D83.3 (VSS), D84.3 (VSS), D85.3 (VSS), D86.3 (VSS), D87.3 (VSS), D88.3 (VSS), D89.3 (VSS), D90.3 (VSS), D91.3 (VSS), D92.3 (VSS), D93.3 (VSS), D94.3 (VSS), D95.3 (VSS), D96.3 (VSS), D97.3 (VSS), D98.3 (VSS), D99.3 (VSS), D100.3 (VSS), D101.3 (VSS), D102.3 (VSS), D103.3 (VSS), D104.3 (VSS), D105.3 (VSS), D106.3 (VSS), D107.3 (VSS), D108.3 (VSS), D109.3 (VSS), J1.3, J2.3, R1.2
unnamed: D1.2 (DOUT), D2.4 (DIN)
unnamed: D2.2 (DOUT), D3.4 (DIN)
unnamed: D3.2 (DOUT), D4.4 (DIN)
unnamed: D4.2 (DOUT), D5.4 (DIN)
unnamed: D5.2 (DOUT), D6.4 (DIN)
unnamed: D6.2 (DOUT), D7.4 (DIN)
unnamed: D7.2 (DOUT), D8.4 (DIN)
unnamed: D8.2 (DOUT), D9.4 (DIN)
unnamed: D10.2 (DOUT), D11.4 (DIN)
unnamed: D9.2 (DOUT), D10.4 (DIN)
unnamed: D11.2 (DOUT), D12.4 (DIN)
unnamed: D13.2 (DOUT), D14.4 (DIN)
unnamed: D14.2 (DOUT), D15.4 (DIN)
unnamed: D15.2 (DOUT), D16.4 (DIN)
unnamed: D16.2 (DOUT), D17.4 (DIN)
unnamed: D17.2 (DOUT), D18.4 (DIN)
unnamed: D18.2 (DOUT), D19.4 (DIN)
unnamed: D19.2 (DOUT), D20.4 (DIN)
unnamed: D20.2 (DOUT), D21.4 (DIN)
unnamed: D21.2 (DOUT), D22.4 (DIN)
unnamed: D22.2 (DOUT), D23.4 (DIN)
unnamed: D23.2 (DOUT), D24.4 (DIN)
unnamed: D24.2 (DOUT), D25.4 (DIN)
unnamed: D25.2 (DOUT), D26.4 (DIN)
unnamed: D26.2 (DOUT), D27.4 (DIN)
unnamed: D27.2 (DOUT), D28.4 (DIN)
unnamed: D28.2 (DOUT), D29.4 (DIN)
unnamed: D29.2 (DOUT), D30.4 (DIN)
unnamed: D30.2 (DOUT), D31.4 (DIN)
unnamed: D31.2 (DOUT), D32.4 (DIN)
unnamed: D32.2 (DOUT), D33.4 (DIN)
unnamed: D33.2 (DOUT), D34.4 (DIN)
unnamed: D34.2 (DOUT), D35.4 (DIN)
unnamed: D35.2 (DOUT), D36.4 (DIN)
unnamed: D36.2 (DOUT), D37.4 (DIN)
unnamed: D37.2 (DOUT), D38.4 (DIN)
unnamed: D38.2 (DOUT), D39.4 (DIN)
unnamed: D39.2 (DOUT), D40.4 (DIN)
unnamed: D40.2 (DOUT), D41.4 (DIN)
unnamed: D41.2 (DOUT), D42.4 (DIN)
unnamed: D42.2 (DOUT), D43.4 (DIN)
unnamed: D43.2 (DOUT), D44.4 (DIN)
unnamed: D44.2 (DOUT), D45.4 (DIN)
unnamed: D45.2 (DOUT), D46.4 (DIN)
unnamed: D46.2 (DOUT), D47.4 (DIN)
unnamed: D47.2 (DOUT), D48.4 (DIN)
unnamed: D48.2 (DOUT), D49.4 (DIN)
unnamed: D49.2 (DOUT), D50.4 (DIN)
unnamed: D50.2 (DOUT), D51.4 (DIN)
unnamed: D51.2 (DOUT), D52.4 (DIN)
unnamed: D52.2 (DOUT), D53.4 (DIN)
unnamed: D53.2 (DOUT), D54.4 (DIN)
unnamed: D54.2 (DOUT), D55.4 (DIN)
unnamed: D55.2 (DOUT), D56.4 (DIN)
unnamed: D56.2 (DOUT), D57.4 (DIN)
unnamed: D57.2 (DOUT), D58.4 (DIN)
unnamed: D58.2 (DOUT), D59.4 (DIN)
unnamed: D59.2 (DOUT), D60.4 (DIN)
unnamed: D60.2 (DOUT), D61.4 (DIN)
unnamed: D61.2 (DOUT), D62.4 (DIN)
unnamed: D62.2 (DOUT), D63.4 (DIN)
unnamed: D63.2 (DOUT), D64.4 (DIN)
unnamed: D64.2 (DOUT), D65.4 (DIN)
unnamed: D65.2 (DOUT), D66.4 (DIN)
unnamed: D66.2 (DOUT), D67.4 (DIN)
unnamed: D67.2 (DOUT), D68.4 (DIN)
unnamed: D68.2 (DOUT), D69.4 (DIN)
unnamed: D69.2 (DOUT), D70.4 (DIN)
unnamed: D71.2 (DOUT), D72.4 (DIN)
unnamed: D72.2 (DOUT), D73.4 (DIN)
unnamed: D73.2 (DOUT), D74.4 (DIN)
unnamed: D74.2 (DOUT), D75.4 (DIN)
unnamed: D75.2 (DOUT), D76.4 (DIN)
unnamed: D76.2 (DOUT), D77.4 (DIN)
unnamed: D77.2 (DOUT), D78.4 (DIN)
unnamed: D78.2 (DOUT), D79.4 (DIN)
unnamed: D79.2 (DOUT), D80.4 (DIN)
unnamed: D80.2 (DOUT), D81.4 (DIN)
unnamed: D81.2 (DOUT), D82.4 (DIN)
unnamed: D82.2 (DOUT), D83.4 (DIN)
unnamed: D83.2 (DOUT), D84.4 (DIN)
unnamed: D84.2 (DOUT), D85.4 (DIN)
unnamed: D85.2 (DOUT), D86.4 (DIN)
unnamed: D86.2 (DOUT), D87.4 (DIN)
unnamed: D87.2 (DOUT), D88.4 (DIN)
unnamed: D88.2 (DOUT), D89.4 (DIN)
unnamed: D89.2 (DOUT), D90.4 (DIN)
unnamed: D90.2 (DOUT), D91.4 (DIN)
unnamed: D91.2 (DOUT), D92.4 (DIN)
unnamed: D92.2 (DOUT), D93.4 (DIN)
unnamed: D93.2 (DOUT), D94.4 (DIN)
unnamed: D94.2 (DOUT), D95.4 (DIN)
unnamed: D95.2 (DOUT), D96.4 (DIN)
unnamed: D96.2 (DOUT), D97.4 (DIN)
unnamed: D97.2 (DOUT), D98.4 (DIN)
unnamed: D98.2 (DOUT), D99.4 (DIN)
unnamed: D100.2 (DOUT), D101.4 (DIN)
unnamed: D99.2 (DOUT), D100.4 (DIN)
unnamed: D101.2 (DOUT), D102.4 (DIN)
unnamed: D102.2 (DOUT), D103.4 (DIN)
unnamed: D103.2 (DOUT), D104.4 (DIN)
unnamed: D104.2 (DOUT), D105.4 (DIN)
unnamed: D105.2 (DOUT), D106.4 (DIN)
unnamed: D106.2 (DOUT), D107.4 (DIN)
unnamed: D13.4 (DIN), D108.2 (DOUT)
unnamed: D12.2 (DOUT), D108.4 (DIN)
unnamed: D71.4 (DIN), D109.2 (DOUT)
unnamed: D70.2 (DOUT), D109.4 (DIN)
unnamed: D110.1 (K), R1.1
