jrsteensen/OpenHornet/ECAD/PCBs/OH_Specific/Backlighting/ECM_JETT_PCB_V1/DISP-EMC Panel PCB V1.sch

## KiCad design ECAD/PCBs/OH_Specific/Backlighting/ECM_JETT_PCB_V1/DISP-EMC Panel PCB V1.sch (2022-09-23)

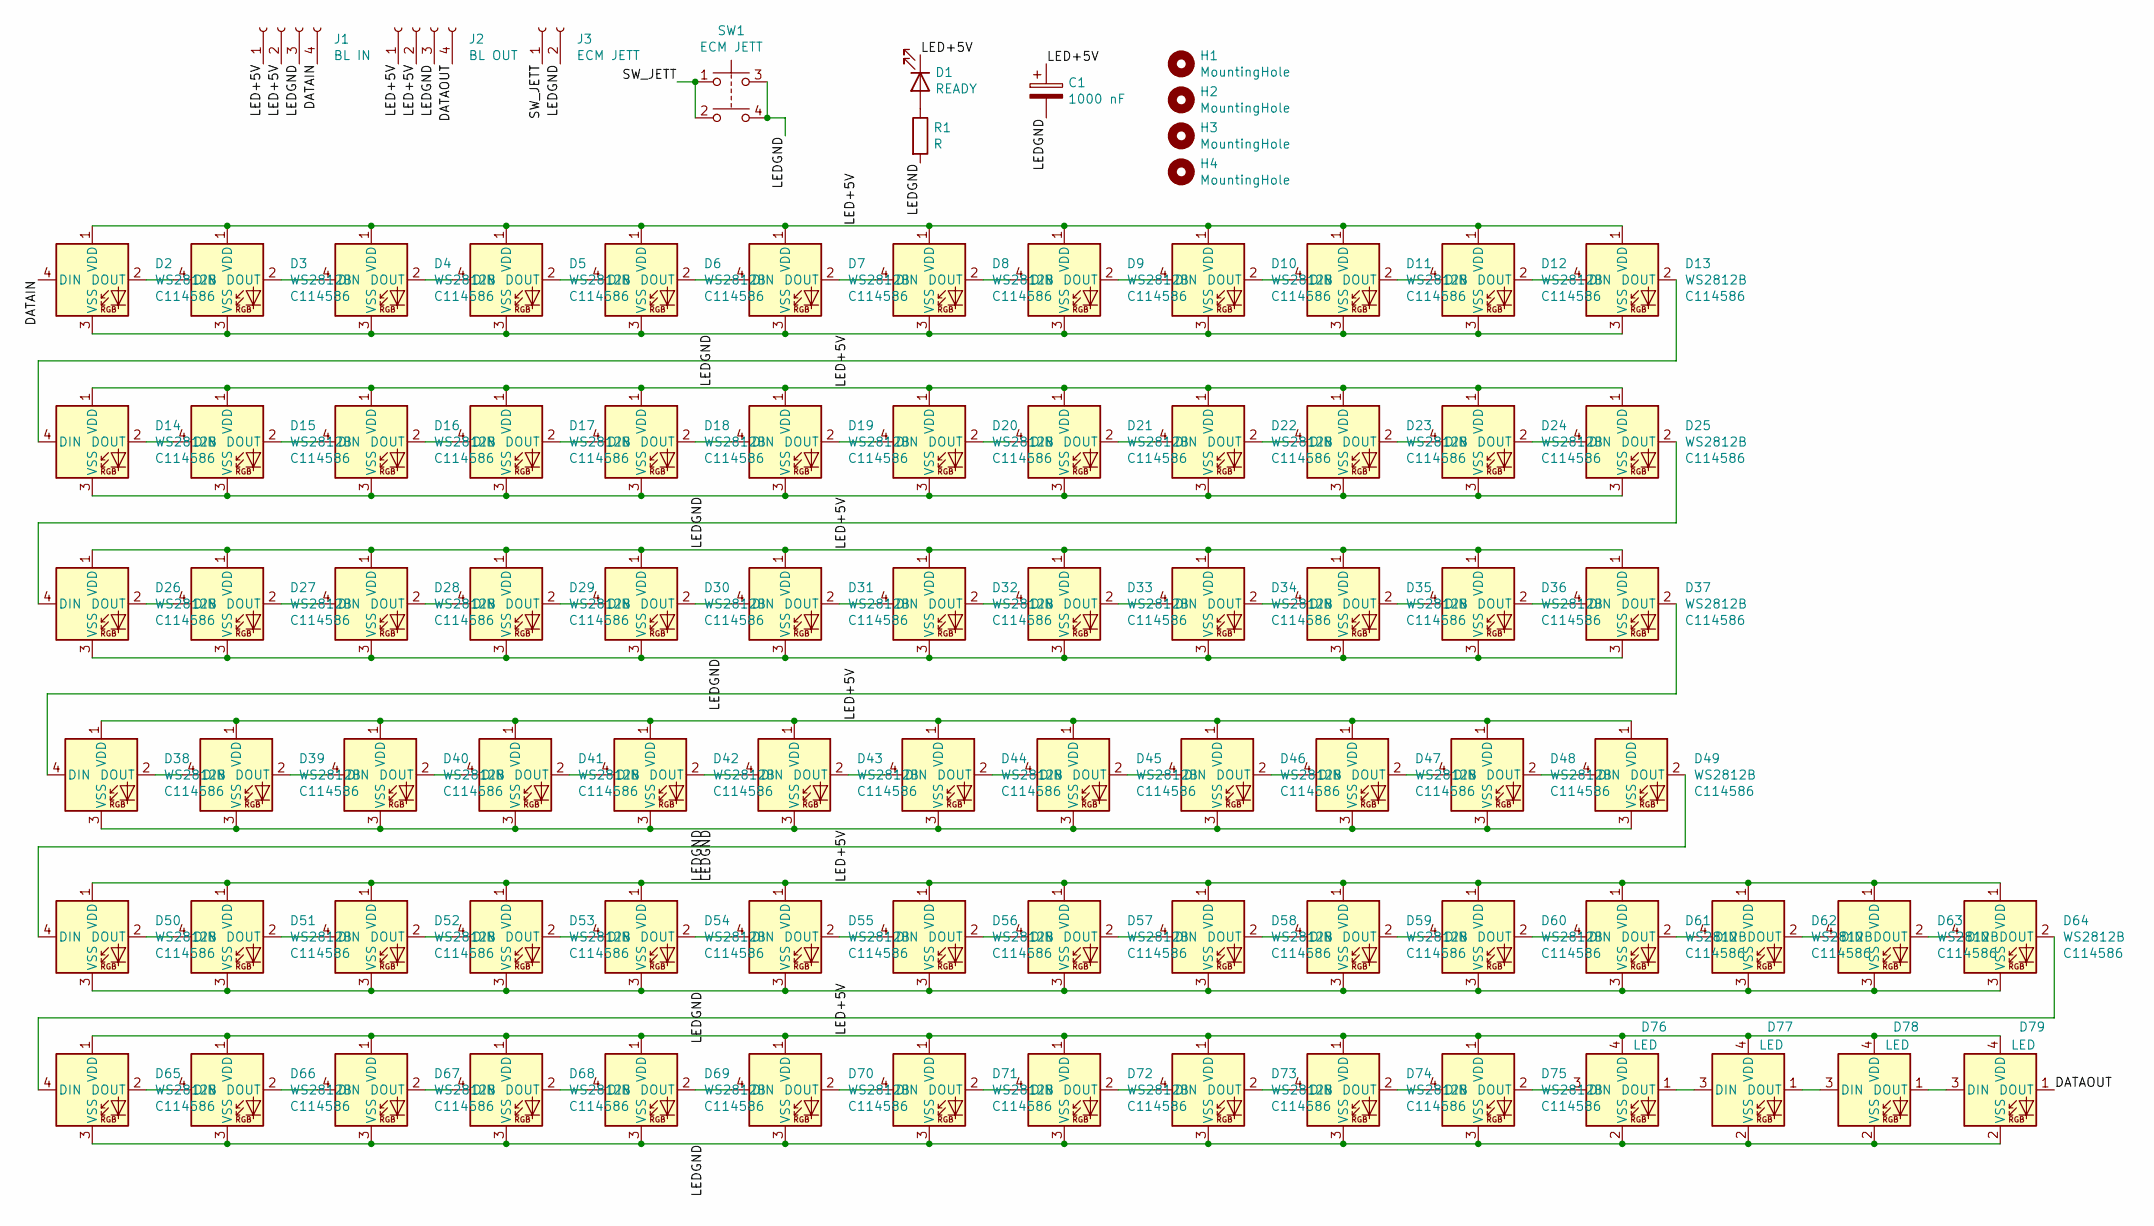
[picture p659: schematic DISP-EMC Panel PCB V1.sch]

Parts:
C1: 1000 nF; CP_Elec_8x10
D1: READY; LED_D3.0mm
D2, D3, D4, D5, D6, D7, D8, D9, D10, D11, D12, D13, D14, D15, D16, D17, D18, D19, D20, D21, D22, D23, D24, D25, D26, D27, D28, D29, D30, D31, D32, D33, D34, D35, D36, D37, D38, D39, D40, D41, D42, D43, D44, D45, D46, D47, D48, D49, D50, D51, D52, D53, D54, D55, D56, D57, D58, D59, D60, D61, D62, D63, D64, D65, D66, D67, D68, D69, D70, D71, D72, D73, D74, D75: WS2812B; LED_WS2812B_PLCC4_5.0x5.0mm_P3.2mm; LCSC Part Number C114586
D76, D77, D78, D79: LED; WS2812-2020; LCSC C965555
H1, H2, H3, H4: MountingHole; MountingHole_4.5mm_Pad
J1: BL IN; Molex_Mini-Fit_Jr_5566-04A_2x02_P4.20mm_Vertical
J2: BL OUT; Molex_Mini-Fit_Jr_5566-04A_2x02_P4.20mm_Vertical
J3: ECM JETT; Molex_KK-254_AE-6410-02A_1x02_P2.54mm_Vertical
R1: R; R_0603_1608Metric; LCSC C23138
SW1: ECM JETT; SW_TH_Tactile_Omron_B3F-10xx

Connections:
DATAIN: D2.4 (DIN), J1.4
DATAOUT: D79.1 (DOUT), J2.4
LED+5V: C1.1, D1.1 (K), D2.1 (VDD), D3.1 (VDD), D4.1 (VDD), D5.1 (VDD), D6.1 (VDD), D7.1 (VDD), D8.1 (VDD), D9.1 (VDD), D10.1 (VDD), D11.1 (VDD), D12.1 (VDD), D13.1 (VDD), D14.1 (VDD), D15.1 (VDD), D16.1 (VDD), D17.1 (VDD), D18.1 (VDD), D19.1 (VDD), D20.1 (VDD), D21.1 (VDD), D22.1 (VDD), D23.1 (VDD), D24.1 (VDD), D25.1 (VDD), D26.1 (VDD), D27.1 (VDD), D28.1 (VDD), D29.1 (VDD), D30.1 (VDD), D31.1 (VDD), D32.1 (VDD), D33.1 (VDD), D34.1 (VDD), D35.1 (VDD), D36.1 (VDD), D37.1 (VDD), D38.1 (VDD), D39.1 (VDD), D40.1 (VDD), D41.1 (VDD), D42.1 (VDD), D43.1 (VDD), D44.1 (VDD), D45.1 (VDD), D46.1 (VDD), D47.1 (VDD), D48.1 (VDD), D49.1 (VDD), D50.1 (VDD), D51.1 (VDD), D52.1 (VDD), D53.1 (VDD), D54.1 (VDD), D55.1 (VDD), D56.1 (VDD), D57.1 (VDD), D58.1 (VDD), D59.1 (VDD), D60.1 (VDD), D61.1 (VDD), D62.1 (VDD), D63.1 (VDD), D64.1 (VDD), D65.1 (VDD), D66.1 (VDD), D67.1 (VDD), D68.1 (VDD), D69.1 (VDD), D70.1 (VDD), D71.1 (VDD), D72.1 (VDD), D73.1 (VDD), D74.1 (VDD), D75.1 (VDD), D76.4 (VDD), D77.4 (VDD), D78.4 (VDD), D79.4 (VDD), J1.1, J1.2, J2.1, J2.2
LEDGND: C1.2, D2.3 (VSS), D3.3 (VSS), D4.3 (VSS), D5.3 (VSS), D6.3 (VSS), D7.3 (VSS), D8.3 (VSS), D9.3 (VSS), D10.3 (VSS), D11.3 (VSS), D12.3 (VSS), D13.3 (VSS), D14.3 (VSS), D15.3 (VSS), D16.3 (VSS), D17.3 (VSS), D18.3 (VSS), D19.3 (VSS), D20.3 (VSS), D21.3 (VSS), D22.3 (VSS), D23.3 (VSS), D24.3 (VSS), D25.3 (VSS), D26.3 (VSS), D27.3 (VSS), D28.3 (VSS), D29.3 (VSS), D30.3 (VSS), D31.3 (VSS), D32.3 (VSS), D33.3 (VSS), D34.3 (VSS), D35.3 (VSS), D36.3 (VSS), D37.3 (VSS), D38.3 (VSS), D39.3 (VSS), D40.3 (VSS), D41.3 (VSS), D42.3 (VSS), D43.3 (VSS), D44.3 (VSS), D45.3 (VSS), D46.3 (VSS), D47.3 (VSS), D48.3 (VSS), D49.3 (VSS), D50.3 (VSS), D51.3 (VSS), D52.3 (VSS), D53.3 (VSS), D54.3 (VSS), D55.3 (VSS), D56.3 (VSS), D57.3 (VSS), D58.3 (VSS), D59.3 (VSS), D60.3 (VSS), D61.3 (VSS), D62.3 (VSS), D63.3 (VSS), D64.3 (VSS), D65.3 (VSS), D66.3 (VSS), D67.3 (VSS), D68.3 (VSS), D69.3 (VSS), D70.3 (VSS), D71.3 (VSS), D72.3 (VSS), D73.3 (VSS), D74.3 (VSS), D75.3 (VSS), D76.2 (VSS), D77.2 (VSS), D78.2 (VSS), D79.2 (VSS), J1.3, J2.3, J3.2, R1.2, SW1.3, SW1.4
unnamed: D1.2 (A), R1.1
unnamed: D2.2 (DOUT), D3.4 (DIN)
unnamed: D3.2 (DOUT), D4.4 (DIN)
unnamed: D4.2 (DOUT), D5.4 (DIN)
unnamed: D5.2 (DOUT), D6.4 (DIN)
unnamed: D6.2 (DOUT), D7.4 (DIN)
unnamed: D7.2 (DOUT), D8.4 (DIN)
unnamed: D8.2 (DOUT), D9.4 (DIN)
unnamed: D10.2 (DOUT), D11.4 (DIN)
unnamed: D9.2 (DOUT), D10.4 (DIN)
unnamed: D11.2 (DOUT), D12.4 (DIN)
unnamed: D12.2 (DOUT), D13.4 (DIN)
unnamed: D13.2 (DOUT), D14.4 (DIN)
unnamed: D14.2 (DOUT), D15.4 (DIN)
unnamed: D15.2 (DOUT), D16.4 (DIN)
unnamed: D16.2 (DOUT), D17.4 (DIN)
unnamed: D17.2 (DOUT), D18.4 (DIN)
unnamed: D18.2 (DOUT), D19.4 (DIN)
unnamed: D19.2 (DOUT), D20.4 (DIN)
unnamed: D20.2 (DOUT), D21.4 (DIN)
unnamed: D21.2 (DOUT), D22.4 (DIN)
unnamed: D22.2 (DOUT), D23.4 (DIN)
unnamed: D23.2 (DOUT), D24.4 (DIN)
unnamed: D24.2 (DOUT), D25.4 (DIN)
unnamed: D25.2 (DOUT), D26.4 (DIN)
unnamed: D26.2 (DOUT), D27.4 (DIN)
unnamed: D27.2 (DOUT), D28.4 (DIN)
unnamed: D28.2 (DOUT), D29.4 (DIN)
unnamed: D29.2 (DOUT), D30.4 (DIN)
unnamed: D30.2 (DOUT), D31.4 (DIN)
unnamed: D31.2 (DOUT), D32.4 (DIN)
unnamed: D32.2 (DOUT), D33.4 (DIN)
unnamed: D33.2 (DOUT), D34.4 (DIN)
unnamed: D34.2 (DOUT), D35.4 (DIN)
unnamed: D35.2 (DOUT), D36.4 (DIN)
unnamed: D36.2 (DOUT), D37.4 (DIN)
unnamed: D37.2 (DOUT), D38.4 (DIN)
unnamed: D38.2 (DOUT), D39.4 (DIN)
unnamed: D39.2 (DOUT), D40.4 (DIN)
unnamed: D40.2 (DOUT), D41.4 (DIN)
unnamed: D41.2 (DOUT), D42.4 (DIN)
unnamed: D42.2 (DOUT), D43.4 (DIN)
unnamed: D43.2 (DOUT), D44.4 (DIN)
unnamed: D44.2 (DOUT), D45.4 (DIN)
unnamed: D45.2 (DOUT), D46.4 (DIN)
unnamed: D46.2 (DOUT), D47.4 (DIN)
unnamed: D47.2 (DOUT), D48.4 (DIN)
unnamed: D48.2 (DOUT), D49.4 (DIN)
unnamed: D49.2 (DOUT), D50.4 (DIN)
unnamed: D50.2 (DOUT), D51.4 (DIN)
unnamed: D51.2 (DOUT), D52.4 (DIN)
unnamed: D52.2 (DOUT), D53.4 (DIN)
unnamed: D53.2 (DOUT), D54.4 (DIN)
unnamed: D54.2 (DOUT), D55.4 (DIN)
unnamed: D55.2 (DOUT), D56.4 (DIN)
unnamed: D56.2 (DOUT), D57.4 (DIN)
unnamed: D57.2 (DOUT), D58.4 (DIN)
unnamed: D58.2 (DOUT), D59.4 (DIN)
unnamed: D59.2 (DOUT), D60.4 (DIN)
unnamed: D60.2 (DOUT), D61.4 (DIN)
unnamed: D61.2 (DOUT), D62.4 (DIN)
unnamed: D62.2 (DOUT), D63.4 (DIN)
unnamed: D63.2 (DOUT), D64.4 (DIN)
unnamed: D64.2 (DOUT), D65.4 (DIN)
unnamed: D65.2 (DOUT), D66.4 (DIN)
unnamed: D66.2 (DOUT), D67.4 (DIN)
unnamed: D67.2 (DOUT), D68.4 (DIN)
unnamed: D68.2 (DOUT), D69.4 (DIN)
unnamed: D69.2 (DOUT), D70.4 (DIN)
unnamed: D70.2 (DOUT), D71.4 (DIN)
unnamed: D71.2 (DOUT), D72.4 (DIN)
unnamed: D72.2 (DOUT), D73.4 (DIN)
unnamed: D73.2 (DOUT), D74.4 (DIN)
unnamed: D74.2 (DOUT), D75.4 (DIN)
unnamed: D75.2 (DOUT), D76.3 (DIN)
unnamed: D76.1 (DOUT), D77.3 (DIN)
unnamed: D77.1 (DOUT), D78.3 (DIN)
unnamed: D78.1 (DOUT), D79.3 (DIN)
SW_JETT: J3.1, SW1.1, SW1.2
