jrsteensen/OpenHornet/ECAD/PCBs/OH_Specific/Backlighting/GEN_TIE_Panel_PCB_V1/GEN TIE PCB V2.sch

## KiCad design ECAD/PCBs/OH_Specific/Backlighting/GEN_TIE_Panel_PCB_V1/GEN TIE PCB V2.sch (2022-09-23)

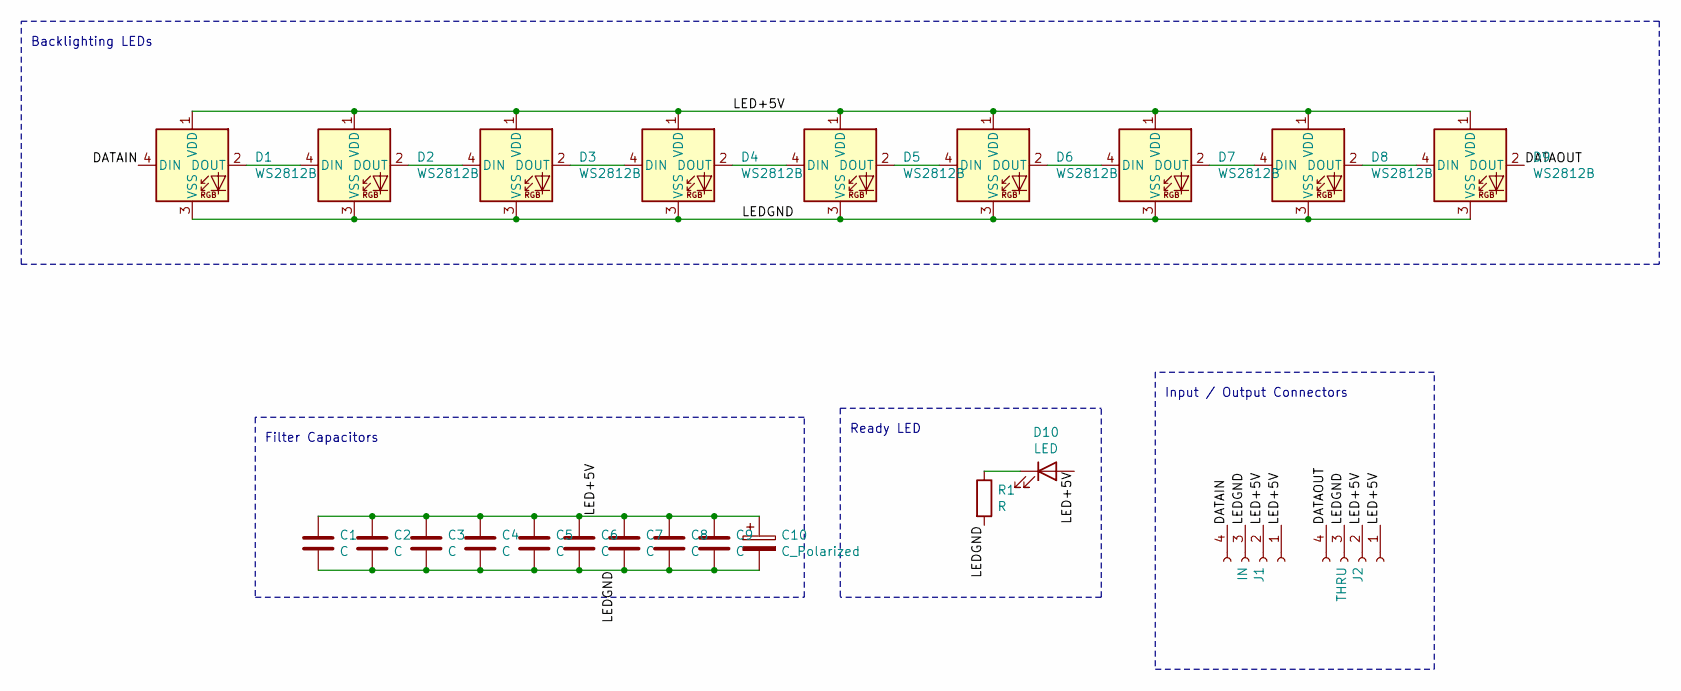
[picture p666: schematic GEN TIE PCB V2.sch]

Parts:
C1, C2, C3, C4, C5, C6, C7, C8, C9: C; C_0603_1608Metric
C10: C_Polarized; CP_Elec_8x10
D1, D2, D3, D4, D5, D6, D7, D8, D9: WS2812B; LED_WS2812B_PLCC4_5.0x5.0mm_P3.2mm
D10: LED; LED_D3.0mm
J1: IN; Molex_Mini-Fit_Jr_5566-04A_2x02_P4.20mm_Vertical
J2: THRU; Molex_Mini-Fit_Jr_5566-04A_2x02_P4.20mm_Vertical
R1: R; R_0603_1608Metric

Connections:
DATAIN: D1.4 (DIN), J1.4
DATAOUT: D9.2 (DOUT), J2.4
LED+5V: C1.1, C2.1, C3.1, C4.1, C5.1, C6.1, C7.1, C8.1, C9.1, C10.1, D1.1 (VDD), D2.1 (VDD), D3.1 (VDD), D4.1 (VDD), D5.1 (VDD), D6.1 (VDD), D7.1 (VDD), D8.1 (VDD), D9.1 (VDD), D10.2 (A), J1.1, J1.2, J2.1, J2.2
LEDGND: C1.2, C2.2, C3.2, C4.2, C5.2, C6.2, C7.2, C8.2, C9.2, C10.2, D1.3 (VSS), D2.3 (VSS), D3.3 (VSS), D4.3 (VSS), D5.3 (VSS), D6.3 (VSS), D7.3 (VSS), D8.3 (VSS), D9.3 (VSS), J1.3, J2.3, R1.2
unnamed: D1.2 (DOUT), D2.4 (DIN)
unnamed: D2.2 (DOUT), D3.4 (DIN)
unnamed: D3.2 (DOUT), D4.4 (DIN)
unnamed: D4.2 (DOUT), D5.4 (DIN)
unnamed: D5.2 (DOUT), D6.4 (DIN)
unnamed: D6.2 (DOUT), D7.4 (DIN)
unnamed: D7.2 (DOUT), D8.4 (DIN)
unnamed: D8.2 (DOUT), D9.4 (DIN)
unnamed: D10.1 (K), R1.1

Notes on the sheet:
Filter Capacitors
Ready LED
Input / Output Connectors
Backlighting LEDs
