jrsteensen/OpenHornet/ECAD/PCBs/OH_Specific/Backlighting/INTR_LT_Panel_PCB_V2/INTR LT Panel PCB V2.sch

## KiCad design ECAD/PCBs/OH_Specific/Backlighting/INTR_LT_Panel_PCB_V2/INTR LT Panel PCB V2.sch (2022-09-23)

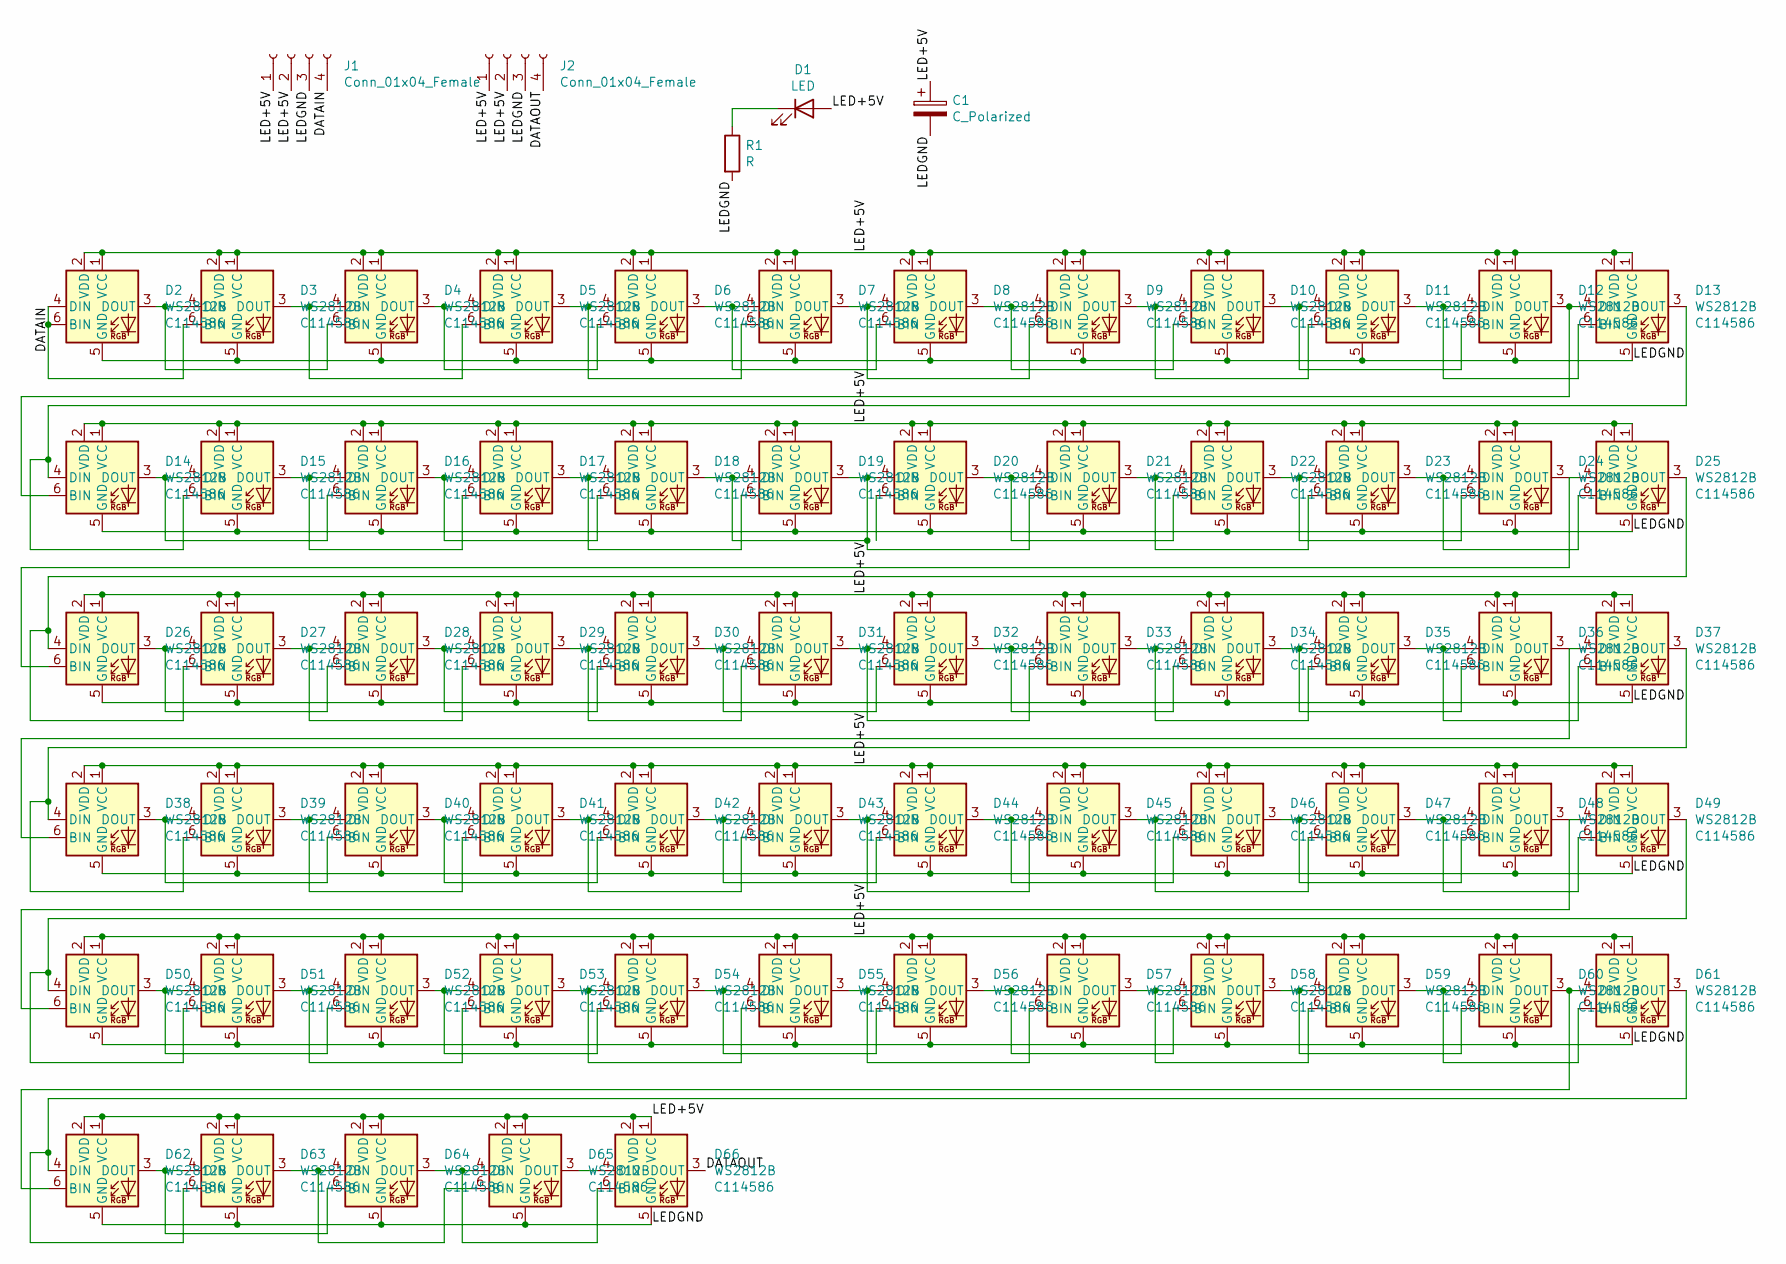
[picture p669: schematic INTR LT Panel PCB V2.sch]

Parts:
C1: C_Polarized; CP_Elec_8x10
D1: LED; LED_D3.0mm
D2, D3, D4, D5, D6, D7, D8, D9, D10, D11, D12, D13, D14, D15, D16, D17, D18, D19, D20, D21, D22, D23, D24, D25, D26, D27, D28, D29, D30, D31, D32, D33, D34, D35, D36, D37, D38, D39, D40, D41, D42, D43, D44, D45, D46, D47, D48, D49, D50, D51, D52, D53, D54, D55, D56, D57, D58, D59, D60, D61, D62, D63, D64, D65, D66: WS2812B; LED_WS2812_PLCC6_5.0x5.0mm_P1.6mm; LCSC Part Number C114586
J1, J2: Conn_01x04_Female; Molex_Mini-Fit_Jr_5566-04A_2x02_P4.20mm_Vertical
R1: R; R_0603_1608Metric

Connections:
DATAIN: D2.4 (DIN), D2.6 (BIN), D3.6 (BIN), J1.4
DATAOUT: D66.3 (DOUT), J2.4
LED+5V: C1.1, D1.2 (A), D2.1 (VCC), D2.2 (VDD), D3.1 (VCC), D3.2 (VDD), D4.1 (VCC), D4.2 (VDD), D5.1 (VCC), D5.2 (VDD), D6.1 (VCC), D6.2 (VDD), D7.1 (VCC), D7.2 (VDD), D8.1 (VCC), D8.2 (VDD), D9.1 (VCC), D9.2 (VDD), D10.1 (VCC), D10.2 (VDD), D11.1 (VCC), D11.2 (VDD), D12.1 (VCC), D12.2 (VDD), D13.1 (VCC), D13.2 (VDD), D14.1 (VCC), D14.2 (VDD), D15.1 (VCC), D15.2 (VDD), D16.1 (VCC), D16.2 (VDD), D17.1 (VCC), D17.2 (VDD), D18.1 (VCC), D18.2 (VDD), D19.1 (VCC), D19.2 (VDD), D20.1 (VCC), D20.2 (VDD), D21.1 (VCC), D21.2 (VDD), D22.1 (VCC), D22.2 (VDD), D23.1 (VCC), D23.2 (VDD), D24.1 (VCC), D24.2 (VDD), D25.1 (VCC), D25.2 (VDD), D26.1 (VCC), D26.2 (VDD), D27.1 (VCC), D27.2 (VDD), D28.1 (VCC), D28.2 (VDD), D29.1 (VCC), D29.2 (VDD), D30.1 (VCC), D30.2 (VDD), D31.1 (VCC), D31.2 (VDD), D32.1 (VCC), D32.2 (VDD), D33.1 (VCC), D33.2 (VDD), D34.1 (VCC), D34.2 (VDD), D35.1 (VCC), D35.2 (VDD), D36.1 (VCC), D36.2 (VDD), D37.1 (VCC), D37.2 (VDD), D38.1 (VCC), D38.2 (VDD), D39.1 (VCC), D39.2 (VDD), D40.1 (VCC), D40.2 (VDD), D41.1 (VCC), D41.2 (VDD), D42.1 (VCC), D42.2 (VDD), D43.1 (VCC), D43.2 (VDD), D44.1 (VCC), D44.2 (VDD), D45.1 (VCC), D45.2 (VDD), D46.1 (VCC), D46.2 (VDD), D47.1 (VCC), D47.2 (VDD), D48.1 (VCC), D48.2 (VDD), D49.1 (VCC), D49.2 (VDD), D50.1 (VCC), D50.2 (VDD), D51.1 (VCC), D51.2 (VDD), D52.1 (VCC), D52.2 (VDD), D53.1 (VCC), D53.2 (VDD), D54.1 (VCC), D54.2 (VDD), D55.1 (VCC), D55.2 (VDD), D56.1 (VCC), D56.2 (VDD), D57.1 (VCC), D57.2 (VDD), D58.1 (VCC), D58.2 (VDD), D59.1 (VCC), D59.2 (VDD), D60.1 (VCC), D60.2 (VDD), D61.1 (VCC), D61.2 (VDD), D62.1 (VCC), D62.2 (VDD), D63.1 (VCC), D63.2 (VDD), D64.1 (VCC), D64.2 (VDD), D65.1 (VCC), D65.2 (VDD), D66.1 (VCC), D66.2 (VDD), J1.1, J1.2, J2.1, J2.2
LEDGND: C1.2, D2.5 (GND), D3.5 (GND), D4.5 (GND), D5.5 (GND), D6.5 (GND), D7.5 (GND), D8.5 (GND), D9.5 (GND), D10.5 (GND), D11.5 (GND), D12.5 (GND), D13.5 (GND), D14.5 (GND), D15.5 (GND), D16.5 (GND), D17.5 (GND), D18.5 (GND), D19.5 (GND), D20.5 (GND), D21.5 (GND), D22.5 (GND), D23.5 (GND), D24.5 (GND), D25.5 (GND), D26.5 (GND), D27.5 (GND), D28.5 (GND), D29.5 (GND), D30.5 (GND), D31.5 (GND), D32.5 (GND), D33.5 (GND), D34.5 (GND), D35.5 (GND), D36.5 (GND), D37.5 (GND), D38.5 (GND), D39.5 (GND), D40.5 (GND), D41.5 (GND), D42.5 (GND), D43.5 (GND), D44.5 (GND), D45.5 (GND), D46.5 (GND), D47.5 (GND), D48.5 (GND), D49.5 (GND), D50.5 (GND), D51.5 (GND), D52.5 (GND), D53.5 (GND), D54.5 (GND), D55.5 (GND), D56.5 (GND), D57.5 (GND), D58.5 (GND), D59.5 (GND), D60.5 (GND), D61.5 (GND), D62.5 (GND), D63.5 (GND), D64.5 (GND), D65.5 (GND), D66.5 (GND), J1.3, J2.3, R1.2
unnamed: D1.1 (K), R1.1
unnamed: D2.3 (DOUT), D3.4 (DIN), D4.6 (BIN)
unnamed: D3.3 (DOUT), D4.4 (DIN), D5.6 (BIN)
unnamed: D4.3 (DOUT), D5.4 (DIN), D6.6 (BIN)
unnamed: D5.3 (DOUT), D6.4 (DIN), D7.6 (BIN)
unnamed: D6.3 (DOUT), D7.4 (DIN), D8.6 (BIN)
unnamed: D7.3 (DOUT), D8.4 (DIN), D9.6 (BIN)
unnamed: D10.3 (DOUT), D11.4 (DIN), D12.6 (BIN)
unnamed: D9.3 (DOUT), D10.4 (DIN), D11.6 (BIN)
unnamed: D8.3 (DOUT), D9.4 (DIN), D10.6 (BIN)
unnamed: D11.3 (DOUT), D12.4 (DIN), D13.6 (BIN)
unnamed: D12.3 (DOUT), D13.4 (DIN), D14.6 (BIN)
unnamed: D13.3 (DOUT), D14.4 (DIN), D15.6 (BIN)
unnamed: D14.3 (DOUT), D15.4 (DIN), D16.6 (BIN)
unnamed: D15.3 (DOUT), D16.4 (DIN), D17.6 (BIN)
unnamed: D16.3 (DOUT), D17.4 (DIN), D18.6 (BIN)
unnamed: D17.3 (DOUT), D18.4 (DIN), D19.6 (BIN)
unnamed: D18.3 (DOUT), D19.3 (DOUT), D19.4 (DIN), D20.4 (DIN), D21.6 (BIN)
unnamed: D20.3 (DOUT), D21.4 (DIN), D22.6 (BIN)
unnamed: D21.3 (DOUT), D22.4 (DIN), D23.6 (BIN)
unnamed: D22.3 (DOUT), D23.4 (DIN), D24.6 (BIN)
unnamed: D23.3 (DOUT), D24.4 (DIN), D25.6 (BIN)
unnamed: D24.3 (DOUT), D25.4 (DIN), D26.6 (BIN)
unnamed: D25.3 (DOUT), D26.4 (DIN), D27.6 (BIN)
unnamed: D26.3 (DOUT), D27.4 (DIN), D28.6 (BIN)
unnamed: D27.3 (DOUT), D28.4 (DIN), D29.6 (BIN)
unnamed: D28.3 (DOUT), D29.4 (DIN), D30.6 (BIN)
unnamed: D29.3 (DOUT), D30.4 (DIN), D31.6 (BIN)
unnamed: D30.3 (DOUT), D31.4 (DIN), D32.6 (BIN)
unnamed: D31.3 (DOUT), D32.4 (DIN), D33.6 (BIN)
unnamed: D32.3 (DOUT), D33.4 (DIN), D34.6 (BIN)
unnamed: D33.3 (DOUT), D34.4 (DIN), D35.6 (BIN)
unnamed: D34.3 (DOUT), D35.4 (DIN), D36.6 (BIN)
unnamed: D35.3 (DOUT), D36.4 (DIN), D37.6 (BIN)
unnamed: D36.3 (DOUT), D37.4 (DIN), D38.6 (BIN)
unnamed: D37.3 (DOUT), D38.4 (DIN), D39.6 (BIN)
unnamed: D38.3 (DOUT), D39.4 (DIN), D40.6 (BIN)
unnamed: D39.3 (DOUT), D40.4 (DIN), D41.6 (BIN)
unnamed: D40.3 (DOUT), D41.4 (DIN), D42.6 (BIN)
unnamed: D41.3 (DOUT), D42.4 (DIN), D43.6 (BIN)
unnamed: D42.3 (DOUT), D43.4 (DIN), D44.6 (BIN)
unnamed: D43.3 (DOUT), D44.4 (DIN), D45.6 (BIN)
unnamed: D44.3 (DOUT), D45.4 (DIN), D46.6 (BIN)
unnamed: D45.3 (DOUT), D46.4 (DIN), D47.6 (BIN)
unnamed: D46.3 (DOUT), D47.4 (DIN), D48.6 (BIN)
unnamed: D47.3 (DOUT), D48.4 (DIN), D49.6 (BIN)
unnamed: D48.3 (DOUT), D49.4 (DIN), D50.6 (BIN)
unnamed: D49.3 (DOUT), D50.4 (DIN), D51.6 (BIN)
unnamed: D50.3 (DOUT), D51.4 (DIN), D52.6 (BIN)
unnamed: D51.3 (DOUT), D52.4 (DIN), D53.6 (BIN)
unnamed: D52.3 (DOUT), D53.4 (DIN), D54.6 (BIN)
unnamed: D53.3 (DOUT), D54.4 (DIN), D55.6 (BIN)
unnamed: D54.3 (DOUT), D55.4 (DIN), D56.6 (BIN)
unnamed: D55.3 (DOUT), D56.4 (DIN), D57.6 (BIN)
unnamed: D56.3 (DOUT), D57.4 (DIN), D58.6 (BIN)
unnamed: D57.3 (DOUT), D58.4 (DIN), D59.6 (BIN)
unnamed: D58.3 (DOUT), D59.4 (DIN), D60.6 (BIN)
unnamed: D59.3 (DOUT), D60.4 (DIN), D61.6 (BIN)
unnamed: D60.3 (DOUT), D61.4 (DIN), D62.6 (BIN)
unnamed: D61.3 (DOUT), D62.4 (DIN), D63.6 (BIN)
unnamed: D62.3 (DOUT), D63.4 (DIN), D64.6 (BIN)
unnamed: D63.3 (DOUT), D64.4 (DIN), D65.6 (BIN)
unnamed: D64.3 (DOUT), D65.4 (DIN), D66.6 (BIN)
unnamed: D65.3 (DOUT), D66.4 (DIN)
