jrsteensen/OpenHornet/ECAD/PCBs/OH_Specific/Backlighting/JETT_Station_Select_Placard_PCB_V1/JETT Station Select Placard PCB V1.sch

## KiCad design ECAD/PCBs/OH_Specific/Backlighting/JETT_Station_Select_Placard_PCB_V1/JETT Station Select Placard PCB V1.sch (2022-09-23)

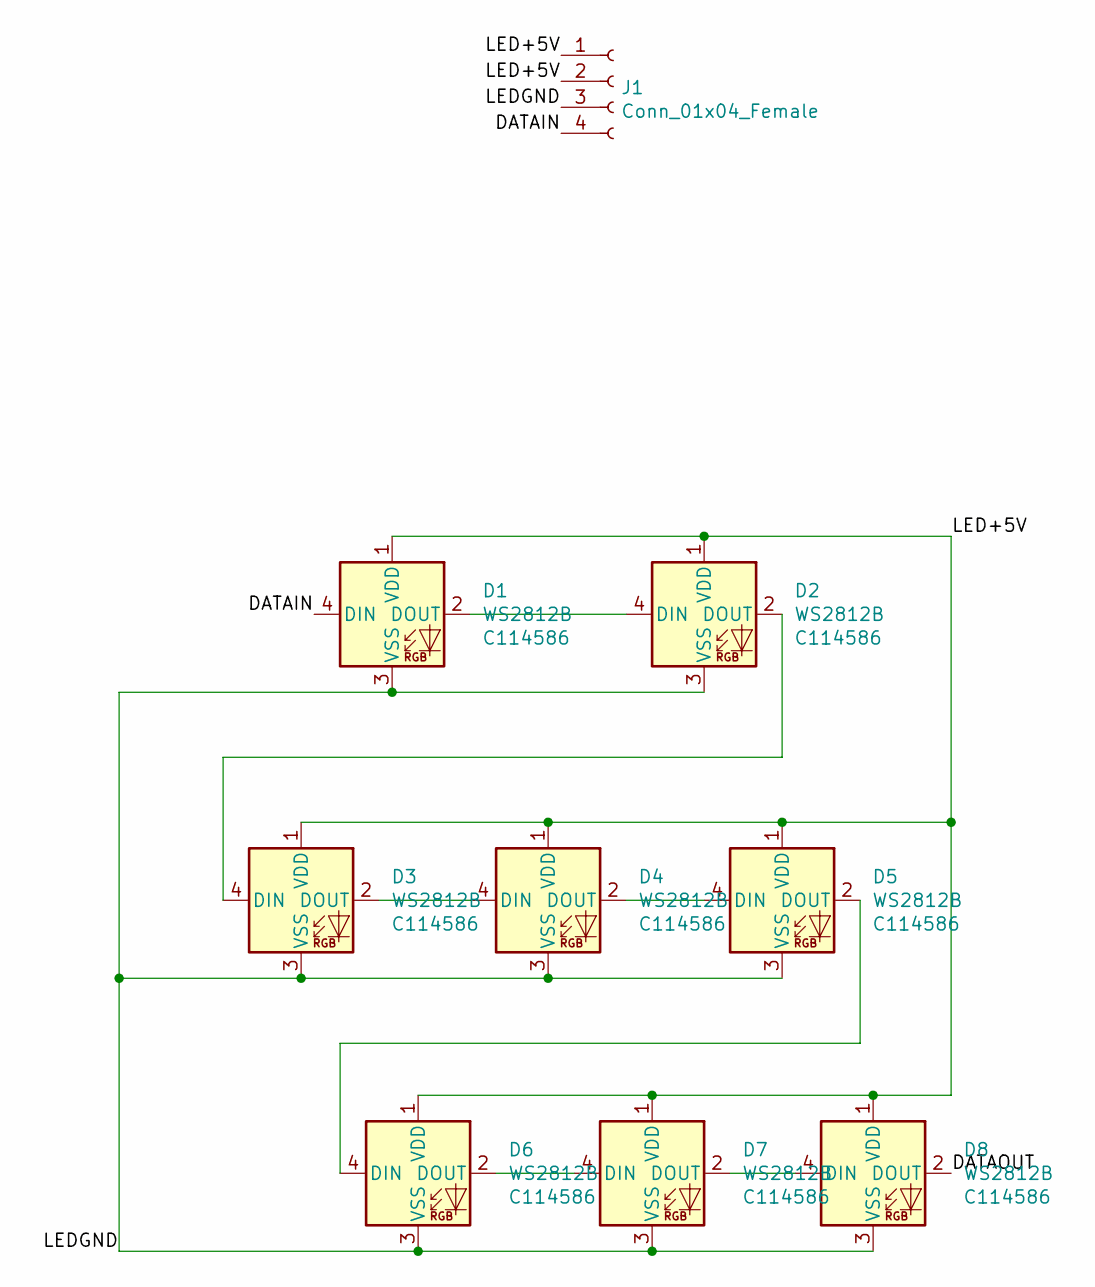
[picture p670: schematic JETT Station Select Placard PCB V1.sch]

Parts:
D1, D2, D3, D4, D5, D6, D7, D8: WS2812B; LED_WS2812B_PLCC4_5.0x5.0mm_P3.2mm; LCSC Part Number C114586
J1: Conn_01x04_Female; Molex_Mini-Fit_Jr_5566-04A_2x02_P4.20mm_Vertical

Connections:
DATAIN: D1.4 (DIN), J1.4
DATAOUT: D8.2 (DOUT)
LED+5V: D1.1 (VDD), D2.1 (VDD), D3.1 (VDD), D4.1 (VDD), D5.1 (VDD), D6.1 (VDD), D7.1 (VDD), D8.1 (VDD), J1.1, J1.2
LEDGND: D1.3 (VSS), D2.3 (VSS), D3.3 (VSS), D4.3 (VSS), D5.3 (VSS), D6.3 (VSS), D7.3 (VSS), D8.3 (VSS), J1.3
unnamed: D1.2 (DOUT), D2.4 (DIN)
unnamed: D2.2 (DOUT), D3.4 (DIN)
unnamed: D3.2 (DOUT), D4.4 (DIN)
unnamed: D4.2 (DOUT), D5.4 (DIN)
unnamed: D5.2 (DOUT), D6.4 (DIN)
unnamed: D6.2 (DOUT), D7.4 (DIN)
unnamed: D7.2 (DOUT), D8.4 (DIN)
