jrsteensen/OpenHornet/ECAD/PCBs/OH_Specific/Backlighting/Master_Arm_Panel_PCB_V2/MasterModePushbuttonV2.sch

## KiCad design ECAD/PCBs/OH_Specific/Backlighting/Master_Arm_Panel_PCB_V2/MasterModePushbuttonV2.sch (2022-09-23)

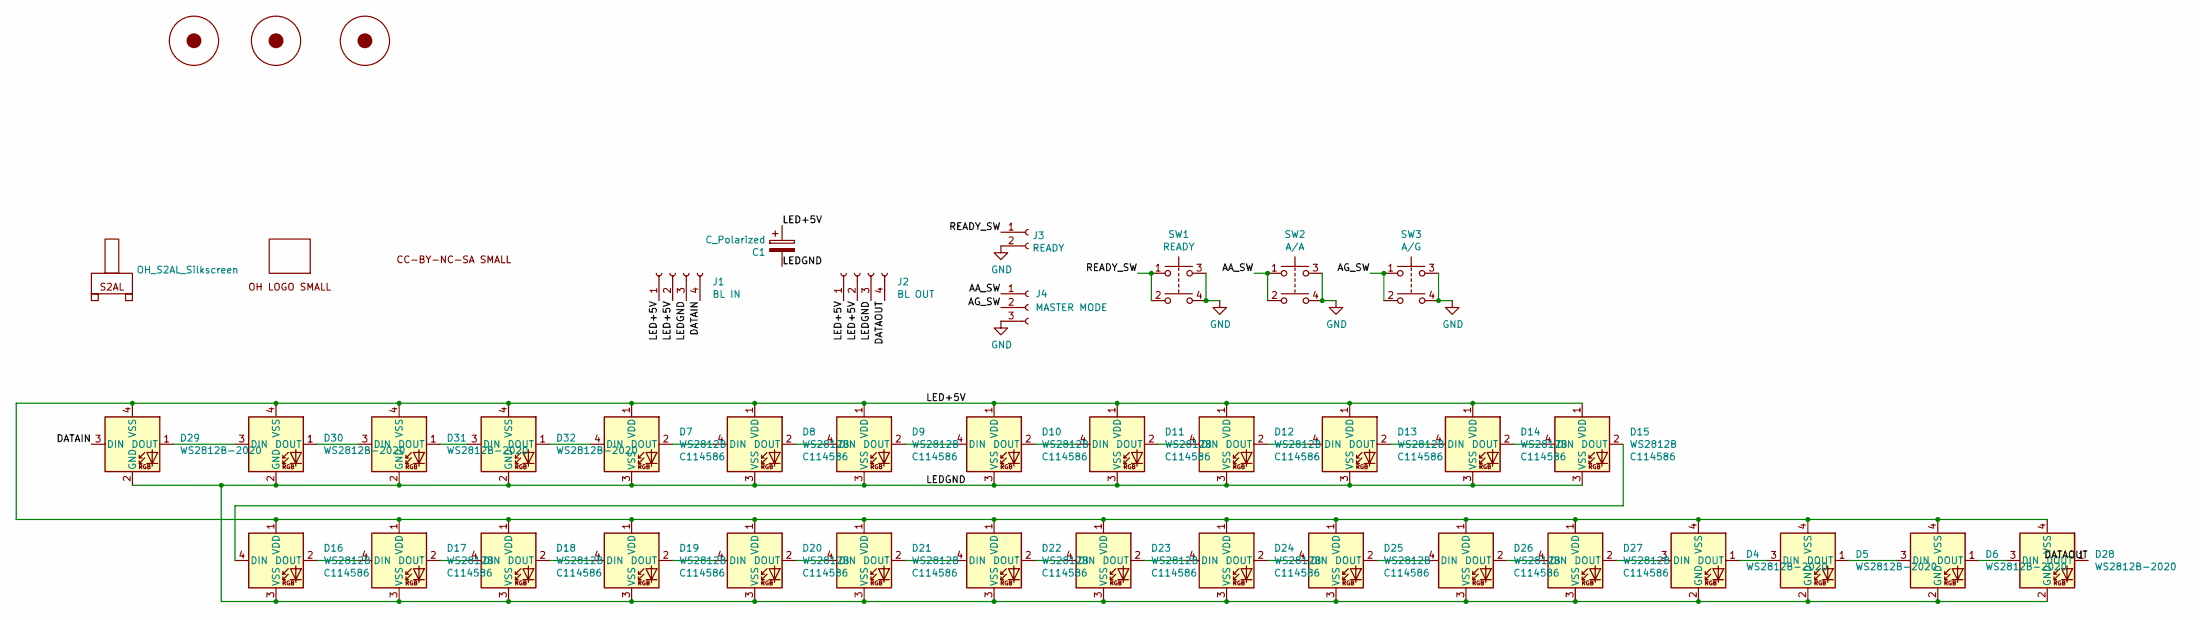
[picture p673: schematic MasterModePushbuttonV2.sch]

Parts:
C1: C_Polarized; CP_Elec_8x10
D4, D5, D6, D28, D29, D30, D31, D32: WS2812B-2020; WS2812-2020; LCSC C965555
D7, D8, D9, D10, D11, D12, D13, D14, D15, D16, D17, D18, D19, D20, D21, D22, D23, D24, D25, D26, D27: WS2812B; LED_WS2812B_PLCC4_5.0x5.0mm_P3.2mm; LCSC Part Number C114586
H1, H2, H3: OHPanelScrew; OH_Panel_6-32_PHS
J1: BL IN; Molex_Mini-Fit_Jr_5566-04A_2x02_P4.20mm_Vertical
J2: BL OUT; Molex_Mini-Fit_Jr_5566-04A_2x02_P4.20mm_Vertical
J3: READY; Molex_KK-254_AE-6410-02A_1x02_P2.54mm_Vertical
J4: MASTER MODE; Molex_KK-254_AE-6410-03A_1x03_P2.54mm_Vertical
LOGO1: CC-BY-NC-SA_Icon; CC-BY-NC-SA-Small
LOGO2: OpenHornetLogoSmall; OH_LOGO_37.7mm_5.9mm
LOGO3: OH_S2AL_Silkscreen; S2AL_Toggle_Silkscreen
SW1: READY; SW_TH_Tactile_Omron_B3F-10xx
SW2: A/A; SW_TH_Tactile_Omron_B3F-10xx
SW3: A/G; SW_TH_Tactile_Omron_B3F-10xx

Connections:
AA_SW: J4.1, SW2.1, SW2.2
AG_SW: J4.2, SW3.1, SW3.2
DATAIN: D29.3 (DIN), J1.4
DATAOUT: D28.1 (DOUT), J2.4
GND: J3.2, J4.3, SW1.3, SW1.4, SW2.3, SW2.4, SW3.3, SW3.4
LED+5V: C1.1, D4.4 (VSS), D5.4 (VSS), D6.4 (VSS), D7.1 (VDD), D8.1 (VDD), D9.1 (VDD), D10.1 (VDD), D11.1 (VDD), D12.1 (VDD), D13.1 (VDD), D14.1 (VDD), D15.1 (VDD), D16.1 (VDD), D17.1 (VDD), D18.1 (VDD), D19.1 (VDD), D20.1 (VDD), D21.1 (VDD), D22.1 (VDD), D23.1 (VDD), D24.1 (VDD), D25.1 (VDD), D26.1 (VDD), D27.1 (VDD), D28.4 (VSS), D29.4 (VSS), D30.4 (VSS), D31.4 (VSS), D32.4 (VSS), J1.1, J1.2, J2.1, J2.2
LEDGND: C1.2, D4.2 (GND), D5.2 (GND), D6.2 (GND), D7.3 (VSS), D8.3 (VSS), D9.3 (VSS), D10.3 (VSS), D11.3 (VSS), D12.3 (VSS), D13.3 (VSS), D14.3 (VSS), D15.3 (VSS), D16.3 (VSS), D17.3 (VSS), D18.3 (VSS), D19.3 (VSS), D20.3 (VSS), D21.3 (VSS), D22.3 (VSS), D23.3 (VSS), D24.3 (VSS), D25.3 (VSS), D26.3 (VSS), D27.3 (VSS), D28.2 (GND), D29.2 (GND), D30.2 (GND), D31.2 (GND), D32.2 (GND), J1.3, J2.3
unnamed: D4.1 (DOUT), D5.3 (DIN)
unnamed: D5.1 (DOUT), D6.3 (DIN)
unnamed: D7.2 (DOUT), D8.4 (DIN)
unnamed: D8.2 (DOUT), D9.4 (DIN)
unnamed: D10.2 (DOUT), D11.4 (DIN)
unnamed: D9.2 (DOUT), D10.4 (DIN)
unnamed: D11.2 (DOUT), D12.4 (DIN)
unnamed: D12.2 (DOUT), D13.4 (DIN)
unnamed: D13.2 (DOUT), D14.4 (DIN)
unnamed: D14.2 (DOUT), D15.4 (DIN)
unnamed: D15.2 (DOUT), D16.4 (DIN)
unnamed: D16.2 (DOUT), D17.4 (DIN)
unnamed: D17.2 (DOUT), D18.4 (DIN)
unnamed: D18.2 (DOUT), D19.4 (DIN)
unnamed: D19.2 (DOUT), D20.4 (DIN)
unnamed: D20.2 (DOUT), D21.4 (DIN)
unnamed: D21.2 (DOUT), D22.4 (DIN)
unnamed: D22.2 (DOUT), D23.4 (DIN)
unnamed: D23.2 (DOUT), D24.4 (DIN)
unnamed: D24.2 (DOUT), D25.4 (DIN)
unnamed: D25.2 (DOUT), D26.4 (DIN)
unnamed: D26.2 (DOUT), D27.4 (DIN)
unnamed: D4.3 (DIN), D27.2 (DOUT)
unnamed: D6.1 (DOUT), D28.3 (DIN)
unnamed: D29.1 (DOUT), D30.3 (DIN)
unnamed: D30.1 (DOUT), D31.3 (DIN)
unnamed: D31.1 (DOUT), D32.3 (DIN)
unnamed: D7.4 (DIN), D32.1 (DOUT)
READY_SW: J3.1, SW1.1, SW1.2
