jrsteensen/OpenHornet/ECAD/PCBs/OH_Specific/Functional/ampcd_button_board/ampcd_button_board.sch

## KiCad design ECAD/PCBs/OH_Specific/Functional/ampcd_button_board/ampcd_button_board.sch (2022-09-23)

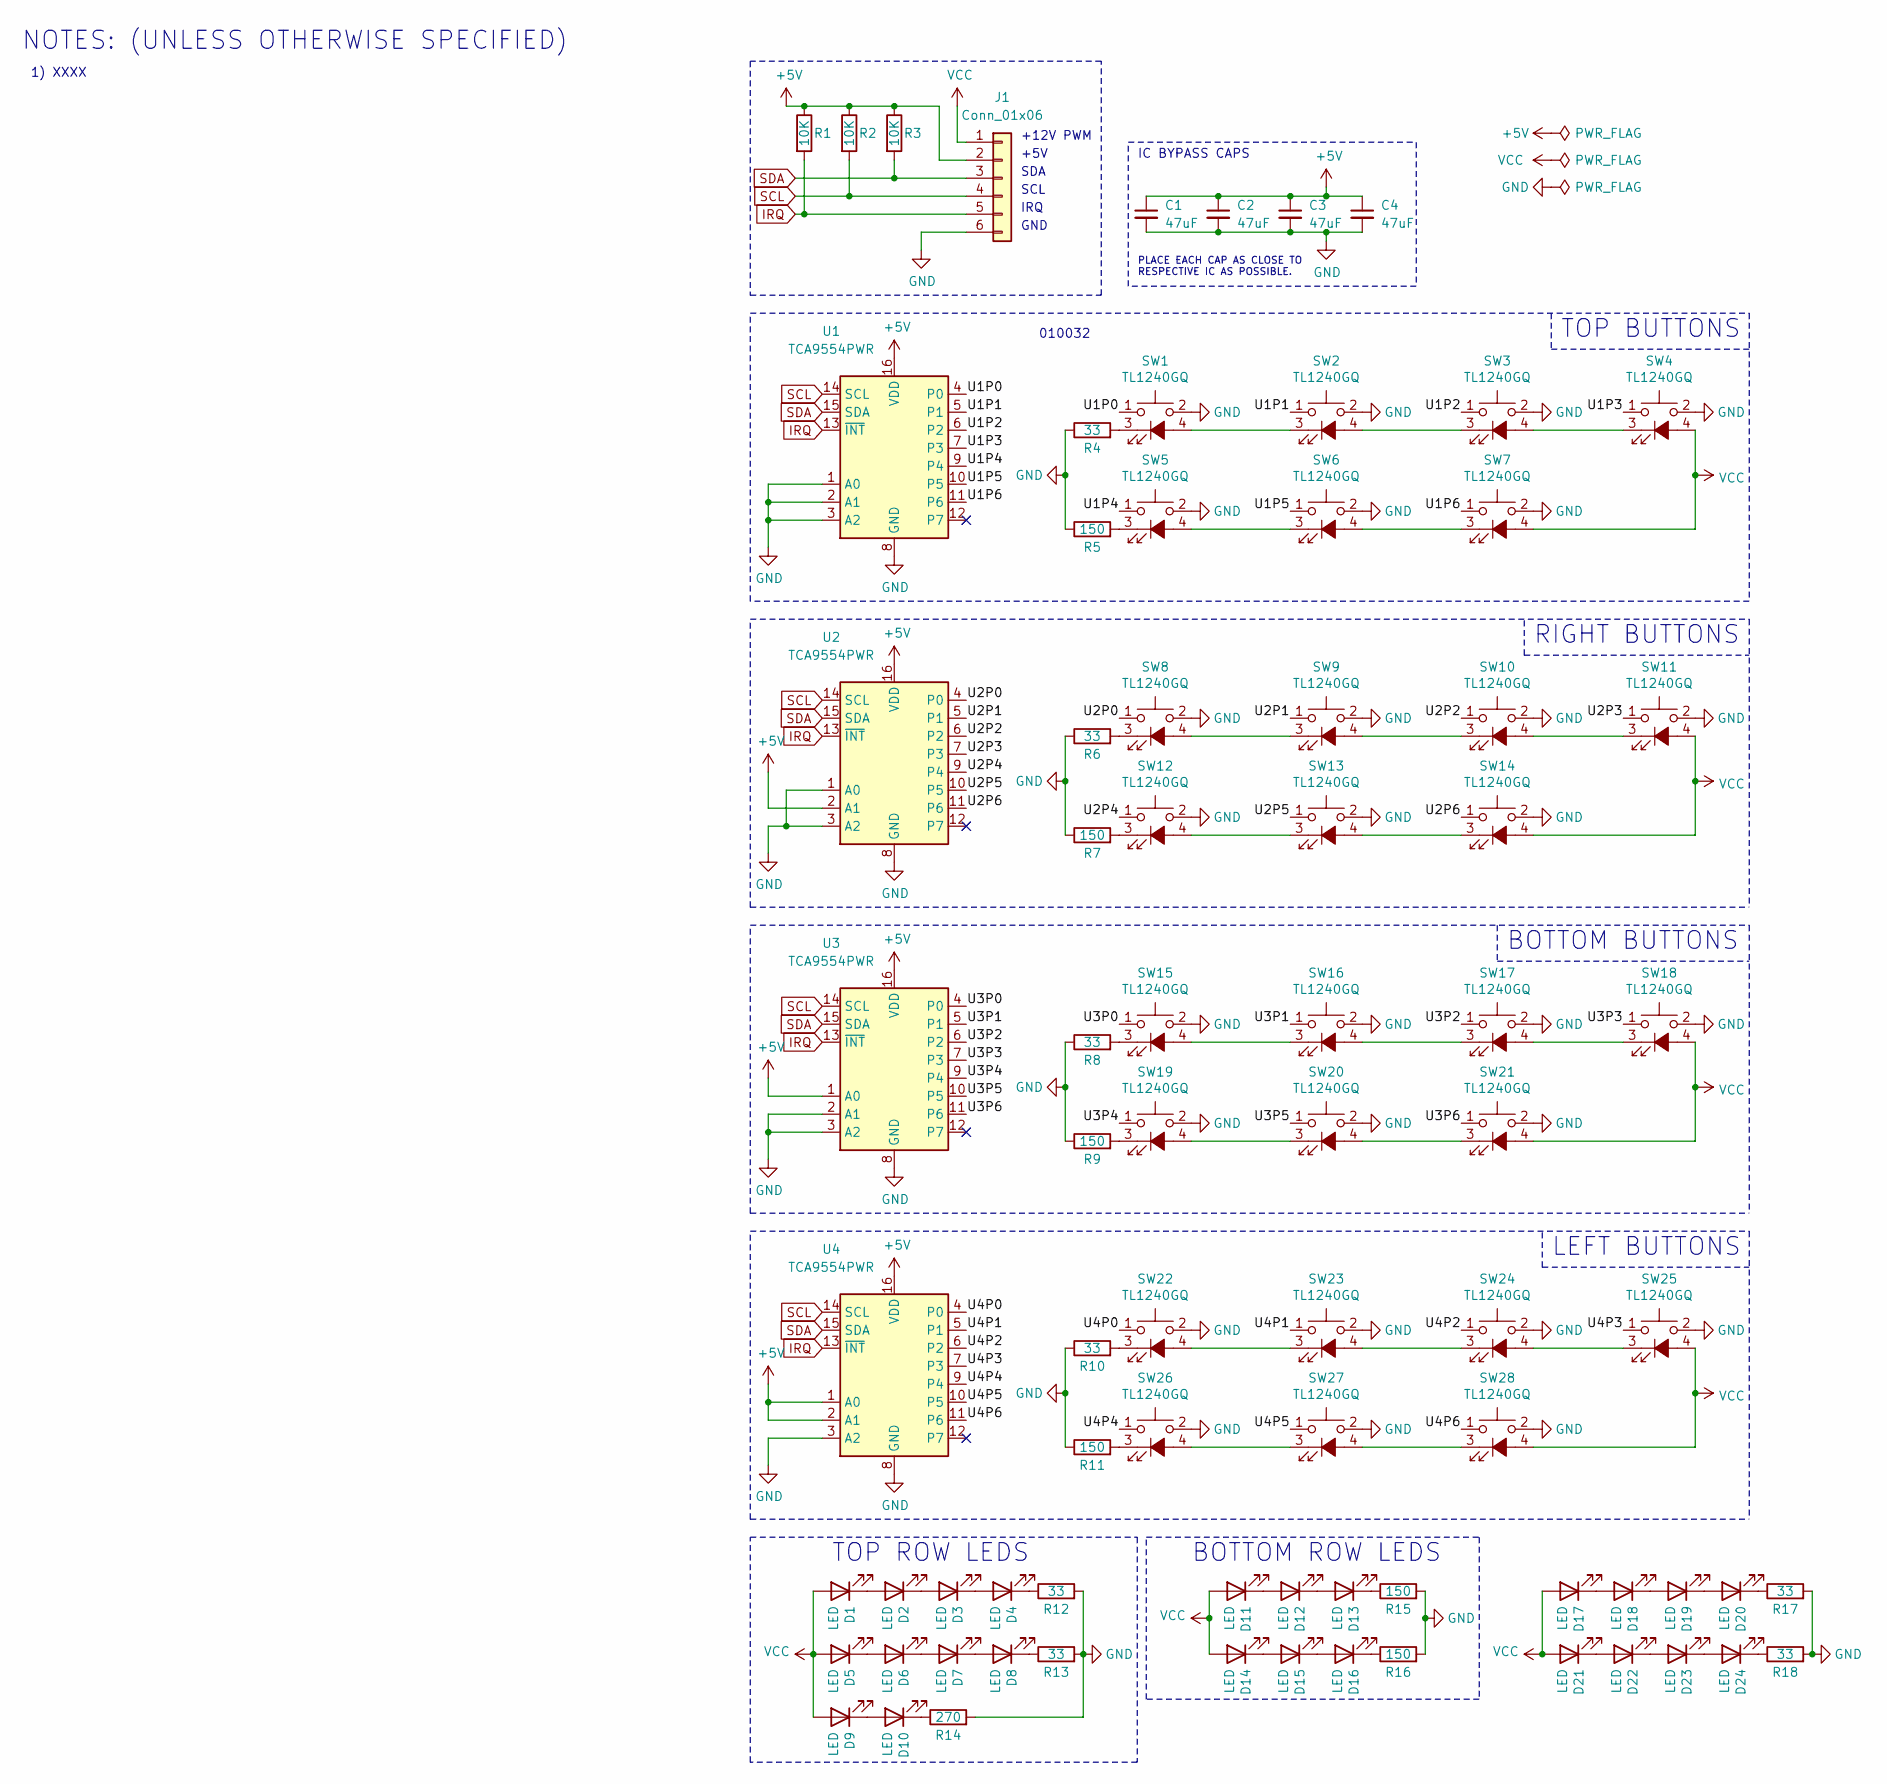
[picture p678: schematic ampcd_button_board.sch]

Parts:
C1, C2, C3, C4: 47uF; C_1206_3216Metric; LCSC C96123
D1, D2, D3, D4, D5, D6, D7, D8, D9, D10, D11, D12, D13, D14, D15, D16, D17, D18, D19, D20, D21, D22, D23, D24: LED; LED_0402_1005Metric; LCSC C130723
J1: Conn_01x06; PinHeader_1x06_P2.54mm_Horizontal
R1, R2, R3: 10K; R_0603_1608Metric; LCSC C25804
R4, R6, R8, R10, R12, R13, R17, R18: 33; R_0402_1005Metric; LCSC C25105
R5, R7, R9, R11, R15, R16: 150; R_0402_1005Metric; LCSC C25082
R14: 270; R_0402_1005Metric; LCSC C25099
SW1, SW2, SW3, SW4, SW5, SW6, SW7, SW8, SW9, SW10, SW11, SW12, SW13, SW14, SW15, SW16, SW17, SW18, SW19, SW20, SW21, SW22, SW23, SW24, SW25, SW26, SW27, SW28: TL1240GQ
U1, U2, U3, U4: TCA9554PWR; TSSOP-16_4.4x5mm_P0.65mm; LCSC C477924

Connections:
+5V: C1.1, C2.1, C3.1, C4.1, J1.2, R1.1, R2.1, R3.1, U1.16 (VDD), U2.2 (A1), U2.16 (VDD), U3.1 (A0), U3.16 (VDD), U4.1 (A0), U4.2 (A1), U4.16 (VDD)
GND: C1.2, C2.2, C3.2, C4.2, J1.6, R4.1, R5.1, R6.1, R7.1, R8.1, R9.1, R10.1, R11.1, R12.2, R13.2, R14.2, R15.2, R16.2, R17.2, R18.2, SW1.2, SW2.2, SW3.2, SW4.2, SW5.2, SW6.2, SW7.2, SW8.2, SW9.2, SW10.2, SW11.2, SW12.2, SW13.2, SW14.2, SW15.2, SW16.2, SW17.2, SW18.2, SW19.2, SW20.2, SW21.2, SW22.2, SW23.2, SW24.2, SW25.2, SW26.2, SW27.2, SW28.2, U1.1 (A0), U1.2 (A1), U1.3 (A2), U1.8 (GND), U2.1 (A0), U2.3 (A2), U2.8 (GND), U3.2 (A1), U3.3 (A2), U3.8 (GND), U4.3 (A2), U4.8 (GND)
IRQ: J1.5, R1.2, U1.13 (~INT~), U2.13 (~INT~), U3.13 (~INT~), U4.13 (~INT~)
unnamed: D1.1 (K), D2.2 (A)
unnamed: D2.1 (K), D3.2 (A)
unnamed: D3.1 (K), D4.2 (A)
unnamed: D4.1 (K), R12.1
unnamed: D5.1 (K), D6.2 (A)
unnamed: D6.1 (K), D7.2 (A)
unnamed: D7.1 (K), D8.2 (A)
unnamed: D8.1 (K), R13.1
unnamed: D10.1 (K), R14.1
unnamed: D9.1 (K), D10.2 (A)
unnamed: D11.1 (K), D12.2 (A)
unnamed: D12.1 (K), D13.2 (A)
unnamed: D13.1 (K), R15.1
unnamed: D14.1 (K), D15.2 (A)
unnamed: D15.1 (K), D16.2 (A)
unnamed: D16.1 (K), R16.1
unnamed: D17.1 (K), D18.2 (A)
unnamed: D18.1 (K), D19.2 (A)
unnamed: D19.1 (K), D20.2 (A)
unnamed: D20.1 (K), R17.1
unnamed: D21.1 (K), D22.2 (A)
unnamed: D22.1 (K), D23.2 (A)
unnamed: D23.1 (K), D24.2 (A)
unnamed: D24.1 (K), R18.1
unnamed: R4.2, SW1.3 (K)
unnamed: R5.2, SW5.3 (K)
unnamed: R6.2, SW8.3 (K)
unnamed: R7.2, SW12.3 (K)
unnamed: R8.2, SW15.3 (K)
unnamed: R9.2, SW19.3 (K)
unnamed: R10.2, SW22.3 (K)
unnamed: R11.2, SW26.3 (K)
unnamed: SW1.4 (A), SW2.3 (K)
unnamed: SW2.4 (A), SW3.3 (K)
unnamed: SW3.4 (A), SW4.3 (K)
unnamed: SW5.4 (A), SW6.3 (K)
unnamed: SW6.4 (A), SW7.3 (K)
unnamed: SW8.4 (A), SW9.3 (K)
unnamed: SW9.4 (A), SW10.3 (K)
unnamed: SW10.4 (A), SW11.3 (K)
unnamed: SW12.4 (A), SW13.3 (K)
unnamed: SW13.4 (A), SW14.3 (K)
unnamed: SW15.4 (A), SW16.3 (K)
unnamed: SW16.4 (A), SW17.3 (K)
unnamed: SW17.4 (A), SW18.3 (K)
unnamed: SW19.4 (A), SW20.3 (K)
unnamed: SW20.4 (A), SW21.3 (K)
unnamed: SW22.4 (A), SW23.3 (K)
unnamed: SW23.4 (A), SW24.3 (K)
unnamed: SW24.4 (A), SW25.3 (K)
unnamed: SW26.4 (A), SW27.3 (K)
unnamed: SW27.4 (A), SW28.3 (K)
SCL: J1.4, R2.2, U1.14 (SCL), U2.14 (SCL), U3.14 (SCL), U4.14 (SCL)
SDA: J1.3, R3.2, U1.15 (SDA), U2.15 (SDA), U3.15 (SDA), U4.15 (SDA)
U1P0: SW1.1, U1.4 (P0)
U1P1: SW2.1, U1.5 (P1)
U1P2: SW3.1, U1.6 (P2)
U1P3: SW4.1, U1.7 (P3)
U1P4: SW5.1, U1.9 (P4)
U1P5: SW6.1, U1.10 (P5)
U1P6: SW7.1, U1.11 (P6)
U2P0: SW8.1, U2.4 (P0)
U2P1: SW9.1, U2.5 (P1)
U2P2: SW10.1, U2.6 (P2)
U2P3: SW11.1, U2.7 (P3)
U2P4: SW12.1, U2.9 (P4)
U2P5: SW13.1, U2.10 (P5)
U2P6: SW14.1, U2.11 (P6)
U3P0: SW15.1, U3.4 (P0)
U3P1: SW16.1, U3.5 (P1)
U3P2: SW17.1, U3.6 (P2)
U3P3: SW18.1, U3.7 (P3)
U3P4: SW19.1, U3.9 (P4)
U3P5: SW20.1, U3.10 (P5)
U3P6: SW21.1, U3.11 (P6)
U4P0: SW22.1, U4.4 (P0)
U4P1: SW23.1, U4.5 (P1)
U4P2: SW24.1, U4.6 (P2)
U4P3: SW25.1, U4.7 (P3)
U4P4: SW26.1, U4.9 (P4)
U4P5: SW27.1, U4.10 (P5)
U4P6: SW28.1, U4.11 (P6)
VCC: D1.2 (A), D5.2 (A), D9.2 (A), D11.2 (A), D14.2 (A), D17.2 (A), D21.2 (A), J1.1, SW4.4 (A), SW7.4 (A), SW11.4 (A), SW14.4 (A), SW18.4 (A), SW21.4 (A), SW25.4 (A), SW28.4 (A)

Notes on the sheet:
NOTES: (UNLESS OTHERWISE SPECIFIED)
1) XXXX
TOP ROW LEDS
BOTTOM ROW LEDS
GND
IRQ
SCL
SDA
+5V
+12V PWM
010032
LEFT BUTTONS
BOTTOM BUTTONS
RIGHT BUTTONS
TOP BUTTONS
PLACE EACH CAP AS CLOSE TO RESPECTIVE IC AS POSSIBLE.
IC BYPASS CAPS
