jrsteensen/OpenHornet/ECAD/PCBs/OH_Specific/Functional/ddi_button_board/Buttons_DDI.sch

## KiCad design ECAD/PCBs/OH_Specific/Functional/ddi_button_board/Buttons_DDI.sch (2022-09-23)

Schematic: Buttons_DDI.sch

Parts:
C1, C2, C3, C4: 47uF; C_1206_3216Metric; LCSC C96123
D1, D2, D3, D4, D5, D6, D7, D8, D9, D10, D11, D12, D13, D14, D17, D18, D19, D20, D21, D22, D23, D24, D25, D26, D27, D28, D29, D30, D31, D32: LED; LED_0402_1005Metric; LCSC C130723
J1: Conn_01x06; Molex_KK-254_AE-6410-06A_1x06_P2.54mm_Vertical
MK1, MK2, MK3, MK4: MH; MountingHole_4.3mm_M4
R1, R2, R3: 10K; R_0603_1608Metric; LCSC C25804
R4, R6, R8, R10, R16, R17, R19, R20: 150; R_0402_1005Metric; LCSC C25082
R5, R7, R9, R11, R15, R18, R21: 270; R_0402_1005Metric; LCSC C25099
R12, R13, R14: 33; R_0402_1005Metric; LCSC C25105
SW1, SW2, SW3, SW4, SW5, SW6, SW7, SW8, SW9, SW10, SW11, SW12, SW13, SW14, SW15, SW16, SW17, SW18, SW19, SW20: TL1240GQ
U1, U2, U3, U4: TCA9554PWR; TSSOP-16_4.4x5mm_P0.65mm; LCSC C477924

Notes on the sheet:
IC BYPASS CAPS
PLACE EACH CAP AS CLOSE TO RESPECTIVE IC AS POSSIBLE.
TOP BUTTONS
RIGHT BUTTONS
BOTTOM BUTTONS
LEFT BUTTONS
NOTES: (UNLESS OTHERWISE SPECIFIED)
1) XXXX
010032
+12V PWM
+5V
SDA
SCL
IRQ
GND
MODE SW BL LED
CONT BL LED
BRT BL LED
