jrsteensen/OpenHornet/ECAD/PCBs/OH_Specific/Functional/dual_needle_gauge/dual_needle_gauge.sch

## KiCad design ECAD/PCBs/OH_Specific/Functional/dual_needle_gauge/dual_needle_gauge.sch (2022-09-23)

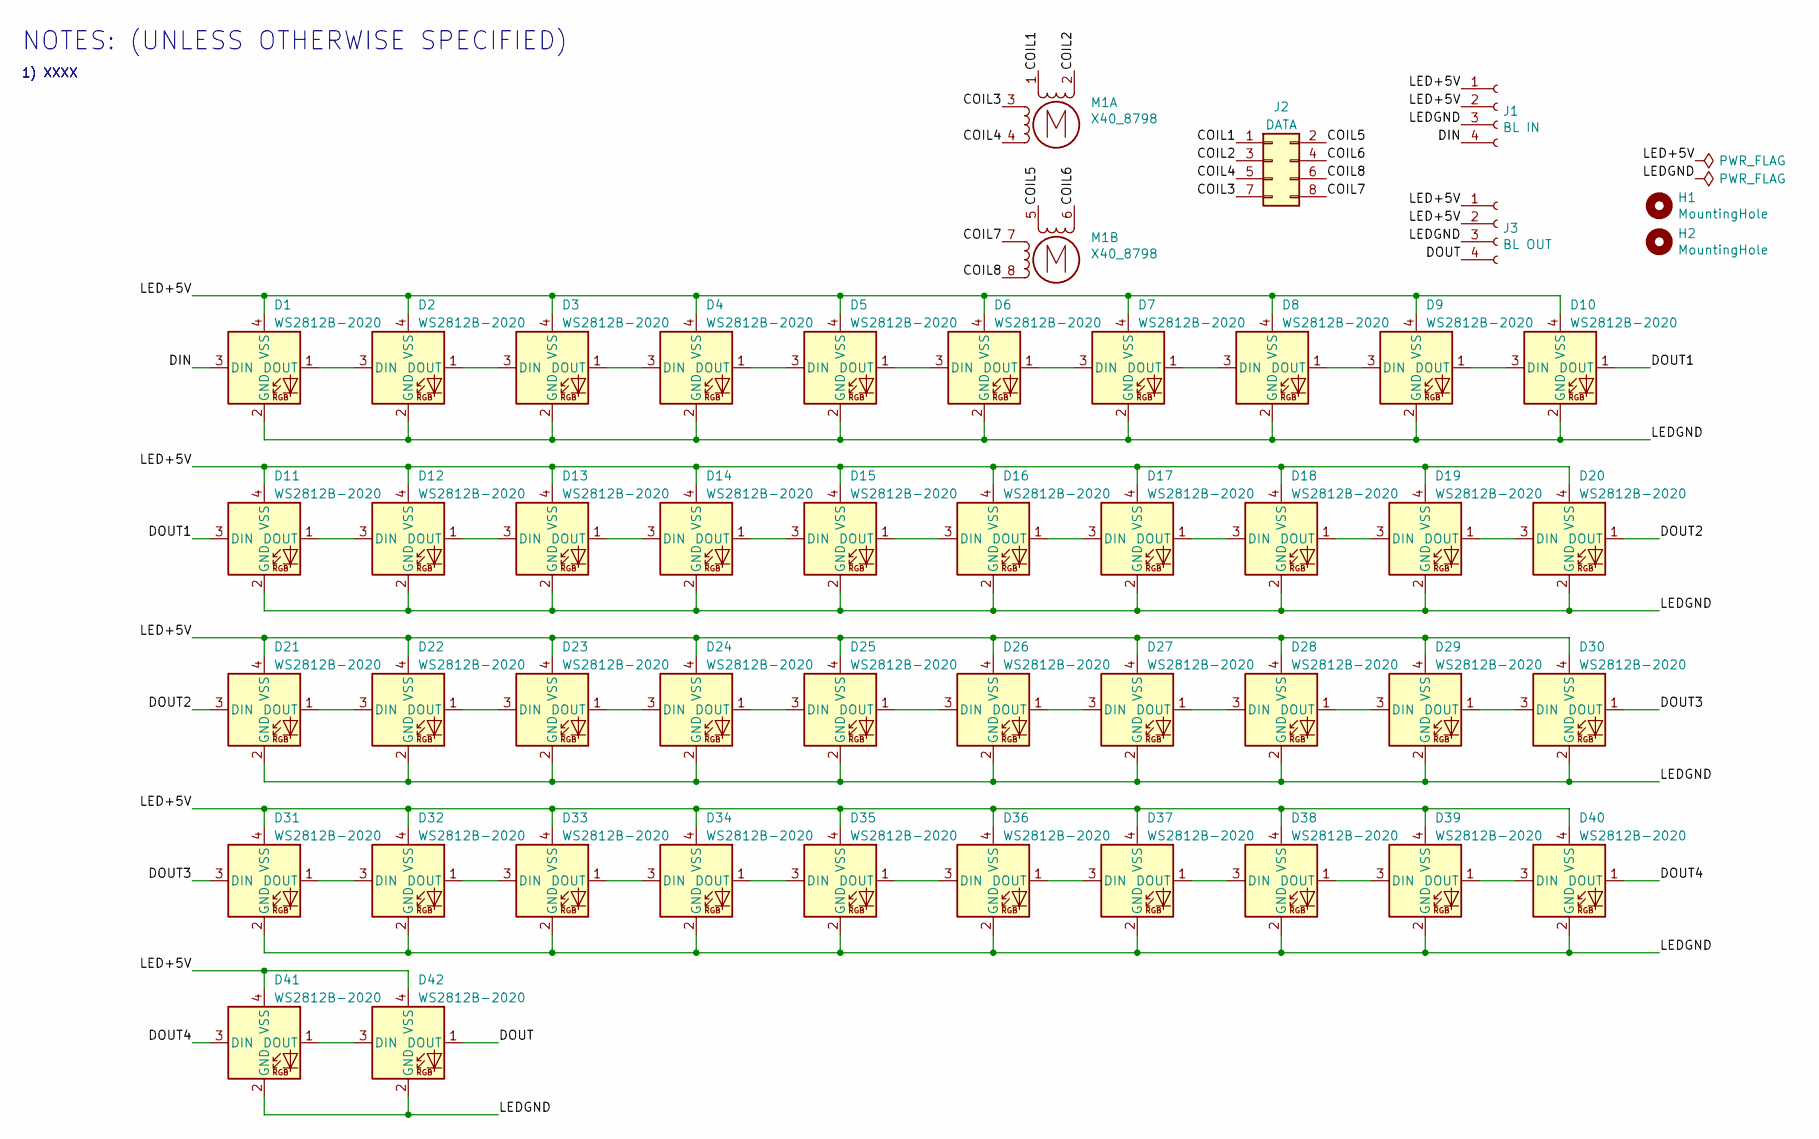
[picture p679: schematic dual_needle_gauge.sch]

Parts:
D1, D2, D3, D4, D5, D6, D7, D8, D9, D10, D11, D12, D13, D14, D15, D16, D17, D18, D19, D20, D21, D22, D23, D24, D25, D26, D27, D28, D29, D30, D31, D32, D33, D34, D35, D36, D37, D38, D39, D40, D41, D42: WS2812B-2020; WS2812-2020; LCSC C965555
H1, H2: MountingHole; MountingHole_4.5mm
J1: BL IN; Molex_Mini-Fit_Jr_5566-04A_2x02_P4.20mm_Vertical
J2: DATA; PinHeader_2x04_P2.54mm_Vertical
J3: BL OUT; Molex_Mini-Fit_Jr_5566-04A_2x02_P4.20mm_Vertical
M1: X40_8798; x40_8798

Connections:
COIL1: J2.1, M1.1
COIL2: J2.3, M1.2 (-)
COIL3: J2.7, M1.3
COIL4: J2.5, M1.4
COIL5: J2.2, M1.5
COIL6: J2.4, M1.6 (-)
COIL7: J2.8, M1.7
COIL8: J2.6, M1.8
DIN: D1.3 (DIN), J1.4
DOUT: D42.1 (DOUT), J3.4
DOUT1: D10.1 (DOUT), D11.3 (DIN)
DOUT2: D20.1 (DOUT), D21.3 (DIN)
DOUT3: D30.1 (DOUT), D31.3 (DIN)
DOUT4: D40.1 (DOUT), D41.3 (DIN)
LED+5V: D1.4 (VSS), D2.4 (VSS), D3.4 (VSS), D4.4 (VSS), D5.4 (VSS), D6.4 (VSS), D7.4 (VSS), D8.4 (VSS), D9.4 (VSS), D10.4 (VSS), D11.4 (VSS), D12.4 (VSS), D13.4 (VSS), D14.4 (VSS), D15.4 (VSS), D16.4 (VSS), D17.4 (VSS), D18.4 (VSS), D19.4 (VSS), D20.4 (VSS), D21.4 (VSS), D22.4 (VSS), D23.4 (VSS), D24.4 (VSS), D25.4 (VSS), D26.4 (VSS), D27.4 (VSS), D28.4 (VSS), D29.4 (VSS), D30.4 (VSS), D31.4 (VSS), D32.4 (VSS), D33.4 (VSS), D34.4 (VSS), D35.4 (VSS), D36.4 (VSS), D37.4 (VSS), D38.4 (VSS), D39.4 (VSS), D40.4 (VSS), D41.4 (VSS), D42.4 (VSS), J1.1, J1.2, J3.1, J3.2
LEDGND: D1.2 (GND), D2.2 (GND), D3.2 (GND), D4.2 (GND), D5.2 (GND), D6.2 (GND), D7.2 (GND), D8.2 (GND), D9.2 (GND), D10.2 (GND), D11.2 (GND), D12.2 (GND), D13.2 (GND), D14.2 (GND), D15.2 (GND), D16.2 (GND), D17.2 (GND), D18.2 (GND), D19.2 (GND), D20.2 (GND), D21.2 (GND), D22.2 (GND), D23.2 (GND), D24.2 (GND), D25.2 (GND), D26.2 (GND), D27.2 (GND), D28.2 (GND), D29.2 (GND), D30.2 (GND), D31.2 (GND), D32.2 (GND), D33.2 (GND), D34.2 (GND), D35.2 (GND), D36.2 (GND), D37.2 (GND), D38.2 (GND), D39.2 (GND), D40.2 (GND), D41.2 (GND), D42.2 (GND), J1.3, J3.3
unnamed: D1.1 (DOUT), D2.3 (DIN)
unnamed: D2.1 (DOUT), D3.3 (DIN)
unnamed: D3.1 (DOUT), D4.3 (DIN)
unnamed: D4.1 (DOUT), D5.3 (DIN)
unnamed: D5.1 (DOUT), D6.3 (DIN)
unnamed: D6.1 (DOUT), D7.3 (DIN)
unnamed: D7.1 (DOUT), D8.3 (DIN)
unnamed: D8.1 (DOUT), D9.3 (DIN)
unnamed: D9.1 (DOUT), D10.3 (DIN)
unnamed: D11.1 (DOUT), D12.3 (DIN)
unnamed: D12.1 (DOUT), D13.3 (DIN)
unnamed: D13.1 (DOUT), D14.3 (DIN)
unnamed: D14.1 (DOUT), D15.3 (DIN)
unnamed: D15.1 (DOUT), D16.3 (DIN)
unnamed: D16.1 (DOUT), D17.3 (DIN)
unnamed: D17.1 (DOUT), D18.3 (DIN)
unnamed: D18.1 (DOUT), D19.3 (DIN)
unnamed: D19.1 (DOUT), D20.3 (DIN)
unnamed: D21.1 (DOUT), D22.3 (DIN)
unnamed: D22.1 (DOUT), D23.3 (DIN)
unnamed: D23.1 (DOUT), D24.3 (DIN)
unnamed: D24.1 (DOUT), D25.3 (DIN)
unnamed: D25.1 (DOUT), D26.3 (DIN)
unnamed: D26.1 (DOUT), D27.3 (DIN)
unnamed: D27.1 (DOUT), D28.3 (DIN)
unnamed: D28.1 (DOUT), D29.3 (DIN)
unnamed: D29.1 (DOUT), D30.3 (DIN)
unnamed: D31.1 (DOUT), D32.3 (DIN)
unnamed: D32.1 (DOUT), D33.3 (DIN)
unnamed: D33.1 (DOUT), D34.3 (DIN)
unnamed: D34.1 (DOUT), D35.3 (DIN)
unnamed: D35.1 (DOUT), D36.3 (DIN)
unnamed: D36.1 (DOUT), D37.3 (DIN)
unnamed: D37.1 (DOUT), D38.3 (DIN)
unnamed: D38.1 (DOUT), D39.3 (DIN)
unnamed: D39.1 (DOUT), D40.3 (DIN)
unnamed: D41.1 (DOUT), D42.3 (DIN)

Notes on the sheet:
1) XXXX
NOTES: (UNLESS OTHERWISE SPECIFIED)
