jrsteensen/OpenHornet/ECAD/PCBs/OH_Specific/Functional/ewi_v3/ewi_v3.sch

## KiCad design ECAD/PCBs/OH_Specific/Functional/ewi_v3/ewi_v3.sch (2022-09-23)

Schematic: ewi_v3.sch

Parts:
C1: 1000 nF; CP_Elec_8x10; LCSC C134755
D1: PWR; LED_D3.0mm
D2, D3, D4, D5, D6, D7, D8, D9, D10, D11, D12, D13, D14, D15, D16, D17, D18, D19, D20, D21, D22, D23, D24, D25, D26, D27, D28, D29, D30, D31: LED; WS2812-2020; LCSC C965555
H1, H2, H3: MountingHole; MountingHole_2.5mm
J1: BL IN; Molex_Mini-Fit_Jr_5566-04A_2x02_P4.20mm_Vertical
J2: BL OUT; Molex_Mini-Fit_Jr_5566-04A_2x02_P4.20mm_Vertical
J3: SW; Molex_KK-254_AE-6410-03A_1x03_P2.54mm_Vertical; LCSC C471416
R1: R; R_0603_1608Metric
SW1: FIRE; SW_TH_Tactile_Omron_B3F-10xx
SW2: MC/APU FIRE; SW_TH_Tactile_Omron_B3F-10xx

Notes on the sheet:
NOTES: (UNLESS OTHERWISE SPECIFIED)
1) XXXX
FIRE
MASTER CAUTION/APU FIRE
GO/NO-GO & DISP/RCDRON
L/R BLEED & ---/---
SPD BRK/STBY & ---/---
L BAR/XMIT & AAA/AI
ASPJ ON & CW
L BAR/REC & SAM/---
SWITCHES
CONNECTORS
