jrsteensen/OpenHornet/ECAD/PCBs/OH_Specific/Functional/ifei/ifei.sch

## KiCad design ECAD/PCBs/OH_Specific/Functional/ifei/ifei.sch (2022-09-23)

Schematic: ifei.sch

Parts:
D1, D2, D3, D4, D5, D6, D7, D8, D9, D10, D11, D12, D13, D14, D15, D16, D17, D18, D19, D20, D21, D22, D23, D24, D25, D26, D27, D28, D29, D30, D31, D32, D33, D34, D35, D36, D37, D38, D39: LED; WS2812-2020; LCSC C965555
H1, H2, H3, H4: MountingHole; MountingHole_4.5mm
H5, H6, H7, H8: MountingHole; MountingHole_2.2mm_M2_DIN965
J1: BL IN; Molex_Mini-Fit_Jr_5566-04A_2x02_P4.20mm_Vertical
J2: BL OUT; Molex_Mini-Fit_Jr_5566-04A_2x02_P4.20mm_Vertical
J3: INPUTS; PinHeader_2x04_P2.54mm_Vertical
LOGO1: OpenHornetLogoSmall; OH_LOGO_75.4mm_11.9mm
SW1: MODE; SW_TH_Tactile_Omron_B3F-10xx
SW2: QTY; SW_TH_Tactile_Omron_B3F-10xx
SW3: UP; SW_TH_Tactile_Omron_B3F-10xx
SW4: DOWN; SW_TH_Tactile_Omron_B3F-10xx
SW5: ZONE; SW_TH_Tactile_Omron_B3F-10xx
SW6: ET; SW_TH_Tactile_Omron_B3F-10xx
