jrsteensen/OpenHornet/ECAD/PCBs/OH_Specific/Functional/jett_station_select/jett_station_select.sch

## KiCad design ECAD/PCBs/OH_Specific/Functional/jett_station_select/jett_station_select.sch (2022-09-23)

Schematic: jett_station_select.sch

Parts:
C1: 1000 nF; CP_Elec_8x10
D1: READY; LED_D3.0mm
D2, D3, D4, D5, D6, D7, D8, D9, D10, D11, D12, D13, D14, D15, D16, D17, D18, D19, D20, D21, D22, D23, D24, D25, D26, D27, D28, D29, D30, D31, D32, D33: LED; WS2812-2020; LCSC C965555
H1, H2, H3: MountingHole; MountingHole_2.5mm
J1: BL IN; Molex_Mini-Fit_Jr_5566-04A_2x02_P4.20mm_Vertical
J2: BL OUT; Molex_Mini-Fit_Jr_5566-04A_2x02_P4.20mm_Vertical
J3: INPUTS; PinHeader_2x03_P2.54mm_Vertical
LOGO1: OpenHornetLogoSmall; OH_LOGO_ONLY_11x6mm
R1: R; R_0603_1608Metric; LCSC C23138
SW1: CTR; SW_TH_Tactile_Omron_B3F-10xx
SW2: LI; SW_TH_Tactile_Omron_B3F-10xx
SW3: RI; SW_TH_Tactile_Omron_B3F-10xx
SW4: LO; SW_TH_Tactile_Omron_B3F-10xx
SW5: RO; SW_TH_Tactile_Omron_B3F-10xx
