jrsteensen/OpenHornet/ECAD/PCBs/OH_Specific/Functional/ralt_controller/ralt_controller.sch

## KiCad design ECAD/PCBs/OH_Specific/Functional/ralt_controller/ralt_controller.sch (2022-09-23)

Schematic: ralt_controller.sch

Parts:
C1: 0.1uF; C_0805_2012Metric; LCSC C49678
J1: BUS IN; Molex_Mini-Fit_Jr_5566-06A2_2x03_P4.20mm_Vertical
J2: BUS OUT; Molex_Mini-Fit_Jr_5566-06A2_2x03_P4.20mm_Vertical
J3: BL IN; Molex_Mini-Fit_Jr_5566-04A_2x02_P4.20mm_Vertical
J4: BL OUT; Molex_Mini-Fit_Jr_5566-04A_2x02_P4.20mm_Vertical
J5: STEPPER; PinHeader_2x05_P2.54mm_Vertical
J13: GRN_LED; PinHeader_1x02_P2.54mm_Vertical
J14: RED_LED; PinHeader_1x02_P2.54mm_Vertical
J15: OFF_SERVO; PinHeader_1x03_P2.54mm_Vertical
J16: PUSH; PinHeader_1x02_P2.54mm_Vertical
J17: POT; PinHeader_1x03_P2.54mm_Vertical
JP1: BL_DIN_SEL; PinHeader_1x03_P2.54mm_Vertical
JP2: BL_DOUT_SEL; PinHeader_1x03_P2.54mm_Vertical
MK1, MK2, MK3: MH; MountingHole_2.5mm
R1, R2: 120; R_0805_2012Metric; LCSC C17437
U0: ProMicro; DIP-24_W15.24mm_Socket; LCSC C72120
U1: MAX487EESA+T; SOIC-8_3.9x4.9mm_P1.27mm; LCSC C116539

Notes on the sheet:
RS485 BUS CONTROLLER
ABSIS BUS CONNECTORS
TEST POINTS
PWR FLAGS
1) BL DATA SELECT: PLACE JUMPER OVER PINS 1 & 2 OF JP1/JP2 TO SELECT DATA INPUT FROM BACKLIGHTING BUS. PLACE JUMPER OVER PINS 2 & 3 OF JP2/JP3 TO SELECT DATA FROM THE STANDBY CONTROLLER MCU.
NOTES: (UNLESS OTHERWISE SPECIFIED)
MOUNT HOLES
BL CONNECTORS
USB SHOULD BE ACCESSIBLE FOR PROGRAMMING
COIL1
LED_DIN
LED_DOUT
COIL4
COIL3
COIL2
