jrsteensen/OpenHornet/ECAD/PCBs/OH_Specific/Functional/standby_airspeed_vvi/standby_airspeed_vvi.sch

## KiCad design ECAD/PCBs/OH_Specific/Functional/standby_airspeed_vvi/standby_airspeed_vvi.sch (2022-09-23)

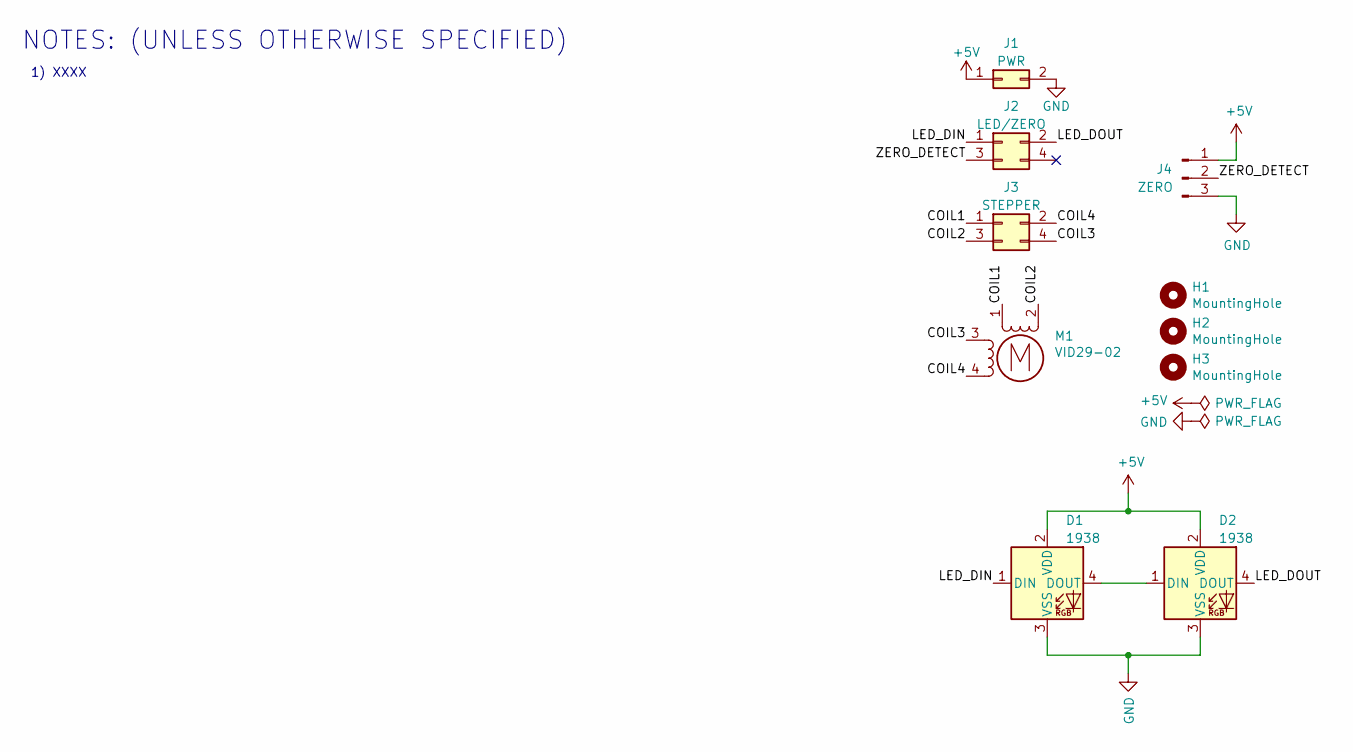
[picture p680: schematic standby_airspeed_vvi.sch]

Parts:
D1, D2: 1938; LED_D5.0mm-4_RGB
H1, H2, H3: MountingHole; MountingHole_2.5mm
J1: PWR; PinHeader_2x01_P2.54mm_Vertical
J2: LED/ZERO; PinHeader_2x02_P2.54mm_Vertical
J3: STEPPER; PinHeader_2x02_P2.54mm_Vertical
J4: ZERO; PinHeader_1x03_P2.54mm_Vertical
M1: VID29-02

Connections:
+5V: D1.2 (VDD), D2.2 (VDD), J1.1, J4.1
COIL1: J3.1, M1.1
COIL2: J3.3, M1.2 (-)
COIL3: J3.4, M1.3
COIL4: J3.2, M1.4
GND: D1.3 (VSS), D2.3 (VSS), J1.2, J4.3
LED_DIN: D1.1 (DIN), J2.1
LED_DOUT: D2.4 (DOUT), J2.2
unnamed: D1.4 (DOUT), D2.1 (DIN)
ZERO_DETECT: J2.3, J4.2

Notes on the sheet:
NOTES: (UNLESS OTHERWISE SPECIFIED)
1) XXXX
