jrsteensen/OpenHornet/ECAD/PCBs/OH_Specific/Functional/standby_altimeter/standby_altimeter.sch

## KiCad design ECAD/PCBs/OH_Specific/Functional/standby_altimeter/standby_altimeter.sch (2022-09-23)

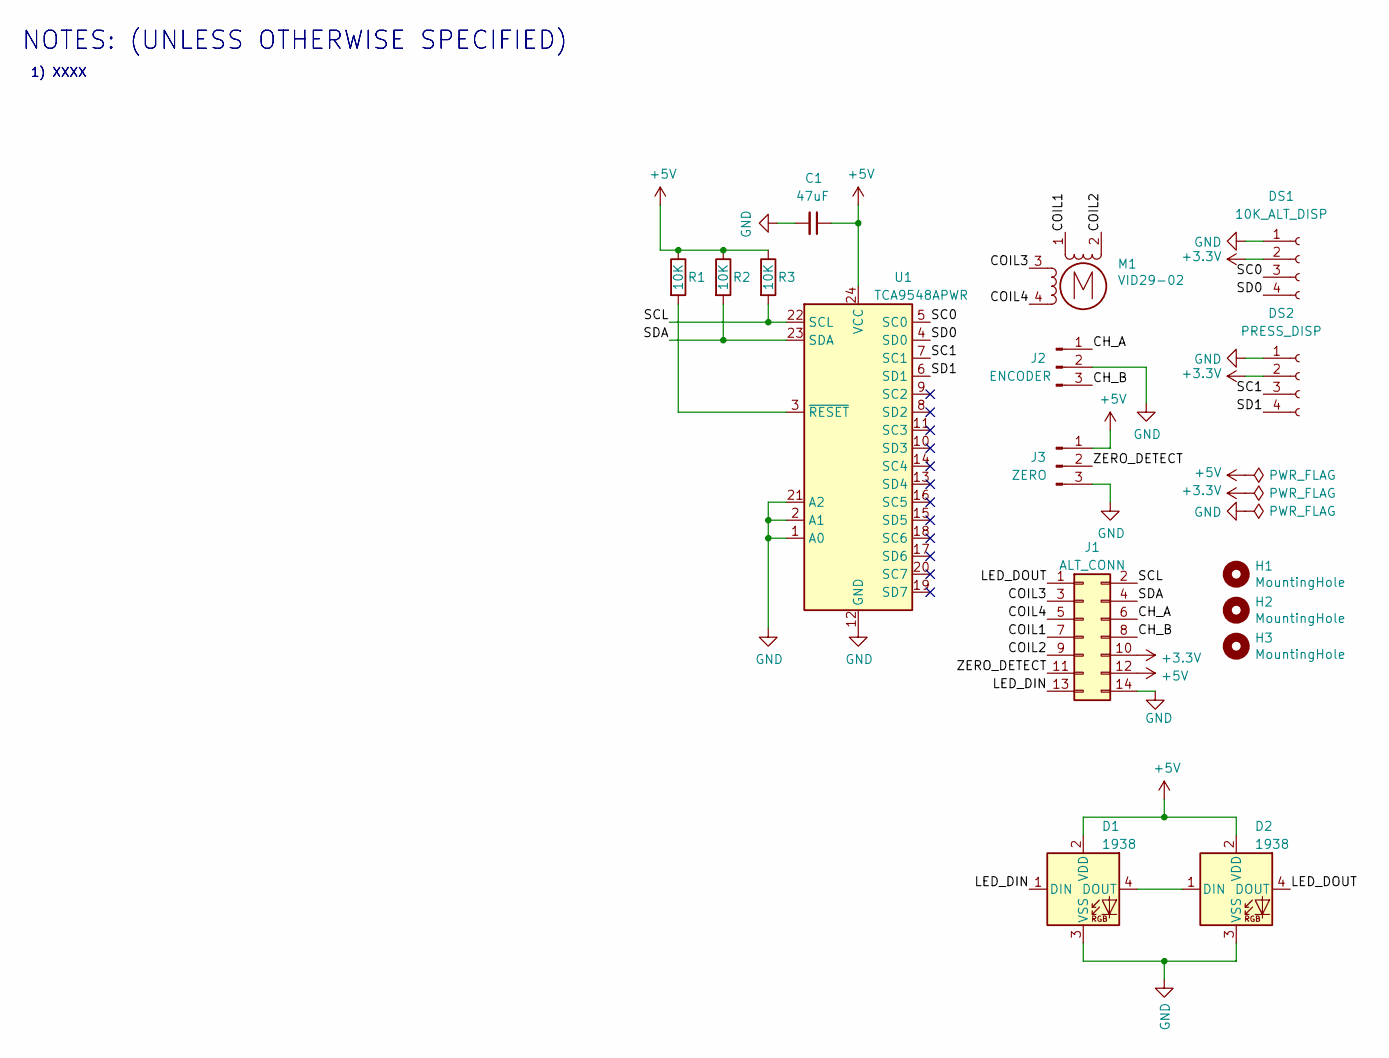
[picture p681: schematic standby_altimeter.sch]

Parts:
C1: 47uF; C_1206_3216Metric; LCSC C96123
D1, D2: 1938; LED_D5.0mm-4_RGB
DS1: 10K_ALT_DISP; PinSocket_1x04_P2.54mm_Vertical
DS2: PRESS_DISP; PinSocket_1x04_P2.54mm_Vertical
H1, H2, H3: MountingHole; MountingHole_2.5mm
J1: ALT_CONN; PinHeader_2x07_P2.54mm_Vertical
J2: ENCODER; PinHeader_1x03_P2.54mm_Vertical
J3: ZERO; PinHeader_1x03_P2.54mm_Vertical
M1: VID29-02
R1, R2, R3: 10K; R_0603_1608Metric; LCSC C25804
U1: TCA9548APWR; TSSOP-24_4.4x7.8mm_P0.65mm; LCSC C130026

Connections:
+3.3V: DS1.2, DS2.2, J1.10
+5V: C1.1, D1.2 (VDD), D2.2 (VDD), J1.12, J3.1, R1.1, R2.1, R3.1, U1.24 (VCC)
CH_A: J1.6, J2.1
CH_B: J1.8, J2.3
COIL1: J1.7, M1.1
COIL2: J1.9, M1.2 (-)
COIL3: J1.3, M1.3
COIL4: J1.5, M1.4
GND: C1.2, D1.3 (VSS), D2.3 (VSS), DS1.1, DS2.1, J1.14, J2.2, J3.3, U1.1 (A0), U1.2 (A1), U1.12 (GND), U1.21 (A2)
LED_DIN: D1.1 (DIN), J1.13
LED_DOUT: D2.4 (DOUT), J1.1
unnamed: D1.4 (DOUT), D2.1 (DIN)
unnamed: R1.2, U1.3 (~RESET)
SC0: DS1.3, U1.5 (SC0)
SC1: DS2.3, U1.7 (SC1)
SCL: J1.2, R3.2, U1.22 (SCL)
SD0: DS1.4, U1.4 (SD0)
SD1: DS2.4, U1.6 (SD1)
SDA: J1.4, R2.2, U1.23 (SDA)
ZERO_DETECT: J1.11, J3.2

Notes on the sheet:
NOTES: (UNLESS OTHERWISE SPECIFIED)
1) XXXX
