jrsteensen/OpenHornet/ECAD/PCBs/OH_Specific/Functional/standby_controller/standby_controller.sch

## KiCad design ECAD/PCBs/OH_Specific/Functional/standby_controller/standby_controller.sch (2022-09-23)

Schematic: standby_controller.sch

Parts:
C1: 0.1uF; C_0805_2012Metric_Pad1.15x1.40mm_HandSolder; LCSC C49678
H1, H2, H3, H4: MountingHole; MountingHole_2.5mm
J1: BUS IN; Molex_Mini-Fit_Jr_5569-06A1_2x03_P4.20mm_Horizontal
J2: BUS OUT; Molex_Mini-Fit_Jr_5569-06A1_2x03_P4.20mm_Horizontal
J3: BL IN; Molex_Mini-Fit_Jr_5566-04A_2x02_P4.20mm_Vertical
J4: BL OUT; Molex_Mini-Fit_Jr_5566-04A_2x02_P4.20mm_Vertical
J5: AIRSPEED; PinHeader_2x05_P2.54mm_Vertical
J6: ALTIMETER; PinHeader_2x07_P2.54mm_Vertical
J7: VVI; PinHeader_2x05_P2.54mm_Vertical
J8: RWR_BRT; PinHeader_1x03_P2.54mm_Vertical
J9: SARI_CAGE; PinHeader_1x05_P2.54mm_Vertical
J10: SARI_TEST; PinHeader_1x02_P2.54mm_Vertical
JP1: BL_DIN_SEL; PinHeader_1x03_P2.54mm_Vertical
JP2: BL_DOUT_SEL; PinHeader_1x03_P2.54mm_Vertical
MK1, MK2, MK3, MK4: MH; Arduino_1pin
P1: PWM; PinHeader_1x10_P2.54mm_Vertical
P2: Power; PinHeader_1x08_P2.54mm_Vertical
P3, P5: Analog; PinHeader_1x08_P2.54mm_Vertical
P4: PWM; PinHeader_1x08_P2.54mm_Vertical
P6: Communication; PinHeader_1x08_P2.54mm_Vertical
P7: Digital; PinHeader_2x18_P2.54mm_Vertical
TP1: TP-12; TestPoint_THTPad_D1.5mm_Drill0.7mm
TP2: TP-5V; TestPoint_THTPad_D1.5mm_Drill0.7mm
TP3: TP-3.3V; TestPoint_THTPad_D1.5mm_Drill0.7mm
TP4: TP-GND; TestPoint_THTPad_D1.5mm_Drill0.7mm
TP5: TP-A; TestPoint_THTPad_D1.5mm_Drill0.7mm
TP6: TP-B; TestPoint_THTPad_D1.5mm_Drill0.7mm
U1: MAX487EESA+T; SOIC-8_3.9x4.9mm_P1.27mm; LCSC C116539

Notes on the sheet:
RS485 BUS CONTROLLER
ABSIS BUS CONNECTORS
TEST POINTS
PWR FLAGS
1) ARDUINO MEGA PROGRAMMING: REMOVE ARDUINO MEGA FROM STANDBY CONTROLLER PCB PRIOR TO PROGRAMMING MEGA VIA USB. 2) RS485 BUS TERMINATION: DO NOT INSTALL J2 (BUS OUT) CONNECTOR AND ADD A 120OHM THRU-HOLE RESISTOR ACROSS PINS 4&5 OF J2 (BUS OUT) ON LAST ABSIS NANO OF RS485 BUS. 3) BL DATA SELECT: PLA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
NOTES: (UNLESS OTHERWISE SPECIFIED)
MOUNT HOLES
ARDUINO MEGA REV3
BL CONNECTORS
