jrsteensen/OpenHornet/ECAD/PCBs/OH_Specific/Functional/stick_controller/stick_controller.sch

## KiCad design ECAD/PCBs/OH_Specific/Functional/stick_controller/stick_controller.sch (2022-09-23)

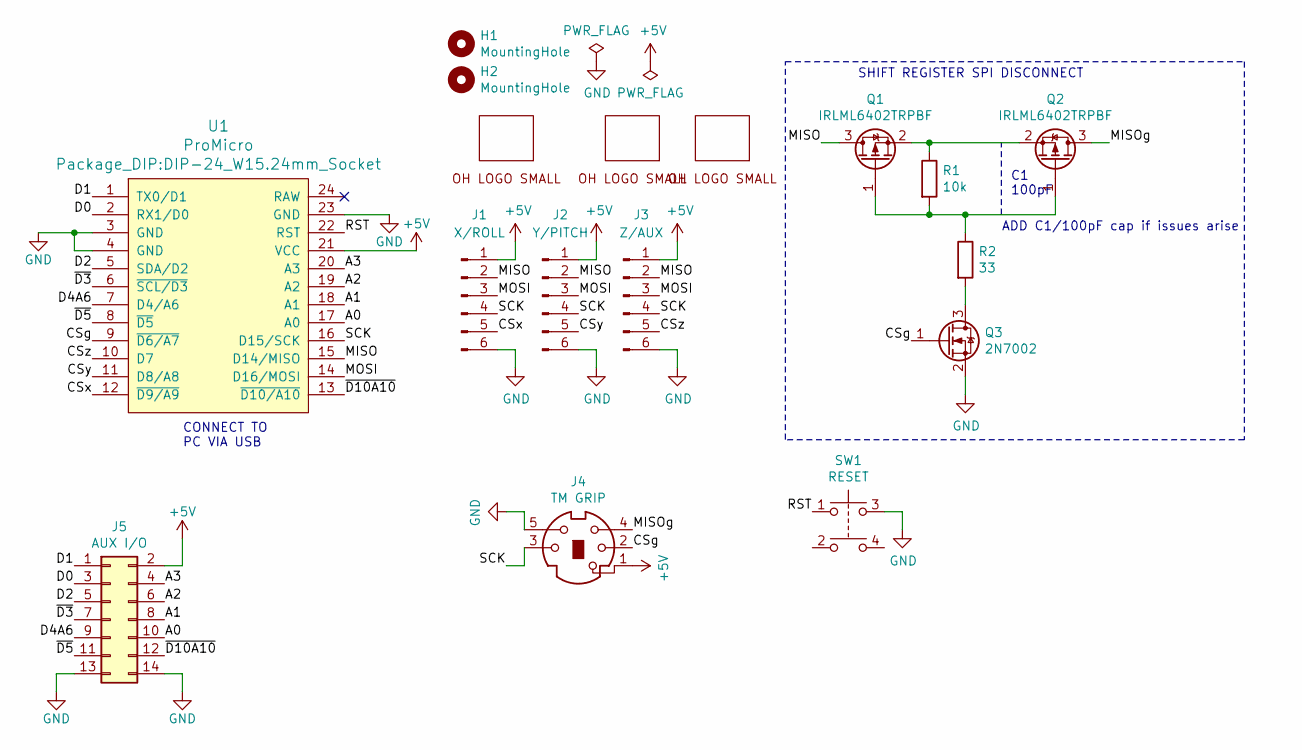
[picture p682: schematic stick_controller.sch]

Parts:
H1, H2: MountingHole; MountingHole_2.5mm
J1: X/ROLL; JST_PH_S6B-PH-K_1x06_P2.00mm_Horizontal; LCSC C265105
J2: Y/PITCH; JST_PH_S6B-PH-K_1x06_P2.00mm_Horizontal; LCSC C265105
J3: Z/AUX; JST_PH_S6B-PH-K_1x06_P2.00mm_Horizontal; LCSC C265105
J4: TM GRIP; JST_PH_S5B-PH-K_1x05_P2.00mm_Horizontal; LCSC C157923
J5: AUX I/O; PinHeader_2x07_P2.54mm_Vertical
LOGO1: OpenHornetLogoSmall; OH_LOGO_37.7mm_5.9mm
LOGO2: OpenHornetLogoSmall; CC-BY-NC-SA-Small
LOGO3: OpenHornetLogoSmall; OH_LOGO_ONLY_11x6mm
Q1, Q2: IRLML6402TRPBF; SOT-23; LCSC C2593
Q3: 2N7002; SOT-23; LCSC C8545
R1: 10k; R_0603_1608Metric; LCSC C25804
R2: 33; R_0402_1005Metric; LCSC C25105
SW1: RESET; SMD-SW-4_5.1x5.1; LCSC C318884
U1: ProMicro; DIP-24_W15.24mm_Socket; LCSC C72120

Connections:
+5V: J1.1, J2.1, J3.1, J4.1, J5.2, U1.21 (VCC)
A0: J5.10, U1.17 (A0)
A1: J5.8, U1.18 (A1)
A2: J5.6, U1.19 (A2)
A3: J5.4, U1.20 (A3)
CSg: J4.2, Q3.1 (G), U1.9 (~D6/A7)
CSx: J1.5, U1.12 (~D9/A9)
CSy: J2.5, U1.11 (D8/A8)
CSz: J3.5, U1.10 (D7)
D0: J5.3, U1.2 (RX1/D0)
D1: J5.1, U1.1 (TX0/D1)
D2: J5.5, U1.5 (SDA/D2)
D4A6: J5.9, U1.7 (D4/A6)
GND: J1.6, J2.6, J3.6, J4.5, J5.13, J5.14, Q3.2 (S), SW1.3, U1.3 (GND), U1.4 (GND), U1.23 (GND)
MISO: J1.2, J2.2, J3.2, Q1.3 (D), U1.15 (D14/MISO)
MISOg: J4.4, Q2.3 (D)
MOSI: J1.3, J2.3, J3.3, U1.14 (D16/MOSI)
unnamed: Q1.1 (G), Q2.1 (G), R1.2, R2.1
unnamed: Q1.2 (S), Q2.2 (S), R1.1
unnamed: Q3.3 (D), R2.2
RST: SW1.1, U1.22 (RST)
SCK: J1.4, J2.4, J3.4, J4.3, U1.16 (D15/SCK)
~D3: J5.7, U1.6 (~SCL/D3)
~D5: J5.11, U1.8 (~D5)
~D10A10: J5.12, U1.13 (~D10/A10)

Notes on the sheet:
CONNECT TO PC VIA USB
ADD C1/100pF cap if issues arise
C1 100pF
SHIFT REGISTER SPI DISCONNECT
