jrsteensen/OpenHornet/ECAD/PCBs/OH_Specific/Functional/throttle_controller/throttle_controller.sch

## KiCad design ECAD/PCBs/OH_Specific/Functional/throttle_controller/throttle_controller.sch (2022-09-23)

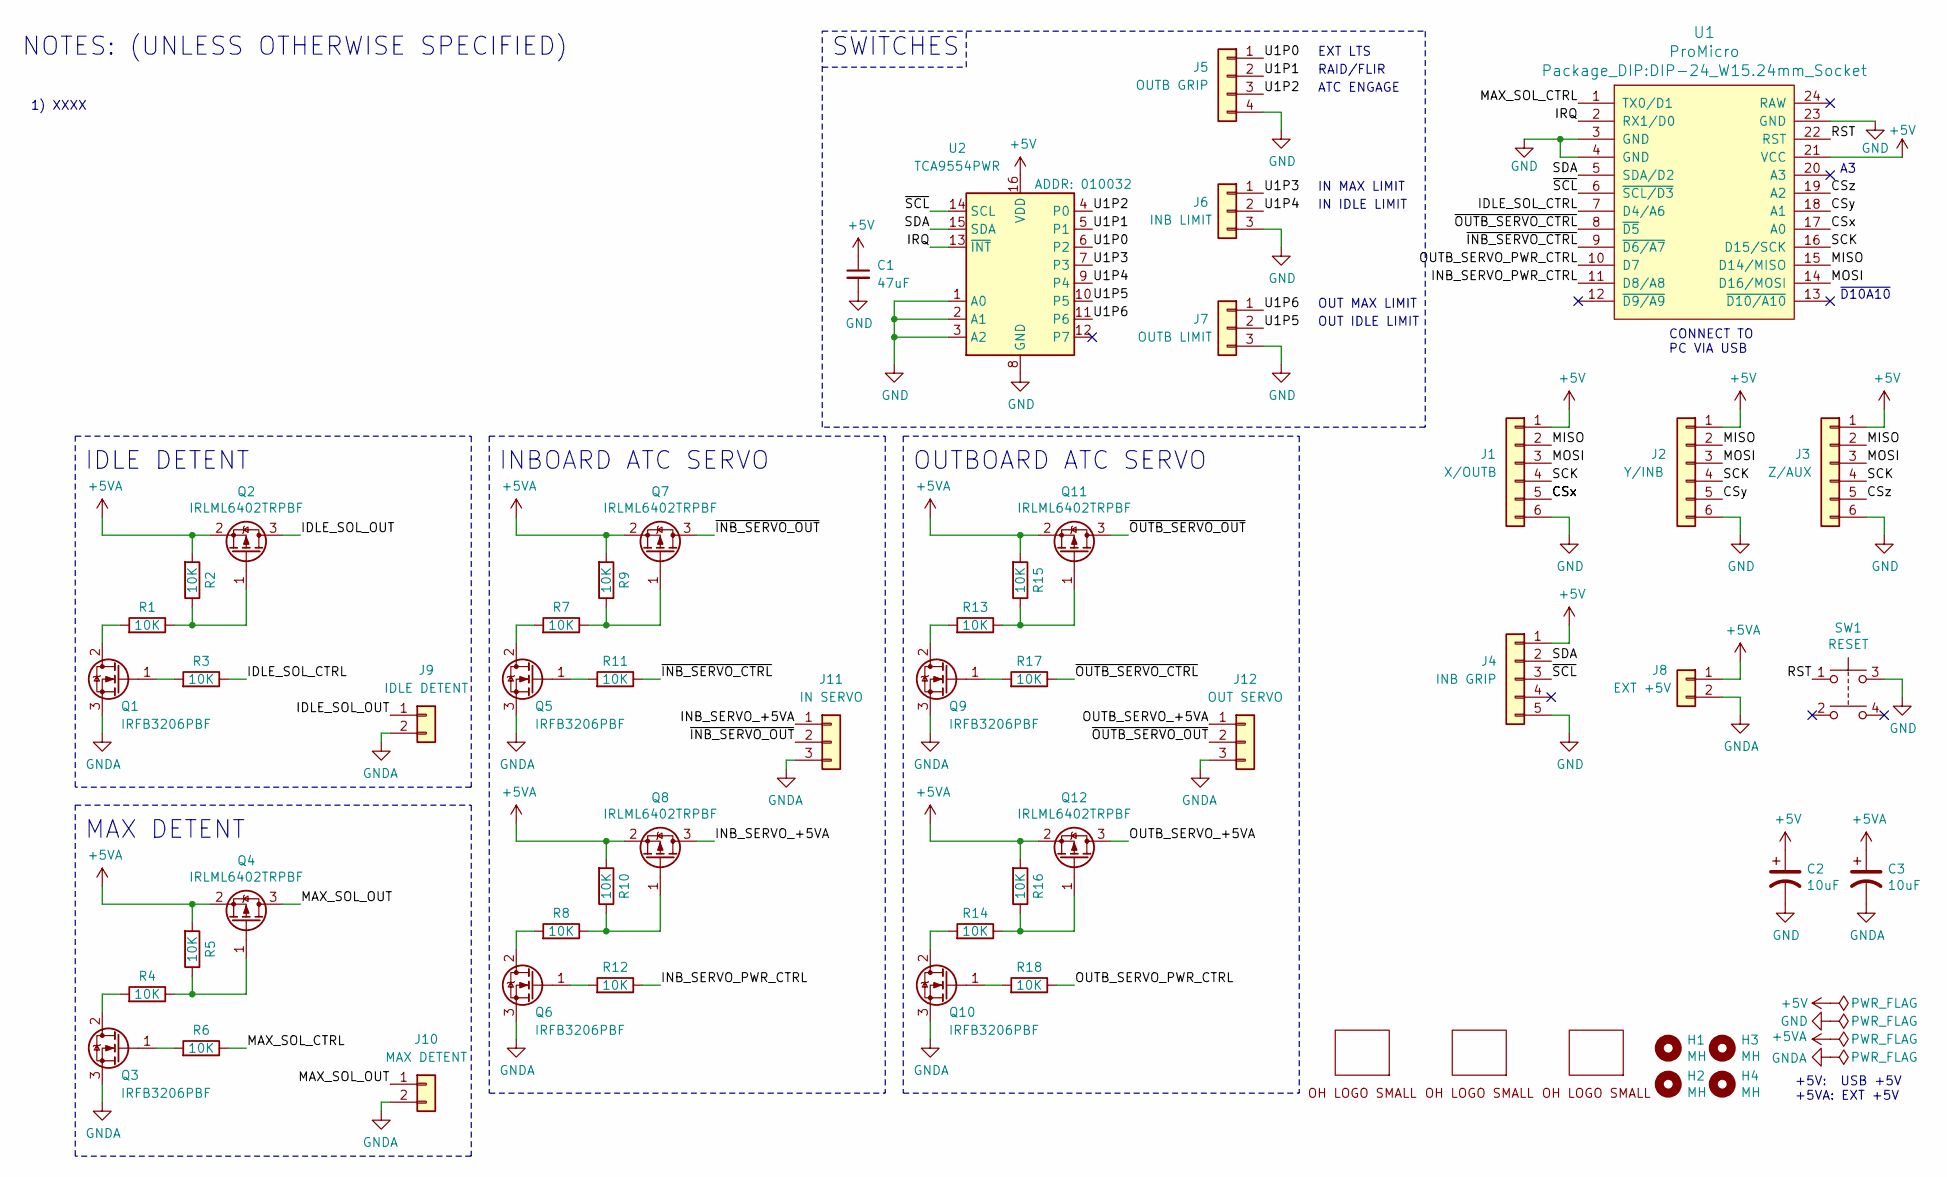
[picture p683: schematic throttle_controller.sch]

Parts:
C1: 47uF; C_1206_3216Metric; LCSC C96123
C2, C3: 10uF; C_1206_3216Metric; LCSC C13585
H1, H2, H3, H4: MH; MountingHole_2.5mm
J1: X/OUTB; JST_PH_S6B-PH-K_1x06_P2.00mm_Horizontal; LCSC C265105
J2: Y/INB; JST_PH_S6B-PH-K_1x06_P2.00mm_Horizontal; LCSC C265105
J3: Z/AUX; JST_PH_S6B-PH-K_1x06_P2.00mm_Horizontal; LCSC C265105
J4: INB GRIP; JST_PH_B5B-PH-K_1x05_P2.00mm_Vertical
J5: OUTB GRIP; JST_PH_B4B-PH-K_1x04_P2.00mm_Vertical
J6: INB LIMIT; JST_PH_B3B-PH-K_1x03_P2.00mm_Vertical
J7: OUTB LIMIT; JST_PH_B3B-PH-K_1x03_P2.00mm_Vertical
J8: EXT +5V; JST_PH_B2B-PH-K_1x02_P2.00mm_Vertical
J9: IDLE DETENT; JST_PH_B2B-PH-K_1x02_P2.00mm_Vertical
J10: MAX DETENT; JST_PH_B2B-PH-K_1x02_P2.00mm_Vertical
J11: IN SERVO; JST_PH_B3B-PH-K_1x03_P2.00mm_Vertical
J12: OUT SERVO; JST_PH_B3B-PH-K_1x03_P2.00mm_Vertical
LOGO1: OpenHornetLogoSmall; OH_LOGO_37.7mm_5.9mm
LOGO2: OpenHornetLogoSmall; CC-BY-NC-SA-Small
LOGO3: OpenHornetLogoSmall; OH_LOGO_ONLY_11x6mm
Q1, Q3, Q5, Q6, Q9, Q10: IRFB3206PBF; TO-220-3_Vertical; LCSC C2642
Q2, Q4, Q7, Q8, Q11, Q12: IRLML6402TRPBF; SOT-23; LCSC C2593
R1, R2, R3, R4, R5, R6, R7, R8, R9, R10, R11, R12, R13, R14, R15, R16, R17, R18: 10K; R_0603_1608Metric_Pad0.98x0.95mm_HandSolder; LCSC C25804
SW1: RESET; SMD-SW-4_5.1x5.1; LCSC C318884
U1: ProMicro; DIP-24_W15.24mm_Socket; LCSC C72120
U2: TCA9554PWR; TSSOP-16_4.4x5mm_P0.65mm; LCSC C477924

Connections:
+5V: C1.1, C2.1, J1.1, J2.1, J3.1, J4.1, U1.21 (VCC), U2.16 (VDD)
+5VA: C3.1, J8.1, Q2.2 (S), Q4.2 (S), Q7.2 (S), Q8.2 (S), Q11.2 (S), Q12.2 (S), R2.2, R5.2, R9.2, R10.2, R15.2, R16.2
CSx: J1.5, U1.17 (A0)
CSy: J2.5, U1.18 (A1)
CSz: J3.5, U1.19 (A2)
GND: C1.2, C2.2, J1.6, J2.6, J3.6, J4.5, J5.4, J6.3, J7.3, SW1.3, U1.3 (GND), U1.4 (GND), U1.23 (GND), U2.1 (A0), U2.2 (A1), U2.3 (A2), U2.8 (GND)
GNDA: C3.2, J8.2, J9.2, J10.2, J11.3, J12.3, Q1.3 (S), Q3.3 (S), Q5.3 (S), Q6.3 (S), Q9.3 (S), Q10.3 (S)
IDLE_SOL_CTRL: R3.1, U1.7 (D4/A6)
IDLE_SOL_OUT: J9.1, Q2.3 (D)
INB_SERVO_+5VA: J11.1, Q8.3 (D)
INB_SERVO_PWR_CTRL: R12.1, U1.11 (D8/A8)
IRQ: U1.2 (RX1/D0), U2.13 (~INT~)
MAX_SOL_CTRL: R6.1, U1.1 (TX0/D1)
MAX_SOL_OUT: J10.1, Q4.3 (D)
MISO: J1.2, J2.2, J3.2, U1.15 (D14/MISO)
MOSI: J1.3, J2.3, J3.3, U1.14 (D16/MOSI)
unnamed: Q1.1 (G), R3.2
unnamed: Q1.2 (D), R1.2
unnamed: Q2.1 (G), R1.1, R2.1
unnamed: Q3.1 (G), R6.2
unnamed: Q3.2 (D), R4.2
unnamed: Q4.1 (G), R4.1, R5.1
unnamed: Q5.1 (G), R11.2
unnamed: Q5.2 (D), R7.2
unnamed: Q6.1 (G), R12.2
unnamed: Q6.2 (D), R8.2
unnamed: Q7.1 (G), R7.1, R9.1
unnamed: Q8.1 (G), R8.1, R10.1
unnamed: Q9.1 (G), R17.2
unnamed: Q9.2 (D), R13.2
unnamed: Q10.1 (G), R18.2
unnamed: Q10.2 (D), R14.2
unnamed: Q11.1 (G), R13.1, R15.1
unnamed: Q12.1 (G), R14.1, R16.1
OUTB_SERVO_+5VA: J12.1, Q12.3 (D)
OUTB_SERVO_PWR_CTRL: R18.1, U1.10 (D7)
RST: SW1.1, U1.22 (RST)
SCK: J1.4, J2.4, J3.4, U1.16 (D15/SCK)
SDA: J4.2, U1.5 (SDA/D2), U2.15 (SDA)
U1P0: J5.1, U2.6 (P2)
U1P1: J5.2, U2.5 (P1)
U1P2: J5.3, U2.4 (P0)
U1P3: J6.1, U2.7 (P3)
U1P4: J6.2, U2.9 (P4)
U1P5: J7.2, U2.10 (P5)
U1P6: J7.1, U2.11 (P6)
~INB_SERVO_CTRL: R11.1, U1.9 (~D6/A7)
~INB_SERVO_OUT: J11.2, Q7.3 (D)
~OUTB_SERVO_CTRL: R17.1, U1.8 (~D5)
~OUTB_SERVO_OUT: J12.2, Q11.3 (D)
~SCL: J4.3, U1.6 (~SCL/D3), U2.14 (SCL)

Notes on the sheet:
CONNECT TO PC VIA USB
OUT IDLE LIMIT
OUT MAX LIMIT
IN IDLE LIMIT
IN MAX LIMIT
ATC ENGAGE
RAID/FLIR
EXT LTS
+5V: USB +5V +5VA: EXT +5V
NOTES: (UNLESS OTHERWISE SPECIFIED)
IDLE DETENT
MAX DETENT
INBOARD ATC SERVO
OUTBOARD ATC SERVO
SWITCHES
~D10A10
1) XXXX
