jrsteensen/OpenHornet/ECAD/PCBs/OH_Specific/Functional/ufc_v5_ap/ufc_v5_ap.sch

## KiCad design ECAD/PCBs/OH_Specific/Functional/ufc_v5_ap/ufc_v5_ap.sch (2022-09-23)

Schematic: ufc_v5_ap.sch

Parts:
C1: .1uF; C_0603_1608Metric; LCSC C14663
H1, H2: MountingHole_3.2mm_M3_DIN965
J1: TO UFC; PinHeader_1x04_P2.54mm_Vertical
R1: 33; R_0402_1005Metric; LCSC C25105
RN1, RN2: 4.7K; R_Array_Convex_4x0603; LCSC C1980
SW1, SW2, SW3, SW4, SW5, SW6, SW7: TL1240GQ
U1: AW9523BTQR; WQFN-24-1EP_4x4mm_P0.5mm_EP2.6x2.6mm

Notes on the sheet:
NOTES: (UNLESS OTHERWISE SPECIFIED)
1) XXXX
A/P SW
IFF SW
TCN SW
ILS SW
D/L SW
BCN SW
ON/OFF SW
