jrsteensen/OpenHornet/ECAD/PCBs/OH_Specific/Functional/ufc_v5_main/ufc_v5_main.sch

## KiCad design ECAD/PCBs/OH_Specific/Functional/ufc_v5_main/ufc_v5_main.sch (2022-09-23)

Schematic: ufc_v5_main.sch

Parts:
BL1: UFCScratchPadBacklight; SCRATCHPADBACKLIGHT
C1, C2, C3, C4: 10uF; C_0805_2012Metric; LCSC C15850
C7, C8, C9, C10, C11, C12: .1uF; C_0603_1608Metric; LCSC C14663
D1, D2, D3, D4, D5, D6, D7, D8, D9, D10, D11, D12, D13, D14, D15, D16, D17, D18, D19, D20, D21, D22, D23, D24, D25, D26, D27, D28, D29, D30, D31, D32, D33, D34, D35, D36: LED_0402_1005Metric; LCSC C130723
DS1: UFCScratchpadLCD; SCRATCHPADLCD
DS2, DS3, DS4, DS5, DS6: UFCOptionDigit
DS7, DS8: UFCSingleDigit
J1: +5VIN; PinHeader_1x02_P2.54mm_Vertical
J2: ENC1; PinHeader_1x04_P2.54mm_Vertical
J3: VOL1; PinHeader_1x03_P2.54mm_Vertical
J4: BRT; PinHeader_1x03_P2.54mm_Vertical
J5: AP KB; PinHeader_1x04_P2.54mm_Vertical
J6: HUD BIT; PinHeader_1x04_P2.54mm_Vertical
J7: ENC2; PinHeader_1x04_P2.54mm_Vertical
J8: VOL2; PinHeader_1x03_P2.54mm_Vertical
J9: ADF SW; PinHeader_1x03_P2.54mm_Vertical
MC1: S2_MINI
MK1, MK2, MK3, MK4: MH; MountingHole_4.3mm_M4
MK5: SW_ADF; MountingHole_6.4mm_M6
POT1: VOL1; BR10K_Pot_11mm_x_11mm
POT2: VOL2; BR10K_Pot_11mm_x_11mm
POT3: BRT; BR10K_Pot_11mm_x_11mm
R1, R36, R38: 1k; R_0603_1608Metric; LCSC C21190
R2: 10K; R_0603_1608Metric; LCSC C25804
R3, R37, R39: 2K; R_0603_1608Metric; LCSC C22975
R4, R5, R6, R7, R8, R9, R10, R11, R12, R13, R14, R15, R19, R20, R21, R22, R23, R24, R25, R26, R27, R28, R29, R30, R31, R32, R33, R34, R35, R40, R41, R42: 4.7k; R_0603_1608Metric; LCSC C23162
R16, R17, R18: 33; R_0402_1005Metric; LCSC C25105
R43, R44: 68; R_0603_1608Metric; LCSC C27592
SW1, SW2, SW3, SW4, SW5, SW6, SW7, SW8, SW9, SW10, SW11, SW12, SW13, SW14, SW15, SW16, SW17, SW18, SW19: TL1240GQ
TP1: 5V; TestPoint_THTPad_D1.5mm_Drill0.7mm
TP2: GND; TestPoint_THTPad_D1.5mm_Drill0.7mm
TP3: SCL; TestPoint_THTPad_D1.5mm_Drill0.7mm
TP4: SDA; TestPoint_THTPad_D1.5mm_Drill0.7mm
U1: HT1621B; LQFP-48_7x7mm_P0.5mm; LCSC C7532
U2, U3, U4, U5: GN1640T; SSOP-28_3.9x9.9mm_P0.635mm; LCSC C2758330
U6, U7: AW9523BTQR; WQFN-24-1EP_4x4mm_P0.5mm_EP2.6x2.6mm
U8, U9: TXS0108EPW; TSSOP-20_4.4x6.5mm_P0.65mm

Notes on the sheet:
CONNECTORS
MOUNT HOLES
PWR FLAGS
TEST POINTS
ILLUMINATED TACT SWITCHES
NOTES: (UNLESS OTHERWISE SPECIFIED)
1) XXXX
EXTERNAL SWITCH/POT MOUNTING HOLES
COMM 1/2 DISPLAYS
OPTION DISPLAYS
CREATE FOOTPRINT FOR S2 MINI ADD HEADER FOR HUD PANEL (MAYBE?) ADD AW9523BTQR TO AP KB.
SCRATCHPAD
GPIO EXPANDERS
BACKLIGHTING LEDS
ANALOG LEVEL SHIFTERS (5V->3.3V)
DIGITAL LEVEL SHIFTERS (5V->3.3V)
MICROCONTROLLER
