jrsteensen/OpenHornet/ECAD/PCBs/OH_Specific/Functional/util_photoswitch/util_photoswitch.sch

## KiCad design ECAD/PCBs/OH_Specific/Functional/util_photoswitch/util_photoswitch.sch (2022-09-23)

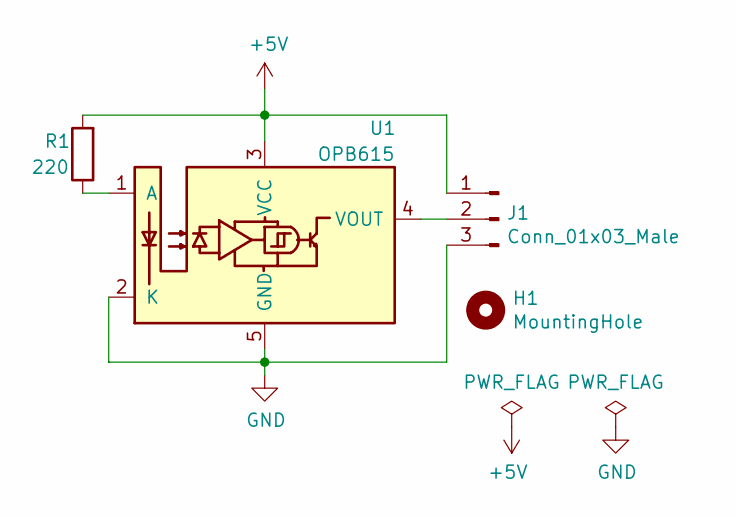
[picture p684: schematic util_photoswitch.sch]

Parts:
H1: MountingHole; MountingHole_2.5mm
J1: Conn_01x03_Male; PinHeader_1x03_P2.54mm_Horizontal
R1: 220; R_Axial_DIN0204_L3.6mm_D1.6mm_P5.08mm_Horizontal
U1: OPB615; OPB61x

Connections:
+5V: J1.1, R1.2, U1.3 (VCC)
GND: J1.3, U1.2 (K), U1.5 (GND)
unnamed: J1.2, U1.4 (VOUT)
unnamed: R1.1, U1.1 (A)
