jrsteensen/OpenHornet/ECAD/PCBs/Specialty/DDI/AMPCD_button_board/Buttons_AMPCD.sch

## KiCad design ECAD/PCBs/Specialty/DDI/AMPCD_button_board/Buttons_AMPCD.sch (2020-11-02)

Schematic: Buttons_AMPCD.sch

Parts:
C1, C2, C3, C4: 47uF; C_0805_2012Metric_Pad1.15x1.40mm_HandSolder
DL_rocker1, DL_rocker2, DL_rocker3, DL_rocker4, DL_rocker5, DL_rocker6, DL_rocker7, DL_rocker8: SW_Push; SWITCH_SNAP_DOME_6.3mm_DIA_SINGLE_SIDE_PCB
J1: ExpansionPort; Molex_KK-254_AE-6410-05A_1x05_P2.54mm_Vertical
R1, R2, R3, R4, R5, R6, R7, R8, R9, R10, R11, R12, R13, R14, R15, R16, R17, R18, R19, R20, R21, R22, R23, R24, R25, R26, R27, R28: 10k; R_0805_2012Metric_Pad1.20x1.40mm_HandSolder
R29, R30, R31: 1k; R_0805_2012Metric_Pad1.15x1.40mm_HandSolder
SW1, SW2, SW3, SW4, SW5, SW6, SW7, SW8, SW9, SW10, SW11, SW12, SW13, SW14, SW15, SW16, SW17, SW18, SW19, SW20: SW_Push; SWITCH_SNAP_DOME_6.3mm_DIA_SINGLE_SIDE_PCB
U1, U2, U3, U4: TCA9534; SOIC-16W_7.5x10.3mm_P1.27mm

Notes on the sheet:
I2C pullups calculation http://www.ti.com/lit/pdf/SLVA689
Check the value of 1k for pullups once hw is assembled, depending on the lenght of the cable we might need to lower or increase resistance
Bypass capacitors, keep close to the ICs in the board.
