jrsteensen/OpenHornet/ECAD/PCBs/Specialty/UFC/interconnects/Interconnects.sch

## KiCad design ECAD/PCBs/Specialty/UFC/interconnects/Interconnects.sch (2019-10-15)

Schematic: Interconnects.sch

Parts:
D11: BIT GO; BLANK_SYMBOL_NOT_FOR_ROUTING
D12: BIT NOGO; BLANK_SYMBOL_NOT_FOR_ROUTING
J10: COM1 ENC; Pin_Header_Straight_1x04_Pitch2.54mm_SMD_Pin1Left
J11: COM2 ENC; Pin_Header_Straight_1x04_Pitch2.54mm_SMD_Pin1Left
J12: BRT/COMM2; Pin_Header_Straight_2x03_Pitch2.54mm_SMD
J13: ADF/COMM1; Pin_Header_Straight_2x03_Pitch2.54mm_SMD
J14: HUD BIT; Pin_Header_Straight_1x04_Pitch2.54mm_SMD_Pin1Left
J15: HUD PANL; Pin_Header_Straight_2x08_Pitch2.54mm_SMD
J16: AP BTNS; Pin_Header_Straight_2x04_Pitch2.54mm_SMD
R10, R11: 100; BLANK_SYMBOL_NOT_FOR_ROUTING
RV1: UFC BRT; BLANK_SYMBOL_NOT_FOR_ROUTING
RV2: COMM 2 VOL; BLANK_SYMBOL_NOT_FOR_ROUTING
RV3: COMM 1 VOL; BLANK_SYMBOL_NOT_FOR_ROUTING
RV4: BRT; BLANK_SYMBOL_NOT_FOR_ROUTING
RV5: BAL; BLANK_SYMBOL_NOT_FOR_ROUTING
RV6: AOA; BLANK_SYMBOL_NOT_FOR_ROUTING
SW20: ADF 1/OFF/2; BLANK_SYMBOL_NOT_FOR_ROUTING
SW21: COMM 1 ENCODER; BLANK_SYMBOL_NOT_FOR_ROUTING
SW22: COMM 2 ENCODER; BLANK_SYMBOL_NOT_FOR_ROUTING
SW23: NORM/REJ; BLANK_SYMBOL_NOT_FOR_ROUTING
SW24: DAY/NIGHT; BLANK_SYMBOL_NOT_FOR_ROUTING
SW25: BLK LVL; BLANK_SYMBOL_NOT_FOR_ROUTING
SW26: BIT START; BLANK_SYMBOL_NOT_FOR_ROUTING
SW27: W/B /VID; BLANK_SYMBOL_NOT_FOR_ROUTING
SW28: ALT; BLANK_SYMBOL_NOT_FOR_ROUTING
SW29: ATT; BLANK_SYMBOL_NOT_FOR_ROUTING

Notes on the sheet:
PANEL MOUNTED UFC SWITCHES (BRT/VOL2/ADF/VOL1)
COMM 1/2 ENCODERS
AP PANEL
HUD PANEL
HUD BIT TEST
