jrsteensen/OpenHornet/ECAD/PCBs/Specialty/UFC/docs/UFC_B_SCHEMATIC.jpg

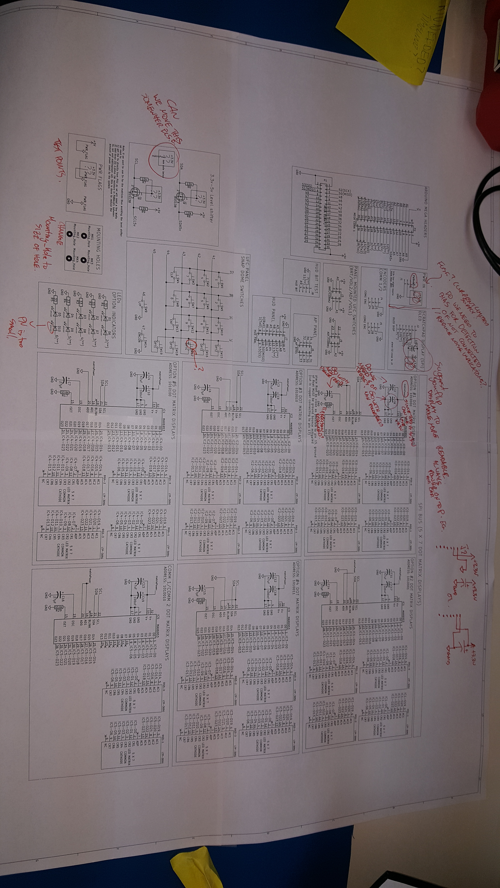
ECAD/PCBs/Specialty/UFC/docs/UFC_B_SCHEMATIC.jpg
